TsanaPhysics/JC-AGRITecH-AI/chewa/OPPO_NPK_SYSTEM_INTEGRATION.md

# ระบบกล่องวัดแบบทึบแสงเชื่อมต่อสมาร์ทโฟน OPPO และการวิเคราะห์ NPK ในดินด้วยปัญญาประดิษฐ์

**โครงการวิจัย** การพัฒนาชุดวิเคราะห์ปริมาณไนโตรเจนและฟอสฟอรัสในดินแบบพกพาด้วยหลักการสะท้อนแสงร่วมกับปัญญาประดิษฐ์  
**หน่วยงาน** คณะวิทยาศาสตร์และเทคโนโลยี มหาวิทยาลัยราชภัฏรำไพพรรณี  
**หัวหน้าโครงการ** ผู้ช่วยศาสตราจารย์ ดร.ชีวะ ทัศนา  

---

## 1. ภาพรวมการเชื่อมต่อระบบระหว่างกล่อง Dark Chamber กับสมาร์ทโฟน OPPO

การพัฒนาชุดตรวจวัดแบบพกพานี้ ได้ผสานโครงสร้างกล่องวัดแบบทึบแสง (Optical Dark Chamber) ที่ขึ้นรูปด้วยเครื่องพิมพ์สามมิติจากเส้นใย PETG สีดำ เข้ากับสมาร์ทโฟน OPPO เพื่อทำหน้าที่เป็นทั้ง **หน่วยรับสัญญาณเชิงแสงความละเอียดสูง** **หน่วยประมวลผลปัญญาประดิษฐ์แบบ On-Device** และ **หน้าจอแสดงผล Cyber Dashboard** สำหรับรายงานค่าธาตุอาหารพืช ไนโตรเจน (N) ฟอสฟอรัส (P) และโพแทสเซียม (K) แก่เกษตรกรชาวสวนทุเรียนได้ทันทีในแปลงเพาะปลูก

ภาพจำลองการใช้งานชุดกล่อง Dark Chamber เชื่อมต่อสมาร์ทโฟน OPPO ในแปลงทุเรียน

---

## 2. การออกแบบแท่นสวมยึดสมาร์ทโฟน OPPO เฉพาะทาง (Custom OPPO Cradle Mount)

เนื่องจากสมาร์ทโฟนตระกูล OPPO (เช่น ซีรีส์ Reno, Find X และ A-Series) มีเอกลักษณ์ในการออกแบบโมดูลกล้องหลังแบบนูนเด่น (Camera Island Bump) ฝาบนของกล่องวัดจึงได้รับการออกแบบเชิงกลเพื่อรองรับลักษณะดังกล่าวโดยเฉพาะ

ภาพระยะประชิดแสดงการล็อกสมาร์ทโฟน OPPO เข้ากับแท่นและปะเก็นยาง EVA กันแสง

### จุดเด่นเชิงกลของแท่นจับยึดสมาร์ทโฟน OPPO
1. **รางประกบขนาดพอดี (Precision Form-fit Rails)** รางนำร่องความกว้าง 75.5 มิลลิเมตร พร้อมเขี้ยวล็อกเลื่อนสปริงด้านข้าง ช่วยให้การสอดสมาร์ทโฟนเข้าตำแหน่งทำได้อย่างรวดเร็ว แนบสนิท ไม่ขยับเขยื้อนขณะเคลื่อนย้ายในแปลงเกษตร
2. **หลุมเบ้ารองรับโมดูลกล้องนูน (Camera Bump Recess)** ปาดผิวเว้าลึก 3.2 มิลลิเมตร รองรับโมดูลกล้องของ OPPO ทำให้ตัวเครื่องวางขนานราบสนิทกับระนาบกล่อง ไม่เอียงตัว
3. **ปะเก็นยางโฟม EVA กันแสงเล็ดลอด 100% (High-density EVA Foam Gasket)** บริเวณรอบเลนส์กล้องหลักมีร่องใส่ยางโฟม EVA สีดำความหนาแน่นสูง เมื่อสอดสมาร์ทโฟนเข้าที่ ยางโฟมจะถูกกดทับแนบสนิทกับผิวกระจกหน้าเลนส์ ตัดแสงสว่างจากภายนอกเข้าสู่เซนเซอร์ได้อย่างสิ้นเชิง
4. **ช่องเปิดเชื่อมต่อสายสัญญาณ USB-C** บริเวณขอบล่างมีช่องเว้นระยะสำหรับเสียบสาย USB-C OTG สำหรับการเชื่อมต่อข้อมูลความเร็วสูง หรือใช้จ่ายพลังงานแบบสองทิศทาง

---

## 3. แผนผังสถาปัตยกรรมการเชื่อมต่อระบบ (System Architecture Diagram)

ระบบทำงานประสานกันระหว่างฮาร์ดแวร์ควบคุมแสงในห้องมืด ช่องทางการสื่อสาร และแอปพลิเคชันปัญญาประดิษฐ์บนสมาร์ทโฟน OPPO ดังแสดงในแผนผัง

```
[ ช่องบรรจุถาดดิน Ø 35 mm ลึก 8 mm ]
                 |
[ เขี้ยวดักแสง Labyrinth Seal สองชั้น ตัดแสง 99.94% ]
                 |
[ แหล่งกำเนิดแสง LED Array 45° (6 ย่านคลื่น 465-940 nm) ]
                 |
[ ลำแสงสะท้อนแบบกระจาย Diffuse Reflectance 0° แนวตั้งฉาก ]
                 |
[ กรวยเลนส์ + ปะเก็นยาง EVA สีดำรอบโมดูลกล้อง OPPO ]
                 |
+-------------------------------------------------------------+
|                     สมาร์ทโฟน OPPO                          |
|                                                             |
|  1. กล้องรับภาพความเข้มแสงสะท้อนสัมพัทธ์ (Relative R)         |
|  2. การแปลงสัญญาณ Kubelka-Munk F(R) และปรับชดเชยน้ำ 940 nm   |
|  3. แบบจำลองโครงข่ายประสาทเทียม MLP-ANN (6-16-8-1)          |
|  4. แสดงผล Cyber Dashboard ค่า N, P, K และคำแนะนำปุ๋ยทุเรียน  |
+-------------------------------------------------------------+
                 ^
                 | ช่องทางสื่อสารคู่ขนาน (Dual-mode Communication)
                 | 1. Bluetooth Low Energy 5.0 (ไร้สาย)
                 | 2. USB-C Serial OTG (สายตรง)
                 v
[ ไมโครคอนโทรลเลอร์ ESP32-S3 + Sequential LED Driver 100ms/50ms ]
```

---

## 4. ช่องทางการเชื่อมต่อข้อมูลสองระบบ (Dual-mode Communication)

ระบบรองรับการเชื่อมต่อกับสมาร์ทโฟน OPPO ได้ 2 รูปแบบ เพื่อความยืดหยุ่นสูงสุดในการทำงานภาคสนาม

### 4.1 การเชื่อมต่อไร้สายผ่านบลูทูธพลังงานต่ำ (Bluetooth Low Energy หรือ BLE 5.0)
* ไมโครคอนโทรลเลอร์ ESP32-S3 ภายในกล่องจะแพร่สัญญาณ BLE Advertisement
* แอปพลิเคชันบนสมาร์ทโฟน OPPO จะตรวจจับและจับคู่อัตโนมัติ (Auto-pairing) ภายใน 1 วินาที
* ส่งคำสั่งเปิด-ปิดไฟ LED พัลส์ตามลำดับ (Sequential Triggering) และส่งกลับข้อมูลสถานะแบตเตอรี่ อุณหภูมิ และความชื้นภายในกล่อง

### 4.2 การเชื่อมต่อผ่านสายตรง USB-C OTG (Direct Serial Cable Connection)
* เชื่อมต่อสาย USB-C สั้นแบบขดสปริงเข้ากับพอร์ต Type-C ของสมาร์ทโฟน OPPO โดยตรง
* ให้ความเร็วในการส่งผ่านคำสั่งระดับไมโครวินาที ปราศจากสัญญาณรบกวนคลื่นวิทยุในพื้นที่ห่างไกล
* สามารถแชร์พลังงานสำรองจากตัวกล่อง Dark Chamber ไปช่วยประจุไฟฟ้าให้สมาร์ทโฟนขณะปฏิบัติงานได้

---

## 5. การทำงานของแอปพลิเคชัน Soil NPK AI บนสมาร์ทโฟน OPPO

1. **ขั้นตอนการสอบเทียบฐานศูนย์ (Baseline Calibration)** ผู้ใช้งานวางแผ่นเทียบสีขาวมาตรฐานในถาดตัวอย่าง กดปุ่ม "สอบเทียบ" บนแอปพลิเคชัน เพื่อบันทึกค่าความเข้มแสงอ้างอิงของแต่ละย่านคลื่น
2. **การสแกนตัวอย่างดิน (Sequential Soil Scan)** บรรจุถาดดินที่ปาดหน้าเรียบเข้าสู่ลิ้นชัก ระบบจะสั่งให้ LED สว่างทีละดวงตามลำดับ (465, 525, 660, 720, 850, 940 nm) ดวงละ 100 มิลลิวินาที สลับความมืด 50 มิลลิวินาที กล้องของ OPPO จะถ่ายภาพความเข้มแสงสะท้อนในแต่ละช่วงคลื่น
3. **การประมวลผลเคมีเมตริกส์ล่วงหน้า (Chemometrics Pipeline)**
   * คำนวณค่าการสะท้อนแสงสัมพัทธ์ $R_\lambda = \frac{I_{\text{sample}} - I_{\text{dark}}}{I_{\text{white}} - I_{\text{dark}}}$
   * แปลงฟังก์ชันคูเบลกา-มังก์ $F(R_\lambda) = \frac{(1 - R_\lambda)^2}{2R_\lambda}$
   * ชดเชยอิทธิพลของความชื้นด้วยอัตราส่วนสเปกตรัมแถบดูดกลืนน้ำที่ 940 นาโนเมตร
4. **การทำนายผลด้วยโมเดลปัญญาประดิษฐ์ (Edge AI Inference)**
   * นำเวกเตอร์สเปกตรัมทั้ง 6 ช่องคลื่น ป้อนเข้าสู่โครงข่ายประสาทเทียม MLP สถาปัตยกรรม 6-16-8-1
   * คำนวณค่า **Total Nitrogen (g/kg)** และ **Available Phosphorus (mg/kg)** โดยตรง พร้อมประเมินแนวโน้มระดับ **Potassium (mg/kg)**
5. **การแสดงผลและคำแนะนำการจัดการปุ๋ย (Decision Support)**
   * หน้าจอ Cyber Dashboard บนสมาร์ทโฟน OPPO จะแสดงผลเป็นมาตรวัดเข็มและแถบสีสถานะ (ต่ำ ปานกลาง สูง)
   * ระบบเชื่อมโยงกับฐานความรู้ปุ๋ยทุเรียน แนะนำสูตรปุ๋ยและอัตราการใส่ที่เหมาะสมกับระยะการเจริญเติบโต เช่น ระยะฟื้นฟูต้น ระยะสะสมอาหาร หรือระยะพัฒนาการของผลทุเรียนโดยอัตโนมัติ

---

## 6. รายการไฟล์โมเดลและภาพจำลองที่จัดทำขึ้น

* [fig_oppo_npk_chamber_field.jpg](file:///Users/chewathassana/Desktop/handysense/chewa/figures/fig_oppo_npk_chamber_field.jpg) ภาพจำลองการทำงานจริงของชุดกล่อง Dark Chamber ร่วมกับสมาร์ทโฟน OPPO ในสวนทุเรียน
* [fig_oppo_macro_mount_engineering.jpg](file:///Users/chewathassana/Desktop/handysense/chewa/figures/fig_oppo_macro_mount_engineering.jpg) ภาพโคลสอัพเชิงวิศวกรรมการสวมล็อกสมาร์ทโฟน OPPO เข้ากับแท่นและปะเก็นยางกันแสง EVA
* [oppo_npk_system_diagram.svg](file:///Users/chewathassana/Desktop/handysense/chewa/figures/oppo_npk_system_diagram.svg) แผนผังเวกเตอร์สถาปัตยกรรมระบบการเชื่อมต่อฮาร์ดแวร์และการประมวลผล AI
* [dark_chamber_oppo_mount.scad](file:///Users/chewathassana/Desktop/handysense/chewa/dark_chamber_oppo_mount.scad) โค้ดพารามิเตอร์ 3 มิติ OpenSCAD ฝาบนสำหรับสมาร์ทโฟน OPPO
* [dark_chamber_oppo_mount.stl](file:///Users/chewathassana/Desktop/handysense/chewa/dark_chamber_oppo_mount.stl) ไฟล์เมช 3D STL สำหรับสั่งพิมพ์ 3 มิติด้วยเส้นใย PETG สีดำได้ทันที
