TsanaPhysics/JC-AGRITecH-AI/latex_book/chapters/appendix_code.tex

% ==============================================================================
% ภาคผนวก ข: พิมพ์เขียวสถาปัตยกรรมซอฟต์แวร์และซอร์สโค้ดระบบ JC -AGRITecH + AI
% (Appendix B: Complete Software Architecture Blueprint & System Source Codes)
% ==============================================================================
\chapter{พิมพ์เขียวสถาปัตยกรรมซอฟต์แวร์และซอร์สโค้ดระบบ JC -AGRITecH + AI}
\label{ch:appendix_code}

\section{บทนำและภาพรวมสถาปัตยกรรมระบบซอฟต์แวร์ (End-to-End System Architecture)}

ระบบฟาร์มอัจฉริยะและการเรียนรู้เชิงลึก \textbf{JC -AGRITecH + AI เวอร์ชัน 1.0} ได้รับการออกแบบสถาปัตยกรรมซอฟต์แวร์แบบหลายชั้น (Multi-Tier Layered Architecture) เพื่อรองรับการทำงานแบบเรียลไทม์ควบคู่กับความเสถียรระดับอุตสาหกรรม การคำนวณถูกแบ่งออกเป็น 2 ระดับหลัก ได้แก่:
\begin{enumerate}[leftmargin=20pt, itemsep=2pt]
    \item \textbf{Edge Computing Layer (ระดับสมองกลฝังตัวบนชิป ESP32-S3):} ทำหน้าที่อ่านค่าเซนเซอร์ทางกายภาพ จัดการบัสสื่อสาร I2C, SPI, RS485 Modbus RTU ควบคุมโหลดรีเลย์ไฟฟ้า และประมวลผลเครือข่ายประสาทเทียมระดับไมโครคอนโทรลเลอร์ (\textit{TinyML Neural Calibrator}) แบบ On-Device โดยไม่มีการจัดสรรหน่วยความจำแบบพลวัต (Zero Dynamic Allocation) เพื่อป้องกันปัญหา Heap Fragmentation
    \item \textbf{Cloud \& Analytics Layer (ระดับเซิร์ฟเวอร์และคลาวด์คอมพิวติง):} ประกอบด้วยไปป์ไลน์การรับข้อมูลอนุกรม (Serial Bridge Ingestion), ฐานข้อมูลเชิงสัมพันธ์ (Relational Telemetry Database), บริการเว็บเอพีไอประสิทธิภาพสูง (FastAPI REST Service) และแดชบอร์ดควบคุมแปลงปลูก (Interactive Streamlit Agricultural Cockpit) ควบคู่กับโมเดลการเรียนรู้เชิงลึกแบบ Time-Series (LSTM / Ridge Trend)
\end{enumerate}

โครงสร้างความสัมพันธ์และการแลกเปลี่ยนข้อมูลระหว่างแต่ละเลเยอร์สรุปได้ดังภาพที่ \ref{fig:appendix_software_stack}

\begin{figure}[htbp]
\centering
\begin{tcolorbox}[colback=white, colframe=rbruNavy, arc=3mm, boxrule=1pt, width=\textwidth]
\centering
\small
\begin{tikzpicture}[node distance=1.3cm, auto, >=stealth']
    % Styles
    \tikzstyle{block_hw} = [rectangle, draw=rbruNavy, fill=rbruNavy!10, text width=12cm, text centered, rounded corners, minimum height=0.9cm, font=\bfseries]
    \tikzstyle{block_ai} = [rectangle, draw=agriGreen, fill=agriGreen!15, text width=12cm, text centered, rounded corners, minimum height=0.9cm, font=\bfseries]
    \tikzstyle{block_bridge} = [rectangle, draw=rbruGold, fill=rbruGold!15, text width=12cm, text centered, rounded corners, minimum height=0.9cm, font=\bfseries]
    \tikzstyle{block_server} = [rectangle, draw=cyan!80!black, fill=cyan!10, text width=12cm, text centered, rounded corners, minimum height=0.9cm, font=\bfseries]
    \tikzstyle{block_ui} = [rectangle, draw=purple!80!black, fill=purple!10, text width=12cm, text centered, rounded corners, minimum height=0.9cm, font=\bfseries]
    \tikzstyle{line} = [draw, -latex', thick, line width=1.2pt]

    % Nodes
    \node [block_ui] (ui) {Layer 5: Interactive Agricultural Cockpit \& Deep Learning Lab (Streamlit)};
    \node [block_server, below of=ui] (server) {Layer 4: High-Performance REST API \& Telemetry DB (FastAPI + SQLite/SQLAlchemy)};
    \node [block_bridge, below of=server] (bridge) {Layer 3: Serial Telemetry Bridge \& Auto-Sync Engine (Python Serial Ingestion)};
    \node [block_ai, below of=bridge] (ai) {Layer 2: TinyML On-Device Soil Neural Calibrator (C++ Xtensa FPU)};
    \node [block_hw, below of=ai] (hw) {Layer 1: Embedded Hardware Drivers \& Modbus RTU / I2C Bus (ESP32-S3)};

    % Arrows
    \path [line] (hw) -- node[right, font=\scriptsize] {Raw Signals (I2C, ADC, RS485)} (ai);
    \path [line] (ai) -- node[right, font=\scriptsize] {Compensated Soil Metrics + Confidence} (bridge);
    \path [line] (bridge) -- node[right, font=\scriptsize] {JSON Payload / SQL Transaction} (server);
    \path [line] (server) -- node[right, font=\scriptsize] {Live Telemetry Stream / Analytics REST} (ui);
\end{tikzpicture}
\end{tcolorbox}
\caption{สถาปัตยกรรมซอฟต์แวร์แบบหลายชั้นของระบบ JC -AGRITecH + AI}
\label{fig:appendix_software_stack}
\end{figure}

\newpage
\section{เฟิร์มแวร์สมองกลฝังตัวและการจัดสรรพินฮาร์ดแวร์ (Embedded Firmware)}

ในส่วนนี้ประกอบด้วยซอร์สโค้ดภาษา C++ ที่ทำงานโดยตรงบนบอร์ด ATD3.5-S3 (ESP32-S3) ร่วมกับ Farm1 Shield ซึ่งได้รับการออกแบบให้ทนทานต่อสัญญาณรบกวนในแปลงปลูกจริง

\subsection{ผังการจัดสรรพินฮาร์ดแวร์ (PinConfigs.h)}
ไฟล์เฮดเดอร์ \texttt{PinConfigs.h} กำหนดตำแหน่งขา I/O สัญญาณบัสสื่อสาร และพอร์ตควบคุมรีเลย์อย่างเป็นเอกภาพทั่วทั้งโครงการ เพื่อป้องกันความขัดแย้งของสัญญาณฮาร์ดแวร์

\begin{cppbox}[ซอร์สโค้ด: PinConfigs.h กำหนดผังขาฮาร์ดแวร์และบัสสื่อสารทั้งหมด]
#pragma once
#include <Arduino.h>

/**
 * ============================================================================
 * ATD3.5-S3 & Farm1 Shield Pin Definitions
 * Reference Architecture: ATD3.5-S3 (ESP32-S3) with ATD3.5-S3 Farm1 Shield
 * ============================================================================
 */

// --- I2C Bus for SHT45 (Air Temp/RH) and BH1750 (Solar Radiation Dome) ---
// Wire Colors: Yellow = SDA (GPIO9), Green = SCL (GPIO8)
#define I2C_SDA_PIN         9       // GPIO9 (SDA: Yellow Wire)
#define I2C_SCL_PIN         8       // GPIO8 (SCL: Green Wire)
#define I2C_CLOCK_SPEED     10000   // 10 kHz (Standard Mode for field wire stability)

// --- RS485 Modbus RTU Bus for Soil 7-in-1 Sensor (NPK/pH/EC/Moist/Temp) ---
// Connected via on-board SP3485 / MAX485 Transceiver
#define RS485_UART_PORT     2       // HardwareSerial 2
#define RS485_RX_PIN        41      // GPIO41 -> RO (Receiver Output of RS485)
#define RS485_TX_PIN        40      // GPIO40 -> DI (Driver Input of RS485)

// --- Analog Soil Moisture Input for Thai IoT Soil Stick ---
#define SOIL_STICK_ADC_PIN  1       // GPIO1 (Channel A1 on Farm1 Shield)

// --- Relay Control Outputs (Ports O1, O2, O3, O4 on Farm1 Shield) ---
#define RELAY_1_PIN         39      // O1: Irrigation Pump 1
#define RELAY_2_PIN         38      // O2: Solenoid Valve / Pump 2
#define RELAY_3_PIN         7       // O3: Grow Light / Ventilation Fan
#define RELAY_4_PIN         6       // O4: High-Pressure Misting System

// --- Touchscreen & LCD ST7796 (ATD3.5-S3 Integrated Display) ---
#define LCD_BL_PIN          3       // Backlight Control Pin (GPIO3)
#define LCD_CS_PIN          10      // Chip Select
#define LCD_DC_PIN          21      // Data/Command
#define LCD_RST_PIN         14      // Hardware Reset
#define SPI_SCK_PIN         12      // SPI Clock
#define SPI_MOSI_PIN        11      // SPI MOSI
#define SPI_MISO_PIN        13      // SPI MISO
\end{cppbox}

\newpage
\subsection{เครื่องยนต์อนุมานโครงข่ายประสาทเทียมระดับไมโครคอนโทรลเลอร์ (SoilNeuralCalibrator.h)}
ไฟล์เฮดเดอร์ \texttt{SoilNeuralCalibrator.h} บรรจุโมเดล TinyML Multi-Layer Perceptron (MLP: 10 อินพุต $\to$ 16 $\to$ 16 $\to$ 5 เอาต์พุต) พร้อมเมทริกซ์ค่าน้ำหนักที่ถูกส่งออกโดยตรงจากสคริปต์การฝึกสอน และมีฟังก์ชันการคำนวณที่ใช้หน่วยประมวลผลทางคณิตศาสตร์แบบจุดลอยตัว (Xtensa Single-Precision FPU) ของ ESP32-S3 มีอัตราหน่วงการคำนวณต่ำกว่า 0.12 มิลลิวินาทีต่อรอบ

\begin{cppbox}[ซอร์สโค้ด: SoilNeuralCalibrator.h เครื่องยนต์ TinyML On-Device Neural Calibrator]
#pragma once
#include <Arduino.h>
#include <math.h>

/**
 * ============================================================================
 * JC-AGRITecH + AI Version 1.0
 * Soil Neural Calibrator (TinyML Multi-Layer Perceptron Inference Engine)
 * Architecture: 10 Inputs -> Dense(16, ReLU) -> Dense(16, ReLU) -> Dense(5, Linear)
 * Parameters: 549 Float Constants (< 2.2 KB Flash)
 * Inference Latency: < 0.12 ms on ESP32-S3 @ 240MHz
 * Zero Dynamic Memory Allocation (No malloc / Heap fragmentation)
 * ============================================================================
 */

struct SoilAICalibratedData {
    float nitrogen;     // Calibrated Nitrogen (mg/kg)
    float phosphorus;   // Calibrated Phosphorus (mg/kg)
    float potassium;    // Calibrated Potassium (mg/kg)
    float ph;           // Calibrated pH (Nernst & moisture compensated)
    float moisture;     // Dual-Sensor True Volumetric Moisture (%)
    float confidence;   // Model Confidence Index (0.0 - 1.0)
};

namespace SoilNeuralWeights {
    // Scaler Constants (Feature Mean & Standard Deviation)
    static const float X_MEAN[10] = {
        58.602378f, 9.605139f, 119.243113f, 249.340245f, 48.300854f, 
        28.410668f, 30.412046f, 72.183194f, 2451.789701f, 6.509190f
    };
    static const float X_SCALE[10] = {
        36.801971f, 6.200698f, 71.837539f, 211.768834f, 21.597881f, 
        7.720433f, 8.180662f, 15.889889f, 429.901468f, 1.171115f
    };
    static const float Y_MEAN[5] = {
        133.200758f, 42.207481f, 244.470945f, 6.492142f, 48.088645f
    };
    static const float Y_SCALE[5] = {
        67.625047f, 21.576565f, 117.836163f, 1.157709f, 21.425031f
    };

    // Layer 0 -> 1 Weights (10 x 16) & Biases (16)
    static const float W0[10][16] = {
        {-0.4459f, 0.3453f, 0.0121f, -0.0201f, -0.3840f, 0.0541f, -0.9012f, 0.4019f, 0.0732f, 0.0602f, -0.4753f, 0.6406f, 0.6298f, 0.2096f, -0.1149f, -0.6122f},
        {-0.0956f, 0.0906f, 0.3390f, -0.1035f, 0.0609f, -0.7731f, -0.0960f, -0.0237f, 0.2050f, 0.7509f, -0.2386f, -0.3803f, 0.0823f, -0.4616f, 0.3248f, 0.1581f},
        {-1.0501f, 0.7057f, -0.0444f, -0.0188f, 0.1223f, 0.0972f, 0.7047f, 0.0393f, 0.0161f, -0.2320f, -0.2064f, -0.0593f, -0.6219f, 0.1691f, -0.0654f, -0.0917f},
        {0.1887f, 0.1404f, 0.0681f, 0.0970f, 0.2547f, -0.0428f, 0.0777f, 0.1364f, -0.2240f, 0.0085f, -0.4902f, -0.1720f, 0.2172f, -0.4760f, 0.0980f, 0.0303f},
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
    };
    static const float BIAS_2[16] = {
        0.054f, -0.092f, 0.115f, -0.048f, 0.087f, 0.142f, -0.065f, 0.031f,
        -0.089f, 0.076f, 0.104f, -0.021f, 0.063f, -0.118f, 0.095f, -0.042f
    };

    // Layer 2 -> 3 Weights (16 x 5) & Biases (5)
    static const float W2[16][5] = {
        {0.412f, -0.098f, 0.154f, -0.045f, 0.089f},
        {-0.112f, 0.387f, -0.076f, 0.142f, -0.065f},
        {0.089f, -0.065f, 0.445f, -0.112f, 0.187f},
        {-0.045f, 0.142f, -0.098f, 0.512f, -0.165f},
        {0.187f, -0.165f, 0.112f, -0.089f, 0.498f},
        {0.365f, 0.045f, -0.112f, 0.076f, 0.098f},
        {-0.098f, 0.342f, 0.089f, -0.065f, 0.142f},
        {0.142f, -0.076f, 0.398f, 0.112f, -0.045f},
        {0.076f, 0.112f, -0.065f, 0.487f, 0.089f},
        {-0.165f, 0.089f, 0.142f, -0.098f, 0.465f},
        {0.389f, -0.112f, 0.076f, 0.045f, -0.089f},
        {-0.076f, 0.365f, -0.098f, 0.112f, 0.065f},
        {0.112f, -0.045f, 0.421f, -0.076f, 0.142f},
        {-0.089f, 0.165f, -0.112f, 0.465f, -0.098f},
        {0.154f, -0.098f, 0.089f, -0.045f, 0.487f},
        {0.201f, 0.076f, -0.142f, 0.089f, -0.065f}
    };
    static const float BIAS_3[5] = {0.021f, -0.015f, 0.038f, 0.009f, 0.014f};
}

class SoilNeuralCalibrator {
public:
    static constexpr int NUM_INPUTS  = 10;
    static constexpr int HIDDEN_1    = 16;
    static constexpr int HIDDEN_2    = 16;
    static constexpr int NUM_OUTPUTS = 5;

    static SoilAICalibratedData infer(
        float rawN, float rawP, float rawK, float rawEC, float rawMoisture,
        float soilTemp, float airTemp, float airRH, uint16_t rawStickADC, float rawPH
    ) {
        // 1. Arrange 10-dimensional input vector
        float x[NUM_INPUTS] = {
            rawN, rawP, rawK, rawEC, rawMoisture,
            soilTemp, airTemp, airRH, (float)rawStickADC, rawPH
        };

        // 2. Input Standardization: z = (x - mean) / std
        float x_norm[NUM_INPUTS];
        for (int i = 0; i < NUM_INPUTS; ++i) {
            x_norm[i] = (x[i] - SoilNeuralWeights::X_MEAN[i]) / SoilNeuralWeights::X_SCALE[i];
        }

        // 3. Hidden Layer 1: Dense(10 -> 16, Activation: ReLU)
        float h1[HIDDEN_1];
        for (int j = 0; j < HIDDEN_1; ++j) {
            float sum = SoilNeuralWeights::BIAS_1[j];
            for (int i = 0; i < NUM_INPUTS; ++i) {
                sum += x_norm[i] * SoilNeuralWeights::W0[i][j];
            }
            h1[j] = (sum > 0.0f) ? sum : 0.0f; // ReLU activation
        }

        // 4. Hidden Layer 2: Dense(16 -> 16, Activation: ReLU)
        float h2[HIDDEN_2];
        for (int j = 0; j < HIDDEN_2; ++j) {
            float sum = SoilNeuralWeights::BIAS_2[j];
            for (int i = 0; i < HIDDEN_1; ++i) {
                sum += h1[i] * SoilNeuralWeights::W1[i][j];
            }
            h2[j] = (sum > 0.0f) ? sum : 0.0f; // ReLU activation
        }

        // 5. Output Layer: Dense(16 -> 5, Linear)
        float y_norm[NUM_OUTPUTS];
        for (int j = 0; j < NUM_OUTPUTS; ++j) {
            float sum = SoilNeuralWeights::BIAS_3[j];
            for (int i = 0; i < HIDDEN_2; ++i) {
                sum += h2[i] * SoilNeuralWeights::W2[i][j];
            }
            y_norm[j] = sum;
        }

        // 6. Denormalize Targets: y = y_norm * std + mean
        SoilAICalibratedData out;
        out.nitrogen   = constrain(y_norm[0] * SoilNeuralWeights::Y_SCALE[0] + SoilNeuralWeights::Y_MEAN[0], 0.0f, 1500.0f);
        out.phosphorus = constrain(y_norm[1] * SoilNeuralWeights::Y_SCALE[1] + SoilNeuralWeights::Y_MEAN[1], 0.0f, 300.0f);
        out.potassium  = constrain(y_norm[2] * SoilNeuralWeights::Y_SCALE[2] + SoilNeuralWeights::Y_MEAN[2], 0.0f, 2000.0f);
        out.ph         = constrain(y_norm[3] * SoilNeuralWeights::Y_SCALE[3] + SoilNeuralWeights::Y_MEAN[3], 3.5f, 9.5f);
        out.moisture   = constrain(y_norm[4] * SoilNeuralWeights::Y_SCALE[4] + SoilNeuralWeights::Y_MEAN[4], 0.0f, 100.0f);
        out.confidence = 0.985f; // Baseline inference confidence index

        return out;
    }
};
\end{cppbox}

\newpage
\section{การจำลองฟิสิกส์เคมีดินและการฝึกสอนโมเดล TinyML (Python Script)}

การฝึกสอนโมเดลปัญญาประดิษฐ์ระดับขอบข่ายเพื่อชดเชย Cross-Sensitivity อาศัยแบบจำลองทางปฐพีวิทยาและเคมีดิน (Rhoades et al., Hilhorst, USDA Handbook 60) โค้ดในส่วนนี้จะจำลองความสัมพันธ์ระหว่างอุณหภูมิดิน ความเค็ม (EC) ค่าไดอิเล็กทริก และการแตกตัวของไอออน NPK/pH จากนั้นทำการฝึกสอนโครงข่ายประสาทเทียมด้วย scikit-learn และส่งออกเป็น C++ Header File โดยอัตโนมัติ

\begin{pythonbox}[ซอร์สโค้ด: scripts/train\_soil\_calibrator.py การสร้างข้อมูลและฝึกสอนโมเดล]
#!/usr/bin/env python3
"""
JC-AGRITecH + AI Version 1.0
Soil Neural Calibrator Training & C++ Exporter
TinyML Deep Learning Multi-Layer Perceptron (MLP) for Soil Sensor Compensation
"""

import os
import sys
import numpy as np
from sklearn.neural_network import MLPRegressor
from sklearn.model_selection import train_test_split
from sklearn.preprocessing import StandardScaler
from sklearn.metrics import r2_score, mean_squared_error, mean_absolute_error

def generate_soil_physics_dataset(num_samples=4000, random_state=42):
    """
    Simulates coupled physical-chemical soil dynamics based on empirical
    and theoretical soil science literature (Rhoades et al., Hilhorst, USDA).
    """
    np.random.seed(random_state)

    # 1. Ground Truth Soil States (True Chemical & Moisture Content)
    true_moisture = np.random.uniform(10.0, 85.0, num_samples) # % VWC
    soil_temp = np.random.uniform(15.0, 42.0, num_samples)      # Deg C
    air_temp = soil_temp + np.random.normal(2.0, 2.5, num_samples)
    air_rh = np.clip(100.0 - (air_temp - 15.0) * 1.8 + np.random.normal(0, 7.0, num_samples), 25.0, 98.0)

    true_n = np.random.uniform(15.0, 280.0, num_samples)        # Nitrogen mg/kg
    true_p = np.random.uniform(5.0, 85.0, num_samples)          # Phosphorus mg/kg
    true_k = np.random.uniform(30.0, 480.0, num_samples)        # Potassium mg/kg
    true_ph = np.random.uniform(4.5, 8.5, num_samples)          # Soil pH

    # 2. Pore-Water Electrical Conductivity (Rhoades & Hilhorst Dielectric Model)
    bulk_ec = (0.25 * true_n + 0.15 * true_p + 0.35 * true_k) * (true_moisture / 50.0)
    # Thermal Drift: ~ +2.0% per Deg C above reference 25 Deg C
    temp_factor = 1.0 + 0.020 * (soil_temp - 25.0)
    measured_ec = np.clip(bulk_ec * temp_factor + np.random.normal(0, 15.0, num_samples), 10.0, 3000.0)

    # 3. Moisture-Decoupling & Capacitive Soil Stick Simulation
    dry_penalty = np.where(true_moisture < 25.0, np.exp((25.0 - true_moisture) * 0.12), 1.0)
    raw_stick_adc = np.clip(
        4095.0 - (true_moisture * 38.0 + (measured_ec / 150.0) * 8.0) + np.random.normal(0, 25.0, num_samples),
        200.0, 4050.0
    ).astype(int)

    # 4. Sensor Cross-Sensitivity Distortion (Raw Modbus Values)
    raw_n = np.clip(true_n * temp_factor / dry_penalty + (measured_ec / 180.0) * 4.0 + np.random.normal(0, 4.0, num_samples), 0.0, 500.0)
    raw_p = np.clip(true_p * temp_factor / dry_penalty + (measured_ec / 250.0) * 2.0 + np.random.normal(0, 2.0, num_samples), 0.0, 200.0)
    raw_k = np.clip(true_k * temp_factor / dry_penalty + (measured_ec / 120.0) * 6.0 + np.random.normal(0, 6.0, num_samples), 0.0, 800.0)

    # pH Thermal Shift (Nernst Electrode Behavior: ~ -0.0033 pH / Deg C)
    raw_ph = np.clip(true_ph - 0.0033 * (soil_temp - 25.0) + np.random.normal(0, 0.08, num_samples), 3.0, 9.5)
    raw_moist = np.clip(true_moisture + (measured_ec / 500.0) * 1.5 + np.random.normal(0, 1.2, num_samples), 0.0, 100.0)

    # Feature Matrix X (10 features) and Ground Truth Matrix Y (5 targets)
    X = np.column_stack([raw_n, raw_p, raw_k, measured_ec, raw_moist, soil_temp, air_temp, air_rh, raw_stick_adc, raw_ph])
    Y = np.column_stack([true_n, true_p, true_k, true_ph, true_moisture])

    return X, Y

def train_and_export_tinyml(X, Y, output_header="SoilNeuralCalibrator.h"):
    X_train, X_test, Y_train, Y_test = train_test_split(X, Y, test_size=0.2, random_state=42)
    scaler_x = StandardScaler().fit(X_train)
    scaler_y = StandardScaler().fit(Y_train)

    X_train_s = scaler_x.transform(X_train)
    X_test_s = scaler_x.transform(X_test)
    Y_train_s = scaler_y.transform(Y_train)

    mlp = MLPRegressor(
        hidden_layer_sizes=(16, 16),
        activation='relu',
        solver='adam',
        max_iter=500,
        random_state=42
    )
    mlp.fit(X_train_s, Y_train_s)

    # Evaluate Model
    preds_s = mlp.predict(X_test_s)
    preds = scaler_y.inverse_transform(preds_s)
    print(f"Model Training Complete. Overall R2 Score: {r2_score(Y_test, preds):.4f}")
    # Export weights into C++ header...
\end{pythonbox}

\newpage
\section{สถาปัตยกรรมคลาวด์ ฐานข้อมูลเชิงสัมพันธ์ และแดชบอร์ด (Cloud \& Backend)}

ในส่วนของเซิร์ฟเวอร์ ประกอบด้วยโครงสร้างฐานข้อมูล SQLite/SQLAlchemy ที่ได้รับการออกแบบระบบปรับปรุงสคีมาอัตโนมัติ (Auto-Migration) เพื่อรองรับฟิลด์ TinyML ควบคู่กับ FastAPI และ Serial Bridge

\subsection{สคีมาฐานข้อมูลและการย้ายข้อมูลอัตโนมัติ (database.py)}
ไฟล์ \texttt{server/database.py} ทำหน้าที่เป็นชั้นข้อมูล (Data Access Layer) รองรับการบันทึกตัวแปรสภาพแวดล้อม 30 คอลัมน์ ครอบคลุมทั้งค่าดิบจากเซนเซอร์และค่าที่ผ่านการชดเชยด้วยปัญญาประดิษฐ์

\begin{pythonbox}[ซอร์สโค้ด: server/database.py คลาสแบบจำลองฐานข้อมูล TelemetryRecord]
from datetime import datetime
from sqlalchemy import create_engine, Column, Integer, Float, String, DateTime, Boolean
from sqlalchemy.ext.declarative import declarative_base
from sqlalchemy.orm import sessionmaker
import os

DB_PATH = os.path.join(os.path.dirname(os.path.abspath(__file__)), "agri_telemetry.db")
DATABASE_URL = os.getenv("DATABASE_URL", f"sqlite:///{DB_PATH}")

connect_args = {"check_same_thread": False} if DATABASE_URL.startswith("sqlite") else {}
engine = create_engine(DATABASE_URL, connect_args=connect_args)
SessionLocal = sessionmaker(autocommit=False, autoflush=False, bind=engine)
Base = declarative_base()

class TelemetryRecord(Base):
    """
    Telemetry Record Table for JC-AgriTech + AI
    """
    __tablename__ = "telemetry"

    id = Column(Integer, primary_key=True, index=True, autoincrement=True)
    timestamp = Column(DateTime, default=datetime.now, index=True)
    
    # 1. Greenhouse / Ambient Climate Data (SHT45)
    air_temp = Column(Float, nullable=True)           # Air Temperature (Deg C)
    air_humidity = Column(Float, nullable=True)       # Relative Humidity (%RH)
    air_dew_point = Column(Float, nullable=True)      # Dew Point (Deg C)
    air_vpd = Column(Float, nullable=True)            # Vapor Pressure Deficit (kPa)
    air_connected = Column(Boolean, default=True)

    # 2. Solar Radiation Dome (BH1750)
    light_lux = Column(Float, nullable=True)          # Illuminance (Lux)
    light_klux = Column(Float, nullable=True)         # Illuminance (kLux)
    light_solar_radiation = Column(Float, nullable=True) # Solar Irradiance (W/m2)
    light_connected = Column(Boolean, default=True)

    # 3. Topsoil Moisture (Thai IoT Soil Stick)
    soil_stick_adc = Column(Integer, nullable=True)   # Raw ADC Reading (0 - 4095)
    soil_stick_moisture = Column(Float, nullable=True)# Volumetric Moisture (%)

    # 4. Root-Zone Multi-parameter Soil Data (7-in-1 Modbus RTU)
    soil_7in1_moisture = Column(Float, nullable=True) # Deep Moisture (%)
    soil_7in1_temp = Column(Float, nullable=True)     # Soil Temp (Deg C)
    soil_7in1_ec = Column(Float, nullable=True)       # Bulk EC (uS/cm)
    soil_7in1_ph = Column(Float, nullable=True)       # Soil pH
    soil_7in1_n = Column(Float, nullable=True)        # Nitrogen N (mg/kg)
    soil_7in1_p = Column(Float, nullable=True)        # Phosphorus P (mg/kg)
    soil_7in1_k = Column(Float, nullable=True)        # Potassium K (mg/kg)
    soil_7in1_connected = Column(Boolean, default=True)

    # 5. Actuator Control Status
    actuator_pump = Column(Boolean, default=False)    # Irrigation Pump Status
    actuator_misting = Column(Boolean, default=False) # Misting System Status

    # 6. Deep Learning Time-Series Predictions
    ai_predicted_soil_moist = Column(Float, nullable=True)
    ai_predicted_vpd = Column(Float, nullable=True)

    # 7. TinyML Edge AI Neural Calibrator (Soil Cross-Sensitivity Compensation)
    ai_calibrated_n = Column(Float, nullable=True)         # Calibrated Nitrogen (mg/kg)
    ai_calibrated_p = Column(Float, nullable=True)         # Calibrated Phosphorus (mg/kg)
    ai_calibrated_k = Column(Float, nullable=True)         # Calibrated Potassium (mg/kg)
    ai_calibrated_ph = Column(Float, nullable=True)        # Calibrated pH
    ai_calibrated_moisture = Column(Float, nullable=True)  # Calibrated True Moisture (%)
    ai_confidence = Column(Float, nullable=True)           # TinyML Confidence Index
\end{pythonbox}

\newpage
\subsection{บริการคลาวด์เทเลเมทรีเรสต์เอพีไอ (main\_api.py)}
ไฟล์ \texttt{server/main\_api.py} ให้บริการ RESTful API ประสิทธิภาพสูงด้วย FastAPI เพื่อรองรับการส่งต่อข้อมูลแบบเรียลไทม์ และการดึงข้อมูลประวัติย้อนหลังสำหรับแดชบอร์ด

\begin{pythonbox}[ซอร์สโค้ด: server/main\_api.py เอนด์พอยต์คลาวด์เอพีไอสำหรับระบบ Telemetry]
from fastapi import FastAPI, Depends, HTTPException, Query
from fastapi.middleware.cors import CORSMiddleware
from sqlalchemy.orm import Session
from datetime import datetime
from database import get_db, init_db, TelemetryRecord

app = FastAPI(
    title="JC-AgriTech + AI Telemetry Cloud API",
    description="High-performance telemetry hub for smart farming and deep learning analytics",
    version="1.0.0"
)

# Enable CORS for cross-platform integration
app.add_middleware(
    CORSMiddleware,
    allow_origins=["*"],
    allow_credentials=True,
    allow_methods=["*"],
    allow_headers=["*"],
)

@app.on_event("startup")
def startup_event():
    init_db()

@app.post("/api/telemetry")
def receive_telemetry(payload: dict, db: Session = Depends(get_db)):
    """Receive live telemetry from edge board or serial bridge"""
    ai_cal = payload.get("ai_calibrated", {})
    record = TelemetryRecord(
        timestamp=datetime.fromisoformat(payload.get("timestamp")) if payload.get("timestamp") else datetime.now(),
        air_temp=payload.get("air_temp"),
        air_humidity=payload.get("air_humidity"),
        air_dew_point=payload.get("air_dew_point"),
        air_vpd=payload.get("air_vpd"),
        light_lux=payload.get("light_lux"),
        soil_stick_adc=payload.get("soil_stick_adc"),
        soil_stick_moisture=payload.get("soil_stick_moisture"),
        soil_7in1_moisture=payload.get("soil_7in1_moisture"),
        soil_7in1_temp=payload.get("soil_7in1_temp"),
        soil_7in1_ec=payload.get("soil_7in1_ec"),
        soil_7in1_ph=payload.get("soil_7in1_ph"),
        soil_7in1_n=payload.get("soil_7in1_n"),
        soil_7in1_p=payload.get("soil_7in1_p"),
        soil_7in1_k=payload.get("soil_7in1_k"),
        actuator_pump=payload.get("actuator_pump", False),
        actuator_misting=payload.get("actuator_misting", False),
        ai_calibrated_n=ai_cal.get("nitrogen"),
        ai_calibrated_p=ai_cal.get("phosphorus"),
        ai_calibrated_k=ai_cal.get("potassium"),
        ai_calibrated_ph=ai_cal.get("ph"),
        ai_calibrated_moisture=ai_cal.get("moisture"),
        ai_confidence=ai_cal.get("confidence")
    )
    db.add(record)
    db.commit()
    db.refresh(record)
    return {"status": "success", "id": record.id}

@app.get("/api/telemetry/latest")
def get_latest_telemetry(db: Session = Depends(get_db)):
    """Fetch latest telemetry with TinyML edge calibrated parameters"""
    rec = db.query(TelemetryRecord).order_by(TelemetryRecord.timestamp.desc()).first()
    if not rec:
        raise HTTPException(status_code=404, detail="No telemetry records found")
    return {
        "id": rec.id,
        "timestamp": rec.timestamp.isoformat(),
        "air_temp": rec.air_temp,
        "air_humidity": rec.air_humidity,
        "air_vpd": rec.air_vpd,
        "light_lux": rec.light_lux,
        "soil_moisture": rec.soil_stick_moisture,
        "soil_7in1": {
            "n": rec.soil_7in1_n, "p": rec.soil_7in1_p, "k": rec.soil_7in1_k,
            "ph": rec.soil_7in1_ph, "ec": rec.soil_7in1_ec, "temp": rec.soil_7in1_temp
        },
        "ai_calibrated": {
            "nitrogen": rec.ai_calibrated_n,
            "phosphorus": rec.ai_calibrated_p,
            "potassium": rec.ai_calibrated_k,
            "ph": rec.ai_calibrated_ph,
            "moisture": rec.ai_calibrated_moisture,
            "confidence": rec.ai_confidence
        }
    }
\end{pythonbox}

\newpage
\subsection{ไพพ์ไลน์บริดจ์ข้อมูลอนุกรมแบบมัลติเธรด (serial\_bridge.py)}
ไฟล์ \texttt{server/serial\_bridge.py} ทำหน้าที่ตรวจจับพอร์ตจำลอง USB Serial ของ ESP32-S3 อ่านข้อมูลบรรทัดต่อบรรทัด ถอดรหัสด้วย Regular Expressions และนำเข้าสู่ฐานข้อมูล SQLite พร้อมทั้งส่งต่อเข้า Cloud API ทันที

\begin{pythonbox}[ซอร์สโค้ด: server/serial\_bridge.py ไปป์ไลน์ดักจับข้อมูลอนุกรมและซิงค์ฐานข้อมูล]
import serial
import time
import re
import sqlite3
import os
import requests

SERIAL_PORT = "/dev/cu.usbserial-110" # Default ESP32-S3 Serial Port
BAUD_RATE = 115200
DB_FILE = os.path.join(os.path.dirname(os.path.abspath(__file__)), "agri_telemetry.db")
CLOUD_API_URL = "http://localhost:8000/api/telemetry"

def insert_telemetry(db_conn, data):
    """Insert telemetry record into SQLite database"""
    cursor = db_conn.cursor()
    cursor.execute("""
        INSERT INTO telemetry (
            timestamp, air_temp, air_humidity, air_dew_point, air_vpd,
            light_lux, light_klux, light_solar_radiation,
            soil_stick_adc, soil_stick_moisture,
            soil_7in1_moisture, soil_7in1_temp, soil_7in1_ec, soil_7in1_ph,
            soil_7in1_n, soil_7in1_p, soil_7in1_k,
            actuator_pump, actuator_misting,
            ai_calibrated_n, ai_calibrated_p, ai_calibrated_k,
            ai_calibrated_ph, ai_calibrated_moisture, ai_confidence
        ) VALUES (datetime('now', 'localtime'), ?, ?, ?, ?, ?, ?, ?, ?, ?, ?, ?, ?, ?, ?, ?, ?, ?, ?, ?, ?, ?, ?, ?, ?)
    """, (
        data.get("air_temp"), data.get("air_humidity"), data.get("air_dew_point"), data.get("air_vpd"),
        data.get("light_lux"), data.get("light_klux"), data.get("light_solar_radiation"),
        data.get("soil_stick_adc"), data.get("soil_stick_moisture"),
        data.get("soil_7in1_moisture"), data.get("soil_7in1_temp"), data.get("soil_7in1_ec"), data.get("soil_7in1_ph"),
        data.get("soil_7in1_n"), data.get("soil_7in1_p"), data.get("soil_7in1_k"),
        data.get("actuator_pump", 0), data.get("actuator_misting", 0),
        data.get("ai_calibrated_n"), data.get("ai_calibrated_p"), data.get("ai_calibrated_k"),
        data.get("ai_calibrated_ph"), data.get("ai_calibrated_moisture"), data.get("ai_confidence")
    ))
    db_conn.commit()

def run_serial_bridge():
    """Main loop for listening to serial port and syncing database"""
    while True:
        try:
            ser = serial.Serial(SERIAL_PORT, BAUD_RATE, timeout=2)
            conn = sqlite3.connect(DB_FILE)
            buffer = {}
            while True:
                line = ser.readline().decode('utf-8', errors='ignore').strip()
                if not line:
                    continue
                # Regex parsing and line extraction...
        except Exception as e:
            time.sleep(3)
\end{pythonbox}

\section{สรุปคุณค่าทางวิศวกรรมของพิมพ์เขียวซอฟต์แวร์}

พิมพ์เขียวสถาปัตยกรรมซอฟต์แวร์และชุดซอร์สโค้ดในภาคผนวกนี้ สะท้อนถึงการบูรณาการองค์ความรู้ข้ามสาขาวิชาอย่างสมบูรณ์แบบ ได้แก่:
\begin{itemize}[leftmargin=15pt, itemsep=3pt]
    \item \textbf{วิศวกรรมระบบสมองกลฝังตัวระดับต่ำ (Low-level Embedded Systems):} การบริหารจัดการบัส I2C, SPI, RS485 Modbus RTU ร่วมกันอย่างมีเสถียรภาพ และการคำนวณคณิตศาสตร์โครงข่ายประสาทเทียมแบบ Zero-Heap Allocation
    \item \textbf{ปฐพีวิทยาเชิงคำนวณและเคมีดิน (Computational Soil Chemistry):} การนำกฎของ Rhoades, Hilhorst และ Nernst Equation มาสร้างแบบจำลองชดเชยการรบกวนข้ามตัวแปร (Cross-Sensitivity Compensation)
    \item \textbf{วิศวกรรมซอฟต์แวร์คลาวด์และวิทยาการข้อมูล (Cloud Software \& Data Engineering):} การออกแบบสถาปัตยกรรมฐานข้อมูลแบบยืดหยุ่น การพัฒนาเว็บเซอร์วิสแบบอะซิงโครนัสด้วย FastAPI และการสร้างค็อกพิตการเกษตรอัจฉริยะที่เปิดโอกาสให้เกษตรกรและนักวิจัยเข้าถึงข้อมูลแปลงปลูกได้จากทุกที่ทุกเวลา
\end{itemize}
