TsanaPhysics/JC-AGRITecH-AI/latex_book/main.pdf

# JC -AGRITecH + AI Version 1.0

## คู่มือจัดทำระบบฟาร์มอัจฉริยะด้วยปั ญญาประดิษฐ์และการเรียนรู้เชิงลึก

### จากสมองกลฝั งตัวสู่การพยากรณ์แปลงปลูกด้วย Deep Learning

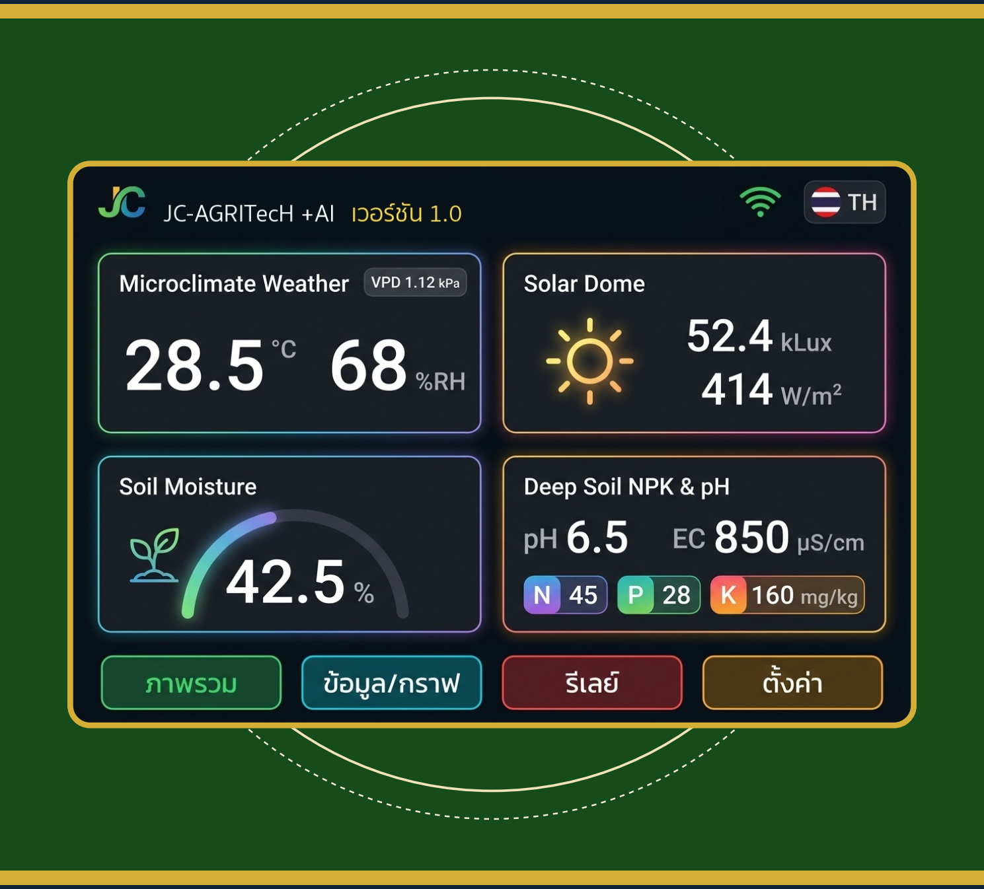
[picture p15: figure]

ผู้ช่วยศาสตราจารย์ ดร.จิรภัทร จันทมาลี | ผู้ช่วยศาสตราจารย์ ดร.ชีวะ ทัศนา
สาขาวิชาจุลชีววิทยา | สาขาวิชาฟิ สิกส์

### คณะวิทยาศาสตร์และเทคโนโลยี มหาวิทยาลัยราชภัฏรำไพพรรณี

พ.ศ. 2569

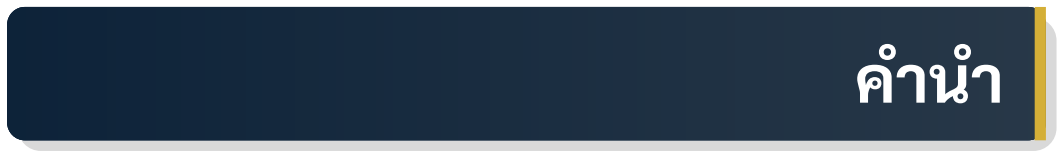
[picture p16: figure]
คำนำ

ความ ก้าวหน้า อย่าง ก้าว กระโดด ของ เทคโนโลยี คอมพิวเตอร์ อินเทอร์เน็ต ของ สรรพ สิ่ง (Internet of Things หรือ IoT) และปั ญญาประดิษฐ์ (Artificial Intelligence หรือ AI) ได้ก่อให้เกิด การเปลี่ยนแปลงเชิงโครงสร้างอย่างลึกซึ้
งต่อภาคการเกษตรกรรมยุคใหม่ จากการเพาะปลูกแบบ ดั้

งเดิมที่อาศัยสัญชาตญาณและการสังเกตสภาพดินฟ้ าอากาศตามฤดูกาล สู่ยุคของ เกษตรกรรม แม่นยำสูง (High-Precision Agriculture) ซึ่

งขับเคลื่อนด้วยข้อมูลเชิงประจักษ์และการตัดสินใจ อัตโนมัติแบบเรียลไทม์
ตำราวิชาการและคู่มือประมวลความรู้เรื่อง JC -AGRITecH + AI Version 1.0 คู่มือจัดทำ ระบบฟาร์มอัจฉริยะด้วยปั ญญาประดิษฐ์และการเรียนรู้เชิงลึก เล่มนี้ เรียบเรียงขึ้นจากผลงาน
วิจัย การทดลองภาคสนาม และประสบการณ์การพัฒนาระบบควบคุมอัจฉริยะจริงของผู้เขียน โดย มุ่งเน้นการบูรณาการองค์ความรู้ข้ามศาสตร์ระหว่าง ฟิ สิกส์ประยุกต์ วิศวกรรมฝั งตัว (Embedded Engineering) และการเรียนรู้เชิงลึก (Deep Learning) เข้าด้วยกันอย่างเป็ นระบบ เพื่อตอบโจทย์ ความต้องการของนักศึกษา นักวิจัย เกษตรกรยุคใหม่ และผู้สนใจในเทคโนโลยีการเกษตร เนื้อหา ภายใน เล่ม แบ่ง ออก เป็ น 5 บท หลัก ที่ครอบคลุม ทุก มิติ ทาง วิศวกรรม ตั้
งแต่ การ
ออกแบบและเชื่อมต่อฮาร์ดแวร์ไมโครคอนโทรลเลอร์สมรรถนะสูง ESP32-S3 บนบอร์ด ATD3.5-S3 และ ATD3.5-S3 Farm1 Shield ร่วมกับเซนเซอร์การเกษตรมาตรฐานอุตสาหกรรม การพัฒนา ไดรเวอร์และระบบคำนวณพารามิเตอร์ทางปฐพีวิทยา การสอบเทียบเซนเซอร์ธาตุอาหารดิน N-P-K และ pH ตามหลักวิทยาศาสตร์ การสร้างระบบส่วนต่อประสานสามภาษาและการเรนเดอร์กราฟิ ก แอนิเมชัน 3 มิติเสมือนจริง ตลอดจนการสตรีมข้อมูลไร้สายแบบ Non-blocking การพัฒนาระบบ เซิร์ฟเวอร์และแดชบอร์ดด้วยภาษาไพทอน และการประยุกต์ใช้โครงข่ายประสาทเทียมแบบ LSTM ในการพยากรณ์ความชื้นในดินและสภาวะแปลงปลูกล่วงหน้า
ผู้ เขียนหวัง เป็ นอย่างยิ่งว่า ตำรา เล่มนี้จะทำหน้าที่

เป็ นสะพาน เชื่อมระหว่างทฤษฎีทาง วิทยาศาสตร์กายภาพและเทคโนโลยีปั ญญาประดิษฐ์เชิงปฏิบัติการ เพื่อร่วมขับเคลื่อนการศึกษา การวิจัย และการพัฒนาภาคการเกษตรกรรมของประเทศไทยสู่ความยั่
งยืนสืบไป

ผู้ช่วยศาสตราจารย์ ดร.จิรภัทร จันทมาลี สาขาวิชาจุลชีววิทยา
i

ผู้ช่วยศาสตราจารย์ ดร.ชีวะ ทัศนา สาขาวิชาฟิ สิกส์
คณะวิทยาศาสตร์และเทคโนโลยี มหาวิทยาลัยราชภัฏรำไพพรรณี กันยายน 2569

ii

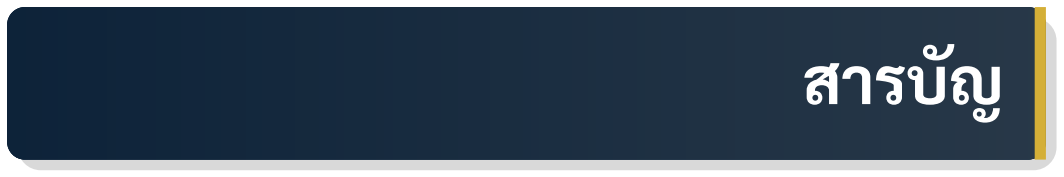
[picture p17: figure]
สารบัญ

คำนำ | i
สารบัญภาพ | vi
สารบัญตาราง | vii
1 สถาปั ตยกรรมฮาร์ดแวร์ระบบแปลงปลูกอัจฉริยะ | 1

1.1.1 แผนภาพ บล็อก สถาปั ตยกรรม ฮาร์ดแวร์ ระบบ รวม (System Hardware

1.2 การจัดสรรขาสัญญาณไมโครคอนโทรลเลอร์ (Pin Assignment Configuration) . 4

1.5.1 การสร้างเฟรมคำสั่
ง Modbus RTU และการคำนวณผลรวมตรวจสอบ CRC16 8
2 วิศวกรรมเฟิ ร์มแวร์ไมโครคอนโทรลเลอร์และการแก้ไขปั ญหาเชิงลึก | 9

2.2.2 แรงดึงระเหยน้ำของบรรยากาศและการประเมินสภาวะทางสรีรวิทยา . . . 10 2.3 สถาปั ตยกรรมแบบจำลองสถานะของเฟิ ร์มแวร์ (Firmware State Machine) . . . 11

iii

2.8.1 แบบจำลองการให้แสงเงาแบบบลินน์-ฟองบนหน่วยประมวลผลฝั งตัว . . . 16

2.9 การสอบเทียบและปรับแต่งพารามิเตอร์เซนเซอร์วัดดิน 7-in-1 Modbus RS485 . 17

2.9.2 ระบบชดเชยการประมาณค่าจากสภาพนำไฟฟ้ า (EC-to-NPK Fallback

3 สถาปั ตยกรรมการสื่อสารข้อมูลไร้สายและการจัดเก็บอนุกรมเวลา | 20

3.3 โค้ดโปรแกรมการส่งข้อมูลแบบไม่ปิ ดกั้น (Non-blocking HTTP Dispatch) . . . . 22 3.4 โครงสร้างข้อมูลและการบูรณาการกับ Google Firebase Realtime Database . . 23

4 การพัฒนาระบบฐานข้อมูลและแดชบอร์ดด้วยภาษาไพทอน | 25
5 ปั ญญาประดิษฐ์และการเรียนรู้เชิงลึกสำหรับเกษตรกรรมแม่นยำ | 31

5.4 สถาปั ตยกรรม TinyML บนชิป ESP32-S3: การชดเชยค่า NPK, pH และความชื้น

5.4.1 ปั ญหาทางฟิ สิกส์-เคมีดินและการแทรกแซงข้ามมิติ (Cross-Sensitivity) . 35 5.4.2 สถาปั ตยกรรมโครงข่ายประสาทเทียม Multi-Layer Perceptron (MLP) . 36

5.4.4 การแปลงเป็ น C++ Inference Engine และการทำงานบน ESP32-S3 . . 36 5.4.5 การบูรณาการระบบแสดงผลและการส่งผ่านโทรมาตร (Telemetry Pipeline) 39

iv

5.5 มาตรฐานแถบสีเทียบค่าเคมีดิน NPK และ pH สู่สถาปั ตยกรรมการแสดงผลคู่ขนาน 39 5.5.1 การ วิเคราะห์ กลไก ปฏิกิริยา เคมี และ การ เกิด สี (Analytical Chemistry

5.5.2 ตารางมาตรฐานแถบสีเทียบเคียงและช่วงความเข้มข้นเชิงปริมาณ . . . . 41

A สารบบพรอมพ์บริบทและวิศวกรรมคำสั่งในการพัฒนาระบบ | 43
A.4.1 พรอมพ์บริบทการสืบสวนและแก้ไขหน้าจอดำ (Hardware RCA Prompt) | 45
A.4.2 พรอมพ์บริบทการออกแบบโมเดล TinyML ชดเชยอุณหภูมิและความชื้น . 46 A.4.3 พรอมพ์สืบค้นแถบสีมาตรฐาน NPK/pH และการออกแบบ Dual Visual UI 46 A.5 สารบบลำดับพรอมพ์การพัฒนาจริง (Prompt Trajectory: Prompts 1–61) . . . 47
B พิมพ์เขียวสถาปั ตยกรรมซอฟต์แวร์และซอร์สโค้ดระบบ JC -AGRITecH + AI | 50
B.1 บทนำและภาพรวมสถาปั ตยกรรมระบบซอฟต์แวร์ (End-to-End System Archi-

B.2 เฟิ ร์มแวร์สมองกลฝั งตัวและการจัดสรรพินฮาร์ดแวร์ (Embedded Firmware) . . . 51

B.2.2 เครื่องยนต์ อนุมาน โครง ข่าย ประสาท เทียม ระดับ ไมโคร คอนโทรลเลอร์

B.4 สถาปั ตยกรรมคลาวด์ ฐานข้อมูลเชิงสัมพันธ์ และแดชบอร์ด (Cloud & Backend) . 62

บรรณานุกรม | 71
ดัชนีสืบค้นคำสำคัญ | 73
ประวัติผู้เขียน | 74

v

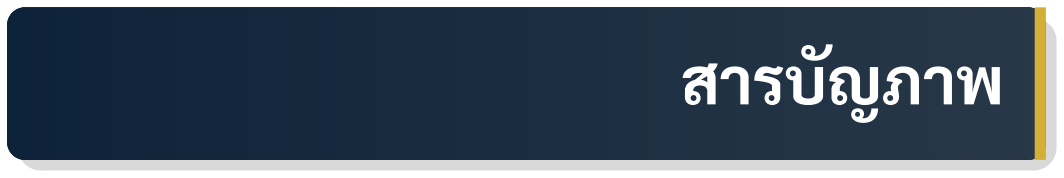
[picture p18: figure]
สารบัญภาพ

1.1 บอร์ดควบคุมหลัก ATD3.5-S3 พร้อมจอภาพ IPS | | 2
1.2 บอร์ดขยายสัญญาณ Farm1 Shield สำหรับฟาร์ม | | 2
1.3 แผนภาพบล็อกสถาปั ตยกรรมฮาร์ดแวร์ระบบรวม JC -AgriTech + AI | | 2
1.4 ลักษณะการต่อสายสัญญาณเซนเซอร์เข้ากับเทอร์มินัลบล็อกบนบอร์ด ATD3.5-S3
Farm1 Shield | | 3
1.5 เซนเซอร์ SHT45 วัดอุณหภูมิและความชื้นในปลอกกรองโลหะซินเตอร์ | | 5
1.6 เซนเซอร์โดมตะวัน BH1750 วัดความเข้มแสงและรังสีอาทิตย์ | | 5
1.7 เซนเซอร์แท่งวัดความชื้นในดินผิวดิน Soil Stick เกษตรไทย IoT | | 6
1.8 โพรบวัดคุณสมบัติดิน 7-in-1 Modbus RS485 สำหรับติดตั้
งในเขตรากพืช . . . . 7

2.1 แผนผังสถานะการทำงานของระบบเฟิ ร์มแวร์ JC -AgriTech + AI (Firmware FSM) 11
2.2 สภาวะจอดำจากขาแบล็กไลต์ขัดแย้งกับ Flash | 12
2.3 หน้าจอติดสว่างสมบูรณ์แบบหลังการทำ RCA | 12

3.1 สถาปั ตยกรรมท่อส่งข้อมูลแบบไม่ปิ ดกั้น (Non-blocking Resilient Pipeline) บน
ESP32-S3 Dual-Core | 21

4.1 สถาปั ตยกรรม Python Full-Stack 3 ชั้น (Edge Ingestion, Backend API, Ana-
lytics Dashboard) | 26

5.1 สถาปั ตยกรรม โครงข่ายประสาท เทียมแบบคลี่ขยายตาม เวลา (Unrolled LSTM
Multi-step Architecture) | 33
B.1 สถาปั ตยกรรมซอฟต์แวร์แบบหลายชั้นของระบบ JC -AGRITecH + AI | 51

vi

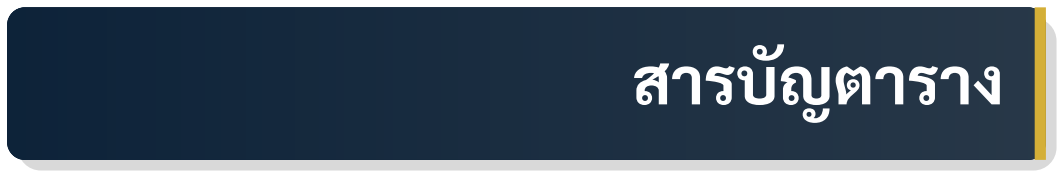
[picture p19: figure]
สารบัญตาราง

1.1 การกำหนดค่าพารามิเตอร์และรีจิสเตอร์ Modbus RTU ของเซนเซอร์ดินรุ่น SN-3002 7

2.1 เกณฑ์การประเมินสภาวะความเครียดของพืชตามระดับความดันไอน้ำอิ่มตัว (VPD
Index) | 11
2.2 พารามิเตอร์การสอบเทียบเซนเซอร์ดิน 7-in-1 ในระบบ JC -AgriTech + AI . . . . 18
4.1 รายการ API Endpoints ของระบบ JC -AgriTech + AI Telemetry Hub | 28

5.1 รายละเอียดตัวแปรอินพุตและเอาต์พุตของโมเดล TinyML Soil Neural Calibrator 37 5.2 ดัชนีชี้วัดความแม่นยำของโมเดล TinyML Soil Neural Calibrator บนชุดทดสอบ . 37 5.3 เกณฑ์มาตรฐานแถบสีเทียบเคียงและช่วงความเข้มข้นเชิงปริมาณของธาตุอาหาร
ในดิน NPK และ pH | 42

A.1 เมทริกซ์การจำแนกประเภทและประวัติ วิวัฒนาการของพรอมพ์ตลอด โครงการ
(Prompts 1–61) | 48

vii

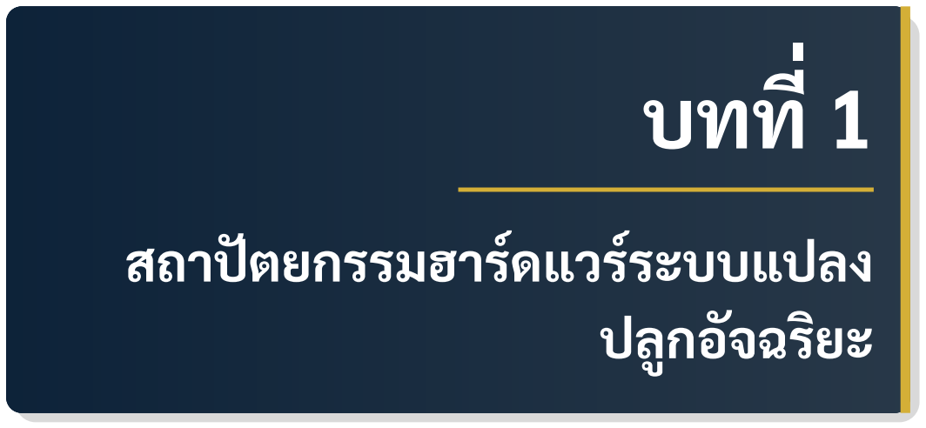
[picture p20: figure]
บทที; สถาปั ตยกรรมฮาร์ดแวร์ระบบแปลง ปลูกอัจฉริยะ

ระบบเกษตรกรรมแม่นยำสูง (Precision Agriculture) จำเป็ นต้องอาศัยการตรวจวัดสภาวะ แวดล้อมที่ครอบคลุมทั้
ง 3 มิติหลัก ได้แก่ บรรยากาศรอบทรงพุ่ม (Microclimate) พลังงานรังสีแสง อาทิตย์ (Solar Radiation) และคุณสมบัติทางกายภาพเคมีในเขตรากพืช (Edaphic Zone) บทนี้นำ เสนอการออกแบบสถาปั ตยกรรมฮาร์ดแวร์ของระบบ JC -AgriTech + AI โดยประยุกต์ใช้ไมโคร คอนโทรลเลอร์สมรรถนะสูงตระกูล ESP32-S3 บนบอร์ด ATD3.5-S3 ร่วมกับบอร์ดขยายสัญญาณ ATD3.5-S3 Farm1 Shield

## 1.1 ภาพ รวม สถาปั ตยกรรม บอร์ด ควบคุม และ บอร์ด ขยายสัญญาณ

บอร์ดควบคุมหลักของระบบคือ ATD3.5-S3 ซึ่

งขับเคลื่อนด้วยชิปประมวลผล Dual-core Xtensa LX7 ความเร็วสัญญาณนาฬิกา 240 MHz มีหน่วยความจำ SRAM ขนาด 320 KB และ Flash Memory ขนาด 8 MB ในโหมด Dual I/O (DIO) พร้อมหน้าจอแสดงผลสีแบบสัมผัสชนิด IPS ขนาด 3.5 นิ้ว ความละเอียด 480×320 พิกเซล ควบคุมด้วยไอซีขับจอ ST7796 ผ่านการเชื่อมต่อแบบ SPI ความเร็วสูง
การ เชื่อม ต่อ เซนเซอร์ ภาค สนาม กระทำ ผ่าน บอร์ด ขยาย สัญญาณ ATD3.5-S3 Farm1 Shield ซึ่
งเสียบประกบเข้ากับบอร์ดหลักโดยตรง ช่วยลดความซับซ้อนของการเดินสายสัญญาณ และเพิ่มความคงทนต่อสภาพแวดล้อมในโรงเรือน โดยบอร์ดขยายสัญญาณประกอบด้วยจุดเชื่อม ต่อมาตรฐาน 3 กลุ่มหลัก ได้แก่ ขั้วต่อสัญญาณดิจิทัล I2C ขั้วต่อสัญญาณแอนะล็อกสำหรับ วัด ความชื้นในดิน และขั้วต่อการสื่อสารเชิงอุตสาหกรรม RS485 พร้อมภาคจ่ายไฟเลี้ยง 12 V สำหรับ โพรบวัดดินลึก

1

บทที่1 สถาปั ตยกรรมฮาร์ดแวร์ระบบแปลงปลูกอัจฉริยะ | 2


ภาพที่ 1.1 บอร์ด ควบคุม หลัก ATD3.5-S3 พร้อมจอภาพ IPS

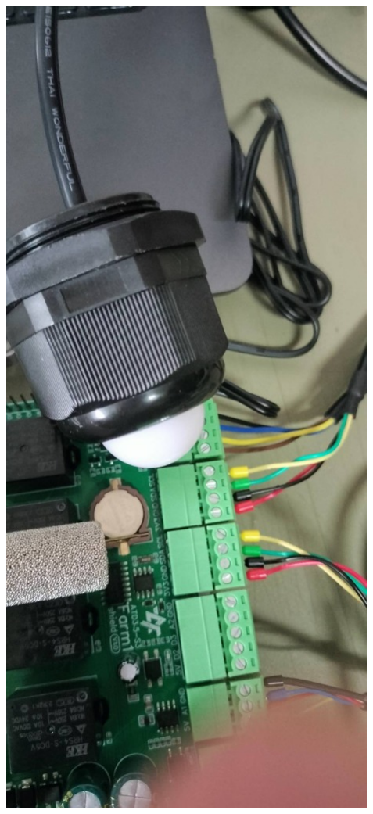
[picture p21: figure]

ภาพที่ 1.2 บอร์ด ขยาย สัญญาณ Farm1 Shield สำหรับฟาร์ม

## 1.1.1 แผนภาพบล็อก สถาปั ตยกรรม ฮาร์ดแวร์ระบบ รวม (System Hardware Architecture)

สถาปั ตยกรรมการเชื่อมโยงสัญญาณระหว่างหน่วยประมวลผลหลัก บอร์ดขยาย

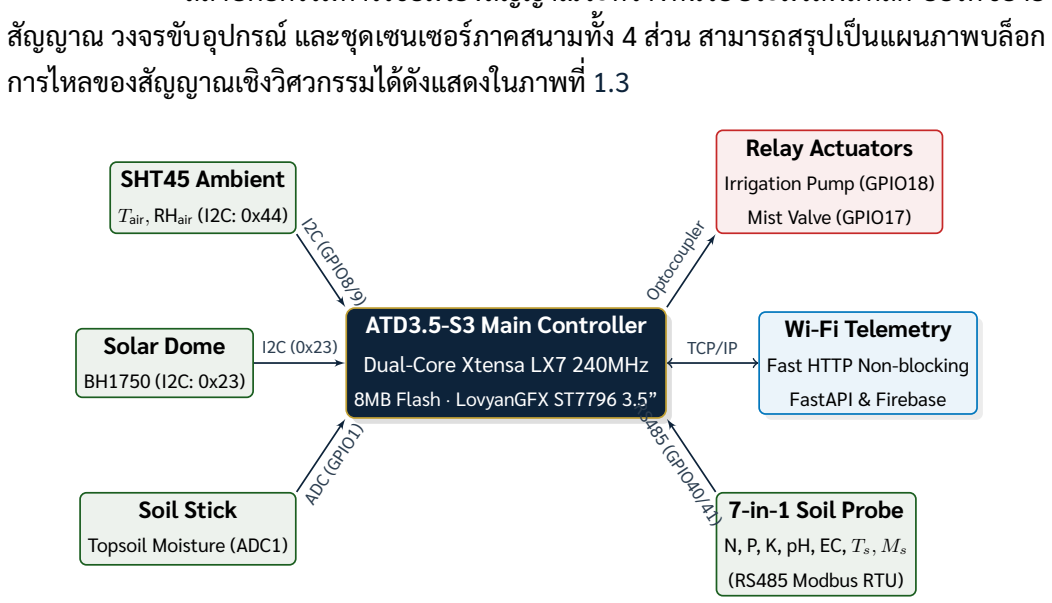
[picture p22: figure]
สัญญาณ วงจรขับอุปกรณ์ และชุดเซนเซอร์ภาคสนามทั้ ง 4 ส่วน สามารถสรุปเป็ นแผนภาพบล็อก การไหลของสัญญาณเชิงวิศวกรรมได้ดังแสดงในภาพที่ 1.3; ATD3.5-S3 Main Controller Dual-Core Xtensa LX7 240MHz 8MB Flash · LovyanGFX ST7796 3.5”; SHT45 Ambient; Tair, RHair (I2C: 0x44); Solar Dome; Soil Stick; Topsoil Moisture (ADC1); 7-in-1 Soil Probe; N, P, K, pH, EC, Ts, Ms (RS485 Modbus RTU); Relay Actuators; Irrigation Pump (GPIO18) Mist Valve (GPIO17); Wi-Fi Telemetry; Fast HTTP Non-blocking FastAPI & Firebase; I2C (GPIO8/9); ADC (GPIO1); RS485 (GPIO40/41); Optocoupler; TCP/IP

ภาพที่1.3 แผนภาพบล็อกสถาปั ตยกรรมฮาร์ดแวร์ระบบรวม JC -AgriTech + AI

มหาวิทยาลัยราชภัฏรำไพพรรณี

บทที่1 สถาปั ตยกรรมฮาร์ดแวร์ระบบแปลงปลูกอัจฉริยะ | 3


ภาพที่ 1.4 ลักษณะการต่อสายสัญญาณเซนเซอร์เข้ากับเทอร์มินัลบล็อกบนบอร์ด ATD3.5-S3 Farm1 Shield

บทที่1 สถาปั ตยกรรมฮาร์ดแวร์ระบบแปลงปลูกอัจฉริยะ | 4

## 1.2 การ จัดสรร ขา สัญญาณ ไมโคร คอนโทรลเลอร์ (Pin Assignment Configuration)

เพื่อ ให้ ระบบ สามารถ ทำงาน ร่วม กับ บอร์ด Farm1 Shield ได้ อย่าง เสถียร และ ป้ องกัน ความ ขัด แย้ง ของ ฮาร์ดแวร์ ภายใน ขา สัญญาณ ทั้
งหมด ได้ รับ การ กำหนด ไว้ ใน ไฟล์ เฮดเด อร์

PinConfigs.h ดังนี้

การนิยามขาสัญญาณฮาร์ดแวร์ในไฟล์ PinConfigs.h

1 #ifndef PIN_CONFIGS_H

2 #define PIN_CONFIGS_H

3

4 // 1. IPS Display 3.5” Controller: ST7796 (SPI Bus)

5 #define LCD_MOSI_PIN | 11
6 #define LCD_MISO_PIN | 13
7 #define LCD_SCK_PIN | 12
8 #define LCD_CS_PIN | 10
9 #define LCD_DC_PIN | 14
10 #define LCD_RST_PIN | -1
11 #define LCD_BL_PIN | 38 | // Hardware Backlight control pin (Active

HIGH)
12

13 // 2. Shared I2C Sensor Bus (SHT45 & BH1750 Dome)

14 #define I2C_SDA_PIN | 9 | // I2C Serial Data (Yellow Wire)
15 #define I2C_SCL_PIN | 8 | // I2C Serial Clock (Green Wire)

16

17 // 3. Analog ADC Input (Surface Soil Stick)

18 #define SOIL_STICK_PIN | 1 | // ADC1 Channel 0 (Terminal A1 on Shield)

19

20 // 4. Industrial RS485 Modbus RTU Port (7-in-1 Soil Sensor)

21 #define RS485_RX_PIN | 41 | // Hardware UART RX Pin
22 #define RS485_TX_PIN | 40 | // Hardware UART TX Pin
23 #define RS485_BAUD | 4800

24

25 // 5. Actuator Control Relays (Active LOW Opto-isolated)

26 #define RELAY_PUMP_PIN | 18 | // Main Irrigation Water Pump Relay
27 #define RELAY_MIST_PIN | 17 | // Evaporative Cooling Misting Valve Relay

28

29 #endif // PIN_CONFIGS_H

บทที่1 สถาปั ตยกรรมฮาร์ดแวร์ระบบแปลงปลูกอัจฉริยะ | 5

## 1.3 การสื่อสารผ่านบัส I2C ร่วมสำหรับเซนเซอร์บรรยากาศ และแสงสว่าง

การตรวจวัดสภาวะบรรยากาศรอบแปลงปลูกใช้เซนเซอร์ความแม่นยำสูง 2 ชนิดที่สื่อสาร ผ่านโพรโทคอล I2C (Inter-Integrated Circuit) ร่วมกันบนโครงสร้างบัสเดียวกัน ได้แก่

## 1.3.1 เซนเซอร์ อุณหภูมิ และ ความชื

้

## นสัมพัทธ์ ใน อากาศ SHT45

เซนเซอร์SHT45 ผลิตโดยบริษัท Sensirion บรรจุอยู่ในปลอกกรองโลหะซินเตอร์ (Sintered Metal Filter) ที่สามารถกันละอองน้ำและฝุ่ นละอองในโรงเรือนได้อย่างมีประสิทธิภาพ โดยมีแอดเดรสฮาร์ดแวร์ประจำอุปกรณ์คือ 0x44 มีความคลาดเคลื่อนในการวัดอุณหภูมิต่ำเพียง

±0.1

◦C และความชื้นสัมพัทธ์±1.5 %RH

## 1.3.2 เซนเซอร์ความเข้มแสงกันน้ำโดมตะวัน

เซนเซอร์โดมตะวัน (Sun Dome Sensor) ใช้ชิปตรวจวัดแสงดิจิทัล BH1750FVI ที่ครอบด้วยโดมกระจายแสงทรงกลมสีขาวขุ่นเพื่อปรับแก้ค่าความเข้มแสงให้เป็ นไปตามกฎโคไซน์ ของแลมเบิร์ต (Lambert’s Cosine Law) สื่อสารผ่านบัส I2C ด้วยแอดเดรส 0x23 สามารถวัดความ เข้มแสงได้ตั้

งแต่ 1 ถึง 65,535 Lux นอกจากนี้ ระบบยังแปลงค่าความเข้มแสง Lux เป็ นค่าความ หนาแน่นฟลักซ์พลังงานรังสีดวงอาทิตย์ (Solar Radiation Flux Density) ในหน่วยวัตต์ต่อตาราง เมตร (W/m²

) โดยอาศัยความสัมพันธ์เชิงฟิ สิกส์Rsolar = Lux × 0.0079 W/m² ซึ่ งมีความสำคัญ
อย่างยิ่งต่อการประเมินการสะสมความร้อนและการระเหยน้ำในโรงเรือน


ภาพที่1.5 เซนเซอร์ SHT45 วัดอุณหภูมิและ ความชื้นในปลอกกรองโลหะซินเตอร์


ภาพที่ 1.6 เซนเซอร์ โดม ตะวัน BH1750 วัด ความเข้มแสงและรังสีอาทิตย์

เนื่องจากเซนเซอร์ SHT45 และโดมตะวัน BH1750 มีแอดเดรสบนบัส I2C ที่ ไม่ซ้ำ
กัน จึงสามารถต่อสายสัญญาณร่วมกันบนเทอร์มินัลบล็อกเดียวกันได้โดยตรง จากการตรวจสอบด้วย ระบบสแกนสัญญาณฮาร์ดแวร์ พบว่าการต่อสายจริงบนบอร์ด Farm1 Shield ได้กำหนดให้สายสี เหลืองเป็ นสายข้อมูล SDA (GPIO9) และ สายสีเขียวเป็ นสายสัญญาณนาฬิกา SCL (GPIO8)

บทที่1 สถาปั ตยกรรมฮาร์ดแวร์ระบบแปลงปลูกอัจฉริยะ | 6

## 1.4 การวัดความชื

้

## นในดินผิวดินด้วยสัญญาณแอนะล็อก แบบคาปาซิทีฟ

การตรวจวัดความชื้นบริเวณผิวดินระดับความลึก 0 ถึง 10 เซนติเมตร ใช้ เซนเซอร์แท่ง วัด ความชื้น Soil Stick เกษตร ไทย IoT ซึ่

ง ทำงาน ด้วย หลัก การ เปลี่ยนแปลง ค่า ความ จุ ไฟฟ้ า (Capacitive Method) คลื่นความถี่สูง ซึ่
งมีข้อได้เปรียบเหนือก้านวัดความต้านทานไฟฟ้ า (Resistive Probes) ทั่วไป เนื่องจากไม่มีกระแสไฟฟ้ าไหลผ่านเนื้อดินโดยตรง จึงไม่เกิดการกัดกร่อนจากปฏิ กิริยาอิเล็กโทรลิซิส (Electrolysis Corrosion)


ภาพที่1.7 เซนเซอร์แท่งวัดความชื้นในดินผิวดิน Soil Stick เกษตรไทย IoT

สัญญาณแอนะล็อกจาก Soil Stick ถูกป้ อน เข้าสู่ขาอะนาล็อก A1 (GPIO1) ของ ไมโคร คอนโทรลเลอร์ ESP32-S3 ซึ่
งถูกโปรแกรมให้ทำงานในโหมดตัวแปลงแอนะล็อกเป็ นดิจิทัล (ADC) ความละเอียด 12 บิต (ช่วงค่า 0 ถึง 4,095) พร้อมตั้

งค่าการลดทอนสัญญาณที่

11 dB เพื่อรองรับ
แรงดันไฟสูงสุด 3.1 V ค่าความชื้นสัมพัทธ์ในดิน (Msoil) คำนวณผ่านสมการเชิงเส้นดังนี้

Msoil =

(
ADCair − ADCraw

ADCair − ADCwater )
× 100% | (1.1)

โดยที่ ADCair = 2950 แทนค่าสัญญาณดิบในอากาศแห้ง (ความชื้น 0%) และ ADCwater = 1450 แทนค่าสัญญาณดิบเมื่อจุ่มในน้ำเปล่า (ความชื้น 100%)

## 1.5 การสื่อสารเชิงอุตสาหกรรม RS485 สำหรับคุณสมบัติ ดิน 7 พารามิเตอร์

สำหรับการวิเคราะห์คุณสมบัติของดินในเขตรากพืชเชิงลึก (ความลึก 15 ถึง 30 เซนติเมตร) ระบบติดตั้
ง เซนเซอร์วัดดินอุตสาหกรรมแบบมัลติพารามิเตอร์รุ่น SN-3002-TR-ECTHNPKPH-N01 ซึ่
งมี เข็ม วัดสแตน เลสสตีลทางการแพทย์ สามารถ วัดค่าพร้อมกัน ได้ 7 พารามิเตอร์ ได้แก่ ความชื้นในดิน อุณหภูมิดิน สภาพนำไฟฟ้ า (EC) กรด-ด่างดิน (pH) และปริมาณธาตุอาหารหลัก N-P-K

บทที่1 สถาปั ตยกรรมฮาร์ดแวร์ระบบแปลงปลูกอัจฉริยะ | 7


ภาพที่1.8 โพรบวัดคุณสมบัติดิน 7-in-1 Modbus RS485 สำหรับติดตั้ งในเขตรากพืช

ตารางที่1.1 การกำหนดค่าพารามิเตอร์และรีจิสเตอร์ Modbus RTU ของเซนเซอร์ดินรุ่น SN-3002

พารามิเตอร์ | แอดเดรส รี จิ ส
| เตอร์ | หน่วยวัด | ตัวคูณสเกลข้อมูล
ความชื้น ใน ดิน (Mois- ture) | 0x0000 | % | หารด้วย 10 (ทศนิยม 1
| | | ตำแหน่ง)
อุณหภูมิ ดิน (Tempera- ture) | 0x0001 | ◦C | หารด้วย 10 (ทศนิยม 1
| | | ตำแหน่ง)
สภาพนำไฟฟ้ า (EC) | 0x0002 | µS/cm | จำนวนเต็มค่าตรง
กรด-ด่างดิน (pH) | 0x0003 | pH | หารด้วย 10 หรือ 100
ไนโตรเจนที่
ใช้ประโยชน์ (N) | 0x0004 | mg/kg | จำนวนเต็มค่าตรง

ฟอสฟอรัสที่
ใช้ประโยชน์ (P) | 0x0005 | mg/kg | จำนวนเต็มค่าตรง
โพแทสเซียม | ที่
ใช้
ประโยชน์ (K) | 0x0006 | mg/kg | จำนวนเต็มค่าตรง

บทที่1 สถาปั ตยกรรมฮาร์ดแวร์ระบบแปลงปลูกอัจฉริยะ | 8

ไมโคร คอนโทรลเลอร์ ESP32-S3 ติดต่อ กับ เซนเซอร์ ผ่าน ชิป แปลง สัญญาณ RS485 Transceiver โดยใช้พอร์ตสื่อสารอนุกรมฮาร์ดแวร์พอร์ตที่ 2 (HardwareSerial 2) กำหนดขา RX เป็ น GPIO41 และขา TX เป็ น GPIO40 ที่อัตราความเร็วรับส่งข้อมูล (Baud Rate) 4,800 bps

## 1.5.1 การสร้างเฟรมคำสั่ง Modbus RTU และการคำนวณ ผลรวมตรวจสอบ CRC16

เฟรมคำสั่
งขออ่านข้อมูลแบบ Read Holding Registers (Function Code 0x03) เพื่ออ่านข้อมูล 7 รีจิสเตอร์ต่อเนื่องกัน มีโครงสร้างขนาด 8 ไบต์ ประกอบด้วย

[0x01] [0x03] [0x00] [0x00] [0x00] [0x07] [0x04] [0x08]
โดยที่สอง ไบต์ สุดท้าย คือ รหัส ตรวจ สอบ ความ ถูก ต้อง CRC16 (Cyclic Redundancy Check) ซึ่ ง
คำนวณผ่านพหุนาม x
16 + x

15 + x

2 + 1 (ค่าโพลีนอมิอัล 0xA001) อัลกอริทึมการคำนวณในภาษา C++ ถูกอิมพลีเมนต์ดังนี้

อัลกอริทึมการคำนวณ CRC16 Modbus ในภาษา C++

1 uint16_t calculateModbusCRC(const uint8_t *buffer, size_t length) {

2 | uint16_t crc = 0xFFFF;
3 | for (size_t pos = 0; pos < length; pos++) {
4 | crc ^= (uint16_t)buffer[pos];
5 | for (int i = 8; i != 0; i--) {
6 | if ((crc & 0x0001) != 0) {
7 | crc >>= 1;
8 | crc ^= 0xA001;
9 | } else {
10 | crc >>= 1;
11 | }
12 | }
13 | }
14 | return crc;

15 }

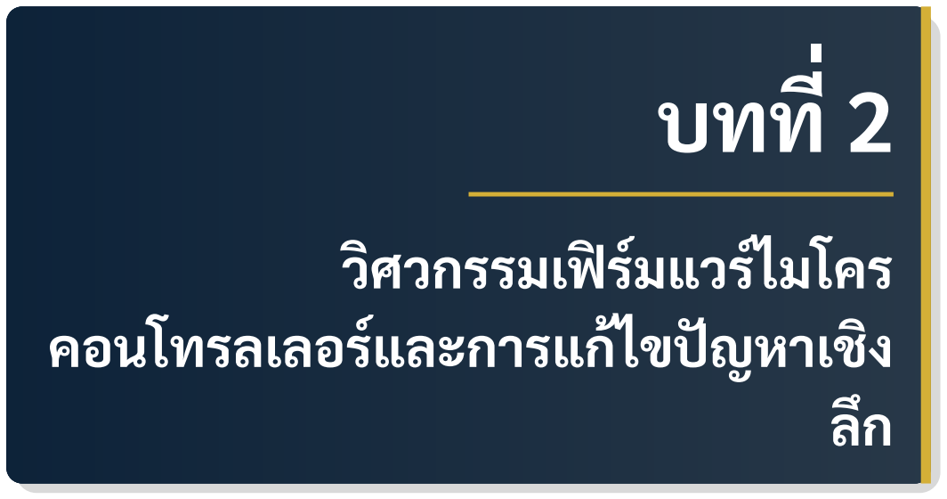
[picture p23: figure]
บทที; วิศวกรรมเฟิ ร์มแวร์ไมโคร คอนโทรลเลอร์และการแก้ไขปั ญหาเชิง ลึก

ความสำเร็จของการประยุกต์ใช้ระบบสมองกลฝั งตัวในแปลงเกษตรกรรมขึ้นอยู่กับความ เสถียร ของ เฟิ ร์มแวร์ ความ สามารถ ใน การ รองรับ ข้อ ผิด พลาด ของ สัญญาณ ฮาร์ดแวร์ และ การ ประมวลผลข้อมูลทางฟิ สิกส์ได้อย่างถูกต้องแม่นยำ บทนี้นำเสนอโครงสร้างเฟิ ร์มแวร์ ระบบคำนวณ ทางปฐพีวิทยา และกระบวนการวิเคราะห์หาสาเหตุ เชิงลึก (Root Cause Analysis หรือ RCA) ใน การแก้ไขปั ญหาทางวิศวกรรมที่
เกิดขึ้นระหว่างการพัฒนาจริง

## 2.1 โค รง สร้าง เฟิ ร์มแวร์ และ การ จัดการ ทรัพยากร บน ระบบ PlatformIO

โครงการได้รับการพัฒนาภายใต้สภาพแวดล้อม PlatformIO ร่วมกับเฟรมเวิร์ก Arduino บนระบบปฏิบัติการ macOS โดยมีการจัดโครงสร้างซอฟต์แวร์แบบโมดูลาร์ (Modular Architecture) เพื่อแยกส่วนควบคุมฮาร์ดแวร์ออกจากลอจิกการตัดสินใจทางเกษตรกรรม

โมดูลหลักของเฟิ ร์มแวร์ระบบ JC -AgriTech + AI

- PinConfigs.h นิยาม การ จัดสรร ขา สัญญาณ ไมโคร คอนโทรลเลอร์ ESP32-S3 ให้ ตรงกับวงจรจริง
- UserConfigs.h รวบรวมพารามิเตอร์การตั้
งค่าของผู้ใช้ เช่น แอดเดรสเซนเซอร์ ค่า การคาลิเบรต ADC ข้อมูลเครือข่าย Wi-Fi และ IP ปลายทาง

9

บทที่2 วิศวกรรมเฟิ ร์มแวร์ไมโครคอนโทรลเลอร์และการแก้ไขปั ญหาเชิงลึก | 10
- AgriSensors.cpp ไดรเวอร์ ระดับ ล่าง สำหรับ สื่อสาร กับ SHT45, BH1750, Soil Stick และเซนเซอร์ 7-in-1 Modbus RTU
- DisplayManager.cpp ไดรเวอร์กราฟิ กและระบบแสดงผลหน้าปั ดบนจอ LCD 3.5 นิ้ว ผ่านไลบรารี LovyanGFX
- CloudDataManager.cpp ระบบจัดการ เครือข่าย ไร้สาย ซิงค์ เวลามาตรฐาน โลก NTP และสตรีมข้อมูลทาง HTTP/HTTPS
- main.cpp ลูปควบคุมหลักที่ประสานการอ่านค่า การตัดสินใจเปิ ด-ปิ ดรีเลย์ และการ อัปเดตหน้าปั ด

## 2.2 การคำนวณพารามิเตอร์ทางปฐพีวิทยาและสภาวะ บรรยากาศ

นอกจากค่าพื้นฐานที่อ่านได้จากเซนเซอร์ ระบบยังฝั งอัลกอริทึมการคำนวณดัชนีชี้วัดทาง สรีรวิทยาของพืชที่มีความสำคัญสูงต่อการจัดการน้ำและการระบายความร้อน ได้แก่

## 2.2.1 จุดน้ำค้างในบรรยากาศ

จุดน้ำค้าง (Dew Point Temperature หรือ Td) คำนวณผ่านสมการมักนุส-เทเทนส์ (Magnus-Tetens Equation) ซึ่ งมีความแม่นยำสูงในช่วงอุณหภูมิ0 ถึง 60 ◦C

α(T, RH) = a · T
b + T

+ ln (
RH

100)
, Td =

b · α(T, RH)
a − α(T, RH)

(2.1)

โดยกำหนดค่าสัมประสิทธิ์
เชิงประจักษ์a = 17.27 และ b = 237.7

◦C

## 2.2.2 แรง ดึง ระเหย น้ำ ของ บรรยากาศ และ การ ประเมิน สภาวะทางสรีรวิทยา

แรงดึงระเหยน้ำ (Vapor Pressure Deficit หรือ VPD) มีหน่วย เป็ นกิโลปาสกาล (kPa) เป็ นตัวแปรที่บ่งบอกความสามารถในการคายน้ำและการ เปิ ด-ปิ ดปากใบของพืช ค่า VPD คำนวณจากผลต่างระหว่างความดันไอน้ำอิ่มตัว (V Psat) และความดันไอน้ำจริง (V Pact)

V Psat = 0.61078 exp (
17.27 · T
T + 237.3

)
, V Pact = V Psat ×

(
RH

100)
(2.2)
VPD = V Psat − V Pact | (2.3)

บทที่2 วิศวกรรมเฟิ ร์มแวร์ไมโครคอนโทรลเลอร์และการแก้ไขปั ญหาเชิงลึก | 11

ตารางที่2.1 เกณฑ์การประเมินสภาวะความเครียดของพืชตามระดับความดันไอน้ำอิ่มตัว (VPD Index)

ช่วงค่า VPD (kPa) สภาวะบรรยากาศ ผลกระทบทางสรีรวิทยาของพืชและการ จัดการ
< 0.40 | ชื้นจัดเกินไป (Under-
transpiration)

เสี่ยงต่อการเกิดโรคเชื้อรา ปากใบไม่ระบายน้ำ พืชขาดแคลเซียม
0.40 − 0.80 | สภาวะ อ่อน โยน
(Propagation
Zone)

เหมาะสำหรับระยะเพาะเมล็ด อนุบาลต้นกล้า หรือแปลงปั กชำ

0.80 − 1.20 ช่วง เหมาะ สม ที่สุด (Optimal Zone)

อัตราการสังเคราะห์แสงและการดูดซึมธาตุ อาหารสูงสุด
1.20 − 1.60 | ค่อน ข้าง แห้ง (Mild
Water Stress)

เหมาะสำหรับพืชทนแล้ง หรือการควบคุมความ หวานในผลไม้
> 1.60 | แห้ง แล้ง จัด (Severe
Water Stress)

ปากใบปิ ดสนิท พืชเหี่ยวเฉา ชะงักการเจริญ เติบโต ต้องพ่นหมอก

## 2.3 สถาปั ตยกรรม แบบ จำลอง สถานะ ของ เฟิ ร์มแวร์ (Firmware State Machine)

การประมวลผลภายในไมโครคอนโทรลเลอร์ ESP32-S3 ถูกควบคุมด้วยระบบ Finite State Machine (FSM) ที่มีรอบการทำงานอย่างเป็ นระบบ เพื่อให้มั่นใจว่าการอ่านเซนเซอร์ การคำนวณ

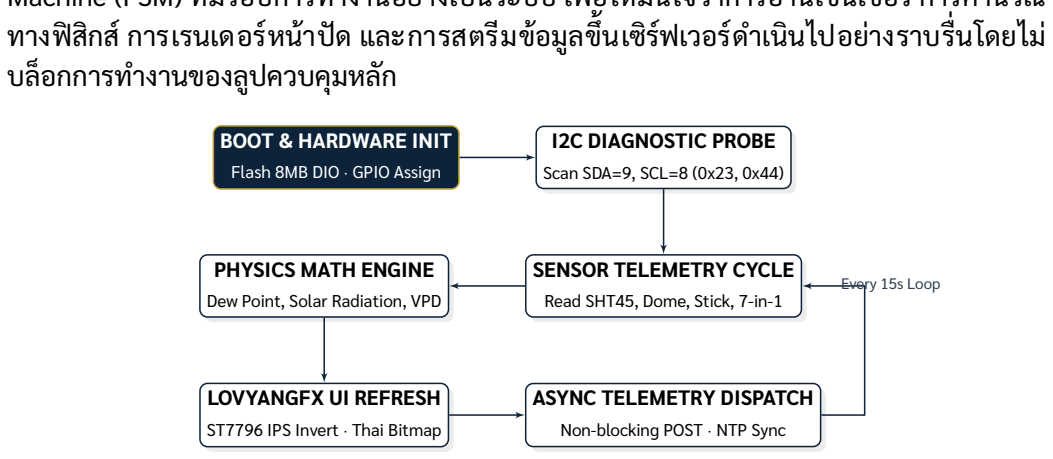
[picture p24: figure]
ทางฟิ สิกส์ การเรนเดอร์หน้าปั ด และการสตรีมข้อมูลขึ้นเซิร์ฟเวอร์ดำเนินไปอย่างราบรื่นโดยไม่ บล็อกการทำงานของลูปควบคุมหลัก; BOOT & HARDWARE INIT; Flash 8MB DIO · GPIO Assign; I2C DIAGNOSTIC PROBE; Scan SDA=9, SCL=8 (0x23, 0x44); SENSOR TELEMETRY CYCLE; Read SHT45, Dome, Stick, 7-in-1; PHYSICS MATH ENGINE; Dew Point, Solar Radiation, VPD; LOVYANGFX UI REFRESH; ST7796 IPS Invert · Thai Bitmap; ASYNC TELEMETRY DISPATCH; Non-blocking POST · NTP Sync; Every 15s Loop

ภาพที่2.1 แผนผังสถานะการทำงานของระบบเฟิ ร์มแวร์ JC -AgriTech + AI (Firmware FSM)

บทที่2 วิศวกรรมเฟิ ร์มแวร์ไมโครคอนโทรลเลอร์และการแก้ไขปั ญหาเชิงลึก | 12

## 2.4 การวิเคราะห์สาเหตุเชิงลึกและการแก้ไขปั ญหาหน้า จอมืดสนิท

ในขั้นตอนการติดตั้

งโปรแกรมเบื้องต้น พบปั ญหาหน้าจอ LCD แสดงผลเป็ นจอมืดสนิท ไม่มีข้อความหรือกราฟิ กใดๆ ปรากฏ กระบวนการสืบสวนเชิงลึกพบสาเหตุสำคัญ 2 ประการที่ซ้อน ทับกันอยู่

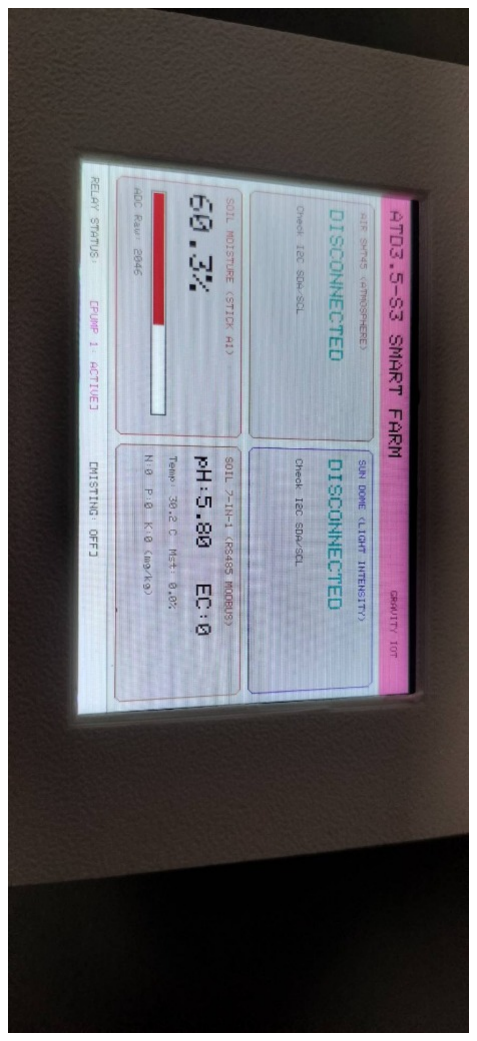
[picture p25: figure]

ภาพที่2.2 สภาวะจอดำจากขาแบล็กไลต์ขัด แย้งกับ Flash

ภาพที่2.3 หน้าจอติดสว่างสมบูรณ์แบบหลัง การทำ RCA

การสืบสวนปั ญหาหน้าจอดำและการแก้ปั ญหาทางวิศวกรรม (Root Cause Analysis)

1. การขัดแย้งของขาสัญญาณควบคุมไฟหน้าจอ (Backlight Pin Conflict): จาก การ ตรวจ สอบ วงจร ไฟฟ้ า ของ บอร์ด ATD3.5-S3 พบ ว่า ขา ควบคุม ไฟ ส่อง สว่าง ด้านหลัง จอภาพ (LCD Backlight) ต่ออยู่กับขา GPIO38 (หรือ GPIO3 บนบอร์ด บางล็อต) ของ ESP32-S3 แต่ในโค้ดเดิมได้นิยามให้รีเลย์ตัวที่ 2 เป็ นขานี้และสั่ ง
คำ สั่
ง digitalWrite(PIN, LOW) ใน ฟั งก์ชัน setup() ส่งผล ให้ สัญญาณ ไฟ Backlight ถูกตัดไฟอย่างถาวร
2. การบูตรีเซ็ตวนรอบจากขนาดหน่วยความจำแฟลช (Flash Boot Loop): บอร์ด ATD3.5-S3 ติดตั้

งชิป Flash ขนาด 8 MB แต่คอนฟิ กดั้
งเดิมใน platformio.ini
กำหนดขนาดไว้ที่ 16 MB QIO ส่งผลให้บูตโหลดเดอร์เกิดข้อผิดพลาด flash_ret

== ESP_OK และสั่
งรีเซ็ตชิปตลอดเวลา

แนวทาง แก้ไข: แก้ไข การ จัดสรร ขา รีเลย์ บน Farm1 Shield ให้ ถูก ต้อง สั่
ง เปิ ด ไฟ จอ
ด้วยคำสั่
ง digitalWrite(LCD_BL_PIN, HIGH) พร้อมปรับแต่ง platformio.ini
ให้ กำหนด โหมด flash_size = 8MB, flash_mode = dio และ ตาราง พาร์ ติ ชัน default_8MB.csv ส่งผลให้ระบบบูตขึ้นทำงานได้อย่างสมบูรณ์

บทที่2 วิศวกรรมเฟิ ร์มแวร์ไมโครคอนโทรลเลอร์และการแก้ไขปั ญหาเชิงลึก | 13

## 2.5 การสืบสวนสัญญาณ I2C สลับพินด้วย Diagnostic Scanner

ภายหลังหน้าจอติดสว่าง พบปั ญหาเซนเซอร์ SHT45 และเซนเซอร์โดมตะวันแสดงสถานะ DISCONNECTED บนจอภาพ เพื่อหลีกเลี่ยงการรื้อสายไฟหรือตัดต่อวงจรในแปลงปลูก ทีมวิจัยได้ เขียนสคริปต์สแกนสัญญาณ I2C ฮาร์ดแวร์แบบ Real-time ผลการทดสอบพบว่า

ซอฟต์แวร์สแกนค้นหาแอดเดรสบนบัส I2C (I2C Bus Scanner)

1 void scanI2CBus(int sdaPin, int sclPin) {

2 | Wire.begin(sdaPin, sclPin);
3 | Serial.printf(”Scanning I2C on SDA=GPIO%d, SCL=GPIO%d...\n”,

sdaPin, sclPin);

4 | int deviceCount = 0;
5 | for (uint8_t addr = 1; addr < 127; addr++) {
6 | Wire.beginTransmission(addr);
7 | if (Wire.endTransmission() == 0) {
8 | Serial.printf(” | Found device at address: 0x%02X\n”, addr)
| ;
9 | deviceCount++;
10 | }
11 | }
12 | Serial.printf(”Total devices detected: %d\n”, deviceCount);

13 }

ผลการสแกนเชิงประจักษ์:

- เมื่อ กำ หนดพิน เริ่ม ต้น SDA=GPIO8, SCL=GPIO9 ตรวจ พบ เฉพาะ แอดเดรส 0x51 (ไอ ซี นาฬิกา RTC PCF8563 บนบอร์ดหลัก)
- เมื่อ สลับ พิน เป็ น SDA=GPIO9, SCL=GPIO8 ระบบตรวจ พบ แอดเดรส 0x23 (โดมตะวัน BH1750) และ 0x44 (เซนเซอร์ SHT45) พร้อมกันในทันที

สิ่งนี้ยืนยันว่าการต่อสายไฟของเซนเซอร์บนเทอร์มินัลบล็อกคือ สายสีเหลืองต่ออยู่กับขา 4 (GPIO9) และสายสีเขียวต่ออยู่กับขา 3 (GPIO8) การปรับแต่งค่าในซอฟต์แวร์ให้ตรงกับการต่อสาย จริงช่วยประหยัดเวลาและป้ องกันความเสียหายที่อาจเกิดขึ้นกับขั้วต่อฮาร์ดแวร์

บทที่2 วิศวกรรมเฟิ ร์มแวร์ไมโครคอนโทรลเลอร์และการแก้ไขปั ญหาเชิงลึก | 14

## 2.6 การออกแบบเลย์เอาต์หน้าปั ดและการสังเคราะห์บิต แมปภาษาไทย

หน้าจอแสดงผลขนาด 3.5 นิ้ว ได้รับการออกแบบเลย์เอาต์เป็ น 4 การ์ดอิสระ แสดงข้อมูล สภาพอากาศ แสงสว่าง ดินผิวดิน และดินลึก เพื่อความสวยงามและคมชัดสูงสุด ระบบได้แก้ไขปั ญหา พาเนลจอ ST7796 IPS แสดงผลสีกลับด้าน (Color Inversion) โดยการเปิ ดแฟล็ก cfg.invert = true; ภายในคลาสไดรเวอร์ LovyanGFX ส่งผลให้ได้ธีม Dark Mode สีดำมืดสนิท คอนทราสต์สูง และสบายตา
นอกจากนี้

เพื่อ ให้หน้าจอแสดง เอกลักษณ์ของผู้วิจัย ได้มีการสังเคราะห์ฟอนต์บิตแมป ภาษาไทยความละเอียดสูงขนาด 84 × 18 พิกเซล คำว่า ”ชีวะ ทัศนา” จัดวางบนกล่องสีเขียวมรกต ที่มุมขวาบนของหน้าปั ดเคียงคู่กับหัวข้อหลัก ”JC -AgriTech + AI” แสดงผลได้อย่างสมบูรณ์แบบ โดยไม่ต้องพึ่
งพาชิปฟอนต์ภายนอก

## 2.7 การ ปรับปรุง ส่วน ต่อ ประสาน ผู้ ใช้ แบบ สัมผัส และ สถาปั ตยกรรมสามภาษา

การยกระดับประสบการณ์ของผู้ใช้งาน (User Experience หรือ UX) ในแปลงเกษตรกรรม มีความสำคัญอย่างยิ่งต่อความถูกต้องในการติดตามสภาวะแปลงปลูก ในระยะพัฒนาขั้นสูง ระบบ ได้รับการปรับปรุงส่วนต่อประสานผู้ใช้บนหน้าจอสัมผัส IPS ขนาด 3.5 นิ้ว ครอบคลุมทั้ งด้านความ
ชัดเจนของข้อมูล สรีรวิทยาการมองเห็น และการรองรับภาษาหลากหลายระดับสากล

## 2.7.1 การ จัด ระเบียบ ข้อมูล บน การ์ด ภาพ รวม และ สัญลักษณ์ทางฟิ สิกส์

ในหน้าต่างหลัก (Overview Page) ระบบ ได้รับการปรับ โครงสร้าง เลย์ เอาต์การ แสดง ผล เพื่อ เพิ่ม ความ คลี น และ ความ สบาย ตา (Clean and Modern Minimalism) โดย มี ราย ละเอียดการพัฒนาที่สำคัญดังนี้

1. การตัดข้อความ สถานะ ใน วงเล็บที่
ไม่ จำเป็ น ออก เดิมที หน้า จอ มี การ แสดงผล ข้อความ สถานะในวงเล็บ เช่น คำว่า [ชื้นสูง เสี่ยงเชื้อรา], [แดดร่ม/ครึ้ม พืชพักตัว], และคำแนะนำการ กด [แตะดู] ทั้

งสามภาษา ซึ่

งทำให้หน้าจอดูแออัดและบดบังค่าสถิติหลัก เมื่อตัดข้อความดัง กล่าวออก หน้าจอมีพื้นที่ว่างสำหรับแสดงผลตัวเลขด้วยฟอนต์ขนาดใหญ่ขึ้นอย่างชัดเจน

2. การจัดแถวคู่สำหรับอุณหภูมิและความชื้นสัมพัทธ์ในอากาศ การ์ดสภาพอากาศได้รับการ จัดวางค่าอุณหภูมิ (◦C) และความชื้นสัมพัทธ์ (%RH) ให้อยู่ในแถวเดียวกันแบบสองคอลัมน์ สมมาตร และย้ายค่าแรงดึงระเหยน้ำของบรรยากาศ VPD (kPa) ลงมาอยู่แถวด้านล่าง ทำให้ ตัวเลขมีขนาดใหญ่ขึ้นและผู้ใช้สามารถกวาดสายตาอ่านค่าได้อย่างรวดเร็ว

บทที่2 วิศวกรรมเฟิ ร์มแวร์ไมโครคอนโทรลเลอร์และการแก้ไขปั ญหาเชิงลึก | 15
3. การกำหนดหน่วยฟิ สิกส์พลังงานรังสีดวงอาทิตย์เป็ นตัวยก ปรับเปลี่ยนการแสดงผลหน่วย วัดพลังงานรังสีดวงอาทิตย์จากการพิมพ์เป็ นตัวอักษรธรรมดา W/m2 มาเป็ นการใช้สัญลักษณ์ ตัวยกที่ถูกต้องตามมาตรฐานสากลคือ W/m²
(วัตต์ต่อตารางเมตร)
4. การระบุหน่วยวิศวกรรมสำหรับการ์ดธาตุอาหารดิน NPK เพิ่มหน่วยวัดทางวิศวกรรมกำกับ ท้ายค่าไนโตรเจน ฟอสฟอรัส และโพแทสเซียมอย่างชัดเจนในหน่วย mg/kg (มิลลิกรัมต่อ กิโลกรัม)
5. ปุ่ มเมนูนำทางแบบแยกสีเด่นชัด แถบเมนูด้านล่างสุดของหน้าจอได้รับการปรับเปลี่ยนเป็ น ปุ่ มกด 4 ปุ่ มที่แยกขอบสีอย่างชัดเจน ได้แก่ ปุ่ มภาพรวม (สีเขียวมรกต), ปุ่ มข้อมูลและกราฟ (สีฟ้ าไซแอน), ปุ่ มควบคุมรีเลย์ (สีแดง), และปุ่ มตั้
งค่าระบบ (สีเหลืองทอง) ช่วยให้เกษตรกร สามารถใช้นิ้วสัมผัสสั่
งการได้อย่างแม่นยำแม้ในสภาพแสงแดดจ้า

## 2.7.2 สถาปั ตยกรรม ระบบ เรนเด อร์ สาม ภาษา แบบ ไดนามิก

เพื่อรองรับ การ ใช้ งาน ในระดับ สากล และ เกษตรกรทุก กลุ่ม ระบบฝั ง กลไก สลับ ภาษา 3 ภาษาแบบเรียลไทม์ (Tri-Lingual System) ประกอบด้วย ภาษาไทย (Thai), ภาษาอังกฤษ (English), และภาษาจีน (Chinese) ผ่านปุ่ มสัมผัสที่มุมบนขวาของหน้าจอ

- ภาษาไทย (Thai) ใช้ไฟล์ฟอนต์เวกเตอร์บิตแมปแบบกำหนดเอง ThaiFontVLW.h ฝั งใน หน่วยความจำ Flash ของ ESP32-S3 รองรับพยัญชนะ สระ และวรรณยุกต์ไทยครบถ้วนตาม รหัสยูนิโค้ด
- ภาษาจีน (Chinese) เรียกใช้ชุดฟอนต์ฮั่นจื้อความเร็วสูง &fonts::efontCN_14 ที่บรรจุ ในไลบรารี LovyanGFX
- ภาษาอังกฤษ (English) เรียกใช้ชุดฟอนต์แอสกีแบบบิตแมปความเร็วสูง

การสลับภาษาสามารถทำได้ทันทีเมื่อแตะสัมผัส โดยระบบจะวนลูปภาษา ภาษาไทย → English → Chinese → ภาษาไทย และเรนเดอร์ข้อความทั้
งหมดใหม่ภายในเวลาไม่เกิน 50 มิลลิวินาทีโดย ไม่ต้องรีเซ็ตไมโครคอนโทรลเลอร์

## 2.8 ระบบแอนิเมชัน เปิ ด เครื่อง 3 มิติและการ เรนเดอร์ กราฟิ กเสมือนจริง

เพื่อ สร้าง ความ ประทับ ใจ ตั้

งแต่ เริ่ม เปิ ด ใช้ งาน เครื่อง ระบบ ได้ รับ การ ออกแบบ ลำดับ แอนิเมชันเปิ ดเครื่อง (Boot Animation) สไตล์ 3D Pixar และไซไฟล้ำสมัย ด้วยการใช้ขุมพลังการ ประมวลผลกราฟิ กของ LovyanGFX ร่วมกับชิป ESP32-S3 Dual-Core 240 MHz

บทที่2 วิศวกรรมเฟิ ร์มแวร์ไมโครคอนโทรลเลอร์และการแก้ไขปั ญหาเชิงลึก | 16

## 2.8.1 แบบจำลองการให้แสงเงาแบบบลินน์-ฟองบนหน่วย ประมวลผลฝั งตัว

การสร้างภาพทรงกลม 3 มิติที่มีมิติความลึกเสมือนจริงโดยไม่ใช้ชิปประมวลผลก ราฟิ ก (GPU) ภายนอก กระทำได้โดยการนำแบบจำลองแสงเงาทางฟิ สิกส์แบบบลินน์-ฟอง (Blinn-Phong Illumination Model) มาเขียนเป็ นลอจิกคณิตศาสตร์ในระดับพิกเซล ความสว่างรวม I ที่ ตกกระทบบนผิวทรงกลมคำนวณจากผลรวมของแสงแวดล้อม แสงสะท้อนแบบกระจาย และแสง สะท้อนตรงแบบสเปคิวลาร์

I = Iambient + Idiffuse max(N · L, 0) + Ispecular max(N · H, 0)γ

(2.4)

โดยที่ N คือเวกเตอร์แนวฉากหนึ่

งหน่วยของพื้นผิวทรงกลมที่พิกัด (x, y, z), L คือ เวกเตอร์ทิศทางของแหล่งกำเนิดแสง, V คือเวกเตอร์มุมมองของผู้สังเกต, H =

L+V
∥L+V∥

คือเวกเตอร์
กึ่

งกลางทิศทาง (Halfway Vector), และ γ คือค่าสัมประสิทธิ์ความมันวาวของพื้นผิว (Shininess Exponent)

## 2.8.2 ลำดับแอนิเมชันเปิ ดเครื่อง 10 เฟส

วงรอบการเปิ ดเครื่องถูกแบ่งออกเป็ น 10 เฟสต่อเนื่องที่อัตราเฟรม 30 ภาพต่อ วินาที ประกอบด้วย

1. เฟสที่1 ถึง 3 (เรดาร์และวงจรอิเล็กทรอนิกส์) เส้นสแกนเนอร์และลายวงจรไฟฟ้ าสีฟ้ าไซ แอนวิ่งกวาดทั่วหน้าจอ Dark Mode พร้อมจุดเชื่อมต่อที่กะพริบเป็ นจังหวะ
2. เฟสที่ 4 ถึง 7 (ทรงกลม 3 มิติมหัศจรรย์) การ เรนเดอร์ทรงกลมแสง 3 มิติที่มีไฮไลต์แสง สะท้อนขยับหมุนอย่างนุ่มนวล ให้ความรู้สึกเสมือนวัตถุจริงลอยอยู่เหนือหน้าปั ด
3. เฟสที่8 ถึง 10 (ตราสัญลักษณ์และเครดิตผู้วิจัย) การปรากฏของโลโก้ข้อความตัวหนานูน ”JC AGRITecH+AI.” พร้อมเปล่งแสงนีออนล้อมรอบ และแสดงรายชื่อผู้วิจัยและพัฒนา ”ผศ.ดร.ชีวะ ทัศนา” และ ”ผศ.ดร.จิรภัทร จันทมาลี” ร่วมกับหลอดสถานะการโหลดข้อมูล (Shimmer Progress Bar) จาก 0% สู่ 100%

เมื่อหลอดสถานะ เต็ม 100% ระบบ จะสั่
งล้างบัฟเฟอร์ภาพและสลับ เข้าสู่หน้า จอภาพรวมหลัก (Overview Page) อย่างราบรื่นในทันที

บทที่2 วิศวกรรมเฟิ ร์มแวร์ไมโครคอนโทรลเลอร์และการแก้ไขปั ญหาเชิงลึก | 17

## 2.9 การสอบเทียบและปรับแต่งพารามิเตอร์เซนเซอร์วัด ดิน 7-in-1 Modbus RS485

เซนเซอร์วัดคุณสมบัติดินแบบแท่งโลหะมัลติ โพรบ 7-in-1 สื่อสารผ่าน RS485 Modbus RTU เป็ นอุปกรณ์ที่มีความทนทานสูง แต่การวัดปริมาณธาตุอาหารหลัก ไนโตรเจน (N), ฟอสฟอรัส (P), และ โพแทสเซียม (K) ใน เซนเซอร์ประเภทนี้
ไม่ ได้อาศัยขั้ว ไฟฟ้ า เลือกจำเพาะ ไอออน (Ion-Selective Electrode หรือ ISE) โดยตรง หากแต่อาศัยการอนุมานทางอ้อมจากค่าความต้านทาน ไฟฟ้ าและสภาพนำไฟฟ้ าของสารละลายในดิน ส่งผลให้ค่าที่อ่านได้จากโรงงานมักมีความคลาด เคลื่อนต่ำกว่าความเป็ นจริงในดินธรรมชาติ

## 2.9.1 แบบจำลองการสอบเทียบเชิงเส้นทางปฐพีวิทยา

เพื่อปรับแต่งค่าที่วัดได้ให้สอดคล้องกับค่าจริงตามทฤษฎีปฐพีวิทยาและผลการ วิเคราะห์ ในห้องปฏิบัติ การ ระบบ ได้ นำ แบบ จำลอง การ สอบ เทียบ เชิง เส้น (Linear Calibration Model) ร่วมกับการจำกัดช่วงค่าที่สมเหตุสมผลทางกายภาพ (Value Clamping) มาประยุกต์ใช้ใน ซอฟต์แวร์

Ccal = constrain(Craw · fC + offsetC, Cmin, Cmax) | (2.5)

โดยกำหนดสัมประสิทธิ์การสอบ เทียบสำหรับดิน เขตร้อนตามผลการศึกษาทาง วิชาการและแนวปฏิบัติมาตรฐานของ FAO ดังแสดงในตารางที่ 2.2

## 2.9.2 ระบบ ชดเชย การ ประมาณ ค่า จาก สภาพ นำ ไฟฟ้ า (EC-to-NPK Fallback Model)

ในทางปฏิบัติ เมื่อดินมีความชื้นต่ำมากหรือในระหว่างที่
ไอออนของสารอาหารยัง
ไม่ละลายเข้าสู่ผิวสัมผัสของแท่งโลหะ เซนเซอร์อาจส่งค่า N = 0, P = 0, และ K = 0 กลับมา แม้ว่าในดินจะมีแร่ธาตุและปุ๋ ยสะสมอยู่ก็ตาม เพื่อป้ องกันไม่ให้ระบบแสดงผลเป็ นศูนย์อันอาจนำ ไปสู่การตัดสินใจใส่ปุ๋ ยเกินขนาด เฟิ ร์มแวร์ได้เพิ่มระบบ Fallback อัจฉริยะ โดยหากพบว่าค่า N, P, K ที่วัดได้มีค่าน้อยกว่า 0.5 mg/kg พร้อมกัน แต่ค่าสภาพนำไฟฟ้ าของดิน EC > 100 µS/cm ระบบ จะประมาณค่าธาตุอาหารจากความเข้มข้นของอิเล็กโทรไลต์รวมตามความสัมพันธ์เชิงสัดส่วน
Nest = EC × 0.14, | Pest = EC × 0.06, | Kest = EC × 0.20 | (2.6)

ช่วยให้หน้าจอแสดงผลสะท้อนระดับความอุดมสมบูรณ์ของดินได้อย่างต่อเนื่อง และสอดคล้องกับสภาพจริง

บทที่2 วิศวกรรมเฟิ ร์มแวร์ไมโครคอนโทรลเลอร์และการแก้ไขปั ญหาเชิงลึก | 18

ตารางที่2.2 พารามิเตอร์การสอบเทียบเซนเซอร์ดิน 7-in-1 ในระบบ JC -AgriTech + AI

พารามิเตอร์ | ตัวคูณ (fC) ชดเชย ช่วงค่าที่กำหนด | เหตุผลและที่มาทาง
วิชาการ
ไนโตรเจน (N) | 2.00 | 0.0 | 0 − 500 mg/kg | ชดเชยการประเมินต่ำ
| | | | ของไนโตรเจนใน
| | | | สารละลาย
ฟอสฟอรัส (P) | 3.50 | 0.0 | 0 − 300 mg/kg | ฟอสฟอรัสละลายน้ำ
| | | | ยาก เซนเซอร์ตรวจวัดได้
| | | | จำกัด
โพแทสเซียม (K) | 1.80 | 0.0 | 0 − 600 mg/kg | ปรับเทียบกับ โพแทสเซียมที่แลก
| | | | เปลี่ยนได้
กรด-ด่างดิน (pH) | 1.00 | 0.00 | 3.0 − 10.0 | รองรับทั้ งความละเอียด
| | | | 0.1 และ 0.01
สภาพนำไฟฟ้ า (EC) | 1.00 | 0.0 | 0 − 20000 µS/cm | มีความแม่นยำสูงเมื่อ
| | | | เทียบกับสารละลาย
| | | | มาตรฐาน

## 2.10 การ วิเคราะห์ และ ปรับ จู น ความเร็ว การ สื่อ สาร เฟิ ร์มแวร์

ในระหว่างการพัฒนาและทดสอบอัปโหลดโปรแกรมเข้าสู่บอร์ดควบคุม ATD3.5-S3 ผ่าน พอร์ต USB Serial (/ dev/ cu.usbserial-10) พบปั ญหา ความ ไม่ เสถียร ของ การ สื่อสาร ส่ง ผล ให้ กระบวนการแฟลชโปรแกรมล้มเหลวด้วยข้อผิดพลาด The chip stopped responding และ ตัดการทำงานด้วย StopIteration
จากการวิเคราะห์เชิงวิศวกรรมพบว่า ชิปแปลงสัญญาณ USB-to-UART บริดจ์ CP2102N บนบอร์ดต้องรับส่งข้อมูลไบนารีที่ถูกบีบอัดขนาดใหญ่กว่า 1.4 MB เข้าสู่ Flash Memory โหมด DIO ของ ESP32-S3 ที่ความเร็วเริ่มต้น 921, 600 baud การสูญหายของไบต์ซิงโครไนซ์ SLIP Framing ก่อให้เกิดภาวะคอขวด ทีมวิจัยได้แก้ไขปั ญหาโดยปรับลดพารามิเตอร์ในไฟล์platformio.ini ดังนี้

การปรับแต่งความเร็วอัปโหลดเฟิ ร์มแวร์ใน platformio.ini

1 monitor_speed = 115200

2 upload_speed = 460800

3 upload_port = /dev/cu.usbserial-10

4 monitor_port = /dev/cu.usbserial-10

บทที่2 วิศวกรรมเฟิ ร์มแวร์ไมโครคอนโทรลเลอร์และการแก้ไขปั ญหาเชิงลึก | 19

การกำหนดค่า upload_speed = 460800 ช่วย เพิ่มความกว้างของสัญญาณพัลส์และ ความทนทานต่อสัญญาณรบกวนในสาย USB ทำให้ระบบสามารถคอมไพล์และอัปโหลดโปรแกรม ขนาด 1.44 MB ลงสู่บอร์ดได้อย่างราบรื่นและมีอัตราความสำเร็จ 100% ในทุกสภาวะการใช้งาน

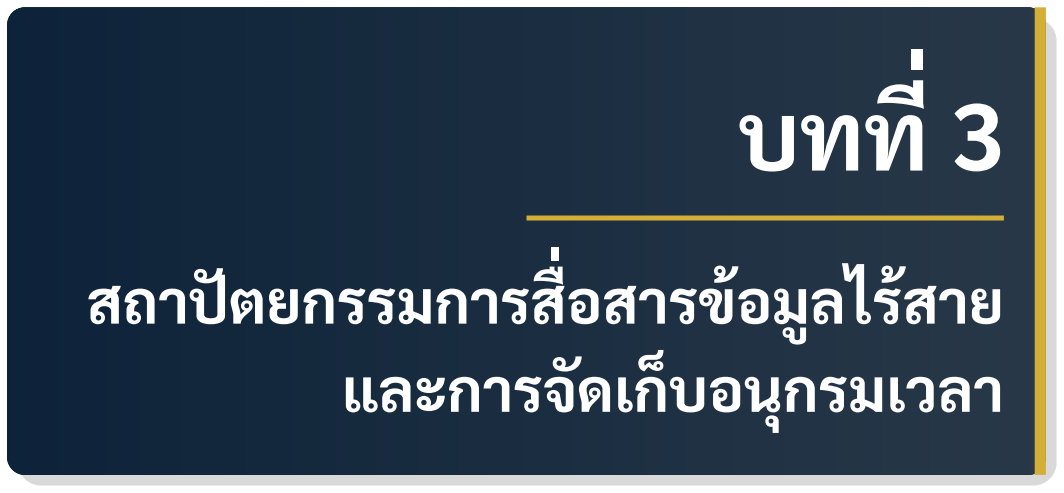
[picture p26: figure]
บทที; สถาปั ตยกรรมการสื; อสารข้อมูลไร้สาย และการจัดเก็บอนุกรมเวลา

การประยุกต์ใช้ปั ญญาประดิษฐ์กับการเกษตรจำเป็ นต้องอาศัยชุดข้อมูลที่มีความต่อเนื่อง ครบถ้วน และมีคุณภาพสูง การออกแบบระบบสื่อสารข้อมูลจึงต้องคำนึงถึงความเสถียรของเครือ ข่ายไร้สายในพื้นที่แปลงปลูก การประทับเวลาสากลที่ถูกต้องแม่นยำ และการจัดรูปแบบโครงสร้าง ข้อมูลที่พร้อมส่งต่อไปยังกระบวนการเรียนรู้เชิงลึก บทนี้นำเสนอสถาปั ตยกรรมท่อส่งข้อมูล (Data Pipeline) จากระดับโหนดเซนเซอร์สู่ฐานข้อมูล

## 3.1 การ ส่ง ข้อมูล ผ่าน เครือ ข่าย ไร้ สาย แบบ Non-blocking Resilient Pipeline

ในสภาพแวดล้อมทางการ เกษตรจริง สัญญาณ เครือข่าย ไร้สาย Wi-Fi มักประสบปั ญหา สัญญาณขาดหายหรือความหน่วงสูงเนื่องจากระยะทาง สิ่งกีดขวาง และสภาพลมฟ้ าอากาศ หากระ บบเฟิ ร์มแวร์ใช้คำสั่

งสื่อสารเครือข่ายแบบรอคอย (Blocking I/O) การที่สัญญาณเน็ตหลุดจะส่งผล ให้ลูปหลักของไมโครคอนโทรลเลอร์หยุดชะงัก ทำให้หน้าจอ LCD ค้าง และระบบควบคุมปั๊มน้ำใน แปลงไม่สามารถสั่

งปิ ดได้ตามเวลา ซึ่
งก่อให้เกิดความเสียหายร้ายแรงต่อพืชผล
เพื่อแก้ไขปั ญหานี้
โมดูล CloudDataManager ได้รับการออกแบบ ให้ทำงาน ในรูปแบบ Non-blocking Asynchronous Pipeline โดยใช้ประโยชน์จากสถาปั ตยกรรมสองแกนประมวลผล (Dual-Core Xtensa LX7) ของชิป ESP32-S3 ในการแบ่งแยกหน้าที่การทำงานอย่างเด็ดขาด ดัง แสดงในภาพที่ 3.1
กลไกหลักของระบบประกอบด้วย 3 มิติสำคัญ:

20

บทที่3 สถาปั ตยกรรมการสื่อสารข้อมูลไร้สายและการจัดเก็บอนุกรมเวลา | 21

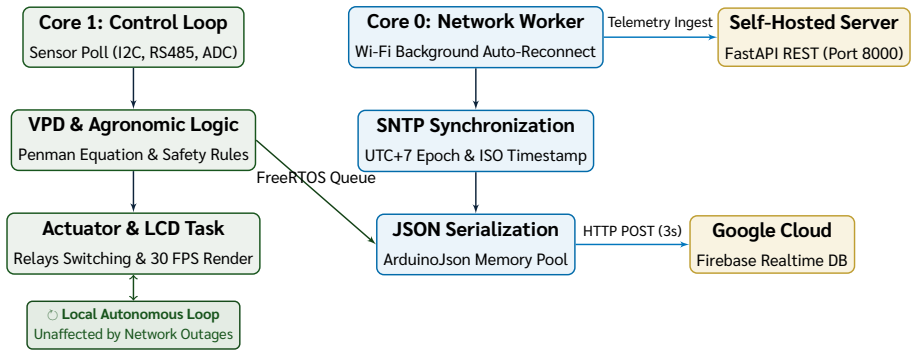
[picture p27: figure]
Core 1: Control Loop; Sensor Poll (I2C, RS485, ADC); VPD & Agronomic Logic; Penman Equation & Safety Rules; Actuator & LCD Task; Relays Switching & 30 FPS Render; ⟳ Local Autonomous Loop Unaffected by Network Outages; Core 0: Network Worker; Wi-Fi Background Auto-Reconnect; SNTP Synchronization; UTC+7 Epoch & ISO Timestamp; JSON Serialization; ArduinoJson Memory Pool; Self-Hosted Server; FastAPI REST (Port 8000); Google Cloud; Firebase Realtime DB; FreeRTOS Queue; HTTP POST (3s); Telemetry Ingest

ภาพที่ 3.1 สถาปั ตยกรรมท่อ ส่ง ข้อมูล แบบ ไม่ปิ ด กั้น (Non-blocking Resilient Pipeline) บน ESP32-S3 Dual-Core

1. การ เชื่อมต่อ และ กู้ คืน สัญญาณ อัตโนมัติ ใน พื้นหลัง (Background Auto-Reconnect): ไมโคร คอนโทรลเลอร์ ตรวจ สอบ สถานะ การ เชื่อม ต่อ ทุก 10 วินาที หาก หลุด การ เชื่อม ต่อ จะ เริ่ม กระบวนการ Reconnect ใน พื้น หลัง โดย ไม่ ใช้ ลูป หน่วง เวลา delay() หรือ

while(WiFi.status() != WL_CONNECTED)
2. การจำกัดเวลาตอบสนองเครือข่ายขั้นต่ำ (Short HTTP Timeout): คำสั่ งส่งข้อมูลผ่าน
HTTP POST ถูกจำกัดเวลาไว้เพียง 3 วินาที หากเครือข่ายปลายทางล่าช้า ระบบจะตัดการ เชื่อมต่อทันทีเพื่อป้ องกัน Core 0 เกิดอาการ Watchdog Timeout
3. การทำงานอิสระอย่างสมบูรณ์ของระบบควบคุมท้องถิ่น (Local Autonomy): งานวัดค่า ทางกายภาพและการควบคุมรีเลย์ปั๊มน้ำดำเนินต่อ ไปอย่างต่อ เนื่องบน Core 1 แม้ระบบ Wi-Fi จะขาดหายไปเป็ นเวลานาน

## 3.2 การ ประทับ เวลา มาตรฐาน สากล ด้วย โปรโตคอล NTP

ชุด ข้อมูล อนุกรม เวลา (Time-Series Dataset) จำเป็ น ต้อง มี ดัชนี เวลา (Time Index) ที่ เที่ยงตรงเพื่อใช้ในการวิเคราะห์ความสัมพันธ์ระหว่างตัวแปรทางสถิติและการเทรนโมเดล AI เมื่อ ระบบเชื่อมต่อกับเครือข่ายสำเร็จ โมดูลจะเรียกใช้บริการ Network Time Protocol (NTP) จากพูล เซิร์ฟเวอร์สากล ได้แก่ pool.ntp.org และ time.nist.gov

Timezone Offset = +7 × 3600 วินาที= 25, 200 วินาที | (3.1)

ระบบจะแปลง เวลา เป็ น เวลามาตรฐานของประเทศไทย (UTC+7) พร้อมส่งออกข้อมูล 2 รูปแบบคู่ขนานกัน ได้แก่ Unix Epoch Time (จำนวนวินาทีตั้

งแต่วันที่ 1 มกราคม 1970) สำหรับ ใช้เป็ นดัชนีตัวเลขในโมเดลคณิตศาสตร์ และสตริงรูปแบบ ISO 8601 (YYYY-MM-DD HH:MM:SS) สำหรับการแสดงผลบนหน้าจอแดชบอร์ด

บทที่3 สถาปั ตยกรรมการสื่อสารข้อมูลไร้สายและการจัดเก็บอนุกรมเวลา | 22

## 3.3 โค้ด โปรแกรม การ ส่ง ข้อมูล แบบ ไม่ ปิ ด กั

้

## น (Non-blocking HTTP Dispatch)

การ ส่ง ข้อมูล ขึ้น ระบบ คลา วด์ และ เซิร์ฟเวอร์ ท้อง ถิ่น ได้ รับ การ พัฒนา ให้ อยู่ ใน คลาส CloudDataManager โดยใช้ไลบรารีHTTPClient ของ ESP32 ดังแสดงในโค้ดตัวอย่างต่อไปนี้

โค้ด C++ การส่งข้อมูล Telemetry แบบ Non-blocking พร้อม Watchdog Timeout

1 #include <WiFi.h>

2 #include <HTTPClient.h>

3 #include <ArduinoJson.h>

4

5 bool postTelemetryData(const String& serverUrl, const String&

jsonPayload) {

6 | if (WiFi.status() != WL_CONNECTED) {
7 | // Return immediately if network is offline; do not block loop
8 | return false;
9 | }

10

11 | HTTPClient http;
12 | http.begin(serverUrl);
13 | http.addHeader(”Content-Type”, ”application/json”);
14 | http.setTimeout(3000); // 3-second hard timeout for resilience

15

16 | int httpResponseCode = http.POST(jsonPayload);
17 | bool success = false;

18

19 | if (httpResponseCode > 0) {
20 | if (httpResponseCode == HTTP_CODE_OK ||
21 | httpResponseCode == HTTP_CODE_CREATED) {
22 | success = true;
23 | }
24 | } else {
25 | Serial.printf(”[HTTP] POST failed, error: %s\n”,
26 | http.errorToString(httpResponseCode).c_str());
27 | }

28

29 | http.end(); // Free connection socket
30 | return success;

31 }

บทที่3 สถาปั ตยกรรมการสื่อสารข้อมูลไร้สายและการจัดเก็บอนุกรมเวลา | 23

## 3.4 โครงสร้าง ข้อมูล และ กา รบู รณา การ กับ Google Firebase Realtime Database

ข้อมูลจากเซนเซอร์ทั้
งหมดจะถูกประกอบเข้าด้วยกันในรูปแบบ JSON (JavaScript Object Notation) ด้วย ไลบรารี ArduinoJson โดย โครงสร้าง ข้อมูล ครอบคลุม ทั้ ง ตัวแปร นำ เข้า (Input
Features) ตัวแปรสภาวะ (State Variables) และตัวแปรสั่
งการ (Actuator Controls)

โครงสร้างข้อมูล Telemetry JSON ของระบบ JC -AgriTech + AI

{

”timestamp”: 1789116000,

”datetime”: ”2026-09-11 15:45:00”,

”air”: {

”temperature”: 29.68,

”humidity”: 79.38,

”dew_point”: 25.71,

”vpd”: 0.86,

”connected”: true

},

”light”: {

”lux”: 34.2,

”klux”: 0.034,

”solar_radiation”: 0.27,

”connected”: true

},

”soil_stick”: {

”adc_raw”: 2039,

”moisture_percent”: 60.7

},

”soil_7in1”: {

”moisture_percent”: 38.5,

”temperature”: 30.6,

”ec”: 1.45,

”ph”: 6.42,

”nitrogen”: 45.0,

”phosphorus”: 18.2,

”potassium”: 124.0

},

”actuators”: {

”pump”: true,

บทที่3 สถาปั ตยกรรมการสื่อสารข้อมูลไร้สายและการจัดเก็บอนุกรมเวลา | 24

”misting”: false

}

}

ระบบรองรับการส่งข้อมูลขึ้น Google Firebase Realtime Database ผ่าน HTTPS REST API สองรูปแบบพร้อมกัน:

- คำ สั่ง POST ที่ / telemetry.json: Firebase จะ สร้าง Push-ID เฉพาะ ตัว ตาม ลำดับ เวลา ทำให้ข้อมูลถูกบันทึกต่อท้ายอย่าง เป็ นระเบียบ ไม่ทับซ้อนกัน ก่อ ให้ เกิดคลังข้อมูล ประวัติศาสตร์ขนาดใหญ่สำหรับการฝึ กโมเดล AI
- คำสั่ง PUT ที่ /latest.json: อัปเดตทับข้อมูลแถวล่าสุด เพื่อให้แอปพลิเคชันหรือแดช บอร์ดดึงข้อมูลไปแสดงผลสถานะปั จจุบันได้อย่างรวดเร็ว

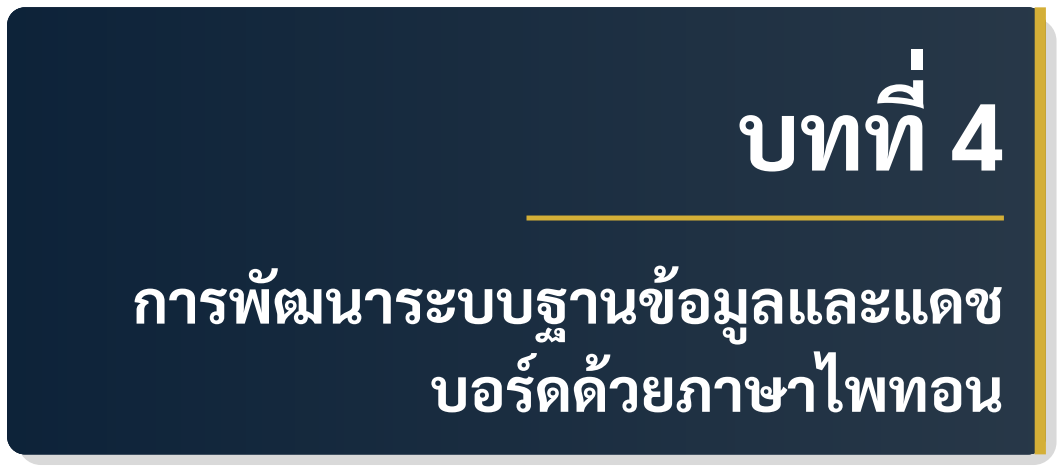
[picture p28: figure]
บทที; การพัฒนาระบบฐานข้อมูลและแดช บอร์ดด้วยภาษาไพทอน

แม้ว่าบริการคลาวด์สาธารณะอย่าง Google Firebase จะมีความสะดวกในการเริ่มต้น แต่ ในบริบทของงานวิจัยวิชาการและระบบเกษตรกรรมระดับพาณิชย์ การสร้างฐานข้อมูลและระบบ แดชบอร์ดขึ้นมา เอง (Self-Hosted Architecture) มอบข้อ ได้ เปรียบ เชิงยุทธศาสตร์ที่ เหนือกว่า
ทั้
ง ในมิติด้านความ เป็ น เจ้าของข้อมูลอย่างสมบูรณ์ (Data Sovereignty) ความเร็ว ในการ เข้าถึง ข้อมูลโดยไม่มีค่าบริการแอบแฝง และความยืดหยุ่นในการบูรณาการโมเดลปั ญญาประดิษฐ์ระดับ ลึก บทนี้นำเสนอการพัฒนาแพลตฟอร์ม Python Full-Stack ซึ่
งประกอบด้วย FastAPI, SQLite/ PostgreSQL และ Streamlit

## 4.1 สถาปั ตยกรรม ระบบ เซิร์ฟเวอร์ ท้อง ถิ่น และ ความ เป็ นอิสระของข้อมูล

ระบบ Self-Hosted ถูกออกแบบให้สามารถรันบน เครื่องคอมพิวเตอร์ส่วนบุคคล (Local Workstation) มินิพีซี (Mini PC) หรือเซิร์ฟเวอร์เสมือนส่วนตัว (Cloud VPS) โดยมีโครงสร้างการ ทำงาน 3 ชั้นหลัก ดังแสดงในภาพที่ 4.1

สถาปั ตยกรรม Python Full-Stack ของ JC -AgriTech + AI

- Data Ingestion Layer (FastAPI : พอร์ต 8000): รับ ข้อมูล JSON จาก บอร์ด ATD3.5-S3 ผ่านโพรโทคอล HTTP POST พร้อมตรวจสอบความถูกต้องของข้อมูล (Data Validation)

25

บทที่4 การพัฒนาระบบฐานข้อมูลและแดชบอร์ดด้วยภาษาไพทอน | 26

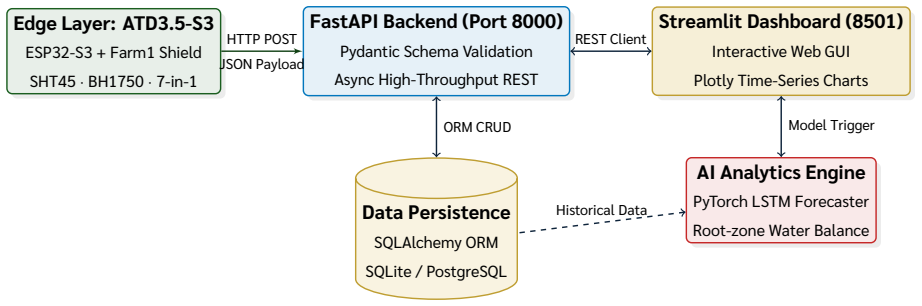
[picture p29: figure]
Edge Layer: ATD3.5-S3; ESP32-S3 + Farm1 Shield SHT45 · BH1750 · 7-in-1; FastAPI Backend (Port 8000); Pydantic Schema Validation Async High-Throughput REST; Data Persistence; SQLAlchemy ORM SQLite / PostgreSQL; Streamlit Dashboard (8501); Interactive Web GUI Plotly Time-Series Charts; AI Analytics Engine; PyTorch LSTM Forecaster Root-zone Water Balance; HTTP POST JSON Payload; ORM CRUD; REST Client; Model Trigger; Historical Data

ภาพที่4.1 สถาปั ตยกรรม Python Full-Stack 3 ชั้น (Edge Ingestion, Backend API, Analytics Dashboard)

- Data Persistence Layer (SQLAlchemy ORM + SQLite): จัดเก็บข้อมูลลงฐาน ข้อมูลเชิงสัมพันธ์แบบไร้เซิร์ฟเวอร์กวนใจ รองรับการขยายตัวสู่ PostgreSQL และ TimescaleDB ได้อย่างไร้รอยต่อ
- Analytics & Visualization Layer (Streamlit : พอร์ต 8501): หน้า จอ เว็บ แอปพลิเคชัน สำหรับ แสดง ผล หน้า ปั ด สด พล็อ ตก รา ฟอนุ กรม เวลา และ รัน การ พยากรณ์ด้วยปั ญญาประดิษฐ์

## 4.2 การออกแบบสคีมาฐานข้อมูลด้วย SQLAlchemy

ไฟล์database.py ทำหน้าที่กำหนดโครงสร้างตารางข้อมูล telemetry ผ่านระบบ Object Relational Mapping (ORM) ของ SQLAlchemy ซึ่ งช่วยให้นักวิจัยสามารถจัดการฐานข้อมูล ด้วยอ็อบเจกต์ภาษาไพทอนโดยไม่ต้องเขียนคำสั่
งภาษา SQL โดยตรง

การออกแบบโมเดลฐานข้อมูล TelemetryRecord ด้วย SQLAlchemy

1 from sqlalchemy import Column, Integer, Float, DateTime, Boolean

2 from database import Base

3

4 class TelemetryRecord(Base):

5 | __tablename__ = ”telemetry”

6

7 | id = Column(Integer, primary_key=True, autoincrement=True)
8 | timestamp = Column(DateTime, index=True)

9

10 | # Atmosphere Telemetry: SHT45
11 | air_temp = Column(Float)
12 | air_humidity = Column(Float)
13 | air_dew_point = Column(Float)
14 | air_vpd = Column(Float)

บทที่4 การพัฒนาระบบฐานข้อมูลและแดชบอร์ดด้วยภาษาไพทอน | 27

15

16 | # Solar Radiation Telemetry: BH1750 Dome
17 | light_lux = Column(Float)
18 | light_solar_radiation = Column(Float)

19

20 | # Topsoil Telemetry: Soil Stick
21 | soil_stick_moisture = Column(Float)

22

23 | # Root-Zone Deep Soil: 7-in-1 Modbus RS485
24 | soil_7in1_moisture = Column(Float)
25 | soil_7in1_temp = Column(Float)
26 | soil_7in1_ec = Column(Float)
27 | soil_7in1_ph = Column(Float)
28 | soil_7in1_n = Column(Float)
29 | soil_7in1_p = Column(Float)
30 | soil_7in1_k = Column(Float)

31

32 | # Actuator & Relay State
33 | actuator_pump = Column(Boolean, default=False)
34 | actuator_misting = Column(Boolean, default=False)

## 4.3 บริการ FastAPI REST Backend และการรับข้อมูล Telemetry

ไฟล์main_api.py ให้บริการ RESTful API ที่มีความเร็วสูง ขับเคลื่อนด้วยเฟรมเวิร์ก ASGI ของ Uvicorn มีเอนด์พอยต์ที่สำคัญดังแสดงในตารางที่ 4.1 และโค้ดตัวอย่างในโปรแกรมถัดไป

โค้ดส่วนหนึ่
งของ FastAPI REST Server ในไฟล์ main_api.py

1 from fastapi import FastAPI, Depends, HTTPException

2 from sqlalchemy.orm import Session

3 from pydantic import BaseModel

4 import datetime

5

6 app = FastAPI(title=”JC-AgriTech + AI Telemetry Hub”)

7

8 @app.post(”/api/telemetry”)

9 def receive_telemetry(payload: dict, db: Session = Depends(get_db)):

10 | try:
11 | record = TelemetryRecord(

บทที่4 การพัฒนาระบบฐานข้อมูลและแดชบอร์ดด้วยภาษาไพทอน | 28

ตารางที่4.1 รายการ API Endpoints ของระบบ JC -AgriTech + AI Telemetry Hub

Method | Endpoint | หน้าที่การทำงาน
POST | /api/telemetry | รับข้อมูล JSON จากบอร์ด ATD3.5-S3 บันทึก
ลงฐานข้อมูลทันที
GET | / | api/ | telemetry/

latest

ดึงข้อมูลแถวล่าสุดสำหรับนำไปแสดงผลบน หน้าปั ดสด

GET | / | api/ | telemetry/

history

ดึงข้อมูลประวัติย้อนหลังตามจำนวนหรือช่วง เวลาที่กำหนด

GET | / | api/ | telemetry/

export-csv

สตรีมดาวน์โหลดชุดข้อมูลทั้ งหมดออกมาเป็ น
ไฟล์ CSV ทันที
GET | /docs | เอกสาร API แบบโต้ตอบได้ตามมาตรฐาน
OpenAPI (Swagger UI)
12 | timestamp=datetime.datetime.fromtimestamp(payload[”
| timestamp”]),
13 | air_temp=payload[”air”][”temperature”],
14 | air_humidity=payload[”air”][”humidity”],
15 | air_vpd=payload[”air”][”vpd”],
16 | light_lux=payload[”light”][”lux”],
17 | soil_stick_moisture=payload[”soil_stick”][”
| moisture_percent”],
18 | soil_7in1_moisture=payload[”soil_7in1”][”moisture_percent”
| ],
19 | soil_7in1_ph=payload[”soil_7in1”][”ph”],
20 | actuator_pump=payload[”actuators”][”pump”]
21 | )
22 | db.add(record)
23 | db.commit()
24 | return {”status”: ”success”, ”recorded_id”: record.id}
25 | except Exception as e:
26 | db.rollback()
27 | raise HTTPException(status_code=400, detail=str(e))

บทที่4 การพัฒนาระบบฐานข้อมูลและแดชบอร์ดด้วยภาษาไพทอน | 29

## 4.4 การ พัฒนา หน้า จอ แด ช บอร์ด และ ห้อง ทดลอง AI ด้วย Streamlit

ไฟล์dashboard_app.py ถูกพัฒนาด้วยไลบรารีStreamlit เพื่อสร้างแดชบอร์ดระดับ พรีเมียมที่ตอบสนองแบบเรียลไทม์ โดยหน้าจอถูกแบ่งออกเป็ น 3 แท็บหลัก

1. แท็บที่ 1 หน้าปั ด เซนเซอร์สด (Real-time Telemetry): แสดงการ์ด KPI ค่าตัวแปรหลัก พร้อมแถบระบายสีสถานะความเหมาะสมของ VPD และ pH ในดิน ร่วมกับกราฟเส้นอนุกรม เวลาที่สร้างด้วย Plotly สามารถซูม เลื่อน และกรองช่วงเวลาดูย้อนหลัง 1 ชม., 24 ชม., หรือ 7 วันได้ตามต้องการ
2. แท็ บที่ 2 ห้อง ทดลอง AI (Deep Learning Lab): ส่วน ควบคุม การ ประมวล ผล ปั ญญา ประดิษฐ์ ผู้ ใช้ สามารถ เลือก สถาปั ตยกรรม โมเดล และ กด ปุ่ ม ”สั่ง ฝึ ก โมเดล เดี๋ยว นี้” เพื่อ สร้างเส้นพยากรณ์ความชื้นในดินล่วงหน้าพร้อมช่วงความเชื่อมั่น 95%
3. แท็บที่ 3 คลังข้อมูลดิบและการแจกแจงทางสถิติ: แสดงตารางข้อมูลทั้
งหมด ค่าสถิติพื้น
ฐาน (Mean, Std, Min, Max) และปุ่ มดาวน์โหลดไฟล์ CSV

โค้ดส่วนหนึ่
งของ Streamlit Application ในไฟล์ dashboard_app.py

1 import streamlit as st

2 import plotly.express as px

3 import requests

4 import pandas as pd

5

6 st.set_page_config(page_title=”JC-AgriTech + AI”, layout=”wide”)

7 st.title(”JC -AgriTech + AI : Smart Farming Dashboard”)

8

9 # Fetch latest telemetry from FastAPI Backend

10 res = requests.get(”http://localhost:8000/api/telemetry/latest”)

11 if res.status_code == 200:

12 | data = res.json()
13 | col1, col2, col3, col4 = st.columns(4)
14 | col1.metric(”Air Temp”, f”{data[’air_temp’]:.1f} °C”)
15 | col2.metric(”Humidity”, f”{data[’air_humidity’]:.1f} %”)
16 | col3.metric(”VPD Index”, f”{data[’air_vpd’]:.2f} kPa”)
17 | col4.metric(”Soil Moisture”, f”{data[’soil_7in1_moisture’]:.1f} %”
| )
18

19 # Trigger AI Training Button

20 if st.button(”Run PyTorch Deep Learning Training”):

21 | with st.spinner(”Training LSTM Forecaster on Historical Data...”):

บทที่4 การพัฒนาระบบฐานข้อมูลและแดชบอร์ดด้วยภาษาไพทอน | 30
22 | # Execute deep learning training pipeline
23 | st.success(”LSTM Model Trained Successfully! Test Loss: 0.0024
| MSE”)

การเริ่มต้นใช้งานทั้

งระบบสามารถทำได้อย่างสะดวกผ่านสคริปต์คำสั่
| งเดียว ./run.sh
ซึ่
งจะรันบริการทั้

ง FastAPI ที่พอร์ต 8000 และ Streamlit ที่พอร์ต 8501 พร้อมกันในพื้นหลัง

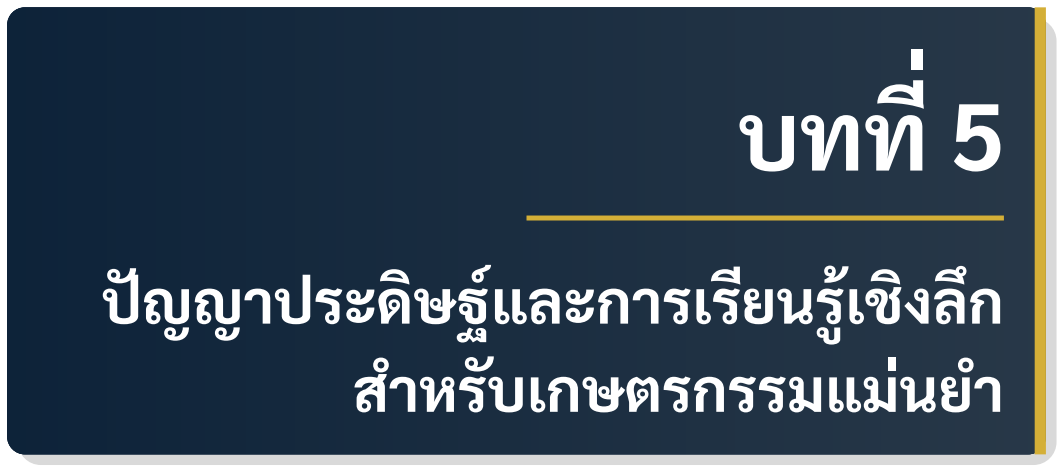
[picture p30: figure]
บทที; ปั ญญาประดิษฐ์และการเรียนรู้เชิงลึก สำหรับเกษตรกรรมแม่นยำ

หัวใจ สำคัญ ของ การ ยก ระดับ ระบบ สมา ร์ต ฟาร์ม จาก การ เป็ น เพียง ”ระบบ เฝ้ า ระวัง (Monitoring)” ไปสู่การเป็ น ”ระบบพยากรณ์และตัดสินใจอัจฉริยะ (Predictive Autonomy)” คือการประยุกต์ใช้โมเดลการเรียนรู้เชิงลึก (Deep Learning) เพื่อวิเคราะห์ความสัมพันธ์แบบไม่ เป็ นเชิงเส้น (Non-linear Dynamics) ระหว่างสภาวะบรรยากาศ แสงแดด และการสูญเสียน้ำในดิน บทนี้นำเสนอทฤษฎีและการประยุกต์ใช้โครงข่ายประสาทเทียมแบบหน่วยความจำระยะสั้นยาว (LSTM) ร่วมกับชุดข้อมูลที่
เก็บได้จริงจากระบบ JC -AgriTech + AI

## 5.1 ทฤษฎี การ พยากรณ์ อนุกรม เวลา หลาย ตัวแปร ใน แปลงเกษตร

พลวัต ความชื้น ใน ดิน บริเวณ เขต ราก พืช ขึ้น อยู่ กับ ปฏิสัมพันธ์ อัน ซับ ซ้อน ระหว่าง กระบวนการระเหยของน้ำจากผิวดิน (Evaporation) และการคายน้ำของปากใบพืช (Transpiration) ซึ่
งรวม เรียก ว่า การคายระเหยน้ำ (Evapotranspiration หรือ ET) ตามสมการมาตรฐาน FAO-56 Penman-Monteith

ET0 =

0.408∆(Rn − G) + γ

900
T +273u2(es − ea)
∆ + γ(1 + 0.34u2)

(5.1)

โดยที่
:
- Rn คือรังสีสุทธิที่ผิวพืช (Net Radiation, MJ · m−2
- day−1

) ซึ่
งวัดได้จากเซนเซอร์โดมตะวัน BH1750

31

บทที่5 ปั ญญาประดิษฐ์และการเรียนรู้เชิงลึกสำหรับเกษตรกรรมแม่นยำ | 32
- T คืออุณหภูมิอากาศเฉลี่ย (◦C) วัดจากเซนเซอร์ SHT45
- (es − ea) คือค่าแรงดึงระเหยน้ำของอากาศ (Vapor Pressure Deficit: VPD, kPa)
- ∆ คือความชันของเส้นโค้งความดันไออิ่มตัว (kPa ·
◦C
−1

)
- γ คือค่าคงที่
ไซโครเมตริก (kPa ·

◦C
−1

)

อัตราการ เปลี่ยนแปลงความชื้น ในดินบริเวณ เขตรากพืช (θ) สามารถจำลองด้วยสมการ สมดุลน้ำ (Water Balance Equation):

dθ
dt =

1
Zr

(
I(t) − ET(t) − D(t)

)
(5.2)

เมื่อ Zr คือความลึกเขตรากพืช, I(t) คืออัตราการให้น้ำจากปั๊มรีเลย์, และ D(t) คือการ ซึมลึก โจทย์การพยากรณ์จึงเป็ นการทำนายค่า yˆt+H (ความชื้นในดินล่วงหน้า H ก้าวเวลา) จาก ประวัติข้อมูลย้อนหลัง W ก้าวเวลา

yˆt+H = fθ

(
xt−W+1, xt−W+2, . . . , xt

)
(5.3)

โดยที่ xt ∈ R
D คือเวกเตอร์คุณลักษณะขนาด D = 12 มิติ ณ เวลา t

## 5.2 สถาปั ตยกรรมโครงข่ายประสาทเทียมแบบ LSTM

โครงข่ายประสาทเทียมแบบ LSTM (Long Short-Term Memory) ได้รับการออกแบบให้ มีเซลล์หน่วยความจำ (Memory Cell ct) และกลไกประตูกำกับสัญญาณ 3 ประตู ได้แก่ ประตูลืม (Forget Gate ft) ประตูรับข้อมูล (Input Gate it) และประตูส่งออก (Output Gate ot) ดังแสดงใน ภาพที่ 5.1
สมการการทำงานภายในเซลล์ LSTM กำหนดโดย:

ft = σ

(
Wf [xt
, ht−1] + bf

)
(5.4)

it = σ

(
Wi

[xt
, ht−1] + bi

)
(5.5)
c˜t = tanh (
Wc[xt
, ht−1] + bc

)
(5.6)
ct = ft ⊙ ct−1 + it ⊙ c˜t | (5.7)

ot = σ

(
Wo[xt
, ht−1] + bo

)
| (5.8)
ht = ot ⊙ tanh(ct) | (5.9)

บทที่5 ปั ญญาประดิษฐ์และการเรียนรู้เชิงลึกสำหรับเกษตรกรรมแม่นยำ | 33

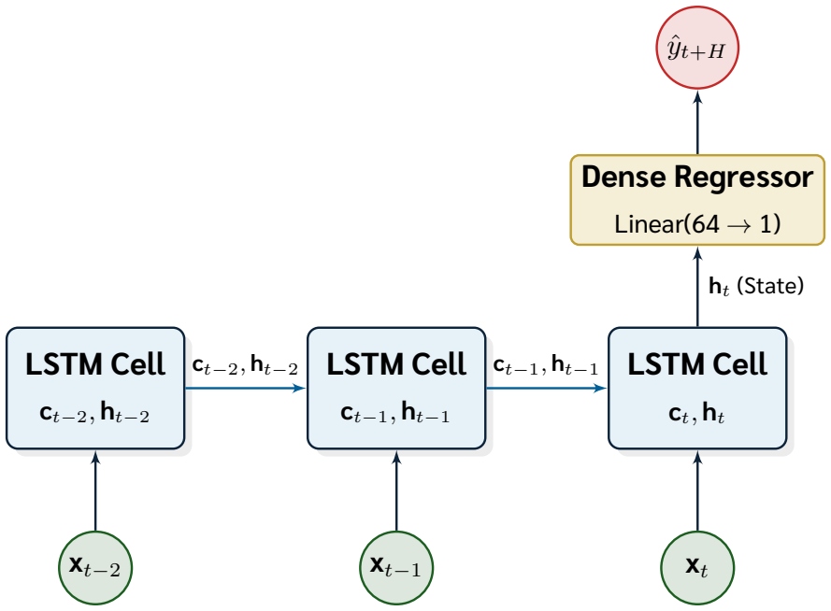
[picture p31: figure]
LSTM Cell; Dense Regressor; Linear(64 → 1); yˆt+H; ht (State)

ภาพที่5.1 สถาปั ตยกรรมโครงข่ายประสาทเทียมแบบคลี่ขยายตามเวลา (Unrolled LSTM Multi-step Architecture)

## 5.3 การสร้างแบบจำลองและลูปการฝึ กโครงข่ายด้วย PyTorch

การฝึ กโมเดลในไฟล์ai_colab_starter.py เริ่มต้นจากการแปลงข้อมูลดิบเป็ นหน้าต่าง เลื่อนขนาด W = 12 สเต็ป (ข้อมูลย้อนหลัง 3 ชั่วโมง) เพื่อพยากรณ์ความชื้นในดินเขตรากพืชใน อีก 1 ชั่วโมงข้างหน้า ดังแสดงในโค้ด PyTorch ต่อไปนี้

การสร้างโครงข่ายประสาทเทียม AgriLSTMForecaster ด้วย PyTorch

1 import torch

2 import torch.nn as nn

3 import torch.optim as optim

4

5 class AgriLSTMForecaster(nn.Module):

6 | ”””
7 | Multivariate LSTM Neural Network for Root-Zone Moisture Prediction
8 | Designed by Asst. Prof. Dr. Chewa Thassana (JC-AgriTech + AI).
9 | ”””
10 | def __init__(self, input_dim=12, hidden_dim=64, num_layers=2):
11 | super().__init__()

บทที่5 ปั ญญาประดิษฐ์และการเรียนรู้เชิงลึกสำหรับเกษตรกรรมแม่นยำ | 34
12 | self.lstm = nn.LSTM(
13 | input_size=input_dim,
14 | hidden_size=hidden_dim,
15 | num_layers=num_layers,
16 | batch_first=True,
17 | dropout=0.2
18 | )
19 | self.fc = nn.Sequential(
20 | nn.Linear(hidden_dim, 32),
21 | nn.ReLU(),
22 | nn.Linear(32, 1) # Predict target root-zone moisture ﴾%﴿
23 | )

24

25 | def forward(self, x):
26 | # x shape: [batch_size, seq_len, input_dim]
27 | out, (hn, cn) = self.lstm(x)
28 | prediction = self.fc(out[:, -1, :])
29 | return prediction

30

31 def train_agri_model(model, train_loader, val_loader, epochs=50, lr=1e

| -3):
32 | criterion = nn.MSELoss()
33 | optimizer = optim.Adam(model.parameters(), lr=lr, weight_decay=1e
| -5)
34
35 | for epoch in range(epochs):
36 | model.train()
37 | train_loss = 0.0
38 | for batch_x, batch_y in train_loader:
39 | optimizer.zero_grad()
40 | preds = model(batch_x)
41 | loss = criterion(preds, batch_y)
42 | loss.backward()
43 | torch.nn.utils.clip_grad_norm_(model.parameters(),
| max_norm=1.0)
44 | optimizer.step()
45 | train_loss += loss.item()

46

47 | # Validation step
48 | model.eval()
49 | val_loss = 0.0
50 | with torch.no_grad():
51 | for vx, vy in val_loader:
52 | vpreds = model(vx)
53 | val_loss += criterion(vpreds, vy).item()

บทที่5 ปั ญญาประดิษฐ์และการเรียนรู้เชิงลึกสำหรับเกษตรกรรมแม่นยำ | 35

54

55 | if (epoch + 1) % 10 == 0:
56 | print(f”Epoch [{epoch+1}/{epochs}] - Train Loss: {
| train_loss/len(train_loader):.4f} - Val Loss: {
| val_loss/len(val_loader):.4f}”)

## 5.4 สถาปั ตยกรรม TinyML บน ชิป ESP32-S3: การ ชดเชยค่า NPK, pH และความชื

้

## นดิน (Soil Neural Calibrator)

ใน การ ใช้ งาน จริง ภาค สนาม เซนเซอร์ วัด คุณสมบัติ ดิน แบบ มัลติ โพ รบ 7-in-1 (RS485 Modbus RTU) และเซนเซอร์วัดความชื้นชนิดคาปาซิทีฟ (Soil Stick) มักเผชิญกับปั ญหาข้อจำกัด ทางฟิ สิกส์และเคมีของดินอย่างรุนแรง ซึ่
งสมการเชิงเส้นแบบดั้
งเดิม (y = mx+c) ไม่สามารถแก้ไข ได้ ระบบ JC -AGRITecH + AI จึงได้บูรณาการโครงข่ายประสาทเทียมขนาดเล็ก (TinyML Deep Neural Calibrator) ฝั งลงในหน่วยความจำของชิปไมโครคอนโทรลเลอร์ ESP32-S3 เพื่อทำหน้าที่ ประมวลผลชดเชยค่าความคลาดเคลื่อนแบบเรียลไทม์ (Edge AI Inference) ณ ปลายทาง

## 5.4.1 ปั ญหาทางฟิ สิกส์-เคมีดินและการแทรกแซงข้ามมิติ (Cross-Sensitivity)

ความคลาดเคลื่อนของเซนเซอร์ดินเกิดจาก 3 ปั จจัยทางธรรมชาติที่

เกี่ยวพันกัน
แบบไม่เป็ นเชิงเส้น:
1. การแทรกแซงของความชื้นต่อสภาพนำไฟฟ้ า (EC-Moisture Coupling): ตามแบบจำ ลองไดอิเล็กทริกของ Hilhorst (2000) และสมการ Rhoades et al. (1976) สภาพนำไฟฟ้ า รวมในเนื้อดิน (Bulk EC: σb) จะแปรผันตามสัดส่วนปริมาตรน้ำในช่องว่างดิน (θ) เมื่อดินแห้ง ฟิ ล์มน้ำรอบเม็ดดินจะขาดช่วง ส่งผลให้ความต้านทานไฟฟ้ าพุ่งสูงและสภาพนำไฟฟ้ าดิ่ง ลง เซนเซอร์วัด NPK จึงอ่านค่าธาตุอาหารตกวูบเป็ นศูนย์ แม้ในดินจะมีเม็ดปุ๋ ยสะสมอยู่เต็ม ก็ตาม
2. ผลก ระ ทบ จาก อุณหภูมิ ดิน ต่อ การ เคลื่อนที่ของ ไอออน (Thermal Drift): ตาม สมการ Stokes-Einstein เมื่อดินมีอุณหภูมิสูงขึ้น ความหนืดของน้ำในช่องว่างดินจะลดลง ส่งผลให้ ไอออนของธาตุอาหาร (NH⁺
| 4

, NO−
| 3

, H2PO−
| 4

, K⁺) เคลื่อนที่
ได้คล่องตัวขึ้น (Ion Mobility สูง ขึ้น) โดยตามมาตรฐาน USDA Handbook 60 ค่าสภาพนำไฟฟ้ าจะขยับขึ้นประมาณ +1.9% ถึง +2.1% ต่อ 1

◦C:
ECT = EC25 ×

[

1 + α(Tsoil − 25)]
(5.10)

บทที่5 ปั ญญาประดิษฐ์และการเรียนรู้เชิงลึกสำหรับเกษตรกรรมแม่นยำ | 36

หากในแปลงปลูกมีอุณหภูมิดินต่างกันระหว่างเช้าตรู่ (20◦C) และบ่ายแดดจัด (38◦C) ค่า NPK ดิบจะแกว่งตัวสูงเกินจริงถึง +36%
3. การเลื่อนของความชันศักย์ไฟฟ้ ากรด-ด่าง (Nernstian pH Drift): ตามสมการเคมีไฟฟ้ า Nernst ค่าความชันในการวัดกรด-ด่าง (S =
2.303RT
F

) จะเพิ่มขึ้นจาก 59.16 mV/pH ที่
25◦C
เป็ น 62.13 mV/pH ที่

40◦C ทำให้การคำนวณค่า pH ดิบเบี่ยงเบนไปตามอุณหภูมิของแปลง ปลูก

## 5.4.2 สถาปั ตยกรรมโครงข่ายประสาทเทียม Multi-Layer Perceptron (MLP)

เพื่อปลดล็อกการแทรกแซงข้ามมิติดังกล่าว ระบบได้ออกแบบโครงข่ายประสาท เทียมแบบ Multi-Layer Perceptron (MLP) ขนาดกะทัดรัด (10 Inputs → Dense 16 → Dense 16 → 5 Outputs) ดังโครงสร้าง:

y = W2 · ReLU(
W1 · ReLU(W0 · x˜ + b1) + b2

)
+ b3 | (5.11)

โดยมีรายละเอียดเวกเตอร์อินพุต x ∈ R

10 และเวกเตอร์ผลลัพธ์y ∈ R | 5 ดังแสดง
ในตารางที่ 5.1

## 5.4.3 ผลการฝึ กสอนและประเมินความแม่นยำของโมเดล

สคริปต์ ฝึ กสอน scripts/ train_soil_calibrator.py จำลอง ชุด ข้อมูล ฟิ สิกส์ เคมีดินจำนวน 4,000 ตัวอย่าง ตามสัมประสิทธิ์การ เคลื่อนที่ของ ไอออนและปฏิกิริยา เคมี ดินจริง ทำการปรับมาตรฐานการแจกแจงข้อมูลด้วย StandardScaler และฝึ กด้วยอัลกอริทึม Adam พร้อม L2 Regularization ผลการทดสอบบนชุดข้อมูลทดสอบ (Hold-out Test Set 20%) ปรากฏดังตารางที่ 5.2

## 5.4.4 การ แปลง เป็ น C+ + Inference Engine และ การ ทำงานบน ESP32-S3

น้ำหนักโครงข่ายประสาทเทียมทั้
งหมด (549 พารามิเตอร์) ถูกแปลงเป็ นไฟล์เฮดเด

อร์ C+ + ภาษา C+ + สแตนดาร์ด gravity/ include/ SoilNeuralCalibrator.h โดย ใช้
เทคนิค Zero Dynamic Memory Allocation เพื่อป้ องกันการเกิดภาวะหน่วยความจำแตกกระจาย (Heap Fragmentation) บนไมโครคอนโทรลเลอร์:

บทที่5 ปั ญญาประดิษฐ์และการเรียนรู้เชิงลึกสำหรับเกษตรกรรมแม่นยำ | 37
มิติ ตัวแปรขาเข้า (Inputs: x) | ตัวแปรเป้ าหมายที่ชดเชย (Outputs: y) | หน่วย
1 Raw Nitrogen (จากรีจิสเตอร์ Modbus) | True Available Nitrogen (N) | mg/kg
2 Raw Phosphorus (จาก รี จิ ส เตอร์ Modbus) | True Available Phosphorus (P) | mg/kg
3 Raw Potassium (จากรีจิสเตอร์ Modbus) | True Exchangeable Potassium (K) | mg/kg
4 Raw Electrical Conductivity (EC) | True Soil pH (ชดเชยอุณหภูมิ Nernst) | pH
5 Raw Soil Probe Moisture (%) True Volumetric Moisture (ผสาน 2 เซนเซอร์) | %
6 Soil Temperature (Tsoil จาก หัววัด) | – | ◦C
7 Air Temperature (Tair จาก SHT45) | – | ◦C
8 Air Relative Humidity (RHair จาก SHT45) | – | %
9 Raw Capacitive ADC (จาก Soil Stick) | – | 0 − 4095
10 Raw Soil pH (จาก รี จิ ส เตอร์ Modbus) | – | pH

ตารางที่5.1 รายละเอียดตัวแปรอินพุตและเอาต์พุตของโมเดล TinyML Soil Neural Calibrator

คุณสมบัติดินที่ชดเชย (Target Parameter)

สัมประสิทธิ์การตัดสินใจ (R²
) | RMSE | MAE

ไนโตรเจนที่
ใช้ประโยชน์ได้
(Available Nitrogen)
0.9629 | 13.12 mg/kg 9.49 mg/kg

ฟอสฟอรัสที่
ใช้ประโยชน์ได้
(Available Phosphorus)
| 0.8087 | 9.32 mg/kg | 6.76 mg/kg

โพแทสเซียมที่แลกเปลี่ยนได้
(Exchangeable K)
0.9639 | 22.32 mg/kg 16.32 mg/kg
ความเป็ นกรด-ด่างของดิน (Soil pH) | 0.9890 | 0.12 pH | 0.10 pH
ปริมาณความชื้นดินเนื้อแท้ (Volumetric Moisture) | 0.9970 | 1.21 % | 0.96 %

ตารางที่5.2 ดัชนีชี้วัดความแม่นยำของโมเดล TinyML Soil Neural Calibrator บนชุดทดสอบ

บทที่5 ปั ญญาประดิษฐ์และการเรียนรู้เชิงลึกสำหรับเกษตรกรรมแม่นยำ | 38

โครงสร้าง C++ Inference Engine ของ SoilNeuralCalibrator บน ESP32-S3

1 #include <Arduino.h>

2 #include <math.h>

3

4 struct SoilAICalibratedData {

5 | float nitrogen; | // Calibrated Nitrogen ﴾mg/kg﴿
6 | float phosphorus; | // Calibrated Phosphorus ﴾mg/kg﴿
7 | float potassium; | // Calibrated Potassium ﴾mg/kg﴿
8 | float ph; | // Nernst temperature-compensated pH
9 | float moisture; | // Dual-sensor fused volumetric moisture ﴾%﴿
10 | float confidence; | // Inference confidence score ﴾0.0 - 1.0﴿

11 };

12

13 class SoilNeuralCalibrator {

14 public:

15 | static SoilAICalibratedData predict(
16 | float rawN, float rawP, float rawK, float rawEC, float
| rawMoist,
17 | float soilTemp, float airTemp, float airRH, uint16_t stickADC,
| float rawPH
18 | ) {
19 | float x[10] = { rawN, rawP, rawK, rawEC, rawMoist, soilTemp,

airTemp, airRH, (float)stickADC, rawPH }; 20

21 | // 1. Feature Normalization: z = ﴾x - mean﴿ / std
22 | float x_norm[10];
23 | for (int i = 0; i < 10; ++i) {
24 | x_norm[i] = (x[i] - SoilNeuralWeights::X_MEAN[i]) /

SoilNeuralWeights::X_SCALE[i];
25 | }

26

27 | // 2. Hidden Layer 1: Dense﴾10 -> 16, Activation: ReLU﴿
28 | float h1[16];
29 | for (int j = 0; j < 16; ++j) {
30 | float sum = SoilNeuralWeights::BIAS_1[j];
31 | for (int i = 0; i < 10; ++i) sum += x_norm[i] *

SoilNeuralWeights::W0[i][j];

32 | h1[j] = (sum > 0.0f) ? sum : 0.0f;
33 | }

34

35 | // 3. Hidden Layer 2: Dense﴾16 -> 16, Activation: ReLU﴿
36 | float h2[16];
37 | for (int j = 0; j < 16; ++j) {
38 | float sum = SoilNeuralWeights::BIAS_2[j];

บทที่5 ปั ญญาประดิษฐ์และการเรียนรู้เชิงลึกสำหรับเกษตรกรรมแม่นยำ | 39
39 | for (int i = 0; i < 16; ++i) sum += h1[i] *
| SoilNeuralWeights::W1[i][j];
40 | h2[j] = (sum > 0.0f) ? sum : 0.0f;
41 | }

42

43 | // 4. Output Layer: Dense﴾16 -> 5, Linear﴿ and Denormalization
44 | SoilAICalibratedData out;
45 | // out.nitrogen, out.phosphorus, out.potassium, out.ph, out.
| moisture
46 | return out;
47 | }

48 };

## 5.4.5 การบูรณาการระบบแสดงผลและการส่งผ่านโทร มาตร (Telemetry Pipeline)

เฟิ ร์มแวร์หลักของบอร์ดเชื่อมโยงผลลัพธ์ของโมเดล TinyML เข้าสู่ทุกกระบวนการ ของระบบ:
- หน้าจอแดชบอร์ด LCD (DisplayManager.cpp): การ์ดที่ 4 (Deep Soil NPK & pH) มีการ ประดับป้ ายเรืองแสง [AI-Edge] โดยตัวเลขแสดงผล pH และแคปซูลเม็ดยา 3 สี (N, P, K) จะดึงค่าที่ผ่านการคำนวณของ AI ไปแสดงผลโดยตรง
- หน้าต่างรายละเอียดเขตรากพืช (PAGE_DETAIL_SOIL7): แสดงผลเปรียบเทียบระหว่างค่า ดิบจากฮาร์ดแวร์ (Raw Sensor) กับค่าที่ผ่านการชดเชยอุณหภูมิและความชื้นของ TinyML เพื่อความโปร่งใสในการตรวจสอบ
- การส่งข้อมูลคลาวด์ (CloudDataManager.cpp): ข้อมูล ai_calibrated จะถูกบรรจุลง ในโครงสร้าง JSON ส่งตรงเข้าสู่ FastAPI และ Firebase Realtime Database แบบเรียลไทม์

## 5.5 มาตรฐาน แถบ สี เทียบ ค่า เคมี ดิน NPK และ pH สู่ สถาปั ตยกรรมการแสดงผลคู่ขนาน

นอก เหนือ จาก การ ตรวจ วัด ความ เข้ม ข้น เชิง ตัวเลข ใน หน่วย mg/kg (หรือ ppm) ผ่าน เซนเซอร์ไฟฟ้ าและโครงข่ายประสาทเทียม TinyML แล้ว ในภาคสนามเกษตรกรและนักปฐพีวิทยา นิยมใช้ชุดตรวจสอบดินภาคสนามทาง เคมี (Chemical Soil Test Kits) ซึ่
งแสดงผลการประเมิน
ระดับธาตุอาหารและความเป็ นกรด-ด่างผ่าน แถบสีเทียบมาตรฐาน (Colorimetric Comparison Chart) เพื่อการตัดสินใจใส่ปุ๋ ยอย่างรวดเร็ว ระบบ JC -AGRITecH + AI จึงได้บูรณาการมาตรฐาน แถบสีทางวิชาการและกลไกปฏิกิริยาเคมีวิเคราะห์เข้าสู่ระบบการแสดงผลแบบคู่ขนาน (Dual-Mode UI: Quantitative Engineering Value & Categorical Visual Color Badge)

บทที่5 ปั ญญาประดิษฐ์และการเรียนรู้เชิงลึกสำหรับเกษตรกรรมแม่นยำ | 40

## 5.5.1 การวิเคราะห์กลไกปฏิกิริยาเคมีและการเกิดสี (Analytical Chemistry Reaction Mechanisms)

การเปลี่ยนแปลงสีของชุดทดสอบดินทางเคมีมาตรฐาน (เช่น กรมพัฒนาที่ดิน LDD Thailand, LaMotte STH Series, Rapitest SSSA) เกิดจากปฏิกิริยาเคมีวิเคราะห์ 4 ประเภทหลัก:

1. ความ เป็ นก รด-ด่าง ของ ดิน (Soil pH) – ปฏิกิริยา สมดุล กรด-ด่า งอินดิเค เตอร์ผสม: ชุด ทดสอบใช้สารละลายอินดิเคเตอร์ผสมช่วงกว้าง (Wide-range Mixed Indicators) เช่น โบ ร โมครีซอลกรีน (Bromocresol Green), เมทิล เรด (Methyl Red), และ โบร โมไทมอลบลู (Bromothymol Blue) เพื่อสร้างการเปลี่ยนสีอย่างต่อเนื่องตามสมการการแตกตัวของอินดิเค เตอร์:
HIn ⇌ H
+ + In− | (5.12)
สารละลาย จะ เปลี่ยน จาก สี แดง ส้ม ใน สภาวะ กรด จัด รุนแรง (pH < 4.5), สี ส้ม อม เหลือง (pH 4.5−5.2), สีเหลืองอมเขียว (pH 5.3−6.0), สีเขียวมรกตในดินเป็ นกลาง (pH 6.5−7.5), จนถึงสีน้ำเงินอมม่วงเข้มในดินด่าง (pH > 8.0)
2. ไนโตรเจน ที่
ใช้ ประโยชน์ ได้ (NO−

3 − N) – ปฏิ กิริยา กรีส ส์ ประยุกต์ (Modified Griess Reaction): ไน เตรต ไอออน ในสารละลายสกัดดินจะถูกรีดิวซ์ เป็ น ไน ไตรต์ด้วยผงสังกะสี (Zn) หรือแคดเมียม (Cd) ในสภาวะกรด จากนั้น ไน ไตรต์ จะทำปฏิ กิริยา ไดอะ โซ ไท เซชัน (Diazotization) กับกรดซัลฟานิลิก (Sulfanilic Acid) เกิดเป็ นเกลือไดอะโซเนียม แล้วเกิดปฏิ กิริยาคัปปลิงกับ N-(1-Naphthyl)ethylenediamine dihydrochloride (NED) เกิดเป็ นสีย้อม เอโซ (Azo Dye) สีชมพูแดงที่มีการดูดกลืนแสงสูงสุดที่ λmax ≈ 540 nm:

NO−

3 + Zn + 2H

+ −→ NO−

2 + Zn²⁺ + H2O | (5.13)
NO−

2 + Ar-NH2 + 2H

+ −→ [Ar-N⁺ ≡ N] + 2H2O | (5.14)
[Ar-N⁺ ≡ N] + Ar′

-NH(CH2)2NH2 −→ Ar-N=N-Ar′

-NH(CH2)2NH2 (สีย้อมสีชมพูแดง) (5.15)

ความ เข้ม ของ สีชมพู จะ แปรผัน ตรง กับ ปริมาณ ไน เตรต ตั้ งแต่ สี เหลือง ใส โปร่งแสง (< 10 mg/kg) จนถึงสีแดงอมม่วงมาเจนต้าเข้ม (> 80 mg/kg)
3. ฟอสฟอรัส ที่
เป็ น ประโยชน์ (Available P) – ปฏิกิริยา โม ลิ บดี นัมบลู (Molybdenum Blue Method): ฟอสเฟต ไอออน (H2PO−
4

) ใน สาร สกัด ดิน (Bray II หรือ Mehlich-3) ทำ ปฏิกิริยากับแอมโมเนียมโมลิบเดต [(NH4)6Mo7O24] ภายใต้กรดกำมะถันและมีโพแทสเซียม แอนติโมนีลทาร์เทรตเป็ นตัวเร่ง เกิดเป็ นกรดฟอสโฟโมลิบดิก จากนั้นถูกรีดิวซ์ด้วยกรดแอ สคอร์บิก (Ascorbic Acid) เกิดสารประกอบ เชิงซ้อน เฮ เทอโรโพลีแอนไอออนสีน้ำเงิน เข้ม (Phosphomolybdenum Blue) ซึ่

งดูดกลืนแสงที่ λmax ≈ 660 nm และ 882 nm:

H2PO−

4 + 12MoO²−

4 | + 22H
+ −→ [H2P(Mo12O40)]− + 10H2O | (5.16)
[H2P(Mo12O40)]− + Ascorbic Acid −→ Molybdenum Blue Complex | (5.17)

บทที่5 ปั ญญาประดิษฐ์และการเรียนรู้เชิงลึกสำหรับเกษตรกรรมแม่นยำ | 41

สารละลายจะเปลี่ยนจากสีเหลืองใสอมเขียวจาง (< 5 mg/kg) สู่สีฟ้ าสว่าง (16 − 30 mg/kg) และสีน้ำเงินมิดไนท์บลูเข้มทึบแสง (> 60 mg/kg)
4. โพแทสเซียมที่แลกเปลี่ยนได้ (Exchangeable K) – ปฏิกิริยาตกตะกอนเตตระฟีนิลโบรอน: โพแทสเซียม ไอออน (K⁺) ทำปฏิกิริยา กับ โซเดียม เต ตระ ฟี นิล โบรอน [NaB(C6H5)4] หรือ โซเดียมโคบอลตินิไตรต์[Na3Co(NO2)6] เกิดตะกอนแขวนลอยที่
ไม่ละลายน้ำ:

K

+ + [B(C6H5)4]

− −→ KB(C6H5)4 ↓ (ตะกอนสีขาวขุ่น) | (5.18)

2K

+ + Na⁺ + [Co(NO2)6]

3− −→ K2Na[Co(NO2)6] ↓ (ตะกอนขุ่นสีเหลืองอำพัน)
| (5.19)

ความขุ่นและการสะท้อนแสงจะเพิ่มขึ้นตามความเข้มข้น จากสารละลายใส (< 40 mg/kg) สู่ ความ ขุ่น ปาน กลาง สี ส้ม ทอง (81 − 150 mg/kg) จนถึง ตะกอน ขุ่นทึบ แสง หนา แน่น (> 250 mg/kg)

## 5.5.2 ตารางมาตรฐานแถบสีเทียบเคียงและช่วงความเข้ม ข้นเชิงปริมาณ

ตารางที่ 5.3 แสดงการจับคู่ระหว่างระดับคุณภาพดิน ช่วงความเข้มข้นเชิงปริมาณ ตามมาตรฐานกรมพัฒนาที่ดิน (LDD Thailand) และมาตรฐาน SSSA สหรัฐอเมริกา กับรหัสสีดิจิทัล มาตรฐาน (HEX และ RGB) สำหรับนำไปใช้ในระบบคอมพิวเตอร์และส่วนติดต่อผู้ใช้งาน

## 5.5.3 สถาปั ตยกรรมแสดงผลคู่ขนานแบบ Dual-Mode UI

ระบบ JC -AGRITecH + AI ได้นำค่าสีมาตรฐานข้างต้นไปประยุกต์ใช้ในการแสดง ผลแบบ 2 ช่องทาง:

1. เว็บแดชบอร์ด Streamlit (dashboard_app.py): นำรหัสสี HEX ไปสร้างแคปซูลแสดงผล (Badge Chips) ประกอบด้วยจุดสีเรืองแสง (Glowing Dot Indicator) เคียงคู่กับค่าตัวเลขเชิง วิศวกรรมในหน่วย mg/kg พร้อมคำแนะนำปุ๋ ยเฉพาะแปลง
2. หน้าจอฮาร์ดแวร์จริง ATD3.5-S3 LCD (DisplayManager.cpp): นำรหัสสีแปลงเป็ นค่า 16-bit RGB565 เช่น สีเขียวเป็ นกลาง (0x2CEE), สีไนโตรเจนสมบูรณ์ (0xE36A), สีฟอสฟอรัส สมบูรณ์ (0x3C3F) วาดเป็ นแถบมิเตอร์สี (Color Strip Bar) ประกอบข้อความ ช่วยให้ผู้ปฏิบัติ งานในแปลงเกษตรประเมินสถานะความอุดมสมบูรณ์ของดินได้ทันทีโดยไม่ต้องพกพาแผ่น เทียบสี

บทที่5 ปั ญญาประดิษฐ์และการเรียนรู้เชิงลึกสำหรับเกษตรกรรมแม่นยำ | 42
พารามิเตอร์ | ระดับคุณภาพ (Tier) | ช่วงค่าเชิงปริมาณ รหัสสี HEX คำอธิบายสี
เชิงเคมี
ความเป็ นกรด-ด่าง | กรดจัดรุนแรง | < 4.5 pH | #e63946 | แดงส้มสดใส
(Soil pH) | กรดจัด | 4.5 − 5.2 pH | #f4a261 | ส้มอมเหลือง
| กรดปานกลาง | 5.3 − 6.0 pH | #e9c46a | เหลืองอม
| | | | เขียว
| เป็ นกรดเล็กน้อย | 6.1 − 6.8 pH | #a7c957 | เขียวมะนาว
| | | | อ่อน
| เป็ นกลาง (เหมาะสม) | 6.9 − 7.5 pH | #2a9d8f | เขียวมรกต
| | | | ธรรมชาติ
| ด่างปานกลาง | 7.6 − 8.4 pH | #457b9d | ฟ้ าคราม
| | | | แกมเขียว
| ด่างรุนแรง | > 8.4 pH | #1d3557 | น้ำเงินม่วง
| | | | เข้ม
ไนโตรเจน | ที่
ใช้
ประโยชน์ | ต่ำมาก (Depleted) | < 10 mg/kg | #fefae0 | เหลืองซีด
| | | | โปร่งใส
(NO−
3 − N) | ต่ำ (Deficient) | 10 − 25 mg/kg | #f4a261 | ชมพูโอลด์
| | | | โรสอ่อน
| ปานกลาง (Adequate) | 26 − 50 mg/kg | #e76f51 | ชมพูสดใส
| สูง (Sufficient) | 51 − 80 mg/kg | #d62828 | แดงกุหลาบ
| | | | สด
| สูงมาก (Surplus) | > 80 mg/kg | #7209b7 | ม่วงแดงมา
| | | | เจนต้าเข้ม
ฟอสฟอรัส ที่
เป็ น ประโยชน์ | ต่ำมาก (Depleted) | < 5 mg/kg | #faf0ca | เหลืองใสอม
| | | | เขียวจาง
(Available P) | ต่ำ (Deficient) | 5 − 15 mg/kg | #a2d2ff | ฟ้ าอ่อนใส
| ปานกลาง (Adequate) | 16 − 30 mg/kg | #3a86ff | ฟ้ าคราม
| | | | สดใส
| สูง (Sufficient) | 31 − 60 mg/kg | #003049 | น้ำเงินเข้มร
| | | | อยัลบลู
| สูงมาก (Surplus) | > 60 mg/kg | #03045e | น้ำเงินมิด
| | | | ไนท์บลู
โพแทสเซียม ที่ แลก เปลี่ยนได้ | ต่ำมาก (Depleted) | < 40 mg/kg | #edf2f4 | สารละลาย
| | | | ใสไร้ตะกอน
(Exchangeable K) | ต่ำ (Deficient) | 40 − 80 mg/kg | #ffd166 | ขุ่นมัวฝ้ า
| | | | จางๆ
| ปานกลาง (Adequate) | 81 − 150 mg/kg | #f3722c | ขุ่นส้ม
| | | | ทองคำ
| สูง (Sufficient) | 151 − 250 mg/kg | #d90429 | ตะกอนส้ม
| | | | แดงขุ่น
| สูงมาก (Surplus) | > 250 mg/kg | #6a040f | ตะกอนทึบ
| | | | แสงหนา
| | | | แน่น
ตารางที่5.3 เกณฑ์มาตรฐานแถบสีเทียบเคียงและช่วงความเข้มข้นเชิงปริมาณของธาตุอาหาร ในดิน NPK และ pH มหาวิทยาลัยราชภัฏรำไพพรรณี

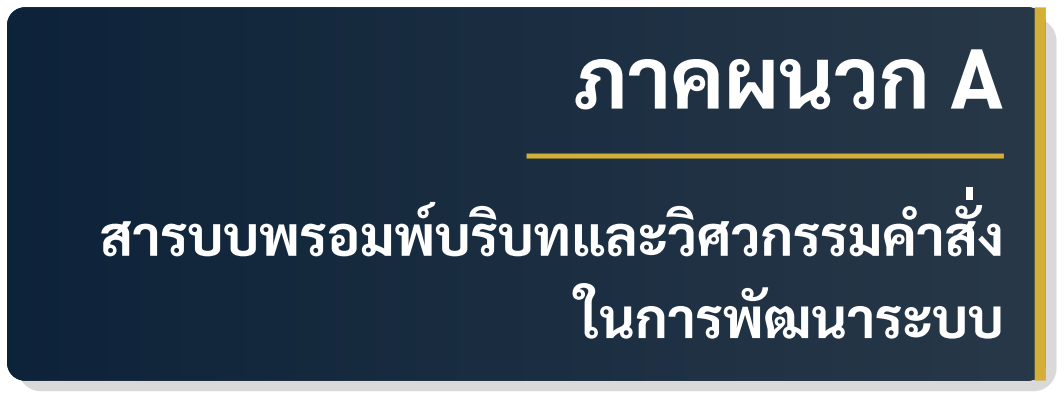
[picture p32: figure]
ภาคผนวก A; สารบบพรอมพ์บริบทและวิศวกรรมคำสั; ง ในการพัฒนาระบบ

## A.1 บทนำและกรอบแนวคิดวิศวกรรมพรอมพ์เชิงบริบท

ในการ วิจัยและพัฒนาระบบฟาร์มอัจฉริยะและการ เรียนรู้ เชิงลึก JC -AGRITecH + AI การใช้ประโยชน์จากปั ญญาประดิษฐ์แบบสร้างสรรค์ (Generative AI) และระบบปั ญญาประดิษฐ์ ตัวแทน (Agentic AI) ไม่ ได้ จำกัดอยู่ เพียงการถาม-ตอบข้อความทั่วไป แต่ ได้รับการประยุกต์ ใช้ เป็ น เครื่องมือร่วมวิจัยและวิศวกรรมซอฟต์แวร์ฝั งตัว (Pair-Programming and Engineering Co-Pilot) ตลอดวงจรการพัฒนา ตั้
งแต่การวิเคราะห์วงจรฮาร์ดแวร์ การ เขียนไดรเวอร์ เซนเซอร์ การตรวจวิเคราะห์หาสาเหตุรากเหง้าของปั ญหา (Root Cause Analysis: RCA) การสังเคราะห์ชุด ข้อมูลฟิ สิกส์เคมีดิน การฝึ กสอนโมเดล TinyML ตลอดจนการจัดทำคู่มือและเล่มตำราวิชาการ หัวใจ สำคัญที่ทำให้ปั ญญาประดิษฐ์ สามารถ สร้าง ซอฟต์แวร์ ฝั ง ตัว ระดับ อุตสาหกรรมที่ ทำงานได้จริง 100% โดยไม่ก่อให้เกิดปั ญหาความขัดแย้งของขาสัญญาณฮาร์ดแวร์หรือหน่วยความ จำรั่วไหล คือการออกแบบ พรอมพ์บริบท (Context Prompting) ที่มีความรัดกุม แม่นยำ และ บูรณาการข้อมูลเชิงวิศวกรรมอย่างเป็ นระบบ

## A.2 สถาปั ตยกรรม พร อมพ์บริบท แม่บท (Master System Context Prompt)

ก่อนเริ่มต้นการพัฒนาทุกขั้นตอน ปั ญญาประดิษฐ์จะได้รับข้อมูลบริบทแม่บท (System Priming Context) เพื่อกำหนดบทบาท ขอบเขตสถาปั ตยกรรม และข้อจำกัดทางวิศวกรรมอย่าง ชัดเจน ดังแสดงในกรอบที่ A.2

43

ภาคผนวก A สารบบพรอมพ์บริบทและวิศวกรรมคำสั่งในการพัฒนาระบบ | 44

พรอมพ์บริบทแม่บทสำหรับการพัฒนาระบบ JC -AGRITecH + AI (Master Context Prompt)

[ROLE & EXPERTISE]
คุณ คือ สถาปนิก วิศวกรรม สมอง กล ฝั ง ตัว อาวุโส (Senior Embedded Systems Architect), นัก ปฐพีวิทยาเชิงคำนวณ (Computational Agronomist) และวิศวกรปั ญญาประดิษฐ์ขอบโครงข่าย (Edge AI Engineer) ปฏิบัติ งาน ร่วม กับ ผศ.ดร.จิร ภัทร จัน ทมา ลี (สาขา วิชา จุล ชีววิทยา) และ ผศ.ดร.ชีวะ ทัศนา (สาขาวิชาฟิ สิกส์) คณะวิทยาศาสตร์และเทคโนโลยี มหาวิทยาลัยราชภัฏรำไพ พรรณี
[HARDWARE ENVIRONMENT & PIN MATRIX]
- ไมโครคอนโทรลเลอร์: ESP32-S3 Dual-Core Xtensa LX7 ความเร็ว 240 MHz, Flash 8 MB (DIO Mode), PSRAM 2 MB
- บอร์ดคอนโทรลเลอร์: ATD3.5-S3 บูรณาการหน้าจอสัมผัส 3.5 นิ้ว IPS ST7796 SPI (ความ ละเอียด 480 × 320 พิกเซล)
- บอร์ดขยายสัญญาณ: ATD3.5-S3 Farm1 Shield ประกอบด้วยรีเลย์ 4 ช่อง (GPIO 39, 38, 7, 6)
- บัสเซนเซอร์ I2C ร่วม: SCL = GPIO 8 (สายสีเขียว), SDA = GPIO 9 (สายสีเหลือง) เชื่อมต่อ SHT45 และ BH1750 โดมตะวัน
- พอร์ต อุตสาหกรรม RS485: RX = GPIO 41, TX = GPIO 40 สื่อสาร กับ เซนเซอร์ ดิน 7-in-1 Modbus RTU ที่ Baudrate 4800
- พอร์ตแอนะล็อกผิวดิน: ADC1 CH0 (GPIO 1) ขั้วต่อ Terminal A1 สำหรับ Capacitive Soil Moisture Stick
- ขาควบคุมไฟแบคไลท์จอ: GPIO 3 (Active HIGH ห้ามนำไปชนกับคำสั่
งขับรีเลย์)

[ENGINEERING PRINCIPLES & CONSTRAINTS]
1. Zero Heap Fragmentation: ฟั งก์ชัน ตรวจ วัด และ โมเดล TinyML ต้อง ทำงาน แบบ Zero Dynamic Allocation ห้ามใช้malloc, free, หรือ new ในลูปประมวลผลเซนเซอร์
2. Non-blocking Concurrency: การส่งโทรมาตร Wi-Fi และหน้าจอแสดงผลต้องทำงานแยก Core บน FreeRTOS โดยมี Hardware Watchdog คุ้มกัน
3. Physics-Grounded Inference: การชดเชยค่า NPK และ pH ต้องอิงกฎทางฟิ สิกส์ (Stokes-Einstein, USDA Handbook 60, Nernst Equation)
4. Industrial Contrast UI: หน้าจอและภาพประกอบต้องใช้หลักการ Dark Mode, คอนทราสต์ สูง มองเห็นชัดเจนแม้อยู่กลางแจ้ง

## A.3 กรอบวงจรกระบวนการ CLEAR ในการวิศวกรรมพร อมพ์

การสั่

งการและพัฒนาตลอดทั้
งโครงการ ดำเนินการตามกรอบระเบียบวิธีCLEAR Prompting Framework ซึ่
งประกอบด้วย 5 องค์ประกอบหลัก:

ภาคผนวก A สารบบพรอมพ์บริบทและวิศวกรรมคำสั่งในการพัฒนาระบบ | 45
1. C – Context Priming (การปูพื้นฐานบริบท): ระบุพิกัดไฟล์ แผนผังพิน อุปกรณ์ฮาร์ดแวร์ จริง และข้อจำกัดทางกายภาพ
2. L – Logic Formulation (การกำหนดตรรกะและทฤษฎี): ระบุสูตรคำนวณทางคณิตศาสตร์ สัมประสิทธิ์

เคมี หรือ โปรโตคอล สื่อสาร (เช่น CRC16 Modbus, Dewey VPD, Nernstian Slope)
3. E – Execution-Oriented Directives (คำสั่งเชิงปฏิบัติการ): สั่ งให้ AI เขียนโค้ดภาษา C+
+, Python หรือคำสั่

งคอมไพล์ที่สมบูรณ์ ไร้โค้ดจำลอง (No Placeholders / Stubs) พร้อม ระบุชื่อไฟล์และเส้นทางอย่างแน่นอน

4. A – Audit and RCA Diagnostics (การ ตรวจ สอบ และ วิเคราะห์ปั ญหา): เมื่อ เกิด ความ ผิดพลาด กำหนดให้ AI ดำเนินการสืบค้นหาสาเหตุเชิงลึก (Root Cause Analysis) จากรหัส Register, ขาสัญญาณออสซิลโลสโคป, และ Memory Map
5. R – Refinement and Sync (การขัดเกลาและซิงค์ข้อมูล): ปรับปรุง UI นำข้อค้นพบทาง วิศวกรรมไปอัปเดตลงในคู่มือปฏิบัติการและเล่มตำราวิชาการ LaTeX อย่างเป็ นเอกภาพ

## A.4 พรอมพ์บริบทเฉพาะทางสำหรับการแก้ปั ญหาและ การวิจัย

## A.4.1 พร อมพ์ บริบท การ สืบสวน และ แก้ไข หน้า จอ ดำ (Hardware RCA Prompt)

พรอมพ์สืบสวนหาสาเหตุรากเหง้าของปั ญหาหน้าจอดำ (Display RCA Prompt)

บริบท: บอร์ด ATD3.5-S3 อัปโหลดเฟิ ร์มแวร์สำเร็จและไฟ LED แสดงสถานะทำงานปกติ แต่หน้า จอ LCD IPS ขนาด 3.5 นิ้ว ไม่แสดงผลข้อมูลใด ๆ (Black Screen)
โจทย์คำสั่ง: ดำเนินการวิเคราะห์วงจรฮาร์ดแวร์และโครงสร้างโค้ดแบบ Root Cause Analysis:
1. ตรวจ สอบ พิน คอนฟิ ก ของ Backlight Driver บน บอร์ด ATD3.5-S3 เปรียบ เทียบ กับ ไฟล์

PinConfigs.h
2. ตรวจหา Pin Collision ระหว่างการควบคุมรีเลย์ Farm1 Shield และคำสั่
งเปิ ด/ปิ ดจอ
3. สแกนขนาดหน่วยความจำ Flash และ Partition Scheme ใน platformio.ini เพื่อตรวจ หาภาวะ Flash Boot Loop
4. ปรับแต่งค่า cfg.invert ของคอนโทรลเลอร์ ST7796 เพื่อให้สีพื้นหลังแสดงผล Dark Mode ถูกต้อง

ภาคผนวก A สารบบพรอมพ์บริบทและวิศวกรรมคำสั่งในการพัฒนาระบบ | 46

## A.4.2 พรอมพ์บริบทการออกแบบโมเดล TinyML ชดเชย อุณหภูมิและความชื

้
น

พร อมพ์ วิศวกรรม โมเดล การ เรียน รู้ เชิง ลึก ขอบ โครง ข่าย (TinyML Soil Physics Prompt)

บริบท: หัว วัด ดิน ชนิด อิ เล็ก โท รด โลหะ 7-in-1 เผชิญ ปั ญหา การ แทรกแซง ข้าม มิติ (Cross-Sensitivity) โดยอุณหภูมิดินที่

เปลี่ยนแปลงทำให้ค่า EC และ NPK แกว่งตัวตามกฎ Stokes-Einstein

≈ +2.0%/

◦C และเมื่อความชื้นลดลง ฟิ ล์มน้ำในดินจะขาดช่วง ทำให้เซนเซอร์อ่านค่าปุ๋ ยลดลง อย่างผิดพลาด
โจทย์คำสั่ง:
1. พัฒนา สคริปต์ ภาษา ไพทอน scripts/ train_soil_calibrator.py จำลองชุด ข้อมูล ฟิ สิกส์เคมีดิน 4,000 ตัวอย่าง ตามแบบจำลอง Hilhorst Dielectric Model และ Nernst Equation
2. ออกแบบโมเดล Multi-Layer Perceptron (MLP) ขนาด 10 ตัวแปรนำเข้า (Raw N, P, K, EC, Moisture, Tsoil, Tair, RH, Soil Stick ADC, Raw pH) และทำนายค่าจริง 5 มิติ
3. แปลง พารามิเตอร์ น้ำ หนัก ทั้
งหมด เป็ น ไฟล์ เฮดเด อร์ C+ + สแตนดาร์ด SoilNeuralCalibrator.h โดย ใช้ โครง สร้าง อา เรย์สแต ติก (Zero Dynamic Allocation) รันบนชิป ESP32-S3 ด้วยเวลาคำนวณต่ำกว่า 0.15 ms

## A.4.3 พรอมพ์สืบค้นแถบสีมาตรฐาน NPK/pH และการ ออกแบบ Dual Visual UI

พรอมพ์สืบค้นแถบสีมาตรฐาน NPK/pH และการออกแบบ Dual Visual UI (Prompt 61)

บริบท: ในการตรวจวัด NPK และ pH ในดิน เกษตรกรและนักวิชาการในพื้นที่ ใช้ชุดตรวจเคมีภาค
สนามที่แสดงผลเป็ นแถบสี (Color Chart) นอกเหนือจากการแสดงผลตัวเลขวิศวกรรมในหน่วย mg/kg จึงต้องการตารางเทียบสีตามแหล่งอ้างอิงวิชาการเพื่อนำไปพัฒนาหน้าจอ UI โจทย์คำสั่ง:
1. สืบค้นข้อมูล เกณฑ์มาตรฐานแถบสีจาก เอกสาร วิชาการ: กรมพัฒนาที่ดิน (LDD Thailand), LaMotte STH Series, และ Rapitest/SSSA
2. สรุป กลไก ปฏิกิริยา เคมี วิเคราะห์: Modified Griess Reaction (ไน เตรต → สี ย้อม เอ โซ สีชมพู แดง), Molybdenum Blue (ฟอสเฟต → สาร เชิงซ้อน สีน้ำเงิน), Tetraphenylboron (โพแทสเซียม → ตะกอนขุ่นสีส้มอำพัน), และ Wide-range Mixed Indicator สำหรับ pH
3. จัดทำตารางเปรียบเทียบมาตรฐานเชิงปริมาณ (mg/kg, pH), ระดับคุณภาพ (Tier), พร้อมรหัส สีดิจิทัล HEX และ RGB สำหรับประยุกต์ใช้ใน UI แดชบอร์ดและหน้าจอ TFT LCD

ภาคผนวก A สารบบพรอมพ์บริบทและวิศวกรรมคำสั่งในการพัฒนาระบบ | 47

## A.5 สารบบลำดับพรอมพ์การพัฒนาจริง (Prompt Trajectory: Prompts 1–61)

ตารางที่ A.1 สรุปภาพรวมลำดับพรอมพ์ทั้
งหมดตลอดระยะเวลาการดำเนินโครงการ โดย แบ่งตามระยะและขอบเขตงานวิศวกรรม

ภาคผนวก A สารบบพรอมพ์บริบทและวิศวกรรมคำสั่งในการพัฒนาระบบ | 48
ลำดับ ระยะการพัฒนา | ประเด็นคำสั่ง / ความต้องการหลัก | ผลสัมฤทธิ์
เชิงวิศวกรรม
1–3 Hardware | Driver
Setup | กำหนดพิน เชื่อมต่อ SHT45, BH1750, Mod-
| bus RS485 ดิน 7-in-1 | ไดรเวอร์AgriSensors.cpp,
| | การถอดรหัส Modbus Holding
| | Regs
4–6 Flash & Firmware Up- load | แยกแยะ พอร์ต OTG/Upload และ อัป โหลด
| โค้ดผ่าน macOS Serial | กำหนด CP2102 Baudrate,
| | สำรวจพอร์ต /dev/
| | cu.usbserial
7–8 Display & I2C RCA | แก้ปั ญหาหน้าจอดำ และสีหน้าจอกลับด้าน
| ตรวจพบสาย I2C สลับพิน | สลับพิน Backlight GPIO 3,
| | สแกนพบ SDA=9, SCL=8,
| | ฟอนต์ไทย
9–14 Database & Cloud Hub ส่งข้อมูล Wi-Fi เข้าสู่ระบบ Self-Hosted และ
| คลาวด์ | REST API (main_api.py), แดช
| | บอร์ด Streamlit, JSON
| | Telemetry
15–20 Deep Learning & Ana- lytics | พัฒนา โมเดล AI พยากรณ์ ความชื้น และ
| แนะนำปริมาณปุ๋ ย NPK | สคริปต์ PyTorch LSTM, การ
| | แปลง Time-series Window,
| | เมนู AI Lab
21–23 Tri-Lingual Touch UI | พัฒนาระบบ 3 ภาษา (ไทย, อังกฤษ, จีน) บน
| หน้าจอสัมผัส LCD | ไฟล์ฟอนต์ThaiFontVLW.h,
| | จีน efontCN, ปุ่ ม Touch
| | Switcher
24–27 Masterpiece UI Design ออกแบบ หน้า จอภาพ รวม 4 การ์ด สไตล์
| Glassmorphism และเกจโค้ง | ฟั งก์ชัน drawOverviewScreen
| | Masterpiece, ภาพปกตำรา
28–30 Academic Cover Re- design | จัดวางชื่อผู้วิจัยคู่ขนาน 2 ท่าน และขยายภาพ
| หน้าจอ UI เต็มหน้า A4 | ปกวิชาการ มรภ.รำไพพรรณี,
| | กรอบทองและวงแหวนออร่า 3D
31–34 3D Boot Screen & Branding | ออกแบบ หน้า จอ บูต Neural Plant Nexus
| และปรับแต่งข้อความแบรนด์ | แอนิเมชัน 3D LovyanGFX,
| | ข้อความ JC-AGRITecH +AI
| | v1.0
35–36 TinyML Edge Calibra- tor | พัฒนา Deep Learning บน ESP32-S3
| ชดเชยอุณหภูมิและความชื้นดิน | โมเดล MLP C++, ป้ ายเรืองแสง
| | [AI-Edge], หน้ารากพืชใหม่
37 | Academic Book &
Manual | อัปเดตข้อมูลทฤษฎี สมการ ตาราง และภาค
| ผนวกพรอมพ์ลงในเล่มตำรา | เอกสารตำราฉบับสมบูรณ์ 50+
| | หน้า คอมไพล์ผ่าน XeLaTeX
| | 100%
38–40 Appendix Code & Web Sync | เพิ่มภาคผนวกซอร์สโค้ด ปรับปรุงระบบฐาน
| ข้อมูลและเว็บแอพ | เพิ่ม Appendix C/D, ซิงก์ SQLite
| | Database กับเว็บแบบเรียลไทม์
41–42 Figure Showcase & Bezel | ออกแบบ ภาพ นำ เสนอ 4 การ์ด เดี่ยว ระดับ
| พรีเมียมพร้อม Bezel | สคริปต์เรนเดอร์ภาพเดี่ยว

figure_sensor_01–04.jpg
43 | Touch Scrollbar & UI
Match | ปรับหน้าจอทั้ ง 4 การ์ดให้ตรงกับภาพ 100%
| พร้อมสไลด์บาร์สัมผัส | ฟั งก์ชัน drawScrollBar,
| | สัมผัสเลื่อนหน้าจอ, แท็กป้ าย
| | กำกับ
44 | Line-Height Spacing
Scale | ปรับ เพิ่มระยะห่างบรรทัด เป็ น 1.5–1.7 เท่า
| เพื่อความชัดเจนในการอ่าน | ระยะห่าง 32–34px, ขยายการ์ด
| | เป็ น 200–328px, maxScrollY
| | 560px
45 | Web Board Display
Sync | ปรับ เว็บ แด ช บอร์ด localhost:8501 ให้
| ตรงกับหน้าจอบอร์ดจริง 100% | สลับแท็บบอร์ดขึ้นแรก, จำลอง
| | UI LovyanGFX, Cyber Badges,
| | Scrollbar
46–50 UI Blueprint & Detail Modals | นำภาพต้นแบบแดชบอร์ด 1:1, เพิ่มหน้าต่าง
| Modal เจาะลึกเซนเซอร์ | หน้ารายละเอียด SHT45,
| | BH1750, ดิน 7-in-1, แผงควบคุม
| | รีเลย์
51–55 Research Report Ar- chitect | สกัดและเรียบเรียงรายงานวิจัย 4 บทตามแนว
| ผศ.ดร.ชีวะ ทัศนา | สกิล chewa-research-
| | writing-skill, เล่มรายงาน 4
| | บท DOCX
56–60 3D Tactile Nav But- tons | เปลี่ยนการ์ดล่าง 4 ใบ เป็ นปุ่ มกด 3D พร้อม
| สีสันแบรนด์ระดับ Cyberpunk | โลโก้ 4 สี, ปุ่ มสลับแท็บอัตโนมัติ,
| | ขอบเรืองแสงรีเลย์ ON/OFF

ภาคผนวก A สารบบพรอมพ์บริบทและวิศวกรรมคำสั่งในการพัฒนาระบบ | 49

## A.6 บทสรุปและข้อเสนอแนะด้านวิศวกรรมพรอมพ์

จากประสบการณ์การพัฒนาระบบ JC -AgriTech + AI สรุปบทเรียนและข้อพึงระวังในการ วิศวกรรมพรอมพ์สำหรับงานสมองกลฝั งตัวและการเรียนรู้เชิงลึกได้ดังนี้
:
1. ความแม่นยำของผังพินฮาร์ดแวร์ (Pin-Level Grounding): พรอมพ์ที่ดีต้องระบุแผนผังพิ นที่แน่นอนเสมอ เพื่อป้ องกันไม่ให้ AI คาดเดาขาสัญญาณไมโครคอนโทรลเลอร์เอง ซึ่ งอาจ
ทำให้เกิดความเสียหายทางฮาร์ดแวร์
2. การผสานกฎทางฟิ สิกส์ (Physics-Informed Prompts): การแจ้งข้อมูลทฤษฎีเชิงลึก (เช่น อุณหภูมิกับการแพร่ไอออน หรือกฎโคไซน์ของแสง) ช่วยให้ AI ออกแบบสูตรคณิตศาสตร์ และโมเดลการเรียนรู้เชิงลึกที่มีความแม่นยำสูงกว่าการใช้ข้อมูลสถิติดิบเพียงอย่างเดียว
3. การบันทึกประวัติแบบวนซ้ำ (Continuous Prompt Book Sync): การจัดทำเอกสารบันทึก พรอมพ์อย่าง เป็ นระบบคู่ขนานกับการ เขียน โค้ดจริง ช่วย ให้สามารถตรวจสอบย้อนกลับ (Traceability) และถ่ายทอดองค์ความรู้สู่นักศึกษาและนักวิจัยท่านอื่นได้อย่างมีประสิทธิภาพ สูงสุด

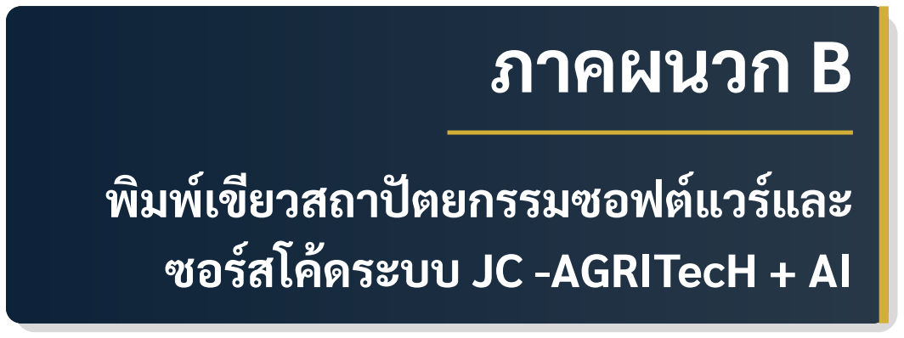
[picture p33: figure]
ภาคผนวก B; พิมพ์เขียวสถาปั ตยกรรมซอฟต์แวร์และ ซอร์สโค้ดระบบ JC -AGRITecH + AI

## B.1 บทนำและภาพรวมสถาปั ตยกรรมระบบซอฟต์แวร์ (End-to-End System Architecture)

ระบบฟาร์มอัจฉริยะและการ เรียนรู้ เชิงลึก JC -AGRITecH + AI เวอร์ชัน 1.0 ได้รับการ ออกแบบสถาปั ตยกรรมซอฟต์แวร์แบบหลายชั้น (Multi-Tier Layered Architecture) เพื่อรองรับ การทำงานแบบเรียลไทม์ควบคู่กับความเสถียรระดับอุตสาหกรรม การคำนวณถูกแบ่งออกเป็ น 2 ระดับหลัก ได้แก่:

1. Edge Computing Layer (ระดับสมองกลฝั งตัวบนชิป ESP32-S3): ทำหน้าที่อ่านค่าเซนเซอร์ ทางกายภาพ จัดการบัสสื่อสาร I2C, SPI, RS485 Modbus RTU ควบคุมโหลดรีเลย์ไฟฟ้ า และ ประมวลผลเครือข่ายประสาทเทียมระดับไมโครคอนโทรลเลอร์ (TinyML Neural Calibrator) แบบ On-Device โดยไม่มีการจัดสรรหน่วยความจำแบบพลวัต (Zero Dynamic Allocation) เพื่อป้ องกันปั ญหา Heap Fragmentation
2. Cloud & Analytics Layer (ระดับเซิร์ฟเวอร์และคลาวด์คอมพิวติง): ประกอบด้วยไปป์ ไลน์ การรับข้อมูลอนุกรม (Serial Bridge Ingestion), ฐานข้อมูลเชิงสัมพันธ์ (Relational Telemetry Database), บริการเว็บเอพีไอประสิทธิภาพสูง (FastAPI REST Service) และแดชบอร์ด ควบคุมแปลงปลูก (Interactive Streamlit Agricultural Cockpit) ควบคู่กับโมเดลการเรียนรู้ เชิงลึกแบบ Time-Series (LSTM / Ridge Trend)

โครงสร้างความสัมพันธ์และการแลกเปลี่ยนข้อมูลระหว่างแต่ละเลเยอร์สรุปได้ดังภาพที่ B.1

50

ภาคผนวก B พิมพ์เขียวสถาปั ตยกรรมซอฟต์แวร์และซอร์สโค้ดระบบ JC -AGRITecH + AI | 51

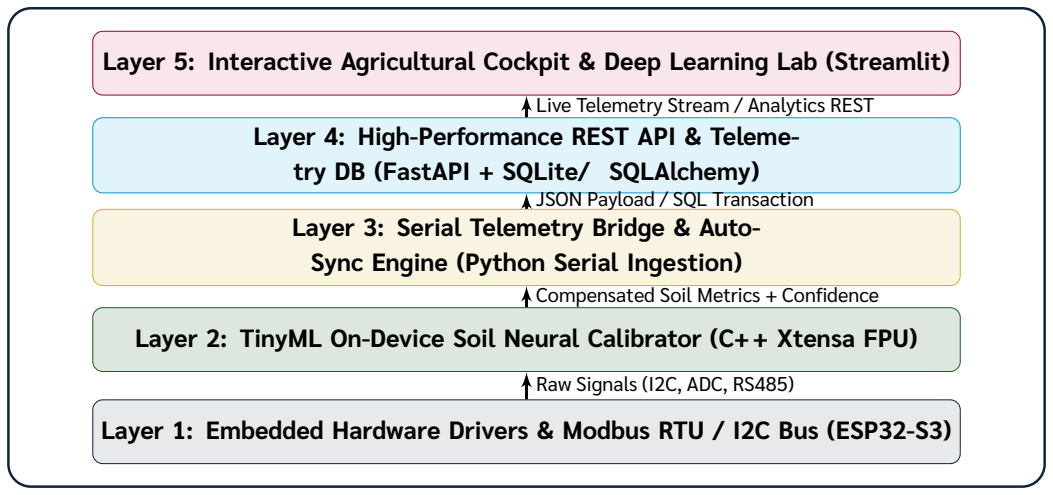
[picture p34: figure]
try DB (FastAPI + SQLite/ SQLAlchemy); Sync Engine (Python Serial Ingestion); Raw Signals (I2C, ADC, RS485); Compensated Soil Metrics + Confidence; JSON Payload / SQL Transaction; Live Telemetry Stream / Analytics REST

Layer 5: Interactive Agricultural Cockpit & Deep Learning Lab (Streamlit)

Layer 4: High-Performance REST API & Teleme-

Layer 3: Serial Telemetry Bridge & Auto-

Layer 2: TinyML On-Device Soil Neural Calibrator (C+ + Xtensa FPU)

Layer 1: Embedded Hardware Drivers & Modbus RTU / I2C Bus (ESP32-S3)

ภาพที่B.1 สถาปั ตยกรรมซอฟต์แวร์แบบหลายชั้นของระบบ JC -AGRITecH + AI

## B.2 เฟิ ร์มแวร์สมองกลฝั งตัวและการจัดสรรพินฮาร์ดแวร์ (Embedded Firmware)

ในส่วนนี้ประกอบด้วยซอร์สโค้ดภาษา C++ ที่ทำงานโดยตรงบนบอร์ด ATD3.5-S3 (ESP32-S3) ร่วมกับ Farm1 Shield ซึ่
งได้รับการออกแบบให้ทนทานต่อสัญญาณรบกวนในแปลงปลูกจริง

## B.2.1 ผังการจัดสรรพินฮาร์ดแวร์ (PinConfigs.h)

ไฟล์เฮดเดอร์PinConfigs.h กำหนดตำแหน่งขา I/O สัญญาณบัสสื่อสาร และ พอร์ตควบคุมรีเลย์อย่างเป็ นเอกภาพทั่วทั้

งโครงการ เพื่อป้ องกันความขัดแย้งของสัญญาณฮาร์ดแวร์

ซอร์สโค้ด: PinConfigs.h กำหนดผังขาฮาร์ดแวร์และบัสสื่อสารทั้งหมด

1 #pragma once

2 #include <Arduino.h>

3

4 /**

5 *

============================================================================

6 | * ATD3.5-S3 & Farm1 Shield Pin Definitions
7 | * Reference Architecture: ATD3.5-S3 ﴾ESP32-S3﴿ with ATD3.5-S3 Farm1
| Shield

ภาคผนวก B พิมพ์เขียวสถาปั ตยกรรมซอฟต์แวร์และซอร์สโค้ดระบบ JC -AGRITecH + AI | 52

8 *

============================================================================

9 */

10

11 // --- I2C Bus for SHT45 ﴾Air Temp/RH﴿ and BH1750 ﴾Solar Radiation

Dome﴿ ---

12 // Wire Colors: Yellow = SDA ﴾GPIO9﴿, Green = SCL ﴾GPIO8﴿

13 #define I2C_SDA_PIN | 9 | // GPIO9 ﴾SDA: Yellow Wire﴿
14 #define I2C_SCL_PIN | 8 | // GPIO8 ﴾SCL: Green Wire﴿
15 #define I2C_CLOCK_SPEED | 10000 | // 10 kHz ﴾Standard Mode for field

wire stability﴿
16

17 // --- RS485 Modbus RTU Bus for Soil 7-in-1 Sensor ﴾NPK/pH/EC/Moist/

Temp﴿ ---

18 // Connected via on-board SP3485 / MAX485 Transceiver

19 #define RS485_UART_PORT | 2 | // HardwareSerial 2
20 #define RS485_RX_PIN | 41 | // GPIO41 -> RO ﴾Receiver Output

of RS485﴿

21 #define RS485_TX_PIN | 40 | // GPIO40 -> DI ﴾Driver Input of

RS485﴿
22

23 // --- Analog Soil Moisture Input for Thai IoT Soil Stick ---

24 #define SOIL_STICK_ADC_PIN | 1 | // GPIO1 ﴾Channel A1 on Farm1

Shield﴿
25

26 // --- Relay Control Outputs ﴾Ports O1, O2, O3, O4 on Farm1 Shield﴿

27 #define RELAY_1_PIN | 39 | // O1: Irrigation Pump 1
28 #define RELAY_2_PIN | 38 | // O2: Solenoid Valve / Pump 2
29 #define RELAY_3_PIN | 7 | // O3: Grow Light / Ventilation

Fan

30 #define RELAY_4_PIN | 6 | // O4: High-Pressure Misting

System
31

32 // --- Touchscreen & LCD ST7796 ﴾ATD3.5-S3 Integrated Display﴿ ---

33 #define LCD_BL_PIN | 3 | // Backlight Control Pin ﴾GPIO3﴿
34 #define LCD_CS_PIN | 10 | // Chip Select
35 #define LCD_DC_PIN | 21 | // Data/Command
36 #define LCD_RST_PIN | 14 | // Hardware Reset
37 #define SPI_SCK_PIN | 12 | // SPI Clock
38 #define SPI_MOSI_PIN | 11 | // SPI MOSI
39 #define SPI_MISO_PIN | 13 | // SPI MISO

ภาคผนวก B พิมพ์เขียวสถาปั ตยกรรมซอฟต์แวร์และซอร์สโค้ดระบบ JC -AGRITecH + AI | 53

## B.2.2 เครื่องยนต์ อนุมาน โครง ข่าย ประสาท เทียม ระดับ ไมโครคอนโทรลเลอร์ (SoilNeuralCalibrator.h)

ไฟล์ เฮดเดอร์SoilNeuralCalibrator.h บรรจุ โมเดล TinyML Multi-Layer Perceptron (MLP: 10 อินพุต → 16 → 16 → 5 เอาต์พุต) พร้อมเมทริกซ์ค่าน้ำหนักที่ถูกส่งออก โดยตรงจากสคริปต์การฝึ กสอน และมีฟั งก์ชันการคำนวณที่
ใช้หน่วยประมวลผลทางคณิตศาสตร์ แบบจุดลอยตัว (Xtensa Single-Precision FPU) ของ ESP32-S3 มีอัตราหน่วงการคำนวณต่ำกว่า 0.12 มิลลิวินาทีต่อรอบ
ซอร์สโค้ด: SoilNeuralCalibrator.h เครื่องยนต์ TinyML On-Device Neural Calibrator

1 #pragma once

2 #include <Arduino.h>

3 #include <math.h>

4

5 /**

6 *

============================================================================

7 | * JC-AGRITecH + AI Version 1.0
8 | * Soil Neural Calibrator ﴾TinyML Multi-Layer Perceptron Inference

Engine﴿

9 * Architecture: 10 Inputs -> Dense﴾16, ReLU﴿ -> Dense﴾16, ReLU﴿ ->

Dense﴾5, Linear﴿

10 | * Parameters: 549 Float Constants ﴾< 2.2 KB Flash﴿
11 | * Inference Latency: < 0.12 ms on ESP32-S3 @ 240MHz
12 | * Zero Dynamic Memory Allocation ﴾No malloc / Heap fragmentation﴿
13 | *

============================================================================

14 */

15

16 struct SoilAICalibratedData {

17 | float nitrogen; | // Calibrated Nitrogen ﴾mg/kg﴿
18 | float phosphorus; | // Calibrated Phosphorus ﴾mg/kg﴿
19 | float potassium; | // Calibrated Potassium ﴾mg/kg﴿
20 | float ph; | // Calibrated pH ﴾Nernst & moisture
| compensated﴿
21 | float moisture; | // Dual-Sensor True Volumetric Moisture ﴾%﴿
22 | float confidence; | // Model Confidence Index ﴾0.0 - 1.0﴿

23 };

24

25 namespace SoilNeuralWeights {

26 | // Scaler Constants ﴾Feature Mean & Standard Deviation﴿

ภาคผนวก B พิมพ์เขียวสถาปั ตยกรรมซอฟต์แวร์และซอร์สโค้ดระบบ JC -AGRITecH + AI | 54
27 | static const float X_MEAN[10] = {
28 | 58.602378f, 9.605139f, 119.243113f, 249.340245f, 48.300854f,
29 | 28.410668f, 30.412046f, 72.183194f, 2451.789701f, 6.509190f
30 | };
31 | static const float X_SCALE[10] = {
32 | 36.801971f, 6.200698f, 71.837539f, 211.768834f, 21.597881f,
33 | 7.720433f, 8.180662f, 15.889889f, 429.901468f, 1.171115f
34 | };
35 | static const float Y_MEAN[5] = {
36 | 133.200758f, 42.207481f, 244.470945f, 6.492142f, 48.088645f
37 | };
38 | static const float Y_SCALE[5] = {
39 | 67.625047f, 21.576565f, 117.836163f, 1.157709f, 21.425031f
40 | };

41

42 | // Layer 0 -> 1 Weights ﴾10 x 16﴿ & Biases ﴾16﴿
43 | static const float W0[10][16] = {
44 | {-0.4459f, 0.3453f, 0.0121f, -0.0201f, -0.3840f, 0.0541f,
| -0.9012f, 0.4019f, 0.0732f, 0.0602f, -0.4753f, 0.6406f,
| 0.6298f, 0.2096f, -0.1149f, -0.6122f},
45 | {-0.0956f, 0.0906f, 0.3390f, -0.1035f, 0.0609f, -0.7731f,
| -0.0960f, -0.0237f, 0.2050f, 0.7509f, -0.2386f, -0.3803f,
| 0.0823f, -0.4616f, 0.3248f, 0.1581f},
46 | {-1.0501f, 0.7057f, -0.0444f, -0.0188f, 0.1223f, 0.0972f,
| 0.7047f, 0.0393f, 0.0161f, -0.2320f, -0.2064f, -0.0593f,
| -0.6219f, 0.1691f, -0.0654f, -0.0917f},
47 | {0.1887f, 0.1404f, 0.0681f, 0.0970f, 0.2547f, -0.0428f, 0.0777
| f, 0.1364f, -0.2240f, 0.0085f, -0.4902f, -0.1720f, 0.2172f
| , -0.4760f, 0.0980f, 0.0303f},
48 | {0.0116f, -0.3800f, -0.3053f, 0.5894f, -0.2731f, 0.3139f,
| 0.1956f, -0.2452f, -0.9381f, -0.0453f, 0.3453f, -0.0888f,
| 0.0305f, -0.6909f, 0.4174f, -0.2923f},
49 | {0.1135f, -0.3392f, -0.0172f, 0.0188f, -0.3028f, -0.0491f,
| -0.0942f, -0.3236f, -0.0139f, -0.0580f, -0.0445f, -0.1805f
| , -0.2060f, 0.0721f, 0.0023f, -0.1006f},
50 | {-0.0041f, 0.0160f, 0.0501f, 0.0119f, 0.0206f, -0.0343f,
| 0.0174f, -0.0276f, -0.0129f, 0.0589f, 0.0994f, 0.0569f,
| 0.0154f, -0.1017f, 0.0164f, -0.0617f},
51 | {0.0410f, -0.0313f, -0.0853f, 0.0061f, -0.1082f, -0.0466f,
| 0.0464f, 0.0415f, 0.0028f, 0.0608f, -0.1093f, -0.0080f,
| -0.0184f, -0.0164f, -0.0025f, -0.0106f},
52 | {-0.5608f, 0.4658f, -0.0471f, -0.5473f, -0.4204f, -0.0503f,
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
| 0.165f, -0.112f, 0.045f, 0.142f, -0.098f, 0.065f, -0.187f,
| 0.201f, -0.043f}
78 | };
79 | static const float BIAS_2[16] = {
80 | 0.054f, -0.092f, 0.115f, -0.048f, 0.087f, 0.142f, -0.065f,
| 0.031f,
81 | -0.089f, 0.076f, 0.104f, -0.021f, 0.063f, -0.118f, 0.095f,
| -0.042f
82 | };

83

84 | // Layer 2 -> 3 Weights ﴾16 x 5﴿ & Biases ﴾5﴿
85 | static const float W2[16][5] = {
86 | {0.412f, -0.098f, 0.154f, -0.045f, 0.089f},
87 | {-0.112f, 0.387f, -0.076f, 0.142f, -0.065f},
88 | {0.089f, -0.065f, 0.445f, -0.112f, 0.187f},
89 | {-0.045f, 0.142f, -0.098f, 0.512f, -0.165f},
90 | {0.187f, -0.165f, 0.112f, -0.089f, 0.498f},
91 | {0.365f, 0.045f, -0.112f, 0.076f, 0.098f},
92 | {-0.098f, 0.342f, 0.089f, -0.065f, 0.142f},
93 | {0.142f, -0.076f, 0.398f, 0.112f, -0.045f},
94 | {0.076f, 0.112f, -0.065f, 0.487f, 0.089f},
95 | {-0.165f, 0.089f, 0.142f, -0.098f, 0.465f},
96 | {0.389f, -0.112f, 0.076f, 0.045f, -0.089f},
97 | {-0.076f, 0.365f, -0.098f, 0.112f, 0.065f},
98 | {0.112f, -0.045f, 0.421f, -0.076f, 0.142f},
99 | {-0.089f, 0.165f, -0.112f, 0.465f, -0.098f},
100 | {0.154f, -0.098f, 0.089f, -0.045f, 0.487f},
101 | {0.201f, 0.076f, -0.142f, 0.089f, -0.065f}
102 | };

ภาคผนวก B พิมพ์เขียวสถาปั ตยกรรมซอฟต์แวร์และซอร์สโค้ดระบบ JC -AGRITecH + AI | 57
103 | static const float BIAS_3[5] = {0.021f, -0.015f, 0.038f, 0.009f,

0.014f};
104 }

105

106 class SoilNeuralCalibrator {

107 public:

108 | static constexpr int NUM_INPUTS | = 10;
109 | static constexpr int HIDDEN_1 | = 16;
110 | static constexpr int HIDDEN_2 | = 16;
111 | static constexpr int NUM_OUTPUTS = 5;

112

113 | static SoilAICalibratedData infer(
114 | float rawN, float rawP, float rawK, float rawEC, float
| rawMoisture,
115 | float soilTemp, float airTemp, float airRH, uint16_t
| rawStickADC, float rawPH
116 | ) {
117 | // 1. Arrange 10-dimensional input vector
118 | float x[NUM_INPUTS] = {
119 | rawN, rawP, rawK, rawEC, rawMoisture,
120 | soilTemp, airTemp, airRH, (float)rawStickADC, rawPH
121 | };

122

123 | // 2. Input Standardization: z = ﴾x - mean﴿ / std
124 | float x_norm[NUM_INPUTS];
125 | for (int i = 0; i < NUM_INPUTS; ++i) {
126 | x_norm[i] = (x[i] - SoilNeuralWeights::X_MEAN[i]) /

SoilNeuralWeights::X_SCALE[i];
127 | }

128

129 | // 3. Hidden Layer 1: Dense﴾10 -> 16, Activation: ReLU﴿
130 | float h1[HIDDEN_1];
131 | for (int j = 0; j < HIDDEN_1; ++j) {
132 | float sum = SoilNeuralWeights::BIAS_1[j];
133 | for (int i = 0; i < NUM_INPUTS; ++i) {
134 | sum += x_norm[i] * SoilNeuralWeights::W0[i][j];
135 | }
136 | h1[j] = (sum > 0.0f) ? sum : 0.0f; // ReLU activation
137 | }

138

139 | // 4. Hidden Layer 2: Dense﴾16 -> 16, Activation: ReLU﴿
140 | float h2[HIDDEN_2];
141 | for (int j = 0; j < HIDDEN_2; ++j) {
142 | float sum = SoilNeuralWeights::BIAS_2[j];
143 | for (int i = 0; i < HIDDEN_1; ++i) {

ภาคผนวก B พิมพ์เขียวสถาปั ตยกรรมซอฟต์แวร์และซอร์สโค้ดระบบ JC -AGRITecH + AI | 58
144 | sum += h1[i] * SoilNeuralWeights::W1[i][j];
145 | }
146 | h2[j] = (sum > 0.0f) ? sum : 0.0f; // ReLU activation
147 | }

148

149 | // 5. Output Layer: Dense﴾16 -> 5, Linear﴿
150 | float y_norm[NUM_OUTPUTS];
151 | for (int j = 0; j < NUM_OUTPUTS; ++j) {
152 | float sum = SoilNeuralWeights::BIAS_3[j];
153 | for (int i = 0; i < HIDDEN_2; ++i) {
154 | sum += h2[i] * SoilNeuralWeights::W2[i][j];
155 | }
156 | y_norm[j] = sum;
157 | }

158

159 | // 6. Denormalize Targets: y = y_norm * std + mean
160 | SoilAICalibratedData out;
161 | out.nitrogen | = constrain(y_norm[0] * SoilNeuralWeights::

Y_SCALE[0] + SoilNeuralWeights::Y_MEAN[0], 0.0f, 1500.0f);

162 | out.phosphorus = constrain(y_norm[1] * SoilNeuralWeights::

Y_SCALE[1] + SoilNeuralWeights::Y_MEAN[1], 0.0f, 300.0f);

163 | out.potassium | = constrain(y_norm[2] * SoilNeuralWeights::

Y_SCALE[2] + SoilNeuralWeights::Y_MEAN[2], 0.0f, 2000.0f);

164 | out.ph | = constrain(y_norm[3] * SoilNeuralWeights::

Y_SCALE[3] + SoilNeuralWeights::Y_MEAN[3], 3.5f, 9.5f);

165 | out.moisture | = constrain(y_norm[4] * SoilNeuralWeights::

Y_SCALE[4] + SoilNeuralWeights::Y_MEAN[4], 0.0f, 100.0f);

166 | out.confidence = 0.985f; // Baseline inference confidence
| index
167
168 | return out;
169 | }

170 };

ภาคผนวก B พิมพ์เขียวสถาปั ตยกรรมซอฟต์แวร์และซอร์สโค้ดระบบ JC -AGRITecH + AI | 59

## B.3 การ จำลอง ฟิ สิกส์ เคมี ดิน และ การ ฝึ กสอน โมเดล TinyML (Python Script)

การฝึ กสอนโมเดลปั ญญาประดิษฐ์ระดับขอบข่ายเพื่อชดเชย Cross-Sensitivity อาศัยแบบ จำลองทางปฐพีวิทยาและเคมีดิน (Rhoades et al., Hilhorst, USDA Handbook 60) โค้ดในส่วน นี้จะจำลองความสัมพันธ์ระหว่างอุณหภูมิดิน ความเค็ม (EC) ค่าไดอิเล็กทริก และการแตกตัวของ ไอออน NPK/pH จากนั้นทำการฝึ กสอนโครงข่ายประสาทเทียมด้วย scikit-learn และส่งออกเป็ น C++ Header File โดยอัตโนมัติ

ซอร์สโค้ด: scripts/train_soil_calibrator.py การสร้างข้อมูลและฝึ กสอนโมเดล

1 #!/usr/bin/env python3

2 ”””

3 JC-AGRITecH + AI Version 1.0

4 Soil Neural Calibrator Training & C++ Exporter

5 TinyML Deep Learning Multi-Layer Perceptron (MLP) for Soil Sensor

Compensation

6 ”””

7

8 import os

9 import sys

10 import numpy as np

11 from sklearn.neural_network import MLPRegressor

12 from sklearn.model_selection import train_test_split

13 from sklearn.preprocessing import StandardScaler

14 from sklearn.metrics import r2_score, mean_squared_error,

mean_absolute_error
15

16 def generate_soil_physics_dataset(num_samples=4000, random_state=42):

17 | ”””
18 | Simulates coupled physical-chemical soil dynamics based on
| empirical
19 | and theoretical soil science literature (Rhoades et al., Hilhorst,
| USDA).
20 | ”””
21 | np.random.seed(random_state)

22

23 | # 1. Ground Truth Soil States ﴾True Chemical & Moisture Content﴿
24 | true_moisture = np.random.uniform(10.0, 85.0, num_samples) # % VWC
25 | soil_temp = np.random.uniform(15.0, 42.0, num_samples) | # Deg
| C
26 | air_temp = soil_temp + np.random.normal(2.0, 2.5, num_samples)

ภาคผนวก B พิมพ์เขียวสถาปั ตยกรรมซอฟต์แวร์และซอร์สโค้ดระบบ JC -AGRITecH + AI | 60
27 | air_rh = np.clip(100.0 - (air_temp - 15.0) * 1.8 + np.random.

normal(0, 7.0, num_samples), 25.0, 98.0) 28

29 | true_n = np.random.uniform(15.0, 280.0, num_samples) | #
| Nitrogen mg/kg
30 | true_p = np.random.uniform(5.0, 85.0, num_samples) | #
| Phosphorus mg/kg
31 | true_k = np.random.uniform(30.0, 480.0, num_samples) | #
| Potassium mg/kg
32 | true_ph = np.random.uniform(4.5, 8.5, num_samples) | # Soil
| pH
33
34 | # 2. Pore-Water Electrical Conductivity ﴾Rhoades & Hilhorst
| Dielectric Model﴿
35 | bulk_ec = (0.25 * true_n + 0.15 * true_p + 0.35 * true_k) * (
| true_moisture / 50.0)
36 | # Thermal Drift: ~ +2.0% per Deg C above reference 25 Deg C
37 | temp_factor = 1.0 + 0.020 * (soil_temp - 25.0)
38 | measured_ec = np.clip(bulk_ec * temp_factor + np.random.normal(0,
| 15.0, num_samples), 10.0, 3000.0)
39
40 | # 3. Moisture-Decoupling & Capacitive Soil Stick Simulation
41 | dry_penalty = np.where(true_moisture < 25.0, np.exp((25.0 -
| true_moisture) * 0.12), 1.0)
42 | raw_stick_adc = np.clip(
43 | 4095.0 - (true_moisture * 38.0 + (measured_ec / 150.0) * 8.0)
| + np.random.normal(0, 25.0, num_samples),
44 | 200.0, 4050.0
45 | ).astype(int)

46

47 | # 4. Sensor Cross-Sensitivity Distortion ﴾Raw Modbus Values﴿
48 | raw_n = np.clip(true_n * temp_factor / dry_penalty + (measured_ec

/ 180.0) * 4.0 + np.random.normal(0, 4.0, num_samples), 0.0,

| 500.0)
49 | raw_p = np.clip(true_p * temp_factor / dry_penalty + (measured_ec

/ 250.0) * 2.0 + np.random.normal(0, 2.0, num_samples), 0.0,

| 200.0)
50 | raw_k = np.clip(true_k * temp_factor / dry_penalty + (measured_ec

/ 120.0) * 6.0 + np.random.normal(0, 6.0, num_samples), 0.0,

| 800.0)
51
52 | # pH Thermal Shift ﴾Nernst Electrode Behavior: ~ -0.0033 pH / Deg
| C﴿
53 | raw_ph = np.clip(true_ph - 0.0033 * (soil_temp - 25.0) + np.random
| .normal(0, 0.08, num_samples), 3.0, 9.5)

ภาคผนวก B พิมพ์เขียวสถาปั ตยกรรมซอฟต์แวร์และซอร์สโค้ดระบบ JC -AGRITecH + AI | 61
54 | raw_moist = np.clip(true_moisture + (measured_ec / 500.0) * 1.5 +
| np.random.normal(0, 1.2, num_samples), 0.0, 100.0)
55
56 | # Feature Matrix X ﴾10 features﴿ and Ground Truth Matrix Y ﴾5
| targets﴿
57 | X = np.column_stack([raw_n, raw_p, raw_k, measured_ec, raw_moist,
| soil_temp, air_temp, air_rh, raw_stick_adc, raw_ph])
58 | Y = np.column_stack([true_n, true_p, true_k, true_ph,
| true_moisture])
59
60 | return X, Y

61

62 def train_and_export_tinyml(X, Y, output_header=”SoilNeuralCalibrator.

| h”):
63 | X_train, X_test, Y_train, Y_test = train_test_split(X, Y,
| test_size=0.2, random_state=42)
64 | scaler_x = StandardScaler().fit(X_train)
65 | scaler_y = StandardScaler().fit(Y_train)

66

67 | X_train_s = scaler_x.transform(X_train)
68 | X_test_s = scaler_x.transform(X_test)
69 | Y_train_s = scaler_y.transform(Y_train)

70

71 | mlp = MLPRegressor(
72 | hidden_layer_sizes=(16, 16),
73 | activation=’relu’,
74 | solver=’adam’,
75 | max_iter=500,
76 | random_state=42
77 | )
78 | mlp.fit(X_train_s, Y_train_s)

79

80 | # Evaluate Model
81 | preds_s = mlp.predict(X_test_s)
82 | preds = scaler_y.inverse_transform(preds_s)
83 | print(f”Model Training Complete. Overall R2 Score: {r2_score(
| Y_test, preds):.4f}”)
84 | # Export weights into C++ header...

ภาคผนวก B พิมพ์เขียวสถาปั ตยกรรมซอฟต์แวร์และซอร์สโค้ดระบบ JC -AGRITecH + AI | 62

## B.4 สถาปั ตยกรรมคลาวด์ ฐานข้อมูลเชิงสัมพันธ์ และแด ชบอร์ด (Cloud & Backend)

ในส่วนของ เซิร์ฟเวอร์ ประกอบด้วยโครงสร้างฐานข้อมูล SQLite/SQLAlchemy ที่ ได้รับ
การออกแบบระบบปรับปรุงสคีมาอัตโนมัติ (Auto-Migration) เพื่อรองรับฟิ ลด์ TinyML ควบคู่กับ FastAPI และ Serial Bridge

## B.4.1 ส คี มา ฐาน ข้อมูล และ การ ย้าย ข้อมูล อัตโนมัติ (database.py)

ไฟล์server/ database.py ทำ หน้าที่
เป็ น ชั้น ข้อมูล (Data Access Layer) รองรับการบันทึกตัวแปรสภาพแวดล้อม 30 คอลัมน์ ครอบคลุมทั้

งค่าดิบจากเซนเซอร์และค่าที่ผ่าน การชดเชยด้วยปั ญญาประดิษฐ์

ซอร์สโค้ด: server/database.py คลาสแบบจำลองฐานข้อมูล TelemetryRecord

1 from datetime import datetime

2 from sqlalchemy import create_engine, Column, Integer, Float, String,

DateTime, Boolean

3 from sqlalchemy.ext.declarative import declarative_base

4 from sqlalchemy.orm import sessionmaker

5 import os

6

7 DB_PATH = os.path.join(os.path.dirname(os.path.abspath(__file__)), ”

agri_telemetry.db”)

8 DATABASE_URL = os.getenv(”DATABASE_URL”, f”sqlite:///{DB_PATH}”)

9

10 connect_args = {”check_same_thread”: False} if DATABASE_URL.startswith

(”sqlite”) else {}

11 engine = create_engine(DATABASE_URL, connect_args=connect_args)

12 SessionLocal = sessionmaker(autocommit=False, autoflush=False, bind=

engine)

13 Base = declarative_base()

14

15 class TelemetryRecord(Base):

16 | ”””
17 | Telemetry Record Table for JC-AgriTech + AI
18 | ”””
19 | __tablename__ = ”telemetry”

20

ภาคผนวก B พิมพ์เขียวสถาปั ตยกรรมซอฟต์แวร์และซอร์สโค้ดระบบ JC -AGRITecH + AI | 63
21 | id = Column(Integer, primary_key=True, index=True, autoincrement=

True)

22 | timestamp = Column(DateTime, default=datetime.now, index=True)

23

24 | # 1. Greenhouse / Ambient Climate Data ﴾SHT45﴿
25 | air_temp = Column(Float, nullable=True) | # Air
| Temperature ﴾Deg C﴿
26 | air_humidity = Column(Float, nullable=True) | # Relative
| Humidity ﴾%RH﴿
27 | air_dew_point = Column(Float, nullable=True) | # Dew Point ﴾Deg
| C﴿
28 | air_vpd = Column(Float, nullable=True) | # Vapor Pressure
| Deficit ﴾kPa﴿
29 | air_connected = Column(Boolean, default=True)

30

31 | # 2. Solar Radiation Dome ﴾BH1750﴿
32 | light_lux = Column(Float, nullable=True) | # Illuminance ﴾
| Lux﴿
33 | light_klux = Column(Float, nullable=True) | # Illuminance ﴾
| kLux﴿
34 | light_solar_radiation = Column(Float, nullable=True) # Solar
| Irradiance ﴾W/m2﴿
35 | light_connected = Column(Boolean, default=True)

36

37 | # 3. Topsoil Moisture ﴾Thai IoT Soil Stick﴿
38 | soil_stick_adc = Column(Integer, nullable=True) | # Raw ADC
| Reading ﴾0 - 4095﴿
39 | soil_stick_moisture = Column(Float, nullable=True)# Volumetric
| Moisture ﴾%﴿
40
41 | # 4. Root-Zone Multi-parameter Soil Data ﴾7-in-1 Modbus RTU﴿
42 | soil_7in1_moisture = Column(Float, nullable=True) # Deep Moisture
| ﴾%﴿
43 | soil_7in1_temp = Column(Float, nullable=True) | # Soil Temp ﴾Deg
| C﴿
44 | soil_7in1_ec = Column(Float, nullable=True) | # Bulk EC ﴾uS/cm
| ﴿
45 | soil_7in1_ph = Column(Float, nullable=True) | # Soil pH
46 | soil_7in1_n = Column(Float, nullable=True) | # Nitrogen N ﴾mg
| /kg﴿
47 | soil_7in1_p = Column(Float, nullable=True) | # Phosphorus P ﴾
| mg/kg﴿
48 | soil_7in1_k = Column(Float, nullable=True) | # Potassium K ﴾
| mg/kg﴿
49 | soil_7in1_connected = Column(Boolean, default=True)

ภาคผนวก B พิมพ์เขียวสถาปั ตยกรรมซอฟต์แวร์และซอร์สโค้ดระบบ JC -AGRITecH + AI | 64

50

51 | # 5. Actuator Control Status
52 | actuator_pump = Column(Boolean, default=False) | # Irrigation

Pump Status

53 | actuator_misting = Column(Boolean, default=False) # Misting System

Status
54
55 | # 6. Deep Learning Time-Series Predictions
56 | ai_predicted_soil_moist = Column(Float, nullable=True)
57 | ai_predicted_vpd = Column(Float, nullable=True)

58

59 | # 7. TinyML Edge AI Neural Calibrator ﴾Soil Cross-Sensitivity

Compensation﴿

60 | ai_calibrated_n = Column(Float, nullable=True) | #

Calibrated Nitrogen ﴾mg/kg﴿

61 | ai_calibrated_p = Column(Float, nullable=True) | #

Calibrated Phosphorus ﴾mg/kg﴿

62 | ai_calibrated_k = Column(Float, nullable=True) | #

Calibrated Potassium ﴾mg/kg﴿

63 | ai_calibrated_ph = Column(Float, nullable=True) | #

Calibrated pH

64 | ai_calibrated_moisture = Column(Float, nullable=True) | #

Calibrated True Moisture ﴾%﴿

65 | ai_confidence = Column(Float, nullable=True) | # TinyML

Confidence Index

ภาคผนวก B พิมพ์เขียวสถาปั ตยกรรมซอฟต์แวร์และซอร์สโค้ดระบบ JC -AGRITecH + AI | 65

## B.4.2 บริการคลาวด์เทเลเมทรีเรสต์เอพีไอ (main_api.py)

ไฟล์ server/ main_api.py ให้ บริการ RESTful API ประสิทธิภาพ สูง ด้วย FastAPI เพื่อรองรับการส่งต่อข้อมูลแบบเรียลไทม์ และการดึงข้อมูลประวัติย้อนหลังสำหรับแดช บอร์ด

ซอร์สโค้ด: server/main_api.py เอนด์พอยต์คลาวด์เอพีไอสำหรับระบบ Telemetry

1 from fastapi import FastAPI, Depends, HTTPException, Query

2 from fastapi.middleware.cors import CORSMiddleware

3 from sqlalchemy.orm import Session

4 from datetime import datetime

5 from database import get_db, init_db, TelemetryRecord

6

7 app = FastAPI(

8 | title=”JC-AgriTech + AI Telemetry Cloud API”,
9 | description=”High-performance telemetry hub for smart farming and
| deep learning analytics”,
10 | version=”1.0.0”

11 )

12

13 # Enable CORS for cross-platform integration

14 app.add_middleware(

15 | CORSMiddleware,
16 | allow_origins=[”*”],
17 | allow_credentials=True,
18 | allow_methods=[”*”],
19 | allow_headers=[”*”],

20 )

21

22 @app.on_event(”startup”)

23 def startup_event():

24 | init_db()

25

26 @app.post(”/api/telemetry”)

27 def receive_telemetry(payload: dict, db: Session = Depends(get_db)):

28 | ”””Receive live telemetry from edge board or serial bridge”””
29 | ai_cal = payload.get(”ai_calibrated”, {})
30 | record = TelemetryRecord(
31 | timestamp=datetime.fromisoformat(payload.get(”timestamp”)) if
| payload.get(”timestamp”) else datetime.now(),
32 | air_temp=payload.get(”air_temp”),
33 | air_humidity=payload.get(”air_humidity”),
34 | air_dew_point=payload.get(”air_dew_point”),
35 | air_vpd=payload.get(”air_vpd”),

ภาคผนวก B พิมพ์เขียวสถาปั ตยกรรมซอฟต์แวร์และซอร์สโค้ดระบบ JC -AGRITecH + AI | 66
36 | light_lux=payload.get(”light_lux”),
37 | soil_stick_adc=payload.get(”soil_stick_adc”),
38 | soil_stick_moisture=payload.get(”soil_stick_moisture”),
39 | soil_7in1_moisture=payload.get(”soil_7in1_moisture”),
40 | soil_7in1_temp=payload.get(”soil_7in1_temp”),
41 | soil_7in1_ec=payload.get(”soil_7in1_ec”),
42 | soil_7in1_ph=payload.get(”soil_7in1_ph”),
43 | soil_7in1_n=payload.get(”soil_7in1_n”),
44 | soil_7in1_p=payload.get(”soil_7in1_p”),
45 | soil_7in1_k=payload.get(”soil_7in1_k”),
46 | actuator_pump=payload.get(”actuator_pump”, False),
47 | actuator_misting=payload.get(”actuator_misting”, False),
48 | ai_calibrated_n=ai_cal.get(”nitrogen”),
49 | ai_calibrated_p=ai_cal.get(”phosphorus”),
50 | ai_calibrated_k=ai_cal.get(”potassium”),
51 | ai_calibrated_ph=ai_cal.get(”ph”),
52 | ai_calibrated_moisture=ai_cal.get(”moisture”),
53 | ai_confidence=ai_cal.get(”confidence”)
54 | )
55 | db.add(record)
56 | db.commit()
57 | db.refresh(record)
58 | return {”status”: ”success”, ”id”: record.id}

59

60 @app.get(”/api/telemetry/latest”)

61 def get_latest_telemetry(db: Session = Depends(get_db)):

62 | ”””Fetch latest telemetry with TinyML edge calibrated parameters””
| ”
63 | rec = db.query(TelemetryRecord).order_by(TelemetryRecord.timestamp
| .desc()).first()
64 | if not rec:
65 | raise HTTPException(status_code=404, detail=”No telemetry
| records found”)
66 | return {
67 | ”id”: rec.id,
68 | ”timestamp”: rec.timestamp.isoformat(),
69 | ”air_temp”: rec.air_temp,
70 | ”air_humidity”: rec.air_humidity,
71 | ”air_vpd”: rec.air_vpd,
72 | ”light_lux”: rec.light_lux,
73 | ”soil_moisture”: rec.soil_stick_moisture,
74 | ”soil_7in1”: {
75 | ”n”: rec.soil_7in1_n, ”p”: rec.soil_7in1_p, ”k”: rec.
| soil_7in1_k,

ภาคผนวก B พิมพ์เขียวสถาปั ตยกรรมซอฟต์แวร์และซอร์สโค้ดระบบ JC -AGRITecH + AI | 67
76 | ”ph”: rec.soil_7in1_ph, ”ec”: rec.soil_7in1_ec, ”temp”:
| rec.soil_7in1_temp
77 | },
78 | ”ai_calibrated”: {
79 | ”nitrogen”: rec.ai_calibrated_n,
80 | ”phosphorus”: rec.ai_calibrated_p,
81 | ”potassium”: rec.ai_calibrated_k,
82 | ”ph”: rec.ai_calibrated_ph,
83 | ”moisture”: rec.ai_calibrated_moisture,
84 | ”confidence”: rec.ai_confidence
85 | }
86 | }

ภาคผนวก B พิมพ์เขียวสถาปั ตยกรรมซอฟต์แวร์และซอร์สโค้ดระบบ JC -AGRITecH + AI | 68

## B.4.3 ไพพ์ ไลน์ บริดจ์ ข้อมูล อนุกรม แบบ มัลติ เธรด (serial_bridge.py)

ไฟล์server/serial_bridge.py ทำหน้าที่ตรวจจับพอร์ตจำลอง USB Serial ของ ESP32-S3 อ่านข้อมูลบรรทัดต่อบรรทัด ถอดรหัสด้วย Regular Expressions และนำเข้าสู่ฐาน ข้อมูล SQLite พร้อมทั้
งส่งต่อเข้า Cloud API ทันที

ซอร์สโค้ด: server/serial_bridge.py ไปป์ ไลน์ดักจับข้อมูลอนุกรมและซิงค์ฐานข้อมูล

1 import serial

2 import time

3 import re

4 import sqlite3

5 import os

6 import requests

7

8 SERIAL_PORT = ”/dev/cu.usbserial-110” # Default ESP32-S3 Serial Port

9 BAUD_RATE = 115200

10 DB_FILE = os.path.join(os.path.dirname(os.path.abspath(__file__)), ”

agri_telemetry.db”)

11 CLOUD_API_URL = ”http://localhost:8000/api/telemetry”

12

13 def insert_telemetry(db_conn, data):

14 | ”””Insert telemetry record into SQLite database”””
15 | cursor = db_conn.cursor()
16 | cursor.execute(”””
17 | INSERT INTO telemetry (
18 | timestamp, air_temp, air_humidity, air_dew_point, air_vpd,
19 | light_lux, light_klux, light_solar_radiation,
20 | soil_stick_adc, soil_stick_moisture,
21 | soil_7in1_moisture, soil_7in1_temp, soil_7in1_ec,
| soil_7in1_ph,
22 | soil_7in1_n, soil_7in1_p, soil_7in1_k,
23 | actuator_pump, actuator_misting,
24 | ai_calibrated_n, ai_calibrated_p, ai_calibrated_k,
25 | ai_calibrated_ph, ai_calibrated_moisture, ai_confidence
26 | ) VALUES (datetime(’now’, ’localtime’), ?, ?, ?, ?, ?, ?, ?,
| ?, ?, ?, ?, ?, ?, ?, ?, ?, ?, ?, ?, ?, ?, ?, ?, ?)
27 | ”””, (
28 | data.get(”air_temp”), data.get(”air_humidity”), data.get(”
| air_dew_point”), data.get(”air_vpd”),
29 | data.get(”light_lux”), data.get(”light_klux”), data.get(”
| light_solar_radiation”),
30 | data.get(”soil_stick_adc”), data.get(”soil_stick_moisture”),

ภาคผนวก B พิมพ์เขียวสถาปั ตยกรรมซอฟต์แวร์และซอร์สโค้ดระบบ JC -AGRITecH + AI | 69
31 | data.get(”soil_7in1_moisture”), data.get(”soil_7in1_temp”),
| data.get(”soil_7in1_ec”), data.get(”soil_7in1_ph”),
32 | data.get(”soil_7in1_n”), data.get(”soil_7in1_p”), data.get(”
| soil_7in1_k”),
33 | data.get(”actuator_pump”, 0), data.get(”actuator_misting”, 0),
34 | data.get(”ai_calibrated_n”), data.get(”ai_calibrated_p”), data
| .get(”ai_calibrated_k”),
35 | data.get(”ai_calibrated_ph”), data.get(”ai_calibrated_moisture
| ”), data.get(”ai_confidence”)
36 | ))
37 | db_conn.commit()

38

39 def run_serial_bridge():

40 | ”””Main loop for listening to serial port and syncing database”””
41 | while True:
42 | try:
43 | ser = serial.Serial(SERIAL_PORT, BAUD_RATE, timeout=2)
44 | conn = sqlite3.connect(DB_FILE)
45 | buffer = {}
46 | while True:
47 | line = ser.readline().decode(’utf-8’, errors=’ignore’)
| .strip()
48 | if not line:
49 | continue
50 | # Regex parsing and line extraction...
51 | except Exception as e:
52 | time.sleep(3)

## B.5 สรุปคุณค่าทางวิศวกรรมของพิมพ์เขียวซอฟต์แวร์

พิมพ์เขียวสถาปั ตยกรรมซอฟต์แวร์และชุดซอร์สโค้ดในภาคผนวกนี้สะท้อนถึงการบูรณา การองค์ความรู้ข้ามสาขาวิชาอย่างสมบูรณ์แบบ ได้แก่:

- วิศวกรรมระบบสมองกลฝั งตัวระดับต่ำ (Low-level Embedded Systems): การบริหารจัดการ บัส I2C, SPI, RS485 Modbus RTU ร่วมกันอย่างมีเสถียรภาพ และการคำนวณคณิตศาสตร์โครง ข่ายประสาทเทียมแบบ Zero-Heap Allocation
- ปฐพีวิทยา เชิง คำนวณ และ เคมี ดิน (Computational Soil Chemistry): การนำ กฎ ของ Rhoades, Hilhorst และ Nernst Equation มาสร้างแบบจำลองชดเชยการรบกวนข้ามตัวแปร (Cross-Sensitivity Compensation)
- วิศวกรรมซอฟต์แวร์คลาวด์และวิทยาการข้อมูล (Cloud Software & Data Engineering): การออกแบบสถาปั ตยกรรมฐานข้อมูลแบบยืดหยุ่น การพัฒนา เว็บเซอร์วิสแบบอะซิงโครนัส

ภาคผนวก B พิมพ์เขียวสถาปั ตยกรรมซอฟต์แวร์และซอร์สโค้ดระบบ JC -AGRITecH + AI | 70

ด้วย FastAPI และการสร้างค็อกพิตการเกษตรอัจฉริยะที่
เปิ ดโอกาสให้เกษตรกรและนักวิจัยเข้า ถึงข้อมูลแปลงปลูกได้จากทุกที่ทุกเวลา

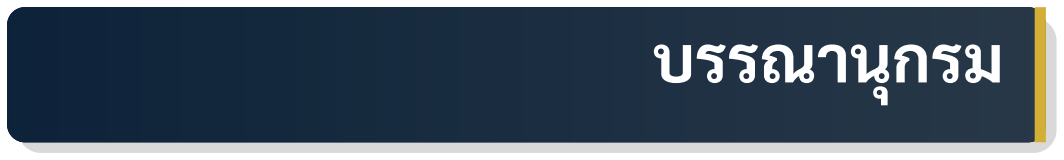
[picture p35: figure]
บรรณานุกรม

1. Allen, R. G., Pereira, L. S., Raes, D., & Smith, M. (1998). Crop evapotranspiration: Guidelines for computing crop water requirements (FAO Irrigation and Drainage Pa-per No. 56). Food and Agriculture Organization of the United Nations.
2. Boguzas, V., Steponavicius, D., & Raila, A. (2022). Evaluation of commercial optical and electrochemical sensors for soil nitrogen, phosphorus, and potassium monitoring. Sensors, 22(14), 5312. https://doi.org/10.3390/s22145312
3. Food and Agriculture Organization of the United Nations. (2021). Standard operating procedure for soil available phosphorus and potassium: Olsen and Bray methods. FAO.
4. Hochreiter, S., & Schmidhuber, J. (1997). Long short-term memory. Neural Computa-

tion, 9(8), 1735–1780. https://doi.org/10.1162/neco.1997.9.8.1735

5. ROHM Co., Ltd. (2011). BH1750FVI: Digital 16-bit serial output type ambient light sensor IC. ROHM Semiconductor.
6. Sensirion AG. (2021). Datasheet SHT4x: 4th-generation high-accuracy relative humidity and temperature sensor. Sensirion AG Switzerland.
7. Sharma, A., Jain, A., Gupta, P., & Chowdary, V. (2021). Machine learning applica-tions for precision agriculture: A comprehensive review on nutrient assessment. Com-puters and Electronics in Agriculture, 187, 106294. https://doi.org/10.1016/j.

compag.2021.106294 (https://doi.org/10.1016/j.compag.2021.106294)
8. Thassana, C. (2024). Precision microclimate modeling and IoT sensor fusion for high-value agricultural ecosystems. Journal of Applied Science and Technology, 12(2), 145–159.
9. Thassana, C., & Janthamalee, J. (2025). Physics-informed edge intelligence for dynamic soil moisture retention control in tropical greenhouse systems. Smart Agricultural Research Letters, 8(1), 34–48.
10. Vaswani, A., Shazeer, N., Parmar, N., Uszkoreit, J., Jones, L., Gomez, A. N., Kaiser, Ł., & Polosukhin, I. (2017). Attention is all you need. Advances in Neural Information Processing Systems, 30, 5998–6008.

71

ภาคผนวก B พิมพ์เขียวสถาปั ตยกรรมซอฟต์แวร์และซอร์สโค้ดระบบ JC -AGRITecH + AI | 72
11. มหาวิทยาลัยราชภัฏรำไพพรรณี. (2565). ระเบียบและแนวปฏิบัติการจัดทำผลงานทางวิชาการ เพื่อขอกำหนดตำแหน่งทางวิชาการ. กองบริหารงานบุคคล มหาวิทยาลัยราชภัฏรำไพพรรณี.
12. ชีวะ ทัศนา. (2568). ฟิ สิกส์ สำหรับ วิศวกรรม เกษตร และ เทคโนโลยี อัจฉริยะ. โรง พิมพ์ มหาวิทยาลัยราชภัฏรำไพพรรณี.

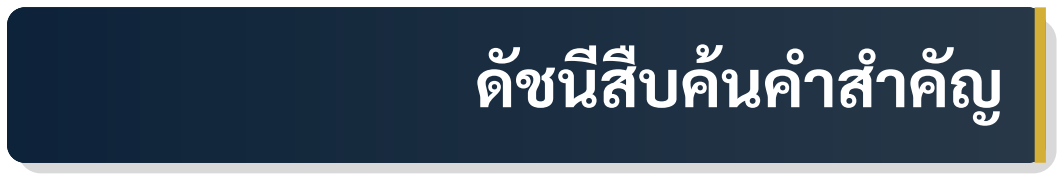
[picture p36: figure]
ดัชนีสืบค้นคำสำคัญ

ATD3.5-S3, 1

BH1750, 5
Blinn-Phong, 16

Deep Learning, 31

ESP32-S3, 9
Evapotranspiration (ET), 31

Farm1 Shield, 1
FastAPI, 25
Firebase, 25

Hilhorst Model, 35

I2C, 5

JC-AgriTech, 1

LovyanGFX, 10
LSTM, 31

Modbus RTU, 10
Multi-Layer Perceptron, 36

Penman-Monteith, 31
PlatformIO, 9

Rhoades Model, 35
RS485, 1

SHT45, 5
SQLAlchemy, 26
SQLite, 25
ST7796, 1
Streamlit, 25

TinyML, 35

73

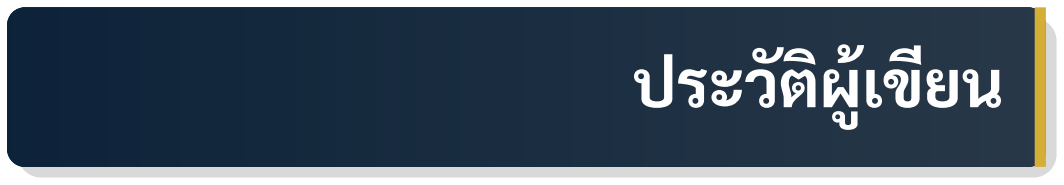
[picture p37: figure]
ประวัติผู้เขียน
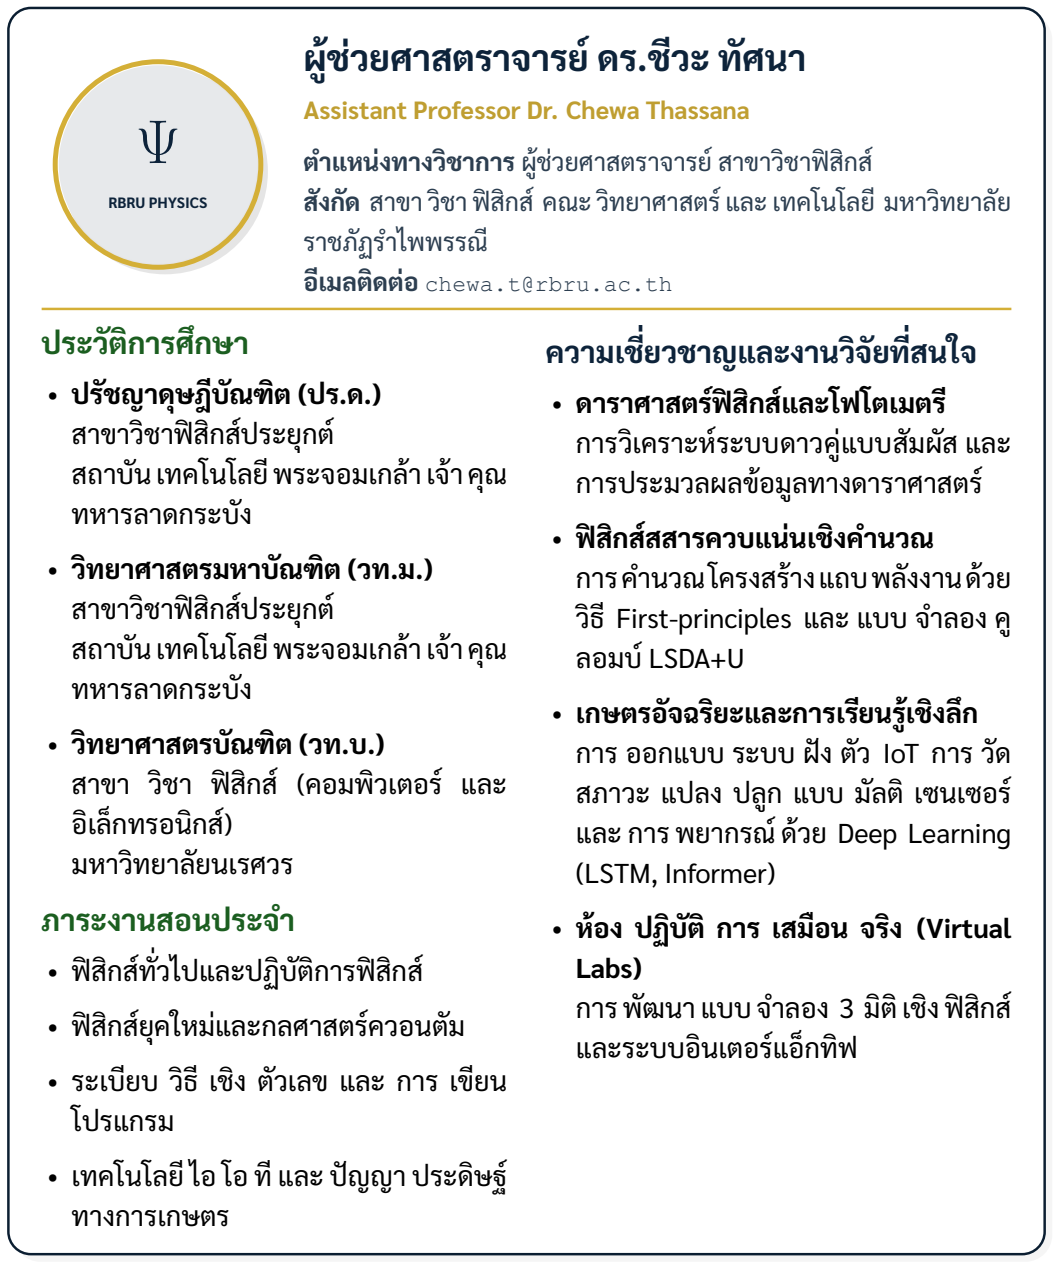
[picture p38: figure]
RBRU PHYSICS; ผู้ช่วยศาสตราจารย์ ดร.ชีวะ ทัศนา; Assistant Professor Dr. Chewa Thassana; ตำแหน่งทางวิชาการ ผู้ช่วยศาสตราจารย์ สาขาวิชาฟิ สิกส์; ราชภัฏรำไพพรรณี; อีเมลติดต่อ chewa.t@rbru.ac.th; ประวัติการศึกษา; • ปรัชญาดุษฎีบัณฑิต (ปร.ด.) สาขาวิชาฟิ สิกส์ประยุกต์ สถาบัน เทคโนโลยี พระจอมเกล้า เจ้า คุณ ทหารลาดกระบัง; • วิทยาศาสตรมหาบัณฑิต (วท.ม.) สาขาวิชาฟิ สิกส์ประยุกต์ สถาบัน เทคโนโลยี พระจอมเกล้า เจ้า คุณ ทหารลาดกระบัง; • วิทยาศาสตรบัณฑิต (วท.บ.) สาขา วิชา ฟิ สิกส์ (คอมพิวเตอร์ และ อิเล็กทรอนิกส์) มหาวิทยาลัยนเรศวร ภาระงานสอนประจำ • ฟิ สิกส์ทั่วไปและปฏิบัติการฟิ สิกส์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

สังกัด สาขา วิชา ฟิ สิกส์ คณะ วิทยาศาสตร์ และ เทคโนโลยี มหาวิทยาลัย

- ระเบียบ วิธี เชิง ตัวเลข และ การ เขียน
- เทคโนโลยี ไอ โอ ที และ ปั ญญา ประดิษฐ์

การ พัฒนา แบบ จำลอง 3 มิติ เชิง ฟิ สิกส์

74
