TsanaPhysics/JC-AGRITecH-AI/thanapat_research/project_dossier/README.md

# คลังข้อมูลโครงการวิจัยและสารบบผู้ช่วยวิจัยหลัก (Research Project Dossier & Lead Assistant Archive)

**โครงการวิจัย** การพัฒนาชุดทดสอบค่าความเป็นกรด-ด่างของดินแบบพกพาภาคสนามความแม่นยำสูงด้วยการชดเชยความคลาดเคลื่อนโดยปัญญาประดิษฐ์  
**คณะผู้วิจัย**  
1. **อาจารย์ธนพัฒน์ ถิระวุฒิ** (หัวหน้าโครงการ สัดส่วน 50%)  
2. **ผู้ช่วยศาสตราจารย์ ดร.ชีวะ ทัศนา** (ผู้ร่วมวิจัย สัดส่วน 30%)  
3. **ผู้ช่วยศาสตราจารย์ ดร.นันทพร มูลรังษี** (ผู้ร่วมวิจัย สัดส่วน 10%)  
4. **รองศาสตราจารย์ ดร.นิภัทร เปี่ยมอรุณ** (ผู้ร่วมวิจัย สัดส่วน 10%)  
**หน่วยงาน** คณะวิทยาศาสตร์และเทคโนโลยี มหาวิทยาลัยราชภัฏรำไพพรรณี  
**งบประมาณ** 75,000 บาท กองทุนวิจัย มหาวิทยาลัยราชภัฏรำไพพรรณี ประจำปีงบประมาณ พ.ศ. 2569  

---

## 1. วัตถุประสงค์ของโฟลเดอร์นี้

โฟลเดอร์นี้จัดทำขึ้นเพื่อเป็นคลังข้อมูลศูนย์กลาง (Single Source of Truth) สำหรับการถอดรหัสข้อเสนอโครงการวิจัยฉบับเต็ม (Full Proposal 26 หน้า) โดยทำหน้าที่เป็นคลังข้อมูลอ้างอิงให้แก่ **ผู้ช่วยวิจัยหลัก (Lead Research Assistant)** ในการปฏิบัติงาน 3 ด้านหลัก

1. **การปรับปรุง ยกร่าง และขยายรายงานวิจัยฉบับสมบูรณ์** ในโฟลเดอร์ `/Users/chewathassana/Desktop/handysense/thanapat_research/` (บทที่ 1 ถึง 5)
2. **การพัฒนาและปรับปรุงโค้ดโปรแกรมแอปพลิเคชันมือถือ** ในแอปพลิเคชันตรวจวัดค่า pH ดิน (Flutter / Dart เช่น วิดเจ็ต `ht_compensation_card.dart` ใน `SoilpH_HT`)
3. **การพัฒนาแบบจำลองปัญญาประดิษฐ์ชดเชยความคลาดเคลื่อน** ทั้งในระดับการฝึกสอนด้วย Python (Scikit-Learn / PyTorch) และการแปลงสู่ระบบสมองกลฝังตัวระดับ Edge (ESP32 C++ / TinyML)

---

## 2. โครงสร้างเอกสารในคลังข้อมูล

* [FULL_PROPOSAL_MASTER_PROFILE.md](file:///Users/chewathassana/Desktop/handysense/thanapat_research/project_dossier/FULL_PROPOSAL_MASTER_PROFILE.md) สรุปสาระสำคัญของข้อเสนอโครงการวิจัย 26 หน้าฉบับสมบูรณ์ ประกอบด้วยประวัติคณะผู้วิจัย วัตถุประสงค์ 3 ข้อ สมมติฐาน แผนผังกรอบแนวคิด ระเบียบวิธีวิจัย 4 ขั้นตอน แผนงบประมาณ 75,000 บาท และผลผลิตผลลัพธ์
* [EXPERIMENTAL_AND_AI_FRAMEWORK.md](file:///Users/chewathassana/Desktop/handysense/thanapat_research/project_dossier/EXPERIMENTAL_AND_AI_FRAMEWORK.md) กรอบทฤษฎีสมการเนินสต์ เมทริกซ์การทดลองในห้องปฏิบัติการด้วยอ่างควบคุมอุณหภูมิ (Water Bath 20-45°C บัฟเฟอร์ 4.01, 7.00, 10.01) สถาปัตยกรรมโครงข่ายประสาทเทียม MLP และเกณฑ์ Method Validation (Error < 5%, %RSD < 5%, t-test)
* [SKILL.md (thanapat-soil-ph-ai-architect)](file:///Users/chewathassana/Desktop/handysense/.agents/skills/thanapat-soil-ph-ai-architect/SKILL.md) สกิลผู้ช่วยวิจัยหลัก ติดตั้งในระบบ `.agents/skills/` พร้อมเรียกใช้งานทันทีสำหรับการเขียนรายงานและพัฒนาโค้ด

---

## 3. สรุปความเชื่อมโยงกับโค้ดโปรแกรมและแอปพลิเคชัน

| ส่วนงาน | ไฟล์และโฟลเดอร์ที่เกี่ยวข้อง | หน้าที่และการประยุกต์ใช้ในโครงการ |
| :--- | :--- | :--- |
| **รายงานวิจัย 4-5 บท** | `thanapat_research/chapters/` | เล่มรายงานวิจัยฉบับสมบูรณ์ เสนอส่งกองทุนวิจัย มรภ.รำไพพรรณี |
| **แอปพลิเคชันมือถือ** | `SoilpH_HT/lib/ui/widgets/ht_compensation_card.dart` | การ์ดหน้าจอคำนวณและแสดงผลการชดเชยความคลาดเคลื่อนอุณหภูมิแบบเรียลไทม์ |
| **สคริปต์ฝึกสอน AI** | `scripts/train_soil_calibrator.py` | โค้ดฝึกสอนโมเดลโครงข่ายประสาทเทียม MLP และสร้าง C++ Array สู่ ESP32 |
| **เฟิร์มแวร์สมองกลฝังตัว** | `server/` / PlatformIO C++ | การอ่านค่า ADC 12-bit จากหัววัด pH และส่งสัญญาณผ่าน BLE 5.0 |
