TsanaPhysics/JC-AGRITecH-AI/leqs-workshop/LEQs_AgriEnvi_xAI_Workshop_Proposal.md

# โครงการอบรมเชิงปฏิบัติการ
## "ปัญญาประดิษฐ์ฝังตัวเพื่อเกษตรดิจิทัลและสิ่งแวดล้อม (LEQs-xAI)"
### (Hands-on Workshop on Embedded AI for Digital Agriculture and Environment)

---

### แหล่งงบประมาณสนับสนุนและหน่วยงานผู้รับผิดชอบ
* **แหล่งงบประมาณ:** งบประมาณเงินรายได้อื่นๆ ประจำปีงบประมาณ พ.ศ. ๒๕๖๙  
  **ภายใต้โครงการหลัก:** **"โครงการเพิ่มศักยภาพครูให้มีสมรรถนะของครูยุคใหม่สำหรับการเรียนรู้ในศตวรรษที่ ๒๑"**
* **หน่วยงานผู้รับผิดชอบ:** คณะวิทยาศาสตร์และเทคโนโลยี มหาวิทยาลัยราชภัฏรำไพพรรณี ร่วมกับโรงเรียนประณีตวิทยาคม และศูนย์พัฒนานวัตกรรมเกษตรดิจิทัล (RBRU-AgriTech Center)
* **วงเงินงบประมาณดำเนินการ:** ๗๖,๐๐๐ บาท (เจ็ดหมื่นหกพันบาทถ้วน) / หรือถัวเฉลี่ยตามกรอบจัดสรร ๕๐–๖๐ คน ๑๒๐,๐๐๐ บาท

---

### 1. ชื่อโครงการและรหัสโครงการ

#### 1.1 ชื่อโครงการภาษาไทย
**โครงการอบรมเชิงปฏิบัติการ "ปัญญาประดิษฐ์ฝังตัวเพื่อเกษตรดิจิทัลและสิ่งแวดล้อม" (LEQs-xAI)**  
*(ภายใต้โครงการเพิ่มศักยภาพครูให้มีสมรรถนะของครูยุคใหม่สำหรับการเรียนรู้ในศตวรรษที่ ๒๑)*

#### 1.2 ชื่อโครงการภาษาอังกฤษ
**Hands-on Workshop on Embedded AI for Digital Agriculture and Environment (LEQs-xAI)**  
*(Under the Teacher Competency Enhancement Program for 21st-Century Learning)*

#### 1.3 ชื่อรหัสโครงการและตัวย่อทางวิชาการ: **LEQs-AgriEnvi-xAI**
ถอดรหัสความหมายตามหลักวิชาการ เทคโนโลยี และสมรรถนะแห่งศตวรรษที่ ๒๑ ได้แก่:
* **L (Learning & Teacher Literacy):** การเรียนรู้เชิงรุก (Active Learning) และการเสริมสร้างความฉลาดรู้ดิจิทัลสำหรับครูและเยาวชนยุคใหม่
* **E (Edge AI & Digital Electronics):** ปัญญาประดิษฐ์ประมวลผลบนอุปกรณ์ฝังตัว (Edge TinyML) ร่วมกับการออกแบบวงจรดิจิทัลอิเล็กทรอนิกส์ควบคุม
* **Q (Quantitative Sensing & Environmental Physics):** การตรวจวัดเชิงปริมาณทางฟิสิกส์สิ่งแวดล้อม (VPD, PAR, Dual-Depth Soil Physics)
* **s (Smart IoT & Sustainability):** ระบบอินเทอร์เน็ตของสรรพสิ่ง (HandySense Platform) และความยั่งยืนของทรัพยากรธรรมชาติและสิ่งแวดล้อม
* **AgriEnvi (Digital Agriculture & Environmental Science):** การบูรณาการเทคโนโลยีเกษตรแม่นยำสูงเข้ากับวิทยาศาสตร์สิ่งแวดล้อมเพื่อความมั่นคงทางอาหาร
* **xAI (Explainable Artificial Intelligence):** ปัญญาประดิษฐ์ที่สามารถอธิบายเหตุผลของการตัดสินใจเชิงกายภาพได้อย่างโปร่งใสและตรวจสอบได้

---

### 2. หลักการและเหตุผล (Background and Rationale)

ในยุคแห่งการเปลี่ยนผ่านสู่สังคมดิจิทัลและความท้าทายระดับโลกด้านความมั่นคงทางอาหารและสภาวะโลกรวน (Climate Crisis) ภาคการศึกษาและการพัฒนากำลังคนของประเทศจำเป็นต้องได้รับการปฏิรูปอย่างเร่งด่วน โดยเฉพาะ **"ครูและบุคลากรทางการศึกษา"** ซึ่งเป็นฟันเฟืองหลักในการถ่ายทอดองค์ความรู้และบ่มเพาะเยาวชน การเรียนรู้ในศตวรรษที่ ๒๑ (21st Century Learning) มิได้จำกัดอยู่เพียงการท่องจำทฤษฎีในห้องเรียน หากแต่ต้องมุ่งเน้นการสร้างสมรรถนะเชิงบูรณาการตามแนวทาง **TPACK (Technological Pedagogical Content Knowledge)** ที่ผสานทักษะด้านเทคโนโลยี วิธีการสอนเชิงรุก (Active Learning) และเนื้อหาวิชาการเข้าด้วยกันอย่างกลมกลืน

กระทรวงการอุดมศึกษา วิทยาศาสตร์ วิจัยและนวัตกรรม (อว.) และมหาวิทยาลัยราชภัฏรำไพพรรณี มีพันธกิจสำคัญในการยกระดับศักยภาพครูให้มีสมรรถนะของครูยุคใหม่ โดยเฉพาะในกลุ่มสาระวิทยาศาสตร์ เทคโนโลยี คอมพิวเตอร์ และการงานอาชีพ ให้ก้าวทันเทคโนโลยีเปลี่ยนโลก (Disruptive Technologies) ๔ เสาหลักสำคัญ ได้แก่:

1. **ดิจิทัลอิเล็กทรอนิกส์และระบบควบคุมอัตโนมัติ (Digital Electronics & Embedded Control):** การทำความเข้าใจโครงสร้างวงจรดิจิทัล การเชื่อมต่อบัสสื่อสารมาตรฐานอุตสาหกรรม (RS485 Modbus RTU, I2C, SPI), การแปลงสัญญาณแอนะล็อกเป็นดิจิทัล (ADC Sampling), การควบคุมโหลดกำลังสูงผ่าน Optocoupler Relay Isolation และการจัดการพลังงานในระบบตรวจวัดภาคสนาม
2. **ระบบอินเทอร์เน็ตของสรรพสิ่งเพื่อการเกษตรและสิ่งแวดล้อม (Smart IoT & Environmental Telemetry):** การตรวจวัดสภาวะแวดล้อมในแปลงเกษตรแบบเรียลไทม์ผ่านแพลตฟอร์มเปิด HandySense, การติดตามค่าทางกายภาพระดับจุลภาค เช่น ความดันไอขาดดุล (Vapor Pressure Deficit: VPD) เพื่อเตือนภัยโรคพืช, ดัชนีความเข้มแสงสังเคราะห์ (PAR), และการตรวจวัดความชื้นดินสองระดับความลึก (Dual-Depth Soil Sensing: 0–10 cm และ 10–30 cm) เพื่อป้องกันการสิ้นเปลืองทรัพยากรน้ำ
3. **คอมพิวเตอร์วิทัศน์และการเรียนรู้เชิงลึก (Computer Vision & Deep Learning):** การประมวลผลข้อมูลภาพถ่ายแปลงเกษตร (Plant Vision) เพื่อจำแนกสุขภาพใบพืช ตรวจจับโรคและแมลงศัตรูพืช และการประเมินสภาพหน้าดินด้วยแบบจำลองโครงข่ายประสาทเทียม (CNN)
4. **ปัญญาประดิษฐ์ระดับอุปกรณ์ฝังตัวและปัญญาประดิษฐ์อธิบายได้ (Edge AI / TinyML & Explainable AI):** การบีบอัดและแปลงแบบจำลองสมองกลให้สามารถติดตั้งและประมวลผลบนไมโครคอนโทรลเลอร์ขนาดเล็ก (ESP32-S3) ได้โดยตรง ทำให้ระบบสามารถตัดสินใจสั่งการวาล์วน้ำ แจ้งเตือนสภาวะวิกฤตได้แบบออฟไลน์ (Zero-Cloud / Offline Real-time Inference) มีความเร็วในระดับมิลลิวินาที ปลอดภัย และประหยัดพลังงาน พร้อมทั้งสามารถแสดงผลเหตุผลการตัดสินใจ (xAI Reasoner) ให้ผู้ใช้งานเข้าใจได้อย่างโปร่งใส

โครงการนี้ได้รับการสนับสนุนงบประมาณจาก **"งบรายได้อื่นๆ ภายใต้โครงการเพิ่มศักยภาพครูให้มีสมรรถนะของครูยุคใหม่สำหรับการเรียนรู้ในศตวรรษที่ ๒๑"** โดยมีกลุ่มเป้าหมายร่วมกัน ๓ ประสาน คือ **ครูและบุคลากรทางการศึกษา, นักเรียนระดับมัธยมศึกษาตอนปลาย และเกษตรกร/ชุมชนในท้องถิ่น** เพื่อสร้างระบบนิเวศแห่งการเรียนรู้ร่วมกัน (Co-Learning Ecosystem) โดยครูจะได้รับการพัฒนาให้เป็น "ครูนวัตกร" ที่สามารถออกแบบแผนการสอนสะเต็มศึกษา (STEM Education) และโครงงานวิทยาศาสตร์ดิจิทัล นักเรียนจะได้รับการฝึกทักษะสร้างชิ้นงานนวัตกรรมจริงเพื่อต่อยอดสู่ TCAS Portfolio และการประกวดระดับชาติ และเกษตรกรในพื้นที่จะได้รับเทคโนโลยีที่จับต้องได้และนำไปใช้งานจริงในแปลงปลูก ซึ่งสอดรับโดยตรงกับ **เป้าหมายการพัฒนาที่ยั่งยืนของสหประชาชาติ (UN Sustainable Development Goals: SDGs)** ได้แก่ SDG 2, SDG 4, SDG 9, SDG 12, SDG 13, SDG 15 และ SDG 17

---

### 3. วัตถุประสงค์ของโครงการ (Objectives)

การดำเนินโครงการมีวัตถุประสงค์หลัก ๕ ประการที่สอดคล้องกับยุทธศาสตร์การพัฒนาครูยุคใหม่และเป้าหมายการพัฒนาที่ยั่งยืน (SDGs) ดังนี้:

1. **เพื่อเพิ่มศักยภาพและยกระดับสมรรถนะครูยุคใหม่ในศตวรรษที่ ๒๑ (Teacher 21st-Century Competencies):** ให้มีความรู้เชิงลึกและทักษะปฏิบัติการด้านดิจิทัลอิเล็กทรอนิกส์, IoT, คอมพิวเตอร์วิทัศน์ และปัญญาประดิษฐ์ฝังตัว (Edge AI/TinyML) สามารถนำไปบูรณาการจัดการเรียนรู้เชิงรุก (Active Learning) และวิจัยในชั้นเรียนได้อย่างมีประสิทธิภาพ **(สอดคล้องกับ SDG 4 การศึกษาที่มีคุณภาพ เป้าประสงค์ 4.4 และ 4.c)**
2. **เพื่อถ่ายทอดทักษะการประกอบวงจรดิจิทัลอิเล็กทรอนิกส์และการตรวจวัดสภาพแวดล้อมทางฟิสิกส์:** การสื่อสาร RS485 Modbus RTU, การตรวจวัดสารอาหารดิน NPK, pH, EC และความชื้นในดิน เพื่อการทำเกษตรกรรมแม่นยำสูง เพิ่มผลผลิต และสร้างความมั่นคงทางอาหาร **(สอดคล้องกับ SDG 2 ขจัดความหิวโหย เกษตรยั่งยืน เป้าประสงค์ 2.4)**
3. **เพื่อส่งเสริมการบริหารจัดการทรัพยากรน้ำ พลังงาน และปัจจัยการผลิตอย่างชาญฉลาด:** ผ่านอัลกอริทึมควบคุมวาล์วรดน้ำอัตโนมัติ ๒ ระดับความลึก และปัญญาประดิษฐ์อธิบายได้ (xAI) ลดการสูญเสียน้ำชลประทาน ลดการตกค้างของปุ๋ยเคมี และฟื้นฟูโครงสร้างดินอย่างยั่งยืน **(สอดคล้องกับ SDG 12 การผลิตและบริโภคที่ยั่งยืน เป้าประสงค์ 12.2 และ SDG 15 ระบบนิเวศบนบก เป้าประสงค์ 15.3)**
4. **เพื่อสร้างระบบเฝ้าระวังและปรับตัวต่อสภาพภูมิอากาศแปรปรวน (Climate-Smart Adaptation):** ด้วยการตรวจวัดค่าความดันไอขาดดุล (VPD) และดัชนีแสงแดด (PAR) เพื่อเตือนภัยสภาวะปากใบพืชปิดและการระบาดของโรคพืชจากความชื้นวิกฤต **(สอดคล้องกับ SDG 13 การรับมือการเปลี่ยนแปลงสภาพภูมิอากาศ เป้าประสงค์ 13.1 และ 13.3)**
5. **เพื่อสร้างเครือข่ายความร่วมมือเชิงพื้นที่ (School-University-Community Partnership):** ระหว่างมหาวิทยาลัยราชภัฏรำไพพรรณี โรงเรียนประณีตวิทยาคม และชุมชนเกษตรกรรม ในการร่วมกันพัฒนานวัตกรรมเทคโนโลยีเปิด (Open Hardware & Software) ที่ชุมชนสามารถพึ่งพาตนเองได้ในระยะยาว **(สอดคล้องกับ SDG 9 โครงสร้างพื้นฐานและนวัตกรรม เป้าประสงค์ 9.5 และ SDG 17 หุ้นส่วนความร่วมมือเพื่อการพัฒนา เป้าประสงค์ 17.17)**

---

### 3.1 ตารางกรอบความสอดคล้องกับเป้าหมายการพัฒนาที่ยั่งยืน (Alignment with UN SDGs Matrix)

| เป้าหมาย SDG | เป้าประสงค์ย่อย (Targets) | กิจกรรมและการดำเนินงานในโครงการ LEQs-AgriEnvi-xAI | ผลลัพธ์และตัวชี้วัดเชิงประจักษ์ (Metrics & Outcomes) |
| :--- | :--- | :--- | :--- |
| **SDG 4 การศึกษาที่มีคุณภาพ (Quality Education)** | **4.4 & 4.c** เสริมสร้างสมรรถนะครูยุคใหม่และเพิ่มจำนวนเยาวชนที่มีทักษะเทคนิคดิจิทัลขั้นสูง | ค่ายอบรมเข้มข้น Hands-on 70% ด้านวงจรดิจิทัลอิเล็กทรอนิกส์, Edge TinyML, Computer Vision, การออกแบบสื่อการสอน Active Learning และ Capstone Hackathon | ครูได้แผนการจัดการเรียนรู้ Active Learning 100%, นักเรียนผ่านเกณฑ์ Post-test $\ge 70\%$ พร้อมผลงานบรรจุลง TCAS Portfolio |
| **SDG 2 ขจัดความหิวโหย (Zero Hunger)** | **2.4** ระบบการผลิตอาหารและเกษตรกรรมยั่งยืน ปรับตัวต่อสภาพอากาศ | ติดตั้งเซนเซอร์ 7-in-1 Modbus RS485 ตรวจวัด NPK, pH, EC และความชื้นเขตรากพืช ทำให้สามารถใส่ปุ๋ยและให้น้ำตรงตามความต้องการทางสรีรวิทยาพืช | ลดต้นทุนปุ๋ยเคมีลงอย่างน้อย 15–25%, เพิ่มผลผลิตต่อไร่, เกษตรกรมีเครื่องมือตรวจวิเคราะห์ดินประจำแปลง |
| **SDG 9 นวัตกรรมและโครงสร้างพื้นฐาน (Industry, Innovation & Infrastructure)** | **9.5** ยกระดับการวิจัย นวัตกรรม และขีดความสามารถทางเทคโนโลยีเปิด | พัฒนาสถาปัตยกรรมบอร์ด ATD3.5-S3 (ESP32-S3), HandySense Open Platform และโมเดล Edge AI ออฟไลน์ แจกจ่ายโค้ดต้นแบบเป็นโอเพนซอร์สบน GitHub | โรงเรียนและชุมชนเข้าถึงเทคโนโลยีเปิดโดยไม่มีค่าลิขสิทธิ์ซอฟต์แวร์ สามารถนำไปสร้างบอร์ดใช้งานเองได้ |
| **SDG 12 การผลิตและบริโภคที่ยั่งยืน (Responsible Consumption & Production)** | **12.2** การจัดการและใช้ทรัพยากรธรรมชาติอย่างมีประสิทธิภาพสูงสุด | อัลกอริทึมควบคุมการให้น้ำอัตโนมัติด้วยฮิสเทอรีซิส ตรวจวัดความชื้นผิวดิน (0–10 cm) ควบคู่เขตรากลึก (10–30 cm) สั่งการตัดน้ำเมื่อดินอิ่มตัว | ประหยัดน้ำชลประทานลงร้อยละ 20–30, ป้องกันการสูญเสียธาตุอาหารจากการชะล้างหน้าดิน |
| **SDG 13 รับมือสภาพภูมิอากาศแปรปรวน (Climate Action)** | **13.1 & 13.3** เสริมสร้างขีดความสามารถในการปรับตัวและเตือนภัยล่วงหน้า | การตรวจวัดอุณหภูมิและความชื้นสัมพัทธ์อากาศด้วย SHT45 คำนวณค่าความดันไอขาดดุล (VPD) เพื่อแจ้งเตือนสภาวะปากใบพืชปิดและการระบาดของเชื้อรา | ระบบแจ้งเตือนภัยล่วงหน้า (Early Warning) ป้องกันความเสียหายของไม้ผลจากคลื่นความร้อนและฝนทิ้งช่วง |
| **SDG 15 ระบบนิเวศบนบก (Life on Land)** | **15.3** ฟื้นฟูดินเสื่อมโทรมและป้องกันการสูญเสียความอุดมสมบูรณ์ | การตรวจวัดค่ากรด-ด่าง (pH) และความเค็ม (EC) ในดิน แจ้งเตือนการปรับปรุงดินด้วยอินทรียวัตถุหรือโดโลไมต์ก่อนดินเปรี้ยวหรือเสื่อมโทรมรุนแรง | รักษาความอุดมสมบูรณ์และจุลินทรีย์ในดิน สนับสนุนเกษตรอินทรีย์และการอนุรักษ์สิ่งแวดล้อมดิน |
| **SDG 17 หุ้นส่วนความร่วมมือเพื่อการพัฒนา (Partnerships for the Goals)** | **17.17** ส่งเสริมความเป็นหุ้นส่วนไตรภาคี (มหาวิทยาลัย-โรงเรียน-ชุมชน) | บันทึกความร่วมมือทางวิชาการ (MOU) ระหว่าง มรภ.รำไพพรรณี, รร.ประณีตวิทยาคม, เกษตรกร จ.จันทบุรี-ตราด และชุมชนเทคโนโลยี HandySense | เกิดเครือข่ายความร่วมมือเชิงพื้นที่อย่างเข้มแข็ง มีกลุ่มสนับสนุนทางเทคนิคต่อเนื่อง 30–60 วันหลังอบรม |

---

### 4. กลุ่มเป้าหมายและคุณสมบัติผู้เข้ารับการอบรม (Target Groups)

### 4. กลุ่มเป้าหมายและคุณสมบัติผู้เข้ารับการอบรม (Target Groups)

โครงการนี้รองรับผู้เข้าร่วมอบรมจำนวนทั้งสิ้น **๕๐–๖๐ คน** แบ่งออกเป็น ๔ กลุ่มเป้าหมายตามยุทธศาสตร์ ๓ ประสาน (ครู-นักเรียน-ชุมชน) ดังนี้:

| กลุ่มเป้าหมาย | สัดส่วน | คุณสมบัติพื้นฐาน | ประโยชน์และสมรรถนะที่ได้รับจากโครงการ |
| :--- | :---: | :--- | :--- |
| **๑. ครูและบุคลากรทางการศึกษา**<br>*(กลุ่มเป้าหมายหลักตามงบประมาณ)* | **๑๕–๒๐ คน** | ครูผู้สอนกลุ่มสาระการเรียนรู้วิทยาศาสตร์และเทคโนโลยี, คอมพิวเตอร์, ฟิสิกส์ หรือการงานอาชีพ ในสังกัด สพม., สพป. หรือ อปท. | **ยกระดับสมรรถนะครูยุคใหม่ในศตวรรษที่ ๒๑ (TPACK):**<br>• ได้รับทักษะปฏิบัติการฮาร์ดแวร์ดิจิทัลอิเล็กทรอนิกส์, IoT และ Edge AI<br>• ได้รับแผนการจัดการเรียนรู้เชิงรุก (Active Learning Lesson Plan)<br>• ได้รับชุดสื่อการสอนจำลองเสมือนจริง (Virtual Lab) ไปใช้จัดการเรียนรู้<br>• ต่อยอดเป็นผลงานวิจัยในชั้นเรียน และการขอมี/เลื่อนวิทยฐานะตามเกณฑ์ ว PA |
| **๒. นักเรียนมัธยมศึกษาตอนปลาย** | **๒๐–๒๕ คน** | กำลังศึกษาในระดับ ม.๔–ม.๖ แผนการเรียนวิทย์-คณิต, เทคโนโลยี หรือมีความสนใจด้าน AI, Coding และสิ่งแวดล้อม | **บ่มเพาะทักษะนวัตกรเยาวชน:**<br>• ทักษะ C++, MicroPython, TinyML และ Computer Vision<br>• ได้ชิ้นงานโครงงานต้นแบบ (Capstone Prototype) ที่ใช้งานได้จริง<br>• ได้โค้ดโอเพนซอร์สบน GitHub และเกียรติบัตรสำหรับแฟ้มสะสมงาน TCAS Portfolio |
| **๓. เกษตรกรผู้เพาะปลูกและผู้นำชุมชน** | **๑๐–๑๕ คน** | เกษตรกรผู้ปลูกไม้ผล พืชสวน พืชเศรษฐกิจ เกษตรกรรุ่นใหม่ (Young Smart Farmer) หรือผู้นำวิสาหกิจชุมชน | **ยกระดับฟาร์มสู่เกษตรแม่นยำสูง (Precision Farming):**<br>• สามารถประกอบ ติดตั้ง และบำรุงรักษาระบบเซนเซอร์และ IoT ประจำสวนได้เอง<br>• เข้าใจค่าความชื้นดิน ๒ ระดับความลึก และค่า VPD ช่วยลดค่าน้ำ-ค่าปุ๋ย และคุมโรคพืช |
| **๔. นักวิจัยและผู้สนใจทั่วไป** | **๕ คน** | นักวิชาการ นิสิต/นักศึกษา หรือผู้ประกอบการเทคโนโลยีชุมชน | ได้ต้นแบบสถาปัตยกรรมเปิด (Open Architecture) ไปขยายผลสู่เชิงพาณิชย์และบริการวิชาการ |

---

### 5. ตัวชี้วัดความสำเร็จของโครงการ (Key Performance Indicators)

#### 5.1 ตัวชี้วัดเชิงปริมาณ (Quantitative KPIs)
* มีครู นักเรียน และเกษตรกรเข้าร่วมการอบรมครบตามเป้าหมายไม่น้อยกว่าร้อยละ ๙๐ ของจำนวนที่กำหนด
* ผู้เข้ารับการอบรมมีเวลาเข้าร่วมกิจกรรมบรรยายและฝึกปฏิบัติการไม่น้อยกว่าร้อยละ ๘๕ ตลอดหลักสูตร
* ครูผู้เข้าร่วมอบรมสามารถจัดทำ **ร่างแผนการจัดการเรียนรู้เชิงรุก (Active Learning Plan)** ด้าน AIoT เกษตรดิจิทัลได้ครบ ๑๐๐%
* สามารถผลิตโครงงานนวัตกรรมต้นแบบระบบดิจิทัลอิเล็กทรอนิกส์และ AI ควบคุมแปลงเกษตรได้ไม่น้อยกว่า ๑๐ โครงงาน (๑ ชิ้นงานต่อกลุ่มย่อย ๔–๕ คน)
* ผลคะแนนการทดสอบความรู้และทักษะหลังการอบรม (Post-test) สูงกว่าก่อนการอบรม (Pre-test) อย่างมีนัยสำคัญทางสถิติที่ระดับ ๐.๐๕ โดยมีค่าดัชนีประสิทธิผล (Effectiveness Index: E.I. หรือ Normalized Gain) ไม่น้อยกว่า ๐.๕๐ (ร้อยละ ๕๐)

#### 5.2 ตัวชี้วัดเชิงคุณภาพ (Qualitative KPIs)
* ผู้เข้ารับการอบรมมีความพึงพอใจต่อภาพรวมของโครงการในระดับ "มากที่สุด" หรือ "มาก" (คะแนนเฉลี่ยไม่น้อยกว่า ๔.๒๕ จาก ๕.๐๐)
* ครูผู้สอนมีความมั่นใจและมีความพร้อมในการนำความรู้ดิจิทัลอิเล็กทรอนิกส์และ Edge AI ไปถ่ายทอดในชั้นเรียน
* นักเรียนสามารถอธิบายตรรกะการทำงานของโครงงานและการตัดสินใจของโมเดล AI (xAI) ได้อย่างเป็นระบบ
* เกษตรกรสามารถนำองค์ความรู้ไปประยุกต์ใช้เพื่อการลดต้นทุนน้ำและปุ๋ยในแปลงเกษตรของตนเองได้อย่างเป็นรูปธรรม

---

### 6. โครงสร้างเนื้อหาหลักสูตรการฝึกอบรม (Curriculum Modules)

หลักสูตรถูกออกแบบให้มีการจัดกระบวนการเรียนรู้แบบบูรณาการ **๕ หน่วยการเรียนรู้หลัก (5 Core Learning Modules)** มุ่งเน้นการลงมือปฏิบัติการจริงร้อยละ ๗๐ (Hands-on Lab) และทฤษฎีร้อยละ ๓๐

```
┌─────────────────────────────────────────────────────────────────────────────────────┐
│                    LEQs-AgriEnvi-xAI Curriculum Architecture                         │
│       (บูรณาการ Digital Electronics • Smart IoT • Edge AI • Environmental SDGs)     │
├─────────────────────────────────────────────────────────────────────────────────────┤
│ Module 1: ดิจิทัลอิเล็กทรอนิกส์และสถาปัตยกรรมฮาร์ดแวร์ไอโอทีเพื่อสิ่งแวดล้อม         │
│   • สถาปัตยกรรมไมโครคอนโทรลเลอร์ ESP32-S3 (Xtensa Dual-Core, 8MB PSRAM, Wi-Fi/BLE)   │
│   • วงจรบัสสื่อสารมาตรฐานอุตสาหกรรม: RS485 Modbus RTU, I2C, SPI และการจัดสัญญาณ     │
│   • วงจรขับโหลดกำลังสูงแบบแยกสัญญาณแสง (Optocoupler Isolated Relay & Solenoid Valve) │
│   • ฟิสิกส์การตรวจวัดสิ่งแวดล้อม: ดิน ๒ ระดับ (0-10 cm, 10-30 cm), NPK, pH, EC, SHT45  │
├─────────────────────────────────────────────────────────────────────────────────────┤
│ Module 2: คอมพิวเตอร์วิทัศน์สำหรับเกษตรดิจิทัลและการเรียนรู้เชิงลึก (Computer Vision) │
│   • การประมวลผลสัญญาณภาพดิจิทัล (Digital Image Processing, Color Spaces, Contours)  │
│   • เทคนิคการถ่ายภาพและสร้างชุดข้อมูลภาพ (Plant Disease & Soil Health Dataset)        │
│   • สถาปัตยกรรมโครงข่ายประสาทเทียมแบบคอนโวลูชัน (CNN) เพื่อการจำแนกโรคและสรีรวิทยาพืช │
├─────────────────────────────────────────────────────────────────────────────────────┤
│ Module 3: ปัญญาประดิษฐ์ระดับอุปกรณ์ฝังตัว (Edge AI & TinyML Zero-Cloud)              │
│   • การบีบอัดและลดทอนโมเดล (Model Quantization & Optimization) ด้วย TensorFlow Lite  │
│   • การแปลงโมเดลเป็น C++ Array และติดตั้งลงหน่วยความจำ Flash ของชิป ESP32-S3        │
│   • ปฏิบัติการประมวลผลอัจฉริยะแบบเรียลไทม์บนตัวบอร์ดโดยไม่ต้องพึ่งพาคลาวด์ (Offline AI) │
├─────────────────────────────────────────────────────────────────────────────────────┤
│ Module 4: ปัญญาประดิษฐ์อธิบายได้ (xAI) และระบบควบคุมอัตโนมัติอัจฉริยะ                │
│   • Explainable AI Reasoner: การแสดงผลเหตุผลการตัดสินใจทางฟิสิกส์บนจอสัมผัส ATD3.5-S3 │
│   • อัลกอริทึมควบคุมวาล์วน้ำสองระดับความลึก และการแจ้งเตือนสภาวะปากใบปิดด้วยค่า VPD   │
│   • การเชื่อมต่อแดชบอร์ด HandySense Platform, Web Telemetry และ Wi-Fi Captive Portal│
├─────────────────────────────────────────────────────────────────────────────────────┤
│ Module 5: สมรรถนะครูสู่การสร้างนวัตกรรม Capstone Hackathon และการนำเสนอผลงาน          │
│   • คลินิกออกแบบแผนการจัดการเรียนรู้ Active Learning & STEM สำหรับครูแกนนำ          │
│   • ปฏิบัติการแก้ปัญหาเชิงพื้นที่จริง ๖ แทร็ก (6 Capstone Tracks) สำหรับนักเรียน/เกษตรกร│
│   • นำเสนอผลงาน (Pitching Showcase), ประเมินรูบริกส์, มอบรางวัลและวุฒิบัตรสมรรถนะ     │
└─────────────────────────────────────────────────────────────────────────────────────┘
```

---

### 7. กำหนดการอบรมเชิงปฏิบัติการ (ระยะเวลา 2 วัน 1 คืน หรือ 16 ชั่วโมง)

#### วันที่ 1 ปูพื้นฐานฟิสิกส์เซนเซอร์ คอมพิวเตอร์วิทัศน์ และระบบสมองกลฝังตัว
* **08.30 – 09.00 น.** ลงทะเบียนผู้เข้ารับการอบรม และทำแบบทดสอบก่อนเรียน (Pre-test)
* **09.00 – 09.30 น.** พิธีเปิดโครงการ แนะนำภาพรวมโครงการ **LEQs-AgriEnvi-xAI** และการสร้างแรงบันดาลใจด้าน AIoT เกษตรดิจิทัล
* **09.30 – 10.45 น.** **Module 1 (Part A)** สถาปัตยกรรมฮาร์ดแวร์ ATD3.5-S3 (ESP32-S3 Dual-Core, หน้าจอ Capacitive Touch) และฟิสิกส์ของการตรวจวัดสิ่งแวดล้อม (VPD, PAR, Soil Physics)
* **10.45 – 11.00 น.** พักรับประทานอาหารว่าง
* **11.00 – 12.00 น.** **Module 1 (Part B - Hands-on)** การต่อวงจรเซนเซอร์อุตสาหกรรม RS485 Modbus RTU (Soil 7-in-1), I2C (SHT45, BH1750) และ Soil Stick พร้อมการเขียนโค้ดอ่านค่าบนบอร์ดจริง
* **12.00 – 13.00 น.** พักรับประทานอาหารกลางวัน
* **13.00 – 14.45 น.** **Module 2 (Hands-on)** คอมพิวเตอร์วิทัศน์สำหรับเกษตรดิจิทัล (Computer Vision): การเชื่อมต่อกล้อง การประมวลผลภาพเพื่อตรวจประเมินความชื้นหน้าดินและตรวจจับรอยโรคบนใบพืช
* **14.45 – 15.00 น.** พักรับประทานอาหารว่าง
* **15.00 – 16.30 น.** **Module 3 (Part A)** พื้นฐาน Deep Learning และการฝึกสอนโมเดลโครงข่ายประสาทเทียมด้วยข้อมูลเซนเซอร์สิ่งแวดล้อมและการวิเคราะห์ภาพ
* **16.30 – 17.30 น.** สรุปบทเรียนประจำวัน มอบหมายโจทย์แนวคิดโครงงาน และแบ่งกลุ่มปฏิบัติการย่อย

---

#### วันที่ 2 Edge AI บนชิปจริง xAI อธิบายเหตุผล และการประชันโครงงานนวัตกรรม
* **08.30 – 10.30 น.** **Module 3 (Part B - Hands-on)** การแปลงโมเดล Deep Learning สู่ Edge TinyML (C++ Array) และการแฟลชลงบนชิป ESP32-S3 เพื่อรันการทำนายผลแบบเรียลไทม์บนตัวเครื่อง
* **10.30 – 10.45 น.** พักรับประทานอาหารว่าง
* **10.45 – 12.00 น.** **Module 4 (Hands-on)** ปัญญาประดิษฐ์ที่อธิบายได้ (Explainable AI): การแสดงผลเหตุผลการตัดสินใจบนหน้าจอทัชสกรีน การควบคุมรีเลย์รดน้ำสองระดับความลึก และการเชื่อมต่อ Wi-Fi / HandySense Cloud
* **12.00 – 13.00 น.** พักรับประทานอาหารกลางวัน
* **13.00 – 15.00 น.** **Module 5 (Capstone Hackathon)** ปฏิบัติการแก้ปัญหาเชิงพื้นที่: แต่ละกลุ่มนำบอร์ดและเซนเซอร์ไปทดสอบในสภาพดินและสภาพแสงจริง พัฒนาฟังก์ชันเฉพาะกลุ่ม
* **15.00 – 15.15 น.** พักรับประทานอาหารว่าง
* **15.15 – 16.30 น.** การนำเสนอผลงานนวัตกรรม (Project Pitching) พร้อมตอบข้อซักถามจากคณะกรรมการผู้ทรงคุณวุฒิ
* **16.30 – 17.00 น.** ทำแบบทดสอบหลังเรียน (Post-test) พิธีมอบเกียรติบัตร มอบรางวัลโครงงานดีเด่น และพิธีปิดการอบรม

---

### 8. ชุดอุปกรณ์และสื่อการเรียนรู้ประจำกลุ่ม (Hardware & Training Kit)

ผู้เข้ารับการอบรมจะได้รับจัดสรรอุปกรณ์ 1 ชุดต่อกลุ่มย่อย (กลุ่มละ 4–5 คน) ประกอบด้วย
1. **บอร์ดประมวลผลหลัก ATD3.5-S3** ชิป ESP32-S3 Dual-Core Xtensa LX7, 8MB PSRAM, หน้าจอสี IPS Capacitive Touch ขนาด 3.5 นิ้ว (ความละเอียด 480×320 พิกเซล)
2. **โมดูลกล้องวิทัศน์ (Vision Camera Module)** สำหรับปฏิบัติการ Computer Vision
3. **ชุดเซนเซอร์สิ่งแวดล้อมและเกษตรแม่นยำ 4 ชนิด**
   * เซนเซอร์อุณหภูมิและความชื้นสัมพัทธ์ในอากาศความแม่นยำสูง (SHT45) สำหรับคำนวณค่า VPD
   * เซนเซอร์วัดความเข้มแสงดิจิทัล (BH1750) สำหรับคำนวณค่า PAR
   * เซนเซอร์วัดความชื้นและอุณหภูมิผิวดินระดับตื้น (Soil Moisture Stick)
   * โพรบสเตนเลสตรวจวัดดินระดับลึก 7 พารามิเตอร์ (Soil 7-in-1 Modbus RS485) ตรวจวัด Moisture, Temperature, EC, pH, N, P, K
4. **โมดูลควบคุมรีเลย์แยกสัญญาณทางแสง (Optocoupler Isolated Relay)** พร้อมปั๊มน้ำจำลองและโซลินอยด์วาล์ว 12V DC
5. **คู่มือปฏิบัติการฉบับสมบูรณ์ (Laboratory Manual)** และซอร์สโค้ดตัวอย่างบน GitHub

---

### 9. ประมาณการงบประมาณดำเนินโครงการ (Budget Estimation)

*(คำนวณสำหรับผู้เข้ารับการอบรม 50 คน และวิทยากร/ผู้ช่วยวิทยากร 10 คน รวม 60 คน)*

| ลำดับ | รายการค่าใช้จ่าย | จำนวน | ราคาต่อหน่วย | รวมเป็นเงิน (บาท) |
| :---: | :--- | :---: | :---: | :---: |
| 1 | ค่าตอบแทนวิทยากรบรรยายและปฏิบัติการ (16 ชม.) | 2 ท่าน | 1,000 บาท/ชม./ท่าน | 32,000 |
| 2 | ค่าตอบแทนผู้ช่วยวิทยากรประจำกลุ่มปฏิบัติการ (16 ชม.) | 4 ท่าน | 300 บาท/ชม./ท่าน | 19,200 |
| 3 | ค่าอาหารกลางวันสำหรับผู้เข้ารับการอบรมและทีมงาน (2 วัน) | 60 คน | 120 บาท/คน/วัน | 14,400 |
| 4 | ค่าอาหารว่างและเครื่องดื่ม (2 วัน วันละ 2 มื้อ) | 60 คน | 70 บาท/คน/วัน | 8,400 |
| 5 | ค่าวัสดุฝึกอบรม ชิ้นส่วนอิเล็กทรอนิกส์ และวัสดุสิ้นเปลือง | 12 ชุด | 2,500 บาท/ชุด | 30,000 |
| 6 | ค่าเอกสารคู่มือปฏิบัติการ ป้ายชื่อ และแฟ้มเอกสาร | 50 ชุด | 150 บาท/ชุด | 7,500 |
| 7 | ค่าเกียรติบัตรและโล่รางวัลโครงงานดีเด่น | 1 ชุด | 3,500 บาท | 3,500 |
| 8 | ค่าสถานที่และระบบไฟฟ้าสัญญาณอินเทอร์เน็ต | 2 วัน | 2,500 บาท/วัน | 5,000 |
| **รวมทั้งสิ้น** | **(หนึ่งแสนสองหมื่นบาทถ้วน)** | | | **120,000** |

*(หมายเหตุ รายการงบประมาณสามารถถัวเฉลี่ยได้ตามระเบียบการเงินของหน่วยงานต้นสังกัด)*

---

### 10. ประโยชน์ที่คาดว่าจะได้รับ (Expected Benefits and Impact)

1. **สำหรับนักเรียนมัธยมศึกษาตอนปลาย** ได้รับองค์ความรู้และทักษะด้านปัญญาประดิษฐ์ฝังตัว (Edge AI) วิทยาการคอมพิวเตอร์ และวิทยาศาสตร์เกษตรดิจิทัล ได้ชิ้นงานโครงงานที่มีหลักฐานเชิงประจักษ์ มีโค้ดบนคลังข้อมูล GitHub สาธารณะ และสามารถนำไปบรรจุลงในแฟ้มสะสมผลงาน (TCAS Portfolio) รอบที่ 1 หรือส่งเข้าประกวดแข่งขันในระดับชาติ
2. **สำหรับบุคลากรทางการศึกษา** ได้รับแนวทางการจัดการเรียนรู้แบบบูรณาการสะเต็มศึกษา (STEM Education) และการเรียนรู้เชิงรุก (Active Learning) ที่สามารถนำชุดทดลองและสื่อจำลองไปใช้สอนจริงในวิชาโครงงานวิทยาศาสตร์ วิทยาการคำนวณ หรือการงานอาชีพ ตลอดจนใช้เป็นผลงานการพัฒนานวัตกรรมการสอน
3. **สำหรับเกษตรกร** ได้รับทักษะการใช้เทคโนโลยีเกษตรแม่นยำที่จับต้องได้จริง สามารถติดตั้งและดูแลรักษาระบบ IoT ตรวจวัดคุณภาพดินและสภาพแวดล้อมได้ด้วยตนเอง เข้าใจความสำคัญของค่า VPD และการควบคุมน้ำ 2 ระดับความลึก ซึ่งช่วยลดต้นทุนค่าน้ำ ค่าปุ๋ย และลดความเสียหายจากโรคพืชได้อย่างยั่งยืน
4. **สำหรับเกษตรกรและผู้สนใจทั่วไป** เกิดชุมชนผู้ใช้งานและนักพัฒนาเทคโนโลยีเกษตรแบบเปิด (Open-Source AgriTech Community) ที่สามารถแลกเปลี่ยนข้อมูลและร่วมกันพัฒนาต่อยอดสู่ระดับวิสาหกิจชุมชน

---

### 11. แนวทางการประเมินผลสัมฤทธิ์และเงื่อนไขการเข้ารับรองสมรรถนะ (Outcome-Based Assessment and Certification Criteria)

เพื่อให้การดำเนินโครงการสามารถประเมินผลลัพธ์เชิงประจักษ์ (Empirical Evidence) ได้อย่างเป็นรูปธรรม ครอบคลุมทั้งผลผลิต (Output) ผลลัพธ์ (Outcome) และผลกระทบ (Impact) โครงการได้กำหนดเงื่อนไขและข้อตกลงในการเข้าร่วมอบรม 5 ประการ พร้อมเกณฑ์ประเมินสมรรถนะตามมาตรฐานมหาวิทยาลัยราชภัฏรำไพพรรณี ดังต่อไปนี้

#### 11.1 เงื่อนไขและข้อตกลงการเข้าร่วมโครงการ 5 ประการ
1. **การบันทึกเวลาและการมีส่วนร่วมตลอดหลักสูตร (Attendance $\ge$ 80%)**  
   ผู้เข้ารับการอบรมต้องมีเวลาเข้าร่วมกิจกรรมบรรยายและฝึกปฏิบัติการไม่น้อยกว่าร้อยละ 80 ของเวลาทั้งหมดตลอดหลักสูตร โดยมีการสแกน QR Code เช็คชื่อแบบเรียลไทม์ทั้งช่วงเช้าและช่วงบ่ายของแต่ละวัน
2. **การวัดผลสัมฤทธิ์ทางการเรียนรู้ก่อนและหลังการอบรม (Pre/Post Test Assessment)**  
   ผู้เข้ารับการอบรมต้องทำแบบทดสอบวัดความรู้พื้นฐาน (Pre-test) และแบบทดสอบวัดผลสัมฤทธิ์ (Post-test) โดยต้องผ่านเกณฑ์คะแนนหลังเรียนไม่ต่ำกว่าร้อยละ 70 หรือมีค่าอัตราการเพิ่มของคะแนนการเรียนรู้เฉลี่ย (Normalized Gain Score หรือ $\langle g \rangle$) ไม่น้อยกว่าร้อยละ 50 ตามแบบจำลองของ Hake
   $$\langle g \rangle = \frac{\text{Post-score} - \text{Pre-score}}{\text{Max-score} - \text{Pre-score}} \times 100\%$$
3. **การฝึกปฏิบัติการฮาร์ดแวร์และการพัฒนาโครงงานต้นแบบ (Hands-on Lab and Capstone Project)**  
   ผู้เข้ารับการอบรมต้องประกอบวงจร เชื่อมต่อเซนเซอร์ดิน น้ำ บรรยากาศ และส่งข้อมูลขึ้นระบบคลาวด์ได้สำเร็จ พร้อมพัฒนาโครงงานนวัตกรรมต้นแบบร่วมกับทีมวิทยากรอย่างน้อย 1 แทร็ก และผ่านการประเมินชิ้นงานตามเกณฑ์รูบริกไม่น้อยกว่าร้อยละ 75
4. **การเข้าร่วมเครือข่ายสื่อสารและการติดตามผลในพื้นที่จริง (LINE Group and Field Deployment)**  
   ผู้สมัครทุกคนต้องเข้าร่วมกลุ่มไลน์ทางการของโครงการ LEQs-xAI Workshop และยินยอมส่งภาพถ่ายหรือรายงานสรุปผลการนำความรู้ ระบบเซนเซอร์ หรือแอปพลิเคชันไปทดลองใช้งานในแปลงเกษตร โรงเรียน หรือหน่วยงานของตนเองภายในระยะเวลา 30 ถึง 60 วันหลังเสร็จสิ้นการอบรม
5. **การประเมินความพึงพอใจและสิทธิ์ในการรับวุฒิบัตรรับรองสมรรถนะ (Certification and Data Consent)**  
   ผู้ที่ผ่านเกณฑ์ครบถ้วนตามข้อ 1 ถึง 4 และส่งแบบประเมินความพึงพอใจ จะได้รับ **วุฒิบัตรรับรองสมรรถนะ AIoT (Certificate of Competence)** ออกโดยคณะวิทยาศาสตร์และเทคโนโลยี มหาวิทยาลัยราชภัฏรำไพพรรณี พร้อมยินยอมให้นำผลการประเมินเชิงสถิติไปใช้ในรายงานวิจัยและการพัฒนานวัตกรรมอย่างโปร่งใส

#### 11.2 ตารางเกณฑ์การประเมินผลรูบริกเพื่อการรับวุฒิบัตร (Rubric Assessment Matrix)

| องค์ประกอบการประเมิน | ค่าน้ำหนัก | เกณฑ์ผ่านขั้นต่ำ | เครื่องมือและหลักฐานเชิงประจักษ์ |
| :--- | :---: | :---: | :--- |
| **1. เวลาเข้าร่วมกิจกรรม (Attendance)** | 20% | $\ge 80\%$ | สถิติการสแกน QR Code เช็คชื่อในระบบฐานข้อมูล LEQs |
| **2. ความก้าวหน้าทางวิชาการ (Pre/Post Test)** | 20% | $\ge 70\%$ หรือ $\langle g \rangle \ge 50\%$ | ระบบสอบออนไลน์และคะแนนเกนสัมพัทธ์ทางสถิติ |
| **3. ทักษะปฏิบัติการฮาร์ดแวร์และแอปพลิเคชัน** | 30% | $\ge 75\%$ | ผลการอ่านค่าเซนเซอร์และการแสดงผลบนแดชบอร์ดจริง |
| **4. ผลงานโครงงานต้นแบบ (Capstone Project)** | 20% | $\ge 70\%$ | การสาธิตการทำงานจริง โค้ดบน GitHub และโปสเตอร์ดิจิทัล |
| **5. การประเมินผลและความร่วมมือติดตามผล** | 10% | ส่งแบบสำรวจครบ 100% | แบบประเมินความพึงพอใจและรายงานผลการติดตั้งในพื้นที่ |
| **รวมคะแนนทั้งสิ้น** | **100%** | **รวม $\ge 75\%$** | **รับวุฒิบัตรรับรองสมรรถนะ (Certificate of Competence)** |

#### 11.3 การติดตามผลระยะยาว 30 ถึง 60 วัน (Long-Term Longitudinal Follow-up)
* การจัดตั้งศูนย์สนับสนุนเทคนิคผ่านกลุ่มไลน์ทางการ เพื่อตอบข้อซักถามในการแก้ปัญหาฮาร์ดแวร์และเฟิร์มแวร์
* การเก็บรวบรวมข้อมูลเชิงปริมาณด้านการประหยัดทรัพยากรน้ำ ปุ๋ย และการลดอัตราความเสียหายจากโรคพืชในแปลงเกษตรของเกษตรกรเครือข่าย
* การสนับสนุนนักเรียนในการจัดทำแฟ้มสะสมผลงาน (TCAS Portfolio) และการส่งผลงานเข้าประกวดโครงงานนวัตกรรมระดับภูมิภาคและระดับชาติต่อไป
