TsanaPhysics/JC-AGRITecH-AI/leqs-workshop/LEQs_xAI_Project_Approval_RBRU.md

# โครงการงบประมาณรายจ่ายประจำปีงบประมาณ พ.ศ. 2569
## มหาวิทยาลัยราชภัฏรำไพพรรณี

---

| ข้อมูลทั่วไป | รายละเอียดโครงการ |
| :--- | :--- |
| **กิจกรรมหลักที่ 1** | สนับสนุนโครงการดำเนินงานตามยุทธศาสตร์มหาวิทยาลัย |
| **หน่วยงาน คณะ/ศูนย์การศึกษา/สถาบัน/สำนัก** | คณะวิทยาศาสตร์และเทคโนโลยี มหาวิทยาลัยราชภัฏรำไพพรรณี |
| **แหล่งที่มาของงบประมาณ** | **งบประมาณเงินรายได้อื่นๆ ประจำปีงบประมาณ พ.ศ. 2569**<br>*(ภายใต้โครงการเพิ่มศักยภาพครูให้มีสมรรถนะของครูยุคใหม่สำหรับการเรียนรู้ในศตวรรษที่ 21)* |
| **แผนงาน** | พื้นฐานด้านการพัฒนาและเสริมสร้างศักยภาพทรัพยากรมนุษย์ |
| **ผลผลิต/โครงการ** | เพิ่มศักยภาพครูและกำลังคนเพื่อรองรับการเรียนรู้ในศตวรรษที่ 21 และการพัฒนาท้องถิ่น |
| **กิจกรรมหลัก** | พัฒนาสมรรถนะครูยุคใหม่ นวัตกรเยาวชน และเทคโนโลยีเกษตรดิจิทัลสู่ชุมชน |
| **ประเภทโครงการ** | โครงการพัฒนาสมรรถนะครูดิจิทัลและสะเต็มศึกษา เพื่อรองรับสังคมศตวรรษที่ 21 |
| **ชื่อโครงการย่อยของหน่วยงาน** | ศูนย์พัฒนานวัตกรรมเกษตรดิจิทัลรำไพพรรณี-ประณีตวิทยาคม<br>(RBRU-Praneet Digital Agri-Innovation Center) |
| **ชื่อกิจกรรม** | **อบรมเชิงปฏิบัติการ ปัญญาประดิษฐ์ฝังตัวเพื่อเกษตรดิจิทัลและสิ่งแวดล้อม (LEQs-xAI)**<br>*(Hands-on Workshop on Embedded AI for Digital Agriculture and Environment)* |
| **วงเงินงบประมาณ** | **76,000 บาท** (เจ็ดหมื่นหกพันบาทถ้วน) |

---

### ความสอดคล้องกับยุทธศาสตร์มหาวิทยาลัย / เป้าประสงค์ / ตัวชี้วัด / กลยุทธ์

| ด้านความสอดคล้อง | รายละเอียด |
| :--- | :--- |
| **นโยบายอธิการบดี** | ด้านเทคโนโลยีสารสนเทศ |
| **นโยบายสภามหาวิทยาลัย** | 3. ด้านสร้างองค์ความรู้ นวัตกรรม การวิจัย และบริการวิชาการ |
| **ยุทธศาสตร์มหาวิทยาลัย** | 2. การพัฒนาท้องถิ่นสู่ความยั่งยืน |
| **เป้าประสงค์** | 1. พัฒนาองค์ความรู้ สร้างนวัตกรรมชุมชนท้องถิ่นนำไปใช้แก้ไขปัญหาชุมชนท้องถิ่น |
| **ตัวชี้วัด** | จำนวนองค์ความรู้หรือนวัตกรรมชุมชนท้องถิ่นที่นำไปใช้แก้ไขปัญหาท้องถิ่นที่ได้รับการเผยแพร่ในระดับชาติ |
| **ตัวชี้วัดรอง** | - |
| **กลยุทธ์** | นำองค์ความรู้ สร้างนวัตกรรม เพื่อชุมชน |

---

### ความสอดคล้องกับยุทธศาสตร์หน่วยงาน / เป้าประสงค์ / ตัวชี้วัด / กลยุทธ์

| ด้านความสอดคล้อง | รายละเอียด |
| :--- | :--- |
| **ยุทธศาสตร์หน่วยงาน** | การพัฒนาท้องถิ่นสู่ความยั่งยืน |
| **เป้าประสงค์** | ขับเคลื่อนงานวิทยาศาสตร์รองรับเป้าหมายการพัฒนาที่ยั่งยืน (SDGs) ได้แก่ สร้างความร่วมมือ การศึกษา การจัดการท้องถิ่น อาหาร ผลไม้เมืองร้อน น้ำและดินชายฝั่ง สิ่งมีชีวิตใต้น้ำ มุ่งเน้นสังคมคาร์บอนต่ำ |
| **ตัวชี้วัด** | จำนวนชุมชนต้นแบบที่ประสบความสำเร็จ (ชุมชนมีการขยายผลและสามารถยืนได้) |
| **ตัวชี้วัดรอง** | - |
| **กลยุทธ์** | SDGs Synergy |

---

### ความสอดคล้องของตัวบ่งชี้การประกันคุณภาพการศึกษา

| ระดับการประกันคุณภาพ | การประกันคุณภาพการศึกษาภายใน | การประกันคุณภาพการศึกษาภายนอก |
| :--- | :--- | :--- |
| **ระดับหลักสูตร** | IQA (คปภ.) และ AUN QA | - |
| **ระดับคณะ** | EdPEx หมวด 3 | - |
| **ระดับมหาวิทยาลัย** | EdPEx หมวด 3 | - |

---

## 1. หลักการและเหตุผล

ในสถานการณ์ปัจจุบัน ภาคการเกษตรของไทยโดยเฉพาะในพื้นที่ภาคตะวันออก ซึ่งเป็นฐานการผลิตผลไม้เมืองร้อนมูลค่าสูง เช่น ทุเรียน มังคุด และลำไย กำลังเผชิญกับวิกฤตการณ์ซ้อนทับระหว่างสภาวะโลกรวน (Climate Change) และพลวัตของโลกดิจิทัลที่เกษตรกรต้องปรับตัวอย่างเร่งด่วน เกษตรกรกำลังตกอยู่ในสถานะเปราะบางจากความเสี่ยงเชิงโครงสร้างที่ไม่สามารถรับมือได้ด้วยภูมิปัญญาดั้งเดิมเพียงลำพัง โดยเฉพาะภัยพิบัติจากสภาพอากาศแปรปรวนสุดขั้ว เช่น ภาวะแล้งจัดที่ยาวนาน หรือฝนตกหนักผิดฤดูกาล ซึ่งส่งผลกระทบโดยตรงทางสรีรวิทยาต่อพืช ทำให้เกิดภาวะเครียด ดอกร่วง ผสมเกสรไม่ติด ไปจนถึงการระบาดรุนแรงของโรครากเน่าและโคนเน่า ส่งผลให้ผลผลิตลดลงหรือเกิดการยืนต้นตาย นอกจากนี้ สภาพอากาศใหม่ยังเป็นตัวเร่งให้เกิดโรคอุบัติใหม่และแมลงศัตรูพืชที่ไม่เคยปรากฏมาก่อน ทำให้ต้นทุนในการจัดการดูแลรักษาพุ่งสูงขึ้นอย่างมีนัยสำคัญ ที่น่ากังวลยิ่งกว่าคือกระบวนการจัดการสวนในปัจจุบันยังคงขาดประสิทธิภาพ โดยเป็นการจัดการในลักษณะการวัดดวงที่อาศัยเพียงประสบการณ์และความรู้สึก ซึ่งมีความเสี่ยงสูงมหาศาลภายใต้สภาพอากาศที่คาดเดาไม่ได้ การขาดแคลนเครื่องมือและข้อมูลที่แม่นยำในการตัดสินใจเรื่องการให้น้ำและการใส่ปุ๋ย นำไปสู่การใช้ทรัพยากรที่เกินความจำเป็นและสิ้นเปลือง ทั้งปุ๋ยเคมีและสารกำจัดศัตรูพืช ซึ่งขัดแย้งกับหลักการเศรษฐกิจสีเขียวและ BCG Model อย่างสิ้นเชิง หากไม่มีการแทรกแซงด้วยเทคโนโลยี เกษตรกรไทยจะสูญเสียขีดความสามารถในการแข่งขันและไม่สามารถรักษาเสถียรภาพความมั่นคงทางรายได้ได้อย่างยั่งยืน

แม้ว่าเทคโนโลยีดิจิทัลจะเป็นโซลูชันสำคัญในการแก้ไขปัญหาข้างต้น แต่ปัจจุบันยังคงปรากฏช่องว่างทางทักษะดิจิทัลขนาดใหญ่ในระดับฐานราก ทั้งในกลุ่มเกษตรกรและเยาวชนที่ยังมองว่าเทคโนโลยีขั้นสูงอย่างปัญญาประดิษฐ์ (Artificial Intelligence หรือ AI) และอินเทอร์เน็ตของสรรพสิ่ง (Internet of Things หรือ IoT) เป็นเรื่องไกลตัว ด้วยเหตุนี้ โครงการศูนย์พัฒนานวัตกรรมเกษตรดิจิทัลรำไพพรรณี-ประณีตวิทยาคม (RBRU-Praneet Digital Agri-Innovation Center) จึงถูกริเริ่มขึ้นเพื่อเป็นกลไกเชิงกลยุทธ์ในการปิดช่องว่างดังกล่าว โดยอาศัยความร่วมมือระหว่างมหาวิทยาลัยราชภัฏรำไพพรรณีและโรงเรียนประณีตวิทยาคม ในการถ่ายทอดองค์ความรู้จากงานวิจัยสู่การปฏิบัติจริงในพื้นที่

โครงการมุ่งเน้นการบูรณาการองค์ความรู้ 6 ด้าน ภายใต้กรอบแนวคิด **LEQs-xAI** ได้แก่
1. **Digital Agriculture** การยกระดับการจัดการสวนผลไม้ด้วยข้อมูลดิจิทัล
2. **Deep Learning** การสร้างและฝึกฝนโมเดลโครงข่ายประสาทเทียมเพื่อการพยากรณ์
3. **Edge AI** การประมวลผลโมเดล AI บนอุปกรณ์สมองกลฝังตัวระดับปลายทาง (เช่น ESP32-S3) โดยไม่ต้องพึ่งพาคลาวด์
4. **Computer Vision** คอมพิวเตอร์วิทัศน์เพื่อวิเคราะห์สุขภาพใบพืชและจำแนกโรคพืช
5. **IoT & Sensors** การตรวจวัดสภาพแวดล้อมจริง ทั้งอุณหภูมิ ความชื้น แสง ค่า pH และความชื้นดินสองระดับ
6. **Environmental AI** การประยุกต์ใช้ AI ในการเฝ้าระวังสภาพแวดล้อมและการเปลี่ยนแปลงสภาพภูมิอากาศ

กระบวนการนี้มุ่งสร้างนวัตกรเกษตรรุ่นใหม่ (Young Agri-Innovators) ครูแกนนำ และเกษตรกรต้นแบบ ที่สามารถใช้ข้อมูลและ AI เป็นเครื่องมือตัดสินใจแทนความรู้สึก เปลี่ยนวิถีการทำเกษตรให้มีประสิทธิภาพ ลดต้นทุนการผลิต ยกระดับคุณภาพชีวิตของชุมชนให้สอดรับกับเป้าหมายการพัฒนาที่ยั่งยืน (SDGs) และสร้างเศรษฐกิจสีเขียว (Green Economy) ในระยะยาว

---

## 2. วัตถุประสงค์

1. เพื่อสร้างนวัตกรเกษตรรุ่นใหม่ด้วยการถ่ายทอดทักษะดิจิทัลขั้นสูง ได้แก่ การเขียนโปรแกรม Python/C++, เทคโนโลยี AI Computer Vision, Deep Learning, Edge AI และ IoT ให้แก่เยาวชน ครู และเกษตรกร เพื่อปิดช่องว่างทางเทคโนโลยีและยกระดับสมรรถนะการศึกษาและการเรียนรู้ตลอดชีวิต **(สอดคล้องกับ SDG 4 การศึกษาที่มีคุณภาพ เป้าประสงค์ 4.4)**
2. เพื่อพัฒนานวัตกรรมต้นแบบเกษตรอัจฉริยะและการตรวจวัดธาตุอาหารดิน NPK/pH/ความชื้น โดยสร้างและพัฒนาต้นแบบนวัตกรรมที่ใช้งานได้จริง เพื่อยกระดับประสิทธิภาพการผลิตอาหารและส่งเสริมเกษตรกรรมยั่งยืน **(สอดคล้องกับ SDG 2 ขจัดความหิวโหย เกษตรยั่งยืน เป้าประสงค์ 2.4)**
3. เพื่อพัฒนาระบบสมองกลฝังตัวและเทคโนโลยีโอเพนซอร์ส (Open-Source AgriTech) สำหรับการบริหารจัดการทรัพยากรน้ำและปัจจัยการผลิตทางการเกษตรอย่างแม่นยำ ช่วยลดการสูญเสียน้ำ ลดการใช้สารเคมีและปุ๋ยเคมีส่วนเกิน และปกป้องระบบนิเวศหน้าดิน **(สอดคล้องกับ SDG 9 โครงสร้างพื้นฐานและนวัตกรรม เป้าประสงค์ 9.5, SDG 12 การผลิตและบริโภคที่ยั่งยืน เป้าประสงค์ 12.2 และ SDG 15 การใช้ประโยชน์ระบบนิเวศบนบก เป้าประสงค์ 15.3)**
4. เพื่อเสริมสร้างขีดความสามารถของชุมชนในการปรับตัวและเฝ้าระวังสภาพภูมิอากาศวิกฤต (Microclimate Adaptation & Extreme Weather Warning) ผ่านระบบเซนเซอร์วัดค่า VPD และดัชนีแสงแดด ช่วยเตือนภัยโรคพืชและลดความสูญเสียจากสภาวะอากาศแปรปรวน **(สอดคล้องกับ SDG 13 รับมือการเปลี่ยนแปลงสภาพภูมิอากาศ เป้าประสงค์ 13.1 และ 13.3)**
5. เพื่อบูรณาการหลักสูตรท้องถิ่นสู่การเกษตรแม่นยำและสร้างความร่วมมือเชิงพื้นที่อย่างเข้มแข็งระหว่างมหาวิทยาลัย สถานศึกษา ชุมชนเกษตรกร และภาคีเครือข่าย เพื่อขับเคลื่อนเศรษฐกิจสีเขียว (Green Economy) อย่างยั่งยืน **(สอดคล้องกับ SDG 17 หุ้นส่วนความร่วมมือเพื่อการพัฒนา เป้าประสงค์ 17.17)**

---

## 3. ผลผลิต / ผลลัพธ์ / ผลกระทบ

### 3.1 ผลผลิต (Outputs)
1. **องค์ความรู้และระบบต้นแบบในการวิเคราะห์ข้อมูลสภาพอากาศด้วย Python** ได้ชุดสคริปต์โค้ดที่สามารถนำไปใช้กับชุดข้อมูลสภาพอากาศชุดใหม่ได้ทันที พร้อมคู่มือการใช้งานและกราฟวิเคราะห์ความเสี่ยงด้านภูมิอากาศ (VPD และสภาพอากาศแปรปรวน)
2. **องค์ความรู้และระบบต้นแบบโมเดลปัญญาประดิษฐ์สำหรับจำแนกโรคพืชและสุขภาพดิน** ผ่านการฝึกสอนด้วย Deep Learning (CNN) และแปลงเป็น Edge TinyML ที่สามารถนำไปติดตั้ง (Deploy) ในบอร์ดไมโครคอนโทรลเลอร์หรือแอปพลิเคชันเพื่อใช้งานจริงในแปลงเกษตรแบบเรียลไทม์
3. **ระบบต้นแบบชุดอุปกรณ์เซนเซอร์ IoT** ประกอบด้วยบอร์ดควบคุมหน้าจอสัมผัส (ATD3.5-S3) และชุดเซนเซอร์สภาพแวดล้อม (SHT45, BH1750, Soil Stick, Soil 7-in-1 Modbus RS485) พร้อมโค้ดควบคุมการทำงาน ที่สามารถติดตั้งเก็บข้อมูลในแปลงจริงได้ทันที
4. **ต้นแบบนวัตกรรมการทำเกษตรแม่นยำด้วย AI และ IoT** ผ่านผลงานโครงงานของนักเรียนและชุมชน (Mini Projects) อย่างน้อย 4 โครงงาน เช่น "ระบบวินิจฉัยโรคใบทุเรียนด้วย Edge Vision", "ระบบแจ้งเตือนการให้น้ำอัตโนมัติตามค่า VPD และความชื้นดินสองระดับ"

### 3.2 ผลลัพธ์ (Outcomes)
1. **ยกระดับทักษะเยาวชนและครู** นักเรียนและบุคลากรทางการศึกษาที่เข้าร่วมโครงการมีทักษะด้านเทคโนโลยีดิจิทัลสูงขึ้นอย่างมีนัยสำคัญ ทั้งการเขียนโปรแกรม การพัฒนาโมเดล AI และการสร้างระบบ IoT ซึ่งเป็นทักษะจำเป็นสำหรับศตวรรษที่ 21
2. **สร้างระบบนิเวศนวัตกรรมการศึกษา** เกิดการนำเทคโนโลยีและองค์ความรู้ใหม่ (ชุดข้อมูล, โมเดล AI, ชุดบอร์ดทดลอง) มาใช้เป็นสื่อการสอนในโรงเรียนประณีตวิทยาคม ทำให้หลักสูตร PBL มีความทันสมัยและยั่งยืน พร้อมเกิดความร่วมมือเข้มแข็งระหว่างมหาวิทยาลัย โรงเรียน และชุมชน
3. **จุดประกายการยอมรับเทคโนโลยีในชุมชน** เกษตรกรในพื้นที่ได้เห็นประโยชน์ที่จับต้องได้จริง ช่วยเปิดใจและสร้างการยอมรับในการนำเทคโนโลยีไปทดลองใช้เพื่อเพิ่มความแม่นยำในการผลิต ลดต้นทุน และยกระดับมาตรฐานผลผลิต

### 3.3 ผลกระทบ (Impacts)
1. **ด้านเศรษฐกิจและคุณภาพชีวิต** ชุมชนเกษตรกรมีความเข้มแข็งทางเศรษฐกิจ สามารถพึ่งพาตนเองได้มากขึ้นจากการทำเกษตรแม่นยำที่ช่วยลดต้นทุนค่าน้ำ ปุ๋ย สารเคมี และเพิ่มผลผลิต ส่งผลให้มีคุณภาพชีวิตที่ดีขึ้น
2. **ด้านสิ่งแวดล้อม** ระบบนิเวศทางการเกษตรได้รับการฟื้นฟูอย่างยั่งยืนจากการลดใช้สารเคมีและจัดการทรัพยากรน้ำอย่างรู้คุณค่า สอดคล้องกับหลักการ Green Economy และเป้าหมายสังคมคาร์บอนต่ำ
3. **ด้านสังคมและทุนมนุษย์** ท้องถิ่นมีกำลังคนรุ่นใหม่ที่มีทักษะสูงด้านเทคโนโลยีดิจิทัลเกษตร (AgriTech) ที่พร้อมกลับมาพัฒนาบ้านเกิด เกิดระบบเศรษฐกิจฐานนวัตกรรมที่ช่วยยกระดับขีดความสามารถการแข่งขันของภูมิภาค

---

## 4. เป้าหมาย (ขอบเขตการจัดโครงการ)

| กิจกรรม | ขอบเขตการจัดโครงการ |
| :--- | :--- |
| **สถานที่จัดกิจกรรม** | โรงเรียนประณีตวิทยาคม อำเภอเขาสมิง จังหวัดตราด |
| **กลุ่มเป้าหมาย** | นักเรียนระดับมัธยมศึกษาตอนปลาย ครูและบุคลากรทางการศึกษา เกษตรกร และผู้สนใจทั่วไป รวม 50 คน |
| **ระยะเวลาดำเนินการ** | วันที่ 11 – 13 มีนาคม พ.ศ. 2569 (รวม 3 วัน หรือ 6 วันทำการอบรมและติดตามผล) |

---

## 5. ตัวชี้วัดและค่าเป้าหมาย

| ประเภทตัวชี้วัด | ตัวชี้วัด | หน่วยนับ | ค่าเป้าหมาย |
| :---: | :--- | :---: | :---: |
| **เชิงคุณภาพ** | 1. ความพึงพอใจต่อภาพรวมของกิจกรรมของผู้เข้าร่วมโครงการ | ร้อยละ | $\ge 85$ |
| **เชิงคุณภาพ** | 2. ผู้เข้าร่วมโครงการได้รับความรู้ความเข้าใจเพิ่มขึ้นหลังเข้าร่วมกิจกรรม (ผลคะแนน Post-test สูงกว่า Pre-test) | ร้อยละ | $\ge 80$ |
| **เชิงปริมาณ** | 1. ครู นักเรียน เกษตรกร และบุคลากรเข้าร่วมโครงการ | คน | 40–50 |
| **เชิงปริมาณ** | 2. โครงงาน/นวัตกรรมต้นแบบที่ผู้เข้าร่วมโครงการพัฒนาร่วมกัน | โครงงาน | $\ge 4$ |

---

## 6. การติดตามและประเมินผล

| ลำดับ | วิธีการประเมิน | เครื่องมือที่ใช้ |
| :---: | :--- | :--- |
| 1 | วัดการเปลี่ยนแปลงองค์ความรู้ของผู้เข้าร่วมโครงการก่อนและหลังการอบรม | แบบทดสอบความรู้ (Pre-test / Post-test) |
| 2 | วัดระดับความพึงพอใจของผู้เข้าร่วมโครงการต่อเนื้อหา วิทยากร และการจัดกิจกรรม | แบบสอบถามความพึงพอใจ |
| 3 | ประเมินทักษะการปฏิบัติ การทำงานเป็นทีม และการแก้ปัญหาเฉพาะหน้าในการพัฒนาชิ้นงาน | แบบประเมินการสังเกตการณ์แบบมีส่วนร่วม |
| 4 | พูดคุยกับตัวแทนนักเรียน ครู และเกษตรกร เพื่อรับฟังความคิดเห็นเชิงลึก อุปสรรค และข้อเสนอแนะ | แบบสัมภาษณ์กลุ่มย่อย (Focus Group Interview) |
| 5 | ติดตามและรายงานผลสัมฤทธิ์การดำเนินงานเมื่อสิ้นสุดโครงการ | รายงานสรุปผลโครงการ และภาพถ่ายกิจกรรม |

---

## 7. การวิเคราะห์ปัญหา / อุปสรรค และแนวทางแก้ไข

| ปัญหาและอุปสรรค | แนวทางแก้ไข |
| :--- | :--- |
| 1. ผู้เข้ารับการอบรมมีพื้นฐานทักษะดิจิทัลและการเขียนโปรแกรมที่หลากหลายและแตกต่างกัน | จัดการเรียนรู้แบบแบ่งกลุ่มคละความสามารถ (Team-based Learning) โดยจัดให้นักเรียน ครู และเกษตรกรทำงานร่วมกัน พร้อมมีผู้ช่วยวิทยากรประจำกลุ่มคอยดูแลให้คำแนะนำอย่างใกล้ชิด |
| 2. สภาพสัญญาณอินเทอร์เน็ตในพื้นที่แปลงเกษตรจริงอาจไม่เสถียร | ออกแบบระบบการเรียนรู้ให้เน้นเทคโนโลยี **Edge AI** ที่ประมวลผลบนบอร์ดฝังตัว ESP32-S3 ได้โดยตรงแบบออฟไลน์ (Offline Autonomous Inference) ไม่ต้องพึ่งพาสัญญาณคลาวด์ตลอดเวลา |
| 3. การนำอุปกรณ์ต้นแบบไปใช้งานจริงในสวนอาจเจอปัญหาสภาพแวดล้อม ความชื้น หรือสัตว์กัดแทะ | ถ่ายทอดองค์ความรู้ด้านมาตรฐานการติดตั้งเซนเซอร์อุตสาหกรรม การป้องกันความชื้นด้วยกล่องกันน้ำ IP65/IP68 และการเดินสายสัญญาณ RS485 ที่ปลอดภัย |

---

## 8. งบประมาณโครงการ (รวมทั้งสิ้น 76,000 บาท)

* **รหัสงบประมาณ:** (ตามที่ได้รับจัดสรรจากงบประมาณแผ่นดิน มหาวิทยาลัยราชภัฏรำไพพรรณี)
* **อ้างอิงกรอบงบประมาณ:** โครงการศูนย์พัฒนานวัตกรรมเกษตรดิจิทัลรำไพพรรณี-ประณีตวิทยาคม (RBRU-Praneet Digital Agri-Innovation Center)
* **วงเงินงบประมาณทั้งสิ้น:** **76,000 บาท** (เจ็ดหมื่นหกพันบาทถ้วน)

### รายละเอียดการจำแนกงบประมาณ

#### 1) หมวดค่าตอบแทน: จำนวน 21,600 บาท
* ค่าตอบแทนวิทยากร (2 คน $\times$ 300 บาท $\times$ 6 ชั่วโมง $\times$ 6 วัน) = **21,600 บาท**

#### 2) หมวดค่าใช้สอย: จำนวน 45,000 บาท
* ค่าอาหารกลางวันสำหรับผู้เข้าร่วมกิจกรรมและคณะกรรมการดำเนินงาน  
  (50 คน $\times$ 80 บาท $\times$ 1 มื้อ $\times$ 6 วัน) = **24,000 บาท**
* ค่าอาหารว่างและเครื่องดื่มสำหรับผู้เข้าร่วมกิจกรรมและคณะกรรมการดำเนินงาน  
  (50 คน $\times$ 35 บาท $\times$ 2 มื้อ $\times$ 6 วัน) = **21,000 บาท**

#### 3) หมวดค่าวัสดุ: จำนวน 9,400 บาท
* ค่าวัสดุประกอบการจัดกิจกรรม อุปกรณ์อิเล็กทรอนิกส์ฝึกอบรม เซนเซอร์ และเอกสารคู่มือ = **9,400 บาท**

$$\text{รวมทั้งสิ้น } 21,600 + 45,000 + 9,400 = \mathbf{76,000} \text{ บาท}$$

*(หมายเหตุ: ทุกรายการสามารถถัวเฉลี่ยจ่ายได้ตามระเบียบการเงินของทางราชการ)*

---

## 9. ผู้รับผิดชอบโครงการ

* **ผู้รับผิดชอบโครงการ**  
  **ผู้ช่วยศาสตราจารย์ ดร.ชีวะ ทัศนา**  
  ตำแหน่ง อาจารย์ประจำสาขาวิชาฟิสิกส์ คณะวิทยาศาสตร์และเทคโนโลยี มหาวิทยาลัยราชภัฏรำไพพรรณี
* **วิทยากรและผู้ร่วมดำเนินโครงการ**  
  **ผู้ช่วยศาสตราจารย์อรรถกร คำฉัตร**  
  ตำแหน่ง อาจารย์ คณะวิทยาศาสตร์และเทคโนโลยี มหาวิทยาลัยราชภัฏรำไพพรรณี
* **ผู้เห็นชอบโครงการ**  
  **ผู้ช่วยศาสตราจารย์ ดร.อาภาพร บุญมี**  
  ตำแหน่ง คณบดีคณะวิทยาศาสตร์และเทคโนโลยี มหาวิทยาลัยราชภัฏรำไพพรรณี

---

## 10. หน่วยงานที่เกี่ยวข้อง

1. คณะวิทยาศาสตร์และเทคโนโลยี มหาวิทยาลัยราชภัฏรำไพพรรณี
2. โรงเรียนประณีตวิทยาคม อำเภอเขาสมิง จังหวัดตราด
3. องค์การบริหารส่วนตำบลประณีต และเครือข่ายวิสาหกิจชุมชนเกษตรกรผู้ปลูกทุเรียนและผลไม้เมืองร้อน อำเภอเขาสมิง จังหวัดตราด

---

## 11. กำหนดการอบรมเชิงปฏิบัติการ

### กำหนดการจัดอบรมเชิงปฏิบัติการ LEQs-xAI
#### ปัญญาประดิษฐ์ฝังตัวเพื่อเกษตรดิจิทัลและสิ่งแวดล้อม
**ระหว่างวันที่ 11 – 13 มีนาคม พ.ศ. 2569**  
**ณ ศูนย์พัฒนานวัตกรรมเกษตรดิจิทัลรำไพพรรณี-ประณีตวิทยาคม โรงเรียนประณีตวิทยาคม อำเภอเขาสมิง จังหวัดตราด**

---

#### วันพุธที่ 11 มีนาคม พ.ศ. 2569: การเตรียมการและการสำรวจพื้นที่จริง
* **09.00 – 12.00 น.** คณะวิทยากรและทีมงานเดินทางจาก มรภ.รำไพพรรณี ไปยังโรงเรียนประณีตวิทยาคม อ.เขาสมิง จ.ตราด
* **12.00 – 13.00 น.** พักรับประทานอาหารกลางวัน
* **13.00 – 15.00 น.** สำรวจแปลงเกษตรสาธิต ติดตั้งสถานีตรวจวัดสภาพอากาศ และจัดเตรียมสถานที่ห้องปฏิบัติการคอมพิวเตอร์และชุดบอร์ด IoT
* **15.00 – 16.30 น.** ประชุมร่วมกับคณะครูและตัวแทนเกษตรกรเพื่อซักซ้อมความเข้าใจและจัดแบ่งกลุ่มผู้เรียน
* **16.30 – 17.00 น.** เดินทางเข้าที่พัก

---

#### วันพฤหัสบดีที่ 12 มีนาคม พ.ศ. 2569: ปฏิบัติการ IoT, คอมพิวเตอร์วิทัศน์ และเซนเซอร์สิ่งแวดล้อม
* **08.30 – 08.45 น.** ลงทะเบียนผู้เข้าร่วมอบรม และทำแบบทดสอบก่อนเรียน (Pre-test)
* **08.45 – 09.00 น.** พิธีเปิดโครงการ โดย ผู้อำนวยการโรงเรียนประณีตวิทยาคม
* **09.00 – 09.30 น.** บรรยายพิเศษเรื่อง "การเปลี่ยนแปลงสภาพภูมิอากาศ พลวัตดิจิทัล และความสำคัญของปัญญาประดิษฐ์ฝังตัวเพื่อเกษตรดิจิทัลและสิ่งแวดล้อม (LEQs-xAI)"  
  *โดย ผศ.ดร.ชีวะ ทัศนา และ ผศ.อรรถกร คำฉัตร*
* **09.30 – 10.30 น.** **Module 1 & 2** สถาปัตยกรรม IoT ทางการเกษตร การตรวจวัดข้อมูลสภาพอากาศ อุณหภูมิ ความชื้น แสง (PAR) ดัชนีไอน้ำสัมพันธ์ (VPD) และความชื้นดินสองระดับ  
  *โดย ผศ.ดร.ชีวะ ทัศนา และ ผศ.อรรถกร คำฉัตร*
* **10.30 – 10.45 น.** พักรับประทานอาหารว่าง
* **10.45 – 12.00 น.** **ปฏิบัติการ Smart Farm Sensor Lab** การต่อวงจรเซนเซอร์ RS485 Modbus RTU (Soil 7-in-1), I2C (SHT45, BH1750) เข้ากับบอร์ดควบคุม ATD3.5-S3 (ESP32-S3)  
  *โดย ผศ.ดร.ชีวะ ทัศนา และ ผศ.อรรถกร คำฉัตร*
* **12.00 – 13.00 น.** พักรับประทานอาหารกลางวัน
* **13.00 – 14.30 น.** **Module 3: Computer Vision for Agriculture** หลักการมองเห็นของ AI การจับภาพใบพืชและหน้าดิน การประมวลผลภาพเบื้องต้น (Image Processing)  
  *โดย ผศ.ดร.ชีวะ ทัศนา และ ผศ.อรรถกร คำฉัตร*
* **14.30 – 14.45 น.** พักรับประทานอาหารว่าง
* **14.45 – 16.30 น.** **ปฏิบัติการ Plant Vision Lab** การเก็บรวบรวมชุดข้อมูลภาพถ่ายใบพืชที่เป็นโรคและสมบูรณ์ การติดป้ายกำกับข้อมูล (Image Annotation) และการจำแนกภาพเบื้องต้น  
  *โดย ผศ.ดร.ชีวะ ทัศนา และ ผศ.อรรถกร คำฉัตร*

---

#### วันศุกร์ที่ 13 มีนาคม พ.ศ. 2569: Deep Learning, Edge AI บนชิปจริง และโครงงานนวัตกรรม
* **08.30 – 09.00 น.** ลงทะเบียนและสรุปทบทวนบทเรียนวันที่หนึ่ง
* **09.00 – 10.30 น.** **Module 4 & 5: Deep Learning & Edge AI** โครงข่ายประสาทเทียม (CNN) การฝึกสอนโมเดล (Training) การบีบอัดโมเดลเพื่อนำไปประมวลผลบนชิป ESP32-S3 โดยตรงแบบเรียลไทม์  
  *โดย ผศ.ดร.ชีวะ ทัศนา และ ผศ.อรรถกร คำฉัตร*
* **10.30 – 10.45 น.** พักรับประทานอาหารว่าง
* **10.45 – 12.00 น.** **ปฏิบัติการ Edge AI Deployment** การแปลงโมเดลลงสู่หน่วยความจำของบอร์ด ATD3.5-S3 และการทดสอบความแม่นยำในการจำแนกโรคและตรวจวัดดินแบบออฟไลน์  
  *โดย ผศ.ดร.ชีวะ ทัศนา และ ผศ.อรรถกร คำฉัตร*
* **12.00 – 13.00 น.** พักรับประทานอาหารกลางวัน
* **13.00 – 15.00 น.** **Module 6 & 7: LEQs-xAI Capstone Mini Project** แต่ละกลุ่มย่อยร่วมกันพัฒนาต้นแบบโครงงานแก้ปัญหาจริงในแปลงเกษตรของโรงเรียนและชุมชน  
  *โดย ผศ.ดร.ชีวะ ทัศนา และ ผศ.อรรถกร คำฉัตร*
* **15.00 – 15.15 น.** พักรับประทานอาหารว่าง
* **15.15 – 16.15 น.** การนำเสนอผลงานโครงงานนวัตกรรม (Project Pitching) พร้อมรับฟังข้อเสนอแนะจากวิทยากรและตัวแทนเกษตรกร
* **16.15 – 16.45 น.** ทำแบบทดสอบหลังเรียน (Post-test) มอบวุฒิบัตรแก่ผู้ผ่านการอบรม มอบรางวัลผลงานดีเด่น
* **16.45 – 17.00 น.** สรุปกิจกรรม พิธีปิดโครงการ และเดินทางกลับมหาวิทยาลัยราชภัฏรำไพพรรณี

*(หมายเหตุ: กำหนดการอาจมีการปรับเปลี่ยนตามความเหมาะสมของสภาพแวดล้อมและบริบทพื้นที่)*

---

<br>

ลงชื่อ ............................................................. ผู้รับผิดชอบโครงการ  
(ผู้ช่วยศาสตราจารย์ ดร.ชีวะ ทัศนา)  
อาจารย์ประจำสาขาวิชาฟิสิกส์ คณะวิทยาศาสตร์และเทคโนโลยี  

<br>

ลงชื่อ ............................................................. ผู้เห็นชอบโครงการ  
(ผู้ช่วยศาสตราจารย์ ดร.อาภาพร บุญมี)  
คณบดีคณะวิทยาศาสตร์และเทคโนโลยี มหาวิทยาลัยราชภัฏรำไพพรรณี
