TsanaPhysics/JC-AGRITecH-AI/chewa/DARK_CHAMBER_STRUCTURE_DIAGRAMS.md

# ภาพโครงสร้างและส่วนประกอบของกล่องวัดแบบทึบแสง (Optical Dark Chamber)

**โครงการวิจัย** การพัฒนาชุดวิเคราะห์ปริมาณไนโตรเจนและฟอสฟอรัสในดินแบบพกพาด้วยหลักการสะท้อนแสงร่วมกับปัญญาประดิษฐ์  
**หัวหน้าโครงการ** ผู้ช่วยศาสตราจารย์ ดร.ชีวะ ทัศนา  
**หน่วยงาน** คณะวิทยาศาสตร์และเทคโนโลยี มหาวิทยาลัยราชภัฏรำไพพรรณี  

---

## ภาพรวมโครงสร้างภาพตัดขวางเชิงวิศวกรรม (Engineering Cutaway View)

ภาพตัดขวาง 3 มิติแสดงมิติภายนอกกล่องขนาด **120 × 80 × 65 มิลลิเมตร** ขึ้นรูปด้วยเครื่องพิมพ์สามมิติจากพอลิเมอร์ **Black PETG** น้ำหนักรวมอุปกรณ์และแบตเตอรี่ไม่เกิน 380 กรัม พร้อมแสดงการจัดวางส่วนประกอบสำคัญทั้ง 4 ส่วนตามหลักทัศนศาสตร์ 45°/0° อย่างแม่นยำ

ภาพตัดขวางโครงสร้างกล่องวัดแบบทึบแสง

---

## ภาพการประกอบชิ้นส่วนแบบแยกชิ้น (Exploded View Diagram)

ภาพจำลองมุมมองกระจายชิ้นส่วนตามแกนทัศนศาสตร์แนวดิ่ง (Vertical Optical Axis) แสดงลำดับการติดตั้งส่วนประกอบ ตั้งแต่ถาดใส่ดิน ลิ้นชักดักแสง ตัวกล่อง วงแหวน LED Array 45 องศา ฝาบนท่อโฟกัส 50 มิลลิเมตร ปะเก็นยาง EVA และสมาร์ทโฟน

ภาพการประกอบชิ้นส่วนแบบกระจายตัวของกล่องวัดทึบแสง

---

## รายละเอียดส่วนประกอบสำคัญ 4 ประการตามข้อกำหนดวิจัย

### 1. ผิวเคลือบดูดกลืนแสง (Matt Black Anti-reflective Inner Lining)
ผนังภายในกล่องทั้งหมดได้รับการพ่นเคลือบด้วยสารดูดกลืนแสงสีดำด้านชนิดพิเศษที่มีค่าการสะท้อนแสงผิวน้อยกว่าร้อยละ 1 เพื่อดูดซับลำแสงที่กระเจิงอยู่ภายใน ป้องกันการเกิดแสงสะท้อนหลายชั้น (Internal Stray Light) ที่อาจทำให้สัญญาณสเปกตรัมเพี้ยน

### 2. แผ่นกั้นดักแสง (Optical Light-trap Baffles)
ติดตั้งรอบบริเวณขอบฝาเปิด-ปิดและช่องบรรจุถาดตัวอย่างดิน โดยใช้ระบบเขี้ยวดักแสงซ้อนสองชั้น (Double-lip Labyrinth Seal) เมื่อปิดลิ้นชักเข้าสู่ตำแหน่งตรวจวัด รอยต่อจะประสานขบล็อกกันสนิท แสงจากภายนอกไม่สามารถเล็ดลอดเป็นเส้นตรงหรือสะท้อนเข้ามาได้ ส่งผลให้อัตราการตัดแสงรบกวนภายนอกสูงกว่าร้อยละ 99.94 (สว่างภายนอก 85,000 ลักซ์ แต่ภายในมืดสนิทต่ำกว่า 0.05 ลักซ์)

### 3. ถาดบรรจุตัวอย่างดินมาตรฐาน (Standard Soil Sample Holder)
ทำจากวัสดุอะคริลิกสีดำ มีขนาดเส้นผ่านศูนย์กลาง 35.0 มิลลิเมตร ลึก 8.0 มิลลิเมตร สามารถบรรจุตัวอย่างดินที่ผ่านการร่อนขนาด 2 มิลลิเมตรได้ปริมาตรคงที่ 7.5 ลูกบาศก์เซนติเมตร และจัดวางในตำแหน่งกึ่งกลางระนาบแสงตกกระทบพอดี ผิวหน้าดินปาดเรียบเสมอกับขอบถาด

### 4. แท่นยึดสมาร์ทโฟนและโมดูลตรวจวัดเชิงแสง (Smartphone Mount & 45°/0° Optical Path)
ออกแบบให้สามารถติดตั้งสมาร์ทโฟนหรือโมดูลตรวจวัดออปติคอลได้อย่างมั่นคง โดยมีระยะห่างทางทัศนศาสตร์จากเลนส์ถึงพื้นผิวตัวอย่างดินคงที่ **50.0 มิลลิเมตร** แหล่งกำเนิดแสง Multi-wavelength LED Array ส่องทำมุมตกกระทบ **45 องศา** เพื่อลดการสะท้อนแบบกระจกเงา (Specular Reflection) และเลนส์รับแสงตั้งฉาก **0 องศา** เพื่อรับเฉพาะแสงสะท้อนแบบกระจาย (Diffuse Reflection) อย่างแม่นยำ พร้อมแผ่นปะเก็นยางโฟม EVA สีดำรอบเลนส์ ป้องกันแสงภายนอกรั่วเข้าสู่เลนส์กล้องสมาร์ทโฟน 100%
