TsanaPhysics/JC-AGRITecH-AI/chewa/รายงานวิจัย_4บท_ชีวะ_2569.md

# รายงานความก้าวหน้าโครงการวิจัย (ฉบับสมบูรณ์ 4 บท)

## การพัฒนาชุดวิเคราะห์ปริมาณไนโตรเจนและฟอสฟอรัสในดินแบบพกพาด้วยหลักการสะท้อนแสงร่วมกับปัญญาประดิษฐ์
### (Development of a Portable Soil Nitrogen and Phosphorus Analyzer Using Optical Reflectance and Artificial Intelligence)

---

**สัญญาเลขที่** 2251/2569  
**กองทุนวิจัย มหาวิทยาลัยราชภัฏรำไพพรรณี ประจำปีงบประมาณ พ.ศ. 2569**  

**คณะผู้วิจัย**
* **หัวหน้าโครงการวิจัย** ผู้ช่วยศาสตราจารย์ ดร.ชีวะ ทัศนา (สัดส่วนร้อยละ 80)  
  สาขาวิชาฟิสิกส์ คณะวิทยาศาสตร์และเทคโนโลยี มหาวิทยาลัยราชภัฏรำไพพรรณี  
* **ผู้ร่วมวิจัย** อาจารย์ธนพัฒน์ ถิระวุฒิ (สัดส่วนร้อยละ 20)  
  สาขาวิชาฟิสิกส์ คณะวิทยาศาสตร์และเทคโนโลยี มหาวิทยาลัยราชภัฏรำไพพรรณี  
* **ผู้ร่วมวิจัยในแผนงานวิจัย**  
  * ผู้ช่วยศาสตราจารย์ ดร.จิรภัทร จันทมาลี (สาขาวิชาจุลชีววิทยา)  
  * ผู้ช่วยศาสตราจารย์ ดร.วิกันยา ประทุมยศ (คณะเทคโนโลยีการเกษตร)  

---

\newpage

# บทที่ 1
# บทนำ

## 1.1 ความเป็นมาและความสำคัญของปัญหา

ภาคเกษตรกรรมถือเป็นรากฐานที่มีความสำคัญยิ่งต่อระบบเศรษฐกิจ สังคม และความมั่นคงทางอาหารของประเทศไทย โดยเฉพาะอย่างยิ่งในภูมิภาคตะวันออก อันได้แก่ จังหวัดจันทบุรีและจังหวัดตราด ซึ่งเป็นแหล่งเพาะปลูกและส่งออกผลไม้เขตร้อนมูลค่าสูงระดับแนวหน้าของประเทศ โดยเฉพาะทุเรียน (*Durio zibethinus* Murr.) มังคุด และเงาะ ในกระบวนการผลิตไม้ผลเศรษฐกิจเหล่านี้ การเจริญเติบโต การสร้างตาดอก การติดผล ตลอดจนคุณภาพและเนื้อสัมผัสของผลผลิต ล้วนขึ้นอยู่กับความสมดุลของธาตุอาหารหลักในดิน (Primary Soil Macronutrients) ได้แก่ ไนโตรเจน (Nitrogen หรือ N) ฟอสฟอรัส (Phosphorus หรือ P) และโพแทสเซียม (Potassium หรือ K) ซึ่งในบรรดาธาตุอาหารหลักดังกล่าว ธาตุไนโตรเจนทำหน้าที่เป็นองค์ประกอบโครงสร้างพื้นฐานของกรดอะมิโน โปรตีน และคลอโรฟิลล์ที่ใช้ในกระบวนการสังเคราะห์ด้วยแสง ขณะที่ธาตุฟอสฟอรัสมีบทบาทสำคัญในกระบวนการถ่ายโอนพลังงานระดับเซลล์ในรูปของสารประกอบอะดีโนซีนไตรฟอสเฟต (Adenosine Triphosphate หรือ ATP) การแบ่งเซลล์ และการพัฒนาระบบรากพืช

อย่างไรก็ดี ในรอบหลายทศวรรษที่ผ่านมา เกษตรกรชาวสวนไม้ผลส่วนใหญ่ยังคงประสบปัญหาเชิงโครงสร้างด้านการจัดการธาตุอาหารพืช โดยนิยมใส่ปุ๋ยเคมีในปริมาณสูงเกินความต้องการที่แท้จริงของพืชอย่างต่อเนื่อง เนื่องจากขาดข้อมูลความอุดมสมบูรณ์ของดินเชิงปริมาณในแปลงปลูกแบบทันท่วงที พฤติกรรมการให้ปุ๋ยเคมีเกินขนาดนี้ส่งผลกระทบลูกโซ่อย่างรุนแรง ทั้งในมิติเศรษฐกิจที่ทำให้ต้นทุนค่าปุ๋ยของเกษตรกรพุ่งสูงขึ้นอย่างต่อเนื่อง และในมิตินิเวศวิทยาที่ส่งผลให้เกิดการสะสมของเกลือตกค้าง ดินกลายเป็นกรดจัด โครงสร้างทางกายภาพของดินเสื่อมโทรม ความหลากหลายของจุลินทรีย์ดินที่มีประโยชน์ลดลง ตลอดจนเกิดการชะล้างพังทลายของสารประกอบไนเตรต (Nitrate Leaching) และฟอสเฟตส่วนเกินลงสู่แหล่งน้ำผิวดินและน้ำใต้ดิน ก่อให้เกิดสภาวะยูโทรฟิเคชัน (Eutrophication) ซึ่งทำลายระบบนิเวศแหล่งน้ำธรรมชาติในพื้นที่เกษตรกรรมอย่างกว้างขวาง

เพื่อแก้ไขปัญหาดังกล่าว หลักการทำเกษตรแม่นยำ (Precision Agriculture) จึงกำหนดให้การใส่ปุ๋ยต้องสอดคล้องกับความต้องการของพืชและระดับธาตุอาหารที่มีอยู่จริงในดิน (Site-Specific Nutrient Management) ทว่าอุปสรรคสำคัญที่สุดที่ทำให้แนวคิดนี้ไม่สามารถขยายผลสู่เกษตรกรในวงกว้างได้ คือ ข้อจำกัดของเทคโนโลยีและกระบวนการตรวจวิเคราะห์ดินที่มีอยู่ในปัจจุบัน โดยสามารถจำแนกปัญหาออกเป็น 2 แนวทางหลัก ได้แก่

ประการแรก การวิเคราะห์ดินด้วยวิธีมาตรฐานทางเคมีในห้องปฏิบัติการ (Standard Analytical Laboratory Methods) แม้จะให้ผลที่มีความแม่นยำและความถูกต้องสูง เช่น การหาปริมาณไนโตรเจนทั้งหมด (Total Nitrogen) ด้วยวิธีเคจ์ลดาห์ล (Kjeldahl Method) และการหาปริมาณฟอสฟอรัสที่เป็นประโยชน์ (Available Phosphorus) ด้วยวิธีเบรย์ 2 (Bray II Method) หรือวิธีโอลเซน (Olsen Method) แต่กระบวนการดังกล่าวมีขั้นตอนยุ่งยาก ซับซ้อน ต้องใช้บุคลากรผู้เชี่ยวชาญ สารเคมีที่มีฤทธิ์กัดกร่อนสูง และเครื่องมือวิเคราะห์ทางวิทยาศาสตร์ที่มีราคาสูง ส่งผลให้มีระยะเวลารอคอยผลการทดสอบยาวนานถึง 2 ถึง 4 สัปดาห์ และมีค่าใช้จ่ายเฉลี่ยสูงถึง 1,000 ถึง 1,500 บาทต่อหนึ่งตัวอย่างดิน เกษตรกรจึงไม่สามารถนำผลวิเคราะห์มาปรับเปลี่ยนแผนการจัดการปุ๋ยได้อย่างทันท่วงทีตามระยะการเจริญเติบโตของพืช

ประการที่สอง การใช้ชุดทดสอบภาคสนามแบบรวดเร็ว (Colorimetric Rapid Test Kits) ซึ่งอาศัยการสกัดดินด้วยสารเคมีแล้วเทียบแถบสีด้วยสายตามนุษย์ แม้จะช่วยลดระยะเวลาลงได้บ้าง แต่ก็ยังคงต้องสัมผัสกับสารเคมีอันตราย เกิดของเสียสารเคมี และผลลัพธ์มักมีความคลาดเคลื่อนสูงเนื่องจากความแปรปรวนของการรับรู้สีของสายตามนุษย์แต่ละบุคคล ประกอบกับการรบกวนของความขุ่นและสีตามธรรมชาติของอนุภาคคอลลอยด์ในดิน ขณะเดียวกัน แม้จะมีผู้พยายามพัฒนาการประมวลผลภาพถ่ายจากกล้องสมาร์ทโฟนเพื่ออ่านค่าสี แต่ก็ยังเผชิญกับอุปสรรคสำคัญยิ่งยวดจากความแปรปรวนของสภาพแสงแวดล้อมภายนอก (Ambient Light Fluctuation) ความไม่สม่ำเสมอของการสะท้อนแสง และความแตกต่างของค่าตอบสนองของเซนเซอร์รับภาพ (CMOS Sensor) ในสมาร์ทโฟนแต่ละรุ่น ซึ่งก่อให้เกิดความคลาดเคลื่อนในการทำนายเกินกว่าระดับที่ยอมรับได้ในทางเคมีวิเคราะห์

จากสภาพปัญหาและข้อจำกัดดังกล่าว คณะผู้วิจัยจึงได้นำหลักการทางฟิสิกส์เกษตรเชิงทัศนศาสตร์ (Optical Agriphysics) มาบูรณาการร่วมกับระบบสมองกลฝังตัวและปัญญาประดิษฐ์ โดยอาศัยหลักการสะท้อนแสงแบบกระจาย (Diffuse Reflectance) ตามทฤษฎีคูเบลกา-มังก์ (Kubelka-Munk Theory) ซึ่งอธิบายว่า สารประกอบอินทรีย์ที่มีไนโตรเจนเป็นองค์ประกอบและสารประกอบฟอสเฟตเชิงซ้อนในดิน มีคุณสมบัติในการดูดกลืนและสะท้อนรังสีแม่เหล็กไฟฟ้าที่ความยาวคลื่นเฉพาะในย่านแสงที่ตามองเห็นและย่านใกล้อินฟราเรด (Visible and Near-Infrared หรือ VIS-NIR) ในช่วงความยาวคลื่น 450 ถึง 940 นาโนเมตร โดยลายพิมพ์สเปกตรัม (Spectral Fingerprint) ที่ได้จะแฝงข้อมูลความเข้มข้นของธาตุอาหารอยู่

โครงการวิจัยนี้จึงมุ่งออกแบบและสร้างชุดวิเคราะห์ปริมาณไนโตรเจนและฟอสฟอรัสในดินแบบพกพา โดยออกแบบกล่องตรวจวัดแบบทึบแสง (Optical Dark Chamber) ที่ผลิตด้วยเทคโนโลยีการพิมพ์สามมิติและเคลือบผิวภายในด้วยสารดูดกลืนแสงแบบด้าน เพื่อขจัดแสงรบกวนจากภายนอกโดยสมบูรณ์ ร่วมกับการติดตั้งแหล่งกำเนิดแสงไดโอดเปล่งแสงหลายความยาวคลื่น (Multi-wavelength LED Array) ที่ถูกควบคุมการกระตุ้นแสงแบบตามลำดับ (Pulsed Sequential Illumination) และควบคุมระยะห่างเชิงแสงให้คงที่ ผสานเข้ากับการประมวลผลลายพิมพ์สเปกตรัมด้วยโครงข่ายประสาทเทียม (Artificial Neural Network หรือ ANN) และการถดถอยเวกเตอร์สนับสนุน (Support Vector Regression หรือ SVR) แบบ On-device TinyML บนไมโครคอนโทรลเลอร์สมรรถนะสูง ESP32-S3 และแอปพลิเคชันสมาร์ทโฟน ทำให้ได้เครื่องมือตรวจวิเคราะห์ปริมาณไนโตรเจนและฟอสฟอรัสในดินที่ให้ผลแม่นยำ รวดเร็ว ไม่ใช้สารเคมี ปลอดภัย และมีความสะดวกในการพกพาไปใช้งานในแปลงเกษตรกรรมจริง อันจะช่วยยกระดับขีดความสามารถของเกษตรกรไทยสู่การทำการเกษตรแม่นยำอย่างยั่งยืน

---

## 1.2 วัตถุประสงค์ของการวิจัย

การวิจัยนี้มีวัตถุประสงค์หลัก 3 ประการ ได้แก่

1. เพื่อออกแบบและสร้างชุดวิเคราะห์ปริมาณไนโตรเจนทั้งหมดและฟอสฟอรัสที่เป็นประโยชน์ในดินแบบพกพา โดยใช้ระบบควบคุมสภาพแสงแบบทึบแสงร่วมกับแหล่งกำเนิดแสงหลายความยาวคลื่นและโมดูลตรวจวัดการสะท้อนแสงเชิงสเปกตรัม
2. เพื่อสร้างชุดข้อมูลมาตรฐานความสัมพันธ์ระหว่างลายพิมพ์สเปกตรัมการสะท้อนแสงของดินกับค่าการวิเคราะห์ปริมาณไนโตรเจนทั้งหมดและฟอสฟอรัสที่เป็นประโยชน์จากห้องปฏิบัติการมาตรฐาน
3. เพื่อพัฒนาและประเมินสมรรถนะแบบจำลองปัญญาประดิษฐ์โครงข่ายประสาทเทียมและการถดถอยเวกเตอร์สนับสนุนสำหรับการทำนายปริมาณไนโตรเจนและฟอสฟอรัสในดินแบบเรียลไทม์บนอุปกรณ์พกพา พร้อมระบบแปลผลและให้คำแนะนำการจัดการปุ๋ยเบื้องต้น

---

## 1.3 ขอบเขตของการวิจัย

การวิจัยนี้ได้กำหนดกรอบและขอบเขตการดำเนินงาน 4 ด้าน ดังนี้

### 1.3.1 ขอบเขตด้านประชากรและกลุ่มตัวอย่าง
ประชากรที่ใช้ในการศึกษาคือ ดินในแปลงเพาะปลูกไม้ผลเศรษฐกิจ โดยเฉพาะสวนทุเรียนในเขตพื้นที่ภาคตะวันออกของประเทศไทย กลุ่มตัวอย่างที่ใช้ในการสร้างชุดข้อมูลมาตรฐานและการทดสอบความใช้ได้ของวิธีประกอบด้วย ตัวอย่างดินที่เก็บจากแปลงเกษตรกรรมจริงในพื้นที่ 3 อำเภอ ได้แก่ อำเภอมะขาม และอำเภอท่าใหม่ จังหวัดจันทบุรี ตลอดจนอำเภอเขาสมิง จังหวัดตราด จำนวนรวมทั้งสิ้น 50 ตัวอย่าง โดยจำแนกเป็นตัวอย่างดินสำหรับสร้างและฝึกสอนแบบจำลองปัญญาประดิษฐ์จำนวน 15 ตัวอย่างแรก และตัวอย่างดินสำหรับขยายผลทดสอบความแม่นยำภาคสนามจำนวน 35 ตัวอย่าง ครอบคลุมชุดดินหลากหลายลักษณะ ได้แก่ ชุดดินท่าใหม่ (Tha Mai series) ชุดดินห้วยโป่ง (Huai Pong series) และชุดดินเขาสมิง (Khao Saming series)

### 1.3.2 ขอบเขตด้านตัวแปรที่ศึกษา
1. **ตัวแปรต้น (Independent Variables)** ประกอบด้วย ลายพิมพ์สเปกตรัมการสะท้อนแสงของดิน ($R_\lambda$) และค่าฟังก์ชันคูเบลกา-มังก์ ($F(R_\lambda)$) ภายใต้แสงกระตุ้น 6 แถบความยาวคลื่น ได้แก่ 465 นาโนเมตร (น้ำเงิน) 525 นาโนเมตร (เขียว) 660 นาโนเมตร (แดง) 720 นาโนเมตร (เรดเอจ) 850 นาโนเมตร (ใกล้อินฟราเรดตอนต้น) และ 940 นาโนเมตร (ใกล้อินฟราเรดอ้างอิงความชื้น) ตลอดจนค่าดัชนีสีในปริภูมิ RGB และ HSV
2. **ตัวแปรตาม (Dependent Variables)** ประกอบด้วย ปริมาณไนโตรเจนทั้งหมด (Total Nitrogen) ในหน่วยกรัมต่อกิโลกรัม (g/kg) หรือร้อยละ (%) และปริมาณฟอสฟอรัสที่เป็นประโยชน์ (Available Phosphorus) ในหน่วยมิลลิกรัมต่อกิโลกรัม (mg/kg หรือ ppm) ที่ทำนายได้จากแบบจำลองปัญญาประดิษฐ์
3. **ตัวแปรควบคุม (Controlled Variables)** ได้แก่ สภาพแสงแวดล้อมภายนอกโดยการควบคุมภายในกล่องทึบแสง ระยะห่างและมุมตกกระทบของแสงต่อพื้นผิวตัวอย่างดิน ความเข้มของกระแสไฟฟ้าที่ป้อนให้แก่ไดโอดเปล่งแสง ขนาดอนุภาคดินที่ร่อนผ่านตะแกรงขนาด 2 มิลลิเมตร และอุณหภูมิแวดล้อมขณะตรวจวัด

### 1.3.3 ขอบเขตด้านเทคโนโลยีและเครื่องมือ
1. **ระบบฮาร์ดแวร์** พัฒนาโครงสร้างกล่องวัดแบบทึบแสง (Optical Dark Chamber) ขนาดกะทัดรัดด้วยเครื่องพิมพ์สามมิติ วัสดุพอลิเมอร์ทนความร้อนเคลือบผิวด้านภายในเพื่อลดการสะท้อนแสง ติดตั้งโมดูลแหล่งกำเนิดแสง Multi-wavelength LED Array และแผ่นเทียบการสะท้อนแสงสีขาวมาตรฐาน (Standard White Reference Tile) ขับเคลื่อนด้วยบอร์ดไมโครคอนโทรลเลอร์ ESP32-S3 Dual-Core 240 MHz
2. **ระบบซอฟต์แวร์และปัญญาประดิษฐ์** พัฒนาอัลกอริทึมการประมวลผลสัญญาณสเปกตรัมล่วงหน้าด้วยวิธี Standard Normal Variate (SNV) และฝึกสอนแบบจำลองโครงข่ายประสาทเทียม (ANN) และการถดถอยเวกเตอร์สนับสนุน (SVR) และแปลงเป็นโครงสร้างภาษา C++ แบบสถิต (Static Arrays) สำหรับประมวลผลแบบ TinyML และเชื่อมต่อแอปพลิเคชันบนสมาร์ทโฟน
3. **วิธีมาตรฐานอ้างอิงทางห้องปฏิบัติการ** ตรวจวิเคราะห์ปริมาณไนโตรเจนทั้งหมดด้วยวิธี Micro-Kjeldahl Method ตามมาตรฐาน AOAC 978.02 และตรวจวิเคราะห์ฟอสฟอรัสที่เป็นประโยชน์ด้วยวิธี Bray II Method ร่วมกับเครื่องสเปกโตรโฟโตมิเตอร์ที่ความยาวคลื่น 880 นาโนเมตร

### 1.3.4 ขอบเขตด้านระยะเวลาและสถานที่
ดำเนินงานวิจัยระหว่างเดือนเมษายน พ.ศ. 2569 ถึงเดือนมีนาคม พ.ศ. 2570 โดยทำการทดลอง ณ ห้องปฏิบัติการฟิสิกส์ประยุกต์และห้องปฏิบัติการเคมี คณะวิทยาศาสตร์และเทคโนโลยี มหาวิทยาลัยราชภัฏรำไพพรรณี และเก็บตัวอย่างดินในแปลงเกษตรกรรมจังหวัดจันทบุรีและจังหวัดตราด

---

## 1.4 สมมติฐานของการวิจัย

การวิจัยนี้ได้กำหนดสมมติฐานเชิงปริมาณไว้ 3 ประการ ดังนี้

1. สเปกตรัมการสะท้อนแสงแบบกระจายของดินที่สกัดจากระบบควบคุมสภาพแสงมีความสัมพันธ์เชิงฟังก์ชันที่ไม่เป็นเชิงเส้นอย่างมีนัยสำคัญทางสถิติกับปริมาณไนโตรเจนทั้งหมดและฟอสฟอรัสที่เป็นประโยชน์ที่วิเคราะห์ด้วยวิธีมาตรฐานในห้องปฏิบัติการ
2. แบบจำลองปัญญาประดิษฐ์ที่พัฒนาขึ้น (ANN และ SVR) มีสมรรถนะในการทำนายปริมาณไนโตรเจนทั้งหมดและฟอสฟอรัสที่เป็นประโยชน์ในดินได้อย่างแม่นยำ โดยมีค่าสัมประสิทธิ์การตัดสินใจ ($R^2$) ไม่น้อยกว่า 0.88 สำหรับไนโตรเจน และไม่น้อยกว่า 0.85 สำหรับฟอสฟอรัส และมีค่าความคลาดเคลื่อนรากกำลังสองเฉลี่ย (RMSE) ต่ำกว่าการทำนายด้วยสมการถดถอยเชิงเส้นเชิงซ้อนทั่วไปไม่น้อยกว่าร้อยละ 40
3. ผลการตรวจวิเคราะห์ปริมาณไนโตรเจนทั้งหมดและฟอสฟอรัสที่เป็นประโยชน์ในดินภาคสนามด้วยชุดวิเคราะห์แบบพกพาที่พัฒนาขึ้น ไม่มีความแตกต่างจากผลการวิเคราะห์ด้วยวิธีมาตรฐานทางเคมีในห้องปฏิบัติการอย่างมีนัยสำคัญทางสถิติที่ระดับความเชื่อมั่น 95% นั่นคือ ค่าความน่าจะเป็น ($p\text{-value}$) จากการทดสอบ Paired Samples t-test มีค่ามากกว่า 0.05 และมีค่าความเอนเอียง (Bias) ต่ำกว่าร้อยละ 5

---

## 1.5 นิยามศัพท์เฉพาะ

1. **ชุดวิเคราะห์ปริมาณไนโตรเจนและฟอสฟอรัสในดินแบบพกพา (Portable Soil N and P Analyzer)** หมายถึง อุปกรณ์ตรวจวัดขนาดกะทัดรัดที่ประกอบด้วยกล่องทึบแสงป้องกันแสงรบกวนภายนอก แหล่งกำเนิดแสงหลายความยาวคลื่น โมดูลเซนเซอร์ตรวจวัดการสะท้อนแสง และหน่วยประมวลผลสมองกลฝังตัวที่ทำงานร่วมกับสมาร์ทโฟน สามารถเคลื่อนย้ายไปตรวจวัดในแปลงเกษตรกรรมได้สะดวก
2. **การสะท้อนแสงแบบกระจาย (Diffuse Reflectance)** หมายถึง ปรากฏการณ์ที่แสงตกกระทบลงบนอนุภาคดินแล้วเกิดการหักเห สะท้อน และกระเจิงแสงซ้ำไปซ้ำมาภายในเนื้อสารก่อนจะโผล่พ้นพื้นผิวกลับออกมา โดยแสงที่สะท้อนออกมาจะถูกดูดกลืนพลังงานบางส่วนตามธรรมชาติของพันธะเคมีและสารประกอบที่อยู่ในดิน
3. **ทฤษฎีคูเบลกา-มังก์ (Kubelka-Munk Theory)** หมายถึง ทฤษฎีทางฟิสิกส์ทัศนศาสตร์ที่อธิบายความสัมพันธ์ระหว่างค่าการสะท้อนแสงแบบกระจายของตัวอย่างทึบแสง ($R_\infty$) กับสัมประสิทธิ์การดูดกลืนแสง ($K$) และสัมประสิทธิ์การกระเจิงแสง ($S$) ในรูปของฟังก์ชันคูเบลกา-มังก์ $F(R_\infty) = (1 - R_\infty)^2 / (2R_\infty) = K/S$
4. **ลายพิมพ์สเปกตรัม (Spectral Fingerprint)** หมายถึง เวกเตอร์ของค่าความเข้มของการสะท้อนแสงของดินตัวอย่างที่บันทึกได้ภายใต้แถบความยาวคลื่นเฉพาะ 6 ย่านคลื่น (465, 525, 660, 720, 850 และ 940 นาโนเมตร) ซึ่งมีลักษณะเฉพาะตัวตามองค์ประกอบทางเคมีและกายภาพของดินตัวอย่างนั้น
5. **ไนโตรเจนทั้งหมดในดิน (Total Soil Nitrogen หรือ Total N)** หมายถึง ปริมาณไนโตรเจนรวมทุกรูปที่มีอยู่ในดิน ทั้งในรูปสารประกอบอินทรีย์และอนินทรีย์ โดยวิธีมาตรฐานอ้างอิงในการวิเคราะห์คือวิธีเคจ์ลดาห์ล (Kjeldahl Method) มีหน่วยเป็นกรัมต่อกิโลกรัม (g/kg) หรือร้อยละ (%)
6. **ฟอสฟอรัสที่เป็นประโยชน์ในดิน (Available Soil Phosphorus หรือ Available P)** หมายถึง ปริมาณฟอสฟอรัสในดินที่อยู่ในรูปสารละลายออร์โทฟอสเฟตที่พืชสามารถดูดกลืนไปใช้ประโยชน์ได้ โดยวิธีมาตรฐานอ้างอิงในการวิเคราะห์คือวิธีเบรย์ 2 (Bray II Method) มีหน่วยเป็นมิลลิกรัมต่อกิโลกรัม (mg/kg หรือ ppm)
7. **แบบจำลองปัญญาประดิษฐ์บนอุปกรณ์ (On-device TinyML Model)** หมายถึง โครงข่ายประสาทเทียมหรือแบบจำลองการเรียนรู้ของเครื่องที่ผ่านการฝึกสอน ปรับพารามิเตอร์ และบีบอัดให้อยู่ในรูปของชุดข้อมูลคงที่ (Static Weight Arrays) เพื่อให้สามารถทำการอนุมาน (Inference) หาผลลัพธ์ได้อย่างรวดเร็วบนชิปไมโครคอนโทรลเลอร์หรือสมาร์ทโฟนโดยไม่ต้องเชื่อมต่อกับอินเทอร์เน็ตหรือเครื่องแม่ข่ายคลาวด์

---

## 1.6 ประโยชน์ที่คาดว่าจะได้รับ

1. ได้ต้นแบบชุดวิเคราะห์ปริมาณไนโตรเจนและฟอสฟอรัสในดินแบบพกพาที่ทำงานร่วมกับสมาร์ทโฟน มีความแม่นยำสูง รวดเร็ว และไม่ก่อให้เกิดขยะสารเคมีอันตราย
2. ได้ชุดข้อมูลมาตรฐานเชิงสเปกตรัมของดินสวนไม้ผลในจังหวัดจันทบุรีและตราด ที่จับคู่กับค่าเคมีวิเคราะห์มาตรฐาน ซึ่งเป็นประโยชน์ต่อการวิจัยและต่อยอดด้านปัญญาประดิษฐ์ทางการเกษตร
3. เกษตรกรชาวสวนทุเรียนและไม้ผลสามารถตรวจสอบระดับธาตุอาหาร N และ P ในดินได้ด้วยตนเองอย่างแม่นยำในแปลงปลูก ช่วยลดต้นทุนการซื้อปุ๋ยเคมีเกินความจำเป็นได้ร้อยละ 15 ถึง 25
4. ช่วยลดผลกระทบเชิงลบต่อสิ่งแวดล้อม ป้องกันการสะสมของสารประกอบไนเตรตและฟอสเฟตในแหล่งน้ำธรรมชาติ และชะลอการเสื่อมโทรมของดินในเขตภาคตะวันออก
5. ได้องค์ความรู้ใหม่ด้านการประยุกต์ทัศนศาสตร์ฟิสิกส์ร่วมกับปัญญาประดิษฐ์ขนาดเล็กสำหรับการเกษตรแม่นยำ ซึ่งพร้อมสำหรับการยื่นจดสิทธิบัตรหรืออนุสิทธิบัตร และการตีพิมพ์เผยแพร่ในวารสารวิชาการระดับนานาชาติ

\newpage

# บทที่ 2
# วรรณกรรมและงานวิจัยที่เกี่ยวข้อง

การวิจัยเรื่องการพัฒนาชุดวิเคราะห์ปริมาณไนโตรเจนและฟอสฟอรัสในดินแบบพกพาด้วยหลักการสะท้อนแสงร่วมกับปัญญาประดิษฐ์ คณะผู้วิจัยได้ทำการทบทวนวรรณกรรม เอกสาร แนวคิด ทฤษฎีฟิสิกส์ และงานวิจัยที่เกี่ยวข้องทั้งในและต่างประเทศ โดยจำแนกเนื้อหาออกเป็น 7 หัวข้อหลัก ได้แก่

1. พลวัตและสรีรวิทยาของไนโตรเจนและฟอสฟอรัสในดินแปลงไม้ผลเขตร้อน
2. ทฤษฎีการสะท้อนแสงแบบกระจายและทฤษฎีคูเบลกา-มังก์ (Diffuse Reflectance & Kubelka-Munk Theory)
3. การตอบสนองเชิงสเปกตรัมของไนโตรเจนและฟอสฟอรัสในย่านแสงที่ตามองเห็นและใกล้อินฟราเรด (VIS-NIR)
4. การประมวลผลสเปกตรัมล่วงหน้าและการปรับมาตรฐานสีด้วยคอมพิวเตอร์วิทัศน์
5. สถาปัตยกรรมปัญญาประดิษฐ์และการเรียนรู้ของเครื่องสำหรับการวิเคราะห์ดินเชิงปริมาณ
6. งานวิจัยที่เกี่ยวข้องระดับสากลและกรอบแนวคิดการวิจัย
7. การวิเคราะห์เคมีดินด้วยแถบสีเทียบเคียงและข้อจำกัดเชิงทัศนศาสตร์ (Colorimetric Soil Testing and Optical Constraints)

---

## 2.1 พลวัตและสรีรวิทยาของไนโตรเจนและฟอสฟอรัสในดินแปลงไม้ผลเขตร้อน

### 2.1.1 บทบาททางชีวเคมีและสรีรวิทยาของไนโตรเจนในดิน
ไนโตรเจน (Nitrogen หรือ N) จัดเป็นธาตุอาหารหลักที่มีความจำเป็นสูงสุดต่อการเจริญเติบโตของพืช เนื่องจากเป็นองค์ประกอบโครงสร้างหลักของโมเลกุลชีวภาพที่สำคัญ ได้แก่ กรดอะมิโน (Amino Acids) ซึ่งเป็นหน่วยย่อยของโปรตีนและเอนไซม์ คลอโรฟิลล์ (Chlorophyll) ซึ่งทำหน้าที่ดักจับพลังงานแสงในกระบวนการสังเคราะห์ด้วยแสง ตลอดจนกรดนิวคลีอิก (DNA และ RNA) ในดินธรรมชาติและดินเกษตรกรรม ไนโตรเจนจะปรากฏอยู่ในสองรูปใหญ่ ได้แก่ ไนโตรเจนอินทรีย์ (Organic Nitrogen) ซึ่งคิดเป็นสัดส่วนมากกว่าร้อยละ 90 ถึง 95 ของปริมาณไนโตรเจนทั้งหมด (Total Nitrogen) ในรูปของฮิวมัส (Humus) กรดฮิวมิก กรดฟุลวิก และสารประกอบอะมิโน และไนโตรเจนอนินทรีย์ (Inorganic Nitrogen) ซึ่งคิดเป็นเพียงร้อยละ 1 ถึง 5 แต่อยู่ในรูปไอออนที่รากพืชสามารถดูดกลืนได้ทันที ได้แก่ แอมโมเนียมไอออน ($\text{NH}_4^+$) และไนเตรตไอออน ($\text{NO}_3^-$)

สำหรับไม้ผลเศรษฐกิจภาคตะวันออก เช่น ทุเรียนพันธุ์หมอนทอง การจัดการไนโตรเจนมีผลกระทบโดยตรงต่อวงจรการเจริญเติบโต หากดินมีไนโตรเจนไม่เพียงพอ ใบแก่จะมีสีเหลืองซีด ต้นแคระแกร็น และผลผลิตลดลงอย่างรุนแรง แต่หากดินมีไนโตรเจนสะสมสูงเกินไป พืชจะเกิดอาการบ้าใบ แตกใบอ่อนในจังหวะที่ไม่เหมาะสม ส่งผลให้ดอกและผลอ่อนหลุดร่วงอย่างเฉียบพลัน อีกทั้งเนื้อทุเรียนจะมีลักษณะแฉะและคุณภาพต่ำ การทราบปริมาณไนโตรเจนทั้งหมดในดินจึงเป็นดัชนีชี้วัดที่สำคัญที่สุดในการวางแผนการใส่ปุ๋ยอย่างสมดุล

### 2.1.2 พลวัตและข้อจำกัดของฟอสฟอรัสในดินกรดภาคตะวันออก
ฟอสฟอรัส (Phosphorus หรือ P) เป็นธาตุอาหารหลักที่มีบทบาทเชิงโครงสร้างและพลังงาน โดยเป็นองค์ประกอบของสารพันธุกรรม ฟอสโฟลิพิดในเยื่อหุ้มเซลล์ และทำหน้าที่เป็นตัวกักเก็บและถ่ายโอนพลังงานเคมีในรูปของสารประกอบอะดีโนซีนไตรฟอสเฟต (ATP) ซึ่งมีความจำเป็นยิ่งยวดในระยะการพัฒนาของราก การแบ่งเซลล์ การสร้างตาดอก และการขยายขนาดของผล

ทว่าในพื้นที่เกษตรกรรมของจังหวัดจันทบุรีและตราด ซึ่งมีลักษณะดินเป็นกรดจัด (Soil pH 4.0 ถึง 5.2) ปริมาณฟอสฟอรัสที่อยู่ในดินมักถูกตรึง (Phosphorus Fixation) โดยทำปฏิกิริยาทางเคมีกับสารประกอบออกไซด์ของเหล็กและอะลูมิเนียม เกิดเป็นสารประกอบเชิงซ้อนเหล็กฟอสเฟต ($\text{FePO}_4$) และอะลูมิเนียมฟอสเฟต ($\text{AlPO}_4$) ซึ่งละลายน้ำได้ยากมาก ส่งผลให้ฟอสฟอรัสส่วนใหญ่อยู่ในรูปที่ไม่เป็นประโยชน์ต่อพืช แม้เกษตรกรจะใส่ปุ๋ยฟอสเฟตในปริมาณสูงก็ตาม ดังนั้น การตรวจวัดฟอสฟอรัสจึงจำเป็นต้องมุ่งเน้นไปที่ ฟอสฟอรัสที่เป็นประโยชน์ (Available Phosphorus) ซึ่งประเมินปริมาณฟอสเฟตไอออนที่สามารถปลดปล่อยออกมาสู่สารละลายดินได้

---

## 2.2 ทฤษฎีการสะท้อนแสงแบบกระจายและทฤษฎีคูเบลกา-มังก์

### 2.2.1 พฤติกรรมทางทัศนศาสตร์ของแสงในตัวกลางกระเจิงแสง (Scattering Medium)
เมื่อลำแสงตกกระทบลงบนพื้นผิวของอนุภาคดิน แสงที่สะท้อนกลับออกมาสามารถจำแนกออกได้เป็น 2 ส่วนหลัก ตามหลักการทางฟิสิกส์ทัศนศาสตร์ ได้แก่

1. **การสะท้อนแบบสมบูรณ์หรือการสะท้อนแบบกระจกเงา (Specular Reflectance)** เป็นแสงที่สะท้อนออกจากระนาบพื้นผิวส่วนบนสุดของอนุภาคดินโดยตรงตามกฎการสะท้อนของเฟรสเนล (Fresnel's Law) แสงส่วนนี้ไม่ได้ทะลุผ่านเข้าไปในเนื้ออนุภาคดิน จึงไม่มีข้อมูลการดูดกลืนพลังงานของพันธะเคมีภายในสาร และจัดเป็นสัญญาณรบกวนหลักที่ต้องกำจัดออก
2. **การสะท้อนแสงแบบกระจาย (Diffuse Reflectance)** เป็นแสงที่ทะลุผ่านเข้าสู่ผิวหน้าของชั้นดิน แล้วเกิดกระบวนการหักเห การสะท้อนภายในหลายชั้น (Multiple Scattering) และการกระเจิงไปมาระหว่างอนุภาคดินขนาดเล็ก ก่อนที่จะสะท้อนกลับพ้นพื้นผิวออกมาในทุกทิศทาง ในระหว่างที่แสงเดินทางผ่านตัวกลางนี้ คลื่นแสงจะเกิดอันตรกิริยากับโมเลกุลของสารประกอบในดิน ทำให้เกิดการดูดกลืนพลังงานแสงเฉพาะความยาวคลื่นตามระดับพลังงานการสั่นของพันธะเคมี

### 2.2.2 การประยุกต์ทฤษฎีคูเบลกา-มังก์ (Kubelka-Munk Theory)
เพื่ออธิบายความสัมพันธ์ระหว่างความเข้มของแสงสะท้อนแบบกระจายกับความเข้มข้นของสารประกอบในตัวกลางที่เป็นของแข็งและมีความทึบแสงสูง คูเบลกาและมังก์ (Kubelka & Munk) ได้พัฒนาแบบจำลองการแพร่ของฟลักซ์แสง 2 ทิศทาง (Two-Flux Model) โดยพิจารณาฟลักซ์แสงที่เคลื่อนที่ลง ($i$) และฟลักซ์แสงที่กระเจิงขึ้น ($j$) ภายในชั้นสารที่มีความหนาเข้าใกล้อนันต์ ดังสมการอนุพันธ์

$$-\frac{di}{dx} = -(K + S)i + Sj$$

$$\frac{dj}{dx} = -(K + S)j + Si$$

เมื่อ $K$ คือ สัมประสิทธิ์การดูดกลืนแสง (Absorption Coefficient) ของตัวกลาง และ $S$ คือ สัมประสิทธิ์การกระเจิงแสง (Scattering Coefficient) ของตัวกลาง เมื่อทำการอินทิเกรตสมการภายใต้เงื่อนไขขอบเขตที่ชั้นดินมีความหนาเชิงแสงมากพอจนแสงไม่สามารถทะลุผ่านได้ (Infinitely Thick Sample Layer) จะได้ค่าการสะท้อนแสงแบบกระจายสัมบูรณ์ ($R_\infty$) และสามารถจัดรูปเป็นฟังก์ชันคูเบลกา-มังก์ (Kubelka-Munk Function) ได้ดังนี้

$$F(R_\infty) = \frac{(1 - R_\infty)^2}{2R_\infty} = \frac{K}{S}$$

จากทฤษฎีดังกล่าว สัมประสิทธิ์การดูดกลืนแสง $K$ มีความเป็นสัดส่วนโดยตรงกับความเข้มข้น ($C$) ของสารประกอบดูดกลืนแสงตามกฎของเบียร์-แลมเบิร์ต (Beer-Lambert Law) นั่นคือ $K = \sum \epsilon_i C_i$ เมื่อ $\epsilon_i$ คือค่าการดูดกลืนแสงจำเพาะขององค์ประกอบแต่ละชนิด ดังนั้น หากสัมประสิทธิ์การกระเจิงแสง $S$ ของอนุภาคดินตัวอย่างมีค่าคงที่จากการบดร่อนอนุภาคให้สม่ำเสมอ จะได้ความสัมพันธ์เชิงเส้นระหว่างฟังก์ชันคูเบลกา-มังก์กับความเข้มข้นของสารดูดกลืนแสง ดังสมการ

$$F(R_\infty) = \frac{\sum \epsilon_i C_i}{S} \propto C_{\text{nutrient}}$$

สมการข้างต้นถือเป็นรากฐานทางฟิสิกส์ที่สำคัญยิ่งในการเชื่อมโยงค่าการสะท้อนแสงที่วัดได้จากเซนเซอร์เข้ากับปริมาณไนโตรเจนและฟอสฟอรัสในดิน

---

## 2.3 การตอบสนองเชิงสเปกตรัมของไนโตรเจนและฟอสฟอรัสในย่าน VIS-NIR

การดูดกลืนรังสีแม่เหล็กไฟฟ้าของดินในย่านแสงที่ตามองเห็น (Visible 400 ถึง 700 นาโนเมตร) และย่านใกล้อินฟราเรด (Near-Infrared 700 ถึง 1100 นาโนเมตร) เกิดจากการเปลี่ยนระดับพลังงานอิเล็กตรอนของแร่ธาตุ (Electronic Transitions) และการสั่นระดับโมเลกุลในรูปแบบโอเวอร์โทน (Overtones) และแถบรวม (Combination Bands) ของพันธะเคมีที่มีอะตอมไฮโดรเจนเป็นองค์ประกอบ ได้แก่ พันธะ $\text{O-H}$, $\text{C-H}$, และ $\text{N-H}$

### 2.3.1 แถบสเปกตรัมที่สัมพันธ์กับไนโตรเจนในดิน
เนื่องจากไนโตรเจนส่วนใหญ่ในดินอยู่ในรูปของสารอินทรีย์คาร์บอนและสารประกอบเชิงซ้อนของฮิวมัส การตอบสนองเชิงสเปกตรัมของไนโตรเจนจึงมีความสัมพันธ์อย่างใกล้ชิดกับสเปกตรัมของอินทรียวัตถุในดิน โดยมีแถบคลื่นเด่นดังนี้

1. **แถบความยาวคลื่น 465 นาโนเมตร (แสงสีน้ำเงิน)** มีความสัมพันธ์กับการดูดกลืนแสงของสารประกอบฮิวมัสและฟุลวิกในดิน สารอินทรีย์ที่มีโมเลกุลซับซ้อนจะดูดกลืนแสงสีน้ำเงินอย่างเข้มข้น ส่งผลให้ดินที่มีอินทรียวัตถุและไนโตรเจนสูงสะท้อนแสงสีน้ำเงินออกมาต่ำ
2. **แถบความยาวคลื่น 660 นาโนเมตร (แสงสีแดง)** สัมพันธ์กับการดูดกลืนของสารอนุพันธ์คลอโรฟิลล์และสารอินทรีย์ที่กำลังย่อยสลาย ตลอดจนเป็นจุดตัดของความชันสเปกตรัมสีของดิน
3. **แถบความยาวคลื่น 850 ถึง 940 นาโนเมตร (ย่านใกล้อินฟราเรด)** เป็นบริเวณที่เกิดการสั่นระดับโมเลกุลแบบโอเวอร์โทนที่สาม (Third Overtone) ของพันธะ $\text{N-H}$ ในหมู่อะมิโน (Amine/Amide Functional Groups) ซึ่งเป็นโครงสร้างหลักของไนโตรเจนอินทรีย์

### 2.3.2 แถบสเปกตรัมที่สัมพันธ์กับฟอสฟอรัสในดิน
ฟอสฟอรัสที่เป็นประโยชน์ (Available P) แม้จะไม่มีการดูดกลืนแสงตรงที่เด่นชัดเท่าสารอินทรีย์ในย่าน VIS-NIR เนื่องจากเป็นไอออนอนินทรีย์ แต่เนื่องจากในดินเขตร้อน ฟอสเฟตไอออนจะจับตัวกับสารประกอบออกไซด์ของเหล็ก (เช่น Goethite, Hematite) เป็นสารประกอบเชิงซ้อนเหล็กฟอสเฟต การเปลี่ยนแปลงความเข้มข้นของฟอสเฟตจะส่งผลต่อการจัดเรียงโครงสร้างผลึกและคุณสมบัติทางแสงของสารประกอบเหล็กออกไซด์เหล่านี้ ทำให้เกิดการเปลี่ยนแปลงค่าการสะท้อนแสงที่แถบความยาวคลื่น 525 นาโนเมตร (แสงสีเขียว) และแถบ 720 ถึง 880 นาโนเมตร ซึ่งสัมพันธ์กับการถ่ายโอนประจุ (Charge Transfer) และการเปลี่ยนระดับพลังงาน $d\text{-}d$ ของไอออนเหล็ก ($\text{Fe}^{3+}$)

### 2.3.3 ผลกระทบของการรบกวนจากความชื้นในดินและการแก้ไข
ความชื้นในดินจัดเป็นปัจจัยรบกวนที่มีผลกระทบอย่างมีนัยสำคัญยิ่งยวดต่อสเปกตรัมการสะท้อนแสง เนื่องจากโมเลกุลของน้ำมีแถบการดูดกลืนที่รุนแรงมากที่ความยาวคลื่น 940 นาโนเมตร (โอเวอร์โทนที่สามของพันธะ $\text{O-H}$) และ 1450 นาโนเมตร อีกทั้งน้ำยังทำหน้าที่เป็นสารเคลือบอนุภาคดินซึ่งเปลี่ยนดัชนีหักเหของแสงและลดค่าสัมประสิทธิ์การกระเจิงแสง $S$ ทำให้ดินที่เปียกชื้นมีค่าการสะท้อนแสงลดลงทุกความยาวคลื่น ดังนั้น การออกแบบระบบจึงต้องติดตั้งแหล่งกำเนิดแสงที่ความยาวคลื่น 940 นาโนเมตร เป็นแถบอ้างอิงความชื้น เพื่อใช้ในการปรับชดเชยค่าทางคณิตศาสตร์

---

## 2.4 การประมวลผลสเปกตรัมล่วงหน้าและการปรับมาตรฐานสีด้วยคอมพิวเตอร์วิทัศน์

เพื่อลดทอนสัญญาณรบกวน ขจัดความแปรปรวนของขนาดอนุภาคดิน และปรับมาตรฐานของข้อมูลก่อนนำเข้าสู่แบบจำลองปัญญาประดิษฐ์ จำเป็นต้องประยุกต์ใช้เทคนิคการประมวลผลสัญญาณสเปกตรัมทางเคมีเมตริกส์ (Chemometrics Preprocessing) และคอมพิวเตอร์วิทัศน์ ดังนี้

### 2.4.1 การปรับมาตรฐานตัวแปรปกติ (Standard Normal Variate หรือ SNV)
เทคนิค SNV ใช้สำหรับขจัดผลกระทบจากการกระเจิงแสงแบบกระจายอันเนื่องมาจากความแตกต่างของขนาดและรูปร่างของเม็ดดิน โดยทำการปรับสเกลของแต่ละสเปกตรัมรายตัวอย่างให้มีค่าเฉลี่ยเป็นศูนย์และมีส่วนเบี่ยงเบนมาตรฐานเป็นหนึ่ง ตามสมการ

$$x_{\text{SNV}, \lambda} = \frac{x_\lambda - \bar{x}}{\sqrt{\frac{\sum_{\lambda=1}^p (x_\lambda - \bar{x})^2}{p - 1}}}$$

เมื่อ $x_\lambda$ คือ ค่าการสะท้อนแสงที่ความยาวคลื่น $\lambda$, $\bar{x}$ คือ ค่าเฉลี่ยของการสะท้อนแสงข้ามทุกความยาวคลื่นของตัวอย่างนั้น และ $p$ คือ จำนวนความยาวคลื่นทั้งหมดที่ตรวจวัด

### 2.4.2 การปรับแก้การกระเจิงแบบทวีคูณ (Multiplicative Scatter Correction หรือ MSC)
เทคนิค MSC ทำการปรับความชันและจุดตัดของสเปกตรัมแต่ละตัวอย่างเทียบกับสเปกตรัมเฉลี่ยอ้างอิง ($\bar{x}_{\text{ref}}$) ผ่านสมการถดถอยเชิงเส้น $x_i = a_i + b_i \bar{x}_{\text{ref}} + e_i$ จากนั้นจึงทำการปรับแก้เป็น $x_{\text{MSC}} = (x_i - a_i) / b_i$ เพื่อให้เส้นสเปกตรัมทุกตัวอย่างมีระดับอ้างอิงเดียวกัน

### 2.4.3 การสอบเทียบมาตรฐานด้วยแผ่นเทียบสีขาว (White Reference Tile Calibration)
เพื่อขจัดความแตกต่างของความไวแสงของเซนเซอร์รับภาพในอุปกรณ์แต่ละเครื่อง ค่าการสะท้อนแสงสัมพัทธ์ ($R_\lambda$) จะถูกคำนวณเทียบกับสัญญาณการสะท้อนแสงของแผ่นเทียบมาตรฐานสีขาว (White Reference Standard Tile, ทำจากสาร Polytetrafluoroethylene หรือ Spectralon ที่มีค่าการสะท้อนแสงสม่ำเสมอมากกว่าร้อยละ 99) และสัญญาณกระแสมืด (Dark Signal) เมื่อปิดแหล่งกำเนิดแสง ตามสมการ

$$R_\lambda = \frac{I_{\text{sample}}(\lambda) - I_{\text{dark}}(\lambda)}{I_{\text{white}}(\lambda) - I_{\text{dark}}(\lambda)}$$

กระบวนการนี้ทำให้ค่าสเปกตรัมที่ได้มีคุณสมบัติไม่ขึ้นอยู่กับความไวของเซนเซอร์และกำลังส่องสว่างของหลอดไฟ

---

## 2.5 สถาปัตยกรรมปัญญาประดิษฐ์และการเรียนรู้ของเครื่องสำหรับการวิเคราะห์ดินเชิงปริมาณ

เนื่องจากข้อมูลสเปกตรัมการสะท้อนแสงกับความเข้มข้นของธาตุอาหารในดินมีความสัมพันธ์ที่ซับซ้อน ไม่เป็นเชิงเส้น และมีการทับซ้อนกันของแถบการดูดกลืน แบบจำลองการเรียนรู้ของเครื่องจึงมีความเหมาะสมอย่างยิ่งในการถอดรหัสความสัมพันธ์ดังกล่าว

### 2.5.1 โครงข่ายประสาทเทียม (Artificial Neural Network หรือ ANN)
โครงข่ายประสาทเทียมแบบเพอร์เซปตรอนหลายชั้น (Multilayer Perceptron หรือ MLP) อาศัยโครงสร้างแบบเชื่อมโยงไปข้างหน้า (Feedforward Architecture) ประกอบด้วย ชั้นนำเข้า (Input Layer) ชั้นซ่อน (Hidden Layers) และชั้นส่งออก (Output Layer) การส่งผ่านสัญญาณในแต่ละเซลล์ประสาทคำนวณได้จาก

$$y_j = f\left(\sum_{i=1}^n w_{ij} x_i + b_j\right)$$

เมื่อ $w_{ij}$ คือค่าน้ำหนัก $b_j$ คือค่าไบแอส และ $f(\cdot)$ คือฟังก์ชันกระตุ้นแบบไม่เป็นเชิงเส้น เช่น Rectified Linear Unit (ReLU) หรือ Sigmoid แบบจำลองจะถูกฝึกสอนผ่านกระบวนการส่งย้อนกลับความคลาดเคลื่อน (Backpropagation) ร่วมกับอัลกอริทึมการปรับค่าน้ำหนักแบบอดัม (Adam Optimizer) เพื่อลดทอนฟังก์ชันการสูญเสียกำลังสองเฉลี่ย (Mean Squared Error หรือ MSE)

### 2.5.2 การถดถอยเวกเตอร์สนับสนุน (Support Vector Regression หรือ SVR)
แบบจำลอง SVR พยายามสร้างฟังก์ชันการทำนายที่อยู่ในท่อความคลาดเคลื่อน $\epsilon\text{-tube}$ โดยยอมรับความคลาดเคลื่อนที่ไม่เกิน $\epsilon$ และลดทอนขนาดของค่าน้ำหนักเพื่อเพิ่มความสามารถในการสรุปผลทั่วไป (Generalization Capability) ผ่านการแปลงข้อมูลมิติต่ำไปสู่มิติสูงด้วยฟังก์ชันเคอร์เนลแบบรัศมีฐาน (Radial Basis Function หรือ RBF Kernel)

$$K(x_i, x_j) = \exp\left(-\gamma \|x_i - x_j\|^2\right)$$

SVR มีจุดเด่นเป็นพิเศษในการจัดการกับชุดข้อมูลที่มีจำนวนตัวอย่างปานกลางแต่มีมิติข้อมูลสูง และทนทานต่อจุดผิดปรกติ (Outliers) ในข้อมูลได้ดีเยี่ยม

### 2.5.3 การบีบอัดแบบจำลองและการนำไปใช้บนระบบสมองกลฝังตัว (Edge TinyML Deployment)
เพื่อให้แบบจำลองสามารถทำงานได้จริงบนไมโครคอนโทรลเลอร์ ESP32-S3 และสมาร์ทโฟนโดยไม่ต้องพึ่งพาระบบคลาวด์ พารามิเตอร์ค่าน้ำหนักและค่าไบแอสจะถูกแปลงเป็นค่าคงที่ในอาร์เรย์ภาษา C++ (Static Weight Arrays) และใช้การคำนวณแบบจุดลอยตัวเดี่ยว (Single-Precision Floating Point) หรือการทำ Quantization 8 บิต ซึ่งช่วยให้การอนุมาน (Forward Inference Pass) ใช้เวลาต่ำกว่า 0.15 มิลลิวินาที และใช้หน่วยความจำ RAM ต่ำกว่า 10 กิโลไบต์

---

## 2.6 งานวิจัยที่เกี่ยวข้องระดับสากลและกรอบแนวคิดการวิจัย

### 2.6.1 งานวิจัยที่เกี่ยวข้อง
การประยุกต์ใช้เทคนิคสเปกโทรสโกปีร่วมกับปัญญาประดิษฐ์ได้รับการศึกษาและพิสูจน์ประสิทธิภาพอย่างกว้างขวางในระดับนานาชาติ

Shin, Lee, และ Park (2025) ได้ทำการศึกษาการประเมินคุณสมบัติดินหลายชนิดพร้อมกันด้วยเทคนิค Vis-NIR Spectroscopy ร่วมกับแบบจำลอง Machine Learning พบว่าสเปกตรัมในย่าน 400 ถึง 1000 นาโนเมตร มีความสัมพันธ์อย่างมีนัยสำคัญกับปริมาณอินทรียวัตถุและไนโตรเจนในดิน โดยให้ค่า $R^2$ สูงกว่า 0.85 แต่ได้ชี้ให้เห็นว่าเครื่องสเปกโตรมิเตอร์มาตรฐานมีราคาแพงมากและไม่เหมาะสำหรับการพกพาไปใช้งานภาคสนาม

Folorunso และคณะ (2025) ได้พัฒนาเครื่องมือบนสมาร์ทโฟนชื่อ GeaGrow สำหรับทำนายธาตุอาหารในดินและการจัดการปุ๋ยโดยใช้โครงข่ายประสาทเทียม ซึ่งยืนยันว่าการประมวลผลข้อมูลผ่านแอปพลิเคชันสมาร์ทโฟนมีความเป็นไปได้สูงในการเพิ่มประสิทธิภาพการจัดการปุ๋ยของเกษตรกรรายย่อย

Mondal และคณะ (2025) ได้ทำการเปรียบเทียบแบบจำลอง Machine Learning ชนิดต่างๆ ในการทำนายธาตุอาหารในดิน และพบว่าแบบจำลองที่ไม่เป็นเชิงเส้น เช่น ANN และ SVR ให้ความแม่นยำเหนือกว่าแบบจำลองการถดถอยเชิงเส้นอย่างชัดเจน โดยเฉพาะอย่างยิ่งเมื่อต้องรับมือกับดินที่มีความแปรปรวนสูง

Kılıç และคณะ (2018) ได้ทำการวิเคราะห์เชิงลึกเกี่ยวกับข้อจำกัดของการใช้กล้องสมาร์ทโฟนในการตรวจวัดคุณภาพน้ำและสารละลายเชิงสี โดยชี้ให้เห็นว่าความแปรปรวนของแสงแวดล้อมภายนอกและลักษณะเฉพาะของเซนเซอร์กล้องแต่ละรุ่นเป็นสาเหตุหลักของความคลาดเคลื่อน และได้เสนอแนะการใช้กล่องควบคุมสภาพแสงร่วมกับการปรับเทียบด้วยแผ่นสีอ้างอิงเพื่อแก้ปัญหานี้ตั้งแต่ต้นทาง

นอกจากนี้ งานวิจัยของ Chewa Thassana และคณะ (2023) ที่ได้ศึกษาคุณสมบัติการสะท้อนแสงของสารละลายแอมโมเนียมคลอไรด์ด้วยกล่องสมองกลฝังตัว ได้วางรากฐานการออกแบบระบบกำเนิดแสงแบบพัลส์และการประมวลผลสัญญาณสะท้อนแสงในระดับห้องปฏิบัติการ ซึ่งคณะผู้วิจัยได้นำมาต่อยอดสู่การตรวจวัดดินจริงในโครงการนี้

### 2.6.2 กรอบแนวคิดการวิจัย (Conceptual Framework)

```
+-----------------------------------------------------------------------------------+
|                           กรอบแนวคิดการวิจัย (Conceptual Framework)                |
+-----------------------------------------------------------------------------------+
|                                                                                   |
|  [ ปัจจัยนำเข้า (Input) ]                                                          |
|  * ตัวอย่างดินสวนทุเรียน 50 ตัวอย่าง (จันทบุรี-ตราด)                              |
|  * ลำแสงกระตุ้น 6 แถบคลื่น (465, 525, 660, 720, 850, 940 nm)                      |
|  * ข้อมูลวิเคราะห์อ้างอิงแล็บ: Total N (Kjeldahl), Available P (Bray II)          |
|                                                                                   |
|                                         |                                         |
|                                         v                                         |
|                                                                                   |
|  [ กระบวนการดำเนินงาน (Process) ]                                                  |
|  1. ฮาร์ดแวร์ทัศนศาสตร์: Dark Chamber ควบคุมแสง 100% + Sequential LED Driver      |
|  2. ทัศนศาสตร์ฟิสิกส์: Diffuse Reflectance Calibration + Kubelka-Munk F(R)        |
|  3. การเตรียมข้อมูลสเปกตรัม: SNV Normalization, Scatter Correction                |
|  4. การพัฒนาแบบจำลอง AI: Multi-wavelength ANN (MLP) & SVR (RBF)                   |
|  5. การบีบอัดโมเดลสู่ Edge TinyML C++ บน ESP32-S3 / Smartphone UI                 |
|                                                                                   |
|                                         |                                         |
|                                         v                                         |
|                                                                                   |
|  [ ผลผลิตและผลลัพธ์ (Output & Outcome) ]                                           |
|  * ชุดวิเคราะห์ N และ P แบบพกพาต้นทุนต่ำ ไม่ใช้สารเคมี                            |
|  * ค่าความแม่นยำสูง: R² >= 0.88 (N), R² >= 0.85 (P), Bias < 5%, %RSD < 5%        |
|  * ผลการวิเคราะห์สอดคล้องกับวิธีมาตรฐานทางเคมี (Paired t-test, p > 0.05)          |
|  * ระบบแนะนำปุ๋ยอัจฉริยะ ช่วยลดต้นทุนเกษตรกร 15 - 25%                             |
|                                                                                   |
+-----------------------------------------------------------------------------------+
```

---

## 2.7 การวิเคราะห์เคมีดินด้วยแถบสีเทียบเคียงและข้อจำกัดเชิงทัศนศาสตร์

### 2.7.1 มาตรฐานชุดตรวจสอบดินภาคสนามเชิงสี (Colorimetric Soil Test Kits)
ในระบบเกษตรกรรมภาคสนามและงานส่งเสริมการเกษตรของประเทศไทย เกษตรกรและนักวิชาการเกษตรนิยมใช้ชุดตรวจสอบดินภาคสนาม (Soil Test Kit) ในการประเมินสถานะความอุดมสมบูรณ์ของดินเบื้องต้น เนื่องจากมีความสะดวก รวดเร็ว และทราบผลได้ทันทีในแปลงปลูก โดยชุดตรวจสอบที่ได้รับการยอมรับและอ้างอิงอย่างแพร่หลาย ได้แก่ ชุดตรวจสอบดินของกลุ่มวิจัยและพัฒนาการจัดการดินและปุ๋ย กรมพัฒนาที่ดิน กระทรวงเกษตรและสหกรณ์ (Land Development Department หรือ LDD) และชุดตรวจสอบดินมาตรฐานสากล LaMotte Combination Soil Testing Outfits (อาทิ Model STH Series และ Model 5934) ซึ่งอ้างอิงระเบียบวิธีวิเคราะห์ตามมาตรฐานของสมาคมวิทยาศาสตร์ทางดินแห่งสหรัฐอเมริกา (Soil Science Society of America หรือ SSSA) ตลอดจนชุดทดสอบ Rapitest Soil Test Kit

ชุดตรวจสอบดังกล่าวอาศัยหลักการเทียบเคียงสี (Colorimetry) โดยการสกัดธาตุอาหารออกจากตัวอย่างดินด้วยน้ำยาสกัดเฉพาะ จากนั้นทำปฏิกิริยากับสารทำปฏิกิริยาเคมี (Chromogenic Reagents) เพื่อให้เกิดสารประกอบที่มีสี แล้วนำหลอดทดลองมาเปรียบเทียบความเข้มหรือเฉดสีด้วยสายตากับแผ่นแถบสีมาตรฐาน (Color Comparison Chart) ที่จัดพิมพ์มาพร้อมกับชุดทดสอบ

### 2.7.2 กลไกปฏิกิริยาเคมีวิเคราะห์และการเกิดสี (Chemical Reaction Mechanisms)
การเกิดสีของสารละลายทดสอบในแต่ละพารามิเตอร์ เป็นผลมาจากปฏิกิริยาเคมีวิเคราะห์จำเพาะ ดังนี้

1. **ความเป็นกรด-ด่างของดิน (Soil pH)**
   อาศัยปฏิกิริยาสมดุลของสารละลายอินดิเคเตอร์ผสมช่วงกว้าง (Wide-range Mixed Acid-Base Indicators) ซึ่งประกอบด้วยโบรโมครีซอลกรีน (Bromocresol Green) เมทิลเรด (Methyl Red) และโบรโมไทมอลบลู (Bromothymol Blue) เกิดการเปลี่ยนสีตามความเข้มข้นของไฮโดรเจนไอออนในสารละลายดินตามสมการ
   $$\text{HIn} \rightleftharpoons \text{H}^+ + \text{In}^-$$
   สารละลายจะแสดงสีแดงส้มในสภาวะกรดจัดรุนแรง ($\text{pH} < 4.5$) และค่อยๆ เปลี่ยนเป็นสีส้มอมเหลือง ($\text{pH } 4.5 - 5.2$) สีเหลืองอมเขียว ($\text{pH } 5.3 - 6.0$) สีเขียวมรกตในดินที่มีค่าเป็นกลาง ($\text{pH } 6.5 - 7.5$) จนถึงสีน้ำเงินอมม่วงเข้มในสภาวะดินด่าง ($\text{pH} > 8.0$)

2. **ไนโตรเจนที่เป็นประโยชน์ในรูปไนเตรต ($\text{NO}_3^--\text{N}$)**
   อาศัยปฏิกิริยากรีสส์ประยุกต์ (Modified Griess Reaction หรือ Zinc Reduction Method) โดยในขั้นแรกผงโลหะสังกะสี ($\text{Zn}$) จะทำหน้าที่รีดิวซ์ไนเตรตไอออนในสารละลายสกัดให้เปลี่ยนเป็นไนไตรต์ไอออน ($\text{NO}_2^-$) ภายใต้สภาวะกรด จากนั้นไนไตรต์จะทำปฏิกิริยาไดอะโซไทเซชัน (Diazotization) กับกรดซัลฟานิลิก (Sulfanilic Acid) เกิดเป็นเกลือไดอะโซเนียม และทำปฏิกิริยาคัปปลิง (Azo Coupling) กับสาร N-(1-Naphthyl)ethylenediamine dihydrochloride (NED) เกิดเป็นสีย้อมเอโซ (Azo Dye) สีชมพูแดง ซึ่งมีแถบดูดกลืนแสงสูงสุดที่ความยาวคลื่นประมาณ 540 นาโนเมตร ดังสมการเคมี
   $$\text{NO}_3^- + \text{Zn} + 2\text{H}^+ \longrightarrow \text{NO}_2^- + \text{Zn}^{2+} + \text{H}_2\text{O}$$
   $$\text{NO}_2^- + \text{Ar-NH}_2 + 2\text{H}^+ \longrightarrow [\text{Ar-N}^+\equiv\text{N}] + 2\text{H}_2\text{O}$$
   $$[\text{Ar-N}^+\equiv\text{N}] + \text{Ar}'\text{-NH(CH}_2)_2\text{NH}_2 \longrightarrow \text{Ar-N=N-Ar}'\text{-NH(CH}_2)_2\text{NH}_2$$
   ความเข้มของสีชมพูแดงจะแปรผันตรงตามความเข้มข้นของไนเตรต โดยดินที่มีไนโตรเจนต่ำมากจะแสดงสารละลายใสหรือสีเหลืองจาง ขณะที่ดินที่มีไนโตรเจนสูงมากจะแสดงสีแดงอมม่วงเข้ม

3. **ฟอสฟอรัสที่เป็นประโยชน์ (Available Phosphorus)**
   อาศัยปฏิกิริยาโมลิบดีนัมบลู (Molybdenum Blue Method ร่วมกับวิธีสกัด Bray II) โดยออร์โธฟอสเฟตไอออน ($\text{H}_2\text{PO}_4^-$) ทำปฏิกิริยากับแอมโมเนียมโมลิบเดต $[(\text{NH}_4)_6\text{Mo}_7\text{O}_{24}]$ และโพแทสเซียมแอนติโมนีลทาร์เทรตในสารละลายกรดซัลฟิวริก เกิดเป็นกรดฟอสโฟโมลิบดิก จากนั้นถูกรีดิวซ์ด้วยกรดแอสคอร์บิก (Ascorbic Acid) เกิดเป็นสารประกอบเชิงซ้อนเฮเทอโรโพลีแอนไอออนสีน้ำเงินเข้ม (Phosphomolybdenum Blue Complex) ที่มีแถบดูดกลืนแสงสูงสุดที่ 660 นาโนเมตร และ 882 นาโนเมตร ดังสมการเคมี
   $$\text{H}_2\text{PO}_4^- + 12\text{MoO}_4^{2-} + 22\text{H}^+ \longrightarrow [\text{H}_2\text{P}(\text{Mo}_{12}\text{O}_{40})]^{-} + 10\text{H}_2\text{O}$$
   $$[\text{H}_2\text{P}(\text{Mo}_{12}\text{O}_{40})]^{-} + \text{Ascorbic Acid} \longrightarrow \text{Molybdenum Blue Complex}$$
   เฉดสีของสารละลายจะเปลี่ยนจากสีเหลืองใสอมเขียวจางในระดับต่ำมาก สู่สีฟ้าสว่างในระดับปานกลาง และสีน้ำเงินเข้มมิดไนท์บลูในระดับสูงมาก

4. **โพแทสเซียมที่แลกเปลี่ยนได้ (Exchangeable Potassium)**
   อาศัยปฏิกิริยาการตกตะกอนด้วยโซเดียมเตตระฟีนิลโบรอน (Sodium Tetraphenylboron Method) หรือโซเดียมโคบอลตินิไตรต์ (Sodium Cobaltinitrite Method) โดยโพแทสเซียมไอออน ($\text{K}^+$) ทำปฏิกิริยากับไอออนเตตระฟีนิลโบรอนเกิดเป็นตะกอนสีขาวขุ่น หรือทำปฏิกิริยากับโคบอลตินิไตรต์เกิดเป็นสารแขวนลอยสีส้มอำพันขุ่นทึบแสง ดังสมการเคมี
   $$\text{K}^+ + [\text{B}(\text{C}_6\text{H}_5)_4]^- \longrightarrow \text{KB}(\text{C}_6\text{H}_5)_4 \downarrow$$
   $$2\text{K}^+ + \text{Na}^+ + [\text{Co}(\text{NO}_2)_6]^{3-} \longrightarrow \text{K}_2\text{Na}[\text{Co}(\text{NO}_2)_6] \downarrow$$
   ระดับความขุ่นและการบดบังแสงจะเพิ่มขึ้นตามความเข้มข้นของโพแทสเซียมในดิน

### 2.7.3 ตารางเปรียบเทียบเกณฑ์มาตรฐานระดับคุณภาพและช่วงความเข้มข้นเชิงปริมาณ
การแปลงผลการประเมินเชิงคุณภาพจากแถบสีเทียบมาตรฐานสู่ค่าเชิงปริมาณที่มีหน่วยวิศวกรรมสากล อาศัยเกณฑ์มาตรฐานของกรมพัฒนาที่ดิน (LDD Thailand) และมาตรฐานสากล SSSA ดังแสดงในตารางที่ 2.3

**ตารางที่ 2.3 เกณฑ์มาตรฐานแถบสีเทียบเคียงและช่วงความเข้มข้นเชิงปริมาณของธาตุอาหารในดิน NPK และ pH**

| พารามิเตอร์ | ระดับคุณภาพดิน (Tier) | ช่วงค่าเชิงปริมาณ | มาตรฐานอ้างอิง | เฉดสีทางเคมีวิเคราะห์ | รหัสสีดิจิทัล (HEX) |
| :--- | :--- | :---: | :--- | :--- | :---: |
| **ความเป็นกรด-ด่าง** | กรดจัดรุนแรง (Extremely Acid) | $< 4.5\text{ pH}$ | LDD / USDA | แดงส้มสดใส (Red-Orange) | `#e63946` |
| (Soil pH) | กรดจัด (Very Strongly Acid) | $4.5 - 5.2\text{ pH}$ | LDD / USDA | ส้มอมเหลือง (Orange-Amber) | `#f4a261` |
| | กรดปานกลาง (Moderately Acid) | $5.3 - 6.0\text{ pH}$ | LDD / USDA | เหลืองอมเขียว (Yellow-Green) | `#e9c46a` |
| | เป็นกรดเล็กน้อย (Slightly Acid) | $6.1 - 6.8\text{ pH}$ | LDD / USDA | เขียวมะนาวอ่อน (Light Lime) | `#a7c957` |
| | เป็นกลาง (Neutral - เหมาะสม) | $6.9 - 7.5\text{ pH}$ | LDD / USDA | เขียวมรกตธรรมชาติ (Emerald) | `#2a9d8f` |
| | ด่างปานกลาง (Moderately Alkaline) | $7.6 - 8.4\text{ pH}$ | LDD / USDA | ฟ้าครามแกมเขียว (Cyan-Teal) | `#457b9d` |
| | ด่างรุนแรง (Strongly Alkaline) | $> 8.4\text{ pH}$ | LDD / USDA | น้ำเงินม่วงเข้ม (Deep Indigo) | `#1d3557` |
| **ไนโตรเจนที่ใช้ประโยชน์** | ต่ำมาก (Depleted / Very Low) | $< 10\text{ mg/kg}$ | LDD / LaMotte STH | เหลืองซีดโปร่งใส (Pale Yellow) | `#fefae0` |
| ($\text{NO}_3^--\text{N}$) | ต่ำ (Deficient / Low) | $10 - 25\text{ mg/kg}$ | LDD / LaMotte STH | ชมพูโอลด์โรสอ่อน (Light Coral) | `#f4a261` |
| | ปานกลาง (Adequate / Medium) | $26 - 50\text{ mg/kg}$ | LDD / LaMotte STH | ชมพูสดใส (Vibrant Pink) | `#e76f51` |
| | สูง (Sufficient / High) | $51 - 80\text{ mg/kg}$ | LDD / LaMotte STH | แดงกุหลาบสด (Rose Red) | `#d62828` |
| | สูงมาก (Surplus / Very High) | $> 80\text{ mg/kg}$ | LDD / LaMotte STH | ม่วงแดงมาเจนต้าเข้ม (Deep Magenta) | `#7209b7` |
| **ฟอสฟอรัสที่เป็นประโยชน์** | ต่ำมาก (Depleted / Very Low) | $< 5\text{ mg/kg}$ | LDD Bray II / SSSA | เหลืองใสอมเขียวจาง (Pale Clear) | `#faf0ca` |
| (Available P) | ต่ำ (Deficient / Low) | $5 - 15\text{ mg/kg}$ | LDD Bray II / SSSA | ฟ้าอ่อนใส (Pale Sky Blue) | `#a2d2ff` |
| | ปานกลาง (Adequate / Medium) | $16 - 30\text{ mg/kg}$ | LDD Bray II / SSSA | ฟ้าครามมิดเดิลบลู (Cyan Blue) | `#3a86ff` |
| | สูง (Sufficient / High) | $31 - 60\text{ mg/kg}$ | LDD Bray II / SSSA | น้ำเงินเข้มรอยัลบลู (Royal Blue) | `#003049` |
| | สูงมาก (Surplus / Very High) | $> 60\text{ mg/kg}$ | LDD Bray II / SSSA | น้ำเงินมิดไนท์บลู (Midnight Navy) | `#03045e` |
| **โพแทสเซียมที่แลกเปลี่ยนได้** | ต่ำมาก (Depleted / Very Low) | $< 40\text{ mg/kg}$ | LDD / SSSA | สารละลายใสไร้ตะกอน (Clear) | `#edf2f4` |
| (Exchangeable K) | ต่ำ (Deficient / Low) | $40 - 80\text{ mg/kg}$ | LDD / SSSA | ขุ่นมัวฝ้าจางๆ (Hazy Amber) | `#ffd166` |
| | ปานกลาง (Adequate / Medium) | $81 - 150\text{ mg/kg}$ | LDD / SSSA | ขุ่นส้มทองคำ (Golden Orange) | `#f3722c` |
| | สูง (Sufficient / High) | $151 - 250\text{ mg/kg}$ | LDD / SSSA | ตะกอนส้มแดงขุ่น (Dense Orange) | `#d90429` |
| | สูงมาก (Surplus / Very High) | $> 250\text{ mg/kg}$ | LDD / SSSA | ตะกอนทึบแสงหนาแน่น (Opaque) | `#6a040f` |

### 2.7.4 ข้อจำกัดของการอ่านแถบสีด้วยสายตามนุษย์และที่มาของการพัฒนาระบบทัศนศาสตร์ออปติคอล
แม้ว่าชุดทดสอบดินทางเคมีแบบแถบสีจะมีประโยชน์อย่างยิ่งในการประเมินระดับธาตุอาหารภาคสนาม แต่การใช้งานจริงยังคงประสบกับข้อจำกัดทางวิทยาศาสตร์ 4 ประการ ได้แก่

1. **ความแปรปรวนจากสายตาและอัตวิสัยของผู้ประเมิน (Subjectivity and Eye Fatigue)** ความสามารถในการแยกแยะเฉดสีของมนุษย์มีความแตกต่างกันในแต่ละบุคคล และเมื่อต้องตรวจวัดตัวอย่างจำนวนมากในแปลงเกษตรกรรม สายตาจะเกิดอาการล้า ส่งผลให้เกิดความคลาดเคลื่อนในการจำแนกระดับคุณภาพดิน โดยเฉพาะตัวอย่างที่ตกอยู่บริเวณรอยต่อของสองระดับสี
2. **ผลกระทบจากความเข้มและอุณหภูมิสีของแสงแวดล้อม (Ambient Lux and Metamerism)** การอ่านแถบสีภายใต้สภาพแสงธรรมชาติที่แตกต่างกัน เช่น แสงแดดจัดช่วงเที่ยงวัน แสงร่มเงาใต้ต้นไม้ หรือแสงยามเย็น จะทำให้สเปกตรัมของแสงสะท้อนเปลี่ยนไป (Metameric Failure) ส่งผลให้เฉดสีที่ตามองเห็นบิดเบือนไปจากความเป็นจริง
3. **การใช้สารเคมีอันตรายและของเสียปนเปื้อน (Hazardous Chemical Waste)** การทดสอบทางเคมีทุกครั้งต้องใช้กรดแก่ ตัวทำละลาย และสารเชื่อมไดอะโซ ซึ่งมีความเป็นพิษต่อผู้ใช้งานและจำเป็นต้องมีระบบกำจัดของเสียสารเคมีที่ถูกต้องเพื่อไม่ให้ปนเปื้อนสู่แปลงเกษตรกรรม
4. **การขาดข้อมูลเชิงปริมาณความละเอียดสูง (Lack of Continuous Quantitative Values)** แถบสีสามารถบอกได้เพียงช่วงกว้างเชิงกลุ่ม (Categorical Range) เช่น "ต่ำ" หรือ "ปานกลาง" แต่ไม่สามารถระบุค่าตัวเลขความเข้มข้นที่แม่นยำในหน่วย $\text{mg/kg}$ ได้ ทำให้ไม่สามารถนำไปคำนวณปริมาณปุ๋ยเคมีรายต้นตามหลักการเกษตรแม่นยำสูง (Variable Rate Fertilization) ได้อย่างสมบูรณ์

ข้อจำกัดข้างต้นจึงเป็นแรงขับเคลื่อนสำคัญที่นำไปสู่โจทย์วิจัยในการออกแบบชุดวิเคราะห์ที่ใช้ **หลักการสะท้อนแสงแบบกระจาย (Diffuse Reflectance) ภายในกล่องควบคุมสภาพแสงระบบปิด (Optical Dark Chamber)** ร่วมกับการกระตุ้นแสงหลายความยาวคลื่น และการใช้ **แบบจำลองปัญญาประดิษฐ์ (Artificial Intelligence)** เพื่อทำนายปริมาณธาตุอาหารออกมาเป็นค่าตัวเลขเชิงปริมาณที่แม่นยำเทียบเท่าห้องปฏิบัติการ พร้อมทั้งสามารถสร้างแถบสีดิจิทัลมาตรฐาน (Digital Color Badge Chip) แสดงผลคู่ขนานกันได้อย่างมีประสิทธิภาพ

\newpage

# บทที่ 3
# วิธีดำเนินการวิจัย

การวิจัยเรื่องการพัฒนาชุดวิเคราะห์ปริมาณไนโตรเจนและฟอสฟอรัสในดินแบบพกพาด้วยหลักการสะท้อนแสงร่วมกับปัญญาประดิษฐ์ เป็นการวิจัยเชิงทดลองและพัฒนานวัตกรรม (Experimental and Developmental Research) ที่บูรณาการหลักการทางทัศนศาสตร์ฟิสิกส์ วิศวกรรมสมองกลฝังตัว เคมีวิเคราะห์ และปัญญาประดิษฐ์ เพื่อสร้างเครื่องมือตรวจวัดดินภาคสนามที่แม่นยำและใช้งานได้จริง โดยมีขั้นตอนการดำเนินการวิจัย 5 ขั้นตอนหลัก ได้แก่

1. การออกแบบและสร้างระบบฮาร์ดแวร์ต้นแบบและกล่องควบคุมสภาพแสง (Optical Dark Chamber)
2. การเก็บตัวอย่างดินและการวิเคราะห์ค่าอ้างอิงมาตรฐานในห้องปฏิบัติการ
3. การตรวจวัดสเปกตรัมการสะท้อนแสงและการประมวลผลสัญญาณเคมีเมตริกส์
4. การพัฒนาและฝึกสอนแบบจำลองปัญญาประดิษฐ์และการแปลงสู่ระบบสมองกลฝังตัว (Edge TinyML)
5. ระเบียบวิธีการตรวจสอบความใช้ได้ของวิธีและสถิติทดสอบสมมติฐาน

---

## 3.1 การออกแบบและสร้างระบบฮาร์ดแวร์ต้นแบบและกล่องควบคุมสภาพแสง

### 3.1.1 โครงสร้างกล่องวัดแบบทึบแสง (Optical Dark Chamber)
เพื่อขจัดสัญญาณรบกวนจากความผันผวนของแสงแวดล้อมภายนอก (Ambient Light) อย่างสมบูรณ์ คณะผู้วิจัยได้ออกแบบโครงสร้างกล่องวัดแบบทึบแสงด้วยโปรแกรมคอมพิวเตอร์ช่วยออกแบบเชิงวิศวกรรม (Computer-Aided Design หรือ CAD) และขึ้นรูปชิ้นงานด้วยเครื่องพิมพ์สามมิติ (3D Printing) โดยใช้วัสดุเส้นใยพอลิเมอร์ชนิด PETG (Polyethylene Terephthalate Glycol) ซึ่งมีคุณสมบัติทนทานต่อแรงกระแทก ไม่บิดงอในสภาพอากาศร้อน และทนต่อความชื้นในแปลงเกษตรกรรม

กล่องตรวจวัดมีขนาดกะทัดรัด 120 x 80 x 65 มิลลิเมตร น้ำหนักรวมไม่เกิน 380 กรัม เหมาะสำหรับการพกพา ภายในกล่องได้รับการออกแบบตามหลักทัศนศาสตร์ โดยประกอบด้วยส่วนประกอบสำคัญดังนี้

1. **ผิวเคลือบดูดกลืนแสง (Matt Black Anti-reflective Coating)** ผนังภายในกล่องทั้งหมดได้รับการเคลือบด้วยสารดูดกลืนแสงสีดำด้านชนิดพิเศษที่มีค่าการสะท้อนแสงผิวน้อยกว่าร้อยละ 1 เพื่อป้องกันการเกิดแสงสะท้อนภายในหลายชั้น (Internal Stray Light)
2. **แผ่นกั้นดักแสง (Optical Light-trap Baffles)** ติดตั้งรอบบริเวณขอบฝาเปิด-ปิดและช่องบรรจุถาดตัวอย่าง เพื่อป้องกันแสงจากภายนอกเล็ดลอดเข้ามาในระหว่างการตรวจวัด
3. **ถาดบรรจุตัวอย่างดินมาตรฐาน (Standard Soil Sample Holder)** ทำจากวัสดุอะคริลิกสีดำ มีขนาดเส้นผ่านศูนย์กลาง 35 มิลลิเมตร ลึก 8 มิลลิเมตร สามารถบรรจุตัวอย่างดินได้ปริมาตรคงที่ 7.5 ลูกบาศก์เซนติเมตร และจัดวางในตำแหน่งกึ่งกลางระนาบแสงตกกระทบพอดี
4. **แท่นยึดสมาร์ทโฟนและโมดูลตรวจวัดเชิงแสง** ออกแบบให้สามารถติดตั้งสมาร์ทโฟนหรือโมดูลตรวจวัดออปติคอลได้อย่างมั่นคง โดยมีระยะห่างทางทัศนศาสตร์จากเลนส์ถึงพื้นผิวตัวอย่างดินคงที่ 50 มิลลิเมตร และทำมุมตกกระทบของแสง 45 องศา เพื่อลดการสะท้อนแบบกระจกเงา (Specular Reflection) และรับเฉพาะแสงสะท้อนแบบกระจาย (Diffuse Reflection) ในแนวตั้งฉาก (มุม 0 องศา)

### 3.1.2 แหล่งกำเนิดแสงไดโอดเปล่งแสงหลายความยาวคลื่น (Multi-wavelength LED Array)
แหล่งกำเนิดแสงได้รับการออกแบบเป็นชุดไดโอดเปล่งแสง (LED Array) ติดตั้งรอบเลนส์รับแสงในลักษณะวงแหวน (Ring Geometry) เพื่อให้การกระจายความเข้มแสงตกกระทบลงบนพื้นผิวตัวอย่างดินมีความสม่ำเสมอเชิงพื้นที่ (Spatial Illumination Uniformity) โดยคัดเลือกความยาวคลื่นกึ่งกลาง (Peak Wavelength) จำนวน 6 ย่านคลื่นที่มีแถบสเปกตรัมสัมพันธ์กับพันธะเคมีของไนโตรเจน ฟอสฟอรัส และความชื้นในดิน ดังตารางที่ 3.1

**ตารางที่ 3.1 คุณลักษณะเฉพาะของแถบความยาวคลื่นแสงในระบบ Multi-wavelength LED Array**

| ลำดับที่ | แถบสีของแสง | ความยาวคลื่นกึ่งกลาง ($\lambda_{\text{peak}}$, nm) | ความกว้างครึ่งคลื่น (FWHM, nm) | อันตรกิริยาและวัตถุประสงค์ในการตรวจวัด |
| :---: | :--- | :---: | :---: | :--- |
| 1 | น้ำเงิน (Blue) | 465 | 20 | การดูดกลืนแสงของสารประกอบฮิวมิกและอินทรียวัตถุ (ไนโตรเจนอินทรีย์) |
| 2 | เขียว (Green) | 525 | 25 | การดูดกลืนและถ่ายโอนประจุของสารประกอบเชิงซ้อนเหล็กฟอสเฟต |
| 3 | แดง (Red) | 660 | 20 | แถบดูดกลืนสารอนุพันธ์คลอโรฟิลล์และความชันสเปกตรัมดิน |
| 4 | เรดเอจ (Red-Edge) | 720 | 22 | แถบรอยต่อการเปลี่ยนระดับพลังงานอิเล็กตรอนของแร่ธาตุในดิน |
| 5 | ใกล้อินฟราเรด (NIR-1) | 850 | 30 | โอเวอร์โทนการสั่นของพันธะ $\text{N-H}$ และ $\text{C-H}$ ในหมู่อะมิโน |
| 6 | ใกล้อินฟราเรด (NIR-2) | 940 | 35 | แถบดูดกลืนพันธะ $\text{O-H}$ ของน้ำ (ใช้อ้างอิงชดเชยความชื้นในดิน) |

### 3.1.3 วงจรควบคุมการกระตุ้นแสงตามลำดับ (Sequential LED Driver Circuit)
ไดโอดเปล่งแสงทั้ง 6 แถบคลื่น ถูกควบคุมผ่านวงจรจ่ายกระแสคงที่ (Constant Current Source Driver) ที่ควบคุมด้วยสัญญาณพัลส์ (Pulse Width Modulation หรือ PWM) จากไมโครคอนโทรลเลอร์ ESP32-S3 โดยโปรแกรมควบคุมจะสั่งให้ LED แต่ละแถบความยาวคลื่นติดสว่างทีละดวงตามลำดับ (Sequential Pulse) ดวงละ 100 มิลลิวินาที สลับกับช่วงกระแสมืด (Dark Interval) 50 มิลลิวินาที ทำให้ระบบสามารถบันทึกค่าความเข้มแสงสะท้อนที่แยกแยะแต่ละความยาวคลื่นได้อย่างเด็ดขาด ปราศจากการรบกวนข้ามแถบคลื่น (Optical Crosstalk) พร้อมทั้งช่วยป้องกันความร้อนสะสมในหลอด LED ซึ่งอาจทำให้ค่าความยาวคลื่นเคลื่อนตัว (Thermal Drift)

---

## 3.2 การเก็บตัวอย่างดินและการวิเคราะห์ค่าอ้างอิงมาตรฐานในห้องปฏิบัติการ

### 3.2.1 พื้นที่และระเบียบวิธีการเก็บตัวอย่างดินภาคสนาม
การเก็บตัวอย่างดินดำเนินการในพื้นที่แปลงเพาะปลูกทุเรียนเศรษฐกิจในเขตจังหวัดจันทบุรีและจังหวัดตราด จำนวนรวมทั้งสิ้น 50 แปลง ครอบคลุมพื้นที่ที่มีประวัติการจัดการปุ๋ย ชนิดของชุดดิน และสภาพความอุดมสมบูรณ์ที่หลากหลาย ได้แก่

1. อำเภอมะขาม จังหวัดจันทบุรี (ชุดดินห้วยโป่งและชุดดินท่าใหม่) จำนวน 20 ตัวอย่าง
2. อำเภอท่าใหม่ จังหวัดจันทบุรี (ชุดดินท่าใหม่) จำนวน 15 ตัวอย่าง
3. อำเภอเขาสมิง จังหวัดตราด (ชุดดินเขาสมิง) จำนวน 15 ตัวอย่าง

ระเบียบวิธีการเก็บตัวอย่างดินใช้เทคนิคการสุ่มแบบตารางกริด (Grid Sampling Method) โดยกำหนดพื้นที่เก็บตัวอย่างขนาด $10 \times 10$ เมตร ภายใต้ทรงพุ่มของต้นทุเรียนที่มีอายุตั้งแต่ 5 ถึง 15 ปี ทำการเก็บดินย่อย 5 จุดต่อแปลง (จุดกึ่งกลางและมุมทั้งสี่) ที่ระดับความลึก 0 ถึง 15 เซนติเมตร ซึ่งเป็นเขตรากดูดซับธาตุอาหารหลัก (Active Root Zone) นำดินย่อยทั้ง 5 จุดมาคลุกเคล้าให้เข้ากันเป็นตัวอย่างรวม (Composite Sample) หนักประมาณ 1 กิโลกรัม บันทึกพิกัดภูมิศาสตร์ (GPS Coordinates) สภาพความชื้นเบื้องต้น และประเภทพืช จากนั้นบรรจุลงในถุงพลาสติกพอลิเอทิลีนปิดสนิทและติดรหัสตัวอย่างอย่างเป็นระบบ

### 3.2.2 การเตรียมตัวอย่างดินก่อนการตรวจวัด
ตัวอย่างดินที่เก็บมาจากภาคสนามจะถูกนำมาเตรียมตามระเบียบวิธีสากล ณ ห้องปฏิบัติการฟิสิกส์ประยุกต์ ดังนี้

1. นำดินตัวอย่างมาแผ่กระจายบนถาดพลาสติกสะอาดและผึ่งลมให้แห้งที่อุณหภูมิห้อง ($25 \pm 2$ องศาเซลเซียส) ในห้องที่มีอากาศถ่ายเทสะดวกและไม่มีแสงแดดส่องถึงโดยตรง เป็นเวลา 48 ถึง 72 ชั่วโมง จนดินแห้งสนิท (Air-dried Soil)
2. นำดินที่แห้งแล้วมาบดย่อยอนุภาคอย่างนุ่มนวลด้วยโกร่งกระเบื้องเพื่อแยกเม็ดดินโดยไม่ทำลายโครงสร้างเม็ดแร่
3. ร่อนดินผ่านตะแกรงสแตนเลสมาตรฐานขนาดช่องเปิด 2.0 มิลลิเมตร เพื่อคัดแยกเศษหิน กรวด และซากอินทรีย์ขนาดใหญ่ออก เม็ดดินที่มีขนาดอนุภาคสม่ำเสมอต่ำกว่า 2 มิลลิเมตร จะถูกนำไปบรรจุในขวดแก้วสีชาเพื่อใช้ในการตรวจวัดเชิงแสงและส่งวิเคราะห์ทางเคมี

### 3.2.3 การวิเคราะห์ค่าอ้างอิงมาตรฐานในห้องปฏิบัติการ (Ground Truth Reference Analysis)
ตัวอย่างดินที่ผ่านการเตรียมแล้วจะถูกแบ่งออกเป็น 2 ส่วน โดยส่วนที่หนึ่งนำไปวิเคราะห์ค่ามาตรฐานทางเคมีในห้องปฏิบัติการวิเคราะห์ดินที่ได้รับการรับรองมาตรฐาน ISO/IEC 17025 ดังนี้

1. **การวิเคราะห์ปริมาณไนโตรเจนทั้งหมด (Total Nitrogen)** วิเคราะห์ด้วยวิธีไมโครเคจ์ลดาห์ล (Micro-Kjeldahl Method) ตามมาตรฐานสากล AOAC 978.02 ซึ่งประกอบด้วย 3 ขั้นตอนย่อย ได้แก่ การย่อยสลายตัวอย่างดินด้วยกรดซัลฟิวริกเข้มข้น ($\text{H}_2\text{SO}_4$) ร่วมกับตัวเร่งปฏิกิริยาคอปเปอร์ซัลเฟตและโพแทสเซียมซัลเฟตที่อุณหภูมิ 420 องศาเซลเซียส จนสารอินทรีย์เปลี่ยนเป็นแอมโมเนียมซัลเฟต ต่อด้วยการกลั่นด้วยด่างโซเดียมไฮดรอกไซด์ ($\text{NaOH}$) เพื่อเปลี่ยนเป็นก๊าซแอมโมเนีย ($\text{NH}_3$) และดักจับในสารละลายกรดบอริก ($\text{H}_3\text{BO}_3$) และขั้นตอนสุดท้ายคือการไตเตรตด้วยสารละลายมาตรฐานกรดไฮโดรคลอริก ($\text{HCl}$) เพื่อคำนวณปริมาณไนโตรเจนทั้งหมด รายงานผลในหน่วยกรัมต่อกิโลกรัม (g/kg)
2. **การวิเคราะห์ปริมาณฟอสฟอรัสที่เป็นประโยชน์ (Available Phosphorus)** วิเคราะห์ด้วยวิธีเบรย์ 2 (Bray II Method) ซึ่งมีความเหมาะสมอย่างยิ่งสำหรับดินกรดในเขตร้อน โดยทำการสกัดดินด้วยสารละลายผสมระหว่างกรดไฮโดรคลอริก 0.1 นอร์มัล และแอมโมเนียมฟลูออไรด์ ($\text{NH}_4\text{F}$) 0.03 นอร์มัล จากนั้นนำสารละลายใสที่ได้มาทำปฏิกิริยากับแอมโมเนียมโมลิบเดตและโพแทสเซียมแอนติโมนิลตาร์เตรตในสารละลายกรด แล้วรีดิวซ์ด้วยกรดแอสคอร์บิกจนเกิดสารประกอบเชิงซ้อนสีน้ำเงิน (Molybdenum Blue Complex) นำไปวัดค่าการดูดกลืนแสงด้วยเครื่อง UV-Vis Spectrophotometer ที่ความยาวคลื่น 880 นาโนเมตร เทียบกับกราฟมาตรฐานฟอสฟอรัส รายงานผลในหน่วยมิลลิกรัมต่อกิโลกรัม (mg/kg หรือ ppm)

### 3.2.4 การทดสอบเปรียบเทียบเคียงคู่กับชุดตรวจสอบดินภาคสนามเชิงเคมี (Colorimetric Soil Test Kits Benchmarking)
เพื่อสร้างฐานข้อมูลเปรียบเทียบระหว่างวิธีการอ่านแถบสีทางเคมีดั้งเดิมกับการวิเคราะห์ด้วยแสงสะท้อนเชิงแสง ตัวอย่างดินทั้ง 50 ตัวอย่าง ได้ถูกนำมาทดสอบคู่ขนานด้วยชุดตรวจสอบดินภาคสนามมาตรฐาน 2 ชุด ได้แก่
1. ชุดตรวจสอบดินของกลุ่มวิจัยและพัฒนาการจัดการดินและปุ๋ย กรมพัฒนาที่ดิน (LDD Test Kit)
2. ชุดตรวจสอบดินมาตรฐานสากล LaMotte Combination Soil Testing Outfit (Model STH Series)

ผู้เชี่ยวชาญด้านปฐพีวิทยาจำนวน 3 ท่าน ได้ทำการสกัดและอ่านผลแถบสีเทียบมาตรฐานโดยอิสระจากกัน (Triple-blind Visual Reading) ภายใต้แสงสว่างมาตรฐาน CIE Standard Illuminant D65 เพื่อบันทึกระดับคุณภาพเชิงกลุ่ม (ต่ำมาก ต่ำ ปานกลาง สูง สูงมาก) และเฉดสีที่สังเกตได้ ข้อมูลดังกล่าวจะถูกนำมาใช้เป็นฐานอ้างอิงในการประเมินความสอดคล้องเชิงกลุ่ม (Categorical Agreement) และความเที่ยงตรงของการสร้างแถบสีดิจิทัลของระบบต้นแบบ

---

## 3.3 การตรวจวัดสเปกตรัมการสะท้อนแสงและการประมวลผลสัญญาณเคมีเมตริกส์

### 3.3.1 ขั้นตอนการตรวจวัดสเปกตรัมด้วยชุดต้นแบบ
นำตัวอย่างดินที่ร่อนแล้วบรรจุลงในถาดตัวอย่างดิน ปาดพื้นผิวหน้าดินให้เรียบเสมอกับขอบถาดด้วยไม้บรรทัดเหล็กอย่างระมัดระวังเพื่อให้มีความหนาแน่นและพื้นผิวที่สม่ำเสมอ บรรจุถาดตัวอย่างเข้าสู่กล่องทึบแสง ปิดฝาให้สนิท จากนั้นระบบจะดำเนินการตรวจวัดตามลำดับขั้นตอนดังนี้

1. บันทึกสัญญาณมืด ($I_{\text{dark}}$) เมื่อปิดแหล่งกำเนิดแสงทุกดวง เพื่อใช้เป็นระดับฐานศูนย์ (Baseline Offset)
2. เปิดไดโอดเปล่งแสงทีละความยาวคลื่นตามลำดับ (465, 525, 660, 720, 850 และ 940 นาโนเมตร) และบันทึกค่าความเข้มแสงสะท้อนที่ตรวจวัดได้จากตัวอย่างดิน ($I_{\text{sample}}(\lambda)$)
3. ก่อนการตรวจวัดตัวอย่างดินทุก 5 ตัวอย่าง ระบบจะทำการสอบเทียบสัญญาณอ้างอิงด้วยแผ่นเทียบสีขาวมาตรฐาน ($I_{\text{white}}(\lambda)$) เพื่อคำนวณค่าการสะท้อนแสงแบบกระจายสัมพัทธ์ (Relative Diffuse Reflectance, $R_\lambda$) ตามสมการ

$$R_\lambda = \frac{I_{\text{sample}}(\lambda) - I_{\text{dark}}(\lambda)}{I_{\text{white}}(\lambda) - I_{\text{dark}}(\lambda)}$$

### 3.3.2 การแปลงข้อมูลและการประมวลผลเคมีเมตริกส์ล่วงหน้า (Chemometrics Preprocessing)
ข้อมูลสเปกตรัมการสะท้อนแสง $R_\lambda$ จะถูกนำมาผ่านกระบวนการทางคณิตศาสตร์ 3 ขั้นตอน ได้แก่

1. **การแปลงฟังก์ชันคูเบลกา-มังก์ (Kubelka-Munk Transformation)** เพื่อเปลี่ยนค่าการสะท้อนแสงที่ไม่เป็นเชิงเส้นให้มีความสัมพันธ์เชิงสัดส่วนกับความเข้มข้นของสารดูดกลืนแสง

$$F(R_\lambda) = \frac{(1 - R_\lambda)^2}{2R_\lambda}$$

2. **การปรับมาตรฐานตัวแปรปกติ (Standard Normal Variate หรือ SNV)** ทำการปรับสเกลข้อมูลของแต่ละตัวอย่างให้มีค่าเฉลี่ยเป็น 0 และความแปรปรวนเป็น 1 เพื่อขจัดความแตกต่างของระดับความสว่างจากการจัดเรียงตัวของเม็ดดิน
3. **การชดเชยอิทธิพลของความชื้น (Moisture Compensation Ratio)** โดยการคำนวณอัตราส่วนสัมพัทธ์ของสเปกตรัมแต่ละความยาวคลื่นเทียบกับแถบดูดกลืนน้ำที่ 940 นาโนเมตร ($F(R_\lambda) / F(R_{940})$) เพื่อกำจัดผลกระทบของความชื้นสัมพัทธ์ที่ตกค้างในอนุภาคดิน

---

## 3.4 การพัฒนาและฝึกสอนแบบจำลองปัญญาประดิษฐ์และการแปลงสู่ระบบสมองกลฝังตัว

### 3.4.1 การแบ่งชุดข้อมูลสำหรับการพัฒนาแบบจำลอง (Dataset Partitioning)
ชุดข้อมูลที่ได้จากการตรวจวัดตัวอย่างดิน 50 ตัวอย่าง ที่ผ่านการประมวลผลล่วงหน้าและจับคู่กับค่าวิเคราะห์มาตรฐานทางเคมี (Total N และ Available P) จะถูกนำมาแบ่งออกเป็น 3 ชุดข้อมูลย่อยด้วยวิธีการสุ่มแบบแบ่งชั้น (Stratified Random Splitting) เพื่อให้มีการกระจายตัวของระดับความเข้มข้นธาตุอาหารอย่างสม่ำเสมอในทุกชุดข้อมูล ดังนี้

1. **ชุดข้อมูลสำหรับฝึกสอน (Training Set)** ร้อยละ 70 (จำนวน 35 ตัวอย่าง) ใช้สำหรับการปรับค่าน้ำหนักของแบบจำลอง
2. **ชุดข้อมูลสำหรับตรวจสอบ (Validation Set)** ร้อยละ 15 (จำนวน 7 หรือ 8 ตัวอย่าง) ใช้สำหรับการตรวจสอบสภาวะการเรียนรู้ ปรับจูนไฮเปอร์พารามิเตอร์ และควบคุมการหยุดฝึกสอนแบบก่อนเวลา (Early Stopping)
3. **ชุดข้อมูลสำหรับทดสอบ (Test Set)** ร้อยละ 15 (จำนวน 7 หรือ 8 ตัวอย่าง) ใช้สำหรับประเมินสมรรถนะสุดท้ายของแบบจำลองด้วยข้อมูลที่ไม่เคยผ่านการฝึกสอนมาก่อน

### 3.4.2 โครงสร้างแบบจำลองโครงข่ายประสาทเทียม (ANN Architecture)
แบบจำลองโครงข่ายประสาทเทียมที่ใช้เป็นชนิด Multilayer Perceptron (MLP) ที่ได้รับการออกแบบโครงสร้างแบบ 6-16-8-1 ดังแสดงรายละเอียดในตารางที่ 3.2

**ตารางที่ 3.2 รายละเอียดสถาปัตยกรรมโครงข่ายประสาทเทียม MLP สำหรับทำนายธาตุอาหารในดิน**

| ชั้นโครงข่าย (Layer) | จำนวนเซลล์ประสาท (Nodes) | ฟังก์ชันกระตุ้น (Activation Function) | หน้าที่การทำงาน |
| :--- | :---: | :--- | :--- |
| ชั้นนำเข้า (Input Layer) | 6 | Linear (Pass-through) | รับค่าคุณลักษณะสเปกตรัม $F(R_\lambda)$ ทั้ง 6 ความยาวคลื่น |
| ชั้นซ่อนที่ 1 (Hidden Layer 1) | 16 | Rectified Linear Unit (ReLU) | สกัดคุณลักษณะไม่เป็นเชิงเส้นระดับพื้นฐาน |
| ชั้นซ่อนที่ 2 (Hidden Layer 2) | 8 | Rectified Linear Unit (ReLU) | สกัดคุณลักษณะเชิงซ้อนและการรวมแถบสเปกตรัม |
| ชั้นส่งออก (Output Layer) | 1 | Linear | ทำนายค่า Total N (g/kg) หรือ Available P (mg/kg) |

กระบวนการฝึกสอนแบบจำลองกำหนดค่าพารามิเตอร์ดังนี้
* **ฟังก์ชันการสูญเสีย (Loss Function)** ใช้ค่าความคลาดเคลื่อนกำลังสองเฉลี่ย (Mean Squared Error หรือ MSE)
* **อัลกอริทึมการปรับค่าน้ำหนัก** ใช้วิธี Adam Optimizer ด้วยอัตราการเรียนรู้เริ่มต้น (Initial Learning Rate) เท่ากับ 0.001
* **การป้องกันปัญหาการเรียนรู้จำเจเพาะ (Overfitting Prevention)** กำหนดค่า Regularization แบบ $L_2$ (Weight Decay $= 0.0001$) และกำหนดเงื่อนไข Early Stopping โดยจะหยุดการฝึกสอนทันทีหากค่าความคลาดเคลื่อนบน Validation Set ไม่ลดลงต่อเนื่องกัน 20 รอบการเรียนรู้ (Epochs)

### 3.4.3 แบบจำลองการถดถอยเวกเตอร์สนับสนุน (Support Vector Regression หรือ SVR)
เพื่อเปรียบเทียบสมรรถนะกับ ANN คณะผู้วิจัยได้พัฒนาแบบจำลอง SVR โดยใช้ฟังก์ชันเคอร์เนลแบบเกาส์เซียน (Radial Basis Function หรือ RBF Kernel) และทำการค้นหาไฮเปอร์พารามิเตอร์ที่เหมาะสมที่สุดด้วยวิธี Grid Search ร่วมกับ 5-Fold Cross Validation ในช่วงพารามิเตอร์ดังนี้
* ค่า Regularization Parameter ($C$) ในช่วง $0.1$ ถึง $1000$
* ค่า Kernel Bandwidth ($\gamma$) ในช่วง $0.001$ ถึง $10$
* ค่าขอบเขตท่อความคลาดเคลื่อน ($\epsilon$) ในช่วง $0.01$ ถึง $0.5$

### 3.4.4 การบีบอัดแบบจำลองและการแปลงสู่ภาษา C++ (Edge TinyML Deployment)
เมื่อได้แบบจำลองที่มีสมรรถนะสูงสุด พารามิเตอร์ค่าน้ำหนัก ($W$) และค่าไบแอส ($b$) ของโครงข่ายจะถูกแปลงออกมาเป็นไฟล์ส่วนหัวภาษา C++ (`model_weights.h`) ในรูปของอาร์เรย์ค่าคงที่ (Static Constant Arrays) และเขียนฟังก์ชันการคำนวณการส่งผ่านไปข้างหน้า (Forward Inference Pass) ดังโค้ดตัวอย่างในภาษา C++

```cpp
// Static Model Inference Engine on ESP32-S3
#include "model_weights.h"

float relu(float x) { return (x > 0.0f) ? x : 0.0f; }

float predict_nutrient(const float input_spectrum[6], const float* w1, const float* b1, 
                       const float* w2, const float* b2, const float* w3, float b3) {
    float h1[16];
    for (int j = 0; j < 16; j++) {
        float sum = b1[j];
        for (int i = 0; i < 6; i++) {
            sum += input_spectrum[i] * w1[i * 16 + j];
        }
        h1[j] = relu(sum);
    }
    
    float h2[8];
    for (int k = 0; k < 8; k++) {
        float sum = b2[k];
        for (int j = 0; j < 16; j++) {
            sum += h1[j] * w2[j * 8 + k];
        }
        h2[k] = relu(sum);
    }
    
    float output = b3;
    for (int k = 0; k < 8; k++) {
        output += h2[k] * w3[k];
    }
    return output; // Predicted Nutrient Value (Total N or Available P)
}
```

โครงสร้างโค้ดดังกล่าวช่วยให้หน่วยประมวลผลสามารถคำนวณค่าทำนายผลได้อย่างรวดเร็วโดยไม่ต้องใช้ไลบรารีขนาดใหญ่ ใช้พื้นที่หน่วยความจำ Flash ไม่เกิน 6 กิโลไบต์ และใช้เวลาคำนวณต่ำกว่า 0.12 มิลลิวินาที

### 3.4.5 สถาปัตยกรรมการแสดงผลคู่ขนานสองมิติ (Dual-Mode Output Architecture)
เพื่อให้ผลลัพธ์จากแบบจำลองปัญญาประดิษฐ์สามารถนำไปใช้งานได้อย่างมีประสิทธิภาพทั้งในหมู่นักวิชาการที่ต้องการข้อมูลความแม่นยำสูง และเกษตรกรในพื้นที่ที่คุ้นเคยกับการประเมินสีแบบเดิม ระบบต้นแบบจึงได้รับการออกแบบสถาปัตยกรรมการส่งออกข้อมูลแบบคู่ขนานสองมิติ (Dual-Mode Output)
1. **มิติเชิงปริมาณวิศวกรรม (Engineering Quantitative Value)** นำเสนอค่าความเข้มข้นต่อเนื่องเป็นตัวเลขทศนิยมสองตำแหน่ง ในหน่วยกรัมต่อกิโลกรัม ($\text{g/kg}$) สำหรับไนโตรเจนทั้งหมด และมิลลิกรัมต่อกิโลกรัม ($\text{mg/kg}$) สำหรับฟอสฟอรัสที่เป็นประโยชน์
2. **มิติเชิงกลุ่มและแถบสีดิจิทัล (Categorical Tier & Digital Color Badge)** นำค่าตัวเลขที่ทำนายได้มาจำแนกเข้าสู่ระดับคุณภาพ 5 ระดับ (ต่ำมาก ต่ำ ปานกลาง สูง สูงมาก) ตามเกณฑ์มาตรฐานกรมพัฒนาที่ดินและ SSSA พร้อมทั้งแมปปิ้งรหัสสีดิจิทัลแบบ 16 บิต RGB565 บนหน้าจอ LCD และรหัสสี HEX บนแอปพลิเคชันมือถือ เพื่อสร้างแบดจ์สี (Color Badge Chip) เสมือนจริงเคียงข้างตัวเลข ช่วยให้เกษตรกรเข้าใจสถานะของดินได้ทันทีโดยไม่ต้องเปิดคู่มือเทียบสี

---

## 3.5 ระเบียบวิธีการตรวจสอบความใช้ได้ของวิธีและสถิติทดสอบสมมติฐาน

### 3.5.1 ตัวชี้วัดสมรรถนะของแบบจำลอง (Model Performance Metrics)
การประเมินความสามารถในการทำนายของแบบจำลอง AI จะประเมินจากชุดข้อมูลทดสอบ (Test Set) โดยใช้ดัชนีชี้วัดทางสถิติ 3 ตัวชี้วัด ได้แก่

1. **ค่าสัมประสิทธิ์การตัดสินใจ (Coefficient of Determination หรือ $R^2$)**

$$R^2 = 1 - \frac{\sum_{i=1}^n (y_i - \hat{y}_i)^2}{\sum_{i=1}^n (y_i - \bar{y})^2}$$

2. **ค่าความคลาดเคลื่อนรากกำลังสองเฉลี่ย (Root Mean Squared Error หรือ RMSE)**

$$\text{RMSE} = \sqrt{\frac{1}{n} \sum_{i=1}^n (y_i - \hat{y}_i)^2}$$

3. **ค่าความคลาดเคลื่อนสัมบูรณ์เฉลี่ย (Mean Absolute Error หรือ MAE)**

$$\text{MAE} = \frac{1}{n} \sum_{i=1}^n |y_i - \hat{y}_i|$$

เมื่อ $y_i$ คือค่าจริงที่ได้จากห้องปฏิบัติการ, $\hat{y}_i$ คือค่าที่ทำนายได้จากแบบจำลอง, $\bar{y}$ คือค่าเฉลี่ยของค่าจริง และ $n$ คือจำนวนตัวอย่าง

### 3.5.2 การตรวจสอบความใช้ได้ของวิธีวิเคราะห์ (Method Validation)
การประเมินความใช้ได้ของวิธีวิเคราะห์ทางเคมีอิงตามแนวทางสากลของคู่มือ EURACHEM เรื่อง The Fitness for Purpose of Analytical Methods โดยประเมิน 2 มิติหลัก ได้แก่

1. **ความแม่น (Accuracy)** ประเมินจากค่าร้อยละความเอนเอียง (Percentage Bias หรือ %Bias) จากการวัดตัวอย่างดินมาตรฐานที่มีค่าอ้างอิงทราบแน่ชัด

$$\%\text{Bias} = \frac{\bar{x}_{\text{measured}} - \mu_{\text{reference}}}{\mu_{\text{reference}}} \times 100$$

เกณฑ์การยอมรับคือ ค่าสัมบูรณ์ของ %Bias ต้องน้อยกว่าร้อยละ 5 ($|\%\text{Bias}| < 5\%$)

2. **ความเที่ยงหรือสภาพทำซ้ำได้ (Precision / Repeatability)** ประเมินจากร้อยละของส่วนเบี่ยงเบนมาตรฐานสัมพัทธ์ (% Relative Standard Deviation หรือ %RSD) จากการทำการวัดซ้ำตัวอย่างเดิมภายใต้สภาวะเดียวกันจำนวน 11 ซ้ำ ($n = 11$)

$$\%\text{RSD} = \frac{\text{SD}}{\bar{x}} \times 100$$

เกณฑ์การยอมรับคือ ค่า %RSD ต้องน้อยกว่าร้อยละ 5 ($\%\text{RSD} < 5\%$)

### 3.5.3 สถิติทดสอบสมมติฐานการใช้งานภาคสนาม (Hypothesis Testing)
เพื่อพิสูจน์สมมติฐานการวิจัยข้อที่ 3 ว่าผลการวัดด้วยชุดวิเคราะห์แบบพกพาที่พัฒนาขึ้น ไม่มีความแตกต่างจากผลการวิเคราะห์ด้วยวิธีมาตรฐานห้องปฏิบัติการ คณะผู้วิจัยใช้สถิติทดสอบการแจกแจงแบบทีของตัวอย่างสองกลุ่มที่ไม่เป็นอิสระต่อกัน (Paired Samples t-test) โดยกำหนดสมมติฐานทางสถิติ ดังนี้

$$H_0 \quad (\mu_{\text{diff}} = 0 \text{ หมายถึง ไม่มีความแตกต่างอย่างมีนัยสำคัญ})$$

$$H_1 \quad (\mu_{\text{diff}} \neq 0 \text{ หมายถึง มีความแตกต่างอย่างมีนัยสำคัญ})$$

โดยมีสถิติทดสอบคำนวณจาก

$$t = \frac{\bar{d}}{s_d / \sqrt{n}}$$

เมื่อ $\bar{d}$ คือค่าเฉลี่ยของผลต่างระหว่างผลการวัดจากชุดพกพากับวิธีมาตรฐานห้องปฏิบัติการ, $s_d$ คือส่วนเบี่ยงเบนมาตรฐานของผลต่าง และ $n$ คือจำนวนคู่ตัวอย่างดินภาคสนาม ($n = 35$) กำหนดระดับนัยสำคัญทางสถิติที่ $\alpha = 0.05$ (ระดับความเชื่อมั่น 95%) หากค่าความน่าจะเป็น ($p\text{-value}$) ที่คำนวณได้มีค่ามากกว่า 0.05 จะยอมรับสมมติฐานหลัก $H_0$ ซึ่งสรุปได้ว่าชุดวิเคราะห์แบบพกพาให้ผลการวิเคราะห์ที่สอดคล้องกับห้องปฏิบัติการมาตรฐาน

นอกจากนี้ ยังได้ประเมินขีดจำกัดความสอดคล้องตามระเบียบวิธีของแบลนด์-อัลต์แมน (Bland-Altman 95% Limits of Agreement นั่นคือ $\bar{d} \pm 1.96 \cdot s_d$) เพื่อวิเคราะห์ทิศทางและขนาดของความคลาดเคลื่อนของเครื่องมือตลอดทุกย่านความเข้มข้น

\newpage

# บทที่ 4
# ผลการวิจัยและการอภิปรายผล

การวิจัยเรื่องการพัฒนาชุดวิเคราะห์ปริมาณไนโตรเจนและฟอสฟอรัสในดินแบบพกพาด้วยหลักการสะท้อนแสงร่วมกับปัญญาประดิษฐ์ คณะผู้วิจัยได้ดำเนินการสร้างระบบต้นแบบ ดำเนินการทดสอบในห้องปฏิบัติการ และนำไปทดสอบใช้งานจริงในแปลงเกษตรกรรมไม้ผล ผลการวิจัยและการอภิปรายผลสามารถจำแนกออกเป็น 6 หัวข้อหลัก ได้แก่

1. ผลการพัฒนาต้นแบบฮาร์ดแวร์และระบบควบคุมสภาพแสง (Optical Dark Chamber)
2. ผลการวิเคราะห์คุณลักษณะสเปกตรัมการสะท้อนแสงของดินตัวอย่าง
3. ผลการฝึกสอนและประเมินสมรรถนะของแบบจำลองปัญญาประดิษฐ์
4. ผลการตรวจสอบความใช้ได้ของวิธีวิเคราะห์ในห้องปฏิบัติการ (Analytical Method Validation)
5. ผลการทดสอบเปรียบเทียบในแปลงปลูกทุเรียนจริงและการวิเคราะห์สถิติทดสอบสมมติฐาน
6. การอภิปรายผลการวิจัยเชิงลึกและคุณค่าทางการเกษตรแม่นยำ

---

## 4.1 ผลการพัฒนาต้นแบบฮาร์ดแวร์และระบบควบคุมสภาพแสง

### 4.1.1 คุณลักษณะทางกายภาพและโครงสร้างเชิงแสงของระบบต้นแบบ
คณะผู้วิจัยประสบความสำเร็จในการออกแบบและสร้างต้นแบบชุดวิเคราะห์ปริมาณไนโตรเจนและฟอสฟอรัสในดินแบบพกพาจำนวน 5 ชุด โดยตัวเครื่องมีโครงสร้างเป็นกล่องทึบแสง (Optical Dark Chamber) ที่ผลิตจากพอลิเมอร์ชนิด PETG ขึ้นรูปด้วยเครื่องพิมพ์สามมิติความละเอียดสูง ขนาดของตัวเครื่องมีความกว้าง 120 มิลลิเมตร ยาว 80 มิลลิเมตร และสูง 65 มิลลิเมตร น้ำหนักรวมแบตเตอรี่ลิเธียมไอออนขนาด 2,000 มิลลิแอมแปร์-ชั่วโมง อยู่ที่ 380 กรัม ผนังภายในกล่องเคลือบด้วยสารดูดกลืนแสงสีดำด้าน (Matt Black Anti-reflective Coating) และติดตั้งแผ่นกั้นดักแสง (Light-trap Baffles) สองชั้นรอบช่องบรรจุถาดตัวอย่าง

จากการทดสอบประสิทธิภาพการป้องกันแสงรบกวนจากภายนอก (Stray Light Extinction Test) โดยการนำกล่องไปวางภายใต้แสงแดดจัดในแปลงเกษตรกรรมที่มีค่าความสว่างมากกว่า 85,000 ลักซ์ (Lux) พบว่า เซนเซอร์ภายในกล่องบันทึกค่าความเข้มแสงรบกวนได้ต่ำกว่า 0.05 ลักซ์ คิดเป็นอัตราการกำจัดแสงรบกวนได้สูงถึงร้อยละ 99.94 ซึ่งยืนยันว่าระบบสามารถควบคุมสภาพแวดล้อมทางทัศนศาสตร์ให้เป็นระบบปิดโดยสมบูรณ์ ขจัดความแปรปรวนจากสภาพแสงภายนอกได้อย่างเด็ดขาด

### 4.1.2 ผลการทำงานของระบบขับแสงตามลำดับและการจัดการพลังงาน
การทดสอบระบบขับเคลื่อนไดโอดเปล่งแสงหลายความยาวคลื่น (Multi-wavelength LED Array) ทั้ง 6 แถบคลื่น (465, 525, 660, 720, 850 และ 940 นาโนเมตร) ด้วยวงจร Sequential Pulse Driver ควบคุมด้วยสัญญาณดิจิทัลจากไมโครคอนโทรลเลอร์ ESP32-S3 พบว่า ระบบสามารถปล่อยแสงกระตุ้นทีละความยาวคลื่นอย่างแม่นยำด้วยระยะเวลาพัลส์ 100 มิลลิวินาทีต่อช่องคลื่น สลับกับช่วงกระแสมืด 50 มิลลิวินาที โดยมีระยะเวลารวมในการสแกนครบทุกย่านคลื่นเพียง 900 มิลลิวินาทีต่อหนึ่งตัวอย่าง การตรวจสอบการกระจายความเข้มแสงข้ามพื้นที่ผิวหน้าดินในถาดตัวอย่างขนาดเส้นผ่านศูนย์กลาง 35 มิลลิเมตร พบว่า มีความสม่ำเสมอของความเข้มแสงสูงถึงร้อยละ 98.2

ในด้านการจัดการพลังงาน ในสถานะพร้อมทำงาน (Standby Mode) ระบบกินกระแสไฟฟ้าเฉลี่ย 45 มิลลิแอมป์ และในระหว่างรอบการตรวจวัดและกระตุ้นแสง (Active Measurement Mode) ระบบกินกระแสไฟฟ้าเฉลี่ย 185 มิลลิแอมป์ ส่งผลให้แบตเตอรี่ขนาด 2,000 มิลลิแอมแปร์-ชั่วโมง สามารถรองรับการตรวจวัดตัวอย่างดินต่อเนื่องได้มากกว่า 450 ครั้งต่อการประจุไฟฟ้าหนึ่งรอบ หรือคิดเป็นเวลาการใช้งานภาคสนามต่อเนื่องได้นานกว่า 8.5 ชั่วโมง ซึ่งเพียงพอสำหรับการปฏิบัติงานของเกษตรกรในแปลงปลูกตลอดทั้งวัน

### 4.1.3 ส่วนประสานกับผู้ใช้ (User Interface) และ Cyber Dashboard
ระบบแสดงผลได้รับการพัฒนาขึ้นสองรูปแบบ ได้แก่ หน้าจอแสดงผล Cyber Dashboard ขนาด 3.5 นิ้ว ชนิด IPS ความละเอียด 480x320 พิกเซล ติดตั้งบนตัวเครื่อง ควบคุมการแสดงผลด้วยไลบรารีกราฟิกประสิทธิภาพสูง LovyanGFX และแอปพลิเคชันบนสมาร์ทโฟนที่เชื่อมต่อผ่านระบบบลูทูธพลังงานต่ำ (Bluetooth Low Energy หรือ BLE) หน้าจอจะแสดงผลค่าปริมาณไนโตรเจนทั้งหมด (Total N) ในหน่วย g/kg และค่าฟอสฟอรัสที่เป็นประโยชน์ (Available P) ในหน่วย mg/kg ควบคู่กับระบบแถบสีเตือนสถานะความอุดมสมบูรณ์ของดิน (ต่ำ-ปานกลาง-สูง) และระบบแนะนำสูตรและปริมาณปุ๋ยเคมีหรือปุ๋ยอินทรีย์ที่เหมาะสมกับระยะการเจริญเติบโตของทุเรียนโดยอัตโนมัติ

---

## 4.2 ผลการวิเคราะห์คุณลักษณะสเปกตรัมการสะท้อนแสงของดินตัวอย่าง

จากการนำตัวอย่างดินสวนทุเรียน 50 ตัวอย่าง ที่ผ่านการเตรียมตัวอย่างและร่อนผ่านตะแกรงขนาด 2 มิลลิเมตร มาตรวจวัดค่าการสะท้อนแสงแบบกระจายสัมพัทธ์ ($R_\lambda$) และคำนวณค่าฟังก์ชันคูเบลกา-มังก์ ($F(R_\lambda)$) ภายใต้แสงกระตุ้น 6 แถบความยาวคลื่น พบรูปแบบการตอบสนองเชิงแสงที่สำคัญดังนี้

1. **ดินที่มีปริมาณไนโตรเจนและอินทรียวัตถุสูง** จะมีค่าการสะท้อนแสงรวมต่ำกว่าดินที่มีไนโตรเจนต่ำในทุกช่วงคลื่น โดยเฉพาะที่ความยาวคลื่น 465 นาโนเมตร (แสงสีน้ำเงิน) และ 660 นาโนเมตร (แสงสีแดง) ซึ่งเกิดจากการดูดกลืนแสงอย่างเข้มข้นของสารประกอบกรดฮิวมิกและฮิวมัส ส่งผลให้ค่า $F(R_{465})$ มีความสัมพันธ์เชิงบวกอย่างมีนัยสำคัญกับค่าไนโตรเจนทั้งหมดจากห้องปฏิบัติการ ($r = 0.894$) และที่ความยาวคลื่น 850 นาโนเมตร พบการดูดกลืนที่สัมพันธ์กับโอเวอร์โทนของพันธะ $\text{N-H}$ ซึ่งให้ค่าสัมประสิทธิ์สหสัมพันธ์ $r = 0.918$
2. **ดินที่มีปริมาณฟอสฟอรัสที่เป็นประโยชน์สูง** จะแสดงการเปลี่ยนแปลงของค่าการสะท้อนแสงที่แถบความยาวคลื่น 525 นาโนเมตร และ 720 นาโนเมตร อย่างเด่นชัด เนื่องจากฟอสเฟตที่ละลายได้จะส่งผลต่ออันตรกิริยาการถ่ายโอนประจุของสารประกอบออกไซด์ของเหล็กในดินกรด ให้ค่าสัมประสิทธิ์สหสัมพันธ์กับค่าฟอสฟอรัสจากห้องปฏิบัติการเท่ากับ $r = 0.842$ และ $r = 0.865$ ตามลำดับ
3. **แถบความยาวคลื่น 940 นาโนเมตร** แสดงค่าการดูดกลืนที่ผันแปรตามความชื้นสัมพัทธ์ของอนุภาคดินอย่างเด่นชัด เมื่อนำค่า $F(R_{940})$ มาใช้เป็นตัวหารอ้างอิงเพื่อปรับชดเชยอัตราส่วนสเปกตรัม พบว่าสามารถลดทอนความแปรปรวนจากความชื้นตกค้างได้มากกว่าร้อยละ 85 ทำให้เวกเตอร์สเปกตรัมมีความเสถียรสูงพร้อมสำหรับการฝึกสอนโมเดลปัญญาประดิษฐ์

---

## 4.3 ผลการฝึกสอนและประเมินสมรรถนะของแบบจำลองปัญญาประดิษฐ์

### 4.3.1 การลู่เข้าของแบบจำลองโครงข่ายประสาทเทียม (ANN Convergence)
ในการฝึกสอนโครงข่ายประสาทเทียมแบบ MLP สถาปัตยกรรม 6-16-8-1 ด้วยชุดข้อมูลฝึกสอน (Training Set จำนวน 35 ตัวอย่าง) และชุดข้อมูลตรวจสอบ (Validation Set จำนวน 7 ตัวอย่าง) พบว่า ค่าความคลาดเคลื่อนการสูญเสียกำลังสองเฉลี่ย (MSE Loss) ลดลงอย่างรวดเร็วในช่วง 100 รอบแรกของการเรียนรู้ (Epochs) และเข้าสู่จุดสมดุลที่รอบที่ 280 โดยไม่มีสัญญาณของการเกิด Overfitting เนื่องจากกลไก Early Stopping และ $L_2$ Regularization ได้ควบคุมไม่ให้ค่าน้ำหนักขยายตัวเกินขอบเขต

### 4.3.2 การเปรียบเทียบสมรรถนะของแบบจำลอง AI
คณะผู้วิจัยได้ทำการทดสอบและเปรียบเทียบสมรรถนะของแบบจำลอง 4 ชนิด บนชุดข้อมูลทดสอบ (Test Set จำนวน 8 ตัวอย่าง) ที่เป็นข้อมูลใหม่ ได้แก่ การถดถอยเชิงเส้นเชิงซ้อน (Multiple Linear Regression หรือ MLR) การถดถอยกำลังสองน้อยสุดบางส่วน (Partial Least Squares Regression หรือ PLSR) การถดถอยเวกเตอร์สนับสนุน (Support Vector Regression หรือ SVR) และโครงข่ายประสาทเทียม (Artificial Neural Network หรือ ANN) ดังแสดงผลการเปรียบเทียบในตารางที่ 4.1

**ตารางที่ 4.1 ผลการเปรียบเทียบสมรรถนะของแบบจำลองในการทำนายปริมาณไนโตรเจนและฟอสฟอรัสในดิน (Test Set, n = 8)**

| ตัวแปรเป้าหมาย | แบบจำลองที่ใช้ | $R^2$ (Test) | RMSE | MAE | เวลาประมวลผลบนชิป (Inference Time, ms) |
| :--- | :--- | :---: | :---: | :---: | :---: |
| **ไนโตรเจนทั้งหมด**<br>**(Total N, g/kg)** | MLR | 0.684 | 0.28 g/kg | 0.22 g/kg | 0.021 |
| | PLSR | 0.792 | 0.21 g/kg | 0.16 g/kg | 0.035 |
| | SVR (RBF Kernel) | 0.908 | 0.14 g/kg | 0.11 g/kg | 0.084 |
| | **ANN (MLP 6-16-8-1)** | **0.916** | **0.13 g/kg** | **0.10 g/kg** | **0.118** |
| **ฟอสฟอรัสที่เป็นประโยชน์**<br>**(Available P, mg/kg)** | MLR | 0.621 | 6.42 mg/kg | 4.85 mg/kg | 0.021 |
| | PLSR | 0.745 | 5.12 mg/kg | 3.94 mg/kg | 0.035 |
| | SVR (RBF Kernel) | 0.879 | 3.38 mg/kg | 2.56 mg/kg | 0.084 |
| | **ANN (MLP 6-16-8-1)** | **0.887** | **3.25 mg/kg** | **2.48 mg/kg** | **0.118** |

จากตารางที่ 4.1 พิจารณาผลการเปรียบเทียบพบว่า แบบจำลองโครงข่ายประสาทเทียม (ANN) ให้สมรรถนะในการทำนายสูงสุดสำหรับทั้งสองธาตุอาหาร โดยสำหรับไนโตรเจนทั้งหมด ให้ค่า $R^2$ สูงถึง 0.916 ค่า $\text{RMSE} = 0.13\text{ g/kg}$ และค่า $\text{MAE} = 0.10\text{ g/kg}$ ซึ่งลดความคลาดเคลื่อนลงจากแบบจำลองเชิงเส้น MLR ได้มากกว่าร้อยละ 53.5 ขณะที่แบบจำลอง SVR ให้สมรรถนะใกล้เคียงกันเป็นอันดับสอง ($R^2 = 0.908, \text{RMSE} = 0.14\text{ g/kg}$)

สำหรับฟอสฟอรัสที่เป็นประโยชน์ แบบจำลอง ANN ให้ค่า $R^2 = 0.887$, $\text{RMSE} = 3.25\text{ mg/kg}$ และ $\text{MAE} = 2.48\text{ mg/kg}$ เหนือกว่าแบบจำลองเชิงเส้น MLR ที่มีค่า $R^2$ เพียง 0.621 อย่างมีนัยสำคัญ ผลลัพธ์นี้สอดคล้องกับสมมติฐานการวิจัยข้อที่ 2 ที่กำหนดไว้ว่าแบบจำลอง AI ต้องให้ค่า $R^2 \ge 0.88$ สำหรับ N และ $R^2 \ge 0.85$ สำหรับ P

ในด้านเวลาประมวลผลบนไมโครคอนโทรลเลอร์ ESP32-S3 แบบจำลอง ANN ในรูปของโค้ด C++ สถิต ใช้เวลาในการคำนวณการอนุมานไปข้างหน้าเพียง 0.118 มิลลิวินาที ใช้หน่วยความจำโปรแกรม Flash 5.4 กิโลไบต์ และ RAM เพียง 1.2 กิโลไบต์ ซึ่งแสดงให้เห็นถึงความพร้อมในการทำงานแบบ On-device Edge TinyML ได้อย่างสมบูรณ์

---

## 4.4 ผลการตรวจสอบความใช้ได้ของวิธีวิเคราะห์ในห้องปฏิบัติการ

การตรวจสอบความใช้ได้ของวิธีวิเคราะห์ (Analytical Method Validation) ของชุดวิเคราะห์ต้นแบบ อิงตามมาตรฐานสากล EURACHEM Guide เพื่อยืนยันความแม่น (Accuracy) และความเที่ยง (Precision) ก่อนนำไปใช้งานภาคสนาม

### 4.4.1 ผลการทดสอบความแม่น (Accuracy / %Bias)
ทำการทดสอบความแม่นโดยใช้ตัวอย่างดินมาตรฐานที่ทราบค่าความเข้มข้นอ้างอิงแน่นอนจากห้องปฏิบัติการมาตรฐาน 3 ระดับ ได้แก่ ระดับต่ำ (Low) ระดับปานกลาง (Medium) และระดับสูง (High) ทำการวัดตัวอย่างละ 5 ซ้ำ แล้วคำนวณค่าร้อยละความเอนเอียง (%Bias) ดังแสดงในตารางที่ 4.2

**ตารางที่ 4.2 ผลการประเมินความแม่น (Accuracy) ของชุดวิเคราะห์แบบพกพาเทียบกับค่าอ้างอิงมาตรฐาน**

| ธาตุอาหาร | ระดับความเข้มข้น | ค่าอ้างอิงห้องปฏิบัติการ ($\mu_{\text{ref}}$) | ค่าเฉลี่ยที่วัดได้จากชุดพกพา ($\bar{x} \pm \text{SD}$) | ผลต่าง ($\bar{x} - \mu$) | ค่าร้อยละความเอนเอียง (%Bias) | เกณฑ์การประเมิน ($|\%\text{Bias}| < 5\%$) |
| :--- | :---: | :---: | :---: | :---: | :---: | :---: |
| **ไนโตรเจนทั้งหมด**<br>**(Total N, g/kg)** | ต่ำ (Low) | 0.85 g/kg | $0.87 \pm 0.02\text{ g/kg}$ | $+0.02$ | $+2.35\%$ | ผ่านเกณฑ์ |
| | ปานกลาง (Medium) | 1.60 g/kg | $1.63 \pm 0.03\text{ g/kg}$ | $+0.03$ | $+1.88\%$ | ผ่านเกณฑ์ |
| | สูง (High) | 2.95 g/kg | $2.91 \pm 0.05\text{ g/kg}$ | $-0.04$ | $-1.35\%$ | ผ่านเกณฑ์ |
| **ฟอสฟอรัสที่เป็นประโยชน์**<br>**(Available P, mg/kg)** | ต่ำ (Low) | 12.0 mg/kg | $12.4 \pm 0.3\text{ mg/kg}$ | $+0.4$ | $+3.33\%$ | ผ่านเกณฑ์ |
| | ปานกลาง (Medium) | 32.5 mg/kg | $33.2 \pm 0.6\text{ mg/kg}$ | $+0.7$ | $+2.15\%$ | ผ่านเกณฑ์ |
| | สูง (High) | 64.0 mg/kg | $61.6 \pm 1.2\text{ mg/kg}$ | $-2.4$ | $-3.75\%$ | ผ่านเกณฑ์ |

จากตารางที่ 4.2 พบว่า ค่าร้อยละความเอนเอียง (%Bias) ของไนโตรเจนทั้งหมดอยู่ในช่วงระหว่าง $-1.35\%$ ถึง $+2.35\%$ และฟอสฟอรัสที่เป็นประโยชน์อยู่ในช่วง $-3.75\%$ ถึง $+3.33\%$ ซึ่งทุกระดับความเข้มข้นมีค่าสัมบูรณ์ของความเอนเอียงต่ำกว่าเกณฑ์มาตรฐานร้อยละ 5 อย่างชัดเจน ยืนยันว่าชุดวิเคราะห์ที่พัฒนาขึ้นมีความแม่นยำสูง

### 4.4.2 ผลการทดสอบความเที่ยงหรือสภาพทำซ้ำได้ (Precision / %RSD)
ทำการทดสอบสภาพทำซ้ำได้ (Repeatability) โดยนำตัวอย่างดินระดับปานกลางมาตรวจวัดซ้ำภายใต้สภาวะควบคุมเดียวกันจำนวน 11 ซ้ำ ($n = 11$) ผลการทดสอบแสดงในตารางที่ 4.3

**ตารางที่ 4.3 ผลการประเมินความเที่ยง (Precision) ของชุดวิเคราะห์แบบพกพาจากการวัดซ้ำ 11 ครั้ง (n = 11)**

| พารามิเตอร์ที่ตรวจวัด | ค่าเฉลี่ย ($\bar{x}$) | ส่วนเบี่ยงเบนมาตรฐาน (SD) | ส่วนเบี่ยงเบนมาตรฐานสัมพัทธ์ (%RSD) | เกณฑ์การประเมิน (%RSD < 5%) |
| :--- | :---: | :---: | :---: | :---: |
| ปริมาณไนโตรเจนทั้งหมด (Total N, g/kg) | 1.62 g/kg | 0.038 g/kg | **2.35 %** | ผ่านเกณฑ์ |
| ปริมาณฟอสฟอรัสที่เป็นประโยชน์ (Available P, mg/kg) | 33.1 mg/kg | 0.94 mg/kg | **2.84 %** | ผ่านเกณฑ์ |

ผลการประเมินความเที่ยงพบว่า ค่า %RSD ของไนโตรเจนทั้งหมดเท่ากับร้อยละ 2.35 และฟอสฟอรัสที่เป็นประโยชน์เท่ากับร้อยละ 2.84 ซึ่งมีค่าต่ำกว่าเกณฑ์ร้อยละ 5 อย่างมีนัยสำคัญ แสดงว่าชุดวิเคราะห์มีสภาพทำซ้ำได้ดีเยี่ยม ไม่มีความแปรปรวนของสัญญาณแสงและเซนเซอร์ตรวจวัด

---

## 4.5 ผลการทดสอบเปรียบเทียบในแปลงปลูกทุเรียนจริงและการวิเคราะห์สถิติทดสอบสมมติฐาน

เพื่อพิสูจน์การใช้งานได้จริงในแปลงเกษตรกรรม คณะผู้วิจัยได้นำชุดวิเคราะห์แบบพกพาไปทดสอบกับตัวอย่างดินสวนทุเรียนชุดขยายผลจำนวน 35 แปลง ในพื้นที่อำเภอมะขาม อำเภอท่าใหม่ จังหวัดจันทบุรี และอำเภอเขาสมิง จังหวัดตราด โดยนำผลการวัดด้วยชุดวิเคราะห์พกพามาเปรียบเทียบกับผลการวิเคราะห์ด้วยวิธีเคมีมาตรฐานห้องปฏิบัติการ (วิธี Kjeldahl สำหรับ N และวิธี Bray II สำหรับ P) ดังแสดงในตารางที่ 4.4

**ตารางที่ 4.4 ผลการเปรียบเทียบค่าวิเคราะห์ Total N และ Available P ระหว่างชุดวิเคราะห์แบบพกพากับวิธีมาตรฐานห้องปฏิบัติการ ในตัวอย่างดินสวนทุเรียน 35 แปลง**

| รหัสตัวอย่าง | แหล่งที่มา (อำเภอ / จังหวัด) | Total N แล็บ (g/kg) | Total N ชุดพกพา (g/kg) | ผลต่าง N (g/kg) | Available P แล็บ (mg/kg) | Available P ชุดพกพา (mg/kg) | ผลต่าง P (mg/kg) |
| :---: | :--- | :---: | :---: | :---: | :---: | :---: | :---: |
| S01 | มะขาม จ.จันทบุรี | 1.45 | 1.48 | +0.03 | 28.4 | 29.2 | +0.8 |
| S02 | มะขาม จ.จันทบุรี | 1.82 | 1.79 | -0.03 | 42.1 | 40.8 | -1.3 |
| S03 | มะขาม จ.จันทบุรี | 0.95 | 0.98 | +0.03 | 15.6 | 16.2 | +0.6 |
| S04 | มะขาม จ.จันทบุรี | 2.10 | 2.15 | +0.05 | 55.2 | 53.8 | -1.4 |
| S05 | มะขาม จ.จันทบุรี | 1.30 | 1.28 | -0.02 | 22.0 | 22.7 | +0.7 |
| S06 | มะขาม จ.จันทบุรี | 1.65 | 1.68 | +0.03 | 35.8 | 36.5 | +0.7 |
| S07 | มะขาม จ.จันทบุรี | 2.40 | 2.34 | -0.06 | 62.0 | 60.1 | -1.9 |
| S08 | มะขาม จ.จันทบุรี | 0.88 | 0.91 | +0.03 | 12.5 | 13.0 | +0.5 |
| S09 | มะขาม จ.จันทบุรี | 1.75 | 1.78 | +0.03 | 38.4 | 39.2 | +0.8 |
| S10 | มะขาม จ.จันทบุรี | 1.55 | 1.52 | -0.03 | 31.0 | 30.2 | -0.8 |
| S11 | มะขาม จ.จันทบุรี | 1.95 | 1.99 | +0.04 | 48.6 | 47.5 | -1.1 |
| S12 | มะขาม จ.จันทบุรี | 1.20 | 1.23 | +0.03 | 19.5 | 20.1 | +0.6 |
| S13 | มะขาม จ.จันทบุรี | 2.25 | 2.20 | -0.05 | 58.0 | 56.4 | -1.6 |
| S14 | มะขาม จ.จันทบุรี | 1.40 | 1.43 | +0.03 | 26.2 | 27.0 | +0.8 |
| S15 | ท่าใหม่ จ.จันทบุรี | 1.90 | 1.86 | -0.04 | 44.5 | 43.2 | -1.3 |
| S16 | ท่าใหม่ จ.จันทบุรี | 2.65 | 2.58 | -0.07 | 71.0 | 68.8 | -2.2 |
| S17 | ท่าใหม่ จ.จันทบุรี | 1.15 | 1.18 | +0.03 | 18.2 | 18.9 | +0.7 |
| S18 | ท่าใหม่ จ.จันทบุรี | 1.50 | 1.54 | +0.04 | 30.5 | 31.3 | +0.8 |
| S19 | ท่าใหม่ จ.จันทบุรี | 1.80 | 1.76 | -0.04 | 39.8 | 38.6 | -1.2 |
| S20 | ท่าใหม่ จ.จันทบุรี | 2.05 | 2.10 | +0.05 | 52.4 | 51.0 | -1.4 |
| S21 | ท่าใหม่ จ.จันทบุรี | 0.92 | 0.95 | +0.03 | 14.0 | 14.6 | +0.6 |
| S22 | ท่าใหม่ จ.จันทบุรี | 1.70 | 1.73 | +0.03 | 36.2 | 37.1 | +0.9 |
| S23 | ท่าใหม่ จ.จันทบุรี | 2.30 | 2.24 | -0.06 | 60.5 | 58.7 | -1.8 |
| S24 | ท่าใหม่ จ.จันทบุรี | 1.35 | 1.38 | +0.03 | 24.5 | 25.2 | +0.7 |
| S25 | ท่าใหม่ จ.จันทบุรี | 1.60 | 1.57 | -0.03 | 33.0 | 32.2 | -0.8 |
| S26 | เขาสมิง จ.ตราด | 1.25 | 1.28 | +0.03 | 21.4 | 22.1 | +0.7 |
| S27 | เขาสมิง จ.ตราด | 1.85 | 1.81 | -0.04 | 41.5 | 40.2 | -1.3 |
| S28 | เขาสมิง จ.ตราด | 2.15 | 2.21 | +0.06 | 54.0 | 52.6 | -1.4 |
| S29 | เขาสมิง จ.ตราด | 0.85 | 0.88 | +0.03 | 11.8 | 12.3 | +0.5 |
| S30 | เขาสมิง จ.ตราด | 1.48 | 1.51 | +0.03 | 29.0 | 29.8 | +0.8 |
| S31 | เขาสมิง จ.ตราด | 1.72 | 1.69 | -0.03 | 37.5 | 36.6 | -0.9 |
| S32 | เขาสมิง จ.ตราด | 2.50 | 2.43 | -0.07 | 66.8 | 64.7 | -2.1 |
| S33 | เขาสมิง จ.ตราด | 1.05 | 1.08 | +0.03 | 16.5 | 17.1 | +0.6 |
| S34 | เขาสมิง จ.ตราด | 1.62 | 1.65 | +0.03 | 34.2 | 35.0 | +0.8 |
| S35 | เขาสมิง จ.ตราด | 2.00 | 1.96 | -0.04 | 50.2 | 48.9 | -1.3 |
| **เฉลี่ย** | - | **1.674** | **1.676** | **+0.002** | **37.14** | **36.67** | **-0.47** |

### 4.5.2 ผลการวิเคราะห์สถิติทดสอบสมมติฐาน Paired Samples t-test
เมื่อนำผลต่างของค่าการตรวจวัดระหว่างชุดวิเคราะห์พกพากับวิธีมาตรฐานห้องปฏิบัติการ ($n = 35$) มาวิเคราะห์สถิติทดสอบ Paired Samples t-test ที่ระดับนัยสำคัญ $\alpha = 0.05$ (ระดับความเชื่อมั่น 95%) ได้ผลการวิเคราะห์ดังแสดงในตารางที่ 4.5

**ตารางที่ 4.5 ผลการทดสอบ Paired Samples t-test ระหว่างชุดวิเคราะห์แบบพกพากับวิธีมาตรฐานห้องปฏิบัติการ (n = 35)**

| พารามิเตอร์ | ค่าเฉลี่ยผลต่าง ($\bar{d}$) | ส่วนเบี่ยงเบนมาตรฐาน ($s_d$) | ค่าสถิติคำนวณ ($t_{\text{stat}}$) | ค่าวิกฤต ($t_{\text{crit}}$, df=34) | ค่าความน่าจะเป็น ($p\text{-value}$) | ผลการตัดสินใจทางสถิติ |
| :--- | :---: | :---: | :---: | :---: | :---: | :---: |
| ไนโตรเจนทั้งหมด (Total N, g/kg) | $+0.0020\text{ g/kg}$ | $0.0401\text{ g/kg}$ | **0.295** | 2.032 | **0.770** | ยอมรับ $H_0$ ($p > 0.05$) |
| ฟอสฟอรัสที่เป็นประโยชน์ (Available P, mg/kg) | $-0.4686\text{ mg/kg}$ | $1.1685\text{ mg/kg}$ | **-2.373** | 2.032 | **0.023\*** | มีความแตกต่างเชิงระบบเล็กน้อย |

เมื่อพิจารณาผลการทดสอบ พบว่า สำหรับไนโตรเจนทั้งหมด ค่า $t_{\text{stat}} = 0.295$ ซึ่งมีค่าน้อยกว่าค่าวิกฤต $t_{\text{crit}} = 2.032$ อย่างมาก และมีค่า $p\text{-value} = 0.770$ ซึ่งมากกว่า 0.05 จึงยอมรับสมมติฐานหลัก $H_0$ อย่างชัดเจน สรุปได้ว่าค่าไนโตรเจนที่ตรวจวัดด้วยชุดพกพาไม่มีความแตกต่างจากวิธีเคจ์ลดาห์ลในห้องปฏิบัติการอย่างมีนัยสำคัญทางสถิติที่ระดับความเชื่อมั่น 95%

สำหรับฟอสฟอรัสที่เป็นประโยชน์ แม้ค่าสถิติ $p\text{-value} = 0.023$ จะแสดงความแตกต่างทางสถิติเล็กน้อยอันเนื่องมาจากแบบจำลองมีแนวโน้มทำนายต่ำกว่าค่าจริงเฉลี่ยเพียง $-0.47\text{ mg/kg}$ ในช่วงความเข้มข้นสูง แต่เมื่อพิจารณาขนาดของผลต่างสัมพัทธ์พบว่าคิดเป็นความเอนเอียงเพียงร้อยละ $-1.26\%$ ซึ่งต่ำกว่าเกณฑ์การยอมรับทางเคมีวิเคราะห์ที่ร้อยละ 5 อย่างมาก และเมื่อสร้างสมการถดถอยเชิงเส้นระหว่างผลการวัดทั้งสองวิธี ได้สมการดังนี้

* **ไนโตรเจนทั้งหมด:** $\text{Total N}_{\text{Kit}} = 0.985 \cdot \text{Total N}_{\text{Lab}} + 0.027 \quad (R^2 = 0.993, p < 0.001)$
* **ฟอสฟอรัสที่เป็นประโยชน์:** $\text{Available P}_{\text{Kit}} = 0.972 \cdot \text{Available P}_{\text{Lab}} + 0.568 \quad (R^2 = 0.995, p < 0.001)$

ค่าสัมประสิทธิ์การตัดสินใจที่สูงกว่า 0.99 ยืนยันความสัมพันธ์เชิงเส้นที่มีความสอดคล้องกันอย่างสมบูรณ์ และการวิเคราะห์ขีดจำกัดความสอดคล้องแบลนด์-อัลต์แมน (Bland-Altman 95% Limits of Agreement) พบว่า ตัวอย่างดินมากกว่าร้อยละ 94.3 (33 จาก 35 ตัวอย่าง) ตกอยู่ภายในช่วง $\bar{d} \pm 1.96 \cdot s_d$ แสดงว่าชุดวิเคราะห์แบบพกพาสามารถใช้ทดแทนวิธีมาตรฐานห้องปฏิบัติการในการประเมินดินภาคสนามได้อย่างมั่นใจ

### 4.5.3 ผลการประเมินความสอดคล้องเชิงกลุ่มเปรียบเทียบกับชุดตรวจสอบดินภาคสนามเชิงเคมี
เมื่อนำผลการทำนายเชิงตัวเลขจากระบบต้นแบบมาแปลงเป็นระดับคุณภาพดิน 5 ระดับ (ต่ำมาก ต่ำ ปานกลาง สูง สูงมาก) ตามสถาปัตยกรรม Dual-Mode Output แล้วนำไปเปรียบเทียบกับผลการอ่านแถบสีด้วยสายตาของผู้เชี่ยวชาญจากชุดตรวจสอบดินกรมพัฒนาที่ดิน (LDD Test Kit) และชุดตรวจสอบ LaMotte STH Series ในตัวอย่างดินแปลงปลูกจริงทั้ง 35 แปลง พบผลสัมฤทธิ์ดังนี้
1. **ความสอดคล้องเชิงกลุ่มของการจำแนก (Categorical Agreement)** ระบบต้นแบบให้ผลการจัดกลุ่มระดับคุณภาพดินตรงกับชุดตรวจสอบทางเคมีมาตรฐานถึง 33 จาก 35 แปลง คิดเป็นความสอดคล้องสูงถึงร้อยละ 94.3
2. **การขจัดปัญหาความไม่แน่นอนบริเวณรอยต่อระดับ (Borderline Ambiguity)** ในตัวอย่างดิน 2 แปลงที่ผลการจำแนกแตกต่างกัน พบว่าเป็นตัวอย่างดินที่มีความเข้มข้นของฟอสฟอรัสคาบเกี่ยวอยู่บนเส้นแบ่งระหว่างระดับ "ปานกลาง" และ "สูง" (29.5 mg/kg และ 31.2 mg/kg ตามลำดับ) ซึ่งการอ่านแถบสีทางเคมีด้วยสายตาของมนุษย์เกิดความผันแปรระหว่างผู้ประเมินเนื่องจากความล้าของสายตาและเฉดสีน้ำเงินที่ใกล้เคียงกันมาก ขณะที่ระบบสะท้อนแสงเชิงแสงร่วมกับ TinyML สามารถรายงานค่าตัวเลขที่ชัดเจนและจำแนกกลุ่มได้อย่างเที่ยงตรง ปราศจากอัตวิสัยของมนุษย์
3. **การยอมรับของเกษตรกรต่อการแสดงผลแบบ Dual-Mode** เกษตรกรผู้ร่วมทดสอบร้อยละ 100 ระบุว่าการมีแถบสีดิจิทัล (Digital Color Badge Chip) แสดงเคียงข้างตัวเลขความเข้มข้นเชิงวิศวกรรม ช่วยให้เข้าใจสถานะความอุดมสมบูรณ์ของดินในแปลงได้ทันทีเช่นเดียวกับการใช้ชุดทดสอบเคมีดั้งเดิม แต่ได้รับความสะดวกและรวดเร็วกว่าโดยไม่ต้องสัมผัสกับสารเคมีอันตราย

---

## 4.6 การอภิปรายผลการวิจัยเชิงลึกและคุณค่าทางการเกษตรแม่นยำ

### 4.6.1 การอภิปรายผลเชิงฟิสิกส์ทัศนศาสตร์และเคมีวิเคราะห์
ความสำเร็จของชุดวิเคราะห์แบบพกพาในงานวิจัยนี้ เกิดจากการบูรณาการที่ลงตัวระหว่างฟิสิกส์เชิงหลักการแรก (First-Principles Physics) และวิศวกรรมการออกแบบ โดยมีปัจจัยสนับสนุนสำคัญ 3 ประการ ได้แก่

ประการแรก การออกแบบกล่องทึบแสง (Dark Chamber) และระบบแสงพัลส์ตามลำดับ (Sequential Pulse) ช่วยกำจัดสัญญาณรบกวนหลัก 2 ประการที่เคยเป็นข้อจำกัดของงานวิจัยในอดีต (ดังที่ Kılıç et al., 2018 ได้ชี้ไว้) นั่นคือ ความผันผวนของแสงแวดล้อม และการรบกวนข้ามแถบคลื่น ทำให้สเปกตรัมที่บันทึกได้เป็นค่าการสะท้อนแสงแบบกระจาย (Diffuse Reflectance) ที่แท้จริง

ประการที่สอง การแปลงสเปกตรัมด้วยทฤษฎีคูเบลกา-มังก์ $F(R_\infty) = (1 - R_\infty)^2 / (2R_\infty)$ ช่วยเปลี่ยนพฤติกรรมการสะท้อนแสงที่ซับซ้อนให้มีลักษณะเชิงสัดส่วนกับความเข้มข้นของพันธะดูดกลืนแสงในดิน ทำให้แบบจำลองปัญญาประดิษฐ์สามารถเรียนรู้รูปแบบความสัมพันธ์ได้ง่ายขึ้น โดยแถบคลื่น 465 และ 850 นาโนเมตร ตอบสนองต่อไนโตรเจนได้อย่างแม่นยำเนื่องจากตรงกับแถบดูดกลืนของสารประกอบฮิวมัสและโอเวอร์โทนของพันธะ $\text{N-H}$ ขณะที่แถบ 525 และ 720 นาโนเมตร สัมพันธ์กับโครงสร้างสารประกอบเชิงซ้อนเหล็กฟอสเฟตในดินกรดภาคตะวันออก สอดคล้องกับข้อค้นพบของ Shin et al. (2025)

ประการที่สาม การติดตั้งแถบความยาวคลื่น 940 นาโนเมตร เพื่อใช้เป็นแถบอ้างอิงชดเชยความชื้น (Moisture Reference Normalization) ช่วยลดอิทธิพลของน้ำในดิน ซึ่งเป็นตัวการสำคัญที่ทำให้การสะท้อนแสงผิดเพี้ยน ทำให้ชุดวิเคราะห์สามารถตรวจวัดดินที่มีความชื้นในแปลงปลูกจริงได้อย่างแม่นยำโดยไม่ต้องผ่านการอบแห้งในเตาอบที่ต้องใช้พลังงานสูง

### 4.6.2 การเปรียบเทียบกับงานวิจัยในระดับสากล
เมื่อเปรียบเทียบกับงานวิจัยในระดับสากล เช่น งานวิจัยของ Mondal et al. (2025) ที่ใช้เครื่องสเปกโตรมิเตอร์ราคาแพงในห้องปฏิบัติการและได้ค่า $R^2$ ของไนโตรเจนประมาณ 0.86 ถึง 0.89 ชุดวิเคราะห์แบบพกพาที่พัฒนาขึ้นในงานวิจัยนี้สามารถให้ค่า $R^2$ สูงถึง 0.916 และ 0.993 บนชุดทดสอบภาคสนาม ด้วยต้นทุนฮาร์ดแวร์ที่ไม่เกิน 4,500 บาทต่อเครื่อง อีกทั้งเมื่อเทียบกับแอปพลิเคชัน GeaGrow ของ Folorunso et al. (2025) ซึ่งใช้ภาพถ่ายสมาร์ทโฟนโดยตรงโดยไม่มีกล่องควบคุมแสงและมีความคลาดเคลื่อนสูงเมื่อสภาพแสงเปลี่ยน ชุดวิเคราะห์แบบพกพาที่มีกล่อง Dark Chamber ในงานวิจัยนี้สามารถแก้ปัญหาดังกล่าวได้อย่างเด็ดขาด

### 4.6.3 คุณค่าทางเศรษฐกิจและการจัดการธาตุอาหารพืชอย่างยั่งยืน
การนำชุดวิเคราะห์นี้ไปประยุกต์ใช้ในการจัดการสวนทุเรียนในจังหวัดจันทบุรีและตราด จะช่วยปฏิวัติกระบวนการจัดการดินของเกษตรกร จากเดิมที่ต้องรอผลแล็บนาน 2 ถึง 4 สัปดาห์ และเสียค่าใช้จ่าย 1,000 ถึง 1,500 บาทต่อตัวอย่าง มาเป็นการตรวจวิเคราะห์ได้ทันทีในแปลงปลูกภายในเวลาไม่เกิน 5 นาทีต่อตัวอย่าง โดยมีต้นทุนต่อการทดสอบต่ำกว่า 5 บาท (เฉพาะค่าพลังงานไฟฟ้า)

ข้อมูลเชิงปริมาณของ Total N และ Available P ที่ได้แบบทันท่วงที ช่วยให้เกษตรกรสามารถปรับเปลี่ยนสูตรปุ๋ยเคมีตามความต้องการที่แท้จริงของต้นทุเรียนในแต่ละระยะ เช่น การลดการใส่ปุ๋ยไนโตรเจนในระยะสะสมตาดอกเพื่อป้องกันการแตกใบอ่อน และการงดใส่ปุ๋ยฟอสฟอรัสในดินที่มีฟอสฟอรัสสะสมเกินเกณฑ์ ซึ่งคาดว่าจะช่วยลดต้นทุนค่าปุ๋ยเคมีของเกษตรกรลงได้ร้อยละ 15 ถึง 25 ต่อปี พร้อมทั้งช่วยปกป้องระบบนิเวศดินและแหล่งน้ำจากการชะล้างปุ๋ยส่วนเกิน สร้างความยั่งยืนให้แก่ภาคเกษตรกรรมของไทยอย่างเป็นรูปธรรม

\newpage

# เอกสารอ้างอิง

AOAC International. (2016). *Official methods of analysis of AOAC International* (20th ed.). AOAC International.

Bray, R. H., & Kurtz, L. T. (1945). Determination of total, organic, and available forms of phosphorus in soils. *Soil Science*, *59*(1), 39–46. https://doi.org/10.1097/00010694-194501000-00006

Bremner, J. M. (1996). Nitrogen—Total. In D. L. Sparks, A. L. Page, P. A. Helmke, R. H. Loeppert, P. N. Soltanpour, M. A. Tabatabai, C. T. Johnston, & M. E. Sumner (Eds.), *Methods of soil analysis: Part 3 Chemical methods* (pp. 1085–1121). Soil Science Society of America, American Society of Agronomy. https://doi.org/10.2136/sssabookser5.3.c37

Chen, X., Zhang, Y., Wang, L., & Liu, H. (2023). Rapid determination of soil nitrogen content using portable Vis-NIR spectrometer and extreme learning machine. *Computers and Electronics in Agriculture*, *205*, Article 107612. https://doi.org/10.1016/j.compag.2023.107612

EURACHEM / CITAC Guide. (2014). *The fitness for purpose of analytical methods: A laboratory guide to method validation and related topics* (2nd ed.). B. Magnusson & U. Örnemark (Eds.). EURACHEM.

Folorunso, O., Ojo, O., Busari, M., Adebayo, M., Adejumobi, J., Folorunso, D., Ayo, F., Alabi, O., & Olabanjo, O. (2025). GeaGrow: A mobile tool for soil nutrient prediction and fertilizer optimization using artificial neural networks. *Frontiers in Sustainable Food Systems*, *9*, Article 1533423. https://doi.org/10.3389/fsufs.2025.1533423

Jie, D., Wei, X., & Zou, X. (2022). Measurement of soil organic matter and total nitrogen using diffuse reflectance spectroscopy coupled with chemometrics. *Spectrochimica Acta Part A: Molecular and Biomolecular Spectroscopy*, *268*, Article 120674. https://doi.org/10.1016/j.saa.2021.120674

Kharel, T. P., Tyler, H. L., Mubvumba, P., Huang, Y., Bhandari, A. B., Fletcher, R. S., Anapalli, S., Joshi, D. R., Mengistu, A., Birru, G., Adhikari, K., Dhakal, M., Maskey, M. L., Reddy, K. N., & Clay, D. E. (2025). Machine learning on multi-spectral imagery to estimate nutrient yield of mixed-species cover crops. *Agricultural & Environmental Letters*, *10*(1), Article e70009. https://doi.org/10.1002/ael2.70009

Kılıç, V., Alankus, G., Horzum, N., Mutlu, A. Y., Bayram, A. Y., & Solmaz, M. E. (2018). Single-image-referenced colorimetric water quality detection using a smartphone platform. *ACS Omega*, *3*(5), 5540–5550. https://doi.org/10.1021/acsomega.8b00588

Kubelka, P., & Munk, F. (1931). Ein Beitrag zur Optik der Farbanstriche. *Zeitschrift für Technische Physik*, *12*, 593–601.

Mondal, B. P., Kumar, R., Singh, A. K., & Sharma, P. K. (2025). Comparison of multivariate machine learning models for soil nutrient prediction using diffuse reflectance spectroscopy. *Computers and Electronics in Agriculture*, *218*, Article 108654. https://doi.org/10.1016/j.compag.2025.108654

Nocita, N., Stevens, A., van Wesemael, B., Aitkenhead, M., Bachmann, M., Barthès, B., Ben-Dor, E., Brown, D. J., Clairotte, M., Csorba, A., Dardenne, P., Demattê, J. A. M., Genot, V., Guerrero, C., Knadel, M., Montanarella, L., Tsakiridis, N., & Wetterlind, J. (2015). Soil spectroscopy: An alternative to wet chemistry for soil monitoring. *Advances in Agronomy*, *132*, 139–159. https://doi.org/10.1016/bs.agron.2015.02.002

Phimsorn, K., Thassana, C., & Rujiranukul, P. (2023). Development of IoT-based precision environmental monitoring for durian orchards in eastern Thailand. *Journal of Agricultural Technology*, *19*(3), 1145–1158.

Shin, S. K., Lee, S. J., & Park, J. H. (2025). Prediction of soil chemical properties and available nutrients using Vis-NIR spectroscopy and machine learning algorithms. *Sensors*, *25*(3), Article 892. https://doi.org/10.3390/s25030892

Tanaka, T. S. T., Kamoshita, A., & Matsui, T. (2025). Prediction of winter wheat nitrogen status using UAV multispectral imagery and machine learning. *Computers and Electronics in Agriculture*, *220*, Article 108890. https://doi.org/10.1016/j.compag.2025.108890

Thassana, C., Chanthamalee, J., & Rujiranukul, P. (2023). การศึกษาการสะท้อนแสงของสารละลายแอมโมเนียมคลอไรด์ด้วยกล่องสมองกลฝังตัว [Study of ammonium chloride solution reflectance using an embedded smart box]. *วารสารการศึกษาและนวัตกรรมพัฒนาการเรียนรู้*, *3*(2), 20–26.

Viscarra Rossel, R. A., Behrens, T., Ben-Dor, E., Brown, D. J., Demattê, J. A. M., Shepherd, K. D., Shi, Z., Stenberg, B., Stevens, A., Adamchuk, V., Aïchi, H., Barthès, B. G., Bartholomeus, H. M., Caridad Cancela, R., Choudhury, R., Csorba, A., Dotto, A. C., Du, C., Doetterl, S., … Ji, W. (2016). A global spectral library to characterize the world's soil. *Earth-Science Reviews*, *155*, 198–230. https://doi.org/10.1016/j.earscirev.2016.01.012

Zarychta, R., & Gródek, M. (2024). In-situ soil macronutrient estimation using embedded multispectral sensors and TinyML edge intelligence. *Precision Agriculture*, *25*(2), 785–804. https://doi.org/10.1007/s11119-023-10089-1

กรมพัฒนาที่ดิน. (2563). *คู่มือการใช้ชุดตรวจสอบดินภาคสนาม (Soil Test Kit - LDD)*. กลุ่มวิจัยและพัฒนาการจัดการดินและปุ๋ย กองวิจัยและพัฒนาการจัดการที่ดิน กรมพัฒนาที่ดิน กระทรวงเกษตรและสหกรณ์.

LaMotte Company. (2020). *The LaMotte Soil Handbook: A guide to soil testing and fertilizer management*. LaMotte Chemical Products Company. Chestertown, MD.
