TsanaPhysics/JC-AGRITecH-AI/chewa/extracted_chewa_full.md

# **แบบเสนอโครงการวิจัย/โครงการวิจัยภายใต้แผนงานวิจัย (Full Proposal)**

**เสนอของบประมาณกองทุนวิจัย มหาวิทยาลัยราชภัฏรำไพพรรณี ประจำปีงบประมาณ พ.ศ.
2569**

**ส่วน 1 ลักษณะสำคัญของโครงการวิจัย**

**1. ประเภททุนวิจัย**

🔾 1.1 ทุนวิจัยสำหรับบุคลากรสายวิชาการ 🔾 1.2 ทุนวิจัยสำหรับบุคลากรสายสนับสนุน

**2. ประเภทงานวิจัย**

🔾 2.1 แผนงานวิจัย/โครงการวิจัยย่อยภายใต้แผนงาน 🔾 2.2 โครงการวิจัยเดี่ยว

**3. ชื่อแผนงานวิจัย** (กรณีแผนงานวิจัย)

> (ภาษาไทย) เรื่อง การบูรณาการเทคโนโลยีจุลชีววิทยาและปัญญาประดิษฐ์เพื่อการจัดการ
> ธาตุอาหารพืชอย่างยั่งยืนในพื้นที่เกษตรกรรมจังหวัดจันทบุรี
>
> (ภาษาอังกฤษ) Integration of Microbiological and Artificial Intelligence
> Technologies for Sustainable Plant Nutrient Management in Agricultural
> Areas of Chanthaburi Province

**4. ชื่อโครงการวิจัยภายใต้แผนงานวิจัย/ โครงการวิจัยเดี่ยว**

> (ภาษาไทย) เรื่อง การพัฒนาชุดวิเคราะห์ปริมาณไนโตรเจนและฟอสฟอรัสในดินแบบพกพา
>
> ด้วยหลักการสะท้อนแสงร่วมกับปัญญาประดิษฐ์
>
> (ภาษาอังกฤษ) Development of a Portable Soil Nitrogen and Phosphorus
> Analyzer using Reflectance Principle Integrated with Artificial
> Intelligence

**ส่วน 2 ความสอดคล้องตามกรอบวิจัยของมหาวิทยาลัยราชภัฏรำไพพรรณี**

**1. ประเด็นความสอดคล้องกับกรอบการวิจัย (สำหรับบุคลากรสายสนับสนุน)**

◻ ประเด็น 1 ด้านหลักสูตร/ การพัฒนาหลักสูตร/ การบริหารจัดการหลักสูตร

◻ ประเด็น 2 ด้านการจัดการเรียนการสอน/ สื่อ/ เทคนิควิธีสอน

◻ ประเด็น 3 ด้านนักเรียน/ นักศึกษา/ บัณฑิต

◻ ประเด็น 4 ด้านอาจารย์/ บุคลากร/ ผู้บริหาร

◻ ประเด็น 5 ด้านการเงิน/ งบประมาณ

◻ ประเด็น 6 ด้านสิ่งอำนวยความสะดวก/ อาคารสถานที่ / สิ่งแวดล้อม

◻ ประเด็น 7 ด้านประชาสัมพันธ์/ ภาพลักษณ์องค์กร

◻ ประเด็น 8 ด้านการประกันคุณภาพการศึกษา

◻ ประเด็น 9 งานวิจัยเพื่อพัฒนางานประจำ (Routine to Research: R2R)

◻ ประเด็น 10 ประเด็นเร่งด่วน (Hot Issue) ซึ่งเป็นความต้องการของหน่วยงานต้นสังกัด

ผู้ขอรับทุนและต้องการผลจากการวิจัยเพื่อศึกษาคำตอบ
การขอทุนในหัวข้อนี้ต้องได้รับความเห็นชอบจากหัวหน้าหน่วยงาน

◻ ประเด็น 11 ประเด็นด้านภูมิปัญญาหรือศาสตร์วิชาที่มุ่งเน้น 7 ด้าน ตามนโยบายเร่งด่วน

ของอธิการบดี ได้แก่ 1) ด้านการผลิตและพัฒนาครู 2) ด้านอาหาร 3)
ด้านการบริหารและการจัดการระบบขนส่ง 4) ด้านอัญมณี 5) ด้านผลไม้เมืองร้อน 6)
ด้านเทคโนโลยีสารสนเทศ 7) ด้านความยั่งยืน

**2. ประเด็นความสอดคล้องกับกรอบการวิจัย (สำหรับบุคลากรสายวิชาการ)**

(เลือกเป้าหมายหลัก และประเด็นที่เกี่ยวข้องโดยตรง 1 ประเด็นเท่านั้น)

- **เป้าหมายที่ 1 การวิจัยและนวัตกรรมเพื่อการพัฒนาท้องถิ่นด้วยวิทยาศาสตร์และเทคโนโลยี**

◻ ประเด็นที่ 1.1 การจัดการสิ่งแวดล้อม ระบบนิเวศบนบก ทรัพยากรทางทะเลและชายฝั่ง
ปะการัง การแก้ปัญหาหรือรับมือกับการเปลี่ยนแปลงสภาพภูมิอากาศ (Climate Change)
(สอดคล้องกับ SDG 13, 14, 15
และภูมิปัญญาหรือศาสตร์วิชามุ่งเน้นตามนโยบายเร่งด่วนอธิการบดีข้อ 7 )

◻ ประเด็นที่ 1.2 การจัดการด้านพลังงาน พลังงานสะอาดและจ่ายได้ พลังงานทางเลือก
(สอดคล้องกับ SDG 7)

◻ ประเด็นที่ 1.3 การบริหารจัดการอัญมณี (สอดคล้องกับ SDG 8
และภูมิปัญญาหรือศาสตร์วิชามุ่งเน้นตามนโยบายเร่งด่วนอธิการบดีข้อ 4)

☑ ประเด็นที่ 1.4 การยกระดับประสิทธิภาพด้านดิจิทัล สารสนเทศ ปัญญาประดิษฐ์ (AI)
ระบบโลจิสติกส์หรือเมือง การบริหารและจัดการระบบขนส่ง และชุมชนยั่งยืน (สอดคล้องกับ SDG
11 และภูมิปัญญาหรือศาสตร์วิชามุ่งเน้นตามนโยบายเร่งด่วนอธิการบดีข้อ 3, 6)

◻ ประเด็นที่ 1.5 เกษตรและอาหาร ความมั่นคงทางอาหารบนฐานทรัพยากรของจังหวัด
ผลไม้เมืองร้อน สมุนไพร การขจัดความหิวโหย การผลิตและบริโภคที่รับผิดชอบ (สอดคล้องกับ SDG
2, 12 และ ภูมิปัญญาหรือศาสตร์วิชามุ่งเน้นตามนโยบายเร่งด่วนอธิการบดีข้อ 2, 5, 7)

◻ ประเด็นที่ 1.6 สุขภาพ ผลิตภัณฑ์ และความเป็นอยู่ที่ดี น้ำสะอาดและสุขาภิบาล (สอดคล้องกับ
SDG 6 และภูมิปัญญาหรือศาสตร์วิชามุ่งเน้นตามนโยบายเร่งด่วนอธิการบดีข้อ 7)

◻ ประเด็นที่ 1.7 เทคโนโลยีด้านวิศวกรรมศาสตร์ อุตสาหกรรมนวัตกรรมโครงสร้างพื้นฐาน
(สอดคล้องกับ SDG 9)

◻ ประเด็นที่ 1.8 ความเป็นกลางทางคาร์บอน คาร์บอนเครดิต (สอดคล้องกับ SDG 13)

**🔾 เป้าหมายที่ 2 การวิจัยและพัฒนานวัตกรรมเพื่อแก้ปัญหาหรือสร้างความเข้มแข็ง ด้านสังคม
ชุมชน และความมั่นคง**

◻ ประเด็นที่ 2.1
การพัฒนาเมืองน่าอยู่และพื้นที่ระเบียงเศรษฐกิจพิเศษที่เชื่อมโยงกับการพัฒนาชุมชน ท้องถิ่น
(สอดคล้องกับ SDG 11)

◻ ประเด็นที่ 2.2 การจัดการนวัตวิถี ท่องเที่ยวชุมชน และเศรษฐกิจสร้างสรรค์
สนับสนุนงานที่มีคุณค่าเศรษฐกิจที่เติบโต (สอดคล้องกับ SDG 8, 11, 12
และภูมิปัญญาหรือศาสตร์วิชามุ่งเน้นตามนโยบายเร่งด่วนอธิการบดีข้อ 7)

◻ ประเด็นที่ 2.3 การพัฒนาคุณภาพชีวิต สวัสดิการ แรงงาน การขจัดความยากจน
ลดความเหลื่อมล้ำ และความมั่นคงของมนุษย์ (สอดคล้องกับ SDG 1, 3, 8, 10
และภูมิปัญญาหรือศาสตร์วิชามุ่งเน้นตามนโยบายเร่งด่วนอธิการบดีข้อ 7)

◻ ประเด็นที่ 2.4 วัฒนธรรม ศาสนา และภูมิปัญญาท้องถิ่น (สอดคล้องกับ SDG 11 และ
ภูมิปัญญาหรือศาสตร์วิชามุ่งเน้นตามนโยบายเร่งด่วนอธิการบดีข้อ 7)

◻ ประเด็นที่ 2.5 การบริหาร การผลิตและพัฒนาครู การพัฒนาบัณฑิตครูตามสมรรถนะในศตวรรษที่
21 และคุณลักษณะตามพระราโชบาย การศึกษาที่มีคุณภาพ การพัฒนานวัตกรรมทางการศึกษา
การศึกษาตลอดชีวิต และการพัฒนาทักษะผู้ประกอบการ (สอดคล้องกับ SDG 5)

◻ ประเด็นที่ 2.6 การอยู่ร่วมกันของประชากรหลายวัย ความเท่าเทียมทางเพศ
ศักยภาพและโอกาสของผู้สูงอายุ และสังคมสูงวัย (สอดคล้องกับ SDG 5
และภูมิปัญญาหรือศาสตร์วิชามุ่งเน้นตามนโยบายเร่งด่วนอธิการบดีข้อ 7)

◻ ประเด็นที่ 2.7 การลดความรุนแรง การค้ามนุษย์ การส่งเสริมนิติธรรม
สันติภาพและสถาบันเข้มแข็ง (สอดคล้องกับ SDG 16
และภูมิปัญญาหรือศาสตร์วิชามุ่งเน้นตามนโยบายเร่งด่วนอธิการบดีข้อ 7)

◻ ประเด็นที่ 2.8 การพัฒนาคุณภาพบัณฑิต การพัฒนาความรู้ ทักษะ สมรรถนะในศตวรรษที่ 21
ทักษะการเป็นวิศวกรสังคม ความสามารถด้านเทคโนโลยีสารสนเทศ
ความสามารถทางการเงินของบัณฑิต (สอดคล้องกับ SDG 4)

**🔾 เป้าหมายที่ 3 องค์ความรู้พื้นฐานเพื่อยกระดับคุณภาพการศึกษา
การวิจัยเพื่อส่งเสริมการเรียนรู้ตลอดชีวิต
หรือการวิจัยเพื่อส่งเสริมประสิทธิภาพการดำเนินงานพลิกโฉมสถาบันอุดมศึกษา (Re-inventing
University)**

**3. ความสอดคล้องตามเป้าหมายการพัฒนาที่ยั่งยืน Sustainable Development Goals 
(SDGs)**

☐ 1. ขจัดความยากจนทุกรูปแบบในทุกพื้นที่

> ☐ 2. ยุติความหิวโหย
> บรรลุความมั่นคงทางอาหารและยกระดับโภชนาการและส่งเสริมเกษตรกรรมที่ยั่งยืน

☐ 3. สร้างหลักประกันว่าคนมีชีวิตที่มีสุขภาพดีและส่งเสริมสวัสดิภาพสำหรับทุกคนในทุกวัย

☐ 4. สร้างหลักประกันว่าทุกคนมีการศึกษาที่มีคุณภาพอย่างครอบคลุมและเท่าเทียม
และสนับสนุนโอกาสในการเรียนรู้ตลอดชีวิต

☐ 5. บรรลุความเท่าเทียมระหว่างเพศ และเสริมสร้างความเข้มแข็งให้แก่สตรีและเด็กหญิง

☐ 6.
สร้างหลักประกันว่าจะมีการจัดให้มีน้ำและสุขอนามัยสำหรับทุกคนและมีการบริหารจัดการที่ยั่งยืน

☐ 7. สร้างหลักประกันให้ทุกคนสามารถเข้าถึงพลังงานสมัยใหม่ที่ยั่งยืนในราคาที่ย่อมเยา

☐ 8. ส่งเสริมการเติบโตทางเศรษฐกิจที่ต่อเนื่อง ครอบคลุมและยั่งยืน การจ้างงานเต็มที่
มีผลิตภาพและการมีงานที่เหมาะสมสำหรับทุกคน

☑ 9. สร้างโครงสร้างพื้นฐานที่มีความยืดหยุ่นต่อการเปลี่ยนแปลง ส่งเสริมการพัฒนาอุตสาหกรรม

ที่ครอบคลุมและยั่งยืน และส่งเสริมนวัตกรรม

☐ 10. ลดความไม่เสมอภาคภายในประเทศและระหว่างประเทศ

☐ 11. ทำให้เมืองและการตั้งถิ่นฐานของมนุษย์มีความครอบคลุม ปลอดภัย มีภูมิต้านทานและยั่งยืน

☑ 12. สร้างหลักประกันให้มีรูปแบบการผลิตและการบริโภคที่ยั่งยืน

☐ 13. เร่งต่อสู้กับการเปลี่ยนแปลงสภาพภูมิอากาศและผลกระทบที่เกิดขึ้น

☐ 14. อนุรักษ์และใช้ประโยชน์จากมหาสมุทร
ทะเลและทรัพยากรทางทะเลอย่างยั่งยืนเพื่อการพัฒนา ที่ยั่งยืน

☐ 15. ปกป้อง ฟื้นฟู และสนับสนุนการใช้ระบบนิเวศบนบกอย่างยั่งยืน จัดการป่าไม้อย่างยั่งยืน
ต่อสู้กับการกลายสภาพเป็นทะเลทราย หยุดการเสื่อมโทรมของที่ดินและฟื้นสภาพกลับมาใหม่
และหยุดการสูญเสียความหลากหลายทางชีวภาพ

☐ 16. ส่งเสริมสังคมที่สงบสุขและครอบคลุมเพื่อการพัฒนาที่ยั่งยืน ให้ทุกคนเข้าถึงความยุติธรรม
และสร้างสถาบันที่มีประสิทธิผล รับผิดชอบและครอบคลุมในทุกระดับ

☐ 17. ความร่วมมือเพื่อการพัฒนาที่ยั่งยืน

**ส่วน 3 : องค์ประกอบการจัดทำแผนงานวิจัย/โครงการวิจัย**

1.  **ชื่อผู้อำนวยการแผนงานวิจัย (กรณีแผนงานวิจัย)**

+----------------+-------------------------+-------------------+----------------------+
| **ชื่อ-สกุล**     | **สังกัดหน่วยงาน**         | **หมายเลขโทรศัพท์** | **อีเมล**             |
+================+=========================+===================+======================+
| นางสาวจิรภัทร    | หลักสูตร วท.บ.จุลชีววิทยา    | 083 786 1113      | jirapat.c@rbru.ac.th |
| จันทมาลี         |                         |                   |                      |
|                | คณะวิทยาศาสตร์และเทคโนโลยี |                   |                      |
+----------------+-------------------------+-------------------+----------------------+

2.  **ชื่อคณะผู้วิจัยและรายละเอียดความรับผิดชอบ**

+----------------+-------------------------+---------------+------------------------+---------------------------------+
| **ชื่อ-สกุล**     | **สังกัดหน่วยงาน**         | **ตำแหน่ง**    | **สัดส่วนร้อยละการดำเนิน** | **ความรับผิดชอบ**                 |
|                |                         |               |                        |                                 |
|                |                         | **ในโครงการ** | **การวิจัย**             |                                 |
+================+=========================+:=============:+:======================:+=================================+
| นายชีวะ ทัศนา    | หลักสูตร คบ.ฟิสิกส์          | หัวหน้าโครงการ  | > 70                   | บริหารโครงการวิจัย                 |
|                |                         |               |                        | ทำการวิจัยจนสิ้นสุดแผนการทดลองที่วางไว้ |
|                | คณะวิทยาศาสตร์และเทคโนโลยี |               |                        |                                 |
+----------------+-------------------------+---------------+------------------------+---------------------------------+
| นางสาวจิรภัทร    | หลักสูตร วท.บ.\           | ผู้ร่วมวิจัย       | > 20                   | รับผิดชอบร่วมในการทำวิจัย            |
| จันทมาลี         | จุลชีววิทยา                |               |                        | ดำเนินการภาคสนาม/ห้องปฏิบัติการ      |
|                |                         |               |                        | รวบรวมและวิเคราะห์ผลการวิจัย        |
|                | คณะวิทยาศาสตร์และเทคโนโลยี |               |                        |                                 |
+----------------+-------------------------+---------------+------------------------+---------------------------------+
| นางสาววิกันยา    | คณะเทคโนโลยี การเกษตร    | ผู้ร่วมวิจัย       | > 10                   | รับผิดชอบร่วมในการทำวิจัย            |
| ประทุมยศ        |                         |               |                        | ดำเนินการภาคสนาม/ห้องปฏิบัติการ      |
+----------------+-------------------------+---------------+------------------------+---------------------------------+

**3. คำสำคัญ (Keywords) ของโครงการวิจัย (กำหนดไม่เกิน 5 คำ)**

> (ภาษาไทย) ธาตุอาหารในดิน ปัญญาประดิษฐ์ การเรียนรู้ของเครื่อง การสะท้อนแสง
>
> (ภาษาอังกฤษ): Soil Nutrient , Artificial Intelligence, Machine
> Learning, Light Reflection

**4. รูปแบบวิธีการวิจัยจำแนกตามการใช้ประโยชน์**

◻ การวิจัยพื้นฐาน ☑ การวิจัยประยุกต์

**5. สาขาการวิจัย**

สาขาการวิจัยหลัก OECD วิทยาศาสตร์ธรรมชาติ (Natural Sciences)

สาขาการวิจัยย่อย OECD วิทยาศาสตร์กายภาพ (Physical Sciences)

**6. ISCED (International Standard Classification of Education)**

ISCED Broad field 05 - Natural sciences, mathematics and statistics

ISCED Narrow field 053 - Physical sciences

ISCED Detailed field 081 - Agriculture

**ส่วน 4 ข้อมูลแผนงานวิจัย/โครงการวิจัย**

**1. บทสรุปแผนงานวิจัย (ไม่เกิน 3,000 คำ) (เฉพาะกรณีแผนงานวิจัย)**

แผนงานวิจัยนี้มีวัตถุประสงค์เพื่อพัฒนาระบบการจัดการธาตุอาหารพืชแบบบูรณาการที่ยั่งยืนในพื้นที่เกษตรกรรมจังหวัดจันทบุรี/ตราด
โดยมุ่งเน้นที่ธาตุไนโตรเจนและฟอสฟอรัสซึ่งเป็นธาตุอาหารหลัก

**1.1 ปัญหาและโจทย์วิจัยหลัก:**

ภาคเกษตรกรรมของไทยประสบปัญหาหลายประการ เช่น ต้นทุนการผลิตที่สูงขึ้น
และความจำเป็นในการเพิ่มผลผลิต การจัดการธาตุอาหารหลัก โดยเฉพาะไนโตรเจน (N)
และฟอสฟอรัส (P) เป็นปัญหาสำคัญ

1 ปัญหาด้านชีวภาพ (โครงการย่อยที่ 1) ในพื้นที่เกษตรกรรมของจังหวัดจันทบุรี
(พื้นที่ยุทธศาสตร์การผลิตไม้ผลเศรษฐกิจ) การใช้ปุ๋ยเคมีต่อเนื่องทำให้อินทรียวัตถุในดินลดลง
ดินเป็นกรดและความหลากหลายของจุลินทรีย์ดินลดลง
นอกจากนี้ไนโตรเจนและฟอสฟอรัสในดินเกษตรอินทรีย์มักอยู่ในรูปที่พืชดูดซึมใช้ไม่ได้ทันที โจทย์วิจัย
P1 PSB (แบคทีเรียละลายฟอสเฟต) และ NFB (แบคทีเรียตรึงไนโตรเจนอิสระ)
สายพันธุ์ท้องถิ่นจากดินเกษตรอินทรีย์จังหวัดจันทบุรีมีศักยภาพและคุณสมบัติส่งเสริมการเจริญเติบโตของพืช
(PGPR) อื่น ๆ ในระดับใด เพื่อนำมาพัฒนาเป็นชีวภัณฑ์ลดการพึ่งพาปุ๋ยเคมี

2 ปัญหาด้านเทคโนโลยี (โครงการย่อยที่ 2)
การวิเคราะห์ดินตามวิธีมาตรฐานในห้องปฏิบัติการใช้เวลานานและมีค่าใช้จ่ายสูง
ทำให้เกษตรกรส่วนใหญ่ใส่ปุ๋ยไม่เหมาะสม
ซึ่งก่อให้เกิดต้นทุนสูงและมลพิษสิ่งแวดล้อมจากการชะล้างไนโตรเจนและฟอสฟอรัสลงสู่แหล่งน้ำ
แม้จะมีการพัฒนาเครื่องมือวิเคราะห์ด้วยสมาร์ทโฟน ร่วมกับปัญญาประดิษฐ์
แต่ก็ยังมีความคลาดเคลื่อนสูงจากความแปรปรวนของสภาพแสงภายนอกและความแตกต่างของกล้องสมาร์ทโฟน
โจทย์วิจัย P2
จะสามารถพัฒนาชุดวิเคราะห์ไนโตรเจนและฟอสฟอรัสในดินแบบพกพาที่แม่นยำและรวดเร็วโดยบูรณาการหลักการสะท้อนแสงเข้ากับปัญญาประดิษฐ์
เพื่อเอาชนะข้อจำกัดด้านแสงและกล้องสมาร์ทโฟนได้อย่างไร

**วัตถุประสงค์**

โครงการย่อยที่ 1

> 1\. คัดแยกและคัดเลือก PSB และ NFB ที่มีศักยภาพสูงจากดินเกษตรอินทรีย์จังหวัดจันทบุรี
> โดยใช้สมรรถนะการละลายฟอสเฟตและการตรึงไนโตรเจนเป็นเกณฑ์
>
> 2\. จำแนกลักษณะทางสัณฐานวิทยา ชีวเคมี และพันธุกรรม (16S rRNA)
> ของสายพันธุ์ที่คัดเลือก
>
> 3\. ประเมินคุณสมบัติ PGPR เพิ่มเติม เช่น การละลายโพแทสเซียม การยับยั้งเชื้อราก่อมโรค
> และความทนทานต่อสภาวะวิกฤต (กรดสูง ความเค็ม อุณหภูมิสูง)
>
> 4\. จัดทำฐานข้อมูลจุลินทรีย์ท้องถิ่นที่มีศักยภาพสูง
> เพื่อใช้เป็นปัจจัยนำเข้าสำคัญในการพัฒนาโมเดล AI ในโครงการย่อยที่ 2

โครงการย่อยที่ 2

> 1\. ออกแบบและพัฒนาชุดวิเคราะห์ N (Total N) และ P (Available P)
> ในดินแบบพกพาที่เชื่อมต่อกับสมาร์ทโฟน โดยใช้หลักการสะท้อนแสง.
>
> 2\. สร้างและฝึกฝนโมเดลการเรียนรู้ของเครื่อง (ANN และ SVR) ที่สามารถทำนายปริมาณ N
> และ P ในดินได้อย่างแม่นยำและรวดเร็ว
>
> 3\. สร้างและพัฒนาแอปพลิเคชันสมาร์ทโฟนที่ใช้โมเดล AI ร่วมกับชุดวิเคราะห์ดิน
> สำหรับการวิเคราะห์ภาคสนามแบบเรียลไทม์ พร้อมระบบให้คำแนะนำการจัดการปุ๋ยเบื้องต้น.

**3. แนวคิดทฤษฎีที่ใช้เป็นกรอบการวิจัย**

โครงการย่อยที่ 1 (จุลชีววิทยา)

> 1 นิเวศวิทยาจุลินทรีย์ดินเน้นบทบาทของ PSB/NFB ในวัฏจักรธาตุอาหาร (เปลี่ยน P
> ที่ไม่ละลายน้ำเป็นรูปที่พืชใช้ได้ และตรึง N~2~ เป็น NH₄⁺)
>
> 2 Plant Growth Promoting Rhizobacteria (PGPR)
> อธิบายกลไกการส่งเสริมการเจริญเติบโตของพืชทั้งทางตรงและทางอ้อม.
>
> 3 เกษตรกรรมยั่งยืน การใช้ทรัพยากรชีวภาพ (ชีวภัณฑ์) เพื่อลดการพึ่งพาสารเคมี.

โครงการย่อยที่ 2 (เทคโนโลยี/AI)

> 1 สเปกโทรสโกปีแบบสะท้อนแสง อาศัยหลักการดูดกลืนและสะท้อนแสงขององค์ประกอบดิน เช่น
> สารอินทรีย์สัมพันธ์กับไนโตรเจน แร่ธาตุสัมพันธ์กับฟอสฟอรัส
> ข้อมูลที่ได้เป็นชุดข้อมูลสเปกตรัมที่มีมิติสูงและซับซ้อน.
>
> 2 ปัญญาประดิษฐ์และการเรียนรู้ของเครื่อง (AI/ML) ใช้เทคนิค Supervised Learning
> เพื่อถอดรหัสรูปแบบที่ไม่เป็นเชิงเส้นในข้อมูลสเปกตรัม โดยใช้ โครงข่ายประสาทเทียม (ANN)
> และ Support Vector Regression (SVR)
> ซึ่งมีประสิทธิภาพในการจัดการข้อมูลที่ซับซ้อนและมีมิติสูง
>
> 3 คอมพิวเตอร์วิทัศน์ (Computer Vision) ใช้ประมวลผลภาพจากสมาร์ทโฟน
> สกัดคุณลักษณะของภาพด้วยปริภูมิสี HSV และปรับมาตรฐานสีด้วยแผ่นเทียบสีมาตรฐาน
> เพื่อลดความคลาดเคลื่อนจากอุปกรณ์

**4. ระเบียบวิธีการวิจัย**

โครงการย่อยที่ 1

> 1\. การเก็บตัวอย่างและแยกเชื้อ: เก็บดินจากเขตรากพืชในสวนเกษตรอินทรีย์ 5 สวน แยก
> PSB บน Pikovskaya\'s Agar (PVK) และ NFB บน Nitrogen-Free Malate medium
> (NFM agar)
>
> 2\. การคัดเลือกเชิงปริมาณ: วัดประสิทธิภาพการละลายฟอสเฟตด้วยวิธี
> Phosphomolybdenum blue colorimetric assay (880 nm)
> และวัดปริมาณแอมโมเนียมที่ผลิตได้ของ NFB ด้วย Ammonium Assay (425 นาโนเมตร)
>
> 3\. การจำแนกชนิดและประเมิน PGPR:
> จัดจำแนกสายพันธุ์ที่ประสิทธิภาพสูงด้วยการทดสอบชีวเคมีและศึกษาลำดับนิวคลีโอไทด์ของยีน 16S
> rRNA พร้อมประเมินคุณสมบัติ PGPR อื่น ๆ

โครงการย่อยที่ 2

> 1\. การพัฒนาฮาร์ดแวร์ ออกแบบชุดวิเคราะห์ดินแบบพกพาด้วย 3D Printing
> ที่เป็นระบบปิดควบคุมแสงรบกวนภายนอก มีแหล่งกำเนิดแสง LED หลายความยาวคลื่น
> และมีแท่นยึดสมาร์ทโฟนให้ได้มุมคงที่
>
> 2\. การสร้างชุดข้อมูลมาตรฐาน เก็บตัวอย่างดิน 15 ตัวอย่างจากจันทบุรี/ตราด,
> วิเคราะห์หาค่า Ground Truth (Total N: Kjeldahl, Available P: Bray
> II/Olsen) ในห้องปฏิบัติการมาตรฐาน และวัด ลายพิมพ์สเปกตรัม (Spectral
> Fingerprint) ด้วยชุดต้นแบบ
>
> 3\. การพัฒนาและประเมินโมเดล AI แบ่งชุดข้อมูลเพื่อฝึกสอน
> ตรวจสอบและทดสอบฝึกสอนโมเดล ANN และ SVR ประเมินประสิทธิภาพด้วยค่า RMSE และ
> R^2^ เพื่อคัดเลือกโมเดลที่ดีที่สุด
>
> 4\. การทดสอบภาคสนาม นำโมเดลที่ดีที่สุดมาฝังในแอปพลิเคชัน (TensorFlow Lite/Core
> ML) และนำระบบต้นแบบไปทดสอบในพื้นที่จริงที่ยังไม่เคยใช้ในการสร้างชุดข้อมูล
> และเปรียบเทียบผลกับค่าจากห้องปฏิบัติการ

**การบูรณาการ**

แผนงานนี้บูรณาการ 2
โครงการย่อยเพื่อให้ได้ทั้งเครื่องมือวิเคราะห์ที่รวดเร็วและปัจจัยนำเข้าทางชีวภาพที่เหมาะสมกับพื้นที่

  ----------------------------------------------------------------------------------------------------------------------
  **โครงการย่อย**    **วัตถุประสงค์หลัก**                       **วิธีการวิจัยหลัก**                     **ผลผลิตหลัก(Output)**
  ----------------- -------------------------------------- ----------------------------------- -------------------------
  **โครงการย่อยที่ 1   คัดแยก PSB และ NFB                      การเพาะเลี้ยงเชื้อบนอาหารเฉพาะ (PVK,    ฐานข้อมูลจุลินทรีย์ท้องถิ่น และ
  (จุลชีววิทยา)**      สายพันธุ์ท้องถิ่นจากดินเกษตรอินทรีย์ที่มีศักยภาพสูง   NFM) และการวิเคราะห์เชิงปริมาณ          ชีวภัณฑ์จุลินทรีย์ต้นแบ 6-10
                    พร้อมจำแนกลักษณะ (16S rRNA)                                                  สายพันธุ์
                    และประเมินคุณสมบัติ PGPR เพิ่มเติม                                                

  **โครงการย่อยที่ 2   พัฒนาชุดวิเคราะห์ N และ P                  พัฒนาชุดควบคุมแสง                      ชุดวิเคราะห์ดินแบบพกพาต้นแบบ 5
  (AI/เทคโนโลยี)**   ในดินแบบพกพาที่แม่นยำและรวดเร็ว             สร้างชุดข้อมูลมาตรฐานจากค่าห้องปฏิบัติการ,   เครื่อง และแอปพลิเคชัน AI
                    โดยใช้หลักการสะท้อนแสงร่วมกับปัญญาประดิษฐ์     ฝึกสอนโมเดล AI (ANN และ SVR)         พร้อมระบบแนะนำปุ๋ยเบื้องต้น
                    (AI)                                                                       
  ----------------------------------------------------------------------------------------------------------------------

**ความเชื่อมโยงของแผนงานย่อย**

ผลผลิตจากโครงการย่อยที่ 1 คือ ข้อมูลประสิทธิภาพเชิงปริมาณของ PSB และ NFB ท้องถิ่น
จะถูกใช้เป็น ปัจจัยนำเข้าสำคัญ เพื่อพัฒนาและปรับปรุง ระบบแนะนำการจัดการปุ๋ยเบื้องต้น
ในแอปพลิเคชัน AI ของโครงการย่อยที่ 2 การบูรณาการนี้ทำให้เกิด ฐานข้อมูลจุลินทรีย์พื้นเมือง +
AI model
ที่ให้คำแนะนำการใช้ธาตุอาหารและชีวภัณฑ์ที่เหมาะสมกับสภาพดินและพืชในจังหวัดจันทบุรีได้อย่างแม่นยำยิ่งขึ้น

**ผลกระทบที่คาดว่าจะได้รับ**

คาดว่าจะช่วยเกษตรกรลดต้นทุนการผลิตของเกษตรกรได้ 10-20%
จากการลดการใช้ปุ๋ยเคมีไนโตรเจนและฟอสฟอรัสที่ไม่จำเป็น และสามารถลดมลพิษทางดินและน้ำ
เพื่อสนับสนุนการเกษตรกรรม ที่ยั่งยืน โดยโครงการสอดคล้องกับเป้าหมาย SDG 2
(ความมั่นคงทางอาหาร), SDG 12 (การผลิตและการบริโภคที่ยั่งยืน) และ SDG 9 (นวัตกรรม).

**แผนผังเชื่อมโยงโครงการวิจัยย่อยทั้งสอง**

แผนผังนี้แสดงให้เห็นว่าโครงการย่อยทั้งสองทำงานควบคู่กัน
และใช้ผลลัพธ์ของกันและกันเพื่อบรรลุเป้าหมายหลักของแผนงาน:
การจัดการธาตุอาหารที่ยั่งยืนบนฐานข้อมูล.

{width="6.268055555555556in"
height="3.4188156167979002in"}

**\**

**2. หลักการและเหตุผลของโครงการวิจัย**

ภาคเกษตรกรรมเป็นรากฐานสำคัญของเศรษฐกิจไทยและเป็นแหล่งรายได้หลักของประชากรส่วนใหญ่
อย่างไรก็ตามภาคการเกษตรกำลังเผชิญกับความท้าทายที่ซับซ้อนหลายประการทั้งจากปัญหาการเปลี่ยนแปลงสภาพภูมิอากาศ
ต้นทุนการผลิตที่สูงขึ้น
และความจำเป็นในการเพิ่มผลผลิตเพื่อรองรับความมั่นคงทางอาหารของประเทศ
ซึ่งเกษตรแม่นยำได้กลายเป็นแนวทางสำคัญในการจัดการทรัพยากรต่าง ๆ ทางการเกษตร
อย่างมีประสิทธิภาพ
โดยเฉพาะอย่างยิ่งการธาตุอาหารหลักที่จำเป็นต่อการเจริญเติบโตของพืชซึ่งประกอบด้วยไนโตรเจน
(N) ฟอสฟอรัส (P) และโพแทสเซียม (K)
ถ้าดินมีปริมาณธาตุอาหารน้อย/ขาดแคลนหรือมากเกินจะส่งผลกระทบโดยตรงต่อคุณภาพและปริมาณของผลผลิต

การจัดการธาตุอาหารหลักในดิน ไนโตรเจน (N) และฟอสฟอรัส (P)
ซึ่งเป็นธาตุมีความสำคัญมากต่อการเจริญเติบโตของพืช
แต่การวิเคราะห์ปริมาณธาตุอาหารในดินตามวิธีมาตรฐานในห้องปฏิบัติการนั้นใช้เวลานานและมีค่าใช้จ่ายสูง
ทำให้เกษตรกรส่วนใหญ่ไม่มีการส่งดินตรวจวิเคราะห์คุณภาพของดิน
เกษตรกรจึงอาจใส่ปุ๋ยไม่เหมาะสมกับความต้องการของพืชในแต่ละพื้นที่
ซึ่งการใช้ปุ๋ยเกินความจำเป็นไม่เพียงแต่เพิ่มต้นทุนการผลิตแต่ยังก่อให้เกิดปัญหาสิ่งแวดล้อม เช่น
การชะล้างไนโตรเจนและฟอสฟอรัสลงสู่แหล่งน้ำ (Tanaka, T. และคณะ, 2025 Kharel, T.
P. และคณะ,2025) ด้วยเหตุนี้การพัฒนาเครื่องมือวิเคราะห์
ธาตุอาหารในดินแบบพกพาที่สามารถให้ผลลัพธ์ได้ทันทีในภาคสนาม จึงเป็นความจำเป็นเร่งด่วน
ในการยกระดับการเกษตรของประเทศให้เข้าสู่ยุคเกษตร 4.0

แม้ว่าปัจจุบันมีงานวิจัยจำนวนมากมุ่งพัฒนาเทคโนโลยีสำหรับวิเคราะห์คุณภาพดินด้วยสมาร์ทโฟน
ร่วมกับโมเดลปัญญาประดิษฐ์ อย่างไรก็ตามวิธีการต่างๆ
ยังคงมีจุดอ่อนสำคัญคือความคลาดเคลื่อนของผลลัพธ์ที่เกิดจากความแปรปรวนของสภาพแสงภายนอกและความแตกต่างของกล้องสมาร์ทโฟนแต่ละรุ่น
(Kılıç, V. และคณะ ,2018)
และงานวิจัยที่มีอยู่ส่วนใหญ่มักเน้นการวิเคราะห์ในห้องปฏิบัติการหรือใช้เทคนิค
สเปกโทรสโกปีที่มีราคาสูง (Shin, S. K. และคณะ, 2025). และโมเดลการเรียนรู้ของเครื่อง
(Machine Learning) ที่พัฒนาขึ้นมักฝึกสอนด้วยข้อมูลจากต่างประเทศ (Mondal, B. P
และคณะ. ,2025) ซึ่งอาจจะ ไม่เหมาะสมกับสภาพดินในท้องถิ่น
ดังนั้นโครงการวิจัยการพัฒนาชุดวิเคราะห์ธาตุไนโตรเจนและฟอสฟอรัสในดินแบบพกพาด้วยหลักการสะท้อนแสงร่วมกับปัญญาประดิษฐ์จึงมุ่งเน้นการแก้ไขช่องว่างดังกล่าว
โดยการบูรณาการหลักการสะท้อนแสงเข้ากับชุดวิเคราะห์ที่ออกแบบมาเป็นพิเศษเพื่อควบคุมสภาพแสงและ
ใช้ปัญญาประดิษฐ์ (Artificial Intelligence) เพื่อจัดการกับความคลาดเคลื่อนของข้อมูล
(Folorunso, O. และคณะ, 2025 , Mondal, B. P. และคณะ ,2025)

โครงการวิจัยนี้มีวัตถุประสงค์เพื่อการพัฒนาชุดวิเคราะห์ธาตุไนโตรเจนและฟอสฟอรัสในดินแบบพกพาโดยใช้หลักการสะท้อนแสงร่วมกับโมเดลปัญญาประดิษฐ์และแอปพลิเคชันสมาร์ทโฟนเพื่อวิเคราะห์ปริมาณของไนโตรเจนทั้งหมด(
Total N) และฟอสฟอรัสที่เป็นประโยชน์ (Available P)
ในดินที่ให้มีความแม่นยำสูงและสามารถนำไปใช้งานภาคสนามได้

**3. วัตถุประสงค์ของการวิจัย**

> 1\. เพื่อออกแบบและพัฒนาชุดวิเคราะห์ปริมาณไนโตรเจนทั้งหมด และฟอสฟอรัสที่เป็นประโยชน์
> ในดินแบบพกพาที่เชื่อมต่อกับสมาร์ทโฟนโดยใช้หลักการสะท้อนแสง
>
> 2.เพื่อสร้างและฝึกฝนโมเดลการเรียนรู้ของเครื่องที่สามารถทำนายปริมาณไนโตรเจนทั้งหมดและฟอสฟอรัสที่เป็นประโยชน์ในดินให้มีความแม่นยำและรวดเร็ว
>
> 3\. เพื่อสร้างและพัฒนาแอปพลิเคชันสมาร์ทโฟนที่ใช้โมเดลการเรียนรู้ของเครื่องร่วมกับ
> ชุดวิเคราะห์ดินฯ สำหรับการวิเคราะห์ปริมาณไนโตรเจนทั้งหมดและฟอสฟอรัสที่เป็นประโยชน์
> ในภาคสนามแบบเรียลไทม์พร้อมระบบให้คำแนะนำการจัดการปุ๋ยเบื้องต้น

**4. กรอบการวิจัย/พัฒนา**

โครงการวิจัยนี้เป็นการบูรณาเชื่อมโยงการออกแบบและพัฒนาเครื่องมือวัดอิเล็กทรอนิกส์และเซนเซอร์และหลักการสะท้อนแสงเข้ากับเทคโนโลยีปัญญาประดิษฐ์
โมเดลการเรียนรู้ของเครื่องและการเรียนรู้เชิงลึก
เพื่อสร้างและพัฒนาเครื่องมือวิเคราะห์ปริมาณไนโตรเจนและฟอสฟอรัสในดิน
แบบพกพาสำหรับเกษตรกรใช้งานจริงในภาคสนาม ซึ่งมีกระบวนการหลัก 3 ขั้นตอน
ดังแสดงในแผนผัง



**4.1 ที่มาและแนวคิด**

เริ่มต้นจากปัญหาการวิเคราะห์ไนโตรเจนทั้งหมดและฟอสฟอรัสที่เป็นประโยชน์ในดินแบบดั้งเดิมค่อนข้างมีความล้าช้า
ราคาแพงและเข้าถึงค่อนข้างยาก นำมาสู่แนวคิดการใช้หลักการสะท้อนแสง
มาทำงานร่วมกับปัญญาประดิษฐ์เพื่อเพิ่มความแม่นยำในการวิเคราะห์ดิน

**4.2 กระบวนการพัฒนา**

การบวนการพัฒนาแบ่งเป็น 2 ส่วน คือการพัฒนาฮาร์ดแวร์ด้วยการสร้างชุดวิเคราะห์ดิน
ด้วยหลักการสะท้อนแสงที่สามารถควบคุมแสงได้ และ
การพัฒนาซอฟต์แวร์ด้วยการสร้างชุดข้อมูลและฝึกสอนโมเดลการเรียนรู้เชิงลึก
จากนั้นนำทั้งสองส่วนมาบูรณาการเข้าด้วยกันเป็นระบบต้นแบบ

> **4.3 ผลลัพธ์และเป้าหมาย**

เมื่อพัฒนาชุดวิเคราะห์ดินเสร็จสิ้น
จะได้ผลลัพธ์เป็นระบบวิเคราะห์ดินต้นแบบที่ประกอบด้วยชุดวิเคราะห์ดินและแอปพลิเคชันสมาร์ทโฟนซึ่งจะถูกนำไปทดสอบภาคสนามเพื่อตรวจสอบความถูกต้องแม่นยำ
และนำไปสู่เป้าหมายสูงสุด คือ เครื่องมือวิเคราะห์ดินที่แม่นยำ รวดเร็ว
และเข้าถึงง่ายสำหรับเกษตรกรในการวิเคราะห์ปริมาณไนโตรเจนทั้งหมดและฟอสฟอรัสที่เป็นประโยชน์ในดินในภาคสนาม
แบบเรียลไทม์พร้อมระบบให้คำแนะนำการจัดการปุ๋ยเบื้องต้น

**5. แนวคิด ทฤษฎี และสมมติฐานงานวิจัย**

**5.1 แนวคิดและทฤษฎีที่เกี่ยวข้อง**

โครงการวิจัยนี้นำหลักการทางฟิสิกส์ เคมี และวิทยาการคอมพิวเตอร์ มาประยุกต์ใช้ร่วมกัน
เพื่อแก้ปัญหาที่ซับซ้อนโดยมีทฤษฎีและแนวคิดที่สำคัญ 4 ข้อ ดังนี้

**1. สเปกโทรสโกปีแบบสะท้อนแสง**

การใช้สเปกโทรสโกปีแบบสะท้อนแสง (Reflectance Spectroscopy) เป็นเทคนิค
การวิเคราะห์ที่ไม่ทำลายตัวอย่างและไม่ต้องใช้สารเคมี
อาศัยหลักการเมื่อแสงตกกระทบลงบนพื้นผิวของดิน
แสงบางส่วนจะถูกดูดกลืนและบางส่วนจะสะท้อนออกมาโดยโมเลกุลและสารประกอบต่าง ๆ
ที่เป็นองค์ประกอบของดิน เช่น สารอินทรีย์ แร่ธาตุต่าง ๆ และความชื้น
มีรูปแบบการดูดกลืนพลังงานแสงที่ความยาวคลื่นต่าง ๆ ที่เป็นเอกลักษณ์เฉพาะตัว
โดยเฉพาะอย่างยิ่งในช่วงคลื่นแสงที่ตามองเห็น (400-700 นาโนเมตร) และย่านใกล้อินฟราเรด
(Near-Infrared, NIR, 700-2500 นาโนเมตร) ดังนั้นจึงสามารถนำมาประยุกต์ใช้
ในโครงการนี้ได้ ทั้งนี้โดยทั่วไปแล้วไนโตรเจน (N) ในดินจะอยู่ในรูปของสารประกอบอินทรีย์
ปริมาณไนโตรเจนทั้งหมดจึงมีความสัมพันธ์อย่างสูงกับปริมาณสารอินทรีย์ในดิน
ซึ่งมีคุณสมบัติดูดกลืนแสงอย่างยิ่งในช่วงคลื่นย่านใกล้อินฟาเรด ดังนั้น
เราสามารถอนุมานปริมาณไนโตรเจนโดยอ้อมได้จากการวิเคราะห์สเปกตรัมการสะท้อนแสงที่สัมพันธ์กับ
ปริมาณสารอินทรีย์ และฟอสฟอรัสในดินมักอยู่ในรูปของสารประกอบอนินทรีย์ เช่น
ฟอสเฟตที่จับกับแคลเซียม เหล็กหรืออะลูมิเนียม
ซึ่งอาจไม่มีแถบการดูดกลืนที่ชัดเจนและโดดเด่นเหมือนสารอินทรีย์
อย่างไรก็ตามรูปแบบสเปกตรัมโดยรวม ซึ่งเป็นผลรวมที่ซับซ้อนของการสะท้อนแสงจากแร่ธาตุต่าง ๆ
และองค์ประกอบอื่น ๆ ในดิน ยังคงมีข้อมูลแฝงที่สัมพันธ์กับปริมาณฟอสฟอรัสอยู่
ดังนั้นแทนที่จะวัดการดูดกลืนแสงของสารละลายเราจะวัดสเปกตรัมการสะท้อนแสงของดินโดยตรงข้อมูลที่ได้จะไม่ใช่ค่าการดูดกลืนแสง
ณ ความยาวคลื่นเดียว
แต่จะเป็นชุดข้อมูลสเปกตรัมที่มีความซับซ้อนและมีมิติสูงซึ่งเป็นข้อมูลที่ตามนุษย์หรือสมการเชิงเส้นธรรมดาไม่สามารถตีความได้
จึงเป็นที่มาของความจำเป็นในการใช้เครื่องมือ ทางคณิตศาสตร์ขั้นสูงอย่างปัญญาประดิษฐ์

**2. ปัญญาประดิษฐ์และการเรียนรู้ของเครื่อง**

เมื่อข้อมูลที่ได้จากเซนเซอร์มีความซับซ้อนและไม่เป็นเชิงเส้น (Non-linear)
การใช้สมการถดถอยเชิงเส้นแบบดั้งเดิมจึงไม่เพียงพอ
โครงการนี้จึงนำเทคนิคการเรียนรู้ของเครื่องเข้ามาเป็นเครื่องมือสำคัญในการถอดรหัสรูปแบบที่ซ่อนอยู่ในสเปกตรัมการสะท้อนแสงของดินโดยใช้แนวคิด
การเรียนรู้แบบมีผู้สอน (Supervised Learning)
ด้วยการสร้างชุดข้อมูลสำหรับสอนโมเดลปัญญาประดิษฐ์ โดยแต่ละตัวอย่างข้อมูลจะประกอบด้วย 2
ส่วน คือ ข้อมูลนำเข้า (Input) ซึ่งก็คือข้อมูลสเปกตรัมการสะท้อนแสงของดินตัวอย่าง และ
ข้อมูลเป้าหมาย (Target/Label) ซึ่งคือค่าปริมาณ
ไนโตรเจนทั้งหมดและฟอสฟอรัสที่เป็นประโยชน์ที่แท้จริงของดินตัวอย่างนั้น ๆ
ที่ได้จากการวิเคราะห์ด้วยวิธีมาตรฐานในห้องปฏิบัติการ
โมเดลปัญญาประดิษฐ์จะเรียนรู้ที่จะสร้างฟังก์ชันทางคณิตศาสตร์ที่สามารถจับคู่ความสัมพันธ์ระหว่างข้อมูลนำเข้าและข้อมูลเป้าหมายได้อย่างแม่นยำ
โมเดลปัญญาประดิษฐ์ที่เลือกใช้ในโครงการนี้ เราจะเลือกใช้โครงข่ายประสาทเทียม
(Artificial Neural Network - ANN)
ซึ่งเป็นโมเดลที่ได้รับแรงบันดาลใจจากโครงสร้างสมองมนุษย์มีความสามารถที่โดดเด่นในการเรียนรู้และจำลองความสัมพันธ์ที่ซับซ้อนและไม่เป็นเชิงเส้นได้ดีเยี่ยมทำให้
ANN
เหมาะสมอย่างยิ่งกับการวิเคราะห์ข้อมูลสเปกตรัมซึ่งมีความสัมพันธ์กับปริมาณธาตุอาหารที่ซับซ้อนและถูกรบกวนจากปัจจัยหลายอย่างพร้อมกัน
เช่น ความชื้น ขนาดอนุภาคดินและองค์ประกอบแร่ธาตุอื่น ๆ และโมเดล Support Vector
Regression (SVR) ซึ่งเป็นอีกหนึ่งโมเดลที่ทรงพลัง
มีจุดเด่นในการจัดการกับชุดข้อมูลที่มีมิติสูงได้ดี
และมักให้ผลลัพธ์ที่ดีแม้จะมีข้อมูลสำหรับฝึกสอนไม่มากเท่า ANN การนำ SVR มาเปรียบเทียบกับ
ANN จะช่วยให้สามารถเลือกโมเดลที่มีประสิทธิภาพสูงสุดสำหรับบริบทของดิน
ในจังหวัดจันทบุรีและตราดได้

การใช้ปัญญาประดิษฐ์ในโครงการวิจัยนี้ไม่ใช่แค่การสร้างสมการแต่เป็นการสร้างผู้เชี่ยวชาญเสมือนที่สามารถตีความสเปกตรัมของดินและทำนายปริมาณไนโตรเจนทั้งหมด(
Total N) และฟอสฟอรัสที่เป็นประโยชน์ (Available P) ในดินได้อย่างแม่นยำและรวดเร็ว

**3. คอมพิวเตอร์วิทัศน์และการประมวลผลภาพ**

แม้ว่าชุดวิเคราะห์ที่ออกแบบมาจะมีการควบคุมแสงแต่ภาพถ่ายที่ได้จากกล้องสมาร์ทโฟนยังคงต้องผ่านกระบวนการประมวลผลเพื่อดึงข้อมูลเชิงแสงที่สำคัญออกมาและลดทอนสัญญาณรบกวนโดยการสกัดคุณลักษณะของภาพด้วยการแปลงภาพให้อยู่ในปริภูมิสี
HSV (Hue, Saturation, Value) ซึ่งสามารถแยกคุณลักษณะของสีออกจากความสว่างได้ดีกว่า
จากนั้นจะทำการสกัดค่าทางสถิติของสีจากบริเวณที่สนใจ (Region of Interest - ROI) เช่น
ค่าเฉลี่ย, ค่ามัธยฐาน, หรือฮิสโตแกรมของสี เพื่อใช้เป็นข้อมูลนำเข้าสำหรับโมเดลปัญญาประดิษฐ์

นอกจากนี้แล้วเรายังต้องมีการแก้ไขและปรับมาตรฐานที่เกิดจากความแตกต่างของเซนเซอร์กล้องสมาร์ทโฟนแต่ละรุ่นที่ต้องใช้เทคนิคการปรับแก้สีด้วยการถ่ายภาพแผ่นเทียบสีมาตรฐาน
ที่รวมอยู่ในชุดวิเคราะห์ เพื่อสร้างโปรไฟล์สำหรับปรับแก้ค่าสีที่อ่านได้จากกล้อง
แต่ละตัวให้มีมาตรฐานใกล้เคียงกัน
ซึ่งจะช่วยเพิ่มความแม่นยำและความสามารถในการทำซ้ำของระบบได้อย่างมีนัยสำคัญ

**4. ชุดวิเคราะห์ปริมาณไนโตรเจนและฟอสฟอรัสในดินแบบพกพา**

บูรณาการองค์ประกอบทั้งสามข้างต้นให้ทำงานร่วมกันได้อย่างราบรื่นในรูปแบบของระบบและแอปพลิเคชันที่ผู้ใช้สามารถเข้าถึงได้ง่าย
ประกอบด้วย ชุดวิเคราะห์ดินแบบพกพาทำหน้าที่เป็นห้องปฏิบัติการขนาดเล็กควบคุมสภาพแวดล้อม
แหล่งกำเนิดแสงเอลอีดี ตำแหน่งตัวอย่างดิน ตำแหน่งกล้องสมาร์ทโฟนให้คงที่
และแอปพลิเคชันบนสมาร์ทโฟนที่ทำหน้าที่หลายอย่างพร้อมกันตั้งแต่การควบคุมการถ่ายภาพ
การประมวลผลภาพเพื่อสกัดข้อมูลสี การส่งข้อมูลไปยังโมเดลปัญญาประดิษฐ์ที่ฝังอยู่ในแอปพลิเคชัน
การรับผล
การทำนายไปจนถึงการแสดงผลลัพธ์และคำแนะนำการใช้ปุ๋ยเบื้องต้นในรูปแบบที่เข้าใจง่าย

**5.2 สมมติฐานงานวิจัย**

โครงการวิจัยนี้ได้ตั้งสมมติฐานหลัก 3 ข้อ ซึ่งสอดคล้องกับวัตถุประสงค์ของโครงการ

1 สมมติฐานข้อที่ 1 ความสัมพันธ์ของข้อมูล

> $H_{0}$ (สมมติฐานว่าง) ข้อมูลสเปกตรัมการสะท้อนแสงของดินที่ได้จากชุดวิเคราะห์ที่พัฒนาขึ้น
> ไม่มีความสัมพันธ์ที่มีนัยสำคัญทางสถิติกับปริมาณไนโตรเจนและฟอสฟอรัส
> ที่วิเคราะห์ด้วยวิธีมาตรฐาน
>
> $H_{1}$ ( (สมมติฐานทางเลือก)
> ข้อมูลสเปกตรัมการสะท้อนแสงของดินที่ได้จากชุดวิเคราะห์ที่พัฒนาขึ้นมีความสัมพันธ์ที่มีนัยสำคัญทางสถิติกับปริมาณไนโตรเจนและฟอสฟอรัส
> ที่วิเคราะห์ด้วยวิธีมาตรฐานซึ่งความสัมพันธ์นี้อาจมีความซับซ้อนและไม่เป็นเชิงเส้น

2 สมมติฐานข้อที่ 2 ประสิทธิภาพของโมเดลปัญญาประดิษฐ์

> $H_{0}$ ( (สมมติฐานว่าง) โมเดลการเรียนรู้ของเครื่อง ANN และ SVR
> ที่ฝึกสอนด้วยข้อมูลสเปกตรัมการสะท้อนแสงไม่สามารถทำนายปริมาณไนโตรเจนและฟอสฟอรัสในดินได้แม่นยำกว่าการคาดเดาแบบสุ่มงและค่าสัมประสิทธิ์การตัดสินใจเข้าใกล้ศูนย์
>
> $H_{1}$ (สมมติฐานทางเลือก) โมเดลการเรียนรู้ของเครื่อง ANN และ SVR
> ที่ฝึกสอนด้วยข้อมูลสเปกตรัมการสะท้อนแสงสามารถทำนายปริมาณไนโตรเจนและฟอสฟอรัสในดินได้อย่างมีนัยสำคัญทางสถิติ
> โดยให้ค่าความคลาดเคลื่อนต่ำและค่าสัมประสิทธิ์ การตัดสินใจสูง
> เมื่อเปรียบเทียบกับค่าจริงจากห้องปฏิบัติการ

3 สมมติฐานข้อที่ 3 การใช้งานจริงของระบบ

> $H_{0}$ (สมมติฐานว่าง) ระบบวิเคราะห์ดินต้นแบบที่บูรณาการฮาร์ดแวร์และซอฟต์แวร์
> ไม่สามารถให้ผลการวิเคราะห์ปริมาณไนโตรเจนและฟอสฟอรัสในภาคสนามที่มีความแม่นยำสอดคล้องกับผลจากห้องปฏิบัติการได้
>
> $H_{1}$ (สมมติฐานทางเลือก)
> ระบบวิเคราะห์ดินต้นแบบที่บูรณาการฮาร์ดแวร์และซอฟต์แวร์สามารถให้ผลการวิเคราะห์ปริมาณไนโตรเจนและฟอสฟอรัสในภาคสนามแบบเรียลไทม์ที่มีความแม่นยำสูงและมีความสอดคล้องอย่างมีนัยสำคัญกับผลที่ได้จากวิธีวิเคราะห์มาตรฐานในห้องปฏิบัติการ

**5.3 การทบทวนวรรณกรรม/สารสนเทศ (information) ที่เกี่ยวข้อง**

การวิจัยเพื่อพัฒนาเครื่องมือวิเคราะห์ดินแบบรวดเร็วและไม่ใช้สารเคมี
ได้รับความสนใจเป็นอย่างมาก
โดยมีงานวิจัยที่เกี่ยวข้องซึ่งเป็นรากฐานและชี้ให้เห็นถึงโอกาสในการพัฒนาต่อยอดดังนี้

การใช้สเปกโทรสโกปีร่วมกับปัญญาประดิษฐ์เพื่อทำนายคุณสมบัติดินนั้นได้รับการยอมรับอย่างกว้างขวาง
Shin, S. K. และคณะ (2025) ได้สรุปและยืนยันว่าเทคนิคสเปกโทรสโกปีในย่าน ใกล้อินฟาเรด
(Vis-NIR) เป็นเครื่องมือที่ทรงพลังอย่างยิ่งในการทำนายคุณสมบัติดินหลายชนิดพร้อมกัน
รวมถึงสารอินทรีย์คาร์บอนซึ่งสัมพันธ์กับไนโตรเจนและแร่ธาตุต่างๆ
งานวิจัยนี้เป็นเครื่องยืนยันว่าข้อมูลสเปกตรัมมีข้อมูลที่จำเป็นสำหรับการทำนายอยู่จริง
แต่ก็ชี้ให้เห็นถึงข้อจำกัดด้านราคาของเครื่องมือที่ใช้ในงานวิจัยส่วนใหญ่
ซึ่งเป็นช่องว่างที่โครงการของเรามุ่งจะแก้ไขโดยการพัฒนาฮาร์ดแวร์ต้นทุนต่ำ ในขณะเดียวกัน
ความพยายามในการลดต้นทุนโดยการใช้กล้องสมาร์ทโฟนก็มีทิศทางที่น่าสนใจ
แต่ก็เต็มไปด้วยความท้าทาย ดังที่ Kılıç V.,และคณะ (2018)
ได้ชี้ให้เห็นอย่างชัดเจนในการศึกษา การวัดคุณภาพน้ำเชิงสีว่า
ความผันผวนของแสงแวดล้อมและความแตกต่างของกล้องแต่ละรุ่นเป็นอุปสรรคสำคัญต่อความแม่นยำและน่าเชื่อถือของผลลัพธ์
บทเรียนจากงานวิจัยนี้มีความสำคัญอย่างยิ่งต่อโครงการของเรา
และเป็นเหตุผลหลักที่อยู่เบื้องหลังการออกแบบชุดวิเคราะห์ที่ควบคุมแสงได้เพื่อกำจัดปัจจัยรบกวนนี้ตั้งแต่ต้นทาง
ซึ่งเป็นแนวทางที่แตกต่างจากแอปพลิเคชันวิเคราะห์ดินด้วยภาพถ่ายส่วนใหญ่ที่ไม่ได้คำนึงถึงปัญหานี้อย่างจริงจัง

เมื่อพิจารณาในเรื่องของซอฟต์แวร์/แอปพลิเคชัน
การใช้การเรียนรู้ของเครื่องและการเรียนรู้เชิงลึกเพื่อตีความข้อมูลที่ซับซ้อนจากดินได้รับการพิสูจน์แล้วว่ามีประสิทธิภาพสูง
Mondal B.P.,และคณะ (2025)
ได้ทำการเปรียบเทียบโมเดลการเรียนรู้ของเครื่องหลายชนิดและสรุปว่าเทคนิคเหล่านี้
โดยเฉพาะโมเดลที่จัดการความสัมพันธ์ไม่เชิงเส้นได้ดี เช่น ANN และ SVR
มีความสามารถสูงในการทำนายปริมาณธาตุอาหารในดิน
ซึ่งสนับสนุนการตัดสินใจเลือกใช้โมเดลในโครงการของเราโดยตรง นอกจากนี้ งานวิจัยของ
Folorunso O. และคณะ (2025) ที่พัฒนาแอปพลิเคชันแล้วยังเป็นต้นแบบ
ที่ดีของการนำผลลัพธ์จากโมเดลปัญญาประดิษฐ์มาสร้างเป็นเครื่องมือที่ใช้งานได้จริงบนสมาร์ทโฟน
พร้อมระบบให้คำแนะนำเบื้องต้น
ซึ่งเป็นแนวทางที่โครงการของเราจะดำเนินการในขั้นตอนสุดท้ายเพื่อส่งมอบนวัตกรรมสู่มือเกษตรกร
ท้ายที่สุดการเชื่อมโยงข้อมูลภาพถ่ายเข้ากับสถานะธาตุอาหารของพืชโดยตรงก็เป็นอีกหนึ่งหลักฐานสนับสนุนที่สำคัญ
แม้ว่างานวิจัยของ Tanaka T. และคณะ (2025) และ Kharel T.P. และคณะ (2025)
จะเน้นที่การวิเคราะห์ภาพถ่ายจากพืช UAV และภาพหลายช่วงคลื่น
แต่ก็เป็นการยืนยันหลักการที่ว่าข้อมูลเชิงแสงมีความสัมพันธ์กับสถานะทางเคมี
ซึ่งสามารถนำหลักการเดียวกันนี้มาประยุกต์ใช้กับดินได้

**6. ระเบียบวิธีวิจัยและวิธีการดำเนินการวิจัย**

โครงการวิจัยนี้เป็นการวิจัยเชิงทดลองและพัฒนาที่มีเป้าหมายเพื่อสร้างนวัตกรรมที่เป็นระบบบูรณาการระหว่างฮาร์ดแวร์และซอฟต์แวร์
แบ่งออกเป็น 4 ขั้นตอน ประกอบด้วย

**6.1 ขั้นตอนที่ 1 การออกแบบและสร้างระบบต้นแบบฮาร์ดแวร์**

การสร้างชุดวิเคราะห์ฮาร์ดแวร์ที่สามารถวัดสเปกตรัมการสะท้อนแสงของดินได้อย่างเสถียรและทำซ้ำได้
โดยการควบคุมตัวแปรทางแสงและกายภาพให้คงที่ประกอบด้วย

6.1.1 การออกแบบชุดวิเคราะห์

ออกแบบโครงสร้างตัวกล่องด้วย Tinkercad ให้เป็นระบบปิดเพื่อป้องกันแสงรบกวน
จากภายนอกโดยสมบูรณ์ และติดตั้งแหล่งกำเนิดแสง LED
ที่มีความยาวคลื่นครอบคลุมช่วงแสงในย่านที่ตามองเห็น (Visible) และย่านใกล้อินฟราเรด
(NIR) ที่สำคัญต่อการวิเคราะห์ดินโดยจัดวางตำแหน่งของ LED
ให้ส่องสว่างไปยังพื้นผิวตัวอย่างดินอย่างสม่ำเสมอ และออกแบบช่องสำหรับวางตัวอย่างดิน (Soil
Sample Holder) และแท่นยึดสมาร์ทโฟน (Smartphone Mount)
ให้มีระยะห่างและมุมระหว่างกล้องกับพื้นผิวตัวอย่างดินคงที่เสมอเพื่อให้ได้ภาพที่มีขนาดและมุมมองเดียวกันทุกครั้ง

6.1.2 การสร้างและประกอบชุดวิเคราะห์ต้นแบบ

ผลิตชิ้นส่วนโครงสร้างตามแบบที่ออกแบบไว้ด้วยการพิมพ์สามมิติแล้วประกอบชิ้นส่วนทั้งหมดเข้าด้วยกันพร้อมติดตั้งวงจรอิเล็กทรอนิกส์สำหรับควบคุมการเปิด-ปิดแหล่งกำเนิดแสง
และเชื่อมต่อกับสมาร์ทโฟนผ่าน Bluetooth หรือ USB-OTG
เพื่อให้แอปพลิเคชันสามารถสั่งการได้เป็นชุดวิเคราะห์ต้นแบบที่พร้อมใช้งาน

**6.2 ขั้นตอนที่ 2 การสร้างชุดข้อมูลมาตรฐานสำหรับการฝึกสอนโมเดล**

สร้างชุดข้อมูล (Dataset) คุณภาพสูงที่จับคู่ระหว่างข้อมูลสเปกตรัมการสะท้อนแสงของดินกับ
ค่าปริมาณไนโตรเจนและฟอสฟอรัสที่แท้จริงสำหรับใช้ในการฝึกสอนและทดสอบโมเดลปัญญาประดิษฐ์

6.2.1 การเก็บตัวอย่างดิน

เก็บตัวอย่างดินจากพื้นที่เกษตรกรรมเป้าหมาย เช่น สวนผลไม้ในจังหวัดจันทบุรีและตราด
โดยเลือกพื้นที่ที่มีความหลากหลายของชนิดดิน
ประวัติการใช้ปุ๋ยและลักษณะทางกายภาพที่แตกต่างกันเพื่อให้ชุดข้อมูลมีความครอบคลุมจำนวนตัวอย่างเบื้องต้น
15 ตัวอย่าง บันทึกข้อมูลประกอบ ของแต่ละจุดเก็บตัวอย่าง เช่น พิกัด GPS
ชนิดพืชที่ปลูกและลักษณะทางกายภาพของดิน

6.2.2 การวิเคราะห์ค่าอ้างอิงในห้องปฏิบัติการ

นำดินแต่ละตัวอย่างส่งไปยังห้องปฏิบัติการที่ได้มาตรฐานเพื่อวิเคราะห์หาค่าปริมาณไนโตรเจนทั้งหมด
(Total Nitrogen) และฟอสฟอรัสที่เป็นประโยชน์ (Available Phosphorus)
ด้วยวิธีวิเคราะห์มาตรฐาน (เช่น วิธี Kjeldahl สำหรับ N และวิธี Bray II หรือ Olsen
สำหรับ P) ผลลัพธ์ที่ได้จะถูกใช้เป็นค่า คำตอบที่ถูกต้อง (Ground Truth)
สำหรับการฝึกสอนโมเดล

6.2.3 การวัดข้อมูลสเปกตรัมด้วยชุดวิเคราะห์ต้นแบบ

นำดินแต่ละตัวอย่างที่ผ่านการเตรียมเบื้องต้น เช่น ผึ่งลมให้แห้งและร่อนผ่านตะแกรง
มาใส่ในช่องวางตัวอย่างของชุดวิเคราะห์ฮาร์ดแวร์ที่สร้างขึ้นในขั้นตอนที่ 1
ใช้แอปพลิเคชันที่พัฒนาขึ้นเบื้องต้นสั่งการให้ LED แต่ละดวงติดสว่างทีละดวง
และให้กล้องสมาร์ทโฟนถ่ายภาพพื้นผิวดินภายใต้แสงแต่ละความยาวคลื่น
ทำการประมวลผลภาพเบื้องต้น (Image Processing)
เพื่อสกัดค่าความเข้มของสีจากบริเวณที่สนใจของแต่ละภาพ ผลลัพธ์ที่ได้คือ ลายพิมพ์สเปกตรัม
(Spectral Fingerprint) ของดินแต่ละตัวอย่าง แล้วดำเนินการจนครบทุกตัวอย่างดิน
และทำการจับคู่ ลายพิมพ์สเปกตรัมกับ ค่ไนโตรเจนและฟอสฟอรัสอ้างอิงที่ได้จากห้องปฏิบัติการ
เพื่อสร้างเป็นชุดข้อมูลมาตรฐานที่สมบูรณ์

**6.3 ขั้นตอนที่ 3 การพัฒนาและประเมินผลโมเดลปัญญาประดิษฐ์**

สร้างและคัดเลือกโมเดลการเรียนรู้ของเครื่องที่สามารถทำนายปริมาณไนโตรเจนและฟอสฟอรัสจากข้อมูลสเปกตรัมได้อย่างแม่นยำที่สุด

6.3.1 การเตรียมข้อมูล

นำชุดข้อมูลมาตรฐานที่สร้างในขั้นตอนที่ 2 ที่ผ่านการตรวจสอบความผิดปกติแล้ว แบ่งออกเป็น 3
ชุดข้อมูล คือ ชุดข้อมูลสำหรับฝึกสอน (Training Set : 70-80%) ชุดข้อมูลสำหรับตรวจสอบ
(Validation Set : 10-15%) และชุดข้อมูลสำหรับทดสอบ (Test Set, 10-15%)

6.3.2 การสร้างและฝึกสอนโมเดล

นำชุดข้อมูลสำหรับทดสอบมาใช้ในการฝึกสอนโมเดลการเรียนรู้ของเครื่องที่เลือกไว้คือโครงข่ายประสาทเทียม
(ANN) และ Support Vector Regression (SVR) โดยในระหว่างการฝึกสอน
จะใช้ชุดข้อมูลสำหรับตรวจสอบเพื่อปรับจูนพารามิเตอร์ของโมเดล และป้องกันการเกิด
Overfitting (การที่โมเดลทำงานได้ดีกับข้อมูลที่ใช้สอนเท่านั้น แต่ทำงานได้ไม่ดีกับข้อมูลใหม่)

6.3.3 การประเมินและคัดเลือกโมเดล

นำชุดข้อมูลสำหรับทดสอบซึ่งเป็นข้อมูลที่โมเดลไม่เคยเห็นมาก่อนมาใช้ประเมินประสิทธิภาพสุดท้ายของโมเดลที่ฝึกสอนเสร็จแล้ว
โดยใช้เกณฑ์วัดทางสถิติในการประเมิน ได้แก่ ค่าความคลาดเคลื่อนรากของกำลังสองเฉลี่ย (Root
Mean Square Error - RMSE) เพื่อดูความแม่นยำ และค่าสัมประสิทธิ์การตัดสินใจ
(Coefficient of Determination - R²)
เพื่อดูความสามารถในการอธิบายความแปรปรวนของข้อมูล
แล้วเปรียบเทียบประสิทธิภาพระหว่างโมเดล ANN และ SVR
แล้วคัดเลือกโมเดลที่ดีที่สุดเพื่อนำไปใช้งานในขั้นตอนต่อไป

**6.4 ขั้นตอนที่ 4 การพัฒนาระบบบูรณาการและทดสอบภาคสนาม**

นำโมเดลปัญญาประดิษฐ์ที่ดีที่สุดมาผนวกรวมกับแอปพลิเคชันและฮาร์ดแวร์
สร้างเป็นระบบต้นแบบที่สมบูรณ์ และนำไปประเมินประสิทธิภาพการใช้งานจริงในภาคสนาม

6.4.1 การพัฒนาแอปพลิเคชันเวอร์ชันสมบูรณ์

นำโมเดลปัญญาประดิษฐ์ที่คัดเลือกไว้ในขั้นตอนที่ 3 มาฝัง (Embed)ลงในแอปพลิเคชันบนสมาร์ทโฟน
(ผ่าน TensorFlow Lite หรือ Core ML) โดยพัฒนาส่วนต่อประสานกับผู้ใช้ (User
Interface - UI) ให้ใช้งานง่าย มีขั้นตอนแนะนำการใช้งานที่ชัดเจน
พัฒนาระบบแสดงผลลัพธ์ปริมาณไนโตรเจนและฟอสฟอรัสพร้อมระบบให้คำแนะนำการจัดการปุ๋ยเบื้องต้นโดยอ้างอิงจากฐานข้อมูลคำแนะนำมาตรฐาน
เช่น ของกรมวิชาการเกษตร

6.4.2 การทดสอบภาคสนาม

นำระบบวิเคราะห์ดินต้นแบบที่สมบูรณ์ (ชุดคิท + แอปพลิเคชัน) ไปทดสอบในพื้นที่เกษตรจริง
โดยเลือกพื้นที่ที่ยังไม่เคยใช้ในการสร้างชุดข้อมูล ดำเนินการวิเคราะห์ดิน ณ
จุดทดสอบด้วยระบบต้นแบบ
และเก็บตัวอย่างดินจากจุดเดียวกันนั้นกลับมาเพื่อส่งวิเคราะห์ในห้องปฏิบัติการโดยทำซ้ำในหลาย ๆ
จุดทดสอบเพื่อให้ได้ข้อมูลที่น่าเชื่อถือ

6.4.3 การวิเคราะห์ผลและสรุป

นำผลการวิเคราะห์ปริมาณไนโตรเจนและฟอสฟอรัสที่ได้จากระบบต้นแบบมาเปรียบเทียบกับผลจากห้องปฏิบัติการและทำการวิเคราะห์ทางสถิติเพื่อประเมินความแม่นยำ
ความเที่ยงตรงและความสอดคล้องของระบบต้นแบบในสภาพการใช้งานจริงแล้สสรุปผลการวิจัย
อภิปรายถึงจุดเด่น ข้อจำกัด และแนวทางการพัฒนาต่อยอดในอนาคต
พร้อมทั้งจัดทำรายงานวิจัยฉบับสมบูรณ์และบทความวิชาการเพื่อการตีพิมพ์

**7. เอกสารอ้างอิง**

> Folorunso, O., Ojo, O., Busari, M., Adebayo, M., Adejumobi, J.,
> Folorunso, D., Ayo, F., Alabi, O., & Olabanjo, O. (2025). GeaGrow: A
> mobile tool for soil nutrient prediction and fertilizer optimization
> using artificial neural networks. Frontiers in Sustainable Food
> Systems, 9, 1533423.
>
> Kharel, T. P., Tyler, H. L., Mubvumba, P., Huang, Y., Bhandari, A. B.,
> Fletcher, R. S., Anapalli, S., Joshi, D. R., Mengistu, A., Birru, G.,
> Adhikari, K., Dhakal, M., Maskey, M. L., Reddy, K. N., & Clay, D. E.
> (2025). Machine learning on multi-spectral imagery to estimate
> nutrient yield of mixed-species cover crops. *Agricultural &
> Environmental Letters, 10*(1), e70009
>
> Kılıç, V., Alankus, G., Horzum, N., Mutlu, A. Y., Bayram, A. Y., &
> Solmaz, M. E. (2018). Single-image-referenced colorimetric water
> quality detection using a smartphone platform. ACS Omega, 3(5),
> 5540--5550.
>
> Mondal, B. P., et al. (2025). Comparison of multivariate machine
> learning models for soil nutrient prediction. *Computers and
> Electronics in Agriculture*. Advance online publication.
>
> Shin, S. K., Lee, S. J., & Park, J. H. (2025). Prediction of soil
> properties using Vis--NIR spectroscopy and machine learning.
> *Sensors*. Advance online publication.
>
> Tanaka, T. S. T., et al. (2025). Prediction of winter wheat nitrogen
> status using UAV imagery and machine learning. *Computers and
> Electronics in Agriculture*. Advance online publication

**ส่วน 5 ระยะเวลาและแผนการดำเนินงานวิจัย**

**1. ระยะเวลาและแผนการดำเนินการวิจัย**
(แสดงแผนการดำเนินงานรายกิจกรรมและระยะเวลาที่ใช้)

+---------------------------------+-----------------------------------------------------------------------------------------------------------------------------------------------+--------------------+
| **กิจกรรม**                      | **เดือนที่**                                                                                                                                     | **ร้อยละของกิจกรรม** |
|                                 +-----------+-----------+-----------+-----------+-----------+-----------+-----------+-----------+-----------+-----------+-----------+-----------+                    |
|                                 | **1**     | **2**     | **3**     | **4**     | **5**     | **6**     | **7**     | **8**     | **9**     | **10**    | **11**    | **12**    |                    |
+=================================+:=========:+:=========:+:=========:+:=========:+:=========:+:=========:+:=========:+:=========:+:=========:+:=========:+:=========:+:=========:+:==================:+
| ขั้นตอนที่ 1:                       |           |           |           |           |           |           |           |           |           |           |           |           | 15                 |
| ออกแบบและสร้างระบบฮาร์ดแวร์        |           |           |           |           |           |           |           |           |           |           |           |           |                    |
|                                 |           |           |           |           |           |           |           |           |           |           |           |           |                    |
| 1.1                             |           |           |           |           |           |           |           |           |           |           |           |           |                    |
| ทบทวนวรรณกรรมและออกแบบชุดวิเคราะห์ |           |           |           |           |           |           |           |           |           |           |           |           |                    |
|                                 |           |           |           |           |           |           |           |           |           |           |           |           |                    |
| 1.2 สร้างและประกอบชุดวิเคราะห์ต้นแบบ |           |           |           |           |           |           |           |           |           |           |           |           |                    |
+---------------------------------+-----------+-----------+-----------+-----------+-----------+-----------+-----------+-----------+-----------+-----------+-----------+-----------+--------------------+
| ขั้นตอนที่ 2:สร้างชุดข้อมูลมาตรฐาน      |           |           |           |           |           |           |           |           |           |           |           |           | 25                 |
|                                 |           |           |           |           |           |           |           |           |           |           |           |           |                    |
| 2.1 วางแผนและเก็บตัวอย่างดิน        |           |           |           |           |           |           |           |           |           |           |           |           |                    |
|                                 |           |           |           |           |           |           |           |           |           |           |           |           |                    |
| 2.2 ส่งตัวอย่างวิเคราะห์ค่าอ้างอิง      |           |           |           |           |           |           |           |           |           |           |           |           |                    |
| (Lab)                           |           |           |           |           |           |           |           |           |           |           |           |           |                    |
|                                 |           |           |           |           |           |           |           |           |           |           |           |           |                    |
| 2.3 วัดข้อมูลสเปกตรัมด้วยชุดต้นแบบ     |           |           |           |           |           |           |           |           |           |           |           |           |                    |
+---------------------------------+-----------+-----------+-----------+-----------+-----------+-----------+-----------+-----------+-----------+-----------+-----------+-----------+--------------------+
| ขั้นตอนที่ 3 พัฒนาและประเมินผลโมเดล   |           |           |           |           |           |           |           |           |           |           |           |           | 30                 |
| AI                              |           |           |           |           |           |           |           |           |           |           |           |           |                    |
|                                 |           |           |           |           |           |           |           |           |           |           |           |           |                    |
| 3.1 เตรียมและแบ่งชุดข้อมูล           |           |           |           |           |           |           |           |           |           |           |           |           |                    |
|                                 |           |           |           |           |           |           |           |           |           |           |           |           |                    |
| 3.2 สร้างและฝึกสอนโมเดล (ANN,     |           |           |           |           |           |           |           |           |           |           |           |           |                    |
| SVR)                            |           |           |           |           |           |           |           |           |           |           |           |           |                    |
|                                 |           |           |           |           |           |           |           |           |           |           |           |           |                    |
| 3.3 ประเมินและคัดเลือกโมเดลที่ดีที่สุด   |           |           |           |           |           |           |           |           |           |           |           |           |                    |
+---------------------------------+-----------+-----------+-----------+-----------+-----------+-----------+-----------+-----------+-----------+-----------+-----------+-----------+--------------------+
| ขั้นตอนที่ 4                        |           |           |           |           |           |           |           |           |           |           |           |           | 30                 |
| พัฒนาระบบบูรณาการและทดสอบ         |           |           |           |           |           |           |           |           |           |           |           |           |                    |
|                                 |           |           |           |           |           |           |           |           |           |           |           |           |                    |
| 4.1 พัฒนาแอปพลิเคชันเวอร์ชันสมบูรณ์    |           |           |           |           |           |           |           |           |           |           |           |           |                    |
|                                 |           |           |           |           |           |           |           |           |           |           |           |           |                    |
| 4.2                             |           |           |           |           |           |           |           |           |           |           |           |           |                    |
| ทดสอบภาคสนามและเก็บข้อมูลเปรียบเทียบ |           |           |           |           |           |           |           |           |           |           |           |           |                    |
|                                 |           |           |           |           |           |           |           |           |           |           |           |           |                    |
| 4.3 วิเคราะห์ผล สรุป               |           |           |           |           |           |           |           |           |           |           |           |           |                    |
| และจัดทำรายงาน/บทความ            |           |           |           |           |           |           |           |           |           |           |           |           |                    |
+---------------------------------+-----------+-----------+-----------+-----------+-----------+-----------+-----------+-----------+-----------+-----------+-----------+-----------+--------------------+

**2. พื้นที่ทำวิจัย**: โปรดระบุสถานที่ทำวิจัยจำแนกตามโครงการวิจัยโดยใช้ฐานข้อมูลจากระบบ
และเพิ่มเติมชื่อเฉพาะ เช่น ชุมชน หมู่บ้าน

+------------------------+--------------------+--------------------------------------+
| **ในประเทศ/ต่างประเทศ** | **ชื่อประเทศ/จังหวัด** | **ชื่อสถานที่**                          |
+:======================:+====================+======================================+
| ในประเทศ               | ประเทศไทย /        | หมู่บ้านหนองอ้อ ตำบลมะขาม อำเภอมะขาม     |
|                        | จังหวัดจันทบุรี         |                                      |
|                        |                    | บ้านหนองตาลิ่น ตำบลสองพี่น้อง อำเภอท่าใหม่   |
+------------------------+--------------------+--------------------------------------+
| ในประเทศ               | ประเทศไทย /        | หมู่บ้านตาละวาย ตำบลประณีต อำเภอเขาสมิง   |
|                        | จังหวัดตราด          |                                      |
+------------------------+--------------------+--------------------------------------+

**3. พื้นที่ที่ได้รับประโยชน์จากการวิจัย**

+------------------------+--------------------+----------------------------------------+
| **ในประเทศ/ต่างประเทศ** | **ชื่อประเทศ/จังหวัด** | **ชื่อสถานที่**                            |
+:======================:+:==================:+========================================+
| ในประเทศ               | จันทบุรี / ตราด       |                                        |
+------------------------+--------------------+----------------------------------------+
| ในประเทศ               | ประเทศไทย /        | หมู่บ้านหนองอ้อ ตำบลมะขาม อำเภอมะขาม       |
|                        | จังหวัดจันทบุรี         |                                        |
|                        |                    | บ้านหนองตาลิ่น ตำบลสองพี่น้อง อำเภอท่าใหม่     |
+------------------------+--------------------+----------------------------------------+
| ในประเทศ               | ประเทศไทย /        | หมู่บ้านตาละวาย ตำบลประณีต อำเภอเขาสมิง     |
|                        | จังหวัดตราด          |                                        |
+------------------------+--------------------+----------------------------------------+

**4. แผนการใช้จ่ายงบประมาณของโครงการวิจัย**

แสดงรายละเอียดประมาณการงบประมาณตลอดโครงการ โดยแบ่งเป็นหมวดต่าง ๆ ดังนี้

+----------------------------------------+---------------------------------+------------+
| **ประเภทงบประมาณ**                     | **รายละเอียด**                   | **งบประมาณ |
|                                        |                                 | (บาท)**    |
+========================================+=================================+:==========:+
| **1 งบดำเนินการ**                       | ค่าตอบแทนปฏิบัติงานนอกเวลาราชการ    | 6,000      |
|                                        |                                 |            |
| **1.1 ค่าตอบแทน**                       | 3 คน x 50 บาท x 2 ชั่วโมง x 20 วัน |            |
|                                        |                                 |            |
| ค่าตอบแทนปฏิบัติงานนอกเวลาราชการของคณะผู้วิจัย |                                 |            |
+----------------------------------------+---------------------------------+------------+
| **1.2 ค่าใช้สอย**                        | ระยะทาง 300 กม. X 4 บาท x 2     | 2,400      |
|                                        | เที่ยวไป-กลับ                      |            |
| 1\) ค่าเดินทางเก็บตัวอย่างดินภาคสนาม         |                                 |            |
+----------------------------------------+---------------------------------+------------+
| 2\)                                    | 15 ตัวอย่าง X 1,000 บาท/ตัวอย่าง    | 15,000     |
| ค่าวิเคราะห์ตัวอย่างดินในห้องปฏิบัติการมาตรฐาน   |                                 |            |
|                                        | 1 ครั้ง x 5,000 บาท               | 5,000      |
| 3\) ค่าลงทะเบียนเข้านำเสนอผลงาน           |                                 |            |
|                                        | ค่าที่พัก 1 ห้อง x 1,500 บาท x 2 คืน  | 3,000      |
| > 4\) ค่าใช้จ่ายในการสัมมนา                |                                 |            |
|                                        |                                 |            |
| และฝึกอบรม/นำเสนอผลงาน                  |                                 |            |
+----------------------------------------+---------------------------------+------------+
| **1.3 ค่าวัสดุ**                          | แหล่งกำเนิดแสง (Multi-wavelength  | 5,000      |
|                                        | LED array)                      |            |
| 1\) ค่าวัสดุไฟฟ้าและวิทยุ                    |                                 | 5,000      |
|                                        | (5 ชุด x 1,000 บาท)              |            |
|                                        |                                 | 5,000      |
|                                        | แผงวงจรควบคุมและโมดูลสื่อสาร (5 ชุด  |            |
|                                        | x 1,000 บาท)                    | 4,500      |
|                                        |                                 |            |
|                                        | แผงวงจรเอนกประสงค์ (5 ชุด x 1,000 | 1,000      |
|                                        | บาท)                            |            |
|                                        |                                 | 3,500      |
|                                        | วัสดุสำหรับสร้างโครงสร้างตัวกล่อง เช่น  |            |
|                                        | 3D Printing Filament            | 3,000      |
|                                        |                                 |            |
|                                        | แผ่นเทียบสีมาตรฐาน (Color          |            |
|                                        | Reference Chart)                |            |
|                                        |                                 |            |
|                                        | อุปกรณ์จัดเก็บข้อมูล(External Hard    |            |
|                                        | Drive/USB Drive)                |            |
|                                        |                                 |            |
|                                        | หัวแล้งบัดกี ลวดเชื่อม สายไฟ          |            |
|                                        | คอนเนกเตอร์ ฯลฯ                  |            |
+----------------------------------------+---------------------------------+------------+
| 2\) ค่าวัสดุวิทยาศาสตร์ สารเคมีและอุปกรณ์      | ชุดทดสอบดินภาคสนามเบื้องต้น (1 ชุด x  | 3,500      |
|                                        | 3,500 บาท)                      |            |
+----------------------------------------+---------------------------------+------------+
| 3\) ค่าวัสดุสำนักงาน/วัสดุอื่น ๆ               | อุปกรณ์เตรียมตัวอย่างดิน เช่น          | 3,000      |
|                                        | ถุงเก็บตัว,ป้ายระบุชื่อ                |            |
|                                        |                                 | 4,850      |
|                                        | วัสดุสำนักงาน เช่น กระดาษ,          |            |
|                                        | กระดาษทิชชู, หมึกพิมพ์, แฟ้ม,         |            |
|                                        | ปากกาเขียนป้าย                    |            |
+----------------------------------------+---------------------------------+------------+
| **ค่าสาธารณูปโภค**                       | ค่าธรรมเนียมอุดหนุนสถาบัน 7%         | **5,250**  |
+----------------------------------------+---------------------------------+------------+
| **รวม**                                                                  | **75,000** |
+--------------------------------------------------------------------------+------------+

หมายเหตุ: ถัวเฉลี่ยทุกรายการ ยกเว้น งบบุคลากร และงบดำเนินงาน: ค่าตอบแทน ไม่เกิน 30%
ของงบประมาณที่ตั้ง

**5. มาตรฐานการวิจัย**

❑ มีการใช้สัตว์ทดลอง

❑ มีการวิจัยในมนุษย์

❑ มีการวิจัยที่เกี่ยวข้องกับงานด้านเทคโนโลยีชีวภาพสมัยใหม่

❑ มีการใช้ห้องปฏิบัติการที่เกี่ยวกับสารเคมี

☑ ไม่มี

**6. หน่วยงานร่วมดำเนินการ/ภาคเอกชนหรือชุมชนที่ร่วมลงทุนหรือดำเนินการ**

+-----------+---------------------------------------+-------------------------------------------+----------------------------+-------------------------+
| **ลำดับที่** | **ชื่อหน่วยงานรัฐ/บริษัท/หน่วยงานต่างประเทศ** | **แนวทางร่วมดำเนินการ**                     | **การร่วมลงทุนในรูปแบบตัวเงิน** | **การร่วมลงทุนในรูปแบบอื่น** |
|           |                                       |                                           |                            |                         |
|           |                                       |                                           | **(in-cash) (บาท)**        | **(in-kind)**           |
+:=========:+:=====================================:+===========================================+:==========================:+=========================+
| 1         | มูลนิธิเก้าเกษตร จังหวัดตราด                | จัดกิจกรรมสาธิตเทคโนโลยี/กลุ่มเกษตรกรในเครือข่ายฯ | \-                         | สถานที่จัดกิจกรรมสาธิต       |
|           |                                       |                                           |                            | ถ่ายทอดเทคโนโลยี          |
+-----------+---------------------------------------+-------------------------------------------+----------------------------+-------------------------+

**7. แนวทางการขับเคลื่อนผลงานวิจัยและนวัตกรรมไปสู่ผลลัพธ์และผลกระทบ**

7.1 การเชื่อมโยงกับนักวิจัยที่เป็นผู้เชี่ยวชาญในสาขาวิชาที่ทำการวิจัยทั้งในและต่างประเทศ
(ถ้ามี) (Connections with other experts within and outside Thailand)
และแผนที่จะติดต่อหรือสร้างความสัมพันธ์กับผู้เชี่ยวชาญ รวมทั้งการสร้างทีมงานวิจัยในอนาคตด้วย

\-

7.2 การเชื่อมโยงหรือความร่วมมือกับผู้มีส่วนได้ส่วนเสีย และผู้ใช้ประโยชน์จากงานวิจัย
(Stakeholder and User Engagement) โดยระบุชื่อหน่วยงานภาครัฐ เอกชน
ประชาสังคมและชุมชน
โดยอธิบายกระบวนการดำเนินงานร่วมกันและการเชื่อมโยงการขับเคลื่อนผลการวิจัยไปสู่การใช้ประโยชน์อย่างชัดเจน
รวมถึงอธิบายกระบวนการดำเนินงานต่อเนื่องของผู้ใช้ประโยชน์จากงานวิจัยเมื่อโครงการวิจัยเสร็จสิ้น

1\. กลุ่มเป้าหมาย

ชุมชน กลุ่มเกษตรกรชาวสวนจังหวัดจันทบุรี/ตราด

ภาคเอกชน มูลนิธิเก้าเกษตร (ความร่วมมือตาม MOU ระหว่างมหาวิทยาลัย
(คณะวิทยาศาสตร์และเทคโนโลยีกับมูลนิธิเก้าเกษตร)

2 แผนดำเนินการ

> \-
> นำชุดวิเคราะห์ปริมาณไนโตเจนและฟอสฟอรัสต้นแบบส่งมอบให้กลุ่มเกษตรชาวสวนจังหวัดจันทบุรีและตราดให้นำไปทดลองใช้ในพื้นที่จริงเพื่อเก็บข้อมูลแล้วนำมาปรับปรุงในอนาคต
>
> \-
> ถ่ายทอดเทคโนโลยีด้วยการจัดทำคู่มือฉบับประชาชนและจัดกิจกรรมสาธิตเทคโนโลยีเพื่อส่งมอบนวัตกรรมและองค์ความรู้สู่เกษตรกร

**ส่วน 6 ประโยชน์ ผลผลิต ผลลัพธ์ และผลกระทบจากงานวิจัย**

**1. ประโยชน์ที่คาดว่าจะได้รับ**

> ☑ ด้านวิชาการ

เกิดองค์ความรู้ใหม่ที่สำคัญในการประยุกต์ใช้เทคนิคปัญญาประดิษฐ์โดยเฉพาะโมเดลการเรียนรู้ของเครื่อง
ANN และ SVR
เพื่อแก้ไขปัญหาความไม่แม่นยำของเซ็นเซอร์เชิงแสงที่เกิดจากความซับซ้อนของเมทริกซ์ดินและการสะท้อนแสงโดยตรง
ซึ่งเป็นการพัฒนาเครื่องมือวัดภาคสนามที่ไม่ต้องพึ่งพาสารเคมี

ผลงานวิจัยสามารถนำไปตีพิมพ์ในวารสารวิชาการระดับชาติ/นานาชาติในวารสาร Computers
and Electronics in Agriculture, Geoderma, หรือ Sensors หรือ
วารสารด้านปัญญาประดิษฐ์เพื่อการเกษตร หรือวารสารอื่นๆ ที่เกี่ยวข้อง

ผู้ได้รับผลประโยชน์ นักวิจัย คณาจารยและนิสิต/นักศึกษา

> ☑ ด้านสังคม

☑ ด้านสาธารณะ ☑ ด้านชุมชนและพื้นที่ ☑ ด้านสิ่งแวดล้อม

ด้านสาธารณะ ส่งเสริมความมั่นคงทางอาหาร
โดยการที่เกษตรกรสามารถจัดการธาตุอาหารพืชได้อย่างแม่นยำจะนำไปสู่การเพิ่มปริมาณและคุณภาพของผลผลิตทางการเกษตรโดยรวม
ซึ่งเป็นการสร้างความมั่นคงทางอาหารให้กับประชากรในประเทศในระยะยาว

ด้านชุมชนและพื้นที่ เสริมสร้างศักยภาพเกษตรกร
ในชุมชนเป้าหมายและพื้นที่ใกล้เคียงจะสามารถเข้าถึงเทคโนโลยีที่ช่วยให้วิเคราะห์คุณภาพดินเบื้องต้นของตนเองได้ทันที
ลดการพึ่งพาการคาดเดาหรือรอผลจากห้องปฏิบัติการที่ยาวนาน
ทำให้เกษตรกรสามารถตัดสินใจจัดการสวนของตนเองได้อย่างมีข้อมูลและ
เป็นวิทยาศาสตร์มากขึ้นและลดความเหลื่อมล้ำในการเข้าถึงเทคโนโลยีเพราะเครื่องมือที่พัฒนาขึ้นมีต้นทุนต่ำและใช้งานง่ายผ่านสมาร์ทโฟนซึ่งเป็นอุปกรณ์ที่เกษตรกรส่วนใหญ่มีอยู่แล้ว

ด้านสิ่งแวดล้อม ลดมลพิษทางดินและน้ำ
เพราะการใช้ปุ๋ยในปริมาณที่เหมาะสมกับความต้องการของพืชและสภาพดินจะช่วยลดปัญหาการใช้ปุ๋ยเกินความจำเป็นได้
ลดการปนเปื้อนของสารเคมีในดินและแหล่งน้ำ และส่งเสริมการทำเกษตรกรรมที่ยั่งยืน

ผู้ได้รับผลประโยชน์ เกษตรกร และประชาชนทั่วไปที่ได้รับประโยชน์จากสิ่งแวดล้อมที่ดีขึ้น

> ◻ ด้านนโยบาย
>
> ☑ ด้านเศรษฐกิจ

ลดต้นทุนการผลิตให้เกษตรกรด้วยการลดค่าใช้จ่ายในการซื้อปุ๋ยเคมีที่ไม่จำเป็น
เมื่อเกษตรกรทราบปริมาณ N และ P ที่มีอยู่แล้วในดิน จะสามารถเลือกซื้อและใส่ปุ๋ยได้ตรงจุด
ทำให้ต้นทุนการผลิตต่อไร่ลดลงเพิ่มนอกจากนี้การที่พืชได้รับธาตุอาหารในปริมาณที่พอเหมาะจะส่งผลให้พืชเจริญเติบโตได้ดี
ให้ผลผลิตต่อไร่สูงขึ้น และมีคุณภาพดีขึ้น

ผู้ได้รับผลประโยชน์ เกษตรกร

**2. ผลผลิตที่คาดว่าจะได้รับ (Output)**

  -----------------------------------------------------------------------------------------------------------------------------------------------------------
  **ผลผลิต**                                **ประเภทผลผลิต**            **รายละเอียดของผลผลิต**                                       **จำนวนนำส่ง**   **หน่วยนับ**
  ---------------------------------------- -------------------------- ---------------------------------------------------------- --------------- ------------
  ชุดวัดปริมาณไนโตรเจนและฟอสฟอรัสในดินแบบพกพา   4.ต้นแบบผลิตภัณฑ์              ชุดวัดปริมาณไนโตรเจนและฟอสฟอรัสในดินแบบพกพาภาคสนามที่มีความแม่นยำ          5           เครื่อง
                                           หรือเทคโนโลยี/กระบวนการใหม่   ใช้งานง่าย ราคาถูก                                                            
                                           หรือนวัตกรรมทางสังคม                                                                                     

  แอปพลิเคชันสมาร์ทโฟน                        4\. ต้นแบบผลิตภัณฑ์            แอปพลิเคชันต้นแบบ (Prototype Application) ที่รวมโมเดลปัญญาประดิษฐ์        1         แอปพลิ เคชัน
                                           หรือเทคโนโลยี/กระบวนการใหม่   และระบบแนะนำการใช้ปุ๋ยเบื้องต้นไว้ด้วยกัน                                           
                                           หรือนวัตกรรมทางสังคม                                                                                     

  บทความวิจัย                                2\. บทความวิจัย (Manuscript) บทความวิจัย 1 เรื่อง                                                **1**          เรื่อง
                                                                      ที่พร้อมสำหรับการส่งตีพิมพ์ในวารสารวิชาการระดับชาติ/นานาชาติ                           

  ชุดข้อมูลสำหรับงานวิจัย                        7\. ฐานข้อมูล ระบบและกลไก    ชุดข้อมูลลายพิมพ์สเปกตรัมของดินที่จับคู่กับค่าวิเคราะห์จากห้องปฏิบัติการ              1           ชุดข้อมูล
                                           หรือมาตรฐาน                                                                                            

  รายงานวิจัยฉบับสมบูรณ์                        3\. หนังสือ                  3.3 เอกสาร/หนังสือที่มีเนื้อหาเกี่ยวกับเรื่องใดเรื่องหนึ่ง อย่างครบถ้วน             1            ฉบับ
                                                                      รายงานสรุปกระบวนการและผลการวิจัยทั้งหมดของโครงการฉบับสมบูรณ์                       
                                                                      ตามรูปแบบที่กองทุนวิจัยกำหนด                                                     
  -----------------------------------------------------------------------------------------------------------------------------------------------------------

**3. ผลลัพธ์ (Expected Outcomes) ที่คาดว่าเกิดขึ้น**

**ประเภทของผลลัพธ์และคําจํากัดความ (Type of Outcomes and Definition)**
(คำอธิบายในภาคผนวก)

+-----------------------------------------------------+-------+-----------+-------------------------------------------------------------+-------------------------------+
| ผลที่คาดว่าจะได้รับ                                      | จำนวน | หน่วยนับ    | รายละเอียดของผลลัพธ์                                           | ผู้ใช้ประโยชน์ (Users)/           |
|                                                     |       |           |                                                             |                               |
| (ทำ dropdown list ให้เลือก)                           |       |           |                                                             | ผู้ได้รับผลประโยชน์                |
|                                                     |       |           |                                                             | (Beneficiaries)               |
+=====================================================+:=====:+:=========:+=============================================================+===============================+
| ผลงานตีพิมพ์ (Publications)                            | 1     | เรื่อง      | บทความวิจัยจากโครงการได้รับการตีพิมพ์ในวารสารวิชาการระดับชาติ/นานาชาติ | นักวิจัย/นักวิชาการ                |
|                                                     |       |           | ทำให้เกิดการเผยแพร่องค์ความรู้ใหม่ด้านการประยุกต์ใช้ AI                |                               |
|                                                     |       |           | ในการวิเคราะห์คุณภาพดิน                                         |                               |
+-----------------------------------------------------+-------+-----------+-------------------------------------------------------------+-------------------------------+
| การอ้างอิง (Citations)                                |       |           |                                                             |                               |
+-----------------------------------------------------+-------+-----------+-------------------------------------------------------------+-------------------------------+
| เครื่องมือและระเบียบวิธีการวิจัย(Research Tools and         |       |           |                                                             |                               |
| Methods)                                            |       |           |                                                             |                               |
+-----------------------------------------------------+-------+-----------+-------------------------------------------------------------+-------------------------------+
| ฐานข้อมูลและแบบจำลองวิจัย                               | 1     | การนำไปใช้ | แบบจำลอง AI และชุดข้อมูลที่พัฒนาขึ้น                                | นักวิจัย/นักพัฒนาซอฟแวร์/oyd;b=kdki |
|                                                     |       |           | ถูกนำไปใช้โดยนักวิจัย/นักพัฒนากลุ่มอื่นเพื่อศึกษาต่อยอด                    |                               |
| (Research Databases and Models)                     |       |           | หรือพัฒนาเป็นแอปพลิเคชัน/ผลิตภัณฑ์ใหม่                               |                               |
+-----------------------------------------------------+-------+-----------+-------------------------------------------------------------+-------------------------------+
| ความก้าวหน้าในวิชาชีพของบุคลากรด้านวิทยาศาสตร์วิจัยและนวัตกรรม |       |           |                                                             |                               |
| (Next Destination)                                  |       |           |                                                             |                               |
+-----------------------------------------------------+-------+-----------+-------------------------------------------------------------+-------------------------------+
| รางวัลและการยอมรับ (Awards and Recognitions)          |       |           |                                                             |                               |
+-----------------------------------------------------+-------+-----------+-------------------------------------------------------------+-------------------------------+
| การใช้ประโยชน์จากเครื่องมือ อุปกรณ์ห้องวิจัยและโครงสร้างพื้นฐาน  |       |           |                                                             |                               |
| (Use of Facilities and Resources)                   |       |           |                                                             |                               |
+-----------------------------------------------------+-------+-----------+-------------------------------------------------------------+-------------------------------+
| ทรัพย์สินทางปัญญา การขึ้นทะเบียนพันธุ์ พืชและพันธุ์สัตว์            | 1     | คำขอ      | มีการยื่นคำขอจด ลิขสิทธิ์ หรืออนุสิทธิบัตร หรือสิทธิบัตร                    | มหาวิทยาลัยราชภัฏรำไพพรรณี        |
| และการอนุญาตให้ใช้สิทธิ (Intellectual property,          |       |           |                                                             |                               |
| Registered Plants Varieties and Animals Breeding    |       |           |                                                             |                               |
| and Licensing)                                      |       |           |                                                             |                               |
+-----------------------------------------------------+-------+-----------+-------------------------------------------------------------+-------------------------------+
| การถ่ายทอดเทคโนโลยี (Technology Transfer)             | 1     | ครั้ง       | มีการจัดกิจกรรมถ่ายทอดเทคโนโลยี ให้กับกลุ่มเกษตรกร                   | เกษตรกร                       |
|                                                     |       |           | หรือนักเรียน/นักศึกษาที่สนใจ                                       |                               |
|                                                     |       |           |                                                             | นักเรียน/นักศึกษา หรือนักวิชาการ     |
+-----------------------------------------------------+-------+-----------+-------------------------------------------------------------+-------------------------------+
| ผลิตภัณฑ์และกระบวนการ บริการ และการ รับรองมาตรฐานใหม่     |       |           |                                                             |                               |
| (New Products/Processes, New Services and New       |       |           |                                                             |                               |
| Standard Assurances)                                |       |           |                                                             |                               |
+-----------------------------------------------------+-------+-----------+-------------------------------------------------------------+-------------------------------+
| ทุนวิจัยต่อยอด (Further Funding)                        |       |           |                                                             |                               |
+-----------------------------------------------------+-------+-----------+-------------------------------------------------------------+-------------------------------+
| ความร่วมมือหรือหุ้นส่วน ความร่วมมือ\                        |       |           |                                                             |                               |
| (Collaborations and Partnerships)                   |       |           |                                                             |                               |
+-----------------------------------------------------+-------+-----------+-------------------------------------------------------------+-------------------------------+
| การผลักดันนโยบาย แนวปฏิบัติ แผนและกฎระเบียบ (Influence on |       |           |                                                             |                               |
| Policy, Practice, Plan and Regulations)             |       |           |                                                             |                               |
+-----------------------------------------------------+-------+-----------+-------------------------------------------------------------+-------------------------------+
| กิจกรรมสร้างการมีส่วนร่วม (Engagement Activities)        |       |           |                                                             |                               |
+-----------------------------------------------------+-------+-----------+-------------------------------------------------------------+-------------------------------+

**4. ผลกระทบ (Expected Impacts) ที่คาดว่าจะเกิดขึ้น**

> ☑ ด้านวิชาการ

ยกระดับขีดความสามารถการวิจัยด้านเกษตรอัจฉริยะของจังหวัดจันทบุรีและตราด
โดยโครงการนี้จะเป็นต้นแบบและแรงผลักดันให้เกิดการวิจัยและพัฒนาที่ผสมผสานศาสตร์ต่าง ๆ
มากขึ้น ทั้งด้านฟิสิกส์ทางแสง เคมีวิเคราะห์และเทคโนโลยีปัญญาประดิษฐ์
เพื่อสร้างนวัตกรรมทางการเกษตร
ส่งผลให้ประเทศไทยมีศักยภาพในการเป็นผู้นำด้านเทคโนโลยีเกษตรแม่นยำ

> ☑ ด้านสังคม

☑ ด้านสาธารณะ ☑ ด้านชุมชนและพื้นที่ ☑ ด้านสิ่งแวดล้อม

ด้านสาธารณะ
ลดความเหลื่อมล้ำในการเข้าถึงเทคโนโลยีทางการเกษตรโดยเครื่องมือที่แม่นยำและราคาถูกจะช่วยทลายกำแพงทางเทคโนโลยี
ทำให้เกษตรกรรายย่อยสามารถเข้าถึงและใช้ประโยชน์จากนวัตกรรม

ด้านชุมชนและพื้นที่ เกิดการเปลี่ยนแปลงสู่การทำเกษตรกรรมบนฐานข้อมูลในระดับชุมชน
เกษตรกรมีเครื่องมือที่ช่วยให้เข้าใจภาษาของดินทำให้เปลี่ยนจากการทำเกษตรตามความเคยชิน
มาเป็นการจัดการสวนอย่างมีหลักการและแม่นยำ ส่งผลให้ชุมชนเกษตรมีความเข้มแข็ง
พึ่งพาตนเองได้

ด้านสิ่งแวดล้อม ฟื้นฟูและรักษาสมดุลของระบบนิเวศทางการเกษตร
เมื่อการใช้ปุ๋ยและสารเคมีเป็นไปอย่างมีประสิทธิภาพและลดลงในวงกว้าง
จะช่วยลดปัญหามลพิษทางดินและแหล่งน้ำอย่างมีนัยสำคัญ
ส่งผลให้ระบบนิเวศในพื้นที่เกษตรกรรมมีความสมดุลและยั่งยืนมากขึ้น

> ◻ ด้านนโยบาย

\-

> ☑ ด้านเศรษฐกิจ

เพิ่มขีดความสามารถในการแข่งขันของภาคเกษตรกรรมไทยในตลาดโลกโดยการจัดการดินที่แม่นยำนำไปสู่การเพิ่มปริมาณและคุณภาพของผลผลิตทางการเกษตรที่สม่ำเสมอ
โดยเฉพาะพืชเศรษฐกิจมูลค่าสูง เช่น ทุเรียน ผลไม้ต่างๆ
ทำให้สินค้าเกษตรของไทยมีคุณภาพเป็นที่ยอมรับและสามารถแข่งขันในตลาดโลกได้ดียิ่งขึ้น

◻ ด้านอื่น ๆ ระบุ
\...\...\...\...\...\...\...\...\...\...\...\...\...\...\...\...\...\...\...\...\...\...\...\...\...\...\...\...\...\...\...\...\...\...\...\...\...\...\...\...\...\...\...\...\...\...\...

**5. การเสนอข้อเสนอหรือส่วนหนึ่งส่วนใดของงานวิจัยนี้ต่อแหล่งทุนอื่นหรือเป็นการวิจัยต่อยอด**

**จากโครงการวิจัยอื่น**

**◻** มี ☑ ไม่มี

หน่วยงาน/สถาบันที่ยื่น\...\...\...\...\...\...\...\...\...\...\...\...\...\...\...\...\...\...\...\...\...\...\...\...\...\...\...\...\...\...\...\...\...\...\...\...\...\...\...\...\...\...\...\...\.....

ชื่อโครงการ\...\...\...\...\...\...\...\...\...\...\...\...\...\...\...\...\...\...\...\...\...\...\...\...\...\...\...\...\...\...\...\...\...\...\...\...\...\...\...\...\...\...\...\...\...\...\...\...\...\...\.....

ระบุความแตกต่างจากโครงการนี้\...\...\...\...\...\...\...\...\...\...\...\...\...\...\...\...\...\...\...\...\...\...\...\...\...\...\...\...\...\...\...\...\...\...\...\...\...\...\...\....

สถานการพิจารณา

**◻** ไม่มีการพิจารณา

**◻** โครงการได้รับอนุมัติแล้ว สัดส่วนทุนที่ได้รับ\...\...\...\...\...\...%

**◻** โครงการอยู่ระหว่างการพิจารณา

ข้าพเจ้าขอรับรองว่าข้อเสนอการวิจัยหรือส่วนหนึ่งส่วนใดของข้อเสนอการวิจัยนี้ ไม่เป็นส่วนหนึ่งของ
วิทยานิพนธ์หรือใช้เพื่อให้ได้มาซึ่งวุฒิการศึกษาของข้าพเจ้า

> ลงลายมือชื่อ หัวหน้าโครงการวิจัย พร้อมวัน เดือน ปี

##  (นายชีวะ ทัศนา)

> วันที่\...\...\...\...\...\...\...\...\...\...\...\...\...\...\...\...\...\...\.....
>
> หัวหน้าโครงการวิจัย
>
> ลงลายมือชื่อผ่านความเห็นชอบของหน่วยงานต้นสังกัด

##  (ผู้ช่วยศาสตราจารย์วิชลัดดา อุ่นสะอาด)

> วันที่\...\...\...\...\...\...\...\...\...\...\...\...\...\...\...\...\...\...\.....
>
> คณบดีคณะวิทยาศาสตร์และเทคโนโลยี

##  ส่วนที่ 7 ประวัติคณะผู้วิจัย

**7.1 หัวหน้าโครงการ**

1\. ชื่อ - นามสกุล (ภาษาไทย) นายชีวะ ทัศนา

ชื่อ - นามสกุล (ภาษาอังกฤษ) Mr.CHEWA THASSANA

2\. ตำแหน่งปัจจุบัน อาจารย์

> เงินเดือน (บาท) 7X,XXX บาท
>
> เวลาที่ใช้ทำวิจัย (ชั่วโมง : สัปดาห์) 20 ชั่วโมง/สัปดาห์
>
> 3\. หน่วยงานและสถานที่อยู่ที่ติดต่อได้สะดวก หลักสูตร คบ.ฟิสิกส์
> คณะวิทยาศาสตร์และเทคโนโลยี
>
> มหาวิทยาลัยราชภัฏรำไพพรรณี
>
> ตำบลท่าช้าง อำเภอเมือง จังหวัดจันทบุรี 22000
>
> โทรศัพท์ 093 742 2654
>
> โทรสาร 0-3947-1060
>
> ไปรษณีย์อิเล็กทรอนิกส์ (e-mail) chewa.t@rbru.ac.th

4 ประวัติการศึกษา

> ปริญญาเอก ปรัชญาดุษฎีบัณฑิต (ฟิสิกส์ประยุกต์)
>
> สถาบันเทคโนโลยีพระจอมเกล้าเจ้าคุณทหารลาดกระบัง 2555
>
> ปริญญาโท วิทยาศาสตรมหาบัณฑิต (ฟิสิกส์ประยุกต์)
>
> สถาบันเทคโนโลยีพระจอมเกล้าเจ้าคุณทหารลาดกระบัง 2549
>
> ปริญญาตรี วิทยาศาสตรบัณฑิต (ฟิสิกส์) มหาวิทยาลัยนเรศวร 2541

5 สาขาวิชาการที่มีความชำนาญพิเศษ (แตกต่างจากวุฒิการศึกษา) ระบุสาขาวิชาการ

> อิเล็กทรอนิกส์และไมโครคอนโทรลเลอร์ ปัญญาประดิษฐ์และการเรียนรู้เชิงลึก

6 ประสบการณ์ที่เกี่ยวข้องกับการบริหารงานวิจัยทั้งภายในและภายนอกประเทศโดยระบุสถานภาพ

ในการทำการวิจัยว่าเป็นผู้อำนวยการแผนงานวิจัย หัวหน้าโครงการวิจัย
หรือผู้ร่วมวิจัยในแต่ละผลงานวิจัย

> 6.1 งานวิจัยที่ทำเสร็จแล้ว

+-------------------+----------------------------------------------------------------+-------+--------------------------------------+------------------------+
| สถานภาพในการทำวิจัย | ชื่อผลงานวิจัย                                                     | ปีที่พิมพ์ | การเผยแพร่                            | แหล่งทุน                 |
+===================+================================================================+:=====:+:=====================================+========================+
| หัวหน้าโครงการ      | การศึกษาการสะท้อนแสงของสารละลายแอมโมเนียมคลอไรด์ด้วยกล่องสมองกลฝังตัว. | 2566  | วารสารการศึกษาและนวัตกรรมพัฒนาการเรียนรู้. | กองทุนวิจัย               |
|                   |                                                                |       | หน้า 20-26.                           | มหาวิทยาลัยราชภัฏรำไพพรรณี |
| (80%)             |                                                                |       |                                      |                        |
|                   |                                                                |       |                                      | ประจำปี พ.ศ. 2566       |
+-------------------+----------------------------------------------------------------+-------+--------------------------------------+------------------------+
| ผู้ร่วมวิจัย           | การศึกษาสมบัติทางความร้อน                                          | 2566  | วารสารวิศวกรรมและเทคโนโลยีอุตสาหกรรม    | กองทุนวิจัย               |
|                   |                                                                |       | มหาวิทยาลัยกาฬสินธุ์                      | มหาวิทยาลัยราชภัฏรำไพพรรณี |
| (25%)             | ของถ่านไม้มังคุดอัดแท่ง                                              |       |                                      |                        |
|                   |                                                                |       | ปีที่ 1ฉบับที่ 5 กันยายน -- ตุลาคม 2566      | ประจำปี พ.ศ. 2566       |
|                   | ผสมคาร์บอนแบล็ค                                                  |       |                                      |                        |
+-------------------+----------------------------------------------------------------+-------+--------------------------------------+------------------------+
| หัวหน้าโครงการ      | ชุดวัดความเร่งเนื่องจาก                                             | 2564  | การประชุมวิชาการระดับชาติและนานาชาติ ครั้งที่ | ทุนวิจัยส่วนตัว             |
|                   |                                                                |       | 4 พ.ศ. 2564 : 7 มกราคม 2564          |                        |
| (100%)            | แรงโน้มถ่วงของโลก                                                |       |                                      |                        |
|                   |                                                                |       | มหาวิทยาลัยราชภัฏบุรีรัมย์                  |                        |
|                   | ด้วยแรงแม่เหล็ก                                                   |       |                                      |                        |
+-------------------+----------------------------------------------------------------+-------+--------------------------------------+------------------------+

6.2 งานวิจัยที่ยังอยู่ระหว่างดำเนินการ

> \-

**7.2 ผู้ร่วมวิจัย**

1\. ชื่อ - นามสกุล (ภาษาไทย) นางสาวจิรภัทร จันทมาลี

ชื่อ - นามสกุล (ภาษาอังกฤษ) Miss Jirapat Chanthamalee

> 2\. ตำแหน่งปัจจุบัน ผู้ช่วยศาสตราจารย์
>
> เงินเดือน (บาท) 4X,XXX บาท
>
> เวลาที่ใช้ทำวิจัย (ชั่วโมง : สัปดาห์) 20 ชั่วโมง/สัปดาห์

3\. หน่วยงานและสถานที่อยู่ที่ติดต่อได้สะดวก ภาควิชาชีววิทยา คณะวิทยาศาสตร์และเทคโนโลยี

มหาวิทยาลัยราชภัฏรำไพพรรณี ต.ท่าช้าง อ.เมือง จ.จันทบุรี

หมายเลขโทรศัพท์ : 083-7861113

> ไปรษณีย์อิเล็กทรอนิกส์ : E-mail: jirapat.c@rbru.ac.th

4 ประวัติการศึกษา

> ปริญญาเอก ปรัชญาดุษฎีบัณฑิต (จุลชีววิทยา) จุฬาลงกรณ์มหาวิทยาลัย 2554
>
> ปริญญาโท วิทยาศาสตรมหาบัณฑิต (จุลชีววิทยาอุตสาหกรรม) จุฬาลงกรณ์มหาวิทยาลัย 2543
>
> ปริญญาตรี วิทยาศาสตรบัณฑิต (จุลชีววิทยา) จุฬาลงกรณ์มหาวิทยาลัย 2540

5 สาขาวิชาการที่มีความชำนาญพิเศษ

\- จุลชีววิทยาทางเกษตรและสิ่งแวดล้อม

6 ประสบการณ์ที่เกี่ยวข้องกับการบริหารงานวิจัยทั้งภายในและภายนอกประเทศ

6.1 หัวหน้าโครงการวิจัย : ชื่อโครงการวิจัย

1\. การบำบัดน้ำทิ้งปนเปื้อนสีจากการย้อมกกโดยใช้เชื้อรา

2\. การคัดแยกแบคทีเรียที่สร้างรงควัตถุจากพื้นที่ปกปักพันธุกรรมพืช มหาวิทยาลัยราชภัฏรำไพพรรณี

3\. ความหลากหลายของจุลินทรีย์ที่มีประโยชน์ทางการเกษตรในดินสวนผลไม้ จังหวัดจันทบุรี

4\. ศักยภาพของแบคทีเรียที่คัดแยกได้จากดินในจังหวัดจันทบุรีในการย่อยสลายไกลโฟเสท

6.2 งานวิจัยที่ทำเสร็จแล้ว

จิรภัทร จันทมาลี, อิสรัศมิ์ แสงน้อย, นภัสกร นาคสกุล, นิภาพร ทองพูล และวิญญู ภักดี.
(2565).
การคัดกรองฤทธิ์ต้านเชื้อราของแบคทีเรียปฏิปักษ์ที่คัดแยกจากดินสวนผลไม้ในจังหวัดจันทบุรี.
การประชุมวิชาการระดับชาติ นนทรี ครั้งที่ 10. มหาวิทยาลัยเกษตรศาสตร์
วิทยาเขตเฉลิมพระเกียรติ จังหวัดสกลนคร. หน้า 182-192.

**7.3 ผู้ร่วมวิจัย**

> 1\. ชื่อ - นามสกุล (ภาษาไทย) นางสาววิกันยา ประทุมยศ
>
> ชื่อ - นามสกุล (ภาษาอังกฤษ) Wikanya Prathumyot

2\. ตำแหน่งปัจจุบัน ผู้ช่วยศาสตราจารย์

> เงินเดือน (บาท) 4X,XXX บาท
>
> เวลาที่ใช้ทำวิจัย (ชั่วโมง : สัปดาห์) 14 ชั่วโมง/สัปดาห์
>
> 3\. หน่วยงานและสถานที่อยู่ที่ติดต่อได้สะดวก คณะเทคโนโลยีการเกษตร
>
> มหาวิทยาลัยราชภัฏรำไพพรรณี จ.จันทบุรี 22000
>
> โทรศัพท์ 080-092-5926 โทรสาร 039-471-073
>
> E-mail: wikanya.p@rbru.ac.th
>
> 4\. ประวัติการศึกษา
>
> Ph.D. (Bioresources Science)Mie University, Japan 2554
>
> M.S. (Bioresources Science) Mie University, Japan 2551
>
> วท.บ. (เทคโนโลยีการเกษตร) มหาวิทยาลัยธรรมศาสตร์ (เกียรตินิยมอันดับหนึ่ง) 2548
>
> 5\. สาขาวิชาการที่มีความชำนาญพิเศษ
>
> สรีรวิทยาพืช การทนเค็มของพืช การปลูกพืชไร้ดิน การจัดการธาตุอาหารของพืช
>
> 6\. ประสบการณ์ที่เกี่ยวข้องกับการบริหารงานวิจัย

6.1 ผู้อำนวยการแผนงานวิจัย : ชื่อแผนงานวิจัย

6.1.1 แผนงานวิจัย เรื่องแนวทางการแก้ไขปัญหาสำหรับการผลิตทุเรียนนอกฤดู

> 6.2 หัวหน้าโครงการวิจัย : ชื่อโครงการวิจัย
>
> 6.2.1 หัวหน้าโครงการวิจัย เรื่อง การศึกษาอิทธิพลของปุ๋ยอินทรีย์และเคมีต่อลักษณะการ

เจริญเติบโตของหนามแดง

> 6.2.2 หัวหน้าโครงการวิจัย เรื่อง การผลิตก๊าซชีวภาพจากเศษเงาะในถังหมักแบบไร้

ออกซิเจน

> 6.2.3 หัวหน้าโครงการวิจัย เรื่อง การผลิตก๊าซชีวภาพจากเปลือกและเมล็ดลำไยในระบบหมัก

แบบไร้ออกซิเจน

> 6.2.4 หัวหน้าโครงการวิจัย เรื่อง การผลิตก๊าซชีวภาพจากเปลือกและเมล็ดทุเรียนร่วมกับมูล

สัตว์ในถังหมักแบบไร้ออกซิเจน

> 6.2.5 หัวหน้าโครงการวิจัย เรื่อง ผลของการใช้น้ำทิ้งจากการหมักก๊าซชีวภาพด้วยมูลสัตว์

และเศษลำไยต่อสมบัติทางเคมีของดินและการเจริญเติบโตของดาวเรือง (*Tagetes erecta*)

6.2.6 หัวหน้าโครงการวิจัย เรื่อง ผลของโพแทสเซียมไนเตรท ยูเรีย ไทโอยูเรีย
และจิบเบอเรลลิน ต่อการกระตุ้นการแตกใบอ่อน
เพื่อเป็นแนวทางในการผลิตทุเรียนพันธุ์หมอนทองนอกฤดูกาล

> 6.3 ผู้ร่วมวิจัย : ชื่อโครงการวิจัย
>
> 6.3.1 ผู้ร่วมวิจัย เรื่อง โครงการบูรณาการการจัดการปุ๋ย อุตสาหกรรมและธุรกิจเงาะ

ของมหาวิทยาลัยราชภัฏรำไพพรรณี

6.3.2 ผู้ร่วมวิจัย เรื่อง
ผลของการใช้น้ำทิ้งจากถังหมักก๊าซชีวภาพด้วยมูลสัตว์และเปลือกทุเรียนต่อสมบัติทางเคมีของดินและการเจริญเติบโตของดาวเรือง
(*Tagetes erecta*)

> 6.3.3 ผู้ร่วมวิจัย เรื่อง ผลของการใช้สารโพแทสเซียมคลอเรตร่วมกับพาโคลบิวทราโซล,

โมโนโพแทสเซียมฟอสเฟต และเมพิควอทคลอไรด์ ต่อการออกดอกของลำไยในฤดูฝน

> 6.3.4 ผู้ร่วมวิจัย เรื่อง การใช้แพคโคบิวทราโซล เมพิควอทคลอไรด์ เอทีฟอน และ

โพแทสเซียมไนเตรท เพื่อยับยั้งการแตกใบอ่อนและลดการหลุดร่วงของผลทุเรียน

6.4 งานวิจัยที่ทำเสร็จแล้ว

+-----------------------------------------------------------------------+
| > 1\. **Prathumyot [W]{.smallcaps}**[.]{.smallcaps}, H. Ehara and H.  |
| > Naito[. 2007.]{.smallcaps} Effect of Diurnal Change of NaCl         |
| > Concentration in                                                    |
| >                                                                     |
| > Culture Solution on Growth of Sago Palm. *In* The 16^th^ Annual     |
| > Meeting of the Society of Sago Palm Studies, Japan.                 |
+-----------------------------------------------------------------------+
| 2\. **Prathumyot [W]{.smallcaps}**[.]{.smallcaps}, H. Ehara, H.       |
| Naito[. 2007.]{.smallcaps} Sago Palm Grown under Diurnal Change of    |
| NaCl Concentration in Hydroponics System with Automatic NaCl          |
| Concentration Controller. In The 223^rd^ Annual Meeting of the Crop   |
| Science Society of Japan, Japan.                                      |
+-----------------------------------------------------------------------+
