TsanaPhysics/JC-AGRITecH-AI/leqs-workshop/เบิกงวด 2 ชีวะ.md

# บันทึกข้อความ

**ส่วนราชการ:** คณะวิทยาศาสตร์และเทคโนโลยี มหาวิทยาลัยราชภัฏรำไพพรรณี โทร. 0-3947-1060  
**ที่:** ........................................................................................ **วันที่:** ....................................................................  
**เรื่อง:** ขออนุมัติเบิกเงินอุดหนุนการวิจัย งวดที่ 2  
**เรียน:** ผู้อำนวยการสถาบันวิจัยและพัฒนา  

ตามที่ข้าพเจ้า **นายชีวะ ทัศนา** อาจารย์/บุคลากร สังกัด **คณะวิทยาศาสตร์และเทคโนโลยี** ได้รับทุนอุดหนุนการวิจัยจากกองทุนวิจัย มหาวิทยาลัยราชภัฏรำไพพรรณี ประจำปีงบประมาณ **2569** ตามสัญญาเลขที่ **2251/2569** เพื่อใช้จ่ายในโครงการวิจัย เรื่อง **การพัฒนาชุดวิเคราะห์ปริมาณไนโตรเจนและฟอสฟอรัสในดินแบบพกพาด้วยหลักการสะท้อนแสงร่วมกับปัญญาประดิษฐ์** 

เป็นจำนวนเงินหลังจากหักค่าธรรมเนียมตามประกาศมหาวิทยาลัยแล้ว ทั้งสิ้น **69,750 บาท (หกหมื่นเก้าพันเจ็ดร้อยห้าสิบบาทถ้วน)** นั้น

ข้าพเจ้า ขออนุมัติเบิกเงินอุดหนุนการวิจัยเพื่อดำเนินงานวิจัยดังกล่าว **ประจำงวดที่ 2 (30%) จำนวนเงินทั้งสิ้น 20,925 บาท (สองหมื่นเก้าร้อยยี่สิบห้าบาทถ้วน)** พร้อมนี้ได้แนบเอกสารประกอบการเบิกเงิน ดังนี้

* [x] **1) แบบรายงานความก้าวหน้าโครงการวิจัย** จำนวน 1 ชุด
* [x] **2) แผนการดำเนินงานการวิจัยงวดที่ 2 (6 เดือน)** จำนวน 1 ชุด
* [x] **3) แผนการใช้งบประมาณการวิจัยงวดที่ 2 (30 %)** จำนวน 1 ชุด
* [x] **4) ร่างรายงานวิจัยบทที่ 1-4** จำนวน 1 ฉบับ
* [x] **5) สำเนาประกาศผลการพิจารณาทุนอุดหนุนฯ** จำนวน 1 ชุด
* [x] **6) สำเนาสัญญาการรับทุนอุดหนุนฯ** จำนวน 1 ชุด
* [x] **7) สำเนาบัตรประชาชน** จำนวน 1 ชุด
* [x] **8) ไฟล์บันทึกข้อความขออนุมัติเบิกเงินฯ และรายการที่ 1-4 ในระบบ RBRU-RMS**

จึงเรียนมาเพื่อโปรดพิจารณาอนุมัติ

\
\
(ลงชื่อ)..........................................................................  
(นายชีวะ ทัศนา)  
หัวหน้าโครงการวิจัย  

\
\
**ความเห็นของเจ้าหน้าที่ฝ่ายบริหารจัดการงานวิจัย:**  
เรียน รองผู้อำนวยการสถาบันวิจัยและพัฒนา  
พิจารณาเอกสารประกอบการเบิกเงินวิจัยแล้ว [x] เอกสารครบถ้วน [ ] เอกสารไม่ครบถ้วน  
(ลงชื่อ)........................................................... วันที่ ......./......./.......

**ความเห็นของรองผู้อำนวยการสถาบันวิจัยและพัฒนา:**  
เรียน ผู้อำนวยการสถาบันวิจัยและพัฒนา  
พิจารณารายละเอียดเนื้อหาเอกสารประกอบการเบิกเงินแล้ว เห็นว่า [x] เห็นควรอนุมัติ [ ] ไม่เห็นควรอนุมัติ  
(ลงชื่อ)........................................................... (ผู้ช่วยศาสตราจารย์ ดร.พัชรินทร์ รุจิรานุกูล) วันที่ ......./......./.......

**การพิจารณาของผู้อำนวยการสถาบันวิจัยและพัฒนา:**  
[x] อนุมัติ [ ] ไม่อนุมัติ  
(ลงชื่อ)........................................................... (ผู้ช่วยศาสตราจารย์ ดร.หยาดรุ้ง สุวรรณรัตน์) วันที่ ......./......./.......

\newpage

# แบบรายงานความก้าวหน้าโครงการวิจัย

### 1. รายละเอียดเกี่ยวกับโครงการวิจัย
* **1.1 ชื่อเรื่อง (ภาษาไทย):** การพัฒนาชุดวิเคราะห์ปริมาณไนโตรเจนและฟอสฟอรัสในดินแบบพกพาด้วยหลักการสะท้อนแสงร่วมกับปัญญาประดิษฐ์  
  **ชื่อเรื่อง (ภาษาอังกฤษ):** Development of a Portable Soil Nitrogen and Phosphorus Analyzer Using Optical Reflectance and Artificial Intelligence
* **1.2 คณะผู้วิจัย:**
  * **หัวหน้าโครงการวิจัย:** นายชีวะ ทัศนา  
    * *สังกัด:* สาขาวิชาฟิสิกส์ คณะวิทยาศาสตร์และเทคโนโลยี มหาวิทยาลัยราชภัฏรำไพพรรณี  
    * *โทรศัพท์มือถือ:* 093-7422654  
    * *E-mail:* chewa.t@rbru.ac.th  
    * *สัดส่วนการทำวิจัย:* **80 %**
  * **ผู้ร่วมวิจัย (1):** นายธนพัฒน์ ถิระวุฒิ สัดส่วนการทำวิจัย **20 %** (สาขาวิชาฟิสิกส์ คณะวิทยาศาสตร์และเทคโนโลยี)
* **การได้รับอนุมัติงบประมาณ:** ได้รับอนุมัติงบประมาณกองทุนวิจัย ปี **2569** จำนวนเงิน **75,000 บาท** (หักค่าธรรมเนียม 7% ร้อยละ 5,250 บาท เหลือรับสุทธิ **69,750 บาท**) ระยะเวลาการวิจัย **1 ปี**
  * *เริ่มทำการวิจัยเมื่อ:* เมษายน 2569  
  * *สิ้นสุดตามสัญญาการรับทุนฯ:* มีนาคม 2570

---

### 2. รายละเอียดความก้าวหน้าของการดำเนินการวิจัย
#### 2.1 วัตถุประสงค์ของการวิจัย
1. เพื่อออกแบบและสร้างชุดวิเคราะห์ปริมาณไนโตรเจน (Total N) และฟอสฟอรัส (Available P) ในดินแบบพกพา โดยใช้ระบบกำเนิดแสงหลายความยาวคลื่น (Multi-wavelength LED) ร่วมกับตัวตรวจวัดการสะท้อนแสง (Optical Reflectance Sensor)
2. เพื่อสร้างชุดข้อมูลความสัมพันธ์ระหว่างสเปกตรัมการสะท้อนแสงของดินที่ความยาวคลื่นต่าง ๆ กับค่าวิเคราะห์ปริมาณธาตุอาหารมาตรฐานจากห้องปฏิบัติการ
3. เพื่อพัฒนาและประเมินผลแบบจำลองปัญญาประดิษฐ์ (Machine Learning / Deep Learning) สำหรับทำนายปริมาณไนโตรเจนและฟอสฟอรัสในดินแบบ On-device/แอปพลิเคชันพกพาที่มีความแม่นยำสูง

\newpage

#### 2.2 ตารางเปรียบเทียบผลการดำเนินงานตามแผนการดำเนินงานวิจัยที่ได้เสนอไว้กับงานวิจัยที่ได้ดำเนินการจริง

| ระยะเวลา | แผนการดำเนินงานวิจัยที่เสนอไว้ | ผลการดำเนินงานจริงพร้อมสรุปวิเคราะห์ผลการดำเนินการวิจัยที่ได้ (พอสังเขป) |
| :---: | :--- | :--- |
| **เดือนที่ 1 - 2**<br>(เม.ย. - พ.ค. 69) | **1. ออกแบบและสร้างระบบฮาร์ดแวร์**<br>1.1 ทบทวนวรรณกรรมและออกแบบชุดวิเคราะห์<br>1.2 สร้างและประกอบชุดวิเคราะห์ต้นแบบ | **ดำเนินการเสร็จสมบูรณ์ 100%:**<br>1. ออกแบบโครงสร้างกล่องวัดแบบทึบแสง (Dark Chamber) ด้วยเครื่องพิมพ์ 3 มิติ (3D Printing Filament) พร้อมช่องยึดสมาร์ทโฟน/โมดูลตรวจวัดออปติคอลที่ป้องกันแสงรบกวนจากภายนอก<br>2. พัฒนาระบบกำเนิดแสง Multi-wavelength LED Array ครอบคลุมแถบสเปกตรัมที่สัมพันธ์กับการดูดกลืนและการสะท้อนแสงของไนโตรเจนและฟอสฟอรัสในดิน พร้อมวงจรควบคุมการกระตุ้นแสงแบบตามลำดับ (Sequential LED Driver) ควบคุมด้วยไมโครคอนโทรลเลอร์<br>3. ประกอบชุดวิเคราะห์ต้นแบบจำนวน 5 ชุด พร้อมแผ่นเทียบสีมาตรฐาน (Color Reference Chart) |
| **เดือนที่ 2 - 4**<br>(พ.ค. - ก.ค. 69) | **2. สร้างชุดข้อมูลมาตรฐาน**<br>2.1 วางแผนและเก็บตัวอย่างดิน<br>2.2 ส่งตัวอย่างวิเคราะห์ค่าอ้างอิง<br>2.3 วัดข้อมูลสเปกตรัมด้วยชุดต้นแบบ | **ดำเนินการเสร็จสมบูรณ์ 100%:**<br>1. วางแผนและเก็บตัวอย่างดินจากแปลงเกษตรกรรมในจังหวัดจันทบุรีและตราด<br>2. ส่งตัวอย่างดินตรวจวิเคราะห์ค่ามาตรฐานในห้องปฏิบัติการมาตรฐานเพื่อหาค่า Total Nitrogen (N) และ Available Phosphorus (P)<br>3. นำตัวอย่างดินมาตรวจวัดการสะท้อนแสงด้วยชุดต้นแบบเพื่อสกัดค่าความเข้มแสงและการตอบสนองเชิงสเปกตรัม จัดเก็บเป็นชุดข้อมูลดิจิทัล (Dataset) อย่างเป็นระบบ |
| **เดือนที่ 4 - 6**<br>(ก.ค. - ก.ย. 69) | **3. พัฒนาและประเมินผลโมเดล AI**<br>3.1 เตรียมและแบ่งชุดข้อมูล<br>3.2 สร้างและฝึกสอนโมเดล<br>3.3 ประเมินและคัดเลือกโมเดลที่ดีที่สุด | **ดำเนินการแล้ว 75% (ก้าวหน้ากว่าแผนงาน):**<br>1. ทำการประมวลผลข้อมูลล่วงหน้า (Data Preprocessing) ปรับสเกลข้อมูลสเปกตรัม (Normalization) และแบ่งชุดข้อมูล Training/Validation/Test Set<br>2. สร้างและฝึกสอนโครงข่ายประสาทเทียม (ANN / Regression Models) เพื่อทำนายค่า N และ P จากค่าการสะท้อนแสงหลายความยาวคลื่น<br>3. พัฒนาสถาปัตยกรรม Edge TinyML แปลงโมเดลให้สามารถรันบนไมโครคอนโทรลเลอร์และแอปพลิเคชันพกพาได้ในเวลา < 0.15 ms โดยไม่ต้องต่ออินเทอร์เน็ต<br>4. พัฒนาระบบแสดงผลหน้าจอ Cyber Dashboard เพื่อแสดงค่า N-P และ N-P-K Stoichiometry ร่วมกับเซนเซอร์ภาคสนามแบบ Real-time |

---

* **2.3 งบประมาณที่ใช้จ่ายไปแล้วในงวดที่ 1:** จำนวน **34,875 บาท** ความก้าวหน้าการดำเนินงานคิดเป็น **75 %** (ดำเนินงานได้เร็วกว่าแผนงานที่กำหนด)
* **2.4 รายละเอียดที่ได้แก้ไขปรับปรุงตามข้อเสนอแนะของผู้ทรงคุณวุฒิประเมินคุณภาพ (ถ้ามี):**  
  ผู้วิจัยได้ปรับปรุงโครงสร้างกล่องวัดให้มีระบบซีลกันแสงสะท้อนภายในแบบ Matt Black Coating และเพิ่มความยาวคลื่นอ้างอิง (Reference Wavelength) เพื่อชดเชยผลกระทบจากความชื้นในดินและสีพื้นฐานของดิน ทำให้โมเดล AI มีความแม่นยำสูงขึ้นในการจำแนกความเข้มข้นของ N และ P
* **2.5 งานตามแผนงานวิจัย/โครงการวิจัยที่จะดำเนินการต่อไป (งวดที่ 2: เดือนที่ 7 - 12):**

| กิจกรรม | เดือน 7 | เดือน 8 | เดือน 9 | เดือน 10 | เดือน 11 | เดือน 12 |
| :--- | :---: | :---: | :---: | :---: | :---: | :---: |
| 1. สอบเทียบความแม่นยำของชุดวิเคราะห์กับสารละลายมาตรฐาน N และ P ในห้องแล็บ | ■ | ■ | | | | |
| 2. ปรับปรุงแอปพลิเคชันพกพา/เฟิร์มแวร์ Edge AI ให้แสดงผลการประเมินปุ๋ยอัตโนมัติ | | ■ | ■ | | | |
| 3. นำชุดทดสอบต้นแบบไปทดสอบจริงในแปลงเกษตรกรรม จ.จันทบุรี และ ตราด | | | ■ | ■ | | |
| 4. วิเคราะห์ผลทางสถิติ (RMSE, R², t-test) เปรียบเทียบกับผลวิเคราะห์ห้องปฏิบัติการ | | | | ■ | ■ | |
| 5. จัดทำรายงานวิจัยฉบับสมบูรณ์ ยื่นจดลิขสิทธิ์ซอฟต์แวร์/อนุสิทธิบัตร | | | | | ■ | ■ |
| 6. จัดเตรียมบทความวิจัย (Manuscript) เพื่อส่งตีพิมพ์ในวารสารวิชาการระดับนานาชาติ | | | | | | ■ |

* **2.6 คำชี้แจงเกี่ยวกับปัญหา/อุปสรรค และวิธีการแก้ไข (ถ้ามี):**  
  * *ปัญหา:* สภาพความชื้นในตัวอย่างดินภาคสนามมีผลต่อค่าสัมประสิทธิ์การสะท้อนแสง (Reflectance) ทำให้สเปกตรัมที่วัดได้มีความแปรปรวน  
  * *การแก้ไข:* นำพารามิเตอร์ความชื้นในดินเข้ามาเป็นฟีเจอร์นำเข้า (Input Feature) ในโมเดลปัญญาประดิษฐ์เพื่อทำการ Decouple และชดเชยผลของความชื้นออกจากสเปกตรัมของสารประกอบไนโตรเจนและฟอสฟอรัสอย่างมีประสิทธิภาพ

\
\
(ลงชื่อ)..........................................................................  
(นายชีวะ ทัศนา)  
หัวหน้าโครงการวิจัย  
วันที่ ......... / ......... / ................

\
\
**ความเห็นจากการประเมินรายงานความก้าวหน้าโครงการวิจัยของผู้บังคับบัญชา (คณบดี):**  
[x] สนับสนุนให้ดำเนินการต่อไป  
[ ] ไม่สนับสนุนให้ดำเนินการต่อไป ระบุเหตุผล ............................................................................  
(ลงชื่อ)........................................................... (ผู้ช่วยศาสตราจารย์ ดร.วิชลัดดา อุ่นสะอาด) คณบดีคณะวิทยาศาสตร์และเทคโนโลยี

**ความเห็นจากการประเมินรายงานความก้าวหน้าโครงการวิจัยของสถาบันวิจัยและพัฒนา:**  
[x] สนับสนุน  
[ ] ไม่สนับสนุน ระบุเหตุผล ............................................................................  
(ลงชื่อ)........................................................... (ผู้ช่วยศาสตราจารย์ ดร.พัชรินทร์ รุจิรานุกูล) รองผู้อำนวยการสถาบันวิจัยและพัฒนา

\newpage

# แผนการดำเนินการวิจัย งวดที่ 2 (6 เดือน)

**โครงการวิจัย เรื่อง:** การพัฒนาชุดวิเคราะห์ปริมาณไนโตรเจนและฟอสฟอรัสในดินแบบพกพาด้วยหลักการสะท้อนแสงร่วมกับปัญญาประดิษฐ์  
**จากแหล่งทุน:** กองทุนวิจัย มหาวิทยาลัยราชภัฏรำไพพรรณี **ปีงบประมาณ:** 2569  

| กิจกรรม | ระยะเวลา | ผลที่คาดว่าจะได้รับ |
| :--- | :---: | :--- |
| **1. สอบเทียบความแม่นยำและเสถียรภาพของชุดตรวจวัดออปติคอลในห้องปฏิบัติการ**<br>- ทดสอบการตอบสนองเชิงสเปกตรัมกับสารละลายมาตรฐานไนโตรเจนและฟอสฟอรัสที่ความเข้มข้นต่าง ๆ<br>- หาค่าความสัมพันธ์เชิงเส้น กราฟมาตรฐาน และขีดจำกัดต่ำสุดในการตรวจวัด (Limit of Detection: LOD)<br>- ประเมินค่าความแม่นยำและความเที่ยง (%RSD < 5%) | ตุลาคม 2569 -<br>พฤศจิกายน 2569 | 1. รายงานผลการสอบเทียบเชิงสเปกตรัมและความแม่นยำของชุดตรวจวัดออปติคอล<br>2. แบบจำลองความสัมพันธ์ทางแสงที่ผ่านการสอบเทียบมาตรฐาน |
| **2. ปรับปรุงตัวเครื่องต้นแบบภาคสนามและทดสอบในแปลงเกษตรกรรมจริง**<br>- ประกอบเครื่องต้นแบบรุ่นสมบูรณ์พร้อมกล่องป้องกันแสงสะท้อนและแบตเตอรี่พกพา<br>- นำไปทดสอบเก็บตัวอย่างดินจริงในแปลงสวนผลไม้ จ.จันทบุรี และ ตราด ไม่น้อยกว่า 20 ตัวอย่าง<br>- เปรียบเทียบผลการวิเคราะห์ N และ P จากชุดพกพากับผลตรวจมาตรฐานจากห้องแล็บ | ธันวาคม 2569 -<br>มกราคม 2570 | 1. ชุดวิเคราะห์ปริมาณ N และ P ในดินแบบพกพาพร้อมใช้งานภาคสนามจริง<br>2. ฐานข้อมูลผลการทดสอบภาคสนามเปรียบเทียบกับวิธีมาตรฐานในห้องปฏิบัติการ |
| **3. วิเคราะห์ผลเชิงสถิติ จัดทำรายงานวิจัยฉบับสมบูรณ์ และยื่นจดทรัพย์สินทางปัญญา**<br>- วิเคราะห์ผลความแม่นยำทางสถิติ (RMSE, R-squared, t-test)<br>- สรุปผลการวิจัยและจัดทำร่างรายงานวิจัยฉบับสมบูรณ์ตามแบบฟอร์ม สวพ. RBRU<br>- ยื่นขอรับความคุ้มครองทรัพย์สินทางปัญญา (อนุสิทธิบัตร/ลิขสิทธิ์ซอฟต์แวร์)<br>- จัดเตรียมนิพนธ์ต้นฉบับบทความวิจัยเพื่อส่งตีพิมพ์ในวารสารวิชาการระดับนานาชาติ | กุมภาพันธ์ 2570 -<br>มีนาคม 2570 | 1. รายงานวิจัยฉบับสมบูรณ์ตามเกณฑ์กองทุนวิจัย มหาวิทยาลัยราชภัฏรำไพพรรณี<br>2. คำขอจดทะเบียนทรัพย์สินทางปัญญา 1 รายการ<br>3. ร่างบทความวิจัย (Manuscript) สำหรับตีพิมพ์ในวารสารวิชาการระดับนานาชาติ (Scopus) |

\newpage

# แผนการใช้งบประมาณการวิจัยงวดที่ 2 (30%)

**โครงการวิจัย เรื่อง:** การพัฒนาชุดวิเคราะห์ปริมาณไนโตรเจนและฟอสฟอรัสในดินแบบพกพาด้วยหลักการสะท้อนแสงร่วมกับปัญญาประดิษฐ์  
**จากแหล่งทุน:** กองทุนวิจัย มหาวิทยาลัยราชภัฏรำไพพรรณี **ปีงบประมาณ:** 2569  

| รายการ | จำนวนเงิน (บาท) |
| :--- | :---: |
| **1. งบบุคลากร** | |
| ค่าจ้างชั่วคราว | - |
| **2. งบดำเนินงาน** | |
| **2.1 ค่าตอบแทน ใช้สอย วัสดุ** | |
| **2.1.1 ค่าตอบแทน** | |
| ค่าตอบแทนปฏิบัติงานนอกเวลาราชการของคณะผู้วิจัย (2 คน x 50 บาท x 2 ชั่วโมง x 10 วัน) | **2,000** |
| **2.1.2 ค่าใช้สอย** | |
| 1) ค่าเดินทางเก็บตัวอย่างดินและทดสอบภาคสนาม (ระยะทาง 250 กม. x 4 บาท x 2 เที่ยวไป-กลับ) ในพื้นที่แปลงเกษตร จ.จันทบุรี และ จ.ตราด | **2,000** |
| 2) ค่าวิเคราะห์ตัวอย่างดินในห้องปฏิบัติการมาตรฐานสำหรับสอบเทียบยืนยันผลเพิ่มเติม (Total N และ Available P) (5 ตัวอย่าง x 1,000 บาท) | **5,000** |
| 3) ค่าลงทะเบียนเข้าร่วมประชุมวิชาการและนำเสนอผลงานวิจัย (1 ครั้ง x 4,000 บาท) | **4,000** |
| 4) ค่าซ่อมแซมครุภัณฑ์ | - |
| 5) ค่าจ้างเหมาบริการ | - |
| 6) ค่าใช้จ่ายในการสัมมนา และฝึกอบรม | - |
| 7) ค่ารับรองและพิธีการ | - |
| 8) ค่าเงินประกันสังคม | - |
| 9) ค่าใช้สอยอื่น ๆ | - |
| **2.1.3 ค่าวัสดุ** | |
| 1) ค่าวัสดุไฟฟ้าและวิทยุ | |
| - โมดูลเซนเซอร์สเปกตรัม/ออปติคอลและแผงวงจรขยายสัญญาณโฟโต้ไดโอดเพิ่มเติม | **3,500** |
| - วัสดุเส้นใย 3D Printing Filament สำหรับพิมพ์โครงสร้างกล่องครอบทึบแสงรุ่นปรับปรุงภาคสนาม | **1,500** |
| 2) ค่าวัสดุวิทยาศาสตร์ สารเคมี และอุปกรณ์ | |
| - สารเคมีและสารละลายมาตรฐานสำหรับทดสอบการสะท้อนแสงและสกัด N-P ในดิน | **1,500** |
| 3) ค่าวัสดุสำนักงานและวัสดุอื่น ๆ | |
| - วัสดุสำนักงาน เอกสารบันทึกผลการทดลอง แบบสำรวจ และหมึกพิมพ์ | **1,425** |
| **2.2 ค่าสาธารณูปโภค** | - |
| **รวมงบประมาณ งวดที่ 2 (30%)** | **20,925** |

*(หมายเหตุ: ถัวเฉลี่ยทุกรายการ ยอดเงินรวมทั้งสิ้น 20,925 บาท คิดเป็นร้อยละ 30 ของเงินทุนสนับสนุนงานวิจัยสุทธิ 69,750 บาท)*

\
\
(ลงชื่อ)..........................................................................  
(นายชีวะ ทัศนา)  
ผู้วิจัย  
วันที่ ......... / ......... / ................
