TsanaPhysics/JC-AGRITecH-AI/leqs-workshop/เบิกงวด 2.md

# บันทึกข้อความ

**ส่วนราชการ:** คณะวิทยาศาสตร์และเทคโนโลยี มหาวิทยาลัยราชภัฏรำไพพรรณี โทร. 0-3947-1060  
**ที่:** ........................................................................................ **วันที่:** ....................................................................  
**เรื่อง:** ขออนุมัติเบิกเงินอุดหนุนการวิจัย งวดที่ 2  
**เรียน:** ผู้อำนวยการสถาบันวิจัยและพัฒนา  

ตามที่ข้าพเจ้า **นายธนพัฒน์ ถิระวุฒิ** อาจารย์/บุคลากร สังกัด **คณะวิทยาศาสตร์และเทคโนโลยี** ได้รับทุนอุดหนุนการวิจัยจากกองทุนวิจัย มหาวิทยาลัยราชภัฏรำไพพรรณี ประจำปีงบประมาณ **2569** ตามสัญญาเลขที่ **2210/2569** เพื่อใช้จ่ายในโครงการวิจัย เรื่อง **การพัฒนาชุดทดสอบค่าความเป็นกรด-ด่างของดินแบบพกพาภาคสนามความแม่นยำสูงด้วยการชดเชยความคลาดเคลื่อนโดยปัญญาประดิษฐ์** 

เป็นจำนวนเงินหลังจากหักค่าธรรมเนียมตามประกาศมหาวิทยาลัยแล้ว ทั้งสิ้น **69,750 บาท (หกหมื่นเก้าพันเจ็ดร้อยห้าสิบบาทถ้วน)** นั้น

ข้าพเจ้า ขออนุมัติเบิกเงินอุดหนุนการวิจัยเพื่อดำเนินงานวิจัยดังกล่าว **ประจำงวดที่ 2 (30%) จำนวนเงินทั้งสิ้น 20,925 บาท (สองหมื่นเก้าร้อยยี่สิบห้าบาทถ้วน)** พร้อมนี้ได้แนบเอกสารประกอบการเบิกเงิน ดังนี้

* [x] **1) แบบรายงานความก้าวหน้าโครงการวิจัย** จำนวน 1 ชุด
* [x] **2) แผนการดำเนินงานการวิจัยงวดที่ 2 (6 เดือน)** จำนวน 1 ชุด
* [x] **3) แผนการใช้งบประมาณการวิจัยงวดที่ 2 (30 %)** จำนวน 1 ชุด
* [x] **4) ร่างรายงานวิจัยบทที่ 1-4** จำนวน 1 ฉบับ
* [x] **5) สำเนาประกาศผลการพิจารณาทุนอุดหนุนฯ** จำนวน 1 ชุด
* [x] **6) สำเนาสัญญาการรับทุนอุดหนุนฯ** จำนวน 1 ชุด
* [x] **7) สำเนาบัตรประชาชน** จำนวน 1 ชุด
* [x] **8) ไฟล์บันทึกข้อความขออนุมัติเบิกเงินฯ และรายการที่ 1-4 ในระบบ RBRU-RMS**

จึงเรียนมาเพื่อโปรดพิจารณาอนุมัติ

\
\
(ลงชื่อ)..........................................................................  
(นายธนพัฒน์ ถิระวุฒิ)  
หัวหน้าโครงการวิจัย  

\
\
**ความเห็นของเจ้าหน้าที่ฝ่ายบริหารจัดการงานวิจัย:**  
เรียน รองผู้อำนวยการสถาบันวิจัยและพัฒนา  
พิจารณาเอกสารประกอบการเบิกเงินวิจัยแล้ว [x] เอกสารครบถ้วน [ ] เอกสารไม่ครบถ้วน  
(ลงชื่อ)........................................................... วันที่ ......./......./.......

**ความเห็นของรองผู้อำนวยการสถาบันวิจัยและพัฒนา:**  
เรียน ผู้อำนวยการสถาบันวิจัยและพัฒนา  
พิจารณารายละเอียดเนื้อหาเอกสารประกอบการเบิกเงินแล้ว เห็นว่า [x] เห็นควรอนุมัติ [ ] ไม่เห็นควรอนุมัติ  
(ลงชื่อ)........................................................... (ผู้ช่วยศาสตราจารย์ ดร.พัชรินทร์ รุจิรานุกูล) วันที่ ......./......./.......

**การพิจารณาของผู้อำนวยการสถาบันวิจัยและพัฒนา:**  
[x] อนุมัติ [ ] ไม่อนุมัติ  
(ลงชื่อ)........................................................... (ผู้ช่วยศาสตราจารย์ ดร.หยาดรุ้ง สุวรรณรัตน์) วันที่ ......./......./.......

\newpage

# แบบรายงานความก้าวหน้าโครงการวิจัย

### 1. รายละเอียดเกี่ยวกับโครงการวิจัย
* **1.1 ชื่อเรื่อง (ภาษาไทย):** การพัฒนาชุดทดสอบค่าความเป็นกรด-ด่างของดินแบบพกพาภาคสนามความแม่นยำสูงด้วยการชดเชยความคลาดเคลื่อนโดยปัญญาประดิษฐ์  
  **ชื่อเรื่อง (ภาษาอังกฤษ):** Development of a Portable Field Test Kit for Soil Acidity and Alkalinity with High Accuracy through AI-Based Error Compensation
* **1.2 คณะผู้วิจัย:**
  * **หัวหน้าโครงการวิจัย:** นายธนพัฒน์ ถิระวุฒิ  
    * *สังกัด:* สาขาวิชาฟิสิกส์ คณะวิทยาศาสตร์และเทคโนโลยี มหาวิทยาลัยราชภัฏรำไพพรรณี  
    * *โทรศัพท์มือถือ:* 085-0716286  
    * *E-mail:* tanapat.t@rbru.ac.th  
    * *สัดส่วนการทำวิจัย:* **50 %**
  * **ผู้ร่วมวิจัย (1):** นายชีวะ ทัศนา สัดส่วนการทำวิจัย **30 %** (สาขาวิชาฟิสิกส์ คณะวิทยาศาสตร์และเทคโนโลยี)
  * **ผู้ร่วมวิจัย (2):** นางสาวนันทพร มูลรังษี สัดส่วนการทำวิจัย **10 %** (สาขาวิชาเคมีประยุกต์ คณะวิทยาศาสตร์และเทคโนโลยี)
  * **ผู้ร่วมวิจัย (3):** นายนิภัทร เปี่ยมอรุณ สัดส่วนการทำวิจัย **10 %** (สาขาวิชาเคมีประยุกต์ คณะวิทยาศาสตร์และเทคโนโลยี)
* **การได้รับอนุมัติงบประมาณ:** ได้รับอนุมัติงบประมาณกองทุนวิจัย ปี **2569** จำนวนเงิน **75,000 บาท** (หักค่าธรรมเนียม 7% ร้อยละ 5,250 บาท เหลือรับสุทธิ **69,750 บาท**) ระยะเวลาการวิจัย **1 ปี**
  * *เริ่มทำการวิจัยเมื่อ:* เมษายน 2569  
  * *สิ้นสุดตามสัญญาการรับทุนฯ:* มีนาคม 2570

---

### 2. รายละเอียดความก้าวหน้าของการดำเนินการวิจัย
#### 2.1 วัตถุประสงค์ของการวิจัย
1. เพื่อศึกษาและสร้างชุดข้อมูลความสัมพันธ์ระหว่างค่าศักย์ไฟฟ้าของเซนเซอร์วัดค่าความเป็นกรด-เบสของดิน (Soil pH) กับค่าอุณหภูมิ และค่า Soil pH มาตรฐาน สำหรับพัฒนาโมเดลปัญญาประดิษฐ์
2. เพื่อพัฒนาโมเดลปัญญาประดิษฐ์ที่สามารถชดเชยความคลาดเคลื่อนในการวัดที่เกิดจากผลของอุณหภูมิ (Temperature Effect) และความไม่เป็นเชิงเส้น (Non-linearity) ของเซนเซอร์
3. เพื่อทดสอบประสิทธิภาพของชุดทดสอบค่าความเป็นกรด-ด่างของดินแบบพกพาภาคสนามที่มีการชดเชยความคลาดเคลื่อนโดยปัญญาประดิษฐ์ โดยเปรียบเทียบความแม่นยำกับเครื่องมือวัดมาตรฐาน และทดสอบจริงในภาคสนาม (สวนผลไม้ทุเรียนในจังหวัดจันทบุรีและตราด)

\newpage

#### 2.2 ตารางเปรียบเทียบผลการดำเนินงานตามแผนการดำเนินงานวิจัยที่ได้เสนอไว้กับงานวิจัยที่ได้ดำเนินการจริง

| ระยะเวลา | แผนการดำเนินงานวิจัยที่เสนอไว้ | ผลการดำเนินงานจริงพร้อมสรุปวิเคราะห์ผลการดำเนินการวิจัยที่ได้ (พอสังเขป) |
| :---: | :--- | :--- |
| **เดือนที่ 1 - 3**<br>(เม.ย. - มิ.ย. 69) | **1. ทบทวนวรรณกรรมและออกแบบระบบ**<br>1.1 ทบทวนวรรณกรรมที่เกี่ยวข้องล่าสุด<br>1.2 ออกแบบและสร้างระบบเก็บข้อมูล (Hardware & Software)<br>1.3 จัดหาและเตรียมสารเคมี/อุปกรณ์ | **ดำเนินการเสร็จสมบูรณ์ 100%:**<br>1. ทบทวนทฤษฎีสมการเนินสต์ (Nernst Equation) ผลกระทบของอุณหภูมิต่อความชัน ($2.303RT/nF$) และโครงข่ายประสาทเทียม ANN ชดเชยความคลาดเคลื่อน<br>2. พัฒนาระบบฮาร์ดแวร์ต้นแบบพกพาภาคสนามบนบอร์ด **ATD3.5-S3 (ESP32-S3 Dual-Core 240MHz)** ร่วมกับ Farm1 Shield เชื่อมต่อโพรบวัดดินอุตสาหกรรม **Soil 7-in-1 Modbus RS485** สแตนเลส 316L และเซนเซอร์อ้างอิงอุณหภูมิความแม่นยำสูง **Sensirion SHT45 (I2C)**<br>3. จัดหาอุปกรณ์อิเล็กทรอนิกส์ หัวโพรบ และสารเคมีบัฟเฟอร์มาตรฐานเรียบร้อย |
| **เดือนที่ 3 - 5**<br>(มิ.ย. - ส.ค. 69) | **2. เก็บข้อมูลและสร้างชุดข้อมูล**<br>2.1 ทดลองเก็บข้อมูลในห้องปฏิบัติการ<br>2.2 ตรวจสอบและจัดระเบียบชุดข้อมูล (Data Cleaning) | **ดำเนินการเสร็จสมบูรณ์ 100%:**<br>1. พัฒนาระบบ Data Acquisition Firmware อ่านค่าสัญญาณเคมีไฟฟ้า Modbus RTU (Holding Registers) พร้อมระบบตรวจสอบความถูกต้อง **CRC-16 Checksum** และ Error Packet Counter ปราศจากสัญญาณรบกวน<br>2. สร้างระบบบันทึกข้อมูล Telemetry Data Pipeline ส่งผ่านพอร์ต USB สู่ระบบฐานข้อมูล **SQLite / CSV** อัตโนมัติ พร้อมสำหรับการฝึกสอนโมเดล AI |
| **เดือนที่ 5 - 8**<br>(ส.ค. - พ.ย. 69) | **3. พัฒนาแบบจำลอง AI และอัลกอริทึม**<br>3.1 เตรียมข้อมูล (Data Preprocessing) และแบ่งชุดข้อมูล<br>3.2 สร้างและฝึกสอนแบบจำลอง AI (Model Training)<br>3.3 ประเมินและคัดเลือกโมเดลที่ดีที่สุด (Model Evaluation) | **ดำเนินการแล้ว 75% (ก้าวหน้ากว่าแผนงาน):**<br>1. ออกแบบสถาปัตยกรรมโครงข่ายประสาทเทียม **Artificial Neural Network (ANN) / Multilayer Perceptron (MLP)** ทำหน้าที่เป็นฟังก์ชันผกผัน (Inverse Mapping Function) ชดเชยอุณหภูมิและความไม่เป็นเชิงเส้น: $\text{pH}_{\text{predicted}} = g(E_{\text{real}}, T, \text{EC})$<br>2. แปลงโครงข่ายให้อยู่ในรูปแบบ **Edge TinyML Decoupling Engine** ฝังลงบน ESP32-S3 ให้ประมวลผล On-device ได้รวดเร็ว (< 0.12 ms) โดยไม่ต้องเชื่อมต่ออินเทอร์เน็ต<br>3. พัฒนาระบบแสดงผล **Cyber Dashboard UI 480x320 พิกเซล บนจอ 3.5 นิ้ว IPS (LovyanGFX)** แสดงค่า pH ชดเชย, N-P-K Stoichiometry, และเรดาร์สุขภาพดินแบบ Real-time |

---

* **2.3 งบประมาณที่ใช้จ่ายไปแล้วในงวดที่ 1:** จำนวน **34,875 บาท** ความก้าวหน้าการดำเนินงานคิดเป็น **75 %** (ดำเนินงานได้เร็วกว่าแผนงานที่กำหนด)
* **2.4 รายละเอียดที่ได้แก้ไขปรับปรุงตามข้อเสนอแนะของผู้ทรงคุณวุฒิประเมินคุณภาพ (ถ้ามี):**  
  ผู้วิจัยได้นำข้อเสนอแนะของผู้ทรงคุณวุฒิมาบูรณาการการตรวจวัดค่าสภาพนำไฟฟ้า (EC) และอุณหภูมิร่วมกับค่า pH ดิน เพื่อให้โมเดลปัญญาประดิษฐ์สามารถชดเชยผลกระทบจากไอออนรบกวนในสารละลายดินได้อย่างแม่นยำยิ่งขึ้น พร้อมทั้งพัฒนาระบบส่วนต่อประสานผู้ใช้ (User Interface) ให้ใช้งานง่ายและมีปุ่มนำทางสะดวกสำหรับเกษตรกรในภาคสนาม
* **2.5 งานตามแผนงานวิจัย/โครงการวิจัยที่จะดำเนินการต่อไป (งวดที่ 2: เดือนที่ 7 - 12):**

| กิจกรรม | เดือน 7 | เดือน 8 | เดือน 9 | เดือน 10 | เดือน 11 | เดือน 12 |
| :--- | :---: | :---: | :---: | :---: | :---: | :---: |
| 1. ทดสอบความใช้ได้ของวิธีในห้องปฏิบัติการ (Method Validation: Bias & %RSD) | ■ | ■ | | | | |
| 2. ประกอบเครื่องต้นแบบภาคสนามสมบูรณ์พร้อมกล่องพกพา | | ■ | ■ | | | |
| 3. ทดสอบเปรียบเทียบจริงในภาคสนาม (สวนทุเรียน จ.จันทบุรี และ จ.ตราด) | | | ■ | ■ | | |
| 4. วิเคราะห์ผลทางสถิติ (t-test) เปรียบเทียบกับวิธีมาตรฐานในห้องปฏิบัติการ | | | | ■ | ■ | |
| 5. จัดทำร่างรายงานวิจัยฉบับสมบูรณ์ และยื่นขอจดทรัพย์สินทางปัญญา | | | | | ■ | ■ |
| 6. จัดเตรียมบทความวิจัยเพื่อส่งตีพิมพ์ในวารสารวิชาการระดับนานาชาติ | | | | | | ■ |

* **2.6 คำชี้แจงเกี่ยวกับปัญหา/อุปสรรค และวิธีการแก้ไข (ถ้ามี):**  
  * *ปัญหา:* หัววัดค่าความเป็นกรด-ด่างในภาคสนามมักมีค่าเบี่ยงเบน (Drift) เมื่อสัมผัสกับอุณหภูมิที่ผันผวนสูงระหว่างช่วงกลางวันและกลางคืนในแปลงปลูก  
  * *การแก้ไข:* คณะผู้วิจัยได้พัฒนาฟังก์ชันชดเชยอุณหภูมิสองขั้นตอน (Two-stage Temperature Compensation) โดยนำการชดเชยเชิงกายภาพตามสมการเนินสต์มาผนวกเข้ากับโครงข่ายประสาทเทียม TinyML เพื่อขจัดความคลาดเคลื่อนได้อย่างแม่นยำในระดับเสี้ยววินาที

\
\
(ลงชื่อ)..........................................................................  
(นายธนพัฒน์ ถิระวุฒิ)  
หัวหน้าโครงการวิจัย  
วันที่ ......... / ......... / ................

\
\
**ความเห็นจากการประเมินรายงานความก้าวหน้าโครงการวิจัยของผู้บังคับบัญชา (คณบดี):**  
[x] สนับสนุนให้ดำเนินการต่อไป  
[ ] ไม่สนับสนุนให้ดำเนินการต่อไป ระบุเหตุผล ............................................................................  
(ลงชื่อ)........................................................... (ผู้ช่วยศาสตราจารย์ ดร.วิชลัดดา อุ่นสะอาด) คณบดีคณะวิทยาศาสตร์และเทคโนโลยี

**ความเห็นจากการประเมินรายงานความก้าวหน้าโครงการวิจัยของสถาบันวิจัยและพัฒนา:**  
[x] สนับสนุน  
[ ] ไม่สนับสนุน ระบุเหตุผล ............................................................................  
(ลงชื่อ)........................................................... (ผู้ช่วยศาสตราจารย์ ดร.พัชรินทร์ รุจิรานุกูล) รองผู้อำนวยการสถาบันวิจัยและพัฒนา

\newpage

# แผนการดำเนินการวิจัย งวดที่ 2 (6 เดือน)

**โครงการวิจัย เรื่อง:** การพัฒนาชุดทดสอบค่าความเป็นกรด-ด่างของดินแบบพกพาภาคสนามความแม่นยำสูงด้วยการชดเชยความคลาดเคลื่อนโดยปัญญาประดิษฐ์  
**จากแหล่งทุน:** กองทุนวิจัย มหาวิทยาลัยราชภัฏรำไพพรรณี **ปีงบประมาณ:** 2569  

| กิจกรรม | ระยะเวลา | ผลที่คาดว่าจะได้รับ |
| :--- | :---: | :--- |
| **1. ทดสอบความใช้ได้ของวิธี (Method Validation) ในห้องปฏิบัติการ**<br>- ทดสอบความแม่น (Accuracy) ในสารละลายบัฟเฟอร์มาตรฐาน (pH 4.01, 7.00, 10.01) หาค่าร้อยละความคลาดเคลื่อน (Bias < 5%)<br>- ทดสอบความเที่ยง (Precision) ทำซ้ำ 11 ครั้ง (n=11) เพื่อหาค่า %RSD (< 5%) | ตุลาคม 2569 -<br>พฤศจิกายน 2569 | รายงานผลการทดสอบความใช้ได้ของวิธี (Validation Report) ที่ยืนยันความแม่นยำและความเที่ยงของชุดทดสอบตามมาตรฐานเคมีวิเคราะห์ |
| **2. ประกอบเครื่องต้นแบบภาคสนามและทดสอบในแปลงสวนผลไม้จริง**<br>- ประกอบชุดต้นแบบพกพาภาคสนามพร้อมโพรบและแบตเตอรี่ในตัว<br>- ทดสอบเก็บตัวอย่างดินจริงในแปลงสวนทุเรียน อ.มะขาม, อ.ท่าใหม่ จ.จันทบุรี และ อ.เขาสมิง จ.ตราด ไม่น้อยกว่า 30 ตัวอย่าง<br>- เปรียบเทียบผลการวัดภาคสนามกับผลวิเคราะห์จากห้องปฏิบัติการมาตรฐาน | ธันวาคม 2569 -<br>มกราคม 2570 | 1. เครื่องต้นแบบชุดวัด pH ดินพกพาภาคสนามความแม่นยำสูงพร้อมใช้งานจริง<br>2. ชุดข้อมูลผลการเปรียบเทียบค่า pH ในตัวอย่างดินจริงเทียบกับเครื่องวัดมาตรฐานในห้องแล็บ |
| **3. วิเคราะห์ผลเชิงสถิติ จัดทำรายงานวิจัยฉบับสมบูรณ์ และยื่นจดทรัพย์สินทางปัญญา**<br>- วิเคราะห์ผลความแม่นยำทางสถิติด้วยการทดสอบ t-test<br>- สรุปผลการวิจัยและจัดทำร่างรายงานวิจัยฉบับสมบูรณ์<br>- ยื่นขอรับการคุ้มครองทรัพย์สินทางปัญญา (อนุสิทธิบัตร/ลิขสิทธิ์)<br>- จัดเตรียมนิพนธ์ต้นฉบับบทความวิจัยเพื่อส่งตีพิมพ์ | กุมภาพันธ์ 2570 -<br>มีนาคม 2570 | 1. รายงานวิจัยฉบับสมบูรณ์ตามเกณฑ์กองทุนวิจัย RBRU<br>2. คำขอจดทะเบียนทรัพย์สินทางปัญญา 1 รายการ<br>3. ร่างบทความวิจัย (Manuscript) สำหรับตีพิมพ์ในวารสารวิชาการระดับนานาชาติ |

\newpage

# แผนการใช้งบประมาณการวิจัยงวดที่ 2 (30%)

**โครงการวิจัย เรื่อง:** การพัฒนาชุดทดสอบค่าความเป็นกรด-ด่างของดินแบบพกพาภาคสนามความแม่นยำสูงด้วยการชดเชยความคลาดเคลื่อนโดยปัญญาประดิษฐ์  
**จากแหล่งทุน:** กองทุนวิจัย มหาวิทยาลัยราชภัฏรำไพพรรณี **ปีงบประมาณ:** 2569  

| รายการ | จำนวนเงิน (บาท) |
| :--- | :---: |
| **1. งบบุคลากร** | |
| ค่าจ้างชั่วคราว | - |
| **2. งบดำเนินงาน** | |
| **2.1 ค่าตอบแทน ใช้สอย วัสดุ** | |
| **2.1.1 ค่าตอบแทน** | |
| ค่าตอบแทนปฏิบัติงานนอกเวลาราชการของคณะผู้วิจัย (3 คน x 50 บาท x 2 ชั่วโมง x 10 วัน) | **3,000** |
| **2.1.2 ค่าใช้สอย** | |
| 1) ค่าเดินทางเก็บตัวอย่างดินและทดสอบภาคสนาม (ระยะทาง 300 กม. x 4 บาท x 2 เที่ยวไป-กลับ) ในพื้นที่สวนผลไม้ จ.จันทบุรี และ จ.ตราด | **2,400** |
| 2) ค่าลงทะเบียนเข้าร่วมประชุมวิชาการและนำเสนอผลงานวิจัย (1 ครั้ง x 5,000 บาท) | **5,000** |
| 3) ค่าซ่อมแซมครุภัณฑ์ | - |
| 4) ค่าจ้างเหมาบริการ | - |
| 5) ค่าใช้จ่ายในการสัมมนา และฝึกอบรม | - |
| 6) ค่ารับรองและพิธีการ | - |
| 7) ค่าเงินประกันสังคม | - |
| 8) ค่าใช้สอยอื่น ๆ | - |
| **2.1.3 ค่าวัสดุ** | |
| 1) ค่าวัสดุไฟฟ้าและวิทยุ | |
| - แผงวงจรวัดแรงดันไฟฟ้าและส่วนขยายการเชื่อมต่อ pH เพิ่มเติม (2 ชุด x 2,000 บาท) | **4,000** |
| - แผงวงจรเอนกประสงค์ สายไฟ สายเคเบิลสัญญาณ RS485 ฉนวนกันสัญญาณรบกวน และอุปกรณ์ประกอบกล่องพกพา | **3,525** |
| 2) ค่าวัสดุวิทยาศาสตร์ สารเคมี และอุปกรณ์ | |
| - สารเคมีสำหรับเตรียมและสกัดตัวอย่างดินภาคสนาม | **1,500** |
| 3) ค่าวัสดุสำนักงานและวัสดุอื่น ๆ | |
| - วัสดุสำนักงาน เอกสารบันทึกผลภาคสนาม แบบฟอร์มสำรวจ และหมึกพิมพ์ | **1,500** |
| **2.2 ค่าสาธารณูปโภค** | - |
| **รวมงบประมาณ งวดที่ 2 (30%)** | **20,925** |

*(หมายเหตุ: ถัวเฉลี่ยทุกรายการ ยอดเงินรวมทั้งสิ้น 20,925 บาท คิดเป็นร้อยละ 30 ของเงินทุนสนับสนุนงานวิจัยสุทธิ 69,750 บาท)*

\
\
(ลงชื่อ)..........................................................................  
(นายธนพัฒน์ ถิระวุฒิ)  
ผู้วิจัย  
วันที่ ......... / ......... / ................
