TsanaPhysics/JC-AGRITecH-AI/latex_book/main.tex

\documentclass[11pt,a4paper,oneside]{book}

% ==============================================================================
% นำเข้าแพ็กเกจสไตล์มาตรฐาน มรภ.รำไพพรรณี (RBRU Master Style)
% ==============================================================================
\usepackage{styles/rbru_style}

\begin{document}

% ==============================================================================
% ส่วนนำ (Front Matter)
% ==============================================================================
\frontmatter
\pagestyle{empty}

% 1. หน้าปกหนังสือวิชาการ (Cover)
\input{frontmatter/cover}

% 2. คำนำ (Preface)
\pagestyle{plain}
\input{frontmatter/preface}

% 3. สารบัญ สารบัญภาพ สารบัญตาราง (TOC, LOF, LOT)
\input{frontmatter/toc}

% ==============================================================================
% ส่วนเนื้อหาหลัก (Main Matter)
% ==============================================================================
\mainmatter
\pagestyle{fancy}

% บทที่ 1: สถาปัตยกรรมฮาร์ดแวร์ระบบแปลงปลูกอัจฉริยะ
\input{chapters/ch01_introduction_hardware}

% บทที่ 2: วิศวกรรมเฟิร์มแวร์ไมโครคอนโทรลเลอร์และการแก้ไขปัญหาเชิงลึก
\input{chapters/ch02_firmware_engineering}

% บทที่ 3: สถาปัตยกรรมการสื่อสารข้อมูลไร้สายและการจัดเก็บอนุกรมเวลา
\input{chapters/ch03_telemetry_pipeline}

% บทที่ 4: การพัฒนาระบบฐานข้อมูลและแดชบอร์ดด้วยภาษาไพทอน
\input{chapters/ch04_self_hosted_dashboard}

% บทที่ 5: ปัญญาประดิษฐ์และการเรียนรู้เชิงลึกสำหรับเกษตรกรรมแม่นยำ
\input{chapters/ch05_deep_learning_agritech}

% ==============================================================================
% ภาคผนวก (Appendix)
% ==============================================================================
\appendix
\input{chapters/appendix_prompts}
\input{chapters/appendix_code}

% ==============================================================================
% ส่วนท้ายเล่ม (Back Matter)
% ==============================================================================
\backmatter

% บรรณานุกรมมาตรฐานสากล APA 7
\input{backmatter/references}

% ดัชนีสืบค้นคำสำคัญ (Bilingual Index)
\clearpage
\phantomsection
\printindex

% ประวัติผู้เขียน ผศ.ดร.ชีวะ ทัศนา (1 หน้าเดียวมาตรฐาน มรภ.รำไพพรรณี)
\input{backmatter/biography}

\end{document}
