TsanaPhysics/JC-AGRITecH-AI/assets/images/atd35/11_qr_portal_screen.jpg

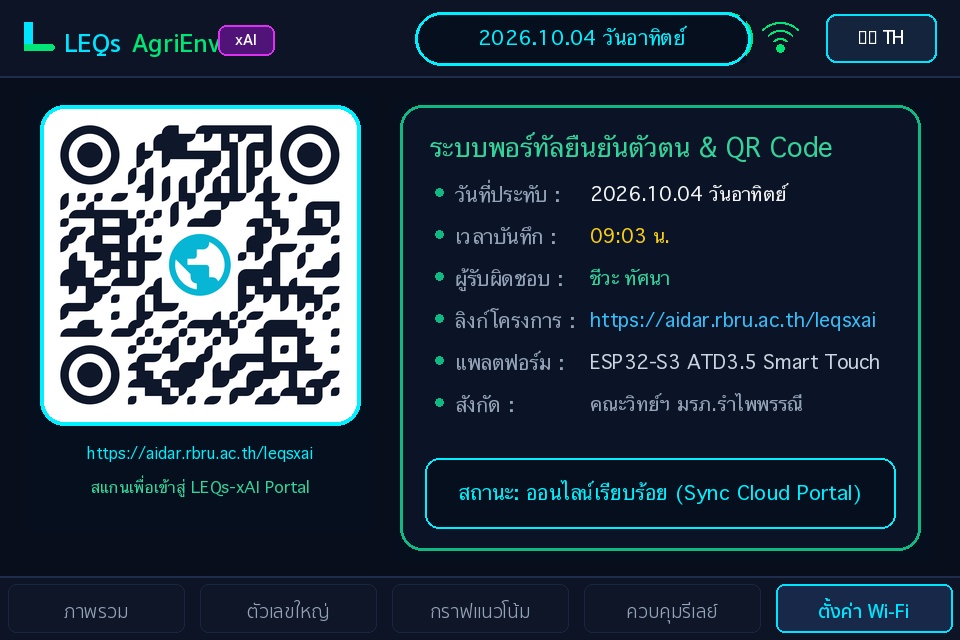
assets/images/atd35/11_qr_portal_screen.jpg
