TsanaPhysics/JC-AGRITecH-AI/assets/images/qr_leqs-agri-workshop.png

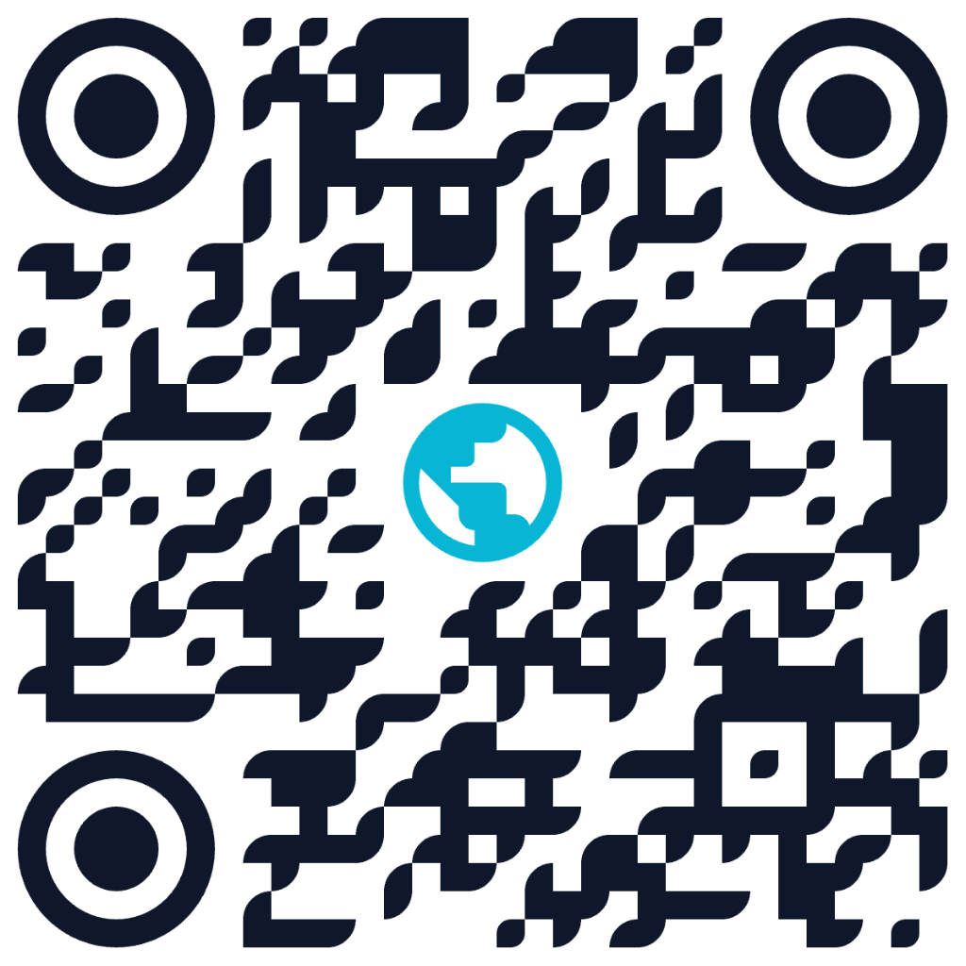
assets/images/qr_leqs-agri-workshop.png
