TsanaPhysics/JC-AGRITecH-AI/assets/images/qr_line_group.jpg

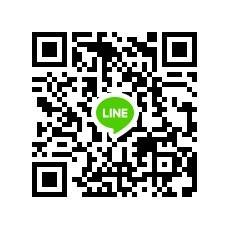
assets/images/qr_line_group.jpg
