TsanaPhysics/JC-AGRITecH-AI/assets/images/soil_nutrient2026/portable_iot_pixar.png

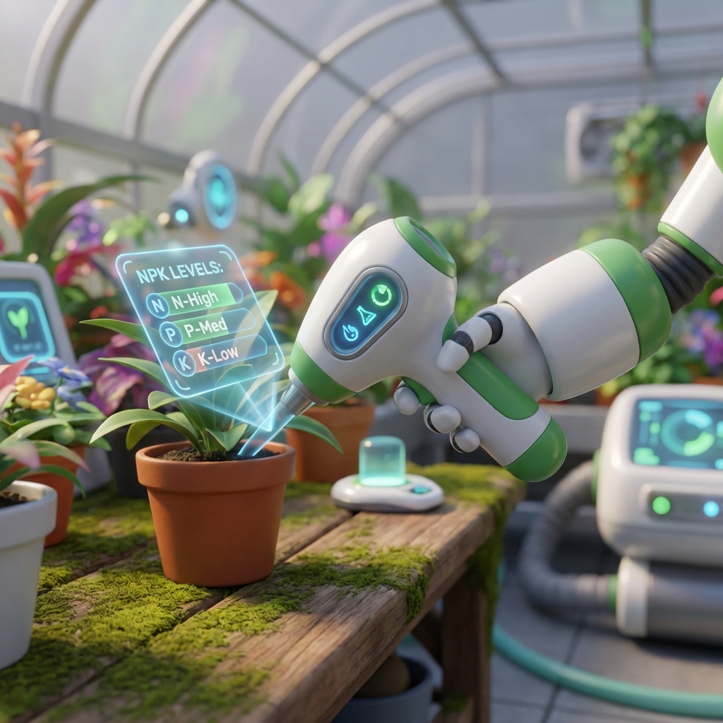
assets/images/soil_nutrient2026/portable_iot_pixar.png
