TsanaPhysics/JC-AGRITecH-AI/assets/images/soil_nutrient2026/sample_soil_lab.jpg

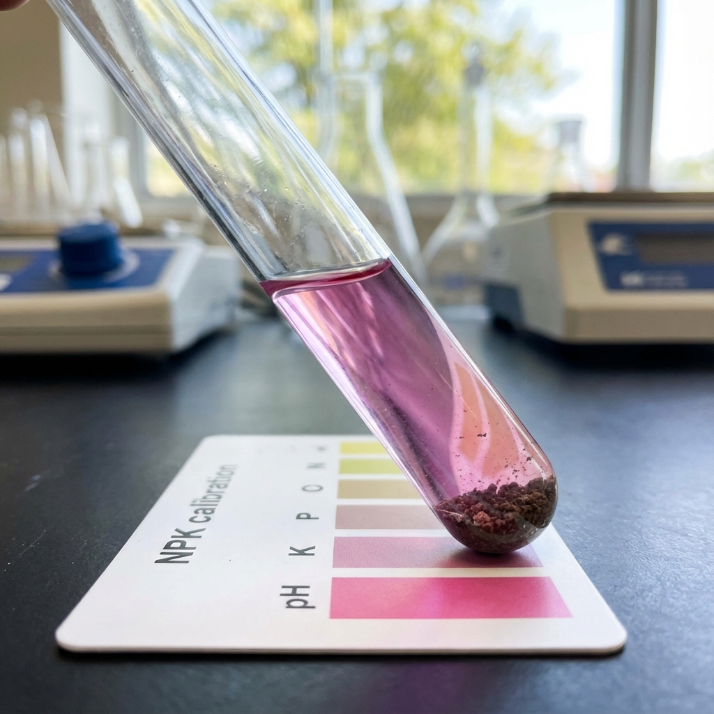
assets/images/soil_nutrient2026/sample_soil_lab.jpg
