TsanaPhysics/JC-AGRITecH-AI/assets/images/soil_nutrient2026/simulated_cam_feed_1766190123.jpg

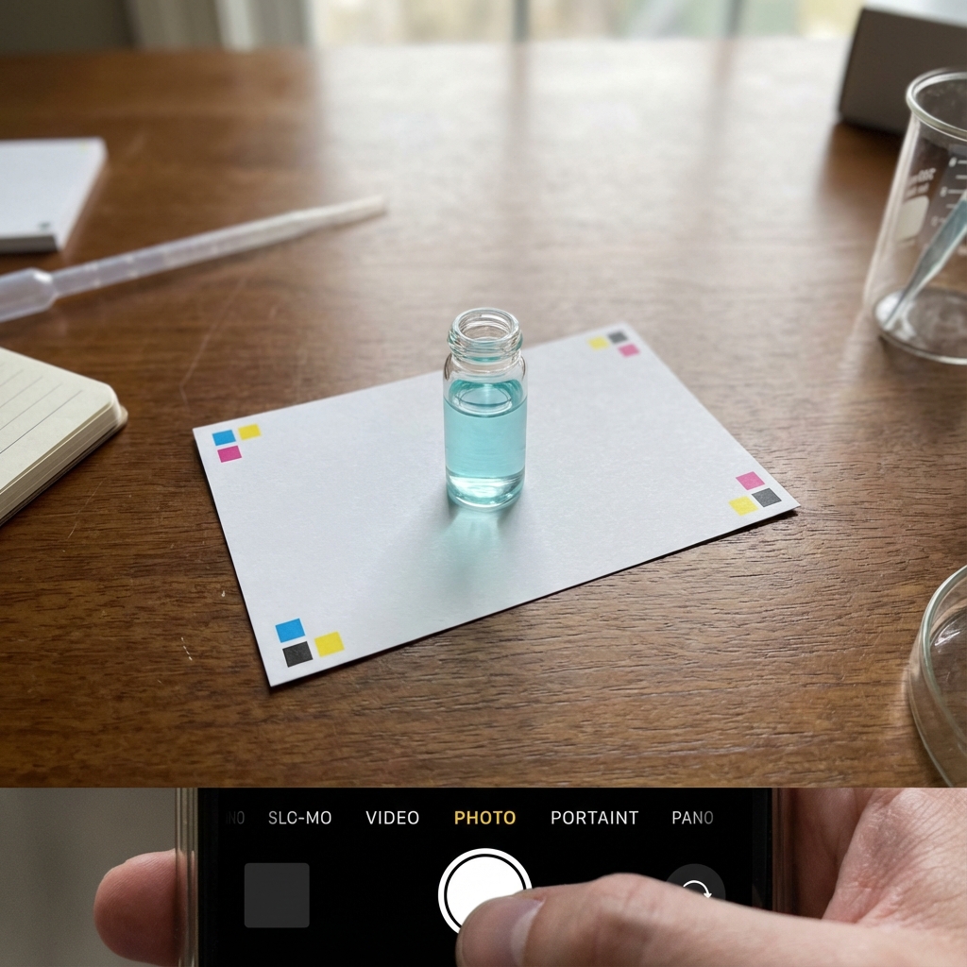
assets/images/soil_nutrient2026/simulated_cam_feed_1766190123.jpg
