TsanaPhysics/JC-AGRITecH-AI/assets/images/soil_nutrient2026/tech_ai_network_1766189604369.png

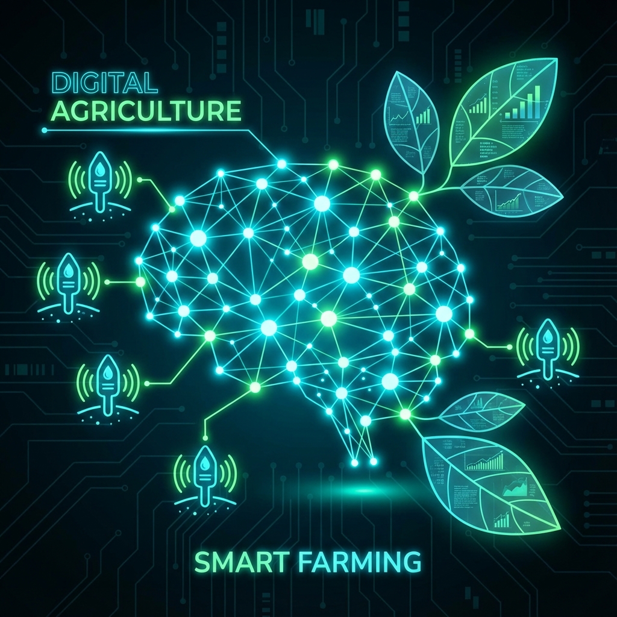
assets/images/soil_nutrient2026/tech_ai_network_1766189604369.png
