TsanaPhysics/JC-AGRITecH-AI/assets/images/soil_nutrient2026/tech_spectroscopy_diagram_1766189587511.png

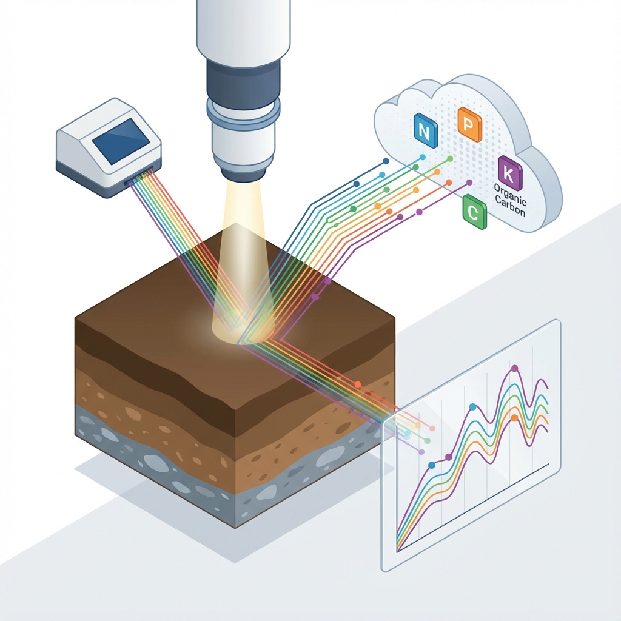
assets/images/soil_nutrient2026/tech_spectroscopy_diagram_1766189587511.png
