TsanaPhysics/JC-AGRITecH-AI/chewa/figures/fig_dark_chamber_exploded_view.jpg

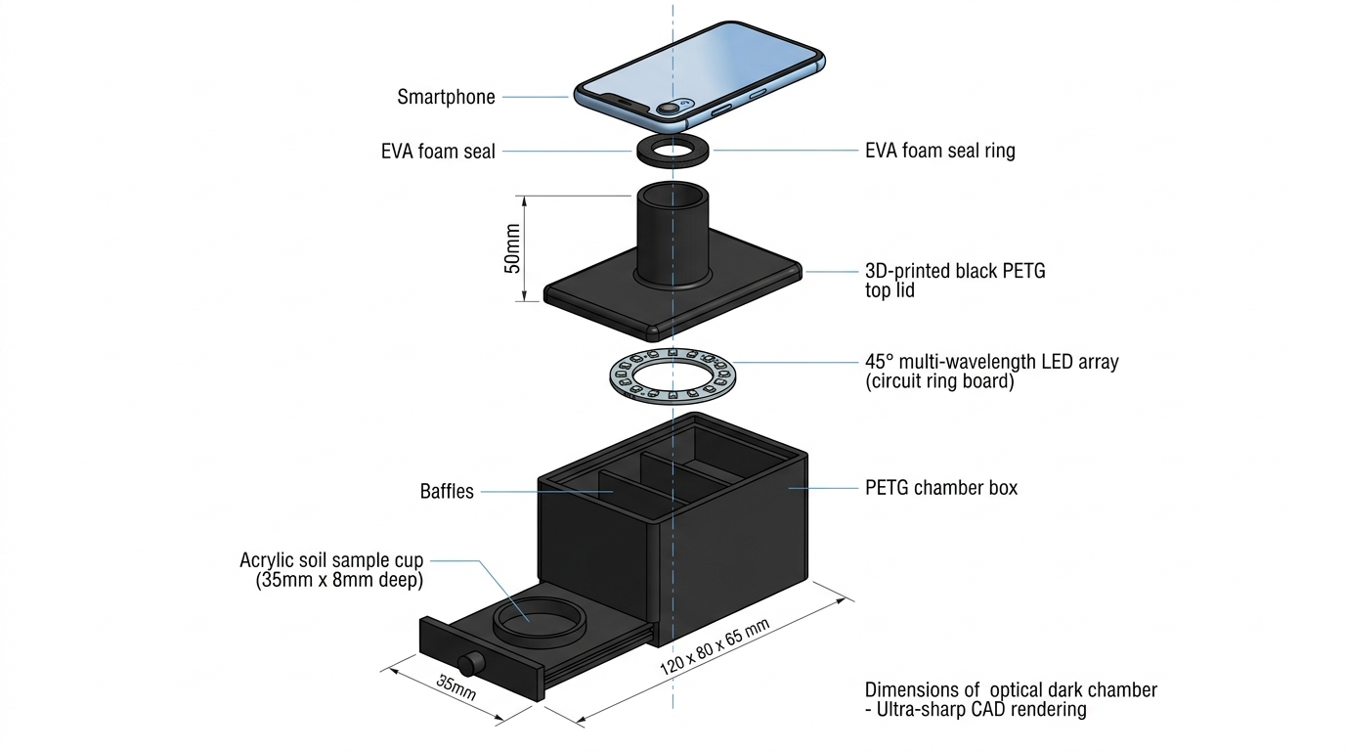
chewa/figures/fig_dark_chamber_exploded_view.jpg
