TsanaPhysics/JC-AGRITecH-AI/chewa/figures/fig_dark_chamber_thai_100percent.jpg

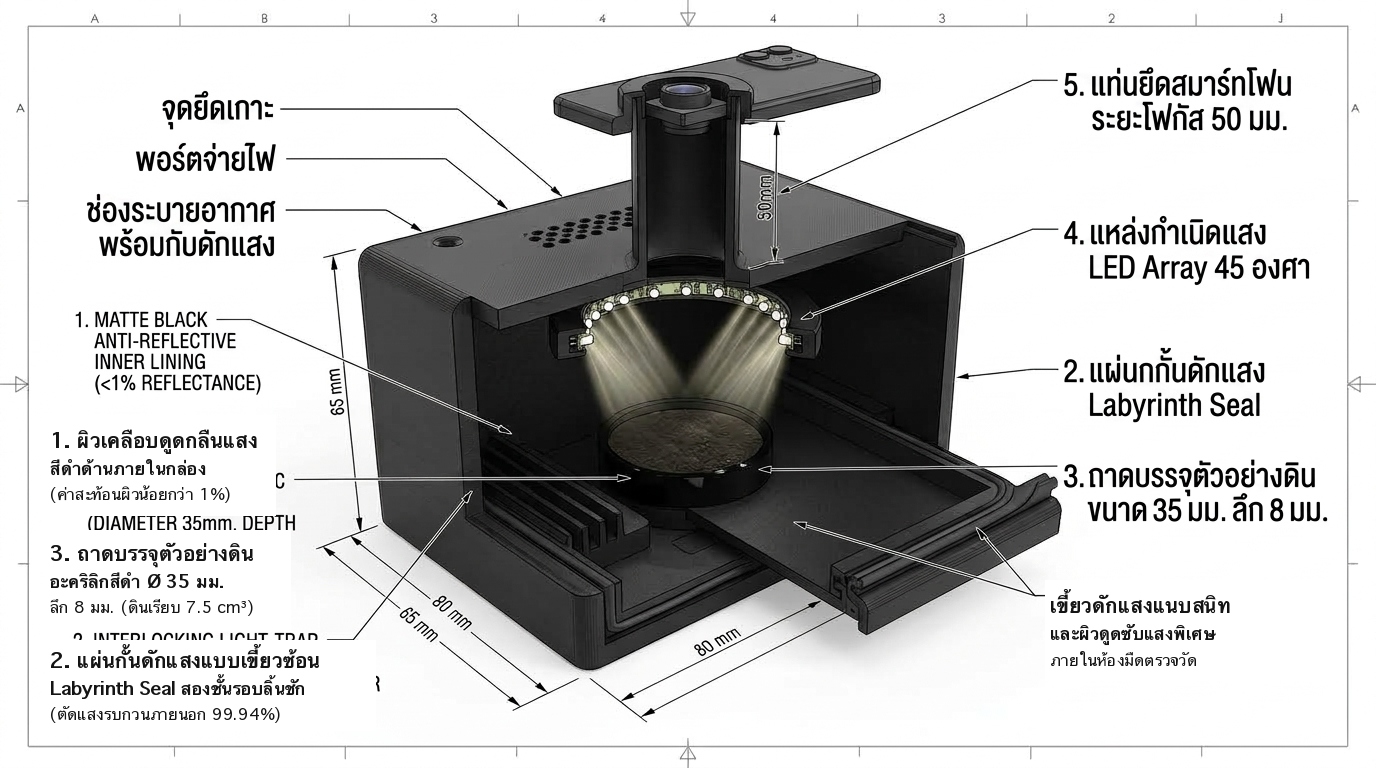
chewa/figures/fig_dark_chamber_thai_100percent.jpg
