TsanaPhysics/JC-AGRITecH-AI/leqs-workshop/assets/images/apps/app_colony_counter.png

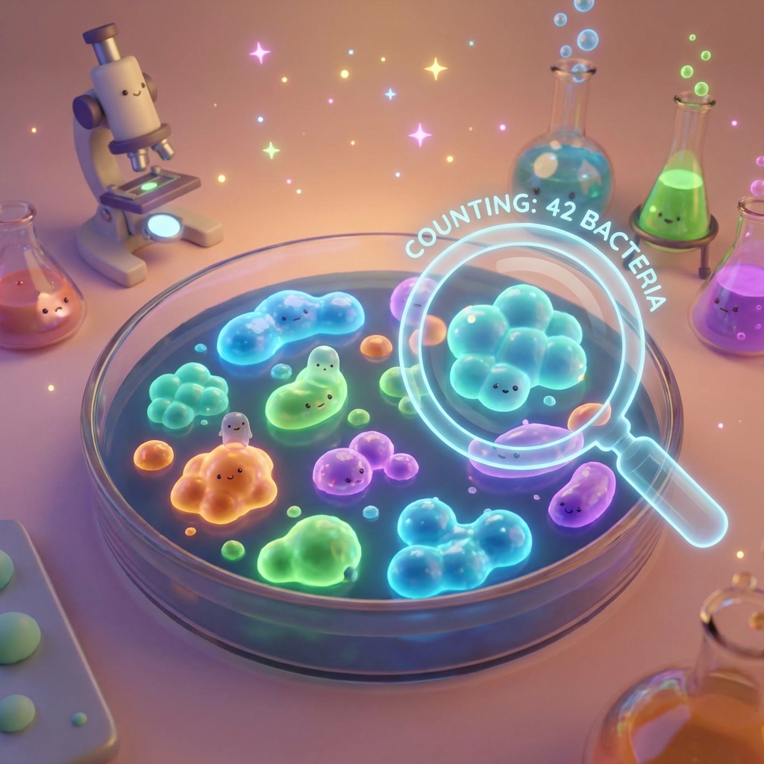
leqs-workshop/assets/images/apps/app_colony_counter.png
