TsanaPhysics/JC-AGRITecH-AI/leqs-workshop/assets/images/apps/app_soilphtxai_cropped.png

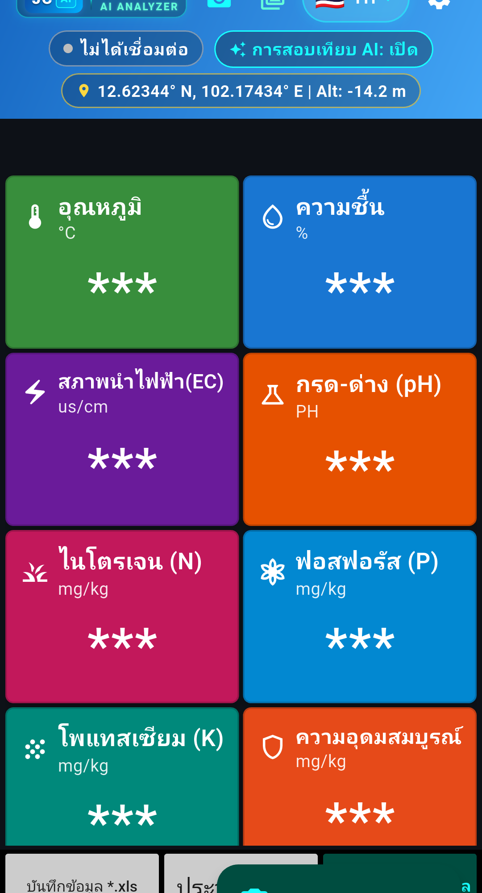
leqs-workshop/assets/images/apps/app_soilphtxai_cropped.png
