TsanaPhysics/JC-AGRITecH-AI/leqs-workshop/assets/images/atd35/02_microclimate_vpd.png

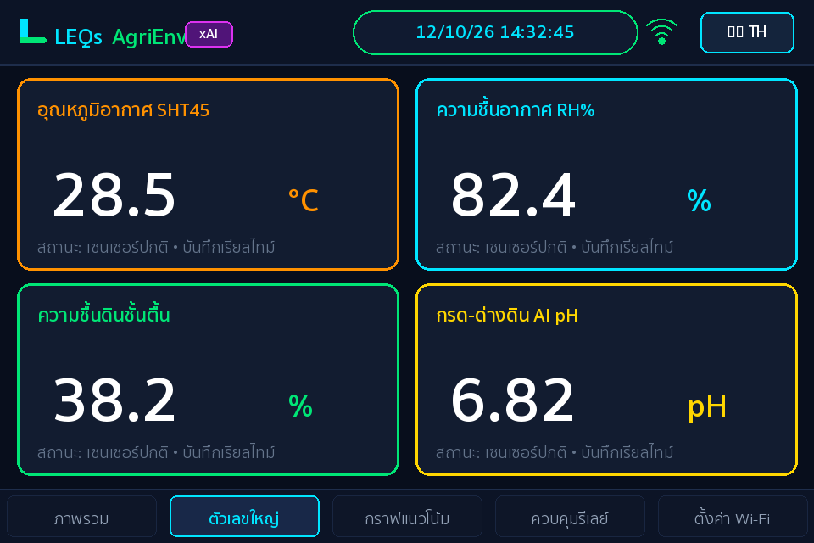
leqs-workshop/assets/images/atd35/02_microclimate_vpd.png
