TsanaPhysics/JC-AGRITecH-AI/leqs-workshop/assets/images/atd35/03_light_solar_par.png

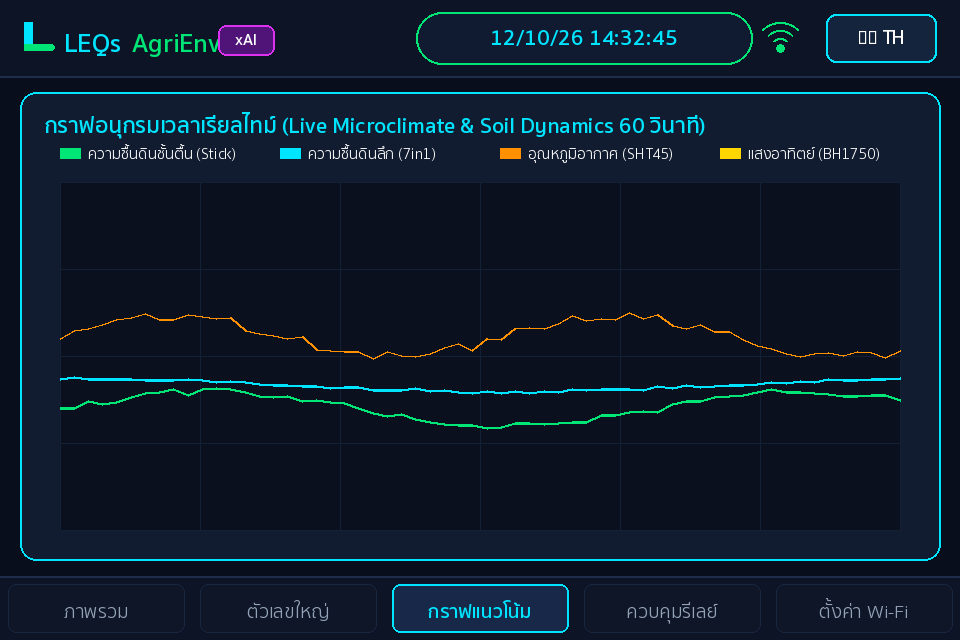
leqs-workshop/assets/images/atd35/03_light_solar_par.png
