TsanaPhysics/JC-AGRITecH-AI/leqs-workshop/assets/images/atd35/04_soil_deep_7in1.png

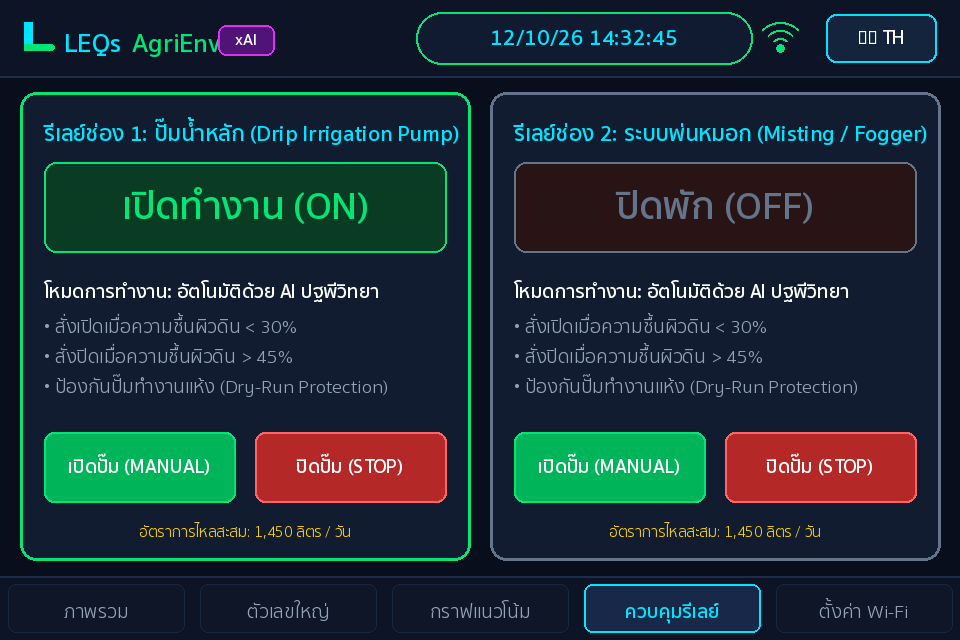
leqs-workshop/assets/images/atd35/04_soil_deep_7in1.png
