TsanaPhysics/JC-AGRITecH-AI/leqs-workshop/assets/images/atd35/05_wifi_captive_portal.png

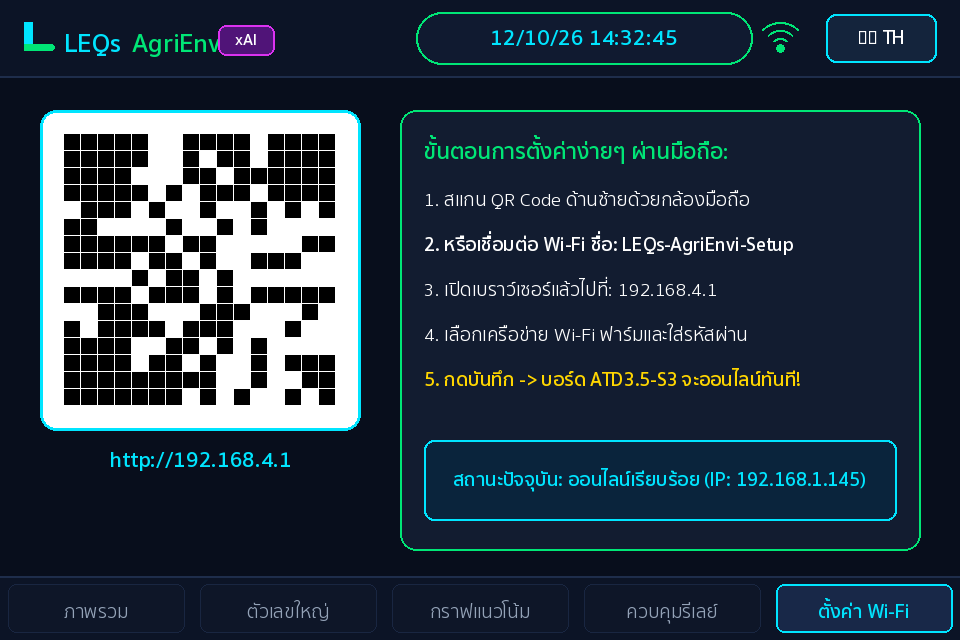
leqs-workshop/assets/images/atd35/05_wifi_captive_portal.png
