TsanaPhysics/JC-AGRITecH-AI/leqs-workshop/assets/images/atd35/06_sht45_air_vpd.png

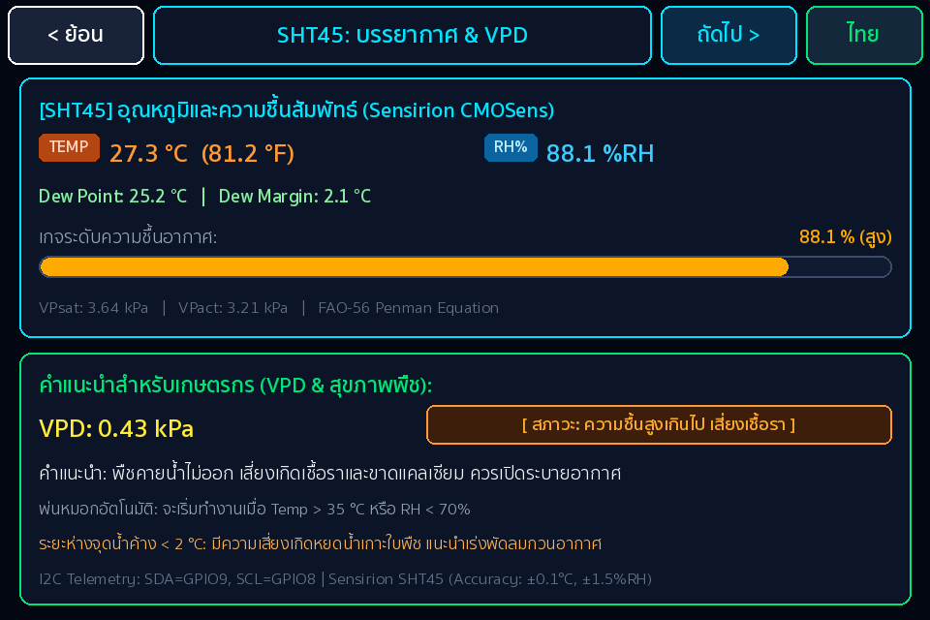
leqs-workshop/assets/images/atd35/06_sht45_air_vpd.png
