TsanaPhysics/JC-AGRITecH-AI/leqs-workshop/assets/images/atd35/07_bh1750_solar_par.png

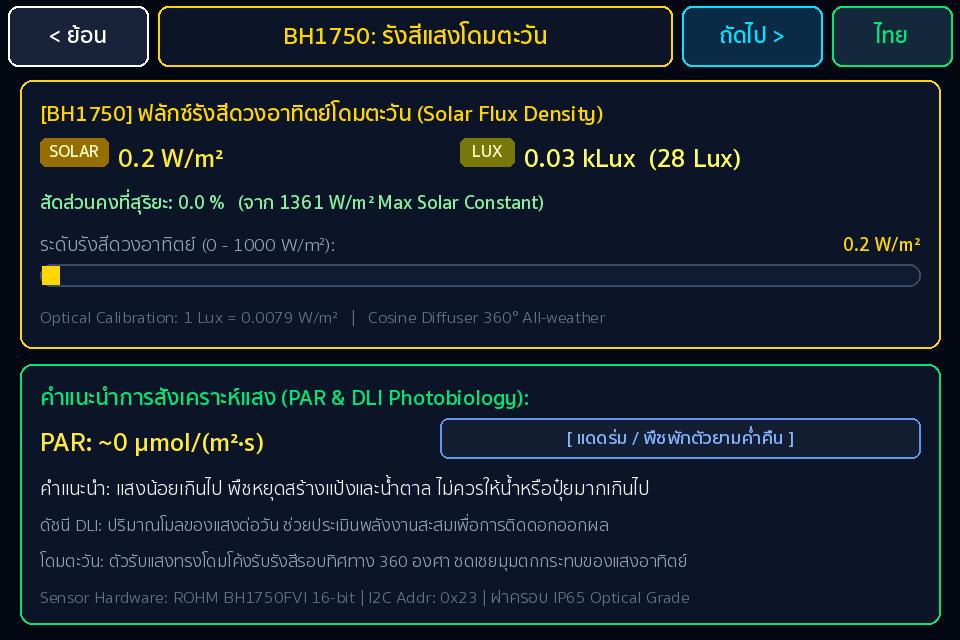
leqs-workshop/assets/images/atd35/07_bh1750_solar_par.png
