TsanaPhysics/JC-AGRITecH-AI/leqs-workshop/assets/images/atd35/08_soil_stick_surface.png

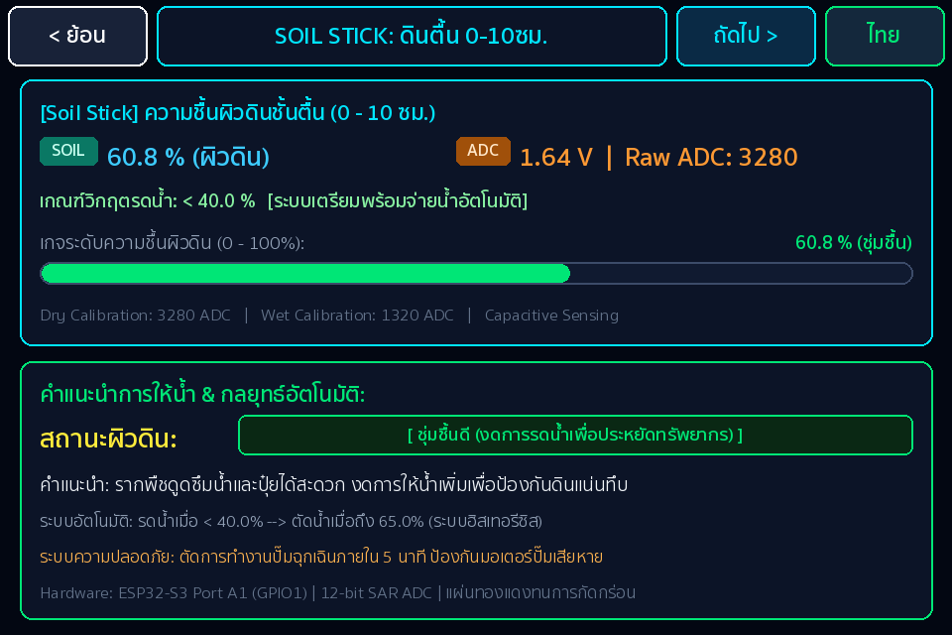
leqs-workshop/assets/images/atd35/08_soil_stick_surface.png
