TsanaPhysics/JC-AGRITecH-AI/leqs-workshop/assets/images/atd35/11_qr_portal_screen.jpg

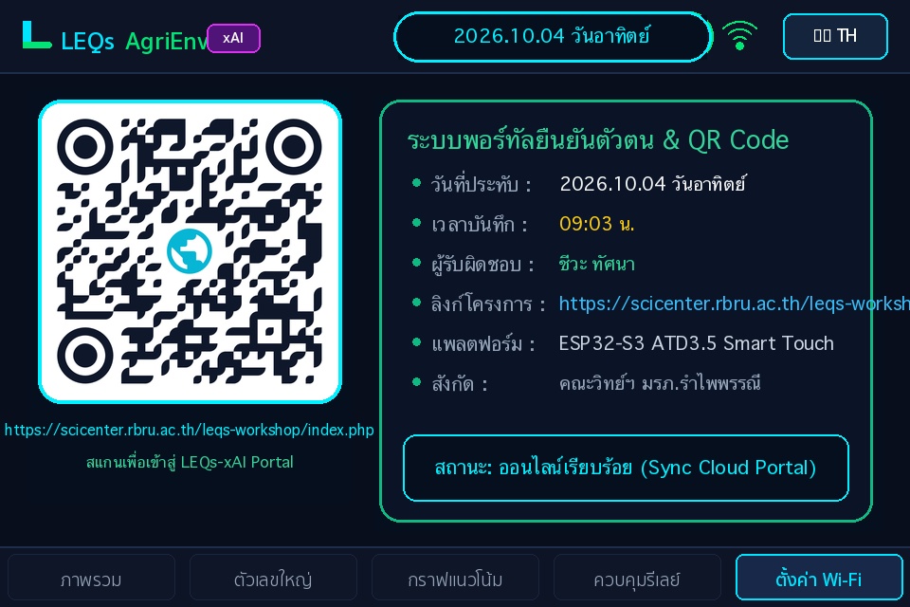
leqs-workshop/assets/images/atd35/11_qr_portal_screen.jpg
