TsanaPhysics/JC-AGRITecH-AI/leqs-workshop/assets/images/atd35/leqs_xai_hero_cover.jpg

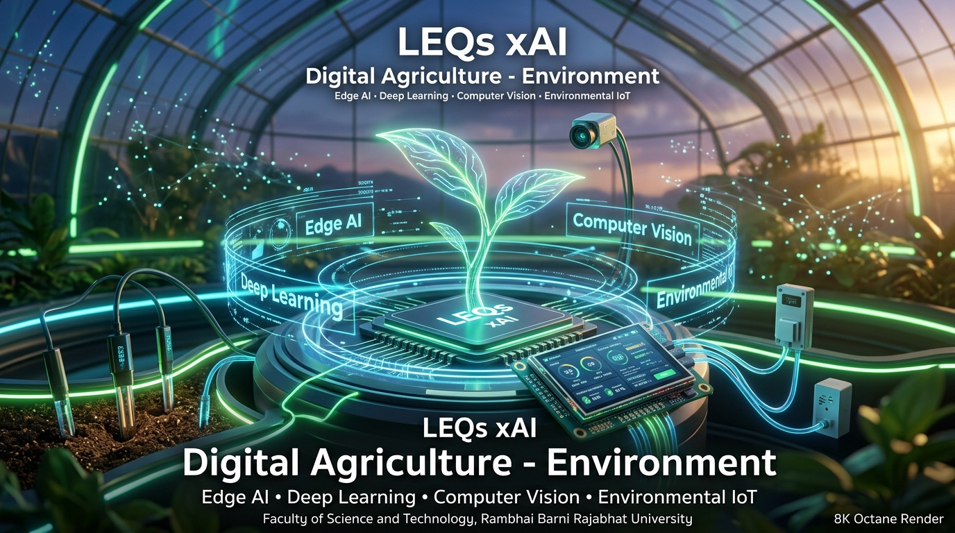
leqs-workshop/assets/images/atd35/leqs_xai_hero_cover.jpg
