TsanaPhysics/JC-AGRITecH-AI/leqs-workshop/assets/images/bio_bg.png

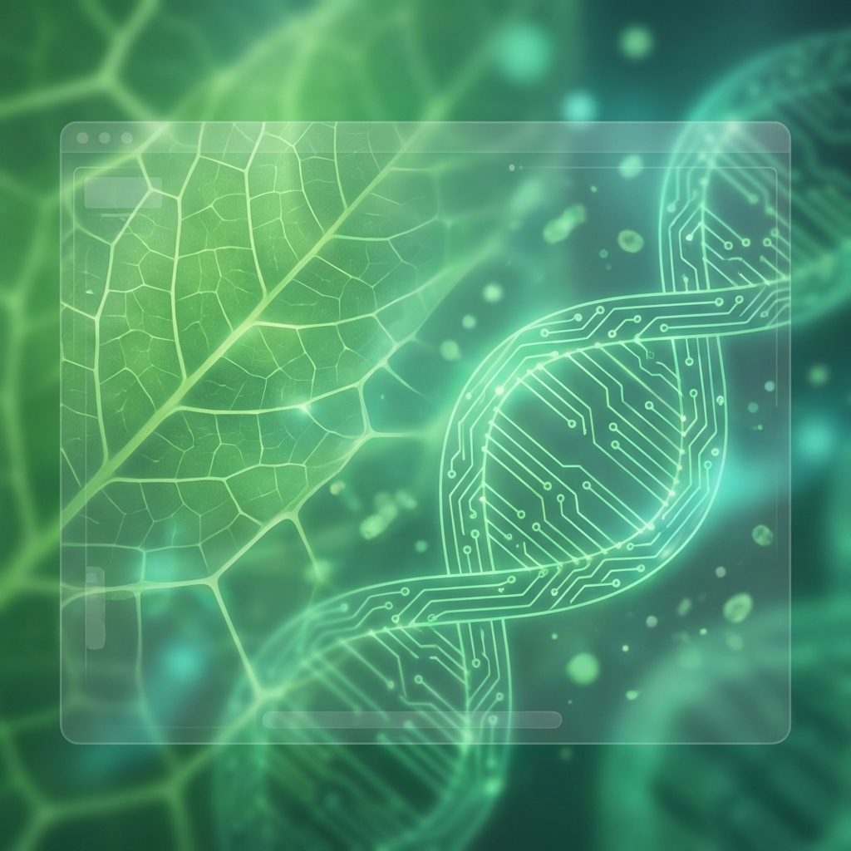
leqs-workshop/assets/images/bio_bg.png
