TsanaPhysics/JC-AGRITecH-AI/leqs-workshop/assets/images/chewa_sign.png

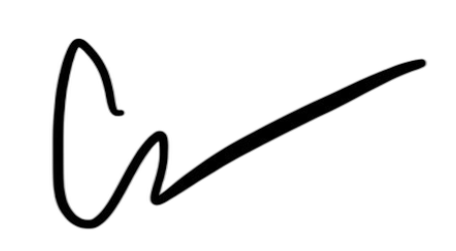
leqs-workshop/assets/images/chewa_sign.png
