TsanaPhysics/JC-AGRITecH-AI/leqs-workshop/assets/images/cv_agri_vision.jpg

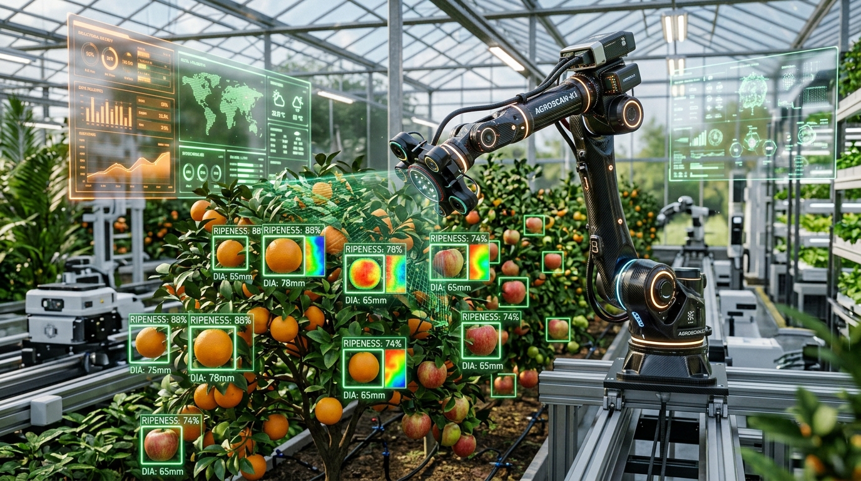
leqs-workshop/assets/images/cv_agri_vision.jpg
