TsanaPhysics/JC-AGRITecH-AI/leqs-workshop/assets/images/cv_cover_artwork.jpg

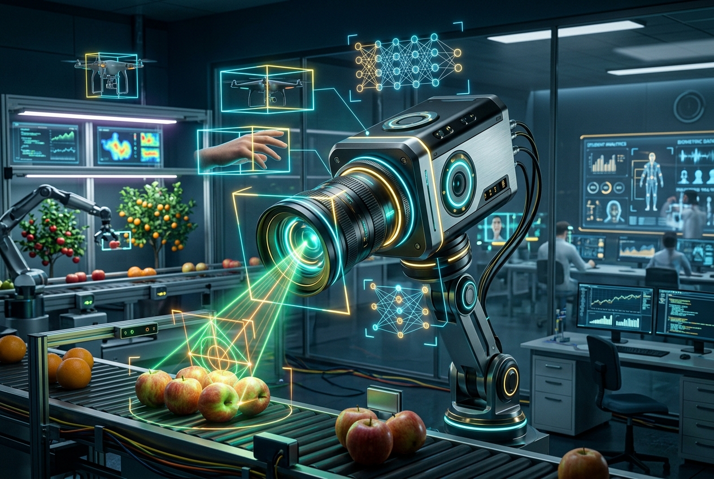
leqs-workshop/assets/images/cv_cover_artwork.jpg
