TsanaPhysics/JC-AGRITecH-AI/leqs-workshop/assets/images/pixar_mode_ai.jpg

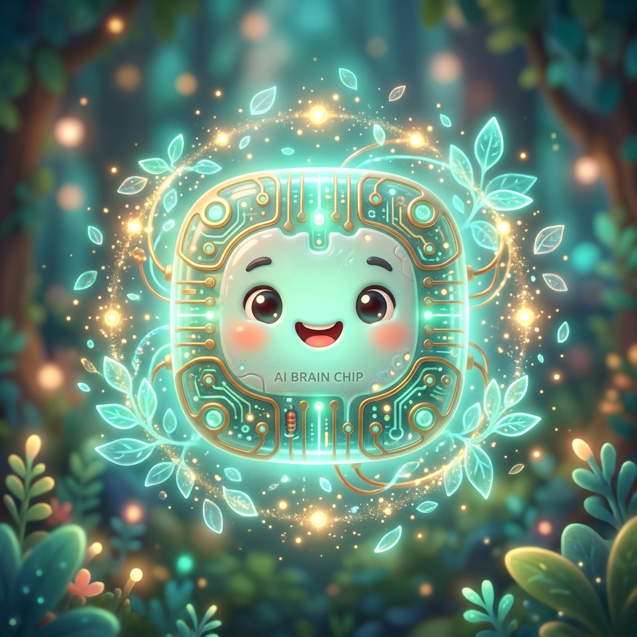
leqs-workshop/assets/images/pixar_mode_ai.jpg
