TsanaPhysics/JC-AGRITecH-AI/leqs-workshop/assets/images/pixar_mode_auto.jpg

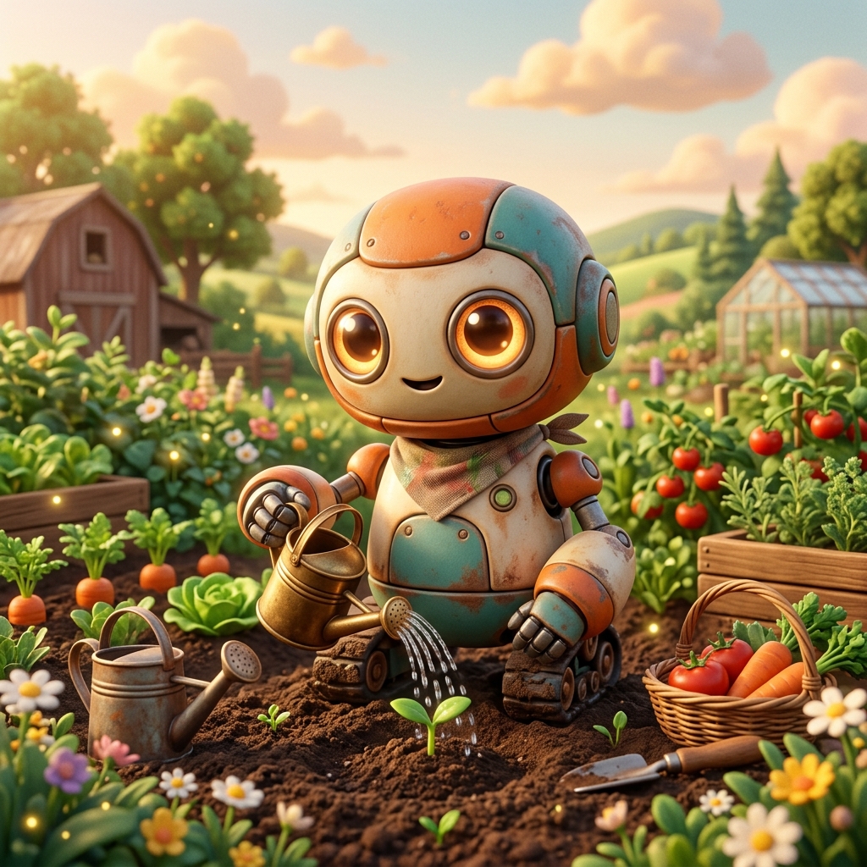
leqs-workshop/assets/images/pixar_mode_auto.jpg
