TsanaPhysics/JC-AGRITecH-AI/leqs-workshop/assets/images/pixar_npk_k.jpg

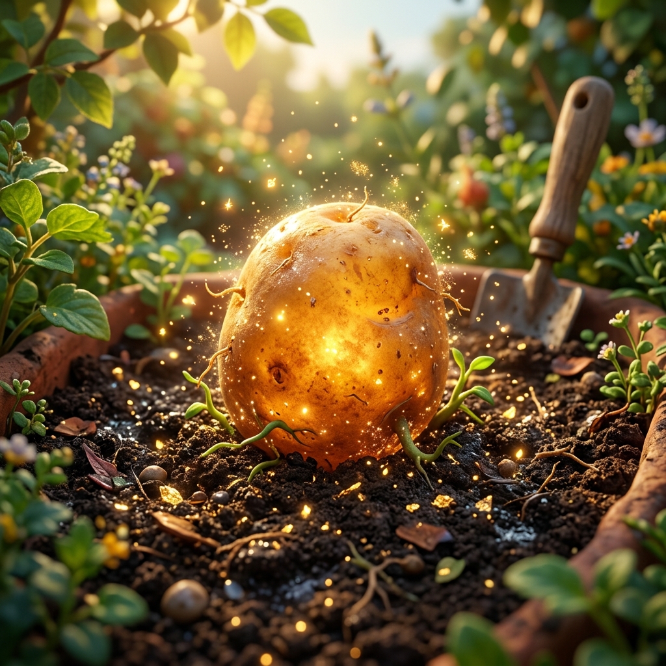
leqs-workshop/assets/images/pixar_npk_k.jpg
