TsanaPhysics/JC-AGRITecH-AI/leqs-workshop/assets/images/pixar_npk_n.jpg

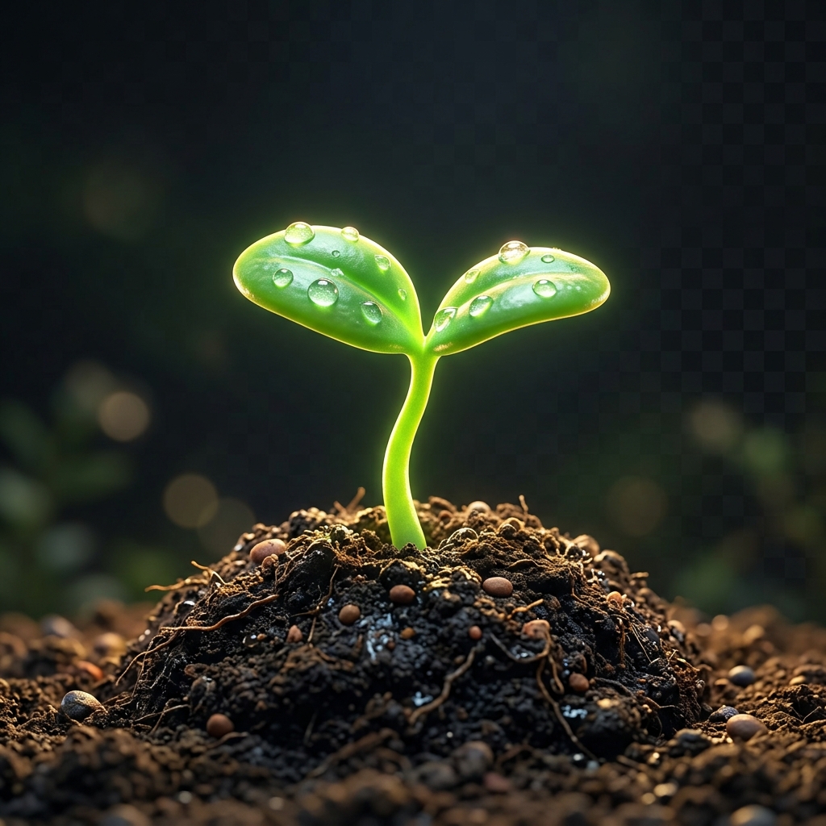
leqs-workshop/assets/images/pixar_npk_n.jpg
