TsanaPhysics/JC-AGRITecH-AI/leqs-workshop/assets/images/pixar_npk_p.jpg

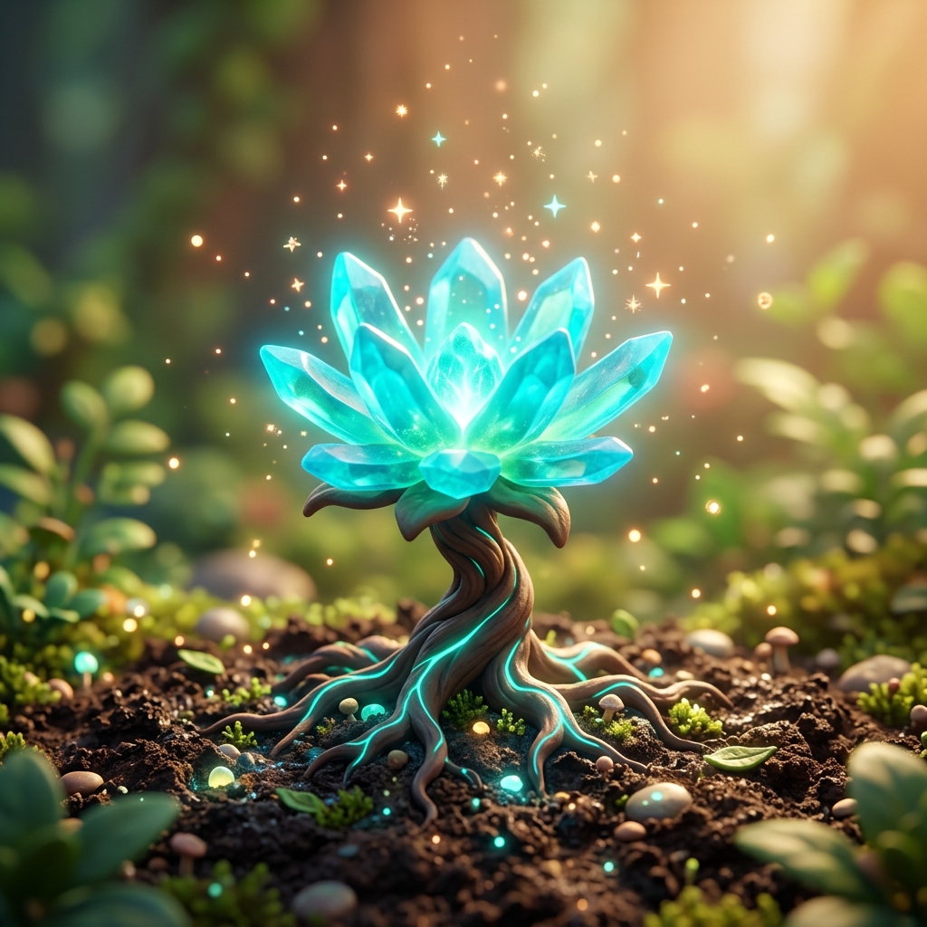
leqs-workshop/assets/images/pixar_npk_p.jpg
