TsanaPhysics/JC-AGRITecH-AI/leqs-workshop/assets/images/pixar_smart_farm_hero.jpg

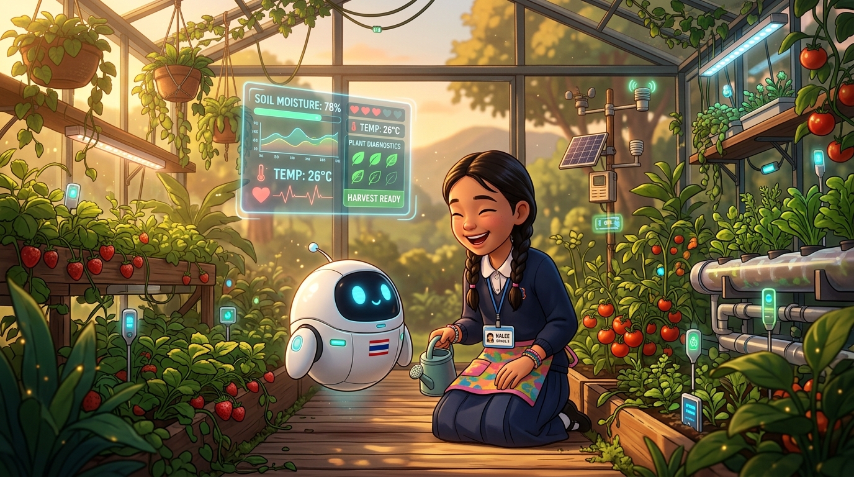
leqs-workshop/assets/images/pixar_smart_farm_hero.jpg
