TsanaPhysics/JC-AGRITecH-AI/leqs-workshop/assets/images/pixar_track_a.jpg

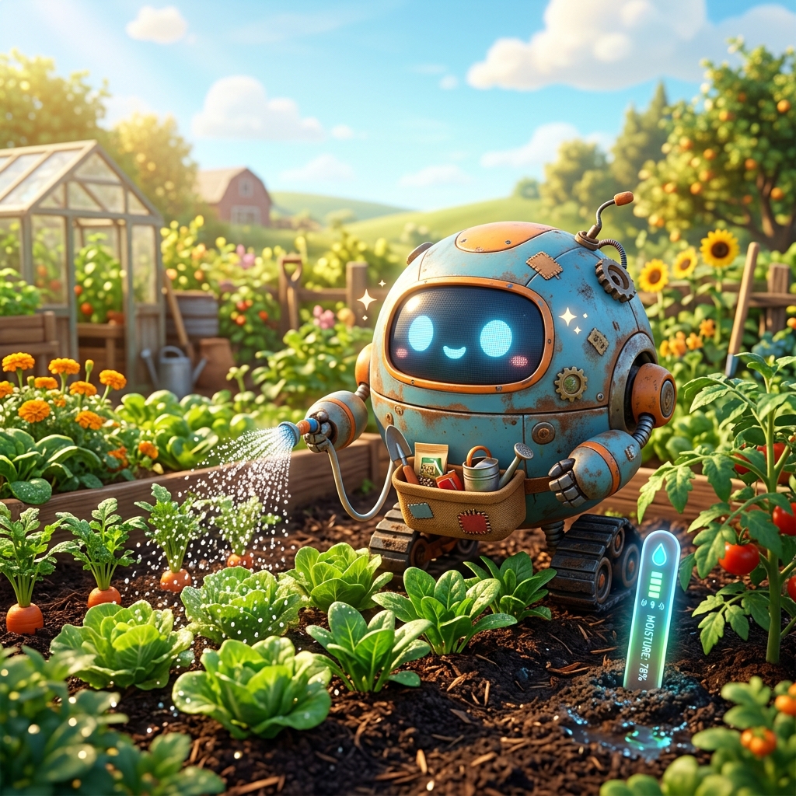
leqs-workshop/assets/images/pixar_track_a.jpg
