TsanaPhysics/JC-AGRITecH-AI/leqs-workshop/assets/images/pixar_track_b.jpg

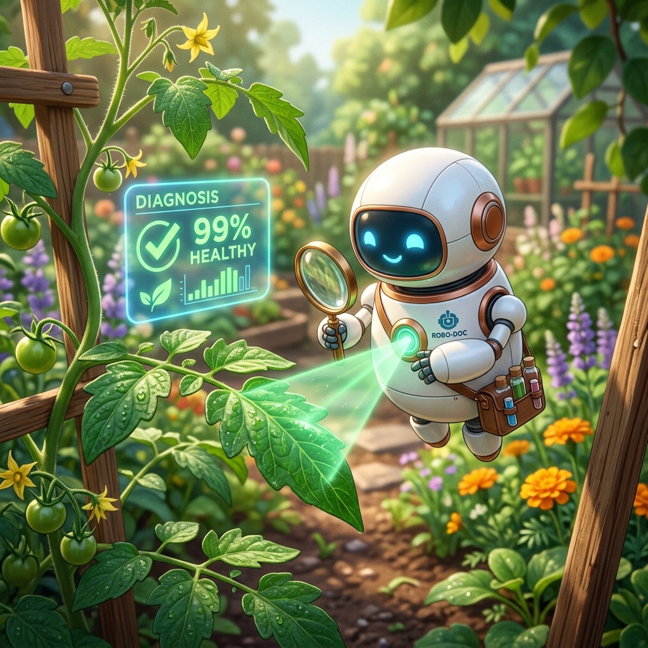
leqs-workshop/assets/images/pixar_track_b.jpg
