TsanaPhysics/JC-AGRITecH-AI/leqs-workshop/assets/images/pixar_track_c.jpg

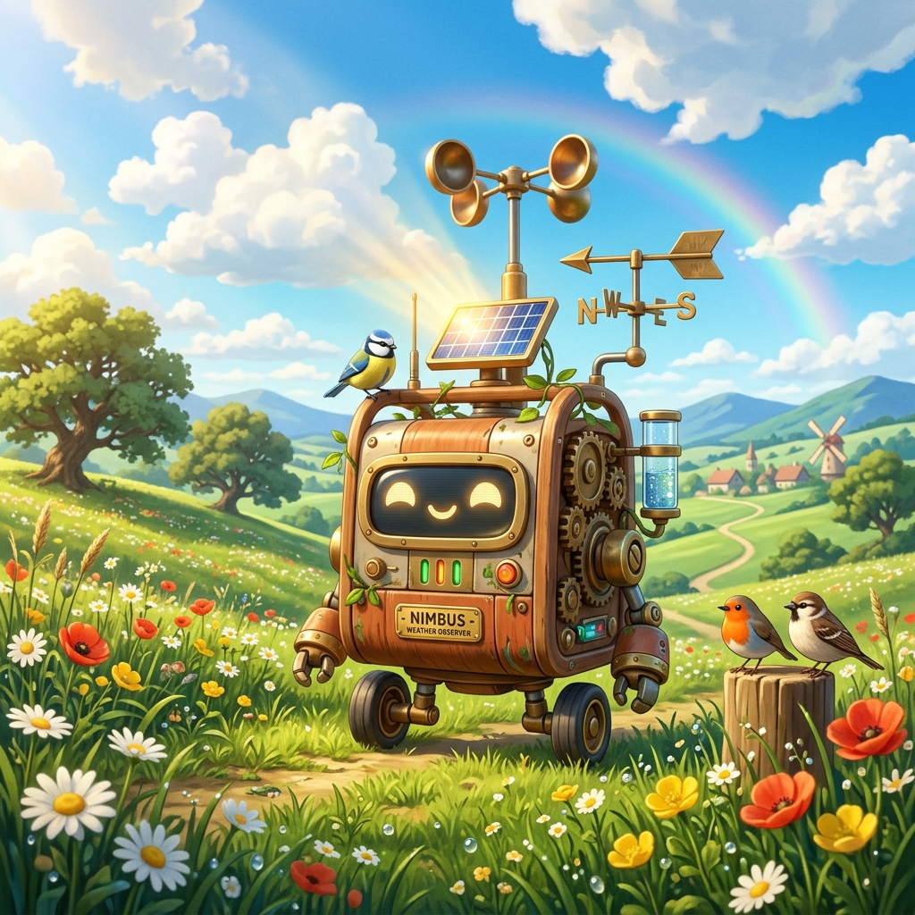
leqs-workshop/assets/images/pixar_track_c.jpg
