TsanaPhysics/JC-AGRITecH-AI/leqs-workshop/assets/images/pixar_track_d.jpg

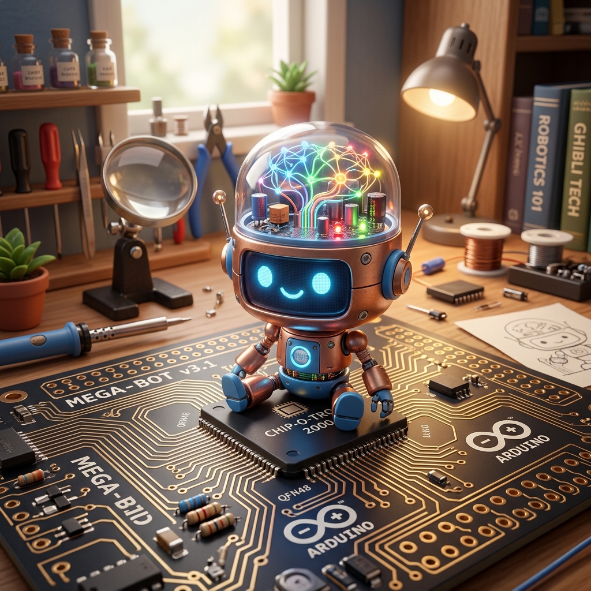
leqs-workshop/assets/images/pixar_track_d.jpg
