TsanaPhysics/JC-AGRITecH-AI/leqs-workshop/assets/images/pixar_track_e.jpg

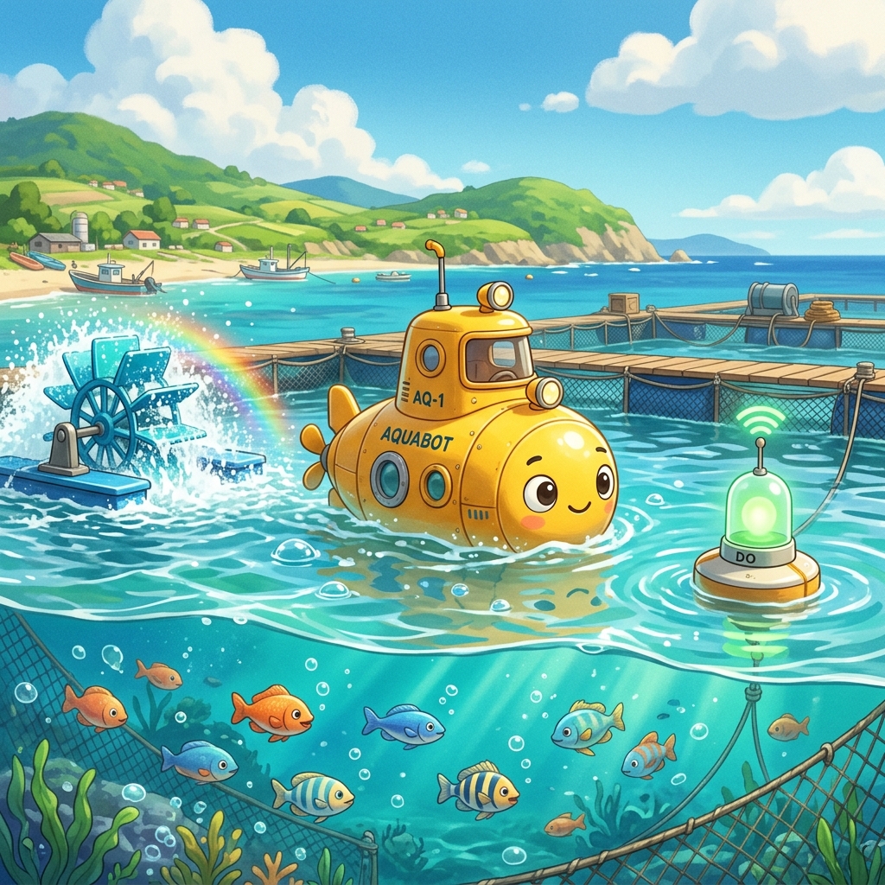
leqs-workshop/assets/images/pixar_track_e.jpg
