TsanaPhysics/JC-AGRITecH-AI/leqs-workshop/assets/images/pixar_track_f.jpg

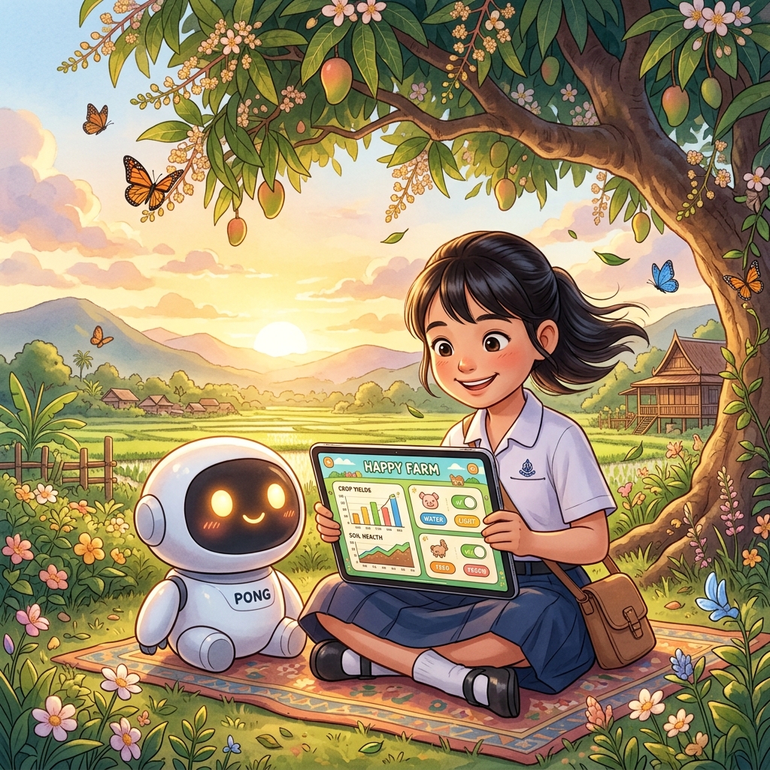
leqs-workshop/assets/images/pixar_track_f.jpg
