TsanaPhysics/JC-AGRITecH-AI/leqs-workshop/assets/images/real_mobile_app_preview.jpg

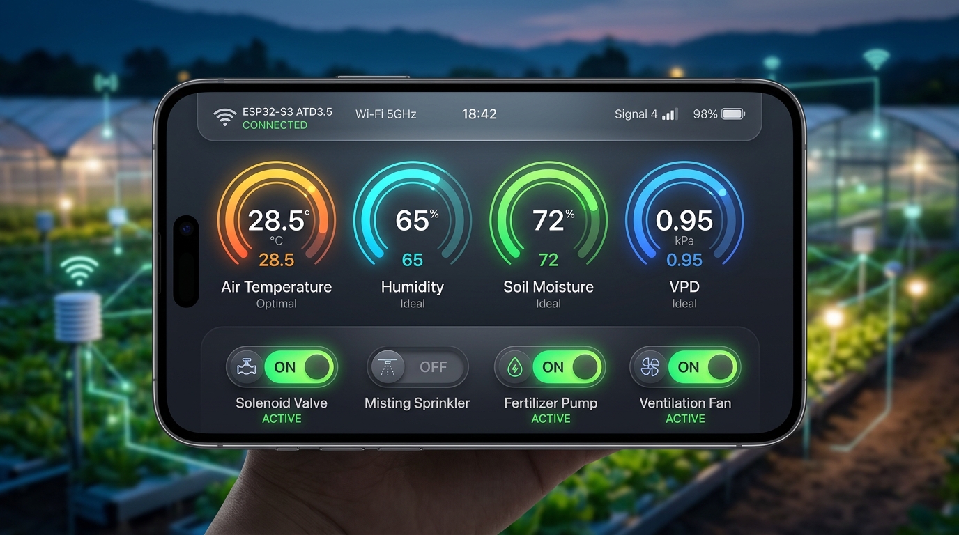
leqs-workshop/assets/images/real_mobile_app_preview.jpg
