TsanaPhysics/JC-AGRITecH-AI/leqs-workshop/assets/images/real_web_dashboard_preview.jpg

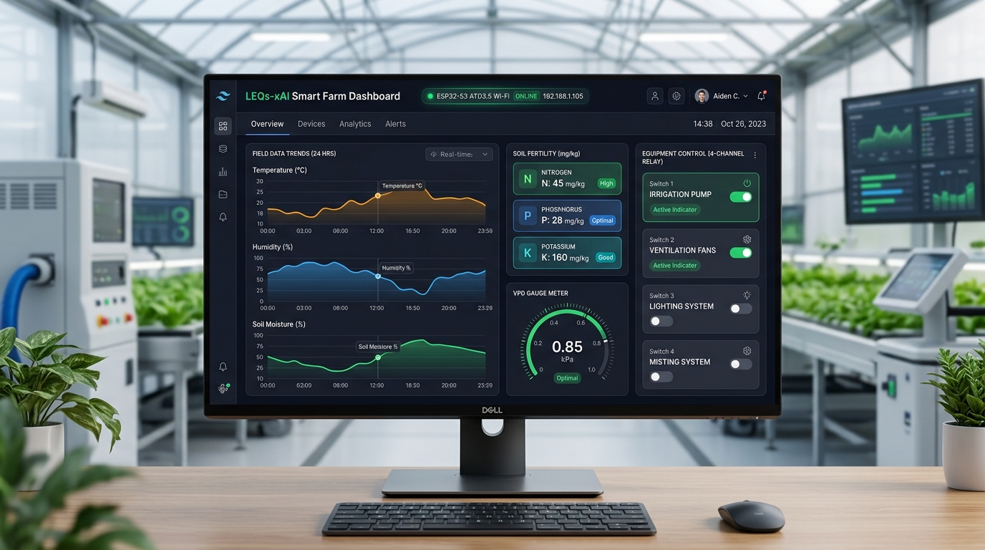
leqs-workshop/assets/images/real_web_dashboard_preview.jpg
