TsanaPhysics/JC-AGRITecH-AI/leqs-workshop/assets/images/soil_7in1_dashboard_ui.jpg

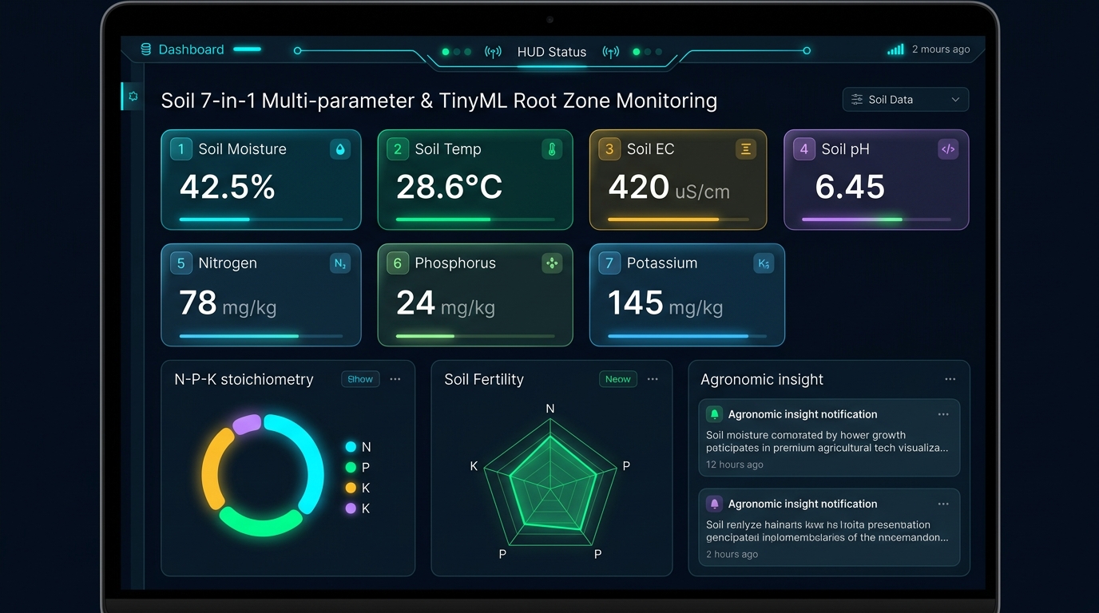
leqs-workshop/assets/images/soil_7in1_dashboard_ui.jpg
