TsanaPhysics/JC-AGRITecH-AI/leqs-workshop/assets/images/soil_kit.png

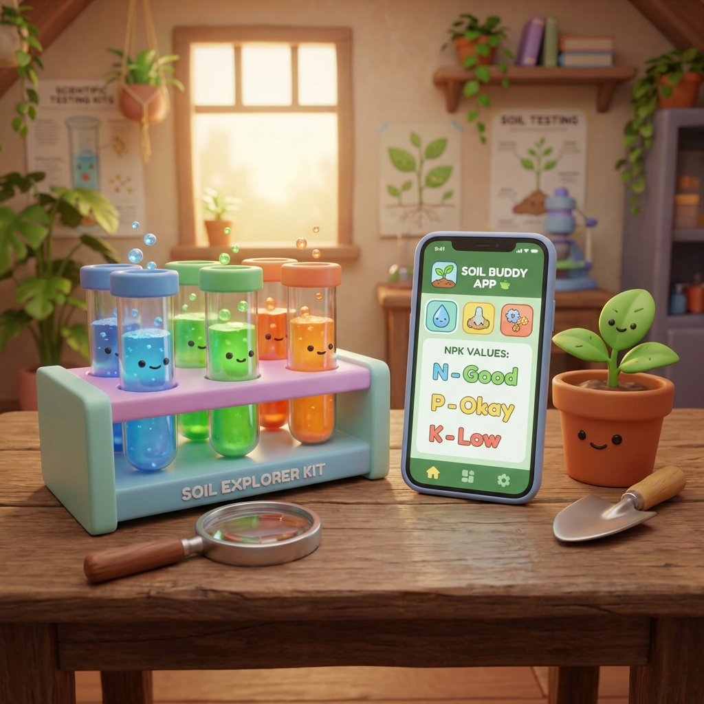
leqs-workshop/assets/images/soil_kit.png
