TsanaPhysics/JC-AGRITecH-AI/leqs-workshop/assets/images/trainers/speaker_attaporn.png

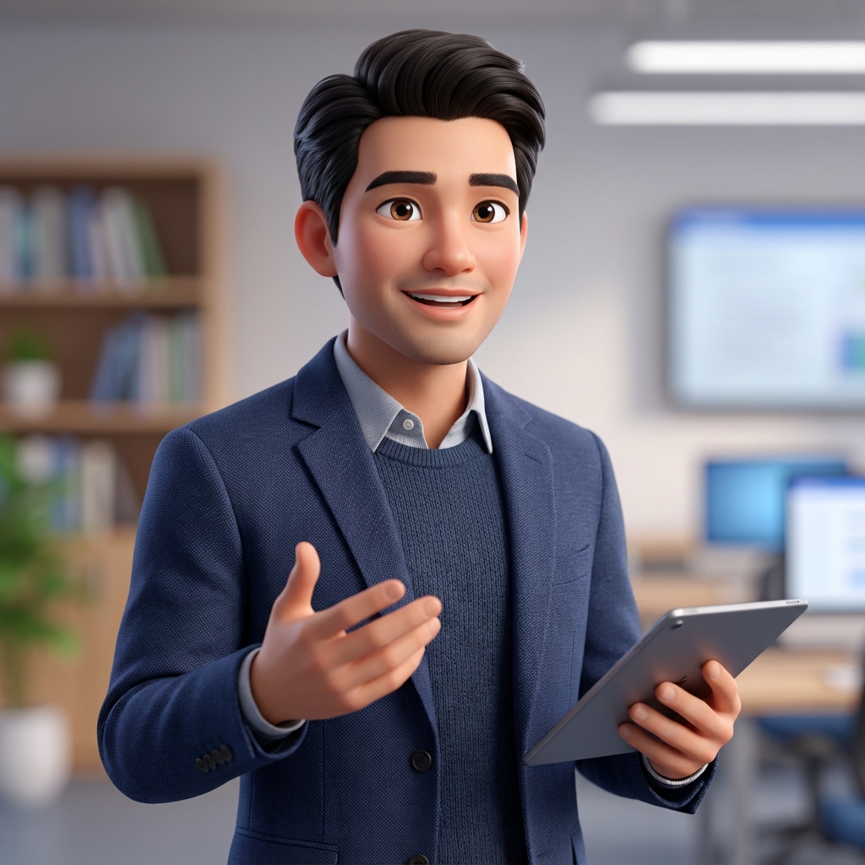
leqs-workshop/assets/images/trainers/speaker_attaporn.png
