TsanaPhysics/JC-AGRITecH-AI/leqs-workshop/assets/images/trainers/speaker_chewa.png

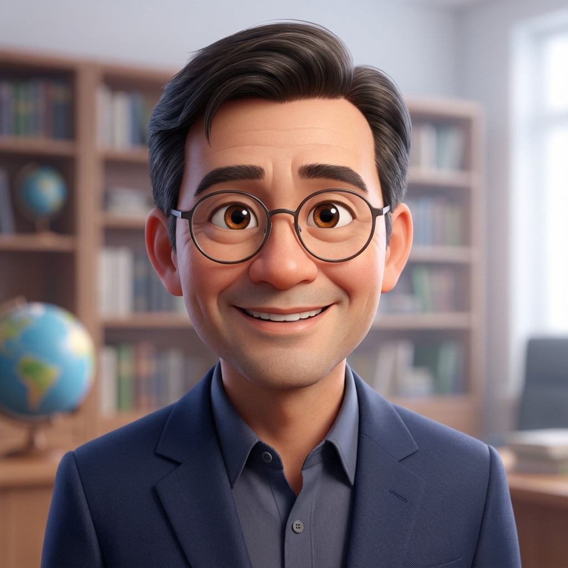
leqs-workshop/assets/images/trainers/speaker_chewa.png
