TsanaPhysics/JC-AGRITecH-AI/leqs-workshop/assets/images/trainers/speaker_jiraporn.png

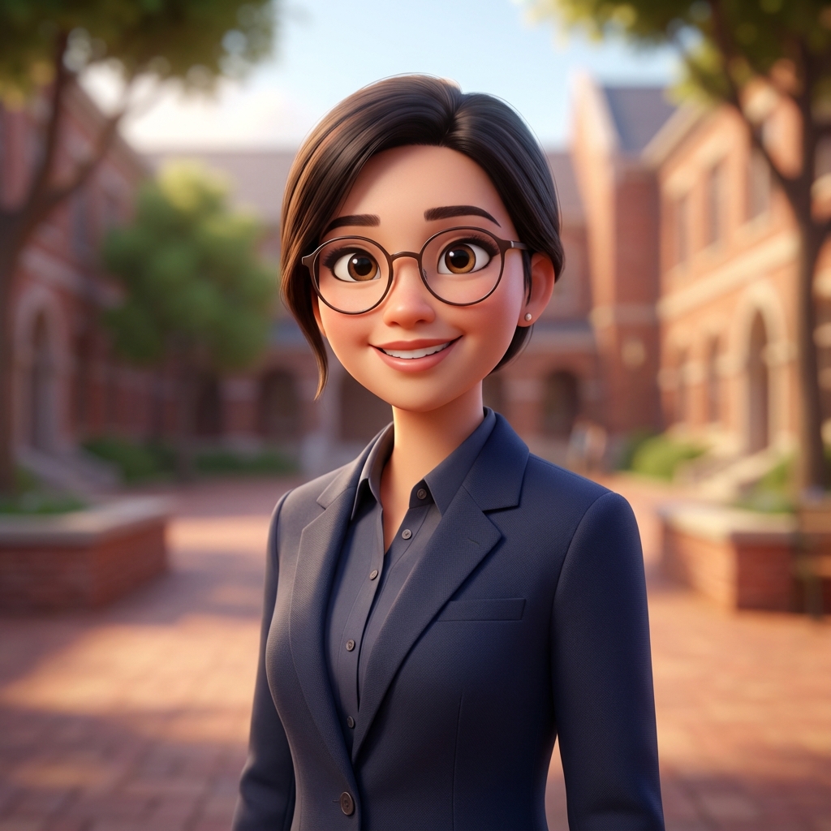
leqs-workshop/assets/images/trainers/speaker_jiraporn.png
