TsanaPhysics/JC-AGRITecH-AI/leqs-workshop/assets/images/trainers/speaker_namonruk.png

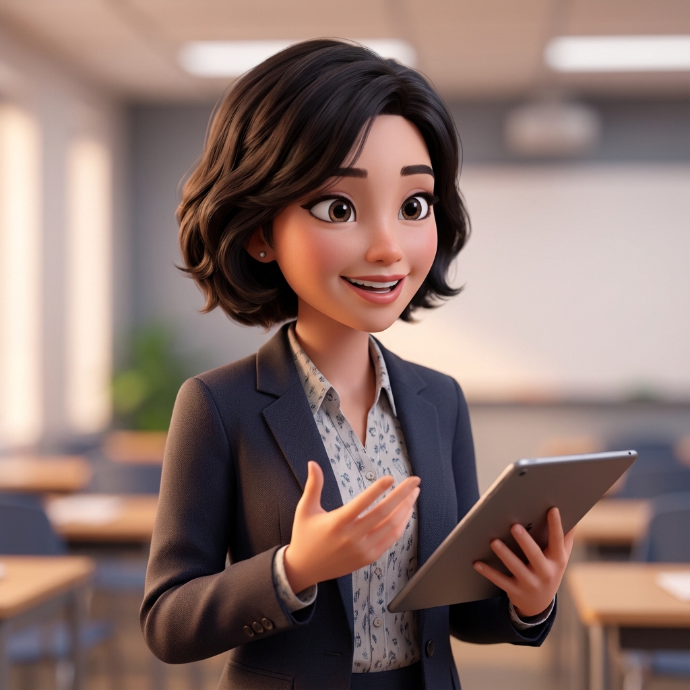
leqs-workshop/assets/images/trainers/speaker_namonruk.png
