TsanaPhysics/JC-AGRITecH-AI/leqs-workshop/assets/images/trainers/speaker_nantaporn.png

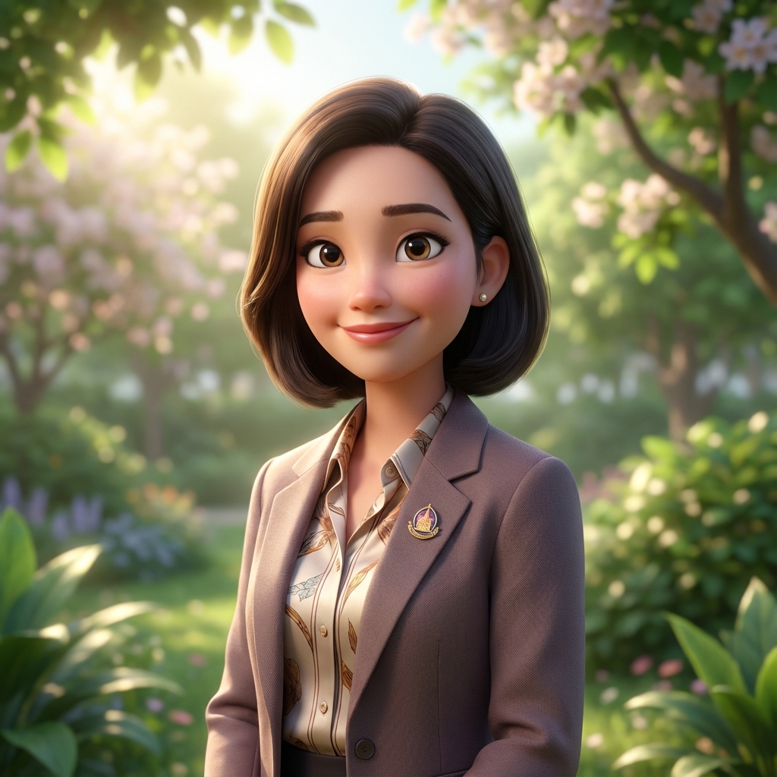
leqs-workshop/assets/images/trainers/speaker_nantaporn.png
