TsanaPhysics/JC-AGRITecH-AI/leqs-workshop/assets/images/trainers/speaker_niphat.png

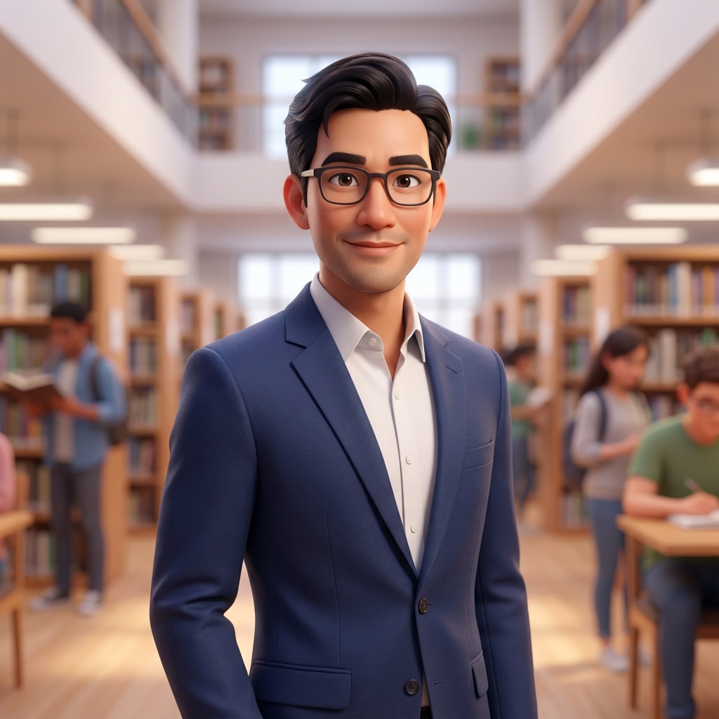
leqs-workshop/assets/images/trainers/speaker_niphat.png
