TsanaPhysics/JC-AGRITecH-AI/leqs-workshop/assets/images/vichaladda_sign.png

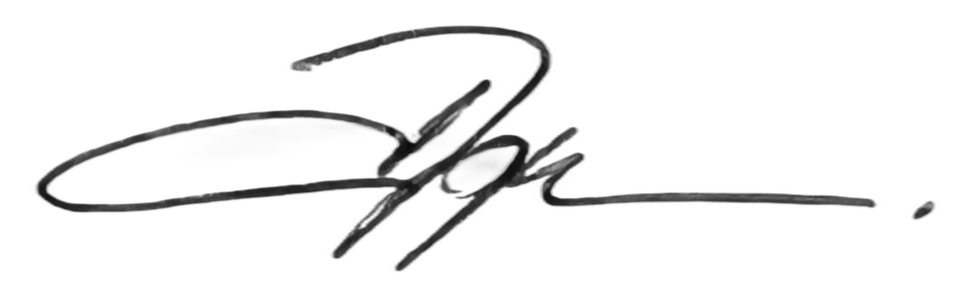
leqs-workshop/assets/images/vichaladda_sign.png
