TsanaPhysics/JC-AGRITecH-AI/oxygen.jpeg

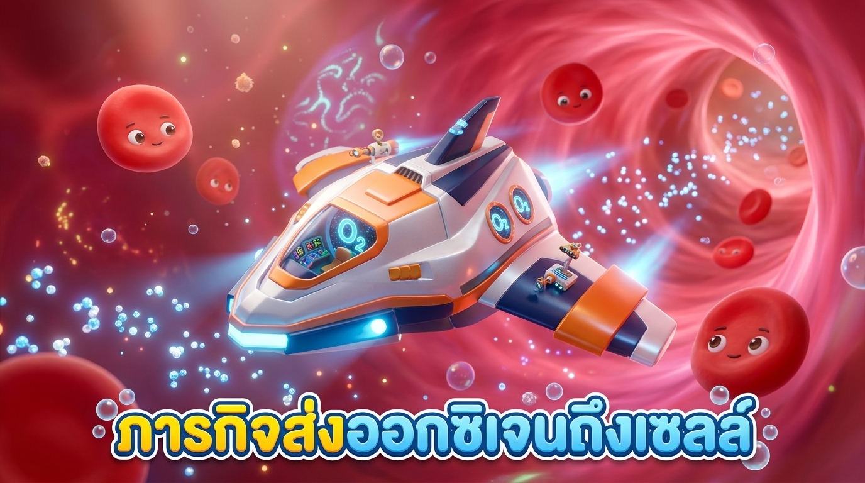
oxygen.jpeg
