TsanaPhysics/JC-AGRITecH-AI/plantheath/assets/images/durian_nutrition_dual_art.jpg

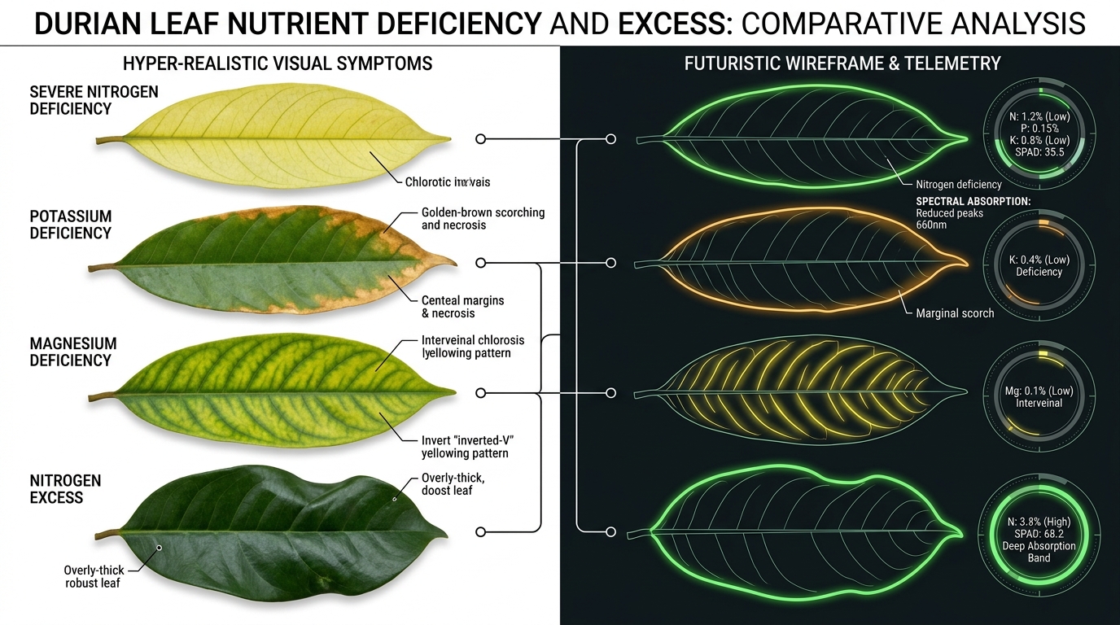
plantheath/assets/images/durian_nutrition_dual_art.jpg
