TsanaPhysics/JC-AGRITecH-AI/plantheath/handysense_dashboard.png

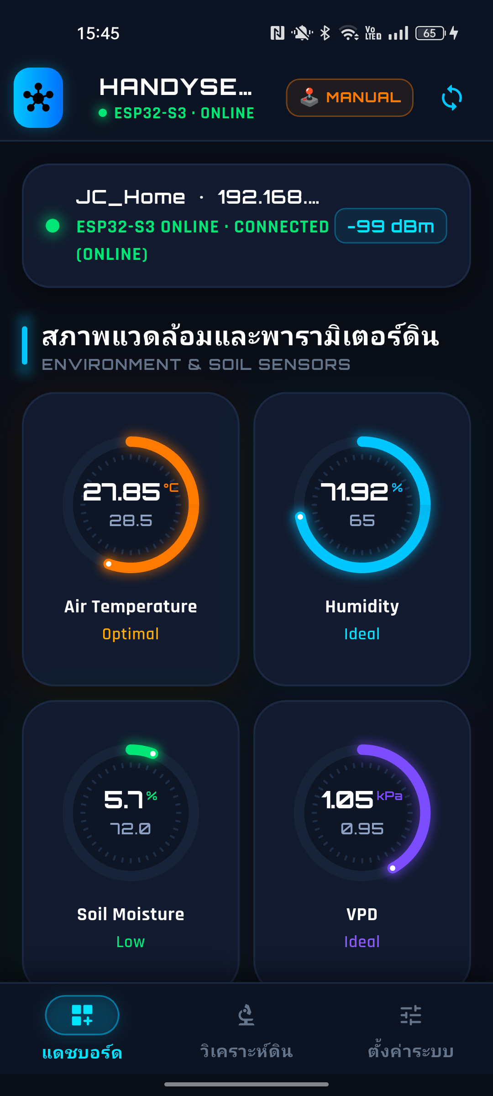
plantheath/handysense_dashboard.png
