TsanaPhysics/JC-AGRITecH-AI/plantheath/handysense_screen.png

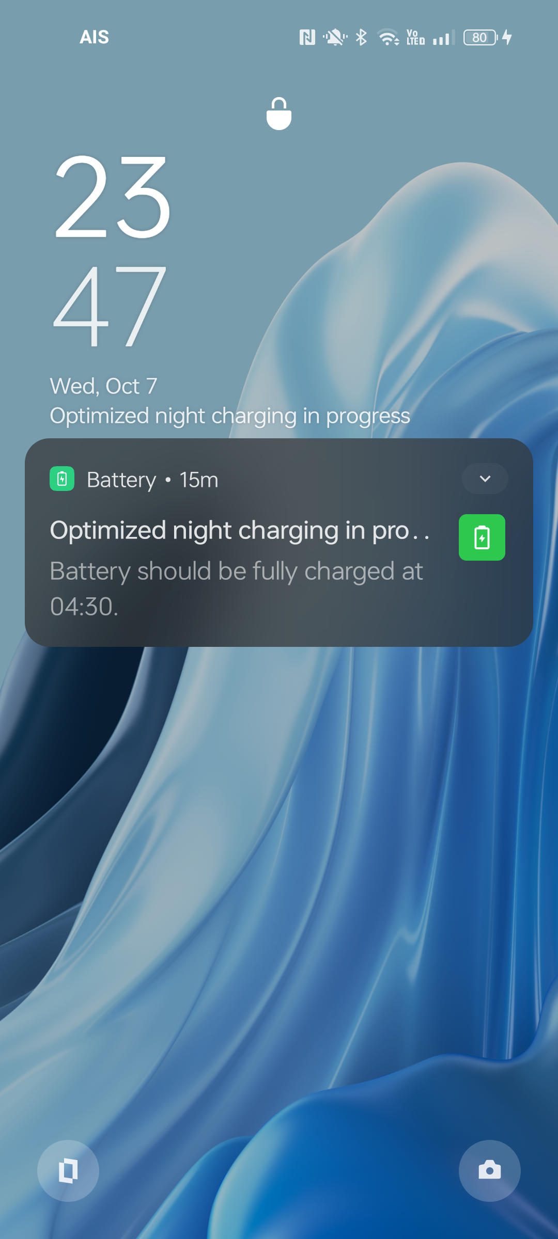
plantheath/handysense_screen.png
