TsanaPhysics/JC-AGRITecH-AI/plantheath/leqsxai_screen.png

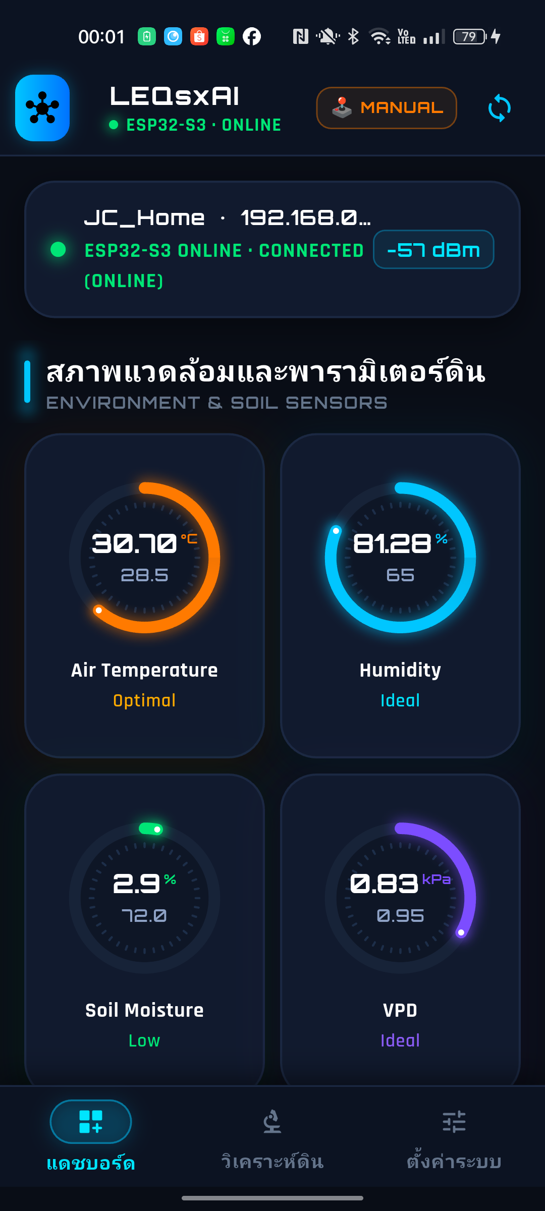
plantheath/leqsxai_screen.png
