TsanaPhysics/JC-AGRITecH-AI/plantheath/leqsxai_screen_cards.png

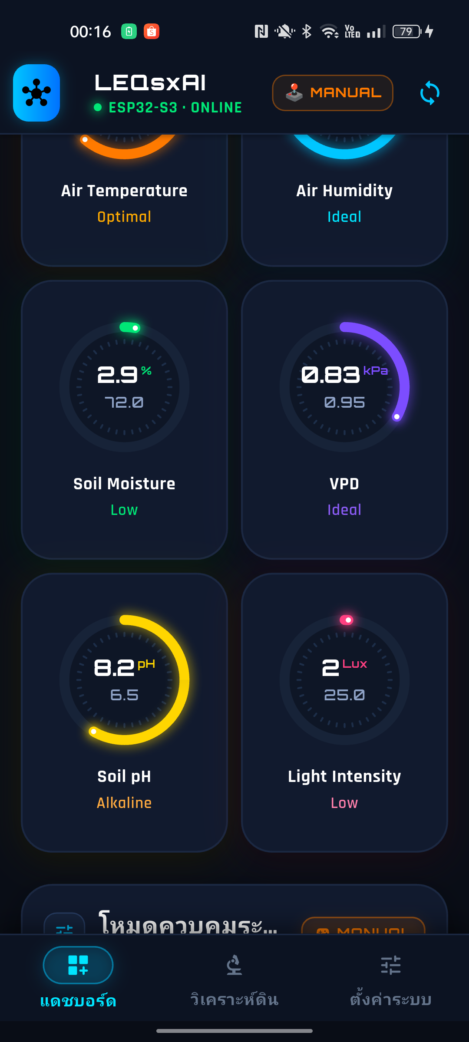
plantheath/leqsxai_screen_cards.png
