TsanaPhysics/JC-AGRITecH-AI/plantheath/leqsxai_screen_top.png

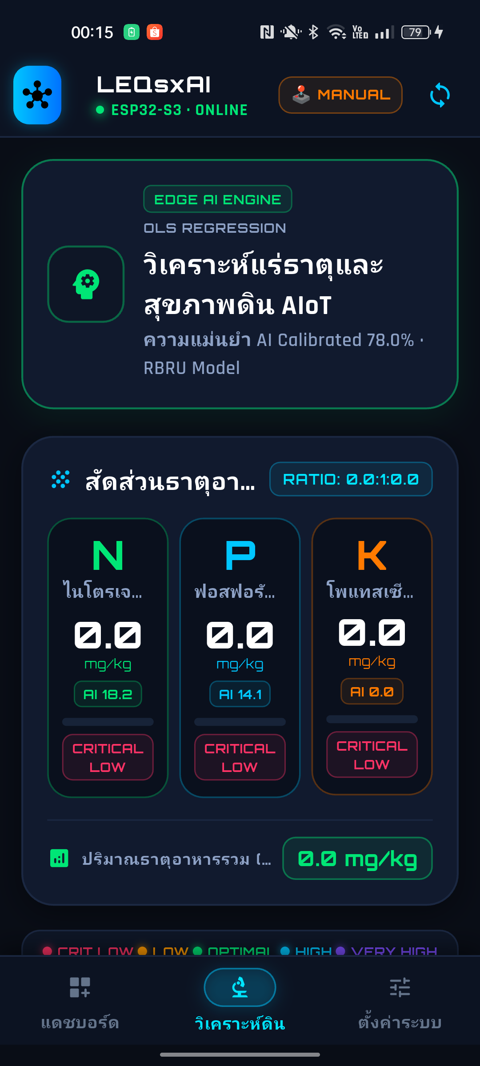
plantheath/leqsxai_screen_top.png
