TsanaPhysics/JC-AGRITecH-AI/plantheath/leqsxai_screen_updated.png

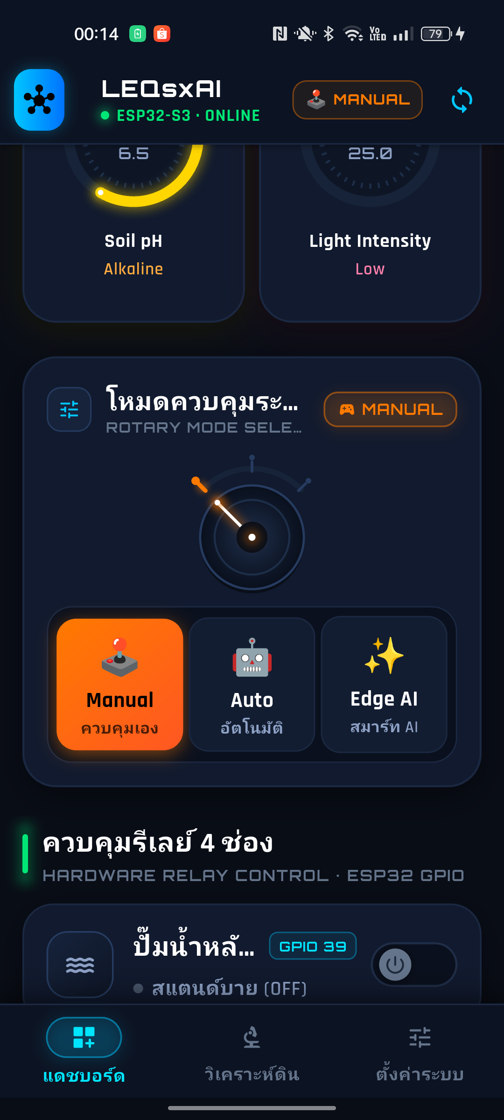
plantheath/leqsxai_screen_updated.png
