TsanaPhysics/JC-AGRITecH-AI/plantheath/tab2_soil.png

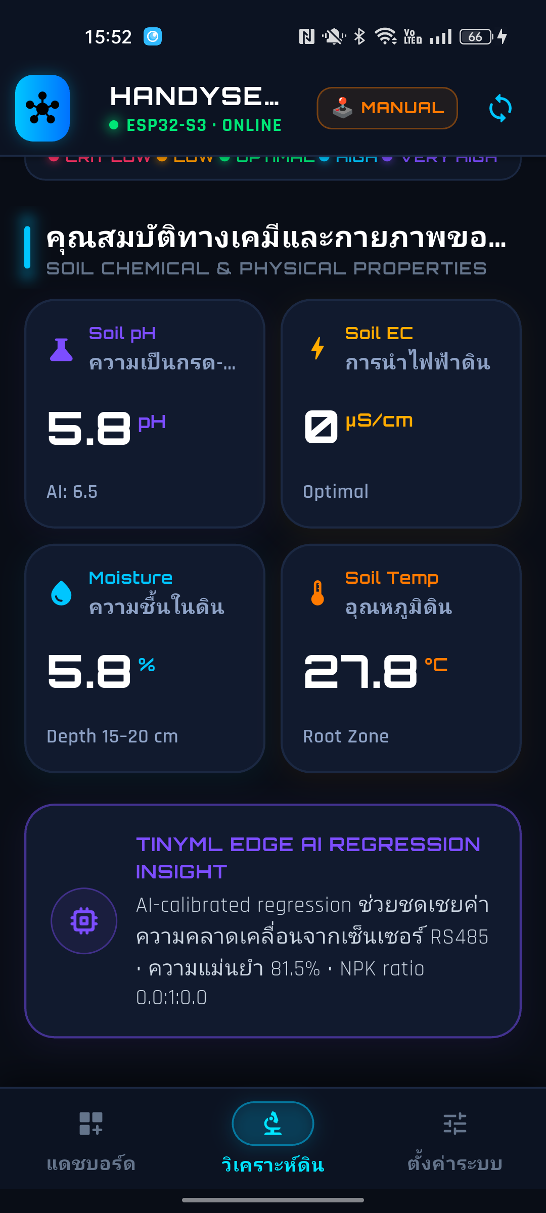
plantheath/tab2_soil.png
