TsanaPhysics/JC-AGRITecH-AI/plantheath/tab3_settings.png

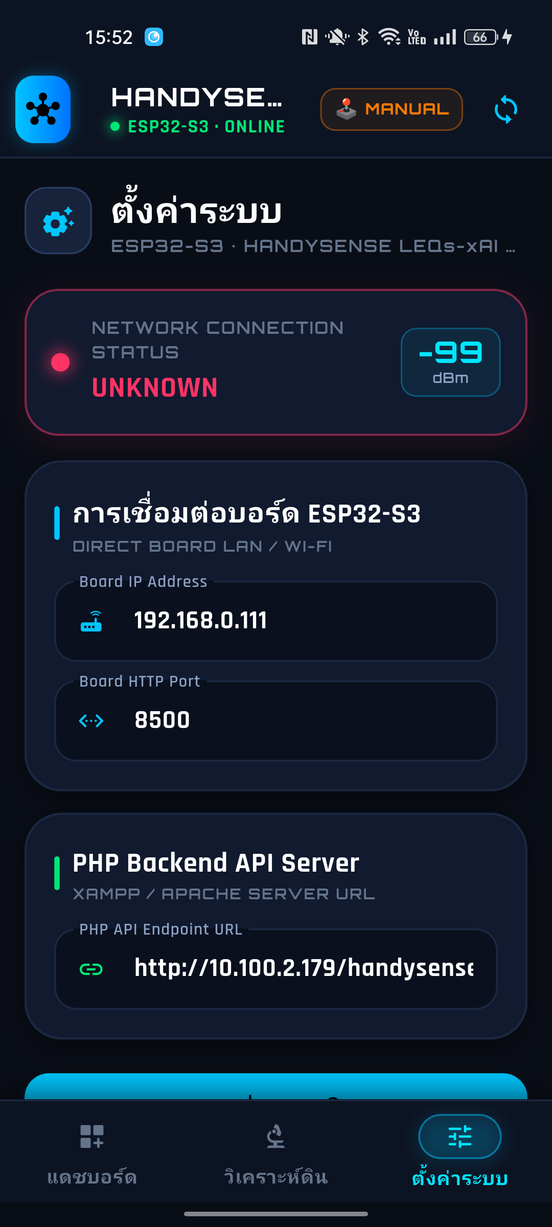
plantheath/tab3_settings.png
