TsanaPhysics/JC-AGRITecH-AI/thanapat_research/project_dossier/MATERIALS_AND_EXECUTION_PLAN.md

# สรุปรายการวัสดุอุปกรณ์และแผนการดำเนินงานวิจัยให้บรรลุวัตถุประสงค์

**โครงการวิจัย** การพัฒนาชุดทดสอบค่าความเป็นกรด-ด่างของดินแบบพกพาภาคสนามความแม่นยำสูงด้วยการชดเชยความคลาดเคลื่อนโดยปัญญาประดิษฐ์  
**คณะผู้วิจัย** อาจารย์ธนพัฒน์ ถิระวุฒิ, ผศ.ดร.ชีวะ ทัศนา, ผศ.ดร.นันทพร มูลรังษี, รศ.ดร.นิภัทร เปี่ยมอรุณ  
**แหล่งทุน** กองทุนวิจัย มหาวิทยาลัยราชภัฏรำไพพรรณี ประจำปีงบประมาณ พ.ศ. 2569 (งบประมาณรวม 75,000 บาท)  

---

## 1. สรุปรายการวัสดุอุปกรณ์และเครื่องมือวิจัย (Materials & Equipment List)

รายการวัสดุอุปกรณ์ได้รับการจัดสรรตามหมวดหมู่งบประมาณและข้อกำหนดระเบียบวิธีวิจัย ดังนี้

### 1.1 หมวดวัสดุไฟฟ้า อิเล็กทรอนิกส์ และสมองกลฝังตัว (26,500 บาท)
1. **แผงวงจรและหัววัดค่าความเป็นกรด-ด่าง (Soil pH Sensor Modules)** จำนวน 5 ชุด (ชุดละ 2,000 บาท รวม 10,000 บาท)  
   ประกอบด้วยหัววัดโพเทนชิออเมตริกพร้อมเยื่อแก้วทนทานภาคสนาม (Glass Electrode) และวงจรแปลงสัญญาณแอนะล็อกความต้านทานนำเข้าสูง (High Input Impedance Pre-amplifier)
2. **แผงวงจรและเซนเซอร์วัดอุณหภูมิความแม่นยำสูง (Temperature Sensor Module)** จำนวน 1 ชุด (3,000 บาท)  
   ใช้โพรบวัดอุณหภูมิสแตนเลสสตีลกันน้ำชนิดดิจิทัล DS18B20 หรือ RTD PT100 เพื่ออ่านค่าอุณหภูมิสารละลายและดินแบบเรียลไทม์
3. **ไมโครคอนโทรลเลอร์ประมวลผลหลัก (Microcontroller Units)** จำนวน 1 ชุด (5,000 บาท)  
   ใช้บอร์ดไมโครคอนโทรลเลอร์ ESP32-S3 Dual-Core Xtensa LX7 รองรับคำสั่งเวกเตอร์สำหรับ TinyML พร้อมโมดูลแปลงสัญญาณแอนะล็อกเป็นดิจิทัลความละเอียด 16 บิต (ADS1115 ADC Module) และระบบสื่อสารบลูทูธพลังงานต่ำ (BLE 5.0)
4. **แผงวงจรเอนกประสงค์ สายสัญญาณ และระบบจ่ายพลังงาน** (8,500 บาท)  
   ประกอบด้วยแผ่นวงจรพิมพ์ (PCB), แบตเตอรี่ลิเธียมไอออนความจุ 2,000 mAh พร้อมวงจรชาร์จและป้องกันแรงดันตก, สวิตช์เปิด-ปิด, ขั้วต่อ USB-C และสายเชื่อมต่อ
5. **อุปกรณ์จัดเก็บข้อมูลสำรอง (External Storage)** (3,500 บาท)  
   External Hard Drive / High-speed USB Drive สำหรับบันทึกชุดข้อมูลดิบจากการทดลอง
6. **วัสดุขึ้นรูปตัวเครื่อง 3 มิติ (3D Printing Filament)**  
   เส้นใยพอลิเมอร์ Black PETG ทนความร้อนสูง ทนรังสี UV และความชื้นในแปลงเกษตรกรรม สำหรับพิมพ์กล่องตรวจวัดแบบพกพา

### 1.2 หมวดวัสดุวิทยาศาสตร์ สารเคมี และอุปกรณ์ห้องปฏิบัติการ (5,000 บาท)
1. **สารละลายบัฟเฟอร์มาตรฐานสอบเทียบ (Standard Buffer Solutions)** (3,500 บาท)  
   สารละลายบัฟเฟอร์มาตรฐานที่ผ่านการรับรองความถูกต้อง (Certified Reference Material หรือ CRM) ได้แก่ pH 4.01, pH 7.00 และ pH 10.01
2. **สารเคมีและวัสดุเตรียมตัวอย่างดิน** (1,500 บาท)  
   น้ำปราศจากไอออน (Deionized Water), สารละลายล้างหัววัด และสารเคมีช่วยตกตะกอนอนุภาคดิน
3. **อ่างควบคุมอุณหภูมิห้องปฏิบัติการ (Constant Temperature Water Bath)**  
   อ่างควบคุมอุณหภูมิที่มีระบบกวนสารละลายในตัว สามารถควบคุมและรักษาอุณหภูมิได้อย่างแม่นยำในช่วง 20.0 ถึง 50.0 องศาเซลเซียส มีความคลาดเคลื่อนไม่เกิน ±0.1 องศาเซลเซียส
4. **อุปกรณ์เตรียมตัวอย่างดินมาตรฐาน**  
   โกร่งบดย่อยดินกระเบื้องเคลือบ (Porcelain Mortar and Pestle), ตะแกรงร่อนดินสแตนเลสมาตรฐานขนาดช่องเปิด 2.0 มิลลิเมตร (ASTM E11 No. 10), เครื่องชั่งไฟฟ้าความละเอียด 2 ตำแหน่ง, บีกเกอร์แก้วบอโรซิลิเกต, และกระบอกตวง

### 1.3 หมวดอุปกรณ์เก็บตัวอย่างดินภาคสนามและสำนักงาน (7,850 บาท)
1. **อุปกรณ์เก็บตัวอย่างดินภาคสนาม** (3,000 บาท)  
   กระบอกสุ่มเก็บตัวอย่างดิน (Soil Core Sampler), ถุงพลาสติกพอลิเอทิลีนปิดสนิท (Zip-lock), ป้ายระบุพิกัดและรหัสตัวอย่างดิน, และเครื่องบันทึกพิกัดภูมิศาสตร์ (GPS)
2. **วัสดุสำนักงานและเอกสารจัดเก็บ** (4,850 บาท)  
   กระดาษบันทึกข้อมูลภาคสนาม, แฟ้มจัดเก็บเอกสาร, หมึกพิมพ์รายงาน, และปากกาเขียนระบุตัวอย่างกันน้ำ

---

## 2. แผนการออกแบบการดำเนินงานวิจัยให้บรรลุวัตถุประสงค์ทั้ง 3 ข้อ

การดำเนินงานวิจัยถูกออกแบบเชิงบูรณาการระหว่างฟิสิกส์เคมีไฟฟ้าและวิศวกรรมปัญญาประดิษฐ์ เพื่อตอบสนองต่อวัตถุประสงค์แต่ละข้ออย่างเป็นรูปธรรม

```
[ วัตถุประสงค์ข้อที่ 1 ] ศึกษาและสร้างชุดข้อมูลความสัมพันธ์ E_real, T, pH_std
         |
         v (กระบวนการ: Water Bath 20-45°C + 3 บัฟเฟอร์มาตรฐาน + บันทึกค่าเสถียร)
[ ชุดข้อมูลมาตรฐาน Benchmark Dataset คุณภาพสูง ]
         |
         v
[ วัตถุประสงค์ข้อที่ 2 ] พัฒนาโมเดล AI ชดเชยผลของอุณหภูมิและความไม่เป็นเชิงเส้น
         |
         v (กระบวนการ: Train ANN 2-16-8-1 + Backprop + Deploy TinyML/Flutter)
[ อัลกอริทึมชดเชยความคลาดเคลื่อน g(E, T) ฝังบนเครื่องต้นแบบและแอปพลิเคชัน ]
         |
         v
[ วัตถุประสงค์ข้อที่ 3 ] ทดสอบประสิทธิภาพ Method Validation และภาคสนามจริง
         |
         v (กระบวนการ: Accuracy < 5%, Precision n=11 %RSD < 5%, Paired t-test > 0.05)
[ รายงานวิจัยฉบับสมบูรณ์ + ต้นแบบ 5 เครื่อง + บทความวิชาการนานาชาติ ]
```

---

### การดำเนินงานเพื่อบรรลุวัตถุประสงค์ข้อที่ 1
**"เพื่อศึกษาและสร้างชุดข้อมูลความสัมพันธ์ระหว่างค่าศักย์ไฟฟ้าของเซนเซอร์วัดค่าความเป็นกรด เบสของดิน (Soil pH) กับค่าอุณหภูมิ และค่า Soil pH มาตรฐาน สำหรับพัฒนาโมเดลปัญญาประดิษฐ์"**

#### ขั้นตอนการปฏิบัติการเชิงวิศวกรรม
1. **การประกอบระบบสถานีเก็บข้อมูล (Data Acquisition Rig)**  
   ต่อวงจรเซนเซอร์โพเทนชิออเมตริกและเซนเซอร์อุณหภูมิ DS18B20 เข้ากับบอร์ด ESP32 โดยใช้โมดูลแปลงสัญญาณ ADS1115 ความละเอียด 16 บิต พร้อมโปรแกรมอ่านค่าแรงดันไฟฟ้าความละเอียดสูง บันทึกข้อมูลส่งผ่านสาย USB Serial สู่คอมพิวเตอร์แบบอัตโนมัติ
2. **การตั้งค่าอ่างควบคุมอุณหภูมิ (Water Bath Protocol)**  
   กำหนดระดับอุณหภูมิควบคุม 6 ระดับ ได้แก่ 20, 25, 30, 35, 40 และ 45 องศาเซลเซียส โดยปรับเพิ่มขึ้นครั้งละ 5.0 องศาเซลเซียส เพื่อจำลองสภาวะอุณหภูมิผันผวนในแปลงเกษตรกรรมภาคสนาม
3. **การทดสอบสารละลายบัฟเฟอร์มาตรฐาน 3 ค่า**  
   ใช้สารละลายบัฟเฟอร์มาตรฐาน pH 4.01 (กรด), pH 7.00 (กลาง) และ pH 10.01 (เบส) ใส่ในอ่างควบคุมอุณหภูมิ รอจนอุณหภูมิสารละลายคงที่สม่ำเสมอ
4. **การบันทึกข้อมูลเพื่อความเสถียร**  
   จุ่มหัววัดลงในสารละลาย บันทึกค่าศักย์ไฟฟ้า $E_{\text{real}}$ และอุณหภูมิ $T$ ต่อเนื่องเป็นเวลา 1.0 ถึง 2.0 นาทีต่อสภาวะ แล้วคำนวณค่าเฉลี่ยที่เสถียร รวมจุดทดสอบทั้งหมด $6 \times 3 = 18$ สภาวะหลัก และทำซ้ำ 5 รอบการทดลอง เพื่อสร้างชุดข้อมูลขนาดใหญ่กว่า 1,500 ตัวอย่าง
5. **การทำความสะอาดและจัดเตรียมชุดข้อมูล (Data Cleaning & Normalization)**  
   กำจัดสัญญาณรบกวนสไปก์ (Noise Spike Filtering) และจัดโครงสร้างข้อมูลลงในไฟล์ CSV ที่ประกอบด้วยฟีเจอร์ ศักย์ไฟฟ้าดิบ อุณหภูมิ และค่า pH มาตรฐานจริง

---

### การดำเนินงานเพื่อบรรลุวัตถุประสงค์ข้อที่ 2
**"เพื่อพัฒนาโมเดลปัญญาประดิษฐ์ที่สามารถชดเชยความคลาดเคลื่อนในการวัดที่เกิดจากผลของอุณหภูมิและความไม่เป็นเชิงเส้นของเซนเซอร์"**

#### ขั้นตอนการปฏิบัติการเชิงวิศวกรรม
1. **การแบ่งส่วนชุดข้อมูล (Dataset Partitioning)**  
   แบ่งข้อมูลด้วยวิธีสุ่มแบบแบ่งชั้น (Stratified Random Splitting) ออกเป็น 3 ส่วน ได้แก่
   * ชุดข้อมูลสำหรับฝึกสอน (Training Set) ร้อยละ 70 สำหรับการเรียนรู้ค่าน้ำหนัก
   * ชุดข้อมูลสำหรับตรวจสอบ (Validation Set) ร้อยละ 15 สำหรับการปรับจูนไฮเปอร์พารามิเตอร์และควบคุมการหยุดฝึกสอน
   * ชุดข้อมูลสำหรับทดสอบ (Test Set) ร้อยละ 15 สำหรับประเมินประสิทธิภาพครั้งสุดท้าย
2. **การออกแบบสถาปัตยกรรมโครงข่ายประสาทเทียม (ANN Architecture)**  
   สร้างโมเดลชนิด Multilayer Perceptron (MLP) แบบ 2-16-8-1
   * **ชั้นนำเข้า (Input Layer)** 2 โหนด รับค่าศักย์ไฟฟ้าดิบ $E_{\text{real}}$ และอุณหภูมิ $T$
   * **ชั้นซ่อนที่ 1 (Hidden Layer 1)** 16 โหนด ใช้ฟังก์ชันกระตุ้นแบบ ReLU เพื่อสกัดความสัมพันธ์ไม่เป็นเชิงเส้น
   * **ชั้นซ่อนที่ 2 (Hidden Layer 2)** 8 โหนด ใช้ฟังก์ชันกระตุ้นแบบ ReLU เพื่อสกัดอันตรกิริยาร่วมระหว่างอุณหภูมิและศักย์ไฟฟ้า
   * **ชั้นส่งออก (Output Layer)** 1 โหนด ใช้ฟังก์ชันเชิงเส้น (Linear) ให้ผลลัพธ์เป็นค่า $\text{pH}_{\text{predicted}}$
3. **การฝึกสอนและการควบคุมความคลาดเคลื่อน**  
   * ใช้ฟังก์ชันการสูญเสีย Root Mean Squared Error (RMSE)
   * ปรับค่าน้ำหนักด้วย Adam Optimizer กำหนดอัตราการเรียนรู้ 0.001
   * ป้องกัน Overfitting ด้วย $L_2$ Regularization (Weight Decay 0.0001) และ Early Stopping หาก Validation Loss ไม่ลดลงต่อเนื่อง 20 Epochs
4. **การเปรียบเทียบแบบจำลองทางเลือก (Model Benchmarking)**  
   เปรียบเทียบสมรรถนะของ ANN กับแบบจำลองอื่น ได้แก่ การถดถอยเชิงเส้นดั้งเดิม (Linear Calibration), การประมาณตามสมการเนินสต์, และ Support Vector Regression (SVR - RBF Kernel)
5. **การฝังแบบจำลองลงบนระบบต้นแบบและแอปพลิเคชัน (Deployment)**  
   * สกัดค่าน้ำหนักและไบอัสของ ANN ออกมาเป็น C++ Matrix Array นำไปฝังในเฟิร์มแวร์ ESP32 ทำงานแบบ TinyML ประมวลผลได้ภายในเวลาไม่เกิน 0.15 มิลลิวินาที
   * นำสมการชดเชยความคลาดเคลื่อนไปติดตั้งลงในแอปพลิเคชันมือถือ Flutter (วิดเจ็ต `ht_compensation_card.dart` ในแอป `SoilpH_HT`) สำหรับการแสดงผลผ่านบลูทูธ

---

### การดำเนินงานเพื่อบรรลุวัตถุประสงค์ข้อที่ 3
**"เพื่อทดสอบประสิทธิภาพของชุดทดสอบค่าความเป็นกรด-ด่างของดินแบบพกพาภาคสนามที่มีการชดเชยความคลาดเคลื่อนโดยปัญญาประดิษฐ์ โดยเปรียบเทียบความแม่นยำกับเครื่องมือวัดมาตรฐานและทดสอบจริงในภาคสนาม (สวนผลไม้)"**

#### ขั้นตอนการปฏิบัติการเชิงวิศวกรรม
การทดสอบแบ่งออกเป็น 2 ระยะสำคัญตามมาตรฐานเคมีวิเคราะห์สากล

#### ระยะที่ 1 การตรวจสอบความใช้ได้ของวิธีในห้องปฏิบัติการ (Method Validation)
1. **การประเมินความแม่น (Accuracy / Trueness Assessment)**  
   นำชุดทดสอบต้นแบบไปตรวจวัดสารละลายบัฟเฟอร์มาตรฐานที่ระดับอุณหภูมิต่างๆ คำนวณค่าร้อยละความคลาดเคลื่อนสัมพัทธ์
   $$\text{Error (\%)} = \left| \frac{\text{pH}_{\text{measured}} - \text{pH}_{\text{standard}}}{\text{pH}_{\text{standard}}} \right| \times 100$$
   * **เกณฑ์ความสำเร็จ** ค่าร้อยละความคลาดเคลื่อนเฉลี่ยต้องน้อยกว่าร้อยละ 5.0 ในทุกช่วงการวัด
2. **การประเมินความเที่ยง (Precision / Repeatability Assessment)**  
   ทำการตรวจวัดซ้ำในสารละลายบัฟเฟอร์มาตรฐานชนิดเดิมจำนวน 11 ครั้งติดต่อกัน ($n = 11$) ภายใต้สภาวะเดียวกัน คำนวณค่าร้อยละของส่วนเบี่ยงเบนมาตรฐานสัมพัทธ์
   $$\text{\%RSD} = \frac{\text{SD}}{\bar{x}} \times 100$$
   * **เกณฑ์ความสำเร็จ** ค่า %RSD ต้องน้อยกว่าร้อยละ 5.0 ยืนยันความเสถียรของชุดทดสอบ

#### ระยะที่ 2 การทดสอบในสภาพแปลงจริงภาคสนาม (Field Testing in Fruit Orchards)
1. **การคัดเลือกพื้นที่และเก็บตัวอย่างดิน**  
   ลงพื้นที่สวนทุเรียนและสวนผลไม้เศรษฐกิจใน จ.จันทบุรี (อ.มะขาม, อ.ท่าใหม่) และ จ.ตราด (อ.เขาสมิง ร่วมกับมูลนิธิเก้าเกษตร) สุ่มเก็บตัวอย่างดินจริงจำนวน 10 ถึง 20 แปลง
2. **การเตรียมตัวอย่างแบบแบ่งคู่ขนาน (Split-sample Protocol)**  
   นำดินแต่ละตัวอย่างมาผึ่งลม บด และร่อนผ่านตะแกรง 2.0 มม. ให้มีขนาดสม่ำเสมอ แล้วแบ่งตัวอย่างออกเป็น 2 ส่วนเท่ากัน
   * **ส่วนที่หนึ่ง** นำมาผสมน้ำกลั่นในอัตราส่วนดินต่อน้ำ 1 ต่อ 1 ตามวิธีมาตรฐาน และตรวจวัดด้วยชุดทดสอบต้นแบบที่ชดเชยด้วย AI ในสภาพอากาศภาคสนาม
   * **ส่วนที่สอง** ส่งไปตรวจวิเคราะห์ด้วยเครื่องวัด pH ดิจิทัลระดับห้องปฏิบัติการมาตรฐานที่ได้รับการรับรอง ISO/IEC 17025 เพื่อใช้เป็นค่าอ้างอิงจริง (Ground Truth)
3. **การทดสอบสมมติฐานทางสถิติ (Statistical Hypothesis Testing)**  
   * ทดสอบเปรียบเทียบผลต่างระหว่างวิธีด้วยการทดสอบทีสำหรับกลุ่มตัวอย่างไม่อิสระ (Paired Samples t-test) ที่ระดับนัยสำคัญ 0.05 โดยตั้งสมมติฐานหลัก ($H_0$) ว่าค่าเฉลี่ยของทั้งสองวิธีไม่แตกต่างกัน
   * หากค่า $p\text{-value} > 0.05$ แสดงว่าชุดทดสอบต้นแบบภาคสนามให้ผลการวัดที่แม่นยำเทียบเท่าเครื่องมือระดับห้องปฏิบัติการมาตรฐาน
   * วิเคราะห์ค่าสัมประสิทธิ์การตัดสินใจ ($R^2$) ต้องมีค่าสูงกว่า 0.95 และทำการพลอตแผนภาพแบลนด์-อัลต์แมน (Bland-Altman Plot) เพื่อยืนยันขอบเขตข้อตกลงร่วมกัน (Limits of Agreement)

---

## 3. ตารางสรุปตัวชี้วัดความสำเร็จตามวัตถุประสงค์ (KPI Matrix)

| วัตถุประสงค์ | กิจกรรมหลัก | ตัวชี้วัดเชิงปริมาณ (KPIs) | เกณฑ์การยอมรับ |
| :--- | :--- | :--- | :---: |
| **วัตถุประสงค์ข้อที่ 1** | การทดลอง Water Bath 20-45°C บัฟเฟอร์ 4.01, 7.00, 10.01 | จำนวนแถวข้อมูลใน Dataset | ไม่น้อยกว่า 1,500 จุดข้อมูล |
| **วัตถุประสงค์ข้อที่ 2** | ฝึกสอนโมเดล ANN และฝัง TinyML / Flutter | ค่า RMSE บน Test Set<br>เวลาประมวลผลบนชิป | $\text{RMSE} < 0.15\text{ pH}$<br>$< 0.15\text{ ms}$ |
| **วัตถุประสงค์ข้อที่ 3.1** | Method Validation ในห้องปฏิบัติการ | ความแม่น (Relative Error)<br>ความเที่ยง (%RSD ซ้ำ 11 ครั้ง) | $\text{Error} < 5.0\%$<br>$\text{\%RSD} < 5.0\%$ |
| **วัตถุประสงค์ข้อที่ 3.2** | ทดสอบภาคสนามสวนผลไม้ จันทบุรี-ตราด | ผลการทดสอบ Paired t-test<br>สัมประสิทธิ์การตัดสินใจ ($R^2$) | $p\text{-value} > 0.05$<br>$R^2 > 0.95$ |
| **ผลผลิตโครงการ** | สร้างชุดต้นแบบและรายงานวิจัยฉบับสมบูรณ์ | เครื่องต้นแบบ<br>บทความวิชาการนานาชาติ | 5 เครื่อง<br>1 เรื่อง |
