TsanaPhysics/JC-AGRITecH-AI/smart_health_tracker/latex_manual/frontmatter/titlepage.tex

\begin{titlepage}
\begin{center}
  \vspace*{1.2cm}

  {\fontsize{20pt}{26pt}\selectfont\bfseries การออกแบบและพัฒนาแอปพลิเคชันเพื่อสุขภาพ\\การนับก้าวและการตรวจจับการเคลื่อนไหวร่างกายเชิงสรีรวิทยาประยุกต์\par}
  \vspace{0.4cm}
  {\fontsize{11pt}{15pt}\selectfont\color{rbruNavy}\bfseries DESIGN AND DEVELOPMENT OF SMART HEALTH TRACKER APPLICATION\\FOR PHYSIOLOGICAL STEP COUNTING AND BIOMECHANICAL KINEMATICS\par}

  \vspace{2.2cm}

  {\fontsize{14pt}{20pt}\selectfont\bfseries
  ผู้ช่วยศาสตราจารย์ ดร.ชีวะ ทัศนา\\
  และคณะนักวิจัย\par}

  \vfill

  {\fontsize{11pt}{16pt}\selectfont
  หน่วยวิเคราะห์-ติดตามคุณภาพดินและสภาพอากาศเชิงพื้นที่\\
  คณะวิทยาศาสตร์และเทคโนโลยี\\
  มหาวิทยาลัยราชภัฏรำไพพรรณี\\
  พุทธศักราช 2569\par}
\end{center}
\end{titlepage}
