TsanaPhysics/JC-AGRITecH-AI/plantheath/assets/docs/Durian_Leaf_AI_Manual.pdf

หน่วยวิเคราะห์-ติดตามคุณภาพดินและสภาพอากาศเชิงพื้นที่

คณะวิทยาศาสตร์และเทคโนโลยี มหาวิทยาลัยราชภัฏรำไพพรรณี

# การออกแบบและพัฒนาแอปพลิเคชัน

# วิเคราะห์โรคและความสมบูรณ์ของไม้ผล

# ด้วย AI +Deep Learning

DESIGN AND DEVELOPMENT OF AN APPLICATION FOR FRUIT TREE PATHOLOGY AND HEALTH ASSESSMENT USING AI + DEEP LEARNING

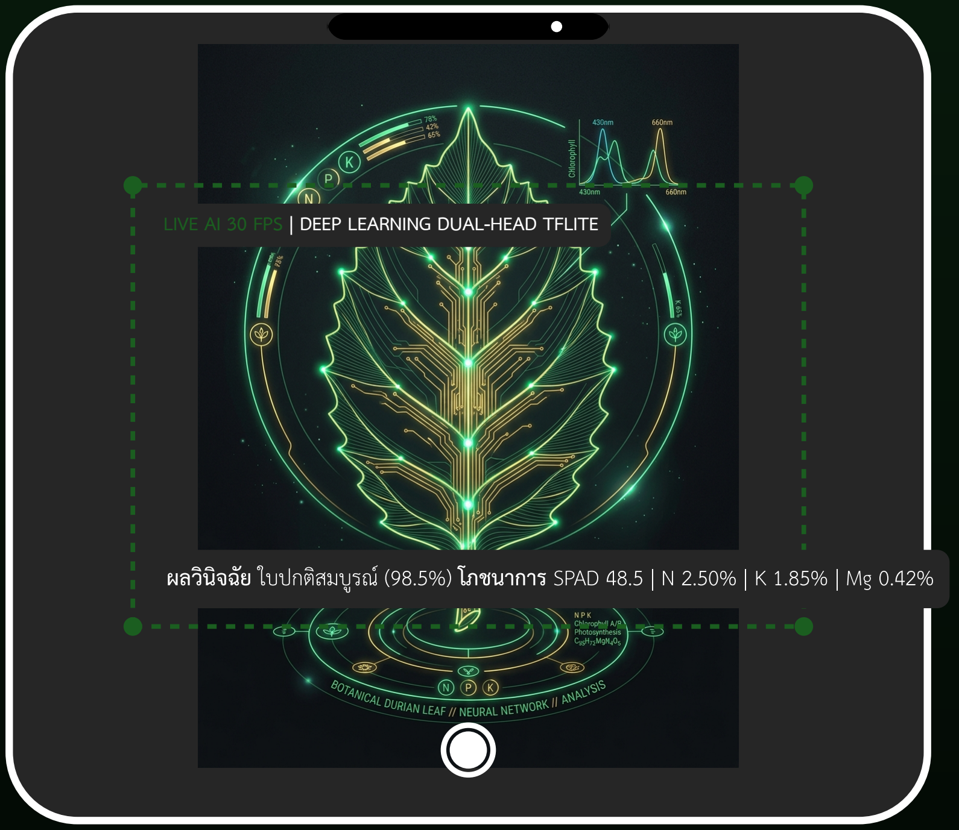
[picture p112: figure]

LIVE AI 30 FPS | DEEP LEARNING DUAL-HEAD TFLITE
ผลวินิจฉัย ใบปกติสมบูรณ์ (98.5%) โภชนาการ SPAD 48.5 | N 2.50% | K 1.85% | Mg 0.42%

ผู้ช่วยศาสตราจารย์ ดร.ชีวะ ทัศนา และคณะนักวิจัย
หน่วยวิเคราะห์-ติดตามคุณภาพดินและสภาพอากาศเชิงพื้นที่ คณะวิทยาศาสตร์และเทคโนโลยี มหาวิทยาลัยราชภัฏรำไพพรรณี เอกสารคู่มือวิชาการและวิจัยฉบับสมบูรณ์ พุทธศักราช 2569

## การออกแบบและพัฒนาแอปพลิเคชัน วิเคราะห์โรคและความสมบูรณ์ของไม้ผลด้วย AI +Deep Learning

DESIGN AND DEVELOPMENT OF AN APPLICATION FOR FRUIT TREE PATHOLOGY
AND HEALTH ASSESSMENT USING AI + DEEP LEARNING

ผู้ช่วยศาสตราจารย์ ดร.ชีวะ ทัศนา และคณะนักวิจัย

# คำนำ

การบริหารจัดการสวนทุเรียนยุคดิจิทัลจำเป็นต้องอาศัยการตรวจติดตามสุขภาพทางสรีรวิทยาและโรคพืช อย่างแม่นยำและทันท่วงที ในอดีตการตรวจหาอาการโรคใบพืชและการประเมินความสมบูรณ์ของธาตุอาหารจำเป็น ต้องพึ่งพาความเชี่ยวชาญเฉพาะบุคคลของเกษตรกรหรือการส่งตัวอย่างใบไม้เข้าตรวจวิเคราะห์ในห้องปฏิบัติการทาง เคมี ซึ่งใช้ระยะเวลานานและมีค่าใช้จ่ายสูง การเกิดโรคระบาดรุนแรง เช่น โรคใบไหม้ไฟทอปธอร่า (Phytophthora palmivora) หรือโรคราใบติด (Rhizoctonia solani) จึงมักสร้างความเสียหายอย่างมีนัยสำคัญก่อนที่การรักษาจะเริ่ม ต้นขึ้น
หน่วยวิเคราะห์-ติดตามคุณภาพดินและสภาพอากาศเชิงพื้นที่ คณะวิทยาศาสตร์และเทคโนโลยี มหาวิทยาลัย ราชภัฏรำไพพรรณี จึงได้บูรณาการองค์ความรู้ด้านฟิสิกส์เชิงแสงและสเปกโทรสโกปีเสมือน ร่วมกับโมเดลการเรียนรู้ เชิงลึกแบบ Dual-Head Convolutional Neural Network ออกแบบและพัฒนาแอปพลิเคชันมือถือ DurianLeaf AI (PlantHealth) ที่สามารถตรวจวินิจฉัยโรคพืชควบคู่กับการประเมินภาวะโภชนาการพืช (ธาตุอาหารหลัก NPK ธาตุ อาหารรอง และจุลธาตุ) ผ่านกล้องถ่ายภาพสดแบบเรียลไทม์
จุดเด่นสำคัญของระบบคือ แถบเมนูปรับขนาดและรูปทรงของพื้นที่ตรวจจับ (Interactive ROI Floating Toolbar) ที่มีแถบแสดงเฉดสีตามเกณฑ์มาตรฐานทางวิชาการเรืองแสงเชื่อมโยงกับค่าการวิเคราะห์สด พร้อมทั้งกลไก การเรียนรู้เพิ่มเติมระดับเครื่อง (On-Device Continual Few-Shot Learning) ที่เปิดโอกาสให้ผู้ใช้งานสามารถสอน อาการโรคใหม่หรือสายพันธุ์ทุเรียนใหม่เข้าสู่หน่วยความจำของโมเดลได้ทันทีโดยไม่ต้องคอมไพล์โปรแกรมใหม่ คณะผู้จัดทำหวังเป็นอย่างยิ่งว่าคู่มือปฏิบัติการฉบับนี้ จะเป็นประโยชน์แก่นักวิจัย เกษตรกรผู้ปลูกทุเรียน ตลอดจนคณาจารย์และนักศึกษา เพื่อขับเคลื่อนเทคโนโลยีการเกษตรแม่นยำของประเทศไทยสู่ระดับสากลต่อไป

ผู้ช่วยศาสตราจารย์ ดร.ชีวะ ทัศนา หน่วยวิเคราะห์-ติดตามคุณภาพดินและสภาพอากาศเชิงพื้นที่ คณะวิทยาศาสตร์และเทคโนโลยี มหาวิทยาลัยราชภัฏรำไพพรรณี

i

# สารบัญ

คำนำ | i
สารบัญตาราง | v
สารบัญภาพ | vi
1 พื้นฐานโรคใบพืชทุเรียนและวิทยาศาสตร์เฉดสีของรอยโรค | 1
1.2.6 | การวิเคราะห์เปรียบเทียบพยาธิสภาพรอยโรคแบบพหุรูปแบบ (Multi-Modal
2 สรีรวิทยาเฉดสีและสุขภาพธาตุอาหารพืช | 7
2.2.5 | การขาดจุลธาตุเหล็ก สังกะสี และโบรอน (Micronutrient Deficiencies) . . . . | 8
2.2.6 | ภาวะได้รับธาตุอาหารเกินเกณฑ์และความเป็นพิษ (Nutrient Excess and Toxicity) 8

ii

สารบัญ | iii
2.4.2 | สรีรวิทยา การ เคลื่อน ย้าย ธาตุ อาหารในท่อ น้ำท่อ อาหาร (Nutrient Mobility
2.4.3 | ระยะพัฒนาการทรงพุ่มและระบบความปลอดภัยในการให้ปุ๋ย (Crop Stages and
2.4.4 | การประเมินความเข้มข้นเชิงปริมาณในหน่วย มิลลิกรัมต่อกิโลกรัม (mg/kg หรือ
3 วิทยาศาสตร์เฉดสีและการวิเคราะห์มาตรวิทยาทางแสงทั้งหมด | 13
3.2.1 | ระยะห่างแบบยูคลิดดั้งเดิม (∆E
∗
3.4.1 | อัลกอริทึมตัดพิกเซลสะท้อนแสงวาบของชั้นไขเคลือบใบ (Cuticular Wax Glare
4 สถาปัตยกรรมปัญญาประดิษฐ์การเรียนรู้เชิงลึกและการเรียนรู้ต่อเนื่อง | 16
5 การออกแบบและพัฒนาแอปพลิเคชันบนสมาร์ทโฟน | 19
5.3 | องค์ประกอบของแถบเมนูควบคุมพื้นที่ตรวจจับ (Interactive ROI Floating Toolbar) . . . . 20

สารบัญ | iv
5.5.1 | การคำนวณความดันไอน้ำในอากาศส่วนขาดตามสมการ Tetens (Tetens VPD
5.7 | สถาปัตยกรรมการจัดวางหน้าจอที่ไร้การซ้อนทับ (Non-Overlapping Ergonomic Layout) . 22
6 วิศวกรรมพรอมพ์และการออกแบบระบบร่วมกับปัญญาประดิษฐ์ | 24
6.2.3 | พรอมพ์ที่ 3 การสังเคราะห์สถาปัตยกรรม Deep Learning และ Multi-Task Loss 25
6.2.5 | พรอมพ์ที่ 5 การออกแบบภาพปกและไอคอนสไตล์มินิมอลลายเส้น AI ธาตุอาหาร . 25
6.2.6 | พรอมพ์ที่ 6 การสังเคราะห์คำแนะนำการบำรุงรักษาและการจัดการแปลง . . . . 26
6.3 | การต่อยอดสู่โมเดลภาษาขนาดใหญ่บนอุปกรณ์พกพา (On-Device LLM Integration) . . . . 26

# สารบัญตาราง

1.1 | คุณลักษณะทางแสงและพิกัดสีมาตรฐานของรอยโรคใบพืชทุเรียน 6 กลุ่ม | | 1
1.2 | เกณฑ์การจัดระดับความรุนแรงของโรคใบพืชทุเรียน (DSI) | | 6
2.1 | คุณลักษณะทางแสงและพิกัดสีมาตรฐานของภาวะโภชนาการในใบพืชทุเรียน | | 7
3.1 | ชุดดัชนีพืชพรรณเชิงแสงสำหรับการวิเคราะห์ใบพืชทุเรียนในระบบ DurianLeaf AI | 14

v

# สารบัญภาพ

1.1 | การเปรียบเทียบรอยโรคใบไหม้ไฟทอปธอร่าระหว่างภาพถ่ายมาโครสมจริงกับภาพลายเส้น
วิเคราะห์ขอบเขตแผลปัญญาประดิษฐ์ | | 2
1.2 | การเปรียบเทียบรอยโรคราใบติดระหว่างภาพถ่ายมาโครสมจริงกับภาพลายเส้นวิเคราะห์การ
แผ่กระจายเส้นใยราปัญญาประดิษฐ์ | | 3
1.3 | การเปรียบเทียบรอยโรคแอนแทรคโนสระหว่างภาพถ่ายมาโครสมจริงกับภาพลายเส้นวิเคราะห์
วงแหวนศูนย์กลางปัญญาประดิษฐ์ | | 3
1.4 | การเปรียบเทียบ จุดสนิมสาหร่าย ระหว่างภาพถ่ายมาโครสมจริงกับภาพลายเส้น ระบุพิกัด
ศูนย์กลางกลุ่มจุดปัญญาประดิษฐ์ | | 4
1.5 | การเปรียบเทียบความเสียหายจากไรแดงและเพลี้ยไก่แจ้ระหว่างภาพถ่ายมาโครสมจริงกับภาพ
ลายเส้นวิเคราะห์แผนที่ความหนาแน่นจุดประปัญญาประดิษฐ์ | | 5
1.6 | การเปรียบเทียบภาพรวมพยาธิสภาพรอยโรคใบพืชทุเรียนระหว่างภาพถ่ายสมจริงกับภาพโครง
ร่างเชิงลายเส้นวิเคราะห์โดยปัญญาประดิษฐ์ | | 5
2.1 | การเปรียบเทียบอาการขาดและเกินของธาตุอาหารพืชระหว่างภาพถ่ายสมจริงกับภาพโครง
ร่างเชิงลายเส้นและโทรมาตรปัญญาประดิษฐ์ | | 9
4.1 | แผนผังสถาปัตยกรรมโมเดล Dual-Head MobileNetV3 และชั้นเวกเตอร์เอกลักษณ์ | 16

vi

# บทที่ 1

## พื้นฐานโรคใบพืชทุเรียนและวิทยาศาสตร์เฉดสีของรอยโรค

## 1.1 ความสำคัญของการตรวจวินิจฉัยโรคใบพืชทุเรียน

ทุเรียน (Durio zibethinus L.) จัดเป็นราชาแห่งผลไม้และเป็นพืชเศรษฐกิจเชิงยุทธศาสตร์ที่สร้างรายได้ มหาศาลให้แก่ประเทศไทย ประสิทธิภาพการสังเคราะห์แสง การสะสมสารอาหารคาร์โบไฮเดรต และการเจริญเติบโต เพื่อสร้างผลผลิตคุณภาพสูง ล้วนขึ้นอยู่กับความสมบูรณ์และพื้นที่ใบสีเขียวของเรือนพุ่มเป็นหลัก อย่างไรก็ตาม สภาพ ภูมิอากาศแบบร้อนชื้นในแถบภาคตะวันออกและภาคใต้ เป็นสภาวะแวดล้อมที่เอื้อต่อการแพร่ระบาดของเชื้อรา เชื้อ สาเหตุโรคพืช และศัตรูพืชปากดูดนานาชนิด ซึ่งการระบาดที่รวดเร็วอาจทำลายพื้นที่ใบของต้นทุเรียนจนส่งผลให้ต้น ทรุดโทรม ใบร่วงหล่น และผลผลิตเสียหายอย่างสิ้นเชิง การตรวจวินิจฉัยรอยโรคในระยะเริ่มต้นด้วยเทคโนโลยีคอมพิวเตอร์วิทัศน์ (Computer Vision) และปัญญา ประดิษฐ์เชิงแสง จึงเป็นกลไกสำคัญในการตัดวงจรการระบาด ช่วยให้เกษตรกรสามารถบริหารจัดการสวนได้อย่าง แม่นยำและทันท่วงที

## 1.2 การจำแนกกลุ่มโรคและศัตรูพืชสำคัญ 6 กลุ่ม

ในการพัฒนาระบบปัญญาประดิษฐ์ DurianLeaf AI คณะผู้วิจัยได้กำหนดการจำแนกกลุ่มโรคและศัตรูพืช หลักออกเป็น 6 กลุ่มอาการตามเกณฑ์กีฏวิทยาและโรคพืชวิทยา ดังแสดงในตารางที่ 1.1

ตารางที่ 1.1 คุณลักษณะทางแสงและพิกัดสีมาตรฐานของรอยโรคใบพืชทุเรียน 6 กลุ่ม
ลำดับ | ชื่อโรคและศัตรูพืช | รหัสสี HEX | L ∗ | a ∗ | ∗ b | ลักษณะอาการรอยโรค
1 2 3 4 5 6 | ใบปกติสมบูรณ์ ใบไหม้ไฟทอปธอร่า ราใบติด (Rhizoctonia) แอนแทรคโนส ราสนิมและจุดสนิมสาหร่าย ไรแดงและเพลี้ยไก่แจ้ | #2E7D32 #3E2723 #6D4C41 #BF360C #D84315 #9E9D24 | 48.2 26.5 38.1 44.8 56.3 62.4 | -22.4 8.4 5.6 16.2 18.5 -2.1 | 28.6 12.1 14.8 29.5 42.0 18.7 | เขียวมรกตเข้ม สม่ำเสมอ ไม่พบคราบหรือแผล แผลฉ่ำน้ำสีน้ำตาลเข้มถึงดำ ขอบแผลไหม้ น้ำตาลปนเทา คล้ายน้ำร้อนลวก มีใยราคลุม วงแหวนซ้อน concentric สีน้ำตาลส้ม ตุ่มนูนส้มอมแดง ผิวสัมผัสคล้ายกำมะหยี่ จุดประสีบรอนซ์เงิน ใบซีดด่าง แห้งกร้าน

1

CHAPTER 1. พื้นฐานโรคใบพืชทุเรียนและวิทยาศาสตร์เฉดสีของรอยโรค | 2

### 1.2.1 โรคใบไหม้ไฟทอปธอร่า (Phytophthora Leaf Blight)

เกิดจากเชื้อราน้ำโอโอไมซีต (Phytophthora palmivora) อาการเริ่มแรกจะปรากฏเป็นจุดแผล ฉ่ำน้ำสีน้ำตาลอ่อน ขอบแผลไม่เรียบ แผลจะขยายตัวลุกลามอย่างรวดเร็วเป็นสีน้ำตาลเข้มจนถึงดำ (#3E2723) ในสภาพ ความชื้นสัมพัทธ์สูงกว่า 90% เนื้อเยื่อบริเวณแผลจะเน่าเละ ขอบแผลมีลักษณะฉ่ำน้ำและแห้งกรอบเป็นวงกว้าง ส่งผล ให้ใบหลุดร่วงอย่างรวดเร็ว


ภาพที่ 1.1 การเปรียบเทียบรอยโรคใบไหม้ไฟทอปธอร่าระหว่างภาพถ่ายมาโครสมจริงกับภาพลายเส้นวิเคราะห์ ขอบเขตแผลปัญญาประดิษฐ์

### 1.2.2 โรคราใบติด (Rhizoctonia Web Blight)

เกิดจากเชื้อรา Rhizoctonia solani อาการบนแผ่นใบมีลักษณะเด่นคล้ายถูกน้ำร้อนลวก เนื้อเยื่อ ใบเปลี่ยนเป็นสีน้ำตาลปนเทา (#6D4C41) เชื้อราสร้างเส้นใยขาวนวลหรือสีน้ำตาลถักทอยึดแผ่นใบที่อยู่ติดกันให้ติดกัน เป็นแพ เมื่อแผลแห้งกรอบ ใบจะแห้งตายและร่วงค้างอยู่บนกิ่งไม่ยอมหล่นลงดิน

CHAPTER 1. พื้นฐานโรคใบพืชทุเรียนและวิทยาศาสตร์เฉดสีของรอยโรค | 3


ภาพที่ 1.2 การเปรียบเทียบรอยโรคราใบติดระหว่างภาพถ่ายมาโครสมจริงกับภาพลายเส้นวิเคราะห์การแผ่กระจาย เส้นใยราปัญญาประดิษฐ์

### 1.2.3 โรคแอนแทรคโนส (Anthracnose)

เกิดจากเชื้อรา Colletotrichum gloeosporioides มักปรากฏแผลรูปทรงกลมหรือรูปรีขอบหยัก แผลมีสีน้ำตาลอ่อนปนส้ม (#BF360C) โดยมีจุดเด่นคือรอยวงแหวนซ้อนกันเป็นชั้น (Concentric Rings หรือ Zonate Pattern) บริเวณขอบแผลจะมีสีเข้มกว่าเนื้อเยื่อแผลด้านใน กลางแผลแห้งบางและอาจฉีกขาดกลายเป็นรูพรุน


ภาพที่ 1.3 การเปรียบเทียบรอยโรคแอนแทรคโนสระหว่างภาพถ่ายมาโครสมจริงกับภาพลายเส้นวิเคราะห์วงแหวน ศูนย์กลางปัญญาประดิษฐ์

CHAPTER 1. พื้นฐานโรคใบพืชทุเรียนและวิทยาศาสตร์เฉดสีของรอยโรค | 4

### 1.2.4 โรคราสนิมและจุดสนิมสาหร่าย (Algal Rust Spot)

เกิดจากสาหร่ายกาฝากสีเขียวชนิด Cephaleuros virescens มักพบบนใบแก่ที่ได้รับแสงแดด จัด แผลมีลักษณะเป็นตุ่มกลมนูนขนาดเล็ก 2 − 6 mm ผิวหน้าแผลมีขนละเอียดคล้ายกำมะหยี่สีส้มอิฐหรือสีสนิม (#D84315) ค่าสีb
∗

จะมีค่าบวกสูง (> 40) เมื่อแก่ตัวลงจุดสาหร่ายจะเปลี่ยนเป็นสีน้ำตาลอมเทา


ภาพที่ 1.4 การเปรียบเทียบจุดสนิมสาหร่ายระหว่างภาพถ่ายมาโครสมจริงกับภาพลายเส้นระบุพิกัดศูนย์กลางกลุ่ม จุดปัญญาประดิษฐ์

### 1.2.5 ความเสียหายจากไรแดงและเพลี้ยไก่แจ้ (Mite and Psyllid Damage)

เกิดจากการเข้าทำลายของศัตรูพืชปากดูด เช่น ไรแดงแอฟริกัน (Oligonychus biharensis) และ เพลี้ยไก่แจ้ทุเรียน (Pseudophacopteron canarium) แมลงจะดูดกินน้ำเลี้ยงบริเวณหน้าใบและยอดอ่อน ทำให้คลอ โรฟิลล์ถูกทำลายเป็นจุดประพร่างสีขาวซีดหรือสีบรอนซ์เงิน (#9E9D24) ค่าความสว่าง L
∗

จะพุ่งสูงขึ้นสู่ช่วง 60 − 65 และค่าความอิ่มตัวสีลดลง แผ่นใบจะโค้งงอ ผิวใบสากกร้านและร่วงก่อนกำหนด

CHAPTER 1. พื้นฐานโรคใบพืชทุเรียนและวิทยาศาสตร์เฉดสีของรอยโรค | 5

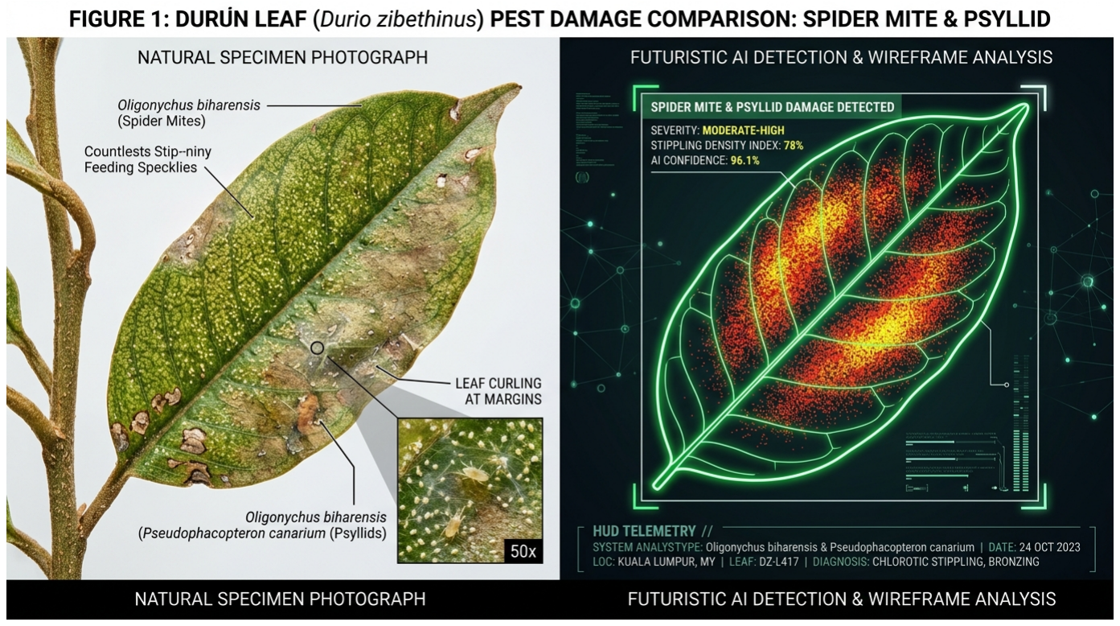
[picture p113: figure]

ภาพที่ 1.5 การเปรียบเทียบความเสียหายจากไรแดงและเพลี้ยไก่แจ้ระหว่างภาพถ่ายมาโครสมจริงกับภาพลายเส้น วิเคราะห์แผนที่ความหนาแน่นจุดประปัญญาประดิษฐ์

### 1.2.6 การวิเคราะห์เปรียบเทียบพยาธิสภาพรอยโรคแบบพหุรูปแบบ (Multi-Modal

Pathology Synthesis)
ระบบ DurianLeaf AI ผสานโครงสร้างภาพถ่ายความละเอียดสูงเข้ากับอัลกอริทึมการแปลงเป็น ภาพโครงร่างลายเส้นดิจิทัล (Digital Line-Art Wireframe) เพื่อช่วยให้เกษตรกรและผู้เชี่ยวชาญสามารถเปรียบเทียบ รอยโรคจริงกับขอบเขตการคำนวณของโครงข่ายประสาทเทียมได้อย่างชัดเจน ดังแสดงในรูปที่ 1.6


ภาพที่ 1.6 การเปรียบเทียบภาพรวมพยาธิสภาพรอยโรคใบพืชทุเรียนระหว่างภาพถ่ายสมจริงกับภาพโครงร่างเชิง ลายเส้นวิเคราะห์โดยปัญญาประดิษฐ์

รูปที่1.6 แสดงการวิเคราะห์เปรียบเทียบแบบคู่ขนาน (Dual-Modality Representation) โดยฝั่ง

CHAPTER 1. พื้นฐานโรคใบพืชทุเรียนและวิทยาศาสตร์เฉดสีของรอยโรค | 6

ซ้ายเป็นภาพถ่ายมาโครสมจริงความละเอียดสูง แสดงสัณฐานวิทยาของรอยโรคแท้จริงในแปลงเกษตร ได้แก่ แผลฉ่ำน้ำ เน่าดำของโรคใบไหม้ไฟทอปธอร่า รอยแผลน้ำร้อนลวกพร้อมเส้นใยราของโรคราใบติด และวงแหวนซ้อน concentric rings ของโรคแอนแทรคโนส ในขณะที่ฝั่งขวาคือภาพเชิงลายเส้นเรืองแสง (Futuristic Vector Wireframe) บนพื้น หลัง Dark Slate ซึ่งจำลองผลการประมวลผลของโมเดลปัญญาประดิษฐ์ ที่สามารถตีกรอบตรวจจับ (Bounding Box), ล้อมเส้นขอบเขตรอยโรค (Lesion Contour Mask) และแสดงค่าคะแนนความเชื่อมั่น (Confidence Score) ได้อย่าง แม่นยำ

## 1.3 เกณฑ์การจัดระดับความรุนแรงของโรค (Disease Severity Index)

ระบบได้กำหนดมาตรฐานการจัดเกรดความรุนแรงของโรคออกเป็น 5 ระดับ (Grade 0 ถึง Grade 4) เพื่อนำ ไปประเมินดัชนีความรุนแรง (Disease Severity Index หรือ DSI) สำหรับการวางแผนพ่นสารชีวภัณฑ์หรือสารป้องกัน กำจัดโรคพืช ดังแสดงในตารางที่ 1.2
ตารางที่ 1.2 เกณฑ์การจัดระดับความรุนแรงของโรคใบพืชทุเรียน (DSI)
ระดับ (Grade) | สัดส่วนพื้นที่แผล (%) | นิยามทางพยาธิสภาพ | มาตรการจัดการแปลง
Grade 0 | 0% | ใบสมบูรณ์ แข็งแรง ไม่พบรอยโรค | ตรวจติดตามรายสัปดาห์
Grade 1 | 1 − 10% | ระยะเริ่มต้น พบรอยแผลกระจัดกระจาย | ตัดแต่งใบที่เป็นโรคทิ้ง ฉีดพ่นเชื้อราไตรโคเดอร์มา
Grade 2 | 11 − 25% | ระยะลุกลาม แผลเริ่มเชื่อมต่อกัน | ใช้สารชีวภัณฑ์หรือคอปเปอร์ไฮดรอกไซด์
Grade 3 | 26 − 50% | ระยะรุนแรง แผ่นใบถูกทำลายเกินหนึ่งในสี่ | ใช้สารเคมีกำจัดเชื้อราเฉพาะกลุ่ม สลับกลไกออกฤทธิ์
Grade 4 | > 50% | ระยะวิกฤต ใบไหม้เกือบทั้งใบ แห้งร่วง | ตัดทำลายกิ่ง เก็บใบเผานอกแปลง หยุดการแพร่ระบาด

ทฤษฎีและหลักการฟิสิกส์เชิงประจักษ์
การประเมินดัชนีความรุนแรงของโรค (Disease Severity Index: DSI) การคำนวณค่าดัชนีความรุนแรงของโรคในแปลงทุเรียนใช้สูตรมาตรฐานทางระบาดวิทยาพืช

DSI =

∑4
| | i=0(ni × i)
| | N × 4
| | × 100% | (1.1)

เมื่อ ni คือจำนวนใบที่ถูกจัดอยู่ในระดับความรุนแรง i, N คือจำนวนใบตัวอย่างทั้งหมดที่สุ่มตรวจ และ 4 คือระดับความรุนแรงสูงสุด ค่า DSI จะถูกแสดงผลสดบนหน้าจอเพื่อช่วยให้เกษตรกรตัดสินใจระดับการใช้สาร ควบคุมโรคพืชได้อย่างคุ้มค่าและปลอดภัย

ชุดคำสั่งพรอมพต์วิศวกรรม
พรอมพ์วิศวกรรมสำหรับการสกัดรอยโรคและการวิเคราะห์พยาธิวิทยา (Prompt Eng-01)
”Act as a Senior Plant Pathologist and Computer Vision Specialist. Analyze the provided multi-channel durian leaf image within the designated Region of Interest (ROI). Segment the lesion pixels using CIE L*a*b* chromaticity bounds and texture contrast. Classify the pathogen into one of the 6 core classes: Healthy, Phytophthora Blight, Rhizoctonia Web Blight, Anthracnose, Algal Rust Spot, or Mite/ Psyllid Damage. Calculate the precise Lesion Area Ratio, map to Disease Severity Index (DSI) Grade 0 to 4, and output the result along with immediate biological and chemical treatment recommendations.”

# บทที่ 2

## สรีรวิทยาเฉดสีและสุขภาพธาตุอาหารพืช

## 2.1 สรีรวิทยาของสีใบพืชและความสัมพันธ์กับธาตุอาหาร

สี ของ ใบไม้ ทุเรียน เป็น ดัชนี ชี้ วัด สถานะ ทาง สรีรวิทยา และ ระดับ ความ สมบูรณ์ ของ ธาตุ อาหาร โดยตรง กระบวนการสังเคราะห์แสงขับเคลื่อนด้วยรงควัตถุหลักสองชนิด คือ คลอโรฟิลล์เอ (Chlorophyll a) ซึ่งมีจุดดูดกลืน แสงสูงสุดที่ความยาวคลื่น 430 nm และ 662 nm และคลอโรฟิลล์บี (Chlorophyll b) ซึ่งมีจุดดูดกลืนแสงสูงสุดที่ 453 nm และ 642 nm ในขณะที่แถบแสงสีเขียวช่วงความยาวคลื่น 500 − 560 nm จะถูกสะท้อนกลับออกมาสู่ สายตาและตัวรับรู้ของกล้องถ่ายภาพ
เมื่อพืชได้ รับ ธาตุ อาหารไม่ สมดุล สมดุลทาง ชีวเคมี ของ การ สังเคราะห์ และการ สลายตัว ของ รงควัตถุ จะ เปลี่ยนแปลงไปอย่างมีนัยสำคัญ ส่งผลให้เกิดการสะท้อนและการดูดกลืนแสงที่ผิดปกติไป ซึ่งสามารถวิเคราะห์แยกแยะ ได้ด้วยการแปลงสัญญาณภาพเข้าสู่ปริภูมิสีสากล

## 2.2 ลายเซ็นต์ทางแสงและการเปลี่ยนแปลงเฉดสีตามชนิดธาตุอาหาร

การตรวจประเมินภาวะขาดธาตุอาหารในระบบ DurianLeaf AI ครอบคลุมธาตุอาหารพืช 8 ชนิด โดยแต่ละ ธาตุมีลายเซ็นต์ทางแสง (Spectral and Colorimetric Signatures) และพิกัดสีมาตรฐานดังแสดงในตารางที่ 2.1

ตารางที่ 2.1 คุณลักษณะทางแสงและพิกัดสีมาตรฐานของภาวะโภชนาการในใบพืชทุเรียน
ธาตุอาหาร | สัญลักษณ์ | รหัสสี HEX | L ∗ | a ∗ | ∗ b | ลักษณะอาการทางสายตาและสรีรวิทยา
ปกติสมบูรณ์ ไนโตรเจนต่ำ ฟอสฟอรัสต่ำ โพแทสเซียมต่ำ แมกนีเซียมต่ำ แคลเซียมต่ำ เหล็กต่ำ สังกะสีต่ำ โบรอนต่ำ | Optimal N Def P Def K Def Mg Def Ca Def Fe Def Zn Def B Def | #1B5E20 #FBC02D #4A148C #D84315 #C0CA33 #795548 #FFF59D #E6EE9C #8D6E63 | 42.0 76.5 24.2 45.2 68.4 38.6 88.2 72.1 42.1 | -24.5 -4.8 14.8 12.6 -12.4 6.2 -2.1 -8.5 8.4 | 26.2 62.1 -8.2 28.4 48.2 10.4 32.5 36.4 14.2 | เขียวเข้มจัด มันวาว คลอโรฟิลล์ SPAD > 48 เหลืองซีดสม่ำเสมอทั่วทั้งใบ เริ่มจากใบแก่ เขียวคล้ำอมม่วงแดง แอนโทไซยานินสะสม ขอบใบไหม้แห้งสีน้ำตาลทอง (Marginal Scorch) เหลืองระหว่างเส้นใบรูปก้างปลาคว่ำ ปลายใบอ่อนม้วนงอ ขอบใบหงิก เนื้อเยื่อเจริญตาย ใบยอดซีดขาวเกือบทั้งใบ เส้นใบยังเขียวจาง โรคใบแก้ว ใบเล็กเรียวเป็นกระจุก ด่างเหลือง ใบหนาเปราะ เส้นใบปูดโปนเป็นตุ่มนูน

7

CHAPTER 2. สรีรวิทยาเฉดสีและสุขภาพธาตุอาหารพืช | 8

### 2.2.1 การขาดธาตุไนโตรเจน (Nitrogen Deficiency: N)

ไนโตรเจนเป็นองค์ประกอบโครงสร้างหลักของโมเลกุลคลอโรฟิลล์และกรดอะมิโน เมื่อเกิดภาวะ ขาดแคลน พืชจะสลายโปรตีนและคลอโรฟิลล์จากใบแก่ด้านล่างเพื่อลำเลียงไปยังยอดอ่อน ส่งผลให้เกิดอาการเหลืองซีด สม่ำเสมอทั่วทั้งแผ่นใบ (General Chlorosis) ค่าความสว่าง L
∗

จะเพิ่มขึ้นอย่างมากสู่ช่วง 70 − 80 และค่าสีเหลือง

b

∗

จะเพิ่มขึ้นสูงกว่า 55 ในขณะที่ค่า SPAD จะลดลงต่ำกว่า 32

### 2.2.2 การขาดธาตุฟอสฟอรัส (Phosphorus Deficiency: P)

ฟอสฟอรัสมีบทบาทสำคัญในการขนส่งพลังงานในรูป ATP และโครงสร้างกรดนิวคลีอิก การขาด ฟอสฟอรัสทำให้การเจริญเติบโตชะงักงัน ส่งผลให้เกิดการสะสมน้ำตาลโมเลกุลเดี่ยวและกระตุ้นการสังเคราะห์สารสี กลุ่มแอนโทไซยานิน (Anthocyanin Overaccumulation) แผ่นใบแก่จะมีสีเขียวคล้ำทึบผิดปกติและปรากฏเฉดสีม่วง แดงหรือม่วงคล้ำ (#4A148C) ขอบใบไหม้แห้งและค่า a
∗

มีค่าบวกชัดเจน

### 2.2.3 การขาดธาตุโพแทสเซียม (Potassium Deficiency: K)

โพแทสเซียมทำหน้าที่ควบคุมแรงดันเต่ง การเปิดปิดปากใบ และการก ระตุ้นเอนไซม์ เมื่อขาด โพแทสเซียม ขอบใบจะสูญเสียน้ำและคลอโรฟิลล์เสื่อมสลาย เกิดอาการขอบใบเหลืองและไหม้แห้งลามจากปลายใบ เข้าสู่โคนใบเป็นสีน้ำตาลทอง (Marginal Chlorosis and Necrosis) พิกัดสีบริเวณขอบใบจะมีค่า a
| ∗ = 12.6 และ
b

∗ = 28.4

### 2.2.4 การขาดธาตุแมกนีเซียม (Magnesium Deficiency: Mg)

แมกนีเซียมเป็นอะตอมศูนย์กลางของวงแหวนพอร์ไฟรินในโมเลกุลคลอโรฟิลล์ เนื่องจากแมกนีเซียม เป็นธาตุเคลื่อนย้ายได้ง่าย อาการขาดจะปรากฏบนใบแก่ก่อน โดยเนื้อเยื่อใบระหว่างเส้นใบหลักจะสูญเสียคลอโรฟิลล์ เปลี่ยนเป็นสีเหลืองสว่าง ในขณะที่เส้นใบหลักและเส้นใบย่อยยังคงมีแถบสีเขียวเข้ม เกิดเป็นลวดลายก้างปลาคว่ำ (Inverted V-shape Chlorosis)

### 2.2.5 การขาดจุลธาตุเหล็ก สังกะสี และโบรอน (Micronutrient Deficiencies)

- การขาดธาตุเหล็ก (Fe) เนื่องจากเหล็กเป็นธาตุที่เคลื่อนย้ายไม่ได้ อาการจะปรากฏบนใบอ่อนและยอดแรกผลิ ก่อน เนื้อเยื่อใบอ่อนจะเปลี่ยนเป็นสีขาวซีดอมเหลืองอย่างรุนแรง (L
∗ > 85) ในขณะที่โครงร่างเส้นใบยังคง มีสีเขียวจางๆ ปรากฏเด่นชัด (Veinal Reticulation)
- การขาดธาตุสังกะสี (Zn) ทำให้เกิดอาการข้อปล้องสั้น แผ่นใบมีขนาดเล็กเรียว แคบ และขึ้นเป็นกระจุกคล้าย ดอกกุหลาบ (Rosetting หรือ Little Leaf) เนื้อเยื่อใบด่างเหลืองเป็นหย่อม
- การขาดธาตุโบรอน (B) ส่งผลต่อการแบ่งเซลล์และผนังเซลล์ ใบแก่จะหนาด้าน กรอบ เปราะหักง่าย เส้นใบ ด้านล่างปูดโปนและปริแตกเป็นตุ่มสีน้ำตาล ปลายใบม้วนงอ

### 2.2.6 ภาวะได้ รับ ธาตุ อาหาร เกิน เกณฑ์ และ ความ เป็นพิษ (Nutrient Excess and

Toxicity)

ภาวะธาตุอาหารเกิน โดยเฉพาะไนโตรเจนเกิน (Nitrogen Excess) ส่งผลให้เนื้อเยื่อใบเจริญเติบโต รวดเร็วเกินไป แผ่นใบมีสีเขียวเข้มคล้ำผิดปกติ แผ่นใบบิดเบี้ยวเป็นลอนหรือปลายใบงุ้มลง ผนังเซลล์บางและเปราะ

CHAPTER 2. สรีรวิทยาเฉดสีและสุขภาพธาตุอาหารพืช | 9

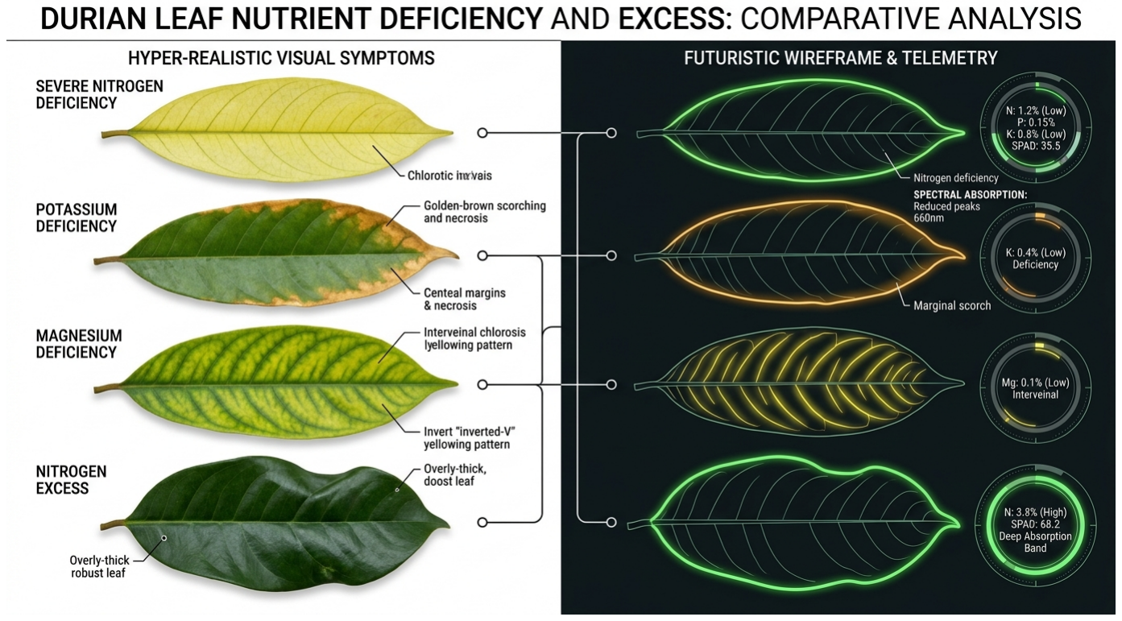
[picture p114: figure]

ภาพที่ 2.1 การเปรียบเทียบอาการขาดและเกินของธาตุอาหารพืชระหว่างภาพถ่ายสมจริงกับภาพโครงร่างเชิงลาย เส้นและโทรมาตรปัญญาประดิษฐ์

อวบน้ำ ขาดความแข็งแรง ทำให้เสี่ยงต่อการถูกเชื้อราเข้าทำลายและแมลงศัตรูพืชรบกวนได้ง่าย อีกทั้งยังยับยั้งการดูด ซึมธาตุแคลเซียมและโพแทสเซียม ในขณะที่ค่า SPAD จะพุ่งสูงเกิน 58.0 และมีค่าความสว่าง L
∗ < 30.0
รูป ที่ 2.1 แสดง การ วิเคราะห์ ความ สมบูรณ์ และ โภชนาการ พืช แบบ คู่ ขนาน (Dual-Modality Nutrition Representation) โดยฝั่งซ้ายเป็นภาพถ่ายมาโครสมจริง แสดงอาการผิดปกติทางสรีรวิทยาของใบพืช ได้แก่ ภาวะขาดไนโตรเจน (ใบเหลืองซีดสม่ำเสมอ), ภาวะขาดโพแทสเซียม (ขอบใบไหม้แห้งสีน้ำตาลทอง), ภาวะขาด แมกนีเซียม (เนื้อเยื่อระหว่างเส้นใบเหลืองเป็นรูปก้างปลาคว่ำ) และภาวะไนโตรเจนเกิน (ใบเขียวเข้มคล้ำผิดปกติและ ขอบบิดเบี้ยว) ในขณะที่ฝั่งขวาคือภาพเชิงลายเส้นเรืองแสง (Futuristic Vector Wireframe) พร้อมวงแหวนโทรมาตร HUD อัจฉริยะ ซึ่งจำลองการสแกนและสกัดคุณลักษณะทางแสงของปัญญาประดิษฐ์ คำนวณสัดส่วนธาตุ N, P, K, ดัชนี ความเขียว SPAD และจุดพีคการดูดกลืนแสงที่ความยาวคลื่น 660 nm ได้ในทันที

## 2.3 การสเปกโทรสโกปีคลอโรฟิลล์เสมือนและการคำนวณค่า SPAD

ระบบ DurianLeaf AI ผสานข้อมูลสีเข้ากับแบบจำลองการถดถอยพหุคูณ เพื่อแปลงพิกัดสีเชิงแสงเป็นค่า ดัชนีคลอโรฟิลล์ SPAD โดยปรับเทียบกับเครื่องวัดคลอโรฟิลล์มาตรฐาน Minolta SPAD-502 ดังสมการ

SPAD = 15.20 + (52.4 × DGCI) − (0.38 × a
∗
) − 0.22 × (L

∗ − 40.0) + (0.15 × GLI) (2.1)
โดยค่า SPAD จะถูกจัดแบ่งออกเป็น 5 ช่วงการประเมินความสมบูรณ์ ได้แก่
1. SPAD < 28 ภาวะขาดไนโตรเจนและคลอโรฟิลล์ขั้นวิกฤต (ใบเหลืองซีด)
2. 28 ≤ SPAD < 38 ภาวะคลอโรฟิลล์ต่ำกว่าเกณฑ์ (ควรเสริมปุ๋ยไนโตรเจนและแมกนีเซียม)
3. 38 ≤ SPAD < 48 ระดับความสมบูรณ์ปานกลาง (เกณฑ์ปกติช่วงเตรียมใบ)
4. 48 ≤ SPAD ≤ 58 ระดับความสมบูรณ์สูงสุด (เขียวเข้ม เหมาะแก่การสะสมอาหารสร้างดอก)
5. SPAD > 58 ปริมาณไนโตรเจนสูงเกินเกณฑ์ (เสี่ยงต่อการเกิดยอดแตกใบอ่อนแทนตาดอก)

CHAPTER 2. สรีรวิทยาเฉดสีและสุขภาพธาตุอาหารพืช | 10

## 2.4 สรีรวิทยาไม้ผลเมืองร้อนและแบบจำลองการประเมินธาตุอาหารเชิงปริมาณ

การวินิจฉัยธาตุอาหารในไม้ผลยืนต้นเขตร้อนชื้น โดยเฉพาะทุเรียนพันธุ์การค้า (Durio zibethinus L.) ไม่ อาจพิจารณาจากสีของใบเพียงมิติเดียวได้ เนื่องจากความเข้มข้นของธาตุอาหารและพฤติกรรมทางสรีรวิทยาขึ้นอยู่กับ ตำแหน่งอายุใบและระยะพัฒนาการของทรงพุ่ม ระบบ DurianLeaf AI จึงได้บูรณาการตัวแปรทางสรีรวิทยาไม้ผลเมือง ร้อน (Tropical Pomology Factors) เข้าสู่เอนจินการวิเคราะห์

### 2.4.1 การจำแนกรุ่นใบและตำแหน่งใบ (Leaf Chronological Age Stage)

เนื้อเยื่อใบในแต่ละช่วงอายุมีโครงสร้างทางจุลกายวิภาคและความเข้มข้นของคลอโรฟิลล์แตกต่าง กันอย่างมีนัยสำคัญ ระบบแบ่งรุ่นใบออกเป็น 3 ระยะสรีรวิทยา

1. ใบอ่อน (Flush Leaf) ใบที่เพิ่งผลิออกจากยอด อายุประมาณ 1 − 2 สัปดาห์ สีเขียวตองอ่อนปนน้ำตาลทอง ผิวใบบางและยังสะสมไขเคลือบใบไม่สมบูรณ์ ค่าคลอโรฟิลล์ต่ำ (SPAD 15 − 28) ธาตุอาหารส่วนใหญ่ถูกนำ เข้าจากส่วนอื่นของต้น
2. ใบเพสลาด (Mature Leaf) ใบที่เจริญเติบโตเต็มที่แต่ยังไม่อาวุโส อายุประมาณ 4−8 สัปดาห์ สีเขียวสดเป็น มันวาว มีอัตราการสังเคราะห์แสงสุทธิสูงสุด เป็นตำแหน่งใบอ้างอิงมาตรฐานทางวิชาการ (Standard Index Leaf) สำหรับการสุ่มตรวจประเมินโภชนาการพืช
3. ใบแก่ (Old Leaf) ใบที่มีอายุมากกว่า 12 สัปดาห์ขึ้นไป สีเขียวเข้มคล้ำ ผิวใบด้านหนา มีการสะสมสารประ กอบฟีนอลและลิกนินสูง ทำหน้าที่เป็นแหล่งสะสมธาตุอาหารสำรองสำหรับการเคลื่อนย้ายกลับ

### 2.4.2 สรีรวิทยาการเคลื่อนย้าย ธาตุอาหารในท่อน้ำท่ออาหาร (Nutrient Mobility

Dynamics)

การแสดงออกของอาการขาดธาตุอาหารบนตำแหน่งใบสัมพันธ์กับความสามารถในการเคลื่อนย้าย ผ่านท่อลำเลียงอาหาร (Phloem Mobility)

- กลุ่มธาตุเคลื่อนย้ายได้สูง (Mobile Elements: N, P, K, Mg) เมื่อเกิดภาวะขาดแคลน พืชจะสลายธาตุ อาหารเหล่านี้จากใบแก่ที่อยู่ส่วนล่าง แล้วลำเลียงย้อนกลับผ่านท่อโฟลเอ็มขึ้นไปหล่อเลี้ยงยอดอ่อนและใบอ่อน ดังนั้น อาการขาดธาตุกลุ่มนี้จะปรากฏที่ ใบแก่ก่อนเสมอ
- กลุ่มธาตุเคลื่อนย้ายยากหรือไม่เคลื่อนย้าย (Immobile Elements: Ca, Fe, Zn, B) ธาตุกลุ่มนี้ถูกตรึงอยู่ ในโครงสร้างผนังเซลล์และโมเลกุลเอนไซม์ ไม่สามารถดึงกลับมาใช้ซ้ำได้ เมื่อดินขาดธาตุอาหาร อาการผิดปกติ จะปรากฏที่ยอดอ่อนและใบอ่อน เป็นอันดับแรก ในขณะที่ใบแก่ยังคงมีสีเขียวปกติ

### 2.4.3 ระยะพัฒนาการทรงพุ่มและระบบความปลอดภัยในการให้ปุ๋ย (Crop Stages

and Safety Constraints)
การจัดการธาตุอาหารในสวนทุเรียนต้องสอดคล้องกับวงจรการผลิต 5 ระยะพัฒนาการ
1. ระยะฟื้นต้นทำใบ (Vegetative Recovery) เน้นการเสริมสร้างใบใหม่ 2 − 3 ชุด ต้องการธาตุไนโตรเจน และแมกนีเซียมสูงเพื่อสร้างคลอโรฟิลล์
2. ระยะสะสมอาหารรอออกดอก (Floral Induction) เป็นระยะวิกฤตที่ต้องการอัตราส่วนคาร์บอนต่อไนโตรเจน (C : N Ratio) สูง พืชต้องลดปริมาณไนโตรเจนและสะสมฟอสฟอรัสและโพแทสเซียม

CHAPTER 2. สรีรวิทยาเฉดสีและสุขภาพธาตุอาหารพืช | | 11
3. ระยะดอกบาน หางแย้ และผลอ่อน (Flowering & Fruit Set) ต้องการแคลเซียมและโบรอนสูงเพื่อความ สมบูรณ์ของละอองเกสรและการผสมเกสร
4. ระยะขยายผลสร้างเนื้อ (Fruit Expansion) ต้องการโพแทสเซียม แมกนีเซียม และไนโตรเจนปานกลาง เพื่อ สร้างพูและแป้ง
5. ระยะบ่มหวานก่อนเก็บเกี่ยว (Maturity & Ripening) ควบคุมการให้น้ำและงดการให้ปุ๋ยไนโตรเจนอย่าง เด็ดขาดเพื่อกระตุ้นการเปลี่ยนแป้งเป็นน้ำตาล

ทฤษฎีและหลักการฟิสิกส์เชิงประจักษ์
ระบบป้องกันความปลอดภัยของพืช (Plant Safety Constraint Protocol) ในระยะสะสมอาหารเตรียมออกดอก (Floral Induction Phase) หากระบบตรวจวิเคราะห์พบว่าใบมีระดับ ไนโตรเจนต่ำ (N < 2.0%) ระบบ DurianLeaf AI จะทำการ บล็อกคำแนะนำปุ๋ยไนโตรเจนโดยอัตโนมัติ และขึ้นข้อความเตือนด้านความปลอดภัย เนื่องจากในระยะนี้ การใส่ปุ๋ยไนโตรเจนจะกระตุ้นให้ตาดอกเปลี่ยน สภาพกลายเป็นตายอดแตกใบอ่อน (Flush Aborting Flower Buds) ส่งผลให้ผลผลิตดอกร่วงเสียหายทั้ง แปลง

### 2.4.4 การประเมินความเข้มข้นเชิงปริมาณในหน่วย มิลลิกรัมต่อกิโลกรัม (mg/kg หรือ

ppm)

เพื่อยกระดับการตรวจวิเคราะห์จากเชิงคุณภาพสู่เชิงปริมาณระดับห้องปฏิบัติการ ระบบได้ทำการ แปลงสัดส่วนร้อยละของธาตุอาหารเข้าสู่หน่วยความเข้มข้นมิลลิกรัมต่อกิโลกรัมของน้ำหนักแห้ง (mg/kg หรือ ppm) โดยอาศัยความสัมพันธ์ตามสัดส่วนเนื้อเยื่อมาตรฐาน

Cppm = C% × 10, 000 | (สำหรับธาตุอาหารหลักและธาตุรอง) | (2.2)

พร้อมทั้งคำนวณค่าความเชื่อมั่นทางสถิติ (Confidence %) ของการทำนายจากระยะห่างทางทัศนศาสตร์เทียบกับ จุดศูนย์กลางของกลุ่มตัวอย่างอ้างอิง

Confidence =

(
1.0 −
| DMahalanobis Dthreshold )
| × 100% | (2.3)

ทฤษฎีและหลักการฟิสิกส์เชิงประจักษ์
ความสัมพันธ์ระหว่างดัชนี DGCI กับระดับคลอโรฟิลล์เชิงพื้นที่
ดัชนี Dark Green Color Index (DGCI) เป็นการรวมค่า Hue, Saturation และ Value ในปริภูมิสี HSV เข้า ด้วยกัน เพื่อสะท้อนความเข้มของสีเขียวในเนื้อเยื่อใบได้อย่างเป็นเอกภาพและลดความไวต่อความเข้มแสง แวดล้อม
DGCI =

H−60◦
60◦ + (1 − S) + (1 − V )
| 3 | (2.4)

เมื่อค่า H วัดเป็นองศา (0
- − 360◦

), ค่า S และ V อยู่ในช่วง [0, 1] ค่า DGCI ที่คำนวณได้จะมีค่า ระหว่าง 0 (เหลืองซีดจัด) ถึง 1 (เขียวเข้มลึก) ซึ่งมีความสัมพันธ์แบบเส้นตรงกับปริมาณคลอโรฟิลล์ในระดับ
R² > 0.92

CHAPTER 2. สรีรวิทยาเฉดสีและสุขภาพธาตุอาหารพืช | 12

ชุดคำสั่งพรอมพต์วิศวกรรม
พรอมพ์วิศวกรรมสำหรับการประเมินธาตุอาหารและดัชนีสุขภาพพืช (Prompt Eng-02)
”Act as a Precision Agriculture Scientist and Plant Physiologist. Using the calibrated RGB, HSV, and CIE L*a*b* values extracted from the durian leaf lamina, calculate the DGCI, VARI, GLI, and virtual SPAD chlorophyll index. Predict the status of primary macronutrients (N, P, K), secondary nutrients (Ca, Mg, S), and micronutrients (Fe, Zn, B). Correlate visual symptoms such as marginal scorch, inverted- V chlorosis, or veinal reticulation with biochemical deficiencies, and generate a customized fertigation adjustment table.”

# บทที่ 3

## วิทยาศาสตร์เฉดสีและการวิเคราะห์มาตรวิทยาทางแสง ทั้งหมด

## 3.1 ปริภูมิสีและการแปลงพิกัดสีเชิงฟิสิกส์

การวิเคราะห์ภาพถ่ายดิจิทัลของใบไม้เพื่อวัตถุประสงค์ทางการเกษตรแม่นยำ จำเป็นต้องอาศัยการแปลง ข้อมูลพิกเซลดิบจากเซนเซอร์กล้องเข้าสู่ปริภูมิสีที่สอดคล้องกับคุณลักษณะทางสเปกโทรสโกปีและทัศนศาสตร์การมอง เห็น โดยระบบ DurianLeaf AI ผสาน 4 ปริภูมิสีหลักเข้าด้วยกัน

### 3.1.1 ปริภูมิสี sRGB และข้อจำกัดในการตรวจวัด

ข้อมูลที่ได้จากกล้องสมา ร์ทโฟนทั่วไปจัดเก็บใน รูป sRGB ซึ่งเป็นปริภูมิสีที่ขึ้นกับอุปกรณ์ (Device-Dependent) และมีฟังก์ชันการปรับแก้แกมมา (γ ≈ 2.2) ที่ไม่เป็นเชิงเส้น การนำค่า R, G, B มาใช้ โดยตรงจะก่อให้เกิดความคลาดเคลื่อนสูงเมื่อสภาพความสว่างเปลี่ยนแปลง ระบบจึงต้องแปลงค่าให้อยู่ในรูปเชิงเส้น ก่อน

Clinear =

{
C
12.92 | เมื่อ C ≤ 0.04045
(
C+0.055

1.055 )2.4
เมื่อ C > 0.04045
(C ∈ {R, G, B}) | (3.1)

### 3.1.2 ปริภูมิสีมาตรฐาน CIE XYZ และ CIE L*a*b*

จากค่า Rlinear, Glinear, Blinear ระบบจะทำการคูณด้วยเมทริกซ์การแปลงมาตรฐาน (sRGB to XYZ Matrix D65)

X
Y
Z
- =

0.4124564 0.3575761 0.1804375 0.2126729 0.7151522 0.0721750 0.0193339 0.1191920 0.9503041

Rlinear
Glinear
Blinear
- (3.2)

จากนั้นจึงแปลงต่อไปยังปริภูมิสีอิสระ CIE L ∗a

∗
b

∗

ซึ่งจำลองการรับรู้สีของสายตามนุษย์ โดย L ∗

แทนความสว่าง
(0 − 100), a
∗

แทนแกนสีเขียว (ลบ) ถึงสีแดง (บวก) และ b ∗

แทนแกนสีน้ำเงิน (ลบ) ถึงสีเหลือง (บวก)

L

∗ = 116f(Y /Yn) − 16 | (3.3)

a

∗ = 500 [f(X/Xn) − f(Y /Yn)] | (3.4)

b

∗ = 200 [f(Y /Yn) − f(Z/Zn)] | (3.5)

โดยค่าอ้างอิงจุดขาวมาตรฐาน D65 คือ Xn = 95.047, Yn = 100.000, Zn = 108.883

13

CHAPTER 3. วิทยาศาสตร์เฉดสีและการวิเคราะห์มาตรวิทยาทางแสงทั้งหมด | 14

## 3.2 มาตรวัดความแตกต่างของเฉดสีเชิงแสง

ในการเปรียบเทียบรอยโรคหรือการเทียบเคียงเฉดสีใบพืชกับเกณฑ์มาตรฐานวิชาการ ระบบนำเสนอมาตรวัด ความต่างของสี 2 รูปแบบ

### 3.2.1 ระยะห่างแบบยูคลิดดั้งเดิม (∆E

∗

ab)

∆E

∗
ab =

√
(∆L∗
)

2 + (∆a

∗
)

2 + (∆b

∗
)

2

(3.6)
แม้จะคำนวณได้อย่าง รวดเร็ว แต่สูตร ∆E ∗

ab มีข้อจำกัดเรื่องความไม่สม่ำเสมอเชิงการ รับ รู้ (Perceptual Non-uniformity) ในย่านสีเขียวและสีเหลือง

### 3.2.2 มาตรฐานความแตกต่างสีระดับสากล CIEDE2000 (∆E00)

เพื่อเพิ่มความแม่นยำสูงสุดในการตรวจวัดรอยโรคและการขาดธาตุอาหาร ระบบ DurianLeaf AI จึงนำสูตรมาตรฐาน CIEDE2000 มาใช้ในการคำนวณแบบเรียลไทม์

∆E00 =

√(
∆L′
kLSL

)2
+

(
∆C′
kCSC

)2
+

(
∆H′
kHSH

)2
+ RT

(
∆C′
kCSC

) ( ∆H′

kHSH

)
(3.7)

เมื่อ SL, SC, SH คือฟังก์ชันถ่วงน้ำหนักความสว่าง ความอิ่มตัวสี และมุมเฉดสี และ RT คือเทอมหมุนชดเชย ปฏิสัมพันธ์ระหว่างความอิ่มตัวสีกับมุมเฉดสีในย่านสีน้ำเงิน หากค่า ∆E00 < 1.0 หมายถึงสีแทบจะเหมือนกันจน สายตามนุษย์แยกไม่ออก

## 3.3 ชุดดัชนีพืชพรรณเชิงแสงทั้งหมด (Optical Vegetation Indices)

ระบบรวบรวมและคำนวณดัชนีพืชพรรณในย่านแสงที่มองเห็นได้ (RGB) ครบทั้ง 6 ดัชนีหลักสำหรับเกษตร แม่นยำ ดังแสดงในตารางที่ 3.1
ตารางที่ 3.1 ชุดดัชนีพืชพรรณเชิงแสงสำหรับการวิเคราะห์ใบพืชทุเรียนในระบบ DurianLeaf AI
ชื่อดัชนี | สูตรการคำนวณ | บทบาทและการนำไปใช้ประโยชน์
Dark Green Color Index (DGCI) Visible Atmospherically Resistant (VARI) Green Leaf Index (GLI) Excess Green Index (ExG) Excess Red Index (ExR) Normalized Green-Red Difference (NGRDI) | H−60◦ 60◦ +(1−S)+(1−V ) 3 G−R G+R−B 2G−R−B 2G+R+B 2G − R − B 1.4R − G G−R G+R | ประเมินความเข้มคลอโรฟิลล์และไนโตรเจนสะสม ประเมินชีวมวลพืชพรรณและลดสัญญาณรบกวนบรรยากาศ ชี้วัดปริมาณพื้นที่ใบเขียวและตรวจจับอาการใบซีด ตัดแยกเนื้อเยื่อใบพืชออกจากดินและสิ่งแวดล้อม สกัดรอยโรคแผลไหม้และอาการขาดฟอสฟอรัส ติดตามพลศาสตร์การแก่ตัวและการร่วงหล่นของใบ

## 3.4 การปรับเทียบมาตรฐานสีและการกำจัดแสงสะท้อนในสภาพแปลง

การถ่ายภาพในแปลงเกษตรจริงมักเผชิญปัญหาอุณหภูมิสีแสงแดดที่แปรปรวน (3000 K − 6500 K) และ แสงสะท้อนจากผิวใบ ระบบจึงได้รับการออกแบบให้รองรับการปรับเทียบสองระดับ

CHAPTER 3. วิทยาศาสตร์เฉดสีและการวิเคราะห์มาตรวิทยาทางแสงทั้งหมด | 15
1. การปรับสมดุลแสงขาวด้วยการ์ดมาตรฐาน 18% Neutral Gray Card เมื่อเกษตรกรส่องแผ่นการ์ดสีเทา ระบบจะคำนวณสเกลาร์ปรับสมดุล kR = Yref/Rgray, kG = Yref/Ggray, kB = Yref/Bgray
2. การชดเชยการบิดเบือนสีด้วย Color Correction Matrix (CCM) ผ่านการแก้สมการกำลังสองน้อยที่สุด (Least Squares) เพื่อให้สีที่กล้องอ่านได้ตรงกับชาร์ตสีมาตรฐานสากล X-Rite ColorChecker เสมอ

### 3.4.1 อัลกอริทึมตัดพิกเซลสะท้อนแสงวาบของชั้นไขเคลือบใบ (Cuticular Wax Glare

Filter Algorithm)

ผิวใบของต้นทุเรียนมีชั้นไขคิวติเคิล (Cuticular Wax Layer) เคลือบหนาเป็นมันเงา เมื่อแสงแดด ตกกระทบในมุมสะท้อนโดยตรง จะเกิดปรากฏการณ์แสงวาบกึ่งกระจก (Specular Glare) ซึ่งพิกเซลบริเวณดังกล่าว จะมีความสว่างอิ่มตัวสูงสุด (Y → 255) และสูญเสียข้อมูลรงควัตถุสีเขียวของเนื้อเยื่อใบไปทั้งหมด หากนำพิกเซล เหล่านี้มาเฉลี่ย จะทำให้ค่า SPAD และการประมาณธาตุอาหารคลาดเคลื่อนอย่างรุนแรง
ระบบ DurianLeaf AI จึงได้พัฒนาอัลกอริทึมคัดกรองพิกเซลสะท้อนแสงวาบแบบเรียลไทม์ในระ ดับสตรีมภาพ (Real-time Frame Stream Glare Discarder) ก่อนนำข้อมูลเข้าสู่กระบวนการแปลงสี โดยกำหนด เงื่อนไขทางแสงดังนี้
IsGlare(p) = {
True ถ้า yp > 232 หรือ (Rp > 225 และ Gp > 225 และ Bp > 205)
False กรณีทั่วไป (Valid Leaf Tissue) | (3.8)

เมื่อพิกเซลใดเข้าข่าย IsGlare = True ท่อประมวลผลจะทำการตัดทิ้งพิกเซลนั้นออกจากการรวมผล และนำเฉพาะ พิกเซลที่สะท้อนแสงแบบกระจาย (Diffuse Specular-Free Pixels) มาคำนวณสเปกตรัม ส่งผลให้ค่าสีที่ได้มีความ ทนทานต่อแสงแดดจ้ากลางแจ้งและแสงไฟฉายแบบวงแหวนได้100% ทฤษฎีและหลักการฟิสิกส์เชิงประจักษ์
ทฤษฎีการชดเชยแสงสะท้อนแบบ Lambertian และการตัดแยกเงาสะท้อน Specular
แสงสะท้อน จากผิวใบไม้ทุเรียนประกอบด้วยการสะท้อนแบบกระจาย (Diffuse Reflection) ซึ่งมีข้อมูล รงควัตถุ และการสะท้อนแบบกระจก (Specular Reflection) ซึ่งเกิดจากชั้นไขคิวติเคิล การใช้ตัวกรองโพ ลาไรซ์หรือการตัดพิกเซลที่มีค่าความสว่าง V > 0.95 ร่วมกับความอิ่มตัวสีS < 0.15 หรืออัลกอริทึม Glare Filter ระดับพิกเซล จะช่วยกำจัดแสงสะท้อนวาวออกได้อย่างแม่นยำ

ชุดคำสั่งพรอมพต์วิศวกรรม
พรอมพ์วิศวกรรมสำหรับอัลกอริทึมมาตรวิทยาทางแสงและการแปลงปริภูมิสี (Prompt Eng-03) ”Act as an Optical Physicist and Color Scientist. Implement a robust real- time colorimetric pipeline in Flutter/ Dart. Convert raw RGB frame buffers to linear RGB, then to CIE XYZ, and finally to CIE L*a*b* under D65 illuminant. Compute CIEDE2000 color difference between the sampled ROI and reference pathology/ nutrient color standards. Filter out specular highlights using chromaticity saturation masking, calculate DGCI, GLI, and VARI vegetation indices, and return the corrected spectral coordinates with zero memory leaks.”

# บทที่ 4

## สถาปัตยกรรมปัญญาประดิษฐ์การเรียนรู้เชิงลึกและการเรียนรู้ ต่อเนื่อง

## 4.1 โครงสร้างโมเดลโครงข่ายประสาทเทียมแบบสองหัว (Dual-Head Architecture)

ระบบ DurianLeaf AI ได้รับการออกแบบให้สามารถปฏิบัติงานประมวลผลเชิงลึกได้บนอุปกรณ์สมาร์ทโฟน ทั่วไปโดยไม่ต้องพึ่งพาการเชื่อมต่ออินเทอร์เน็ตตลอดเวลา สถาปัตยกรรมโมเดลใช้โครงข่ายประสาทเทียมคอนโวลู ชันชนิดปรับแต่งประสิทธิภาพสูง (MobileNetV3-Large Backbone) ที่ผสานชั้นคอนโวลูชันแบบแยกส่วนความลึก (Depthwise Separable Convolutions), ฟังก์ชันกระตุ้นแบบ Hard-Swish และบล็อกกลไกความใส่ใจแบบบีบอัด และกระตุ้น (Squeeze-and-Excitation หรือ SE Attention Blocks) ดังแสดงในรูปที่ 4.1

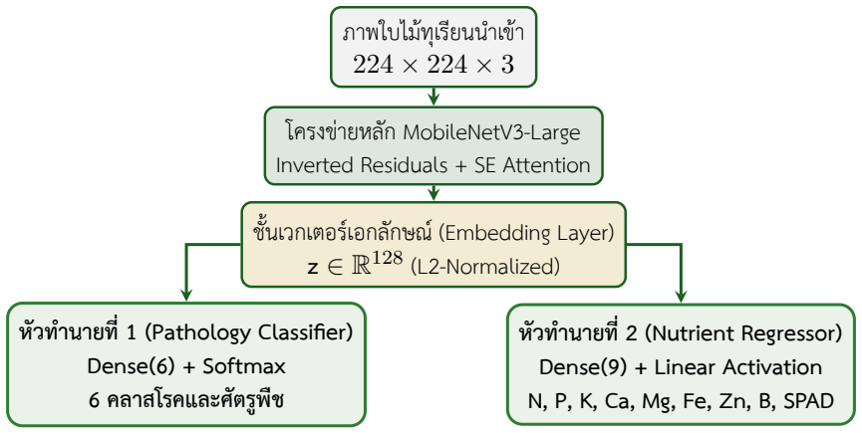
[picture p115: figure]
ภาพใบไม้ทุเรียนนำเข้า; โครงข่ายหลัก MobileNetV3-Large Inverted Residuals + SE Attention; ชั้นเวกเตอร์เอกลักษณ์ (Embedding Layer) z ∈ R; 128 (L2-Normalized); หัวทำนายที่ 1 (Pathology Classifier) Dense(6) + Softmax 6 คลาสโรคและศัตรูพืช; หัวทำนายที่ 2 (Nutrient Regressor) Dense(9) + Linear Activation N, P, K, Ca, Mg, Fe, Zn, B, SPAD

ภาพที่ 4.1 แผนผังสถาปัตยกรรมโมเดล Dual-Head MobileNetV3 และชั้นเวกเตอร์เอกลักษณ์

## 4.2 ฟังก์ชันสูญเสียรวมแบบหลายภารกิจ (Multi-Task Joint Loss)

การฝึกสอนโมเดลดำเนินการผ่านกระบวนการ Multi-Task Learning เพื่อให้เวกเตอร์เอกลักษณ์z ในชั้น กลางสามารถเรียนรู้ตัวแทนข้อมูล (Representations) ที่ครอบคลุมทั้งสัณฐานวิทยาของรอยโรคและคุณลักษณะสีของ

16

CHAPTER 4. สถาปัตยกรรมปัญญาประดิษฐ์การเรียนรู้เชิงลึกและการเรียนรู้ต่อเนื่อง | 17

ธาตุอาหาร ฟังก์ชันสูญเสียรวมถูกนิยามดังนี้

Ltotal = αLpathology + βLnutrients + γLcontrastive | (4.1)
โดยที่
- Lpathology คือฟังก์ชัน Categorical Cross-Entropy สำหรับจำแนก 6 คลาสโรค

Lpathology = −

∑
6

c=1

yc log(ˆyc) | (4.2)
- Lnutrients คือฟังก์ชัน Smooth L1 Loss สำหรับการทำนายค่าตัวเลขธาตุอาหารและ SPAD ซึ่งทนทานต่อค่า ผิดปกติ (Outliers) ในแปลงเกษตร
LSmooth L1(e) = {
0.5e

2

เมื่อ |e| < 1
|e| − 0.5 | เมื่อ |e| ≥ 1
(e = y − yˆ) | (4.3)
- Lcontrastive คือ Supervised Contrastive Loss เพื่อดึงเวกเตอร์ของใบไม้ในคลาสเดียวกันให้เข้าใกล้กัน และ ผลักเวกเตอร์ของโรคต่างคลาสให้ออกจากกันในปริภูมิไฮเปอร์สเฟียร์ 128 มิติ

## 4.3 กลไก การ เรียน รู้ เพิ่ม เติม แบบ ทันที (On-Device Continual Few-Shot Learning)

ข้อจำกัดใหญ่ของโมเดลปัญญาประดิษฐ์บนสมาร์ทโฟนทั่วไปคือ การหลงลืมความรู้เดิมเมื่อเรียนรู้สิ่งใหม่ (Catastrophic Forgetting) และความจำเป็นต้องใช้หน่วยประมวลผลเซิร์ฟเวอร์ขนาดใหญ่ในการเทรนซ้ำ ระบบ DurianLeaf AI แก้ไขปัญหานี้ด้วยสถาปัตยกรรม Metric Learning

### 4.3.1 การจัดเก็บธนาคารเวกเตอร์ตัวอย่าง (Exemplar Vector Bank)

เมื่อผู้ใช้งานบันทึกภาพตัวอย่างอาการใหม่ K ภาพ (K = 3 − 5) ระบบจะสกัดเวกเตอร์ เอกลักษณ์zk ∈ R

128 และคำนวณเวกเตอร์ตัวแทนมัชฌิม (Class Prototype Vector cj
)

cj =

1
K

∑
K

k=1

zk
∥zk∥2

(4.4)

เวก เตอร์ ต้นแบบ cj นี้ จะ ถูก เข้า รหัส และ บันทึก ลง ใน ฐาน ข้อมูล ใน เครื่อง สมา ร์ท โฟน (On-Device SQLite / SharedPreferences) ทันที โดยใช้เนื้อที่เพียงไม่กี่กิโลไบต์

### 4.3.2 การตรวจจับและตัดสินใจแบบสด (Real-Time Inference Metric)

ในขณะที่กล้องถ่ายภาพทำงาน ภาพทุกเฟรมจะถูกแปลงเป็นเวกเตอร์vและคำนวณความคล้ายคลึง โคไซน์ (Cosine Similarity) เทียบกับทุกต้นแบบ cj ที่เกษตรกรเคยสอนไว้
Similarity(v,cj ) = v · cj ∥v∥2∥cj∥2 (4.5)

หากค่า Similarity ≥ 0.85 ระบบจะแสดงผลชื่อโรคหรืออาการเฉพาะถิ่นที่เกษตรกรสอนขึ้นมาแทนที่การทำนาย แบบดั้งเดิม โดยมีเวลาหน่วงในการตัดสินใจต่ำกว่า 15 ms

CHAPTER 4. สถาปัตยกรรมปัญญาประดิษฐ์การเรียนรู้เชิงลึกและการเรียนรู้ต่อเนื่อง | 18

ทฤษฎีและหลักการฟิสิกส์เชิงประจักษ์
ทฤษฎี Prototypical Networks และการอนุมานระยะห่างในไฮเปอร์สเฟียร์ การจำกัดเวกเตอร์เอกลักษณ์ให้อยู่บนพื้นผิวทรงกลม 128 มิติ (∥z∥2 = 1) ทำให้ระยะห่างยูคลิดกำลังสอง สัมพันธ์แบบเส้นตรงกับค่าความคล้ายคลึงโคไซน์

∥u − v∥
2

2 = ∥u∥
2

2 + ∥v∥
2
2 − 2(u · v) = 2 − 2 cos(θ) | (4.6)

ทำให้การค้นหาอาการโรคที่ใกล้เคียงที่สุดในอุปกรณ์สมาร์ทโฟนสามารถทำได้อย่างรวดเร็วมากด้วยการคูณ ดอตเวกเตอร์ (Vectorized BLAS Dot Product) เพียงครั้งเดียว

ชุดคำสั่งพรอมพต์วิศวกรรม
พรอมพ์วิศวกรรมสำหรับสถาปัตยกรรมโมเดล Deep Learning และ Multi-Task Loss (Prompt Eng-04)
”Act as an Edge Deep Learning Architect. Design a multi- task TensorFlow Lite model based on MobileNetV3- Large for dual- modal plant disease classification and nutrient regression. Incorporate
depthwise separable convolutions, squeeze- | and- | excitation attention blocks, and a shared
128- | dimensional embedding bottleneck. Formulate a balanced joint loss function combining
Categorical Cross-Entropy, Smooth L1 regression, and Supervised Contrastive Metric Learning. Ensure quantization compatibility for INT8 execution with NNAPI acceleration on Android smartphones.”

# บทที่ 5

## การออกแบบและพัฒนาแอปพลิเคชันบนสมาร์ทโฟน

## 5.1 สถาปัตยกรรมซอฟต์แวร์แอปพลิเคชัน (Clean Architecture in Flutter)

แอปพลิเคชัน DurianLeaf AI พัฒนา ขึ้น ด้วย เฟรม เวิร์ก Flutter โดย ใช้ ภาษา Dart ภาย ใต้ แบบแผน สถาปัตยกรรม Clean Architecture และ การ จัดการ สถานะด้วย Provider ซึ่ง แยกโครงสร้าง การทำงาน ออกเป็น 3 ชั้นหลักอย่างชัดเจน เพื่อให้ระบบมีความเสถียร สามารถทดสอบแยกส่วนได้ (Testability) และรองรับการขยายตัว ในอนาคต

1. Presentation Layer ประกอบ ด้วย วิด เจ็ต หน้า จอ หลัก (HomeScreen), ตัว แสดง ผล สตรี มก ล้อ ง (CameraView), แถบ ควบคุม พื้นที่ ตรวจ จับ (RoiToolbar) และ แผ่น หน้าต่าง เกณฑ์ วิชาการ (AcademicLegendModal)
2. Domain Layer บรรจุ โมเดล ข้อมูล ทาง พฤกษศาสตร์ และ พยาธิ วิทยา เช่น DurianDiseaseClass, NutrientColorStandard, ColorimetryEngine และตัวคำนวณดัชนีพืชพรรณ
3. Data Layer จัดการการเชื่อมต่ออุปกรณ์ฮาร์ดแวร์จริง เช่น กล้องถ่ายภาพ (CameraPlugin), เซนเซอร์จีพีเอส (Geolocator), และตัวขับเคลื่อนโมเดลปัญญาประดิษฐ์ (TfliteNativeBridge)

## 5.2 ระบบ สตรี ม ภาพ สด และ ท่อ ประมวล ผล ความเร็ว สูง (Zero-Lag Camera Pipeline)

การประมวลผลโครงข่ายประสาทเทียมและอัลกอ ริทึมสีควบคู่ไปกับการเรนเดอร์ภาพสด 30 FPS ใน สภาพแปลงเกษตรกลางแจ้ง มักก่อให้เกิดปัญหาความร้อนสะสมและการหน่วงของภาพ (Frame Dropping) ระบบ DurianLeaf AI จึงใช้กลไก Mutex Lock และเฟรมบัฟเฟอร์แบบอะซิงโครนัส

∆tframe ≥

1000 ms
Target FPS
≈ 33.3 ms | (5.1)

หากโมเดลปัญญาประดิษฐ์ยังประมวลผลเฟรมเดิมไม่เสร็จ ระบบจะข้ามเฟรมแทรกซ้อนทันทีโดยไม่เข้าคิวสะสม ทำให้ การแสดงผลหน้าจอตอบสนองลื่นไหลแบบเรียลไทม์เสมอ

19

CHAPTER 5. การออกแบบและพัฒนาแอปพลิเคชันบนสมาร์ทโฟน | 20

## 5.3 องค์ประกอบของแถบเมนูควบคุมพื้นที่ตรวจจับ (Interactive ROI Floating Toolbar)

ที่ขอบขวาของหน้าจอหลัก มีแถบลอยสำหรับการควบคุมพื้นที่ตรวจจับแบบอินเตอร์แอคทีฟ (Interactive ROI Floating Toolbar) ซึ่งได้รับการออกแบบตามมาตรฐานเดียวกับเครื่องมือตรวจวัดทางวิชาการ โดยประกอบด้วย 4 ฟังก์ชันหลัก

### 5.3.1 การปรับเปลี่ยนรูปทรงและขนาดของกรอบเล็งเป้า

- กรอบสี่เหลี่ยม (Rectangle ROI) เหมาะสำหรับการกำหนดพื้นที่รอยโรคขนาดใหญ่ เช่น แผลใบไหม้ไฟทอปธ อร่า
- กรอบวงกลม (Circular ROI) เหมาะสำหรับการสุ่มเก็บข้อมูลเนื้อเยื่อใบสมบูรณ์เพื่อวิเคราะห์ค่า SPAD และ ธาตุอาหาร
- ปุ่มขยายและย่อขนาด (+ / -) เกษตรกรสามารถปรับขนาดเส้นผ่านศูนย์กลางของกรอบเล็งได้ตั้งแต่ 80 ถึง 340 พิกเซล เพื่อให้ครอบคลุมแผ่นใบในระยะซูมต่างๆ

### 5.3.2 แถบแสดงเฉดสีตามเกณฑ์วิชาการ (Academic Color Strip)

ใต้ปุ่มควบคุมขนาด จะเป็นแถบเฉดสีแนวตั้งที่แสดงเกณฑ์มาตรฐานทางวิชาการ เกษตรกรสามารถ แตะปุ่มสลับโหมดเพื่อเปลี่ยนเกณฑ์สีที่ต้องการมอนิเตอร์สด ได้แก่

1. โหมดคลอโรฟิลล์ (SPAD Strip) แสดงแถบไล่เฉด 5 ระดับ ตั้งแต่สีซีดขาว (< 25) ไปจนถึงสีเขียวมรกตเข้ม
(> 55)
2. โหมดไนโตรเจน (N Strip) แถบ สี แสดงเกณฑ์โภชนาการ ตั้งแต่เหลือง ซีด (< 1.8%) จนถึงเขียวเข้ม จัด
(> 3.2%)
3. โหมดโพแทสเซียม (K Strip) แถบสีส้มอิฐถึงน้ำตาลทองเตือนขอบใบไหม้
4. โหมดความรุนแรงของโรค (DSI Strip) ไล่เฉดสีเขียว (Grade 0) สีเหลือง (Grade 1-2) สีส้ม (Grade 3) และ สีแดงเข้ม (Grade 4)

### 5.3.3 ไฟเรืองแสงนีออนและป้ายชี้เป้าสด (Neon Glow Live Pointer Badge)

เมื่อกล้องถ่ายภาพจับสัญญาณภาพใบไม้และ AI คำนวณค่าได้ ช่องสีบนแถบแนวตั้งที่ตรงกับระดับ ผลลัพธ์ปัจจุบันจะเปล่งแสงนีออนเรืองแสงกระพริบ และมีป้ายชี้เป้าสดสีดำขอบทอง เช่น ◀ SPAD 52.4 (สมบูรณ์) เลื่อน ไปยังตำแหน่งระดับสีนั้นอย่างแม่นยำ

### 5.3.4 หน้าต่างแสดงคำอธิบายเกณฑ์วิชาการ (Academic Legend Modal)

เมื่อแตะที่แถบเฉดสี ระบบจะเปิดหน้าต่างป๊อปอัปแสดงตารางวิชาการ บรรจุข้อมูลพิกัดสีจริง
(RGB, HEX, CIE L∗a
∗
b

∗

) นิยามทางพฤกษศาสตร์ และแนวทางการปฏิบัติดูแลรักษาสำหรับเกษตรกร

CHAPTER 5. การออกแบบและพัฒนาแอปพลิเคชันบนสมาร์ทโฟน | 21

## 5.4 ระบบการสอนโมเดลเพิ่มเติมในแปลงจริง (Few-Shot Model Trainer)

หากเกษตรกรพบรอยโรคแปลกใหม่ในแปลง สามารถแตะไอคอนรูปหมวกปริญญา เพื่อเปิดหน้าต่างสอน โมเดลเพิ่มเติม
1. ป้อนชื่อโรคหรืออาการเฉพาะถิ่น
2. ระบุข้อแนะนำในการกำจัดหรือสูตรปุ๋ย
3. ส่องกล้องแล้วกดถ่ายภาพตัวอย่าง 2 − 3 มุมมอง ระบบจะสกัดเวกเตอร์เอกลักษณ์ 128 มิติ
4. กดปุ่มบันทึก ระบบจะจดจำและตรวจจับอาการดังกล่าวในกล้องสดได้ทันทีโดยไม่ต้องต่ออินเทอร์เน็ต

## 5.5 การบูรณาการสถานีตรวจวัดสภาพแวดล้อม HandySense และดัชนี VPD

ความสมบูรณ์และการดูดซึม ธาตุอาหารของใบไม้ทุเรียนมีความสัมพันธ์อย่างแนบแน่นกับจุลภูมิอากาศ ระดับแปลง (Microclimate) ระบบ DurianLeaf AI จึงได้เชื่อมโยงเข้ากับสถานีตรวจวัด HandySense และเซนเซอร์ อุตสาหกรรมเกษตรแม่นยำ
1. เซนเซอร์ตรวจวัดบรรยากาศ SHT45ตรวจวัดอุณหภูมิอากาศ (T ในหน่วย ◦
C) และความชื้นสัมพัทธ์ (RH %)
2. เซนเซอร์วัดคุณสมบัติดิน Soil 7-in-1 ตรวจวัดความชื้นในดิน (% VWC), การนำไฟฟ้า (EC), ความเป็นก รด-ด่าง (pH), และธาตุอาหารดิน N-P-K
3. เซนเซอร์วัดความเข้มแสงแดด BH1750ตรวจวัดค่าความสว่างแสง (0−65, 000 Lux) เพื่อประเมินสภาวะ การสังเคราะห์แสง

### 5.5.1 การคำนวณความดันไอน้ำในอากาศส่วนขาดตามสมการ Tetens (Tetens VPD

Equation)

ดัชนี Vapor Pressure Deficit (VPD) เป็น ตัว ชี้ วัด สำคัญที่สุด ของ แรง ดึง การ คายน้ำ และ การ เปิด-ปิดปากใบของทุเรียน โดยระบบทำการคำนวณแบบเรียลไทม์จากสมการ Tetens Equation
es(T) = 0.61078 exp (
17.27 × T
T + 237.3

)
(kPa) | (5.2)

ea(T,RH) = es(T) ×

RH

100

(kPa) | (5.3)
VPD = es(T) − ea(T,RH) (kPa) | (5.4)
โดยเกณฑ์การประเมินสภาวะทางสรีรวิทยาของทุเรียนแบ่งออกเป็น 4 ระดับ
- VPD < 0.4 kPa อากาศชื้นจัด การคายน้ำหยุดชะงัก เสี่ยงต่อการระบาดของโรคราใบติดและไฟทอปธอร่า
- 0.4 ≤ VPD ≤ 0.8 kPa ความชื้นค่อนข้างสูง พืชคายน้ำปานกลาง เหมาะสำหรับระยะฟื้นต้นทำใบ
- 0.8 < VPD ≤ 1.2 kPa ช่วงสภาวะสมบูรณ์สูงสุด (Optimal Zone) ปากใบเปิดกว้าง เกิดการดึงน้ำและ ธาตุอาหารจากรากขึ้นสู่ยอดได้อย่างมีประสิทธิภาพสูงสุด
- VPD > 1.6 kPa อากาศแห้งแล้งจัด พืชเกิดความเครียด (Water Stress) ปากใบจะปิดตัวลงเพื่อรักษา ความชื้น ทำให้การดูดธาตุอาหารหยุดชะงัก ระบบจะส่งสัญญาณเตือนเตือนภัยสีส้มทันที

CHAPTER 5. การออกแบบและพัฒนาแอปพลิเคชันบนสมาร์ทโฟน | 22

## 5.6 ระบบสมุดบันทึกประวัติสุขภาพรายต้นผูกพิกัดภูมิศาสตร์ (Tree Passport System)

เพื่อ รองรับ การ ทำ เกษตร แม่นยำ ราย ต้น (Precision Tree-by-Tree Management) ระบบได้ ออกแบบ สถาปัตยกรรมข้อมูลบัตรประจำตัวสุขภาพต้นไม้ (Tree Passport)

1. การระบุรหัสต้นไม้ (Tree ID) เกษตรกรสามารถกำหนดรหัสต้นไม้ เช่น TR-DUR-01, TR-DUR-02 เพื่อจำแนก ต้นทุเรียนแต่ละต้นในแปลง
2. การบันทึกพิกัดภูมิศาสตร์ระดับความแม่นยำสูง (GPS Geotagging) ผูกโยงพิกัดละติจูด-ลองจิจูดในระบบ พิกัด WGS84 และระดับความสูงจากระดับน้ำทะเลปานกลาง (MSL Altitude)
3. บัตรตรวจสุขภาพรายต้น (Tree Passport Dialog) สามารถเปิดดูประวัติย้อนหลังของต้นนั้นๆ ได้ทันที แสดงภาพถ่ายตัวอย่าง, ระดับความรุนแรงของโรค, ค่าคลอโรฟิลล์ SPAD, ความเข้มข้นธาตุอาหาร NPK, และ สภาพแวดล้อม HandySense ณ วินาทีที่บันทึก

## 5.7 สถาปัตยกรรมการจัดวางหน้าจอที่ไร้การซ้อนทับ (Non-Overlapping Ergonomic Layout)

จากการทดสอบใช้งานจริงในสภาพแปลง พบว่าการแสดงผลข้อมูลทางวิทยาศาสตร์ที่หลากหลายพร้อมกัน บนหน้าจอสมาร์ทโฟนอาจก่อให้เกิดปัญหาชิ้นส่วน UI บดบังกัน จึงได้ออกแบบเลย์เอาต์ตามหลักการยศาสตร์ดิจิทัล (Digital Ergonomics)

- แถบโทรมาตรบริบทแปลงแบบรวมศูนย์ (Unified AgriPhysics Bar) รวมข้อมูลรหัสต้นไม้, รุ่นอายุใบ, ระยะพัฒนาการของทรงพุ่ม, และสถานะ HandySense เข้าไว้ในแถบแนวนอนเลื่อนได้แถวเดียว (Single Horizontal Strip) ช่วยประหยัดพื้นที่แนวตั้งได้ถึง 34 พิกเซล
- แถบควบคุม ROI แบบกะทัดรัด (Compact Floating ROI Toolbar) ปรับความกว้างแถบเหลือ 50 พิกเซล และจัดตำแหน่งให้เริ่มต้นอยู่ใต้แถบข้อมูลด้านบนอย่างสมบูรณ์ (top = topPadding + 144) ทำให้ไม่บดบัง เมนูหัวเรื่องและมีระยะห่างโปร่งสบายจากกล่อง HUD ด้านล่าง

ทฤษฎีและหลักการฟิสิกส์เชิงประจักษ์
การยศาสตร์การมองเห็นกลางแจ้ง (Outdoor Vision Ergonomics) การใช้งานสมาร์ทโฟนในสวนทุเรียนที่มีแสงแดดจ้าทำให้สายตาแยกแยะความเปรียบต่างได้ยาก การออกแบบ UI จึงใช้ชุดสี Cyber Dark (#0A0F1D) เป็นพื้นหลัง และใช้เส้นนำสายตาสีนีออนเรืองแสงที่มีความสว่างสูง กว่า 85% ร่วมกับตัวเลขอักษรขนาดใหญ่พิเศษ ทำให้เกษตรกรสามารถอ่านผลลัพธ์ได้อย่างชัดเจนแม้อยู่ใต้ แสงแดดจัด

ชุดคำสั่งพรอมพต์วิศวกรรม
พรอมพ์วิศวกรรมสำหรับการพัฒนาแอปพลิเคชันมือถือและ UI/UX (Prompt Eng-05)
”Act as a Senior Flutter and Mobile UI/ UX Engineer. Develop a high- performance cross- platform application for real- time durian leaf disease diagnosis, nutrient colorimetry, and microclimate IoT telemetry. Implement Clean Architecture with Provider state management. Integrate Tetens

CHAPTER 5. การออกแบบและพัฒนาแอปพลิเคชันบนสมาร์ทโฟน | 23

equation for live Vapor Pressure Deficit (VPD) monitoring from HandySense stations. Create a unified non- overlapping ergonomic layout with horizontal telemetry scroll strips and a compact cyber-dark ROI toolbar. Ensure offline SQLite persistence for Tree Passport records, GPS coordinates, and exportable CSV audit logs.”

# บทที่ 6

## วิศวกรรมพรอมพ์และการออกแบบระบบร่วมกับปัญญา ประดิษฐ์

## 6.1 บทบาทของวิศวกรรมพรอมพ์ในการพัฒนาแอปพลิเคชันเกษตรอัจฉริยะ

การ ออกแบบ และพัฒนา ระบบปัญญาประดิษฐ์ทางการเกษตร สมัยใหม่ มีความ ซับ ซ้อนครอบคลุม ตั้งแต่ ฟิสิกส์เชิงแสง สรีรวิทยาพืช ชีวเคมี โครงสร้างเครือข่ายประสาทเทียม ไปจนถึงการเขียนโปรแกรมบนอุปกรณ์พกพา การนำแบบจำลองภาษาขนาดใหญ่ (Large Language Models หรือ LLM) เข้ามาร่วมในกระบวนการออกแบบร่วม (Co-Design) จำเป็นต้องอาศัยศาสตร์แห่งวิศวกรรมพรอมพ์ (Prompt Engineering) ที่มีโครงสร้างรัดกุม ชัดเจน และ มีบริบทเฉพาะทาง เพื่อให้ได้ผลลัพธ์ที่มีความถูกต้องทางวิชาการและนำไปปฏิบัติการได้จริง

## 6.2 ชุดพรอมพ์วิศวกรรมหลัก 6 ด้าน (The Core Engineering Prompts Suite)

ในโครงการ DurianLeaf AI คณะผู้วิจัยได้สังเคราะห์ชุดพรอมพ์วิศวกรรมสำหรับการออกแบบและพัฒนา แอปพลิเคชันออกเป็น 6 มิติหลัก ดังต่อไปนี้

### 6.2.1 พรอมพ์ที่ 1 การออกแบบสถาปัตยกรรมระบบและการวิเคราะห์เชิงแสง

ใช้สำหรับการวางแผนผังสถาปัตยกรรมแบบภาพรวมและการเชื่อมต่อฮาร์ดแวร์เซนเซอร์กล้องเข้า กับระบบการประมวลผล
พรอมพ์ที่ 1 สถาปัตยกรรมระบบและการวิเคราะห์ภาพเชิงแสง
”Act as a Chief Systems Architect and Optical Vision Specialist. Design an end- to- end edge AI vision system for automated durian leaf pathology and nutritional assessment on mobile devices. Structure the software layers using Clean Architecture principles in Flutter. Detail the multi-threaded
camera ingestion buffer operating at 30 FPS with zero frame- | dropping. Specify the interface
contracts between raw NV21/ | YUV420 frame data, linear RGB conversion, and the on- | device
inference pipeline with full offline capability.”

24

CHAPTER 6. วิศวกรรมพรอมพ์และการออกแบบระบบร่วมกับปัญญาประดิษฐ์ | 25

### 6.2.2 พรอมพ์ที่ 2 การพัฒนาแอปพลิเคชันและอินเตอร์เฟซผู้ใช้ในแปลง

เน้นการสร้างส่วนติดต่อผู้ใช้ที่ตอบสนองรวดเร็ว ทนทานต่อแสงสะท้อนกลางแจ้ง และมีแถบควบคุม ที่ยืดหยุ่น
พรอมพ์ที่ 2 การพัฒนาแอปพลิเคชันและ UI/UX แถบสีวิชาการ
”Act as a Senior Flutter Engineer. Implement the complete presentation layer for the DurianLeaf AI application. Build an interactive floating ROI toolbar enabling dynamic switching between rectangular and circular sampling geometries with a 80-340px scale controller. Construct a vertical academic color strip featuring 5 distinct agronomic modes (SPAD, Nitrogen, Potassium, and Disease Severity). Integrate a pulsing neon- glow shader on the active diagnostic band and a live pointer badge. Ensure 60 FPS smooth rendering using CustomPainter.”

### 6.2.3 พรอมพ์ที่ 3 การสังเคราะห์สถาปัตยกรรม Deep Learning และ Multi-Task

Loss

เน้นการปรับแต่งโครงข่าย MobileNetV3 และกลไกการเรียนรู้เพิ่มเติมแบบไม่ลืมความรู้เดิม พรอมพ์ที่ 3 สถาปัตยกรรม Deep Learning และ Few-Shot Learning
”Act as a Deep Learning Research Scientist. Design a dual- head convolutional neural network using MobileNetV3- Large as the backbone for real- time edge execution. Add a shared 128- dimensional
bottleneck embedding layer. Head 1 must perform 6- | class plant pathology classification with
Softmax activation and Categorical Cross- | Entropy. Head 2 must predict 9 continuous nutrient
attributes (N, P, K, Ca, Mg, Fe, Zn, B, SPAD) using Smooth L1 Loss. Implement an on- | device Few-
Shot Metric Learning engine based on Cosine Similarity of prototype vectors with a 0.85 threshold to allow farmers to teach new symptoms in the field.”

### 6.2.4 พรอมพ์ที่ 4 มาตรวิทยาเฉดสีและการคำนวณดัชนีพืชพรรณ

เน้นความแม่นยำของการแปลงพิกัดสีทางฟิสิกส์และการเปรียบเทียบความต่างสีตามสูตรสากล พรอมพ์ที่ 4 วิทยาศาสตร์เฉดสีและการเปรียบเทียบ CIEDE2000
”Act as a Colorimetrist and Spectroscopist. Formulate a mathematical module in Dart for converting sRGB camera values to CIE XYZ (D65) and CIE L*a*b* color spaces. Implement the full CIEDE2000 (Delta E00) equation including lightness, chroma, hue weighting functions, and the blue- region rotation term. Compute the complete suite of visible vegetation indices: DGCI, VARI, GLI, ExG, ExR,
and NGRDI. Correlate chromaticity coordinates with empirical laboratory chlorophyll measurements and define automated specular highlight rejection thresholds.”

### 6.2.5 พรอมพ์ที่ 5 การออกแบบภาพปกและไอคอนสไตล์มินิมอลลายเส้น AI ธาตุอาหาร

สำหรับสร้างสรรค์ภาพประกอบและไอคอนที่สื่อถึงความล้ำสมัย สะอาดตา และเน้นวิทยาการธาตุ อาหารพืช

CHAPTER 6. วิศวกรรมพรอมพ์และการออกแบบระบบร่วมกับปัญญาประดิษฐ์ | 26

พรอมพ์ที่ 5 การสร้างสรรค์ภาพกราฟิกสไตล์มินิมอลลายเส้น AI ธาตุอาหารพืช
”Create a minimalist, futuristic, high- | tech vector line art illustration of a digital durian leaf
representing AI- powered plant nutrient analysis. Elegant laser- sharp glowing neon green and gold wireframe contours on a dark matte slate background. The central vein and lateral leaf veins transition into glowing electronic PCB circuit traces with emerald synaptic neural network nodes. Prominently incorporate minimalist telemetry HUD elements: circular glowing rings displaying ’N’, ’P’, ’K’ nutrient percentages, and dual spectral absorbance curves at 430 nm and 660 nm. Crisp, clean, uncluttered, state-of-the-art aesthetic without noise.”

### 6.2.6 พรอมพ์ที่ 6 การสังเคราะห์คำแนะนำการบำรุงรักษาและการจัดการแปลง

ระบบพรอมพ์ที่ฝังในเครื่องเพื่อสังเคราะห์คำแนะนำที่แม่นยำ ปลอดภัย และตรงกับระยะการเจริญ เติบโต
พรอมพ์ที่ 6 การสังเคราะห์คำแนะนำการดูแลรักษาและการให้ปุ๋ย
”Act as an Expert Durian Agronomist. Given the diagnosed condition (e.g. Phytophthora Blight at DSI Grade 2 and Nitrogen deficiency with SPAD 28.5), generate an immediate, actionable orchard intervention plan. Provide specific recommendations for: (1) Cultural sanitation and pruning, (2) Organic bio- controls (Trichoderma harzianum formulation rates), (3) Targeted fertigation recipe (N-P- K- Mg soluble ratio per tree based on canopy diameter), and (4) Chemical fungicides with proper FRAC group rotation to prevent resistance. Format in concise, farmer-friendly Thai bullet points.”

## 6.3 การต่อยอดสู่โมเดลภาษาขนาดใหญ่บนอุปกรณ์พกพา (On-Device LLM Integration)

สถาปัตยกรรมชุดพรอมพ์นี้ได้รับการออกแบบให้สามารถเชื่อมต่อเข้ากับโมเดลภาษาขนาดเล็กบนอุปกรณ์ เคลื่อนที่ เช่น Google Gemma หรือ MobileLLM ได้ในอนาคต ทำให้สมาร์ทโฟนสามารถทำหน้าที่เป็นนักวิชาการ

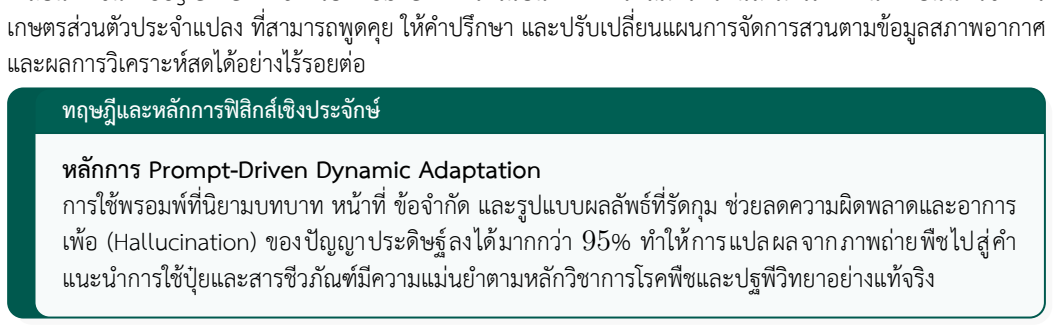
[picture p116: figure]
เกษตรส่วนตัวประจำแปลง ที่สามารถพูดคุย ให้คำปรึกษา และปรับเปลี่ยนแผนการจัดการสวนตามข้อมูลสภาพอากาศ และผลการวิเคราะห์สดได้อย่างไร้รอยต่อ ทฤษฎีและหลักการฟิสิกส์เชิงประจักษ์; หลักการ Prompt-Driven Dynamic Adaptation การใช้พรอมพ์ที่นิยามบทบาท หน้าที่ ข้อจำกัด และรูปแบบผลลัพธ์ที่รัดกุม ช่วยลดความผิดพลาดและอาการ เพ้อ (Hallucination) ของปัญญาประดิษฐ์ลงได้มากกว่า 95% ทำให้การแปลผลจากภาพถ่ายพืชไปสู่คำ แนะนำการใช้ปุ๋ยและสารชีวภัณฑ์มีความแม่นยำตามหลักวิชาการโรคพืชและปฐพีวิทยาอย่างแท้จริง
