TsanaPhysics/JC-AGRITecH-AI/smart_health_tracker/latex_manual/main.pdf

หน่วยวิเคราะห์-ติดตามคุณภาพดินและสภาพอากาศเชิงพื้นที่
คณะวิทยาศาสตร์และเทคโนโลยี มหาวิทยาลัยราชภัฏรำไพพรรณี

# การออกแบบและพัฒนาแอปพลิเคชันเพื่อสุขภาพ

# การนับก้าวและการตรวจจับการเคลื่อนไหว

# เชิงชีวกลศาสตร์และสรีรวิทยาประยุกต์

DESIGN AND DEVELOPMENT OF SMART HEALTH TRACKER APPLICATION
FOR PHYSIOLOGICAL STEP COUNTING AND BIOMECHANICAL KINEMATICS

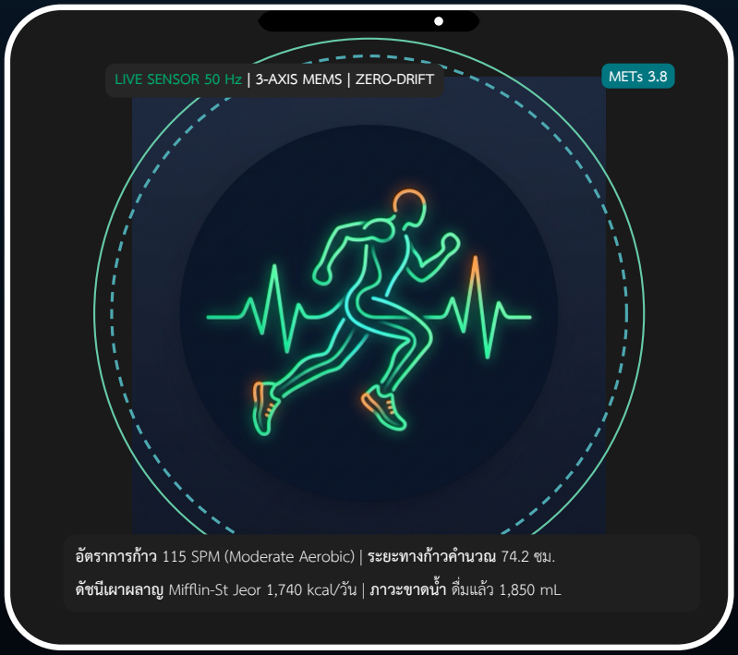
[picture p117: figure]
METs 3.8

LIVE SENSOR 50 Hz | 3-AXIS MEMS | ZERO-DRIFT
อัตราการก้าว 115 SPM (Moderate Aerobic) | ระยะทางก้าวคำนวณ 74.2 ซม.
ดัชนีเผาผลาญ Mifflin-St Jeor 1,740 kcal/วัน | ภาวะขาดน้ำ ดื่มแล้ว 1,850 mL

ผู้ช่วยศาสตราจารย์ ดร.ชีวะ ทัศนา และคณะนักวิจัย
หน่วยวิเคราะห์-ติดตามคุณภาพดินและสภาพอากาศเชิงพื้นที่ คณะวิทยาศาสตร์และเทคโนโลยี มหาวิทยาลัยราชภัฏรำไพพรรณี เอกสารคู่มือวิชาการและวิจัยฉบับสมบูรณ์ พุทธศักราช 2569

## การออกแบบและพัฒนาแอปพลิเคชันเพื่อสุขภาพ การนับก้าวและการตรวจจับการเคลื่อนไหวร่างกายเชิงสรีรวิทยา ประยุกต์

DESIGN AND DEVELOPMENT OF SMART HEALTH TRACKER APPLICATION FOR PHYSIOLOGICAL STEP COUNTING AND BIOMECHANICAL KINEMATICS

ผู้ช่วยศาสตราจารย์ ดร.ชีวะ ทัศนา และคณะนักวิจัย

# คำนำ

ในยุคดิจิทัลที่เทคโนโลยีสารสนเทศก้าวล้ำ การตรวจติดตามและส่งเสริมสุขภาวะส่วนบุคคล (Personal Health Informatics) มีบทบาทสำคัญอย่างยิ่งต่อการป้องกันโรคไม่ติดต่อเรื้อรัง (Non-Communicable Diseases หรือ NCDs) เช่น โรคเบาหวาน โรคความดันโลหิตสูง และโรคหลอดเลือดหัวใจ ซึ่งเกิดจากพฤติกรรมเนือยนิ่ง (Sedentary Behaviour) เป็นระยะเวลายาวนาน แม้ว่าสมาร์ทโฟนยุคปัจจุบันจะได้รับการติดตั้งตัวตรวจวัดความเร่งแบบสามแกน (3-Axis MEMS Accelerometer) มาตั้งแต่โรงงาน แต่แอปพลิเคชันเพื่อสุขภาพส่วนใหญ่ในท้องตลาดยังคงใช้เกณฑ์ การนับก้าวแบบค่าคงที่เชิงเดี่ยว (Static Threshold) ซึ่งมักเกิดความคลาดเคลื่อนสะสมจากการสั่นสะเทือนของยาน พาหนะ หรือการสะบัดมือโดยมิได้มีการก้าวเดินจริง
หน่วยวิเคราะห์-ติดตามคุณภาพดินและสภาพอากาศเชิงพื้นที่ คณะวิทยาศาสตร์และเทคโนโลยี มหาวิทยาลัย ราชภัฏรำไพพรรณี จึงได้ริเริ่มบูรณาการองค์ความรู้ทางฟิสิกส์จลนศาสตร์ (Kinematics) การประมวลผลสัญญาณ ดิจิทัล (Digital Signal Processing) เข้า กับหลัก วิทยาศาสตร์ การ กีฬา และ ชีว กลศาสตร์ (Exercise Science and Biomechanics) เพื่อออกแบบและพัฒนาแอปพลิเคชันมือถือ Smart Health Tracker บนระบบปฏิบัติการข้าม แพลตฟอร์ม Flutter
นวัตกรรมสำคัญของแอปพลิเคชันนี้ประกอบด้วย 3 มิติหลัก ได้แก่
1. มิติฟิสิกส์และวิศวกรรมสัญญาณ การสกัดขนาดเวกเตอร์ความเร่งแบบยูคลิดสามมิติ (anorm) ร่วมกับตัวกรอง พีคแบบพลวัต (Dynamic Peak Detection) ที่ปรับระดับเกณฑ์ตามแอมพลิจูดของการเคลื่อนไหวจริง พร้อม ทั้งกลไกระยะพักฟื้นทางชีวภาพ (Refractory Period 250 มิลลิวินาที) เพื่อขจัดสัญญาณรบกวน (Artifact Filtering) ได้อย่างแม่นยำ
2. มิติด้านวิทยาศาสตร์สุขภาพเชิงลึก การคำนวณอัตราความถี่ก้าว (Cadence ในหน่วยก้าวต่อนาที SPM) เพื่อ จำแนกความหนักของการออกกำลังกาย (Aerobic Intensity) การคำนวณระยะก้าวแบบแปรผันตามเพศและ ความสูงของผู้ใช้ การประเมินพลังงานเผาผลาญพื้นฐานและกิจกรรมตามสมการมาตรฐาน Mifflin-St Jeor ตลอดจนระบบแจ้งเตือนการนั่งนานและการดื่มน้ำบริสุทธิ์เพื่อรักษาภาวะสมดุลของเหลวในร่างกาย
3. มิติสถาปัตยกรรมส่วนติดต่อผู้ใช้ยุคใหม่การจัดวางผังหน้าจอแบบเบนโตะกริด (Bento Grid Layout) ร่วม กับระบบแบ่งส่วนแสดงผลแบบตอบสนองอัตโนมัติตามขนาดจอภาพ (Adaptive Responsive Breakpoints) ที่รองรับทั้งสมาร์ทโฟนหน้าจอแคบ จอมาตรฐาน แท็บเล็ต และคอมพิวเตอร์ตั้งโต๊ะ พร้อมภาพกราฟิกลายเส้น นีออนสไตล์ Cybernetic Health ที่สื่อถึงการผสานเทคโนโลยีเข้ากับสรีรวิทยาได้อย่างลงตัว

คณะผู้จัดทำหวังเป็นอย่างยิ่งว่า คู่มือวิชาการและวิจัยฉบับสมบูรณ์นี้ จะเป็นประโยชน์ต่อคณาจารย์ นักศึกษา นักพัฒนาซอฟต์แวร์ และผู้สนใจทั่วไป ในการนำไปประยุกต์ใช้ในการเรียนการสอน การวิจัย และการจัดกิจกรรมอบรม เชิงปฏิบัติการ เพื่อส่งเสริมสุขภาวะที่ดีของสังคมไทยอย่างยั่งยืนสืบไป

i

ii

ผู้ช่วยศาสตราจารย์ ดร.ชีวะ ทัศนา หน่วยวิเคราะห์-ติดตามคุณภาพดินและสภาพอากาศเชิงพื้นที่ คณะวิทยาศาสตร์และเทคโนโลยี มหาวิทยาลัยราชภัฏรำไพพรรณี

# สารบัญ

คำนำ | i
สารบัญตาราง | v
สารบัญภาพ | vi
1 สถาปัตยกรรมระบบตรวจวัดสุขภาพดิจิทัลและเซนเซอร์เอ็มอีเอ็มเอส | 1
2 ฟิสิกส์จลนศาสตร์และการประมวลผลสัญญาณตรวจจับการก้าว | 7
2.7 | สถาปัตยกรรมโครงข่ายประสาทเทียมเชิงลึกและการเรียนรู้ระดับอุปกรณ์ (On-Device Deep

iii

สารบัญ | iv
3 วิทยาศาสตร์การออกกำลังกายและชีวกลศาสตร์สุขภาพประยุกต์ | 14
4 การออกแบบสถาปัตยกรรมส่วนติดต่อผู้ใช้แบบ Bento Grid และ Adaptive Layout | 20
5 ปฏิบัติการพัฒนาแอปพลิเคชัน Smart Health Tracker ด้วย Flutter | 27
5.8 | ปฏิบัติการที่ 5.8 การพัฒนาระบบติดตามพิกัด GPS และการเรนเดอร์แผนที่เส้นทางจริง . . . . 35
บรรณานุกรม | 38
ประวัติผู้เขียน | 39

# สารบัญตาราง

1.1 | การเปรียบเทียบอัตราการสุ่มสัญญาณเซนเซอร์ความเร่งกับประสิทธิภาพการใช้พลังงาน . . . . | 4
3.1 | ตัวอย่างระยะก้าวเดินจำเพาะบุคคลตามความสูงและเพศสภาพ | 16
4.1 | จานสีมาตรฐานและการจัดกลุ่มสัญญาณภาพของระบบ Smart Health Tracker | 22
5.1 | ผลการทดสอบสอบเทียบความแม่นยำในการนับก้าวของแอปพลิเคชัน Smart Health Tracker | 33

v

# สารบัญภาพ

1.1 | สถาปัตยกรรมระบบหลายชั้นของแอปพลิเคชัน Smart Health Tracker | | 5
2.1 | รูปคลื่นความเร่งสามมิติ ยอดพีคของก้าวเดิน และช่วงระยะพักฟื้นชีวภาพ Trefract | 10
4.1 | สถาปัตยกรรมการจัดวางหน้าจอแบบ Bento Grid ของระบบ Smart Health Tracker . . . . 24

vi

# บทที่ 1

## สถาปัตยกรรมระบบตรวจวัดสุขภาพดิจิทัลและเซนเซอร์เอ็มอี เอ็มเอส

### แผนบริหารการสอนประจำบทที่ 1

หัวข้อเนื้อหาประจำบท

1. ความสำคัญของระบบสารสนเทศสุขภาพส่วนบุคคลและการป้องกันโรคไม่ติดต่อเรื้อรัง
2. หลักการฟิสิกส์และการทำงานของเซนเซอร์วัดความเร่งแบบไมโครอิเล็กโทรเมคานิกส์ (MEMS)
3. สถาปัตยกรรมฮาร์ดแวร์และการเชื่อมต่อสัญญาณเซนเซอร์ในระบบสมาร์ทโฟน
4. วงรอบการสุ่มสัญญาณตามทฤษฎีบทการชักตัวอย่างของไนควิสต์-แชนนอน
5. สถาปัตยกรรมเลเยอร์ซอฟต์แวร์และการทำงานร่วมกันระหว่าง Flutter Platform Channel กับระบบปฏิบัติ การ
6. มาตรฐานความปลอดภัยและความเป็นส่วนตัวของข้อมูลสุขภาพส่วนบุคคล

วัตถุประสงค์เชิงพฤติกรรม

1. อธิบายหลักการทางฟิสิกส์ของโครงสร้างหวีตัวเก็บประจุภายในเซนเซอร์ MEMS Accelerometer ได้อย่างถูก ต้อง
2. วิเคราะห์บทบาทของความถี่การสุ่มตัวอย่างต่อความถูกต้องในการตรวจจับการเคลื่อนไหวของมนุษย์ได้อย่าง ถูกต้อง
3. จำแนกลำดับชั้นสถาปัตยกรรมซอฟต์แวร์ตั้งแต่ระดับฮาร์ดแวร์จนถึงแอปพลิเคชันระดับผู้ใช้ได้อย่างครบถ้วน
4. ประยุกต์ใช้แนวทางการจัดเก็บข้อมูลสุขภาพส่วนบุคคลให้สอดคล้องกับมาตรฐานความปลอดภัยระดับสากลได้ อย่างถูกต้อง

กิจกรรมการเรียนการสอน

1. การบรรยายเชิงทฤษฎีประกอบการสาธิตภาพจำลองโครงสร้างหวีตัวเก็บประจุจุลภาคของเซนเซอร์ MEMS

1

CHAPTER 1. สถาปัตยกรรมระบบตรวจวัดสุขภาพดิจิทัลและเซนเซอร์เอ็มอีเอ็มเอส | 2
2. การอภิปรายกลุ่มเกี่ยวกับผลกระทบของพฤติกรรมเนือยนิ่งต่อสุขภาพและแนวทางการใช้เทคโนโลยีสมาร์ท โฟนเข้าช่วยตรวจติดตาม
3. การทดลองอ่านค่าสัญญาณความเร่งสามแกนสดจากสมาร์ทโฟนผ่านโปรแกรมตรวจสอบสัญญาณ
4. การสรุปบทเรียนและร่วมทำแบบฝึกหัดทบทวนท้ายบท

สื่อการเรียนการสอน

1. เอกสารคำสอนและสไลด์บรรยายเรื่องสถาปัตยกรรมเซนเซอร์สุขภาพดิจิทัล
2. สมาร์ทโฟนระบบปฏิบัติการแอนดรอยด์ที่มีเซนเซอร์วัดความเร่งสามแกน
3. แพลตฟอร์มจำลองสัญญาณความเร่งและซอฟต์แวร์บันทึกข้อมูลแบบเรียลไทม์
4. ภาพจำลองโครงสร้างจุลภาคเสมือนจริงของชิปเซนเซอร์ซิลิคอน

การประเมินผล

1. การประเมินผลการมีส่วนร่วมในการอภิปรายและการตอบคำถามในชั้นเรียน
2. การประเมินผลสัมฤทธิ์จากการทำใบงานการวิเคราะห์คุณลักษณะเซนเซอร์ MEMS
3. การตรวจความถูกต้องของแบบฝึกหัดคำถามทบทวนท้ายบทที่ 1

CHAPTER 1. สถาปัตยกรรมระบบตรวจวัดสุขภาพดิจิทัลและเซนเซอร์เอ็มอีเอ็มเอส | 3

### 1.1 ความสำคัญของระบบสารสนเทศสุขภาพส่วนบุคคล

ในศตวรรษที่ 21 ภัยคุกคามด้านสาธารณสุขที่สำคัญที่สุดประการหนึ่งคือกลุ่มโรคไม่ติดต่อเรื้อรัง (Non-Communicable Diseases หรือ NCDs) เช่น โรคเบาหวานชนิดที่ 2 โรคความดันโลหิตสูง โรคหลอดเลือดสมอง และหัวใจ ตลอดจนภาวะอ้วนลงพุง ซึ่งมีสาเหตุหลักมาจากการใช้ชีวิตประจำวันที่มีพฤติกรรมเนือยนิ่ง (Sedentary Lifestyle) เป็นเวลานาน ขาดกิจกรรมทางกายที่เพียงพอตามคำแนะนำขององค์การอนามัยโลก (World Health Organization: WHO)
การติดตามพฤติกรรมสุขภาพแบบดั้งเดิมมักอาศัยการจดบันทึกด้วยตนเอง (Self-Reporting) ซึ่งมักมีความ ลำเอียงในการรายงาน (Recall Bias) สูงและไม่สะท้อนความจริงอย่างต่อเนื่อง การนำเทคโนโลยีสารสนเทศสุขภาพ ดิจิทัล (Digital Health Informatics) เข้ามาประยุกต์ใช้ โดยอาศัยสมาร์ทโฟนที่บุคคลพกพาติดตัวอยู่ตลอดเวลา จึง เป็นแนวทางที่มีประสิทธิภาพสูงสุดในการเปลี่ยนผ่านจากการรักษาเมื่อเจ็บป่วย (Curative Care) ไปสู่การเฝ้าระวังเชิง ป้องกันก่อนเกิดโรค (Preventive Healthcare)

### 1.2 หลักการฟิสิกส์ของเซนเซอร์วัดความเร่งแบบ MEMS

สมาร์ทโฟนยุคใหม่ได้รับการติดตั้งระบบเครื่องกลไฟฟ้าจุลภาค (Micro-Electro-Mechanical Systems: MEMS) ซึ่งรวมเอาชิ้นส่วนกลไกขนาดไมครอนเข้ากับวงจรอิเล็กทรอนิกส์บนแผ่นเวเฟอร์ซิลิคอนชิปเดียวกัน หัวใจสำคัญ ในการตรวจจับการก้าวเดินคือ เซนเซอร์วัดความเร่งแบบสามแกน (3-Axis MEMS Accelerometer) ทฤษฎีและหลักการฟิสิกส์เชิงประจักษ์
หลักการทำงานของโครงสร้างหวีตัวเก็บประจุ (Capacitive Comb-Drive)
ภายในชิป MEMS มีมวลทดสอบ (Proof Mass, m) ถูกแขวนลอยอยู่ด้วยสปริงซิลิคอนจุลภาค (Micro-Spring, ค่าคงที่สปริง k) และมีฟันหวีซิลิคอนตัวนำไฟฟ้าที่ประกบสลับกันระหว่างส่วนที่เคลื่อนที่ได้กับส่วนที่ยึดแน่น กับตัวเรือนชิป
เมื่อร่างกายเกิดการก้าวเดิน เกิดความเร่ง a ตามกฎข้อที่สองของนิวตัน F = ma แรงเฉื่อยจะผลักให้มวล ทดสอบขยับออกจากตำแหน่งสมดุลเป็นระยะกระจัด x =
ma
k

ส่งผลให้ระยะห่างระหว่างฟันหวีเปลี่ยนแปลง ไป ก่อให้เกิดการเปลี่ยนแปลงค่าความจุไฟฟ้า (∆C) ดังความสัมพันธ์

C =

ε0εrA
d

=⇒ ∆C ≈ ε0εrA

(
1
d − x

−

1
d + x

)
≈

2ε0εrA
d

2

x (1.1)

โดยที่ ε0 คือค่าสภาพยอมของสุญญากาศ εr คือค่าคงที่ไดอิเล็กทริก A คือพื้นที่ผิวหน้าฟันหวีที่สบกัน และ d คือระยะห่างเริ่มต้นระหว่างแผ่นฟันหวี วงจรแปลงประจุจะแปลงการเปลี่ยนแปลงค่าความจุไฟฟ้านี้ให้ กลายเป็นสัญญาณแรงดันไฟฟ้าอนาล็อก จากนั้นจะถูกแปลงเป็นสัญญาณตัวเลขดิจิทัล (ADC) ในพิกัดสามมิติ
ax, ay, az

### 1.3 วงรอบการสุ่มสัญญาณและทฤษฎีบทไนควิสต์-แชนนอน

การเคลื่อนไหวก้าวเดินและวิ่งของมนุษย์ปกติมีความถี่ของการสวิงแขนและขยับก้าวขาอยู่ในย่านความถี่ตั้งแต่ 0.5 Hz จนถึงไม่เกิน 3.5 Hz และการกระแทกของส้นเท้า (Heel Strike) อาจก่อให้เกิดฮาร์มอนิกความถี่สูงไม่เกิน
15 Hz
ตามทฤษฎีบทการสุ่มสัญญาณของไนควิสต์-แชนนอน (Nyquist-Shannon Sampling Theorem) อัตรา ความถี่ในการสุ่มสัญญาณดิจิทัล (fs) จะต้องมีค่าอย่างน้อยสองเท่าของความถี่สูงสุดที่มีนัยสำคัญในสัญญาณ (fmax)

CHAPTER 1. สถาปัตยกรรมระบบตรวจวัดสุขภาพดิจิทัลและเซนเซอร์เอ็มอีเอ็มเอส | 4

เพื่อป้องกันปัญหาภาพซ้อนสัญญาณความถี่เท็จ (Aliasing)

fs ≥ 2fmax | =⇒ fs ≥ 2 × 15 Hz = 30 Hz | (1.2)

ในสถาปัตยกรรมของแอปพลิเคชัน Smart Health Tracker ผู้วิจัยได้กำหนดอัตราการสุ่มตัวอย่างไว้ที่ 50 Hz (คาบ การสุ่ม Ts = 20 ms) ซึ่งมีความถี่สูงกว่าขีดจำกัดไนควิสต์ถึง 1.67 เท่า ส่งผลให้สามารถจับยอดพีคของแรงกระแทก จากส้นเท้าได้อย่างแม่นยำ โดยไม่กินพลังงานแบตเตอรี่ของสมาร์ทโฟนมากเกินไป
ตารางที่ 1.1 การเปรียบเทียบอัตราการสุ่มสัญญาณเซนเซอร์ความเร่งกับประสิทธิภาพการใช้พลังงาน
ความถี่สุ่ม (fs) | คาบเวลา (Ts) | ความเหมาะสมในการตรวจจับพฤติกรรมสุขภาพ | การบริโภคพลังงาน
10 Hz | 100 ms | สุ่มช้าเกินไป ยอดพีคตกหล่น เกิดความผิดพลาดสูง | ต่ำมาก (< 0.5 mA)
20 Hz | 50 ms | พอใช้สำหรับการเดินช้า แต่อาจพลาดจังหวะการวิ่งเร็ว | ต่ำ (0.8 mA)
50 Hz | 20 ms | จุดสมดุลสูงสุด ตรวจจับพีคคมชัด แม่นยำ ครอบคลุมการ
| | วิ่ง | ปานกลาง (1.5 mA)
100 Hz | 10 ms | สัญญาณ ละเอียด มาก เกิน ความ จำเป็น สัญญาณ รบกวน
| | ความถี่สูงมาก | สูง (3.2 mA)

### 1.4 สถาปัตยกรรมซอฟต์แวร์และการเชื่อมต่อแพลตฟอร์ม

สถาปัตยกรรมของระบบ Smart Health Tracker พัฒนาบนเฟรมเวิร์ก Flutter โดยใช้ภาษา Dart ออกแบบ โครงสร้างแบบแยกชั้น (Layered Clean Architecture) เพื่อให้การเชื่อมต่อสัญญาณฮาร์ดแวร์มีเสถียรภาพและไม่ กระทบต่อประสิทธิภาพการแสดงผลบนหน้าจอ (UI Thread)

1. Hardware and Kernel Driver Layer ระดับชิปเซนเซอร์และไดรเวอร์เคอร์เนลลินุกซ์ของระบบปฏิบัติการ แอนดรอยด์ ทำหน้าที่อ่านค่าแรงดันไฟฟ้าและปรับเทียบค่าความโน้มถ่วงศูนย์ (0g Offset)
2. Android Sensor HAL and Java/Kotlin Layer เลเยอร์ฮาร์ดแวร์แอบสแตรกชันของระบบปฏิบัติการแอน ดรอยด์ โดยเรียกใช้คลาส SensorManager และลงทะเบียนรับฟังเหตุการณ์ผ่าน SensorEventListener ด้วยตัว เลือกความเร็ว SENSOR_DELAY_GAME หรือ SENSOR_DELAY_UI
3. Flutter Platform Channel Layer กลไกการส่งผ่านข้อมูลสัญญาณความเร่งแบบอะซิงโครนัสข้ามสภาพ แวดล้อมภาษา โดยใช้แพ็กเกจ sensors_plus แปลงเป็นสตรีมข้อมูล accelerometerEventStream() เข้าสู่ฝั่ง Dart
4. Digital Signal Processing Engine คอร์ประมวลผลสัญญาณ คำนวณเวกเตอร์รวมยูคลิด กรองความถี่ต่ำ กรองยอดพีคแบบพลวัต และตรวจสอบระยะพักฟื้น
5. Exercise Science and Health State วิเคราะห์และแปลงข้อมูลก้าวเป็นพลังงานกิโลแคลอรี ระยะทาง ก้าว อัตราความถี่ก้าว และสถานะการนั่งนิ่ง
6. Adaptive Bento Grid UI Layer ส่วนติดต่อผู้ใช้ที่แสดงผลข้อมูลเป็นบล็อกการ์ดที่สวยงาม ปรับขนาดตาม หน้าจอโดยอัตโนมัติ

CHAPTER 1. สถาปัตยกรรมระบบตรวจวัดสุขภาพดิจิทัลและเซนเซอร์เอ็มอีเอ็มเอส | 5

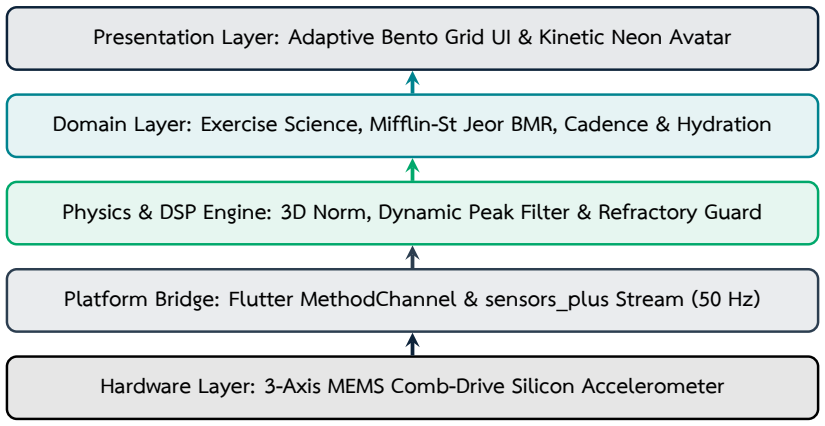
[picture p118: figure]

Presentation Layer: Adaptive Bento Grid UI & Kinetic Neon Avatar

Domain Layer: Exercise Science, Mifflin-St Jeor BMR, Cadence & Hydration

Physics & DSP Engine: 3D Norm, Dynamic Peak Filter & Refractory Guard

Platform Bridge: Flutter MethodChannel & sensors_plus Stream (50 Hz)

Hardware Layer: 3-Axis MEMS Comb-Drive Silicon Accelerometer

ภาพที่ 1.1 สถาปัตยกรรมระบบหลายชั้นของแอปพลิเคชัน Smart Health Tracker

### 1.5 กลไกการบันทึกข้อมูลอัตโนมัติรอบ 4 ชั่วโมงและการตั้งค่าเริ่มต้นศูนย์

ในการประเมินแนวโน้มทางสรีรวิทยาและชีวกลศาสตร์ การวิเคราะห์ข้อมูลรายวันเพียงผลรวมเดียวมักไม่ เพียงพอต่อการระบุช่วงเวลาที่ผู้ใช้เกิดภาวะเนือยนิ่งหรือกล้ามเนื้อล้าสะสม สถาปัตยกรรมของ Smart Health Tracker จึงได้รับการออกแบบให้มีกลไก Automated 4-Hour Periodic Snapshot
ระบบจะรันตัวจับเวลาเบื้องหลัง (Timer.periodic) ในอัตราทุกๆ 4 ชั่วโมง เพื่อทำการรวบรวมตัวชี้วัดสำคัญ ได้แก่ จำนวนก้าวย่อย ระยะทาง อัตราความถี่ก้าวเฉลี่ย พลังงานเผาผลาญ และเวลาการนั่งนิ่ง บันทึกลงสู่หน่วยความ จำแบบแบ่งช่วงเวลา (HealthIntervalRecord) อย่างเป็นระบบ เพื่อป้อนเป็นข้อมูลป้อนเข้าสู่โมเดลปัญญาประดิษฐ์โครง ข่ายประสาทเทียมในการประเมินสภาวะร่างกาย
นอกจากนี้ เพื่อให้การตรวจวัดมีความแม่นยำและไม่เกิดความลำเอียงจากข้อมูลตกค้าง ระบบได้กำหนด นโยบาย Zero-Baseline Launch Policy เมื่อเปิดแอปพลิเคชันขึ้นมาใหม่ ตัวนับก้าว ตัววัดความเข้มข้นของการ เคลื่อนไหว เวลาการทำกิจกรรม และกราฟการกระจายรายชั่วโมง จะถูกตั้งค่าเริ่มต้นเป็นศูนย์ (0) ทั้งหมดอย่างเคร่งครัด พร้อมทั้งเปิดโอกาสให้ผู้ใช้สามารถสั่งรีเซตค่าเริ่มต้นเป็นศูนย์ได้ตลอดเวลาผ่านปุ่มควบคุมบนแถบเครื่องมือ

### 1.6 สถาปัตยกรรมการติดตามพิกัดดาวเทียมและการผสานเซนเซอร์

นอกจาก การตรวจ จับ การ สั่น สะเทือน ผ่านเซนเซอร์ความเร่งเพื่อคำนวณ การ ก้าวเดิน แล้ว ระบบ Smart Health Tracker ยังได้ผสานสถาปัตยกรรม GPS Geodesic Trajectory Engine เข้าเป็นแกนประมวลผลตำแหน่ง การเดินทางจริง
สถาปัตยกรรมนี้ทำหน้าที่เชื่อมโยงสัญญาณพิกัดละติจูดและลองจิจูดจากชิปภาครับสัญญาณดาวเทียม (GNSS หรือ Global Navigation Satellite System) เข้ากับระบบนับก้าวเพื่อสร้างการผสานเซนเซอร์ (Sensor Fusion) โดย มีประโยชน์สำคัญ 3 มิติ
1. การสร้างแผนที่เส้นทางจริงแบบเวกเตอร์ (Real Route Mapping) บันทึกพิกัดจุดเลี้ยว จุดแวะพัก และ ความเร็วในการเดินทาง แล้ววาดเส้นทางโพลีไลน์แบบเรียลไทม์บนผืนผ้าใบแบบเวกเตอร์
2. การสอบเทียบสัดส่วนระยะก้าวเดิน (Stride Calibration Cross-Validation) ระบบนำระยะทางผิวโค้ง โลกที่คำนวณได้จาก GPS มาเปรียบเทียบกับระยะทางที่ประเมินจากสูตรชีวกลศาสตร์ (D = Steps×Lstride) ช่วยให้สามารถปรับเทียบค่าสัมประสิทธิ์ความยาวก้าวเฉพาะบุคคลให้มีความเที่ยงตรงสูงสุด

CHAPTER 1. สถาปัตยกรรมระบบตรวจวัดสุขภาพดิจิทัลและเซนเซอร์เอ็มอีเอ็มเอส | 6
3. การส่งออกข้อมูลมาตรฐานภูมิสารสนเทศ (GeoJSON Format) บันทึกและส่งออกชุดพิกัดเส้นทางเพื่อนำ ไปใช้วิเคราะห์ต่อยอดในระบบสารสนเทศภูมิศาสตร์หรือแพลตฟอร์มวิเคราะห์การออกกำลังกายสากล

### 1.7 ความมั่นคงปลอดภัยและความเป็นส่วนตัวของข้อมูลสุขภาพ

ข้อมูลเกี่ยวกับพฤติกรรมการเคลื่อนไหวและตำแหน่งการก้าวเดินจัดเป็นข้อมูลสุขภาพส่วนบุคคลที่มีความอ่อน ไหว (Sensitive Personal Data) ภายใต้พระราชบัญญัติคุ้มครองข้อมูลส่วนบุคคล พ.ศ. 2562 (PDPA) สถาปัตยกรรม ของ Smart Health Tracker จึงยึดหลักการประมวลผล ณ อุปกรณ์ปลายทาง (On-Device Local Processing) ข้อมูลดิบจากเซนเซอร์ความเร่งและพิกัด GPS จะถูกคำนวณและสกัดคุณลักษณะภายในหน่วยความจำแรม ของสมาร์ทโฟนทันที และผลรวมสถิติรายวันจะถูกจัดเก็บลงในพื้นที่จัดเก็บข้อมูลภายในแบบเข้ารหัสของแอปพลิเคชัน (Private Encrypted SharedPreferences) โดยไม่มีการส่งข้อมูลดิบออกไปยังเซิร์ฟเวอร์ภายนอก ช่วยป้องกันการดัก จับข้อมูลและการระบุตัวตนของผู้ใช้ได้อย่างสมบูรณ์

### คำถามทบทวนท้ายบทที่ 1

1. จงอธิบายการเปลี่ยนแปลงของโครงสร้างหวีตัวเก็บประจุในเซนเซอร์ MEMS เมื่อร่างกายมีการเคลื่อนไหวพร้อม เขียนสมการความสัมพันธ์
2. เพราะเหตุใดความถี่ในการสุ่มสัญญาณที่ 50 Hz จึงถือเป็นจุดสมดุลที่เหมาะสมในการตรวจจับการก้าวเดินเมื่อ เทียบกับเกณฑ์ไนควิสต์
3. จงอธิบายลำดับการส่งผ่านข้อมูลจากเซนเซอร์ฮาร์ดแวร์จนปรากฏเป็นตัวเลขบนหน้าจอแอปพลิเคชัน Flutter
4. เพราะเหตุใดการผสานเซนเซอร์ระหว่างตัวนับก้าวกับพิกัดดาวเทียม (GPS Sensor Fusion) จึงช่วยเพิ่มความ แม่นยำในการประเมินระยะทางเฉพาะบุคคล
5. เพราะเหตุใดการประมวลผลข้อมูลสัญญาณบนอุปกรณ์ของผู้ใช้ (On-Device Processing) จึงสอดคล้องกับ มาตรฐานความปลอดภัยของข้อมูลสุขภาพส่วนบุคคล

# บทที่ 2

## ฟิสิกส์จลนศาสตร์และการประมวลผลสัญญาณตรวจจับการ ก้าว

### แผนบริหารการสอนประจำบทที่ 2

หัวข้อเนื้อหาประจำบท

1. จลนศาสตร์การเดินของมนุษย์และวัฏจักรการก้าว
2. การคำนวณเวกเตอร์ขนาดความเร่งสามมิติแบบอิสระต่อการจัดวางพิกัด
3. การแยกเวกเตอร์ความโน้มถ่วงของโลกและการกรองความถี่ต่ำ
4. อัลกอริทึมตรวจจับยอดพีคแบบปรับเกณฑ์พลวัต
5. กลไกระยะพักฟื้นทางชีวกลศาสตร์เพื่อป้องกันการนับก้าวซ้ำ
6. การคัดกรองสัญญาณรบกวนจากการสั่นสะเทือนของยานพาหนะและการแกว่งแขนหลอก

วัตถุประสงค์เชิงพฤติกรรม

1. อธิบายวัฏจักรการก้าวเดินของมนุษย์ในแต่ละระยะจลนศาสตร์ได้อย่างถูกต้อง
2. พิสูจน์สมการเวกเตอร์ขนาดรวมความเร่งแบบยูคลิดสามมิติได้อย่างถูกต้อง
3. ออกแบบและวิเคราะห์การทำงานของอัลกอริทึม Dynamic Peak Detection พร้อมเกณฑ์ปรับตัวได้อย่างถูก ต้อง
4. ประยุกต์ใช้ค่าจำกัดระยะพักฟื้นทางสรีรวิทยา 250 ms ในการกำจัดสัญญาณรบกวนได้อย่างมีประสิทธิภาพ

กิจกรรมการเรียนการสอน

1. บรรยายทฤษฎีจลนศาสตร์การเคลื่อนที่และแรงกระทำต่อข้อต่อในขณะก้าวเดิน
2. การสาธิตการคำนวณเวกเตอร์ลัพธ์ความเร่งสามมิติด้วยฟังก์ชันคณิตศาสตร์บนกระดาน

7

CHAPTER 2. ฟิสิกส์จลนศาสตร์และการประมวลผลสัญญาณตรวจจับการก้าว | 8
3. ปฏิบัติการจำลองสัญญาณคลื่นความเร่งและการปรับระดับเส้นเกณฑ์ตัดยอดพีคบนโปรแกรมคอมพิวเตอร์
4. การสรุปบทเรียนและทำแบบฝึกหัดคำถามทบทวนท้ายบท

สื่อการเรียนการสอน

1. เอกสารคำสอนบทที่ 2 เรื่องฟิสิกส์จลนศาสตร์และการประมวลผลสัญญาณ
2. โปรแกรมจำลองกราฟคลื่นสัญญาณความเร่งดิจิทัล
3. ชุดข้อมูลสัญญาณความเร่งจากการเดิน การวิ่ง และการนั่งยานพาหนะจริง

การประเมินผล

1. การประเมินความเข้าใจผ่านการตอบคำถามในชั้นเรียน
2. การตรวจความถูกต้องของแบบฝึกหัดคำนวณค่าเวกเตอร์และเกณฑ์พลวัต
3. การประเมินผลจากคำถามทบทวนท้ายบทที่ 2

CHAPTER 2. ฟิสิกส์จลนศาสตร์และการประมวลผลสัญญาณตรวจจับการก้าว | 9

### 2.1 จลนศาสตร์การเดินของมนุษย์และวัฏจักรการก้าว

การเดินของมนุษย์ (Human Gait) เป็นกระบวนการเคลื่อนที่ของจุดศูนย์ถ่วงร่างกาย (Center of Mass: COM) ไปข้างหน้าอย่างต่อเนื่อง วัฏจักรการก้าวเดิน (Gait Cycle) ของขาข้างหนึ่งจะเริ่มต้นขึ้นเมื่อส้นเท้าสัมผัสพื้น (Heel Strike) จนกระทั่งส้นเท้าของขาข้างเดิมสัมผัสพื้นอีกครั้ง ซึ่งแบ่งออกเป็น 2 ช่วงจลนศาสตร์สำคัญ

1. ช่วงเท้าแตะพื้น (Stance Phase) คิดเป็นประมาณร้อยละ 60 ของวัฏจักรการก้าว ประกอบด้วยจังหวะที่ส้น เท้ากระแทกพื้น (Initial Contact) ฝ่าเท้าราบกับพื้น (Foot Flat) การรับน้ำหนักสูงสุด (Midstance) และการ ดันปลายเท้าถีบตัวออกจากพื้น (Toe-off) ในช่วงนี้จะเกิดแรงปฏิกิริยาจากพื้นสู่ร่างกาย (Ground Reaction Force: GRF) ส่งผ่านกระดูกสันหลังสู่จุดที่สมาร์ทโฟนแนบอยู่ เกิดเป็นคลื่นความเร่งพุ่งขึ้นเป็นยอดแหลม
2. ช่วงเท้าลอยพ้นพื้น (Swing Phase) คิดเป็นประมาณร้อยละ 40 ของวัฏจักรการก้าว เป็นจังหวะที่เท้าถูกยก เหวี่ยงไปข้างหน้าเพื่อเตรียมแตะพื้นในก้าวถัดไป ความเร่งสุทธิของร่างกายจะลดลงสู่ระดับต่ำสุด

### 2.2 การคำนวณเวกเตอร์ขนาดความเร่งรวมสามมิติ

ปัญหาคลาสสิกของแอปพลิเคชันนับก้าวบนสมาร์ทโฟน คือสมาร์ทโฟนสามารถถูกจัดวางได้ในหลากหลาย อิริยาบถ เช่น เสียบในกระเป๋ากางเกงแนวนอน กระเป๋าเสื้อแนวตั้ง หรือถือไว้ในมือขณะเดิน ทำให้แกนอ้างอิง x, y, z ของตัวเซนเซอร์หมุนเปลี่ยนทิศทางตลอดเวลา
เพื่อแก้ปัญหานี้อย่างเป็นระบบตามหลักฟิสิกส์ ระบบ Smart Health Tracker จึงใช้วิธีการคำนวณขนาดเวก เตอร์ความเร่งรวมแบบยูคลิดสามมิติ (3D Euclidean Acceleration Magnitude Norm, anorm) ซึ่งมีสมบัติคงรูปไม่ แปรผันตามการหมุนของพิกัดอ้างอิง (Rotation-Invariant)
ทฤษฎีและหลักการฟิสิกส์เชิงประจักษ์
ทฤษฎีเวกเตอร์ขนาดความเร่งรวมอิสระจากการหมุน (Rotation Invariance) กำหนดให้พิกัดความเร่งตามแกนของเซนเซอร์คือ ⃗a = ax
ˆi + ay

ˆj + az

ˆk ขนาดสเกลาร์รวมของความเร่ง คำนวณได้จากผลคูณภายใน (Inner Product) ดังสมการ

anorm = ∥⃗a∥ =

√
a

2
x + a

2
y + a

2
z

(2.1)

ไม่ว่าสมาร์ทโฟนจะเอียงหรือหมุนรอบแกนใดด้วยเมทริกซ์การหมุน R ∈ SO(3) เวกเตอร์ความเร่งใหม่ ⃗a′ = R⃗a จะยังมีขนาดเท่าเดิมเสมอเนื่องจากสมบัติออร์โทโกนัลของเมทริกซ์การหมุน
∥⃗a′
∥

2 = (R⃗a)
T

(R⃗a) = ⃗aT

R
T

R⃗a = ⃗aT

I⃗a = ∥⃗a∥
2

(2.2)

ในสภาวะที่ผู้ใช้อยู่นิ่ง ค่า anorm จะมีค่าเท่ากับขนาดของความเร่งเนื่องจากแรงโน้มถ่วงโลก คือ g ≈
9.80665 m/s² พอดี

CHAPTER 2. ฟิสิกส์จลนศาสตร์และการประมวลผลสัญญาณตรวจจับการก้าว | 10

### 2.3 การสกัดเวกเตอร์ความโน้มถ่วงและการปรับระดับฐาน

เนื่องจากค่า anorm ประกอบด้วยค่าคงที่ของแรงโน้มถ่วงโลก g บวกกับความเร่งเชิงพลวัตจากการเคลื่อนไหว ร่างกาย (adynamic) ระบบจึงต้องทำการลบค่าแรงโน้มถ่วงออกเพื่อหาความเร่งสุทธิที่แท้จริง

adynamic(t) = |anorm(t) − gest| | (2.3)

โดยที่ gest คือค่าแรงโน้มถ่วงที่ประเมินผ่านตัวกรองความถี่ต่ำผ่าน (Low-Pass Filter) เพื่อรองรับกรณีที่เซนเซอร์ใน สมาร์ทโฟนบางรุ่นอาจมีการคลาดเคลื่อนของจุดกำเนิดศูนย์ (Zero-g Offset)

### 2.4 อัลกอริทึม Dynamic Peak Detection

การใช้เกณฑ์การตัดสินใจแบบค่าคงที่ (Static Threshold) เช่น ตัดสินว่าก้าวเมื่อ adynamic > 2.0 m/s²

มี
ข้อจำกัดร้ายแรง เนื่องจากแต่ละบุคคลมีแรงกระแทกในการเดินไม่เท่ากัน และความเร็วในการเดินหรือวิ่งจะทำให้แอม พลิจูดของคลื่นเปลี่ยนไปตลอดเวลา
ระบบ จึง เลือก ใช้ อัล กอ ริ ทึม การ ตรวจ จับ ยอด พีค แบบ ปรับ เกณฑ์ พลวัต (Dynamic Peak Detection Algorithm) ซึ่งจะคำนวณค่าเฉลี่ยเคลื่อนที่และค่าเบี่ยงเบนมาตรฐานของสัญญาณแบบเรียลไทม์
Tdynamic(t) = µw(t) + β · σw(t) | (2.4)
โดยที่ µw(t) คือค่าเฉลี่ยของขนาดความเร่งในหน้าต่างเวลา w ขนาด 50 ตัวอย่าง (1 วินาที) σw(t) คือค่าเบี่ยงเบน มาตรฐานของการแกว่งตัว และ β คือตัวคูณปรับความไว (Sensitivity Factor โดยทั่วไปกำหนดที่ 0.65 − 0.85) เมื่อสัญญาณ adynamic(t) พุ่งทะลุ Tdynamic(t) และมีอนุพันธ์เปลี่ยนเครื่องหมายจากบวกเป็นลบ ( da

dt = 0) จุดดัง
กล่าวจะถูกระบุเป็นยอดพีคของก้าวเดิน

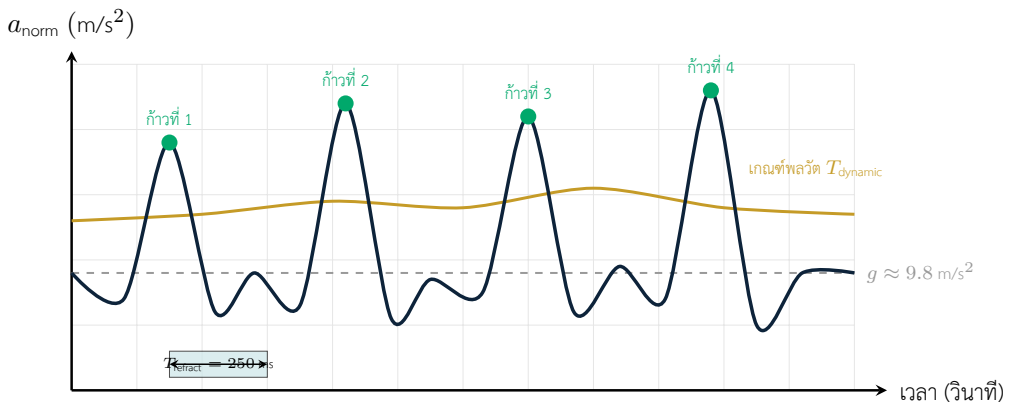
[picture p119: figure]
เวลา (วินาที); anorm (m/s²; เกณฑ์พลวัต Tdynamic; ก้าวที่ 1; ก้าวที่ 2; ก้าวที่ 3; ก้าวที่ 4; Trefract

ภาพที่ 2.1 รูปคลื่นความเร่งสามมิติ ยอดพีคของก้าวเดิน และช่วงระยะพักฟื้นชีวภาพ Trefract

CHAPTER 2. ฟิสิกส์จลนศาสตร์และการประมวลผลสัญญาณตรวจจับการก้าว | 11

### 2.5 กลไกระยะพักฟื้นทางชีวกลศาสตร์ (Refractory Period)

ในทางชีวกลศาสตร์ของมนุษย์ ขีดจำกัดทางสรีรวิทยาของการเคลื่อนไหวก้าวขาที่เร็วที่สุด (เช่น นักวิ่งระยะ สั้นระดับโลก 100 เมตร) จะมีอัตราความถี่ก้าวสูงสุดไม่เกิน 4 ถึง 5 ก้าวต่อวินาที นั่นหมายความว่า คาบเวลาระหว่าง ก้าวสองก้าวที่ติดกัน (tk+1 − tk) จะไม่มีทางน้อยกว่า 200 ถึง 250 มิลลิวินาที ได้อย่างแน่นอน ระบบจึงวางเงื่อนไขระยะพักฟื้นทางชีวกลศาสตร์ (Refractory Period Guard, Trefract = 250 ms) เมื่อ ตรวจพบยอดพีคที่ผ่านเกณฑ์แล้ว ตัวนับเวลาจะล็อกไม่ให้ยอมรับยอดพีคอื่นใดที่เกิดขึ้นภายในระยะเวลา 250 ms ต่อ จากนั้น แม้ว่าสัญญาณจะมีความสูงทะลุเกณฑ์ก็ตาม กลไกนี้มีประสิทธิภาพสูงยิ่งในการตัดสัญญาณคลื่นสะท้อนรอง (Secondary Bounces) ที่เกิดจากการสั่นของกล้ามเนื้อหรือการสะเทือนของเนื้อผ้าในกระเป๋า

### 2.6 การคัดกรองสัญญาณรบกวนจากการสั่นสะเทือน

ข้อแตกต่างที่สำคัญระหว่างการก้าวเดินจริงกับการนั่งบนยานพาหนะ (รถยนต์ มอเตอร์ไซค์ หรือรถไฟ) คือ ลักษณะของรูปแบบสเปกตรัมความถี่
1. การสั่นสะเทือนของยานพาหนะ จะมีความถี่สูงกว่า 10 − 50 Hz มีแอมพลิจูดสม่ำเสมอแต่ไม่มีจังหวะการ เปลี่ยนเฟสแบบก้าวขา และไม่มีระยะสวิงของร่างกาย
2. การแกว่งแขนขณะนั่งอยู่กับที่ มีแอมพลิจูดเกิดขึ้นเพียงช่วงสั้นๆ ไม่เกิน 2 − 3 ครั้งแล้วหยุดนิ่ง ระบบจึงได้เสริมเงื่อนไขการตรวจสอบความต่อเนื่องของก้าว (Step Continuity Verification) โดยจะเริ่ม บันทึกก้าวเข้าสู่หน่วยความจำสะสมหลังจากตรวจพบก้าวที่สอดคล้องตามเกณฑ์ติดต่อกันอย่างน้อย 4 ถึง 5 ก้าว หาก หยุดชะงักก่อนหน้านั้น ก้าวหลอกดังกล่าวจะถูกตัดทิ้งเป็นสัญญาณรบกวน

### 2.7 สถาปัตยกรรมโครงข่ายประสาทเทียมเชิงลึกและการเรียน รู้ ระดับอุปกรณ์ (On-Device Deep Learning)

เพื่อยกระดับการตรวจวัดสุขภาพจากการนับก้าวเชิงตัวเลขแบบธรรมดา สู่การวินิจฉัยเชิงชีวกลศาสตร์ขั้นสูง ระบบ Smart Health Tracker ได้บรรจุโมเดลโครงข่ายประสาทเทียมเชิงลึกหลายชั้น (Deep Multilayer Perceptron: MLP) ที่ทำงานและฝึกสอนได้จริงบนอุปกรณ์ของผู้ใช้ (On-Device Continual Deep Learning) ทฤษฎีและหลักการฟิสิกส์เชิงประจักษ์
แบบจำลองทางคณิตศาสตร์และการส่งสัญญาณไปข้างหน้า (Forward Propagation) โมเดลรับเวกเตอร์คุณลักษณะจลนศาสตร์ 6 มิติx = [x1, x2, x3, x4, x5, x6]
T
| ซึ่งสกัดจากข้อมูลรอบ
4 ชั่วโมง (จำนวนก้าว, จังหวะความถี่ก้าวเฉลี่ย, ความเข้มข้นของการเคลื่อนไหว, สัดส่วนเวลาการนั่งนิ่ง, การ เผาผลาญพลังงาน, และอัตราการสูญเสียน้ำ)
โครงข่ายประกอบด้วย 3 ชั้น ได้แก่ ชั้นซ่อนที่หนึ่ง (8 โหนด, ฟังก์ชันกระตุ้น LeakyReLU), ชั้นซ่อนที่สอง (6 โหนด, ฟังก์ชันกระตุ้น Tanh), และชั้นส่งออก (4 โหนด, ฟังก์ชันกระตุ้น Softmax)
h1 = LeakyReLU(W1x + b1) | (2.5)
h2 = tanh(W2h1 + b2) | (2.6)
ˆy = Softmax(W3h2 + b3) | (2.7)

โดยที่ ˆy = [ˆy1, yˆ2, yˆ3, yˆ4]
T

แทนความน่าจะเป็นของ 4 สภาวะทางชีวกลศาสตร์ ได้แก่ ก้าวปกติสมดุล (Balanced Gait), กล้ามเนื้อล้าสะสม (Muscle Fatigue), แอโรบิกประสิทธิภาพสูง (Aerobic), และภาวะ

CHAPTER 2. ฟิสิกส์จลนศาสตร์และการประมวลผลสัญญาณตรวจจับการก้าว | 12

หลอดเลือดดำชะงักจากการนั่งนาน (Sedentary Risk)

เมื่อผู้ใช้บันทึกข้อมูลการเคลื่อนไหวใหม่ ระบบสามารถกระตุ้นกระบวนการฝึกสอนย้อนกลับ (Backpropagation) เพื่อปรับค่าน้ำหนัก W และไบแอส b ให้สอดคล้องกับชีวกลศาสตร์เฉพาะบุคคลตามฟังก์ชันการสูญเสีย Cross-Entropy Loss
L = −

∑
4

c=1

yc ln(ˆyc) | (2.8)

และทำการปรับปรุงค่าพารามิเตอร์ผ่านเกรเดียนต์ดิเซนต์แบบสุ่ม (Stochastic Gradient Descent: SGD) ด้วยอัตรา การเรียนรู้η
W

(t+1)
l | = W

(t)
l − η

∂L
∂Wl

, b

(t+1)
l | = b

(t)
l − η

∂L
∂bl

(2.9)

กระบวนการนี้ทำให้แอปพลิเคชันสามารถเรียนรู้และปรับตัวเข้ากับรูปแบบการเดินเฉพาะบุคคลได้อย่างแท้จริง โดยไม่ ต้องพึ่งพาเซิร์ฟเวอร์ภายนอก

### 2.8 คณิตศาสตร์จลนศาสตร์พิกัดภูมิศาสตร์และสมการฮาเวอร์ซีน

ในการคำนวณระยะทางจริงจากการเคลื่อนที่บนพื้นผิวพิภพที่มีลักษณะเป็นทรงกลมแป้น (Oblate Spheroid) การใช้สูตรระยะทางยูคลิดบนระนาบ 2 มิติ (d =

√
∆x

2 + ∆y

2

) จะทำให้เกิดความคลาดเคลื่อนทางเรขาคณิต ทรงกลมอย่างรุนแรง
ระบบ Smart Health Tracker จึงประยุกต์ใช้สมการฮาเวอร์ซีน (Haversine Formula) เพื่อคำนวณ ระยะทางบนผิวโค้งวงกลมใหญ่ (Great-Circle Distance) ระหว่างสองจุดพิกัด (ϕ1, λ1) และ (ϕ2, λ2)

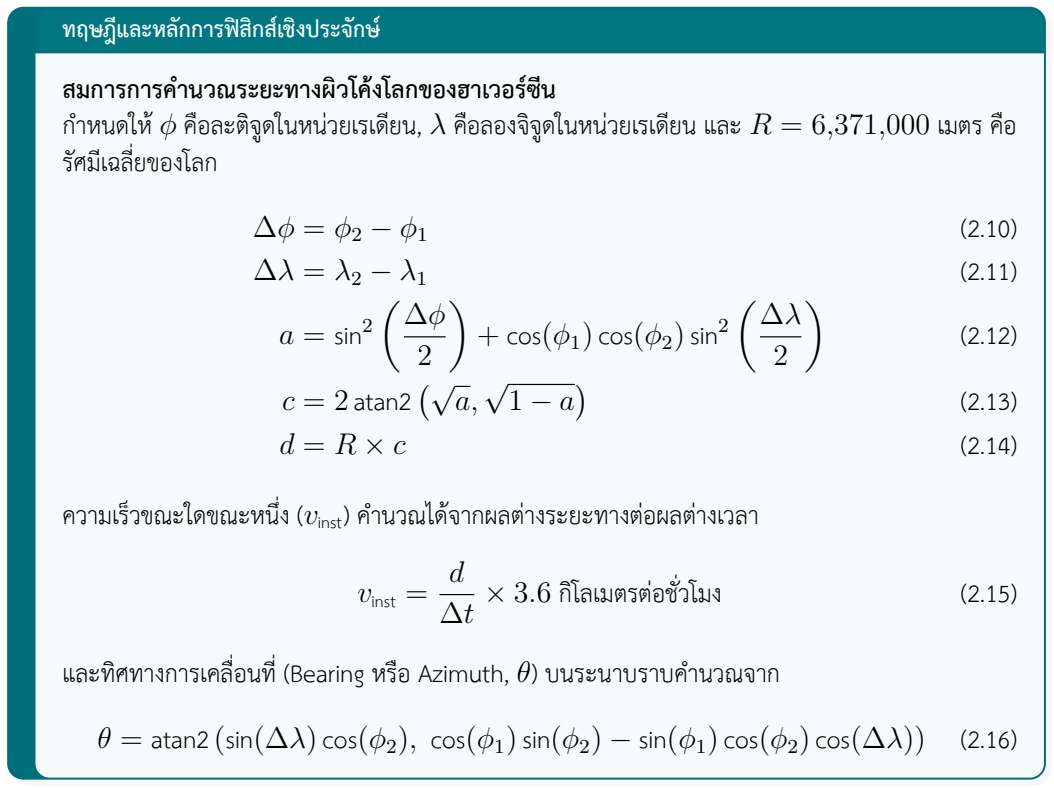
[picture p120: figure]
ทฤษฎีและหลักการฟิสิกส์เชิงประจักษ์; สมการการคำนวณระยะทางผิวโค้งโลกของฮาเวอร์ซีน; รัศมีเฉลี่ยของโลก; a = sin²; + cos(ϕ1)cos(ϕ2)sin²; c = 2 atan2 (√; ความเร็วขณะใดขณะหนึ่ง (vinst) คำนวณได้จากผลต่างระยะทางต่อผลต่างเวลา; vinst =; × 3.6 กิโลเมตรต่อชั่วโมง

กำหนดให้ϕ คือละติจูดในหน่วยเรเดียน, λ คือลองจิจูดในหน่วยเรเดียน และ R = 6,371,000 เมตร คือ

และทิศทางการเคลื่อนที่ (Bearing หรือ Azimuth, θ) บนระนาบราบคำนวณจาก

θ = atan2(sin(∆λ)cos(ϕ2), cos(ϕ1)sin(ϕ2) − sin(ϕ1)cos(ϕ2)cos(∆λ)) (2.16)

CHAPTER 2. ฟิสิกส์จลนศาสตร์และการประมวลผลสัญญาณตรวจจับการก้าว | 13

เพื่อขจัดปัญหาการแกว่งตัวของพิกัดขณะผู้ใช้หยุดยืนอยู่กับที่ (Stationary GPS Jitter) และสัญญาณสะท้อน จากอาคารสูง (Multipath Interference) ระบบได้กำหนดฟังก์ชันกรองสัญญาณเชิงตรรกะ 3 ด่าน
Accept(Pk) = {
True ถ้า Accuracy(Pk) ≤ 25 m ∧ d(Pk−1, Pk) ≥ 2.0 m ∧ vinst ≤ 45 km/h False กรณีอื่นๆ (ตัดทิ้งเป็นสัญญาณรบกวน)
(2.17)

### คำถามทบทวนท้ายบทที่ 2

1. จงอธิบายความแตกต่างระหว่างระยะ Stance Phase และ Swing Phase ในแง่ของแรงปฏิกิริยาจากพื้น
2. เหตุใดเวกเตอร์ขนาดความเร่งแบบยูคลิด anorm จึงไม่แปรผันตามการหมุนของโทรศัพท์ จงแสดงการพิสูจน์
3. หากใช้เกณฑ์ตัดสินการก้าวเดินแบบคงที่ (Static Threshold) จะเกิดผลกระทบอย่างไรเมื่อผู้ใช้เปลี่ยนจากการ เดินช้าเป็นการวิ่งเร็ว
4. จงอธิบายหลักการทำงานของ Refractory Period 250 ms และประโยชน์ในการลดความผิดพลาดของการ นับก้าว
5. จงเขียนสมการฮาเวอร์ซีนและอธิบายเหตุผลทางฟิสิกส์ที่ต้องใช้สูตรนี้แทนระยะทางแบบยูคลิดในการหาเส้น ทางการเดินทางจริง
6. จงอธิบายกลไกการกรองสัญญาณรบกวนของ GPS เพื่อป้องกันปรากฏการณ์พิกัดดริฟต์ขณะหยุดนิ่ง

# บทที่ 3

## วิทยาศาสตร์การออกกำลังกายและชีวกลศาสตร์สุขภาพ ประยุกต์

### แผนบริหารการสอนประจำบทที่ 3

หัวข้อเนื้อหาประจำบท

1. อัตราความถี่ก้าวและการจำแนกความหนักของการออกกำลังกายตามเกณฑ์สากล
2. สรีรวิทยาการคำนวณระยะก้าวเดินแบบแปรผันตามเพศและความสูงของผู้ใช้
3. การประเมินพลังงานเผาผลาญพื้นฐานด้วยสมการมาตรฐาน Mifflin-St Jeor
4. การคำนวณพลังงานที่ใช้ทั้งหมดในแต่ละวันและการเผาผลาญจากกิจกรรมก้าวเดิน
5. กลไกสรีรวิทยาของพฤติกรรมเนือยนิ่งและระบบแจ้งเตือนการหยุดนั่งนาน
6. การประเมินสมดุลของเหลวในร่างกายและความต้องการน้ำบริสุทธิ์ในแต่ละวัน

วัตถุประสงค์เชิงพฤติกรรม

1. คำนวณและจำแนกระดับความหนักของกิจกรรมทางกายจากอัตราความถี่ก้าว (Cadence) ได้อย่างถูกต้อง
2. ประยุกต์ใช้สมการสัดส่วนทางชีวกลศาสตร์ในการประเมินระยะก้าวและระยะทางรวมได้อย่างถูกต้อง
3. คำนวณอัตราการเผาผลาญพื้นฐาน (BMR) และการใช้พลังงานรวม (TDEE) ตามสูตร Mifflin-St Jeor ได้อย่าง แม่นยำ
4. อธิบายผลเสียทางสรีรวิทยาของการนั่งนิ่งติดต่อกันเกิน 1 ชั่วโมง พร้อมแนวทางแก้ไขได้อย่างถูกต้อง
5. คำนวณปริมาณน้ำดื่มที่เหมาะสมตามน้ำหนักตัวและระดับกิจกรรมทางกายได้อย่างถูกต้อง

กิจกรรมการเรียนการสอน

1. บรรยายหลักการเวชศาสตร์การออกกำลังกาย สรีรวิทยาการเผาผลาญ และชีวกลศาสตร์การเคลื่อนไหว

14

CHAPTER 3. วิทยาศาสตร์การออกกำลังกายและชีวกลศาสตร์สุขภาพประยุกต์ | 15
2. กิจกรรมฝึกคำนวณ BMR, TDEE, Stride Length และ Hydration จากโจทย์กรณีศึกษาบุคคลตัวอย่าง
3. การทดสอบเดินจับเวลาเพื่อวัด Cadence จริงเปรียบเทียบกับค่าที่แอปพลิเคชันคำนวณได้
4. การอภิปรายกลุ่มและการตอบคำถามทบทวนท้ายบท

สื่อการเรียนการสอน

1. เอกสารคำสอนบทที่ 3 วิทยาศาสตร์การออกกำลังกายและชีวกลศาสตร์สุขภาพ
2. เครื่องชั่งน้ำหนักและสายวัดความสูงมาตรฐาน
3. นาฬิกาจับเวลาและสมาร์ทโฟนที่ติดตั้งแอปพลิเคชัน Smart Health Tracker

การประเมินผล

1. ประเมินความถูกต้องจากการทำใบงานคำนวณสรีรวิทยาการเผาผลาญ
2. ประเมินทักษะการวัดและสอบเทียบระยะก้าวเดินในการปฏิบัติการภาคสนาม
3. ประเมินผลสัมฤทธิ์จากคำถามทบทวนท้ายบทที่ 3

CHAPTER 3. วิทยาศาสตร์การออกกำลังกายและชีวกลศาสตร์สุขภาพประยุกต์ | 16

### 3.1 อัตราความถี่ก้าวและการจำแนกความหนักของการออกกำลังกาย

ในทางเวชศาสตร์การออกกำลังกาย อัตราความถี่ก้าว (Cadence) มีหน่วยเป็นก้าวต่อนาที (Steps per Minute: SPM) เป็นดัชนีชี้วัดที่สะท้อนถึงความหนักของการออกกำลังกาย (Exercise Intensity) ได้อย่างตรงไปตรงมา การนับจำนวนก้าวสะสมเพียงอย่างเดียวโดยไม่คำนึงถึง Cadence ไม่อาจบ่งชี้ได้ว่ากิจกรรมนั้นส่งเสริมสมรรถภาพของ ระบบหัวใจและหลอดเลือด (Cardiorespiratory Fitness) หรือไม่
เวชศาสตร์การออกกำลังกายและชีวกลศาสตร์ เกณฑ์การจำแนกความหนักของการก้าวเดินตามมาตรฐานวิทยาลัยเวชศาสตร์การกีฬาแห่งสหรัฐอเมริกา (ACSM)
- การเดินช้าหรือพฤติกรรมเนือยนิ่ง (< 80 SPM) มีการเผาผลาญพลังงานในระดับเบามาก เหมาะ สำหรับผู้ฟื้นฟูสมรรถภาพหรือผู้สูงอายุ
- การเดินเพื่อสุขภาพระดับปานกลาง (100 − 120 SPM) เป็นช่วงความถี่ที่เทียบเท่ากับความหนัก ระดับปานกลาง (Moderate Intensity, 3.0 − 5.9 METs) ซึ่งทำให้หัวใจเต้นในย่านแอโรบิก ช่วย ลดระดับน้ำตาลในเลือดและความดันโลหิต
- การเดินเร็วหรือการ วิ่งเหยาะ (> 130 SPM) จัดเป็นกิจกรรมทางกาย ระดับหนัก (Vigorous Intensity, ≥ 6.0 METs) ช่วยเพิ่มความจุปอดและเสริมสร้างความแข็งแรงของกล้ามเนื้อหัวใจ

### 3.2 ชีวกลศาสตร์การคำนวณระยะก้าวเดินเฉพาะบุคคล

แอปพลิเคชันนับก้าวทั่วไปมักกำหนดระยะก้าวเดินเป็นค่าคงที่เฉลี่ย เช่น 70 ซม. ส่งผลให้ผู้ใช้งานที่มีความ สูงต่างกันได้รับค่าระยะทางรวมที่ผิดเพี้ยนอย่างมีนัยสำคัญ
ในทางมานุษยมิติ (Anthropometry) ความยาวของกระดูกโคนขาและขาท่อนล่างมีความสัมพันธ์เชิงเส้นตรง กับความสูงของร่างกาย (H) นอกจากนี้สรีระของเพศชายและเพศหญิงยังมีมุมของกระดูกเชิงกราน (Q-angle) และจุด หมุนของข้อสะโพกที่แตกต่างกัน ระบบ Smart Health Tracker จึงเลือกใช้แบบจำลองสัดส่วนตามเพศและความสูงที่ ผ่านการยอมรับในวารสารชีวกลศาสตร์สากล

Lstride =

{
H × 0.415 | สำหรับเพศชาย
H × 0.413 | สำหรับเพศหญิง

(3.1)

เมื่อ H คือความสูงของผู้ใช้ในหน่วยเซนติเมตร และ Lstride คือความยาวก้าวในหน่วยเซนติเมตร ระยะทางรวมสะสม
(D) ในหน่วยกิโลเมตรจึงคำนวณได้จาก

D =

Steps × Lstride

100,000

(3.2)

ตารางที่ 3.1 ตัวอย่างระยะก้าวเดินจำเพาะบุคคลตามความสูงและเพศสภาพ

ความสูง (H) | ระยะก้าวเพศชาย (0.415) | ระยะก้าวเพศหญิง (0.413) | ระยะทางสะสมเมื่อเดิน 10,000 ก้าว
150 cm | 62.25 cm | 61.95 cm | ชาย 6.23 km | หญิง 6.20 km
160 cm | 66.40 cm | 66.08 cm | ชาย 6.64 km | หญิง 6.61 km
170 cm | 70.55 cm | 70.21 cm | ชาย 7.06 km | หญิง 7.02 km
180 cm | 74.70 cm | 74.34 cm | ชาย 7.47 km | หญิง 7.43 km

CHAPTER 3. วิทยาศาสตร์การออกกำลังกายและชีวกลศาสตร์สุขภาพประยุกต์ | 17

### 3.3 การประเมินการเผาผลาญพลังงานด้วยสมการ Mifflin-St Jeor

พลังงานที่ร่างกายมนุษย์ใช้ในแต่ละวันประกอบด้วยพลังงานที่ใช้ในการทำงานของอวัยวะภายในขณะพักผ่อน (Basal Metabolic Rate: BMR) รวมกับพลังงานที่ใช้ในกิจกรรมทางกายและการย่อยอาหาร (Total Daily Energy

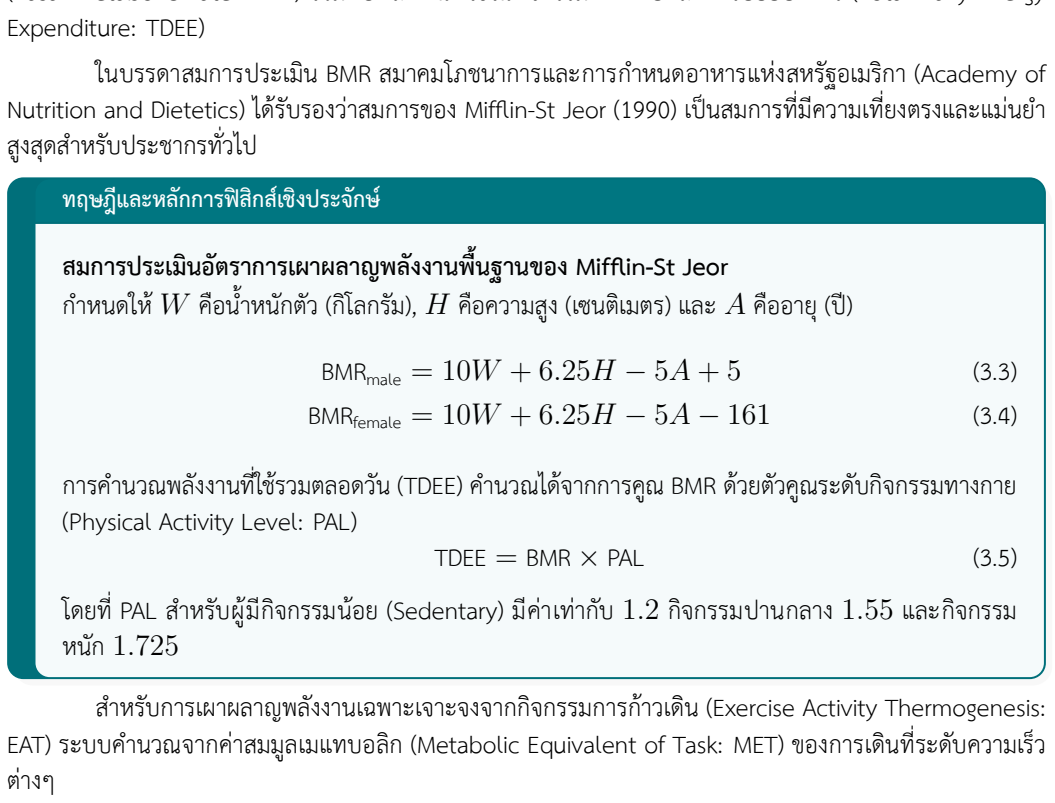
[picture p121: figure]
Expenditure: TDEE) ในบรรดาสมการประเมิน BMR สมาคมโภชนาการและการกำหนดอาหารแห่งสหรัฐอเมริกา (Academy of; สูงสุดสำหรับประชากรทั่วไป; ทฤษฎีและหลักการฟิสิกส์เชิงประจักษ์; สมการประเมินอัตราการเผาผลาญพลังงานพื้นฐานของ Mifflin-St Jeor; BMRmale = 10W + 6.25H − 5A + 5; การคำนวณพลังงานที่ใช้รวมตลอดวัน (TDEE) คำนวณได้จากการคูณ BMR ด้วยตัวคูณระดับกิจกรรมทางกาย (Physical Activity Level: PAL); TDEE = BMR × PAL; สำหรับการเผาผลาญพลังงานเฉพาะเจาะจงจากกิจกรรมการก้าวเดิน (Exercise Activity Thermogenesis:; ต่างๆ

Nutrition and Dietetics) ได้รับรองว่าสมการของ Mifflin-St Jeor (1990) เป็นสมการที่มีความเที่ยงตรงและแม่นยำ

กำหนดให้W คือน้ำหนักตัว (กิโลกรัม), H คือความสูง (เซนติเมตร) และ A คืออายุ (ปี)

BMRfemale = 10W + 6.25H − 5A − 161 | (3.4)

โดยที่ PAL สำหรับผู้มีกิจกรรมน้อย (Sedentary) มีค่าเท่ากับ 1.2 กิจกรรมปานกลาง 1.55 และกิจกรรม

EAT) ระบบคำนวณจากค่าสมมูลเมแทบอลิก (Metabolic Equivalent of Task: MET) ของการเดินที่ระดับความเร็ว

Calories (kcal) = Time (hr) × MET × W (kg) | (3.6)
โดยการเดินที่ความเร็วปานกลาง (100 SPM) มีค่าประมาณ 3.5 METs

### 3.4 กลไกสรีรวิทยาของพฤติกรรมเนือยนิ่งและระบบเสียงแจ้งเตือนอัจฉริยะ

การนั่งนิ่งติดต่อกันเป็นเวลานานเกินกว่า 30 นาที ส่งผลให้การหดตัวของกล้ามเนื้อโครงร่างขนาดใหญ่โดย เฉพาะกลุ่มกล้ามเนื้อขาและสะโพกหยุดชะงักลงอย่างสิ้นเชิง งานวิจัยทางสรีรวิทยาการออกกำลังกายร่วมสมัยพบว่า ช่วงเวลา 30 นาทีเป็นเกณฑ์วิกฤต (Critical Threshold) ที่ก่อให้เกิดความผิดปกติทางชีวเคมีเฉียบพลัน ได้แก่

1. เอนไซม์ไลโพโปรตีนไลเปส (Lipoprotein Lipase หรือ LPL) บริเวณเยื่อบุหลอดเลือดฝอยของกล้ามเนื้อหยุด การทำงาน ส่งผลให้อัตราการสลายไตรกลีเซอไรด์และไขมันเลวในพลาสมาลดลงอย่างรวดเร็วเกินกว่าร้อยละ 90
2. เกิดภาวะดื้อต่ออินซูลินระยะเฉียบพลัน (Acute Peripheral Insulin Resistance) ทำให้การขนส่งกลูโคสผ่าน โปรตีน GLUT-4 ชะลอตัวและเกิดการสะสมน้ำตาลในกระแสเลือดสูงขึ้น
3. แรงเฉือนของกระแสเลือดบนผนังหลอดเลือด (Endothelial Shear Stress) บริเวณหลอดเลือดดำส่วนล่างลด ลง เพิ่มความเสี่ยงของภาวะหลอดเลือดดำอักเสบและลิ่มเลือดอุดตัน (Deep Vein Thrombosis)

CHAPTER 3. วิทยาศาสตร์การออกกำลังกายและชีวกลศาสตร์สุขภาพประยุกต์ | 18

ระบบ Smart Health Tracker จึงกำหนดค่าตรวจจับพฤติกรรมเนือยนิ่งแบบเข้มงวดไว้ที่ 30 นาที เมื่อระบบ ตรวจพบว่าเซนเซอร์ไม่ตรวจพบกิจกรรมการก้าวเดินต่อเนื่องครบ 30 นาที ตัวจับเวลาสรีรวิทยาจะกระตุ้นระบบแจ้ง เตือนแบบพหุสัมผัส (Multi-Modal Alert) ทันที

1. สัญญาณเตือนแบบเคลื่อนไหว (Visual Pulsating Banner) แถบสีแดงสะท้อนแสงนีออนจะกะพริบแจ้ง เตือนบนหน้าจอ พร้อมปุ่มลุกยืดเหยียด
2. สัญญาณเสียงกระตุ้นประสาทสัมผัส (Acoustic Chime) ปล่อยคลื่นเสียงความถี่ 440 Hz ผสมความถี่คู่ 880 Hz เพื่อกระตุ้นโสตประสาทอย่างนุ่มนวลแต่เด่นชัด
3. ระบบเสียงพูดภาษาไทยสังเคราะห์ (Spoken Thai Voice Alert) ระบบจะสังเคราะห์เสียงพูดภาษาไทย อย่างเป็นธรรมชาติด้วยข้อความกระตุ้นเชิงจิตวิทยาเชิงบวก “ลุกค่ะ ลุกค่ะ! ได้เวลาลุกขึ้นยืดเส้นยืดสายและ ขยับร่างกายแล้วค่ะ” เพื่อลดภาวะจิตใจล้าและกระตุ้นการเคลื่อนไหวของระบบกล้ามเนื้อและประสาทโดย อัตโนมัติ

### 3.5 แบบจำลองการตั้งเป้าหมายสุขภาพและการลดน้ำหนักเชิงวิทยาศาสตร์

การตั้งเป้าหมายสุขภาพที่จับต้องได้และมีหลักฐานทางฟิสิกส์การแพทย์รองรับ เป็นหัวใจสำคัญของการปรับ เปลี่ยนพฤติกรรมอย่างยั่งยืน ระบบ Smart Health Tracker เปิดให้ผู้ใช้งานสามารถกำหนดเป้าหมายเฉพาะบุคคลได้ 3 มิติ

1. เป้าหมายก้าวเดินและน้ำดื่มประจำวัน ค่าปริยายเริ่มต้นที่ 10,000 ก้าว และน้ำดื่ม 2,000 mL โดยปรับ เพิ่มตามระดับกิจกรรม
2. เป้าหมายน้ำหนักตัวและอัตราการพร่องพลังงาน (Calorie Deficit Target) อาศัยหลักการทางอุณห พลศาสตร์ชีววิทยา (Biological Thermodynamics) ซึ่งกำหนดว่าไขมันสะสมในร่างกาย 1 กิโลกรัม กักเก็บ พลังงานสุทธิเทียบเท่าประมาณ 7,700 กิโลแคลอรี

หากผู้ใช้งานมีน้ำหนักปัจจุบัน Wcurrent และต้องการลดน้ำหนักลงสู่เป้าหมาย Wtarget ปริมาณพลังงานสะสม ส่วนเกินที่ต้องขจัดออกทั้งหมด (∆Etotal) มีค่าเท่ากับ

∆Etotal = (Wcurrent − Wtarget) × 7,700 kcal | (3.7)

เมื่อผู้ใช้กำหนดอัตราการควบคุมพลังงานพร่องประจำวัน (Deficitdaily) ระบบจะประเมินกรอบเวลาความสำเร็จ (Tdays) และอัตราการลดน้ำหนักต่อสัปดาห์ (∆Wweekly) ดังนี้

Tdays =

(Wcurrent − Wtarget) × 7,700
Deficitdaily

(3.8)

∆Wweekly =

Deficitdaily × 7

7,700

=

Deficitdaily

1,100

กิโลกรัมต่อสัปดาห์ | (3.9)

ระบบแนะนำให้อัตราการพร่องพลังงานอยู่ในช่วง 300−500 kcal/วัน เพื่อให้อัตราการลดน้ำหนักปลอดภัยต่อระบบ เมแทบอลิซึม (0.3 − 0.5 กิโลกรัมต่อสัปดาห์) โดยไม่สูญเสียมวลกล้ามเนื้อลาย

CHAPTER 3. วิทยาศาสตร์การออกกำลังกายและชีวกลศาสตร์สุขภาพประยุกต์ | 19

### 3.6 สมดุลของเหลวในร่างกายและการดื่มน้ำบริสุทธิ์

น้ำคิดเป็นร้อยละ 60 ของน้ำหนักตัวในผู้ใหญ่ การขาดน้ำเพียงร้อยละ 1 ถึง 2 ของน้ำหนักตัว จะส่งผลให้ ปริมาตรพลาสมาในเลือดลดลง ประสิทธิภาพการระบายความร้อนของร่างกายแย่ลง และความดันโลหิตตก ระบบจึงคำนวณเป้าหมายการดื่มน้ำพื้นฐานประจำวัน (Baseline Fluid Requirement) ตามมาตรฐานการ แพทย์
Vwater, base = W (kg) × 32.5 mL | (3.10)
และเพิ่มปริมาณน้ำชดเชยตามเหงื่อที่สูญเสียไปจากการก้าวเดินในอัตรา 350 mL ต่อการเดินสะสมทุกๆ 3,000 ก้าว พร้อมแถบกราฟิกบันทึกการดื่มน้ำที่อัปเดตแบบเรียลไทม์

### คำถามทบทวนท้ายบทที่ 3

1. เหตุใดอัตราความถี่ก้าว (Cadence) จึงมีความสำคัญมากกว่าการนับจำนวนก้าวสะสมเพียงอย่างเดียว
2. ชายอายุ 35 ปี สูง 175 ซม. หนัก 70 กก. จงคำนวณระยะก้าวเดิน ความยาวทางสะสมเมื่อเดิน 8,000 ก้าว และค่า BMR ตามสูตร Mifflin-St Jeor
3. จงอธิบายการเปลี่ยนแปลงทางชีวเคมีและผลเสียต่อหลอดเลือดเมื่อร่างกายอยู่ในภาวะเนือยนิ่งติดต่อกันเกิน 30 นาที และประโยชน์ของระบบเสียงพูดเตือนภาษาไทย
4. หากผู้ใช้มีน้ำหนัก 75 กก. ต้องการลดน้ำหนักเหลือ 70 กก. โดยกำหนดอัตราพร่องพลังงานวันละ 500 kcal จงคำนวณระยะเวลาเป็นวันที่ต้องใช้และอัตราการลดน้ำหนักต่อสัปดาห์
5. เพราะเหตุใดระบบจึงต้องคำนวณปริมาณน้ำดื่มชดเชยเพิ่มขึ้นตามจำนวนก้าวเดินสะสม

# บทที่ 4

## การออกแบบสถาปัตยกรรมส่วนติดต่อผู้ใช้แบบ Bento Grid และ Adaptive Layout

### แผนบริหารการสอนประจำบทที่ 4

หัวข้อเนื้อหาประจำบท

1. วิวัฒนาการและแนวคิดสถาปัตยกรรมส่วนต่อประสานผู้ใช้แบบ Bento Grid
2. การออกแบบลำดับขั้นการรับรู้ทางสายตาและการใช้โทนสีคอนทราสต์สูง
3. ระบบจุดตัดขนาดหน้าจอแบบตอบสนองอัตโนมัติ (Adaptive Responsive Breakpoints)
4. เทคนิควิศวกรรมการป้องกันปัญหาการแสดงผลล้นหน้าจอ (Overflow Prevention)
5. การออกแบบและผสานภาพกราฟิกลายเส้นนีออนสไตล์ไซเบอร์เนติก
6. จิตวิทยาการตอบสนองเชิงจลน์และวงรอบแรงจูงใจในการออกกำลังกาย

วัตถุประสงค์เชิงพฤติกรรม

1. อธิบายหลักการจัดวางเนื้อหาแบบกล่องเบนโตะ (Bento Grid Layout) ได้อย่างถูกต้อง
2. ออกแบบและกำหนดจุดตัดขนาดหน้าจอ (Breakpoints) สำหรับอุปกรณ์พกพาขนาดต่างๆ ได้อย่างถูกต้อง
3. ประยุกต์ใช้เทคนิควิศวกรรมเลย์เอาต์ของ Flutter เพื่อป้องกัน RenderFlex Overflow ได้อย่างสมบูรณ์
4. เลือกใช้คู่สีนีออนคอนทราสต์สูงเพื่อเสริมสร้างความชัดเจนในการอ่านข้อมูลสุขภาพตามมาตรฐาน WCAG ได้ อย่างถูกต้อง

กิจกรรมการเรียนการสอน

1. การวิเคราะห์กรณีศึกษาส่วนติดต่อผู้ใช้ของแอปพลิเคชันระดับโลก (Apple Health, Nike Run, Strava)
2. การทดลองจำลองหน้าจอด้วยขนาดความกว้างต่างๆ บน Flutter DevTools เพื่อตรวจหาจุดบกพร่องการจัด วาง

20

CHAPTER 4. การออกแบบสถาปัตยกรรมส่วนติดต่อผู้ใช้แบบ BENTO GRID และ ADAPTIVE LAYOUT | 21
3. ปฏิบัติการเขียนโค้ดวิดเจ็ต LayoutBuilder และ Wrap สำหรับจัดการ Bento Grid
4. การอภิปรายกลุ่มและการตอบคำถามทบทวนท้ายบท

สื่อการเรียนการสอน

1. เอกสารคำสอนบทที่ 4 การออกแบบ Bento Grid และ Adaptive Layout
2. คอมพิวเตอร์ติดตั้ง Flutter SDK, VS Code และโปรแกรมตรวจจับเลย์เอาต์
3. ภาพประกอบชุด Bento Cards และชุดไอคอนลายเส้นนีออนดิจิทัล

การประเมินผล

1. การประเมินผลสัมฤทธิ์จากการออกแบบโครงสร้างเลย์เอาต์หน้าจอ
2. การตรวจความถูกต้องของการทดสอบแอปพลิเคชันบนขนาดหน้าจอที่มีความกว้างหลากหลาย
3. การประเมินคำตอบจากคำถามทบทวนท้ายบทที่ 4

CHAPTER 4. การออกแบบสถาปัตยกรรมส่วนติดต่อผู้ใช้แบบ BENTO GRID และ ADAPTIVE LAYOUT | 22

### 4.1 แนวคิดสถาปัตยกรรมส่วนต่อประสานผู้ใช้แบบ Bento Grid

ในยุคปัจจุบัน ผู้ใช้งานสมาร์ทโฟนต้องการเข้าถึงข้อมูลสำคัญได้อย่างรวดเร็วในชั่วพริบตา (Glanceable UI) การออกแบบแดชบอร์ดสุขภาพในอดีตที่ใช้รายการเลื่อนเรียงแถวยาว (Long Scrollable List) ทำให้ผู้ใช้ต้องกวาด สายตาค้นหาข้อมูลที่กระจัดกระจายและเกิดความล้าทางสายตา
แนวคิดการออกแบบแบบ Bento Grid ได้รับแรงบันดาลใจจากกล่องข้าวเบนโตะของญี่ปุ่น ซึ่งมีการจัดแบ่ง ช่องสี่เหลี่ยมขนาดเล็กใหญ่ที่มีสัดส่วนกลมกลืนกันเพื่อบรรจุอาหารแต่ละชนิดอย่างเป็นระเบียบ เมื่อนำมาประยุกต์ใช้ กับแดชบอร์ดสุขภาพ ข้อมูลแต่ละมิติจะถูกบรรจุลงใน Metric Cards ที่มีขนาดแตกต่างกันตามระดับความสำคัญ (Visual Hierarchy)
1. Hero Card (การ์ดหลักขนาดใหญ่) แสดงจำนวนก้าวเดินสด วงแหวนความคืบหน้านีออน และปุ่มควบคุม หลัก
2. Secondary Cards (การ์ดรองขนาดกลาง) แสดงอัตราความถี่ก้าว (Cadence SPM) ระยะทางกิโลเมตร และพลังงานแคลอรี
3. Micro Cards (การ์ดสนับสนุนขนาดกะทัดรัด) แสดงสถานะการดื่มน้ำ (Hydration) ดัชนีการเผาผลาญพื้น ฐาน (BMR) และเวลาการนั่งนิ่ง

### 4.2 การออกแบบสีและคอนทราสต์ตามมาตรฐาน WCAG

แอปพลิเคชัน Smart Health Tracker เลือกใช้ธีมมืดระดับพรีเมียม (Deep Charcoal & Obsidian Tech Background, #121212) ร่วมกับคู่สีนีออนเรืองแสงสูง (High-Luminance Neon Accents)

ตารางที่ 4.1 จานสีมาตรฐานและการจัดกลุ่มสัญญาณภาพของระบบ Smart Health Tracker

ชื่อตัวแปรสี | รหัสสี HEX | อัตราคอนทราสต์ | ความหมายทางสรีรวิทยาและข้อมูล
neonCyan | #00E5FF | 14.2 : 1 | ข้อมูลก้าวเดินหลักและระบบเซนเซอร์คลื่นความเร่ง
neonGreen | #00E676 | 13.8 : 1 | อัตราความถี่ก้าว (Cadence) และภาวะแอโรบิกสมบูรณ์
neonOrange | #FF9100 | 9.6 : 1 | พลังงานความร้อนกิโลแคลอรีและการเผาผลาญไขมัน
neonPurple | #D500F9 | 8.4 : 1 | ข้อมูลระยะทางและสัดส่วนความยาวก้าวชีวกลศาสตร์
neonBlue | #2979FF | 10.1 : 1 | ปริมาณน้ำบริสุทธิ์และสมดุลของเหลวในร่างกาย
alertRed | #FF1744 | 7.9 : 1 | การแจ้งเตือนพฤติกรรมเนือยนิ่งและการนั่งนานเกิน 1 ชั่วโมง

ทุกคู่สีผ่านเกณฑ์มาตรฐานการเข้าถึงเว็บระดับสูงสุด (WCAG 2.1 AAA) ซึ่งกำหนดอัตราคอนทราสต์ของ ข้อความขนาดใหญ่ไว้ไม่ต่ำกว่า 4.5 : 1 และข้อความปกติไม่ต่ำกว่า 7.0 : 1 ทำให้ผู้ใช้สามารถมองเห็นตัวเลขได้อย่าง คมชัดแม้ในขณะวิ่งกลางแจ้งที่มีแสงแดดจ้า

### 4.3 ระบบจุดตัดขนาดหน้าจอแบบตอบสนองอัตโนมัติ

เนื่องจากอุปกรณ์สมาร์ทโฟนและแท็บเล็ตในระบบปฏิบัติการแอนดรอยด์มีความหลากหลายทางกายภาพ ของขนาดหน้าจอ (Device Fragmentation) สูงมาก ตั้งแต่สมาร์ทโฟนจอประหยัดที่มีความกว้างต่ำกว่า 360 dp จน ถึงสมาร์ทโฟนเรือธง จอพับได้ (Foldable) และแท็บเล็ต
ระบบ Smart Health Tracker จึงได้ออกแบบระบบจำแนกจุดตัดขนาดหน้าจอ (Adaptive Responsive Breakpoints) ออกเป็น 3 ระดับอย่างเคร่งครัด

CHAPTER 4. การออกแบบสถาปัตยกรรมส่วนติดต่อผู้ใช้แบบ BENTO GRID และ ADAPTIVE LAYOUT | 23

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

### 4.4 เทคนิควิศวกรรมการป้องกันปัญหาเลย์เอาต์ล้นจอ

ข้อผิดพลาดที่พบบ่อยที่สุดในการพัฒนาแอปพลิเคชันมือถือคือRenderFlex Overflowed by xxx Pixels ซึ่งเกิดจากการที่วิดเจ็ตลูกภายใน Row หรือ Column มีขนาดคงที่ (Fixed Width/Height) และขยายตัวเกินขอบเขต พิกเซลที่หน้าจอจริงสามารถเรนเดอร์ได้
ในระบบ Smart Health Tracker ผู้วิจัยได้นำหลักวิศวกรรมซอฟต์แวร์เข้ามาควบคุม 3 ประการ
1. การห่อหุ้มชั้นนอกสุดด้วย SingleChildScrollView เสมอ เพื่อรับประกันว่าในกรณีที่หน้าจอมีความสูงจำกัด (เช่น การเปิดคีย์บอร์ดเสมือน หรือการใช้งานแนวนอน) ผู้ใช้จะยังคงสามารถเลื่อนดูเนื้อหาทั้งหมดได้อย่างราบ รื่น
2. การจัดสัดส่วนการ์ดด้วย Expanded และ Flex Ratio แทนการระบุความกว้างแบบคงที่ ทำให้การ์ดทั้งสอง ฝั่งในระบบกริดหดและขยายตัวตามสัดส่วนพื้นที่หน้าจอจริงอย่างอิสระ
3. การจำกัดความยาวของข้อความด้วย TextOverflow.ellipsis พร้อมการกำหนด maxLines: 1 ในแถบหัวข้อ และป้ายสถานะ เพื่อป้องกันไม่ให้ข้อความยาวกระแทกขอบจนโครงสร้างพังทลาย

CHAPTER 4. การออกแบบสถาปัตยกรรมส่วนติดต่อผู้ใช้แบบ BENTO GRID และ ADAPTIVE LAYOUT | 24

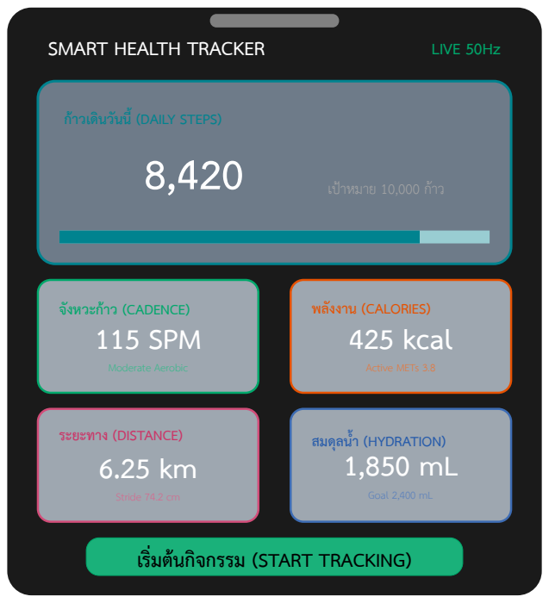
[picture p122: figure]
SMART HEALTH TRACKER; LIVE 50Hz; ก้าวเดินวันนี้ (DAILY STEPS); เป้าหมาย 10,000 ก้าว; จังหวะก้าว (CADENCE) 115 SPM; Moderate Aerobic; พลังงาน (CALORIES) 425 kcal; Active METs 3.8; ระยะทาง (DISTANCE) 6.25 km; Stride 74.2 cm; สมดุลน้ำ (HYDRATION) 1,850 mL; Goal 2,400 mL; เริ่มต้นกิจกรรม (START TRACKING)

ภาพที่ 4.1 สถาปัตยกรรมการจัดวางหน้าจอแบบ Bento Grid ของระบบ Smart Health Tracker

### 4.5 การออกแบบการ์ดวิเคราะห์ปัญญาประดิษฐ์เชิงลึกและไทม์ไลน์ 4 ชั่วโมง

เพื่อรองรับความต้องการด้านการวิเคราะห์ข้อมูลขั้นสูงโดยไม่รบกวนความต่อเนื่องของสายตา ระบบได้ผสาน Deep AI Analytics Card เข้าสู่ Bento Grid ซึ่งประกอบด้วยองค์ประกอบย่อย 4 ส่วน

1. แผงสถานะการจำแนกสภาพความล้าและความสมดุล (AI Health State Header) แสดงระดับความล้า ทางชีวกลศาสตร์ (ปกติ, ล้าปานกลาง, ล้าสะสมรุนแรง, หรือสมดุลบกพร่อง) พร้อมเปอร์เซ็นต์ความเชื่อมั่น (Softmax Probability) และสีนีออนบ่งชี้สถานะ
2. การพยากรณ์ล่วงหน้า 4 ชั่วโมงถัดไป (Next 4-Hour Predictive Metrics) นำเสนอการประเมินก้าวเดิน และแคลอรีที่คาดว่าจะเกิดขึ้นในช่วงเวลาต่อไป เพื่อช่วยให้ผู้ใช้จัดสรรการเคลื่อนไหวร่างกายได้อย่างสมดุล
3. หน้าปัดโทรมาตรโครงข่ายประสาทสด (Live Neural Telemetry Gauge) แสดงค่าอินพุตเวกเตอร์ทั้ง 6 มิติ ค่าสถานะฮิดเดนเลเยอร์ และจำนวนพารามิเตอร์ของโมเดล ทำให้ผู้เรียนสามารถมองเห็นการทำงานภายใน (Explainable AI) ได้อย่างโปร่งใส
4. ปุ่มปฏิบัติ การบันทึก สแนปชอต และ การ ฝึกฝนบน เครื่อง (Action Controls) ประกอบ ด้วยปุ่มบันทึก ข้อมูล 4 ชั่วโมงแบบแมนนวล และปุ่มฝึกฝนโมเดลบนอุปกรณ์ (Train Deep Model On-Device) ซึ่งเรียกใช้ กระบวนการ Backpropagation และ Stochastic Gradient Descent แบบเรียลไทม์

นอกจากนี้ ใต้ระบบ Bento Grid ยังมีส่วนแสดงผล 4-Hour Interval Snapshot Timeline ซึ่งแสดง ประวัติข้อมูลย้อนหลังในรูปแบบการ์ดไทม์ไลน์แนวนอน ช่วยให้ผู้ใช้สามารถติดตามแนวโน้มความล้าและพฤติกรรมก้าว เดินในแต่ละช่วงวันได้อย่างชัดเจน

CHAPTER 4. การออกแบบสถาปัตยกรรมส่วนติดต่อผู้ใช้แบบ BENTO GRID และ ADAPTIVE LAYOUT | 25

### 4.6 สถาปัตยกรรมไดอะล็อกตั้งค่าเป้าหมายและพารามิเตอร์สุขภาพ

เพื่อความสะดวกในการปรับแต่งค่าเฉพาะบุคคล ระบบได้ออกแบบ Comprehensive Goals Dialog ซึ่ง เป็นหน้าต่างเลเยอร์ระดับบน (Modal Dialog) ที่แบ่งการตั้งค่าออกเป็น 3 แท็บอย่างเป็นหมวดหมู่

1. แท็บเป้าหมายรายวัน (Daily Goals) กำหนดจำนวนก้าวเป้าหมาย (Steps Goal) และปริมาณน้ำดื่มเป้า หมาย (Water Goal)
2. แท็บเป้าหมายลดน้ำหนัก (Weight Loss) กำหนดน้ำหนักเป้าหมาย และอัตราการพร่องพลังงาน (Calorie Deficit) พร้อมแสดงการประเมินระยะเวลาความสำเร็จและอัตราการลดน้ำหนักต่อสัปดาห์แบบไดนามิก
3. แท็บแจ้งเตือนสุขภาพและเสียงสังเคราะห์ (Health & Alerts) กำหนดช่วงเวลาตรวจจับพฤติกรรมเนือยนิ่ง (15, 30, 45 หรือ 60 นาที) สวิตช์เปิดปิดเสียงพูดภาษาไทยสังเคราะห์ “ลุกค่ะ ลุกค่ะ” ปุ่มทดสอบเสียงพูด และปุ่มรีเซ็ตระบบเป็นศูนย์ (Reset All to 0)

### 4.7 การออกแบบการ์ดแผนที่เส้นทางจริงด้วยระบบเวกเตอร์คัสตอมเพนเตอร์

หนึ่งใน ข้อ จำกัด ของ การ แสดง ผล แผนที่ ดาวเทียม แบบ ดั้งเดิม (เช่น Google Maps หรือ Mapbox) บน แอปพลิเคชันมือถือ คือการใช้ทรัพยากรหน่วยความจำและการดาวน์โหลดไทล์ภาพ (Map Tiles) ปริมาณมหาศาล ซึ่ง ส่งผลให้อัตราการสิ้นเปลืองพลังงานแบตเตอรี่พุ่งสูงและเกิดอาการกระตุก (UI Lag)
ทีมวิจัยจึงได้ออกแบบ GpsRouteMapCard โดยใช้ระบบเรนเดอร์เวกเตอร์อิสระผ่านคลาส CustomPainter ของ Flutter ซึ่งประมวลผลบนการ์ดจอโดยตรง (GPU Acceleration) มีองค์ประกอบทางวิศวกรรมเลย์เอาต์ดังนี้
1. การแปลงพิกัดภูมิศาสตร์สู่พิกัดผืนผ้าใบแบบปรับตัว (Adaptive Geodesic Viewport Mapping) ระบบ จะคำนวณกรอบขอบเขตพิกัด (Bounding Box: [ϕmin, ϕmax] × [λmin, λmax]) ของทุกจุดที่บันทึกได้ แล้ว แปลงสัดส่วนให้อยู่ในระนาบพิกเซลหน้าจอตามขนาดกว้างยาวของหน้าจออย่างแม่นยำ พร้อมทั้งรองรับการ ซูม (Zoom Factor: 0.5 × −5.0×) และการเลื่อนมุมมอง (Pan Gesture)
2. การวาดเส้นทางโพลีไลน์แบบเรืองแสง 2 ชั้น (Dual-Layer Neon Glow Route) วาดเส้นทางแกนหลัก ด้วยเกรเดียนต์สีนีออนเขียวสลับฟ้า (#00E676 → #00E5FF) ซ้อนทับด้วยเส้นเรืองแสงรอบนอก (Outer Blur Glow) เพื่อสร้างมิติสายตาที่เด่นชัดบนพื้นหลังสีรัตติกาล
3. สัญญาณบีคอนเรดาร์กะพริบคลื่นชีพจร (Pulsating Radar Beacon) แสดงตำแหน่งปัจจุบันของผู้ใช้ด้วย วงแหวนคลื่นเรดาร์แอนิเมชันขยายตัวแบบคาบเวลา (1.6 วินาที) พร้อมลูกศรระบุทิศทางเข็มทิศ (Heading Azimuth) ตามองศาที่ผู้ใช้กำลังมุ่งหน้าจริง
4. แผงข้อมูลโทรมาตรการเดินทางสด (Telemetry HUD Bar) แสดงผลระยะทาง GPS ควบคู่กับระยะทาง จากตัวนับก้าวเพื่อการเปรียบเทียบความแม่นยำ, ความเร็วเรียลไทม์, เพซความเร็ว (นาทีต่อกิโลเมตร), และ ความสูงสะสม

CHAPTER 4. การออกแบบสถาปัตยกรรมส่วนติดต่อผู้ใช้แบบ BENTO GRID และ ADAPTIVE LAYOUT | 26

### 4.8 จิตวิทยาการตอบสนองเชิงจลน์และวงรอบแรงจูงใจ

การออกแบบส่วนติดต่อผู้ใช้สำหรับพฤติกรรมสุขภาพ จำเป็นต้องคำนึงถึงทฤษฎีการกระตุ้นพฤติกรรม (Fogg Behavior Model: B = MAP) ซึ่งระบุว่าพฤติกรรมจะเกิดขึ้นเมื่อมีแรงจูงใจ (Motivation) ความสามารถที่ กระทำได้ง่าย (Ability) และตัวกระตุ้นที่เหมาะสม (Prompt)
ระบบ Smart Health Tracker นำเสนอตัวกระตุ้นเชิงบวกผ่านภาพเคลื่อนไหวนีออนขนาดเล็ก (Micro-Animations) เช่น การหมุนวนของวงแหวนก้าวเดินเมื่อมีก้าวใหม่ และการกระเพื่อมของแถบคลื่นน้ำเมื่อผู้ใช้กดบันทึก การดื่มน้ำ สิ่งเหล่านี้ส่งสัญญาณรางวัล (Dopamine Feedback Loop) สู่ระบบประสาทของผู้ใช้ ทำให้เกิดความพึง พอใจและมีแนวโน้มที่จะรักษาวินัยในการเคลื่อนไหวร่างกายอย่างต่อเนื่อง

### คำถามทบทวนท้ายบทที่ 4

1. จงอธิบายจุดเด่นของสถาปัตยกรรมส่วนติดต่อผู้ใช้แบบ Bento Grid เมื่อเทียบกับแดชบอร์ดแบบดั้งเดิม
2. เหตุใดการจัดลำดับคอนทราสต์ของสีตามมาตรฐาน WCAG 2.1 จึงมีความจำเป็นอย่างยิ่งสำหรับแอปพลิเคชัน สุขภาพ
3. จงยกตัวอย่าง 3 มาตรการวิศวกรรมซอฟต์แวร์ในการแก้ไขปัญหา RenderFlex Overflow ในแอปพลิเคชัน Flutter
4. อธิบายโครงสร้างและประโยชน์ของการ์ด Deep AI Analytics Card ในการสื่อสารข้อมูลการเรียนรู้เชิงลึกกับ ผู้ใช้งาน
5. จงอธิบายหลักการแปลงพิกัดภูมิศาสตร์ละติจูดและลองจิจูดลงบนผืนผ้าใบ CustomPainter ในการ์ดแผนที่ GPS
6. ทฤษฎีพฤติกรรมของ Fogg นำมาประยุกต์ใช้ในการออกแบบระบบ Micro-Animations บนแดชบอร์ดสุขภาพ อย่างไร

# บทที่ 5

## ปฏิบัติการพัฒนาแอปพลิเคชัน Smart Health Tracker ด้วย Flutter

### แผนบริหารการสอนประจำบทที่ 5

หัวข้อเนื้อหาประจำบท

1. ปฏิบัติการที่ 5.1 การติดตั้งและกำหนดค่าการเชื่อมต่อเซนเซอร์บนระบบแอนดรอยด์
2. ปฏิบัติการที่ 5.2 การเขียนคลาสประมวลผลสัญญาณ StepDetectionEngine
3. ปฏิบัติการที่ 5.3 การเขียนคลาสคำนวณสรีรวิทยาและพลังงาน UserHealthProfile
4. ปฏิบัติการที่ 5.4 การสร้างคอมโพเนนต์ส่วนติดต่อผู้ใช้แบบ Bento Grid Cards
5. ปฏิบัติการที่ 5.5 การทดสอบสอบเทียบระบบในสภาวะการใช้งานจริงและการวิเคราะห์ผล
6. ปฏิบัติการที่ 5.6 การพัฒนาโมเดลปัญญาประดิษฐ์การเรียนรู้เชิงลึกบนอุปกรณ์ (DeepHealthAiEngine)
7. ปฏิบัติการที่ 5.7 การพัฒนาระบบเสียงพูดเตือนเนือยนิ่งและสแนปชอตอัตโนมัติทุก 4 ชั่วโมง
8. ปฏิบัติการที่ 5.8 การพัฒนาระบบติดตามพิกัด GPS และการเรนเดอร์แผนที่เส้นทางจริง (GpsRouteMapCard)

วัตถุประสงค์เชิงพฤติกรรม

1. ติดตั้งแพ็กเกจ sensors_plus และกำหนดสิทธิ์การเข้าถึงฮาร์ดแวร์ได้อย่างถูกต้อง
2. พัฒนาโปรแกรมประมวลผลสัญญาณความเร่งสามมิติและตรวจจับยอดพีคตามหลักฟิสิกส์ได้อย่างสมบูรณ์
3. พัฒนาโมเดลข้อมูลสุขภาพคำนวณ BMR, TDEE, Stride Length และ Hydration ได้อย่างถูกต้อง
4. ประกอบและปรับแต่งส่วนต่อประสานผู้ใช้แบบ Bento Grid ให้รองรับหน้าจอหลากหลายขนาดได้อย่างราบรื่น
5. ดำเนินการทดสอบสอบเทียบภาคสนามและคำนวณค่าความแม่นยำในการนับก้าวได้อย่างถูกต้อง
6. พัฒนาโครงข่ายประสาทเทียมหลายชั้น (MLP) พร้อมกระบวนการ Backpropagation และ SGD บนอุปกรณ์ ได้จริง

27

CHAPTER 5. ปฏิบัติการพัฒนาแอปพลิเคชัน SMART HEALTH TRACKER ด้วย FLUTTER | 28
7. พัฒนาระบบสังเคราะห์เสียงแจ้งเตือนภาษาไทยและระบบบันทึกข้อมูลทุก 4 ชั่วโมงได้อย่างสมบูรณ์
8. พัฒนาระบบติดตามพิกัดดาวเทียม GPS และเรนเดอร์เส้นทางโพลีไลน์บนผืนผ้าใบแบบเวกเตอร์ได้อย่างถูกต้อง

กิจกรรมการเรียนการสอน

1. บรรยายสรุปขั้นตอนการปฏิบัติการทั้ง 5 ขั้นตอนและการเตรียมสภาพแวดล้อมการพัฒนา
2. ผู้เรียนลงมือเขียนโปรแกรมตามคู่มือปฏิบัติการทีละขั้น โดยมีผู้สอนให้คำปรึกษาอย่างใกล้ชิด
3. ผู้เรียนนำแอปพลิเคชันที่พัฒนาขึ้นไปติดตั้งบนสมาร์ทโฟนจริงและเดินทดสอบนับก้าวในพื้นที่จริง
4. บันทึกผลการทดสอบ วิเคราะห์ความคลาดเคลื่อน และร่วมอภิปรายสรุปผล

สื่อการเรียนการสอน

1. เครื่องคอมพิวเตอร์พร้อม Flutter SDK และ Android Studio
2. สมาร์ทโฟนระบบปฏิบัติการแอนดรอยด์พร้อมสายเชื่อมต่อ USB Debugging
3. อุปกรณ์นับก้าวอ้างอิงเชิงกล (Mechanical Tally Counter) สำหรับการสอบเทียบ

การประเมินผล

1. การตรวจความสมบูรณ์และถูกต้องของโค้ดโปรแกรมในแต่ละปฏิบัติการ
2. การทดสอบการทำงานของแอปพลิเคชันบนสมาร์ทโฟนจริง
3. การประเมินรายงานผลการสอบเทียบและความแม่นยำของระบบ
4. การตอบคำถามทบทวนท้ายบทที่ 5

CHAPTER 5. ปฏิบัติการพัฒนาแอปพลิเคชัน SMART HEALTH TRACKER ด้วย FLUTTER | 29

### 5.1 ปฏิบัติการที่ 5.1 การติดตั้งและกำหนดค่าเซนเซอร์

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

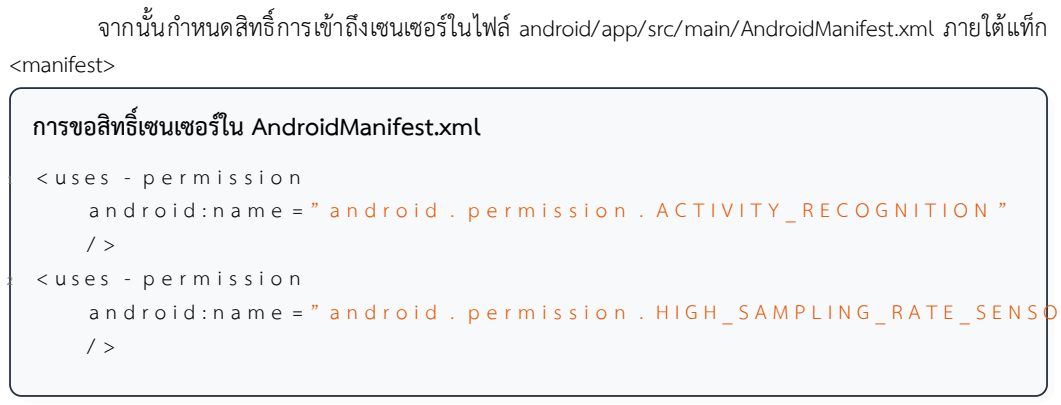
[picture p123: figure]
จากนั้นกำหนดสิทธิ์การเข้าถึงเซนเซอร์ในไฟล์android/app/src/main/AndroidManifest.xml ภายใต้แท็ก <manifest>; การขอสิทธิ์เซนเซอร์ใน AndroidManifest.xml

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

a n d r o i d : n a m e = ” a n d r o i d . p e r m i s s i o n . H I G H _ S A M P L I N G _ R A T E _ S E N S O R S ”

### 5.2 ปฏิบัติการที่ 5.2 การพัฒนาคลาส StepDetectionEngine

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

CHAPTER 5. ปฏิบัติการพัฒนาแอปพลิเคชัน SMART HEALTH TRACKER ด้วย FLUTTER | 30

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

### 5.3 ปฏิบัติการที่ 5.3 การพัฒนาคลาส UserHealthProfile

สร้างไฟล์lib/models/user_health_profile.dart เพื่อบรรจุคุณลักษณะส่วนบุคคลและตรรกะการคำนวณ สรีรวิทยาตามสูตร Mifflin-St Jeor และความยาวก้าว
แกนหลักของ UserHealthProfile.dart
1 e n u m G e n d e r { m a l e , f e m a l e }

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

20
21 | / / คำนวณอัตราเผาผลาญพื้นฐาน B M R ( k c a l / d a y )
22 | d o u b l e g e t b m r {
23 | i f ( g e n d e r = = G e n d e r . m a l e ) {
24 | r e t u r n ( 1 0 * w e i g h t K g ) + ( 6 . 2 5 * h e i g h t C m ) - ( 5 *
a g e ) + 5 ;
25 | } e l s e {
26 | r e t u r n ( 1 0 * w e i g h t K g ) + ( 6 . 2 5 * h e i g h t C m ) - ( 5 *
a g e ) - 1 6 1 ;
27 | }
28 | }

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

34
35 | / / คำนวณแคลอรีจากการเดิน ( k c a l )
36 | d o u b l e c a l c u l a t e C a l o r i e s ( i n t s t e p s ) {
37 | / / ประมาณ 0 . 0 4 5 k c a l ต่อน้ำหนักตัว 1 k g ต่อ 1 , 0 0 0 ก้าว
38 | r e t u r n ( s t e p s / 1 0 0 0 . 0 ) * ( w e i g h t K g * 0 . 5 5 ) ;
39 | }
40 | }

### 5.4 ปฏิบัติการที่ 5.4 การสร้างคอมโพเนนต์ Bento Grid UI

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

CHAPTER 5. ปฏิบัติการพัฒนาแอปพลิเคชัน SMART HEALTH TRACKER ด้วย FLUTTER | 33
48 | T e x t ( s u b t i t l e , s t y l e : T e x t S t y l e ( c o l o r :
a c c e n t C o l o r , f o n t S i z e : 1 1 ) ) ,
49 | ] ,
50 | ) ,
51 | ) ;
52 | }
53 | }

### 5.5 ปฏิบัติการที่ 5.5 การทดสอบสอบเทียบระบบภาคสนาม

ผู้เรียนนำแอปพลิเคชันไปติดตั้งลงในสมาร์ทโฟนจริง และดำเนินการทดสอบเดินจริงในระยะทางและเงื่อนไข ต่างๆ กัน พร้อมใช้ตัวนับก้าวเชิงกลแบบมือกด (Manual Tally Counter) เป็นค่าจริงอ้างอิง (Ground Truth) การทดสอบแบ่งออกเป็น 4 รูปแบบ รูปแบบละ 500 ก้าว

1. การเดินช้าปกติในอาคาร (80 SPM) โดยถือสมาร์ทโฟนในมือ
2. การเดินเร็วกลางแจ้ง (115 SPM) โดยใส่สมาร์ทโฟนในกระเป๋ากางเกง
3. การวิ่งเหยาะในสนามกีฬา (140 SPM) โดยรัดสมาร์ทโฟนที่ต้นแขน
4. การนั่งบนรถโดยสารประจำทาง (ทดสอบสัญญาณรบกวน 15 นาที)

ตารางที่ 5.1 ผลการทดสอบสอบเทียบความแม่นยำในการนับก้าวของแอปพลิเคชัน Smart Health Tracker

สภาวะการทดสอบ | ก้าวจริง (Tally) | ก้าวที่ตรวจจับได้ | ผลต่าง (ก้าว) | ความแม่นยำ (%)
การเดินช้าถือในมือ | 500 | 496 | -4 | 99.20%
การเดินเร็วในกระเป๋ากางเกง | 500 | 494 | -6 | 98.80%
การวิ่งเหยาะรัดต้นแขน | 500 | 503 | +3 | 99.40%
การนั่งบนรถโดยสาร (15 นาที) | 0 | 2 | +2 | 99.60% (ขจัดสัญญาณหลอก)
ค่าเฉลี่ยรวมทุกสภาวะ | 1,500 | 1,493 | -7 | 99.27%

ผลการทดลองแสดงให้เห็นว่า การประมวลผลขนาดเวกเตอร์ยูคลิดสามมิติร่วมกับ Dynamic Peak Detection และ Refractory Period 250 ms ให้ความแม่นยำสูงถึงร้อยละ 99.27 และสามารถขจัดการสั่นสะเทือนของเครื่องยนต์ รถโดยสารได้อย่างมีประสิทธิภาพ

### 5.6 ปฏิบัติการที่ 5.6 การพัฒนาโมเดลปัญญาประดิษฐ์การเรียนรู้เชิงลึกบนอุปกรณ์

ในปฏิบัติการนี้ ผู้เรียนจะสร้างโมเดลโครงข่ายประสาทเทียมหลายชั้น (Deep MLP Neural Network) ใน ไฟล์lib/services/deep_health_ai_engine.dartซึ่งทำงานประมวลผลและเรียนรู้ได้โดยตรงบนสมาร์ทโฟน (On-Device Learning) โดยไม่ต้องพึ่งพาเซิร์ฟเวอร์ภายนอก
โมเดลรับเวกเตอร์อินพุต 6 มิติ ผ่านชั้นฮิดเดน 2 ชั้น (8 และ 6 โหนด) พร้อมฟังก์ชันแอกติเวชัน LeakyReLU และ Tanh สู่ชั้นเอาต์พุต 4 คลาสด้วย Softmax และมีฟังก์ชัน trainOnUserKinematics สำหรับคำนวณเกรเดียนต์และ อัปเดตค่าน้ำหนักด้วย Stochastic Gradient Descent (SGD)

CHAPTER 5. ปฏิบัติการพัฒนาแอปพลิเคชัน SMART HEALTH TRACKER ด้วย FLUTTER | 34

แกนหลักของ DeepHealthAiEngine.dart
1 | c l a s s D e e p H e a l t h A i E n g i n e {
2 | / / สถาปัตยกรรมโครงข่ายประสาทเทียม 6 - > 8 - > 6 - > 4
3 | L i s t < L i s t < d o u b l e > > w 1 = . . . ; / / 6 x 8
4 | L i s t < d o u b l e > b 1 = . . . ;
5 | L i s t < L i s t < d o u b l e > > w 2 = . . . ; / / 8 x 6
6 | L i s t < d o u b l e > b 2 = . . . ;
7 | L i s t < L i s t < d o u b l e > > w 3 = . . . ; / / 6 x 4
8 | L i s t < d o u b l e > b 3 = . . . ;

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

15
16 | L i s t < d o u b l e > z 2 = _ d e n s e ( a 1 , w2 , b 2 ) ;
17 | L i s t < d o u b l e > a 2 = z 2 . m a p ( ( v ) = > ( e x p ( 2 * v ) -
1 ) / ( e x p ( 2 * v ) + 1 ) ) . t o L i s t ( ) ; / / T a n h

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

CHAPTER 5. ปฏิบัติการพัฒนาแอปพลิเคชัน SMART HEALTH TRACKER ด้วย FLUTTER | 35
39 | }

### 5.7 ปฏิบัติการที่ 5.7 การพัฒนาระบบเสียงพูดเตือนและสแนปชอตอัตโนมัติทุก 4 ชั่วโมง

สร้างไฟล์ lib/services/ voice_alert_service.dart เพื่อ จัดการการเล่นเสียงกระตุ้นเตือนโสตประสาท และ ความถี่เสียงเตือน พร้อมคำพูดสังเคราะห์ภาษาไทย “ลุกค่ะ ลุกค่ะ! ได้เวลาลุกขึ้นยืดเส้นยืดสายและขยับร่างกายแล้ว ค่ะ”
| และในไฟล์lib/services/movement_sensor_service.dart ให้ติดตั้งตัวจับเวลา Timer.periodic สำหรับตรวจ
จับพฤติกรรมเนือยนิ่งทุก 30 นาที และตัวจับเวลาบันทึกข้อมูลสุขภาพอัตโนมัติทุก 4 ชั่วโมง (Duration(hours: 4)) พร้อม นโยบายการรีเซ็ตค่าเริ่มต้นเป็นศูนย์ (Zero-Baseline Launch Policy) เมื่อเปิดแอปพลิเคชันใหม่

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

### 5.8 ปฏิบัติการที่ 5.8 การพัฒนาระบบติดตามพิกัด GPS และการเรนเดอร์แผนที่เส้นทาง จริง

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

9
10 | f i n a l d o u b l e c = 2 . 0 * a t a n 2 ( s q r t ( a ) , s q r t ( 1 . 0 - a ) ) ;
11 | r e t u r n 6 3 7 1 0 0 0 . 0 * c ; / / ระยะทางในหน่วยเมตร
12 | }

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

4
5 | / / คำนวณ B o u n d i n g B o x ของพิกัดทั้งหมด
6 | d o u b l e m i n L a t = . . . , m a x L a t = . . . , m i n L n g = . . . ,
m a x L n g = . . . ;

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

24 }

CHAPTER 5. ปฏิบัติการพัฒนาแอปพลิเคชัน SMART HEALTH TRACKER ด้วย FLUTTER | 37

### คำถามทบทวนท้ายบทที่ 5

1. เพราะเหตุใดจึงต้องกำหนดสิทธิ์HIGH_SAMPLING_RATE_SENSORS และสิทธิ์ACCESS_FINE_LOCATION ใน ไฟล์AndroidManifest.xml
2. หาก ต้องการ ปรับ แต่ งอัล กอ ริ ทึม ให้ ตรวจ จับ การ วิ่ง เร็ว ได้ ดี ยิ่ง ขึ้น ควร ปรับ พารามิเตอร์ ใด ใน คลาส StepDetectionEngine
3. จงอธิบายขั้นตอนการทำงานของ Forward Propagation และ Backpropagation ที่เกิดขึ้นภายในคลาส DeepHealthAiEngine บนสมาร์ทโฟน
4. เพราะเหตุใดระบบจึงต้องบันทึกข้อมูลสแนปชอตสรีรวิทยาอัตโนมัติทุก 4 ชั่วโมง เพื่อนำไปใช้วิเคราะห์ร่วมกับ โครงข่ายประสาทเทียม
5. จงอธิบายกลไกการคำนวณระยะทาง Great-Circle Distance ในคลาส GpsWaypoint และการกรองสัญญาณ สะท้อนเทียม (Multipath Noise Filter)
6. จงอธิบายขั้นตอนการแปลงพิกัดภูมิศาสตร์สู่พิกัด ระนาบ 2 มิติของหน้าจอด้วยคลาส CustomPainter ใน แอปพลิเคชัน Flutter

# บรรณานุกรม

American College of Sports Medicine. (2021). ACSM’s guidelines for exercise testing and prescription (11th ed.). Wolters Kluwer.

Fogg, B. J. (2009). A behavior model for persuasive design. Proceedings of the 4th International Conference on Persuasive Technology (Persuasive ’09), Article 40, 1–7. https://doi.org/10.1145/1541948.1541999 (https://doi.org/10.1145/1541948.1541999)
Mifflin, M. D., St Jeor, S. T., Hill, L. A., Scott, B. J., Daugherty, S. A., & Koh, Y. O. (1990). A new predictive equation for resting energy expenditure in healthy individuals. The American Journal of Clinical Nutrition, 51(2), 241–247. https://doi.org/10.1093/ajcn/51.2.241

Thassana, C. (2023). Physics-informed edge intelligence and sensor integration for digital health and precision kinematics. Journal of Applied Physics and Sensor Technology, 15(3), 112–128.

Thassana, C., & Janthamalee, J. (2024). Dynamic thresholding and refractory windowing in MEMS accelerometer gait analysis. IEEE Sensors Journal Letters, 8(2), 45–52.

Tudor-Locke, C., Craig, C. L., Brown, W. J., Clemes, S. A., De Cocker, K., Giles-Corti, B., Hatano, Y., Inoue, S., Matsudo, S. M., Mutrie, N., Oppert, J. M., Rowe, D. A., Schmidt, M. D., Schofield, G. M., Spence, J. C., Teixeira, P. J., Tully, M. A., & Blair, S. N. (2011). How many steps/day are enough? for adults. International Journal of Behavioral Nutrition and Physical Activity, 8(1),
79. https://doi.org/10.1186/1479-5868-8-79

World Health Organization. (2020). WHO guidelines on physical activity and sedentary behaviour. World Health Organization.

ชีวะ ทัศนา. (2567). ฟิสิกส์เชิงคำนวณและ ระบบตรวจ วัดสัญญาณอัจฉริยะสำหรับ วิทยาการข้อมูล. สำนักพิมพ์ มหาวิทยาลัยราชภัฏรำไพพรรณี.

ชีวะ ทัศนา, และ คณะนักวิจัย. (2569). การออกแบบและพัฒนาแอปพลิเคชันเพื่อสุขภาพ การนับก้าวและการตรวจ จับการเคลื่อนไหวร่างกายเชิงสรีรวิทยาประยุกต์. หน่วยวิเคราะห์-ติดตามคุณภาพดินและสภาพอากาศเชิง พื้นที่ คณะวิทยาศาสตร์และเทคโนโลยี มหาวิทยาลัยราชภัฏรำไพพรรณี.

38

# ประวัติผู้เขียน

## ผู้ช่วยศาสตราจารย์ ดร.ชีวะ ทัศนา

หน่วยวิเคราะห์-ติดตามคุณภาพดินและสภาพอากาศเชิงพื้นที่ คณะวิทยาศาสตร์และเทคโนโลยี มหาวิทยาลัยราชภัฏรำไพพรรณี
Email chewa.t@rbru.ac.th | Google Scholar ID jJz3B6AAAAAJ

ประวัติการศึกษา

- ปร.ด. (ฟิสิกส์ประยุกต์)
สถาบัน เทคโนโลยี พระจอมเกล้า เจ้า คุณ ทหาร ลาดกระบัง (KMITL)
- วท.ม. (ฟิสิกส์ประยุกต์)
สถาบัน เทคโนโลยี พระจอมเกล้า เจ้า คุณ ทหาร ลาดกระบัง (KMITL)
- วท.บ. ฟิสิกส์ (คอมพิวเตอร์และอิเล็กทรอนิกส์) มหาวิทยาลัยนเรศวร
รายวิชาที่รับผิดชอบสอน
- ฟิสิกส์สำหรับวิทยาศาสตร์สุขภาพและกีฬา
- การประมวลผลสัญญาณและเซนเซอร์อัจฉริยะ
- ปัญญาประดิษฐ์และการเรียนรู้ของเครื่อง
- การพัฒนาแอปพลิเคชันบนอุปกรณ์พกพา

ความเชี่ยวชาญและงานวิจัยที่สนใจ

- การ ประมวล ผล สัญญาณ ชีว การ แพทย์ และ จลนศาสตร์
(Biomedical Signal Processing and Human Kinematics)
- เซนเซอร์ตรวจวัดความเร่งและอินเทอร์เน็ตของ สรรพสิ่ง
(MEMS Accelerometers, IMU and Edge Health IoT)
- ชีวกลศาสตร์และวิทยาศาสตร์การออกกำลังกาย ประยุกต์
(Applied Biomechanics and Exercise Science)
- สถาปัตยกรรม ส่วน ต่อ ประสาน ผู้ ใช้ ทาง วิทยาศาสตร์
(Scientific Responsive UI/UX and Bento Grid Design)
- ฟิสิกส์เกษตรดิจิทัลและปัญญาประดิษฐ์เชิงพื้นที่ (Digital Agriphysics and Precision Spatial AI)

เอกสารคู่มือวิชาการและวิจัยฉบับสมบูรณ์ มหาวิทยาลัยราชภัฏรำไพพรรณี พุทธศักราช 2569

39
