TsanaPhysics/JC-AGRITecH-AI/leqs-workshop/assets/images/cv_hardware_setup.jpg

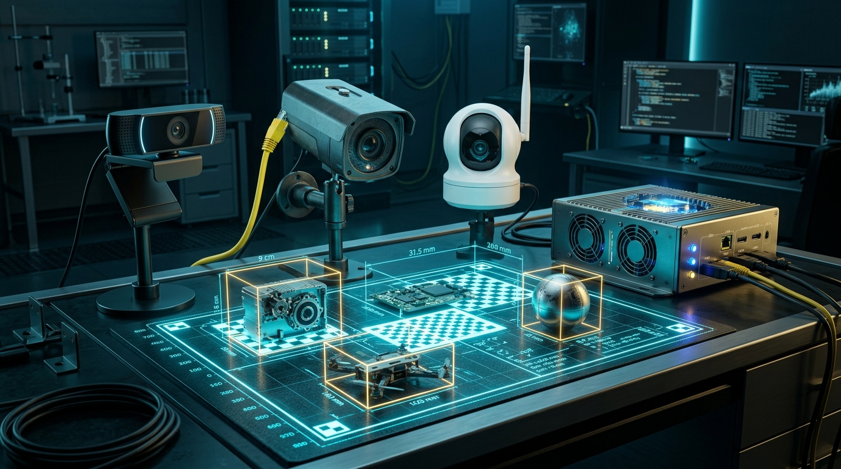
leqs-workshop/assets/images/cv_hardware_setup.jpg
