TsanaPhysics/JC-AGRITecH-AI/thanapat_research/figures/fig3_7_lab_waterbath_calibration.jpg

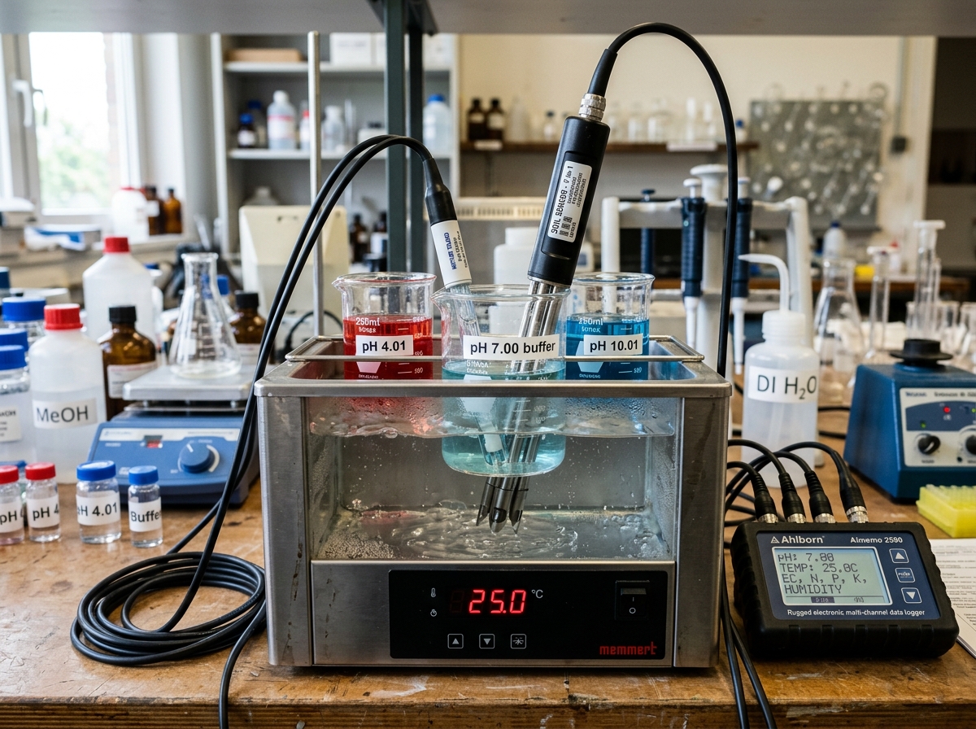
thanapat_research/figures/fig3_7_lab_waterbath_calibration.jpg
