TsanaPhysics/JC-AGRITecH-AI/esp32-board/src/DisplayManager.cpp

#include "DisplayManager.h"
#include "WiFiConfigManager.h"
#include "CloudDataManager.h"
#include "PinConfigs.h"
#include "ThaiFontVLW.h"
#include <WiFi.h>
#include <freertos/FreeRTOS.h>
#include <freertos/task.h>
#include <freertos/queue.h>

static LGFX_ATD35 lcd;

// สีสำหรับ UI Design (RGB565)
#define COLOR_BG          0x0841 // ดำอมน้ำเงินเข้ม
#define COLOR_CARD_BG     0x18E3 // การ์ดพื้นหลังสีเทาเข้ม
#define COLOR_HEADER      0x02E7 // เขียวมรกตเข้ม
#define COLOR_TEXT_DIM    0x9CD3 // สีเทาอ่อน
#define COLOR_TEXT_VAL    0xFFFF // ขาว
#define COLOR_ACCENT      0x3E7C // เขียวสด
#define COLOR_CYAN        0x277E // ฟ้าสว่าง
#define COLOR_YELLOW      0xFDE0 // เหลืองสว่าง/ทอง
#define COLOR_WARN        0xFA08 // ส้ม/แดง
#define COLOR_ACTIVE_TAB  0x07E0 // นีออนเขียวแท็บแอคทีฟ
#define COLOR_INACT_TAB   0x18C3 // เทาเข้มแท็บปกติ

// ตัวแปรควบคุมการแสดงผลและหน้าจอ
static DisplayPage currentPage = PAGE_OVERVIEW;
static bool pageChanged = true;
static unsigned long lastTouchTime = 0;

// บิตแมปภาษาไทย "ชีวะ  ทัศนา" (ความกว้าง 84 x สูง 18 พิกเซล)
const uint16_t THAI_NAME_W = 84;
const uint16_t THAI_NAME_H = 18;
const uint8_t thai_name_bitmap[] = {
    0x00, 0x00, 0x00, 0x00, 0x00, 0x00, 0x00, 0x00, 0x00, 0x00, 0x00,
    0x00, 0x00, 0x00, 0x00, 0x00, 0x00, 0x00, 0x00, 0x00, 0x00, 0x00,
    0x00, 0x00, 0x00, 0x00, 0x00, 0x00, 0x00, 0x00, 0x00, 0x00, 0x00,
    0x00, 0x20, 0x00, 0x00, 0x00, 0x00, 0x07, 0x00, 0x00, 0x00, 0x00,
    0x03, 0xE0, 0x00, 0x00, 0x00, 0x00, 0x05, 0x20, 0x00, 0x00, 0x00,
    0x07, 0xE0, 0x00, 0x00, 0x00, 0x00, 0x03, 0xC0, 0x00, 0x00, 0x00,
    0x00, 0x20, 0x00, 0x00, 0x00, 0x00, 0x00, 0x00, 0x00, 0x00, 0x00,
    0x00, 0x40, 0x00, 0x00, 0x00, 0x00, 0x00, 0x03, 0x00, 0x00, 0x00,
    0x19, 0x87, 0x83, 0x80, 0x00, 0x00, 0xE6, 0x3C, 0x71, 0x1E, 0x00,
    0x34, 0x88, 0xC2, 0xA0, 0x00, 0x00, 0xAA, 0x42, 0x51, 0x23, 0x00,
    0x2C, 0x80, 0x43, 0xC0, 0x00, 0x00, 0x6A, 0x5E, 0x71, 0x01, 0x00,
    0x3C, 0x80, 0x40, 0x00, 0x00, 0x00, 0x32, 0x56, 0x11, 0x01, 0x00,
    0x04, 0x80, 0x43, 0x80, 0x00, 0x00, 0x32, 0x6E, 0x11, 0x01, 0x00,
    0x04, 0x80, 0xC2, 0xA0, 0x00, 0x00, 0x32, 0x22, 0x17, 0x01, 0x00,
    0x04, 0x81, 0x42, 0xA0, 0x00, 0x00, 0x22, 0x22, 0x1F, 0x01, 0x00,
    0x0F, 0x81, 0xC1, 0xC0, 0x00, 0x00, 0x22, 0x22, 0x13, 0x01, 0x00,
    0x00, 0x00, 0x00, 0x00, 0x00, 0x00, 0x00, 0x00, 0x00, 0x00, 0x00,
    0x00, 0x00, 0x00, 0x00, 0x00, 0x00, 0x00, 0x00, 0x00, 0x00, 0x00,
};

// Circular Ring Buffer สำหรับบันทึกประวัติค่าเซนเซอร์ 60 จุดสำหรับพล็อตกราฟ
#define HISTORY_LEN 60
struct SensorHistoryPoint {
    float soilSurface;
    float soilDeep;
    float solarRad;
    float airTemp;
};
static SensorHistoryPoint history[HISTORY_LEN];
static int historyCount = 0;
static int historyHead = 0;

static void addHistoryPoint(float sSurface, float sDeep, float sRad, float aTemp) {
    history[historyHead].soilSurface = sSurface;
    history[historyHead].soilDeep = sDeep;
    history[historyHead].solarRad = sRad;
    history[historyHead].airTemp = aTemp;
    historyHead = (historyHead + 1) % HISTORY_LEN;
    if (historyCount < HISTORY_LEN) {
        historyCount++;
    }
}

static void drawTopNavBar();
static DisplayLanguage currentLanguage = LANG_TH;

// ตัวชี้ฟอนต์ไทย VLW ที่โหลดแล้ว ใช้เลี่ยงการโหลด/ตีความฟอนต์ซ้ำทุกครั้งที่วาด (เดิมโหลดซ้ำหลายสิบครั้งต่อหน้า)
static const lgfx::IFont* g_thaiFontPtr = nullptr;

static inline void ensureThaiFont() {
    if (g_thaiFontPtr == nullptr || lcd.getFont() != g_thaiFontPtr) {
        lcd.loadFont(thai_font_vlw);
        g_thaiFontPtr = lcd.getFont();
    }
}

static inline void ensureAppFont() {
    if (currentLanguage == LANG_ZH) {
        lcd.unloadFont();
        lcd.setFont(&fonts::efontCN_14);
        g_thaiFontPtr = nullptr;
    } else {
        // ใช้ thai_font_vlw (Ayuthaya 16px) ซึ่งรองรับทั้งภาษาไทยครบ 91 ตัว และภาษาอังกฤษ/ตัวเลขครบ 100%
        ensureThaiFont();
    }
}

void DisplayManager_setLanguage(DisplayLanguage lang) {
    if (currentLanguage != lang) {
        currentLanguage = lang;
        ensureAppFont();
        pageChanged = true;
        if (currentPage <= PAGE_WIFI_SETUP) {
            drawTopNavBar();
        }
    }
}

DisplayLanguage DisplayManager_getLanguage() {
    return currentLanguage;
}

void DisplayManager_toggleLanguage() {
    DisplayLanguage nextLang = (currentLanguage == LANG_TH) ? LANG_EN : ((currentLanguage == LANG_EN) ? LANG_ZH : LANG_TH);
    DisplayManager_setLanguage(nextLang);
}

static const char* L_STR(const char *th, const char *en, const char *zh) {
    if (currentLanguage == LANG_TH) return th;
    if (currentLanguage == LANG_ZH) return zh;
    return en;
}

static void drawTopNavBar();
static void drawDetailHeader(const char *th_title, const char *en_title, const char *zh_title, uint16_t accentCol);

static int32_t scrollOffsetY = 0;
static int32_t maxScrollY = 0;

void DisplayManager_setPage(DisplayPage page) {
    if (currentPage != page) {
        currentPage = page;
        pageChanged = true;
        scrollOffsetY = 0;
        if (currentPage >= PAGE_DETAIL_AIR && currentPage <= PAGE_DETAIL_SOIL7) {
            maxScrollY = (currentPage == PAGE_DETAIL_SOIL7) ? 630 : 430;
        } else {
            maxScrollY = 0;
        }
    }
}

DisplayPage DisplayManager_getPage() {
    return currentPage;
}

void DisplayManager_scroll(int deltaY) {
    scrollOffsetY += deltaY;
    if (scrollOffsetY < 0) scrollOffsetY = 0;
    if (scrollOffsetY > maxScrollY) scrollOffsetY = maxScrollY;
    pageChanged = true;
}

int DisplayManager_getScrollY() {
    return scrollOffsetY;
}

// ============================================================================
// แถบเลื่อนสไลด์บาร์แนวตั้งแบบโมเดิร์น (Modern Vertical Scrollbar & Slider Controls)
// ============================================================================
static void drawScrollBar(int scrollY, int maxScroll, int viewTop, int viewHeight, uint16_t accentCol) {
    if (maxScroll <= 0) return;
    int barX = 462;
    int barW = 16;
    int btnH = 14;
    int topBtnY = viewTop + 2;
    int botBtnY = viewTop + viewHeight - btnH - 2;
    int trackY = topBtnY + btnH + 3;
    int trackH = botBtnY - trackY - 3;

    // 1. ปุ่มลูกศรเลื่อนขึ้น (▲ Up Button)
    lcd.fillRoundRect(barX, topBtnY, barW, btnH, 3, (scrollY > 0) ? 0x2166 : 0x10A2);
    lcd.drawRoundRect(barX, topBtnY, barW, btnH, 3, 0x4208);
    lcd.fillTriangle(barX + barW / 2, topBtnY + 3, barX + 3, topBtnY + btnH - 4, barX + barW - 4, topBtnY + btnH - 4, (scrollY > 0) ? accentCol : 0x632C);

    // 2. ปุ่มลูกศรเลื่อนลง (▼ Down Button)
    lcd.fillRoundRect(barX, botBtnY, barW, btnH, 3, (scrollY < maxScroll) ? 0x2166 : 0x10A2);
    lcd.drawRoundRect(barX, botBtnY, barW, btnH, 3, 0x4208);
    lcd.fillTriangle(barX + barW / 2, botBtnY + btnH - 3, barX + 3, botBtnY + 4, barX + barW - 4, botBtnY + 4, (scrollY < maxScroll) ? accentCol : 0x632C);

    // 3. รางเลื่อน Track สีเข้มเรียบหรู
    lcd.fillRoundRect(barX + 2, trackY, barW - 4, trackH, 3, 0x0842);
    lcd.drawRoundRect(barX + 2, trackY, barW - 4, trackH, 3, 0x2945);

    // 4. ตัวเลื่อน Thumb (คำนวณตามสัดส่วนความยาวเนื้อหา)
    int thumbH = max(38, trackH * 280 / (280 + maxScroll));
    int thumbY = trackY + (scrollY * (trackH - thumbH) / maxScroll);
    lcd.fillRoundRect(barX + 1, thumbY, barW - 2, thumbH, 4, accentCol);
    lcd.drawRoundRect(barX + 1, thumbY, barW - 2, thumbH, 4, 0xFFFF);

    // ลายกริปสัมผัส (Tactile Grip Lines) ตรงกลาง Thumb
    int midY = thumbY + thumbH / 2;
    lcd.drawFastHLine(barX + 4, midY - 2, barW - 8, 0x0000);
    lcd.drawFastHLine(barX + 4, midY + 2, barW - 8, 0x0000);
}

// ============================================================================
// ฟังก์ชันวาดป้ายแคปซูล Cyber Badge Tag (สวยงาม คมชัด ตาม Mockup)
// ============================================================================
static int drawBadgeTag(int x, int y, const char *text, uint16_t fill_color, uint16_t text_color, uint16_t border_color, int w = 0, int h = 18) {
    if (w <= 0) {
        w = lcd.textWidth(text) + 12;
    }
    lcd.fillRoundRect(x, y, w, h, 4, fill_color);
    if (border_color != fill_color) {
        lcd.drawRoundRect(x, y, w, h, 4, border_color);
    }
    lcd.setTextColor(text_color, fill_color);
    lcd.setTextDatum(textdatum_t::middle_center);
    lcd.drawString(text, x + w / 2, y + h / 2);
    lcd.setTextDatum(textdatum_t::top_left);
    return x + w + 8; // ส่งคืนแกน X สำหรับข้อความถัดไป
}


// ============================================================================
// SVG-Style Vector Graphic Icons (ไอคอนกราฟิกเวกเตอร์คมชัดแทนข้อความ)
// ============================================================================

// 1. ไอคอนเทอร์โมมิเตอร์ (อุณหภูมิ / Temperature) 🌡️
static void drawIconThermometer(int x, int y, uint16_t col) {
    lcd.drawRoundRect(x + 2, y, 6, 12, 2, 0xFFFF);
    lcd.fillCircle(x + 5, y + 13, 5, col);
    lcd.drawCircle(x + 5, y + 13, 5, 0xFFFF);
    lcd.fillRect(x + 4, y + 4, 2, 8, col);
}

// 2. ไอคอนหยดน้ำ (ความชื้น / Humidity) 💧
static void drawIconDroplet(int x, int y, uint16_t col) {
    lcd.fillCircle(x + 6, y + 10, 5, col);
    lcd.fillTriangle(x + 1, y + 9, x + 11, y + 9, x + 6, y + 2, col);
    lcd.drawPixel(x + 4, y + 8, 0xFFFF);
    lcd.drawPixel(x + 4, y + 9, 0xFFFF);
}

// 3. ไอคอนดวงอาทิตย์ (รังสีดวงอาทิตย์ / Solar Radiation) ☀️
static void drawIconSun(int x, int y, uint16_t col) {
    lcd.fillCircle(x + 7, y + 7, 4, col);
    lcd.drawCircle(x + 7, y + 7, 4, 0xFFFF);
    lcd.drawFastVLine(x + 7, y, 3, col);
    lcd.drawFastVLine(x + 7, y + 11, 3, col);
    lcd.drawFastHLine(x, y + 7, 3, col);
    lcd.drawFastHLine(x + 11, y + 7, 3, col);
    lcd.drawLine(x + 2, y + 2, x + 4, y + 4, col);
    lcd.drawLine(x + 12, y + 12, x + 10, y + 10, col);
    lcd.drawLine(x + 12, y + 2, x + 10, y + 4, col);
    lcd.drawLine(x + 2, y + 12, x + 4, y + 10, col);
}

// 4. ไอคอนหลอดไฟ (ความสว่าง / Illuminance Lux) 💡
static void drawIconBulb(int x, int y, uint16_t col) {
    lcd.fillCircle(x + 6, y + 6, 5, col);
    lcd.fillRect(x + 4, y + 11, 4, 3, 0xC618);
    lcd.drawPixel(x + 6, y + 1, col);
    lcd.drawPixel(x + 1, y + 4, col);
    lcd.drawPixel(x + 11, y + 4, col);
}

// 5. ไอคอนต้นกล้าผิวดิน (ความชื้นดินตื้น / Soil Moisture) 🌱
static void drawIconSprout(int x, int y, uint16_t col) {
    lcd.drawFastHLine(x, y + 14, 14, 0x9CD3); // ผิวดิน
    lcd.drawFastVLine(x + 6, y + 5, 9, 0x07E0); // ก้าน
    lcd.fillTriangle(x + 6, y + 8, x + 6, y + 5, x, y + 5, col); // ใบซ้าย
    lcd.fillTriangle(x + 6, y + 7, x + 6, y + 4, x + 12, y + 4, 0x07E0); // ใบขวา
}

// 6. ไอคอนขวดเคมีดิน (NPK & Soil Chemistry) 🧪
static void drawIconFlask(int x, int y, uint16_t col) {
    lcd.drawRect(x + 4, y, 4, 4, 0xFFFF);
    lcd.fillTriangle(x + 6, y + 4, x, y + 14, x + 12, y + 14, col);
    lcd.drawTriangle(x + 6, y + 4, x, y + 14, x + 12, y + 14, 0xFFFF);
    lcd.drawPixel(x + 4, y + 11, 0x07E0); // เม็ด N
    lcd.drawPixel(x + 6, y + 12, 0x07FF); // เม็ด P
    lcd.drawPixel(x + 8, y + 11, 0xFFE0); // เม็ด K
}

// ============================================================================
// Big Vector Graphic Icons (ไอคอนสัญลักษณ์ขนาดใหญ่สำหรับโหมดเน้นตัวเลข)
// ============================================================================

// 1. ไอคอนเทอร์โมมิเตอร์ขนาดใหญ่ 🌡️
static void drawBigIconThermometer(int x, int y, uint16_t col) {
    lcd.drawRoundRect(x + 4, y, 10, 20, 4, 0xFFFF);
    lcd.fillCircle(x + 9, y + 22, 9, col);
    lcd.drawCircle(x + 9, y + 22, 9, 0xFFFF);
    lcd.fillRect(x + 7, y + 6, 4, 14, col);
}

// 2. ไอคอนหยดน้ำขนาดใหญ่ 💧
static void drawBigIconDroplet(int x, int y, uint16_t col) {
    lcd.fillCircle(x + 10, y + 16, 9, col);
    lcd.fillTriangle(x + 2, y + 14, x + 18, y + 14, x + 10, y + 2, col);
    lcd.drawCircle(x + 10, y + 16, 9, 0xFFFF);
    lcd.drawPixel(x + 6, y + 12, 0xFFFF);
    lcd.drawPixel(x + 7, y + 13, 0xFFFF);
    lcd.drawPixel(x + 6, y + 14, 0xFFFF);
}

// 3. ไอคอนดวงอาทิตย์ขนาดใหญ่ ☀️
static void drawBigIconSun(int x, int y, uint16_t col) {
    lcd.fillCircle(x + 13, y + 13, 7, col);
    lcd.drawCircle(x + 13, y + 13, 7, 0xFFFF);
    lcd.drawFastVLine(x + 13, y, 5, col);
    lcd.drawFastVLine(x + 13, y + 21, 5, col);
    lcd.drawFastHLine(x, y + 13, 5, col);
    lcd.drawFastHLine(x + 21, y + 13, 5, col);
    lcd.drawLine(x + 3, y + 3, x + 7, y + 7, col);
    lcd.drawLine(x + 23, y + 23, x + 19, y + 19, col);
    lcd.drawLine(x + 23, y + 3, x + 19, y + 7, col);
    lcd.drawLine(x + 3, y + 23, x + 7, y + 19, col);
}

// 4. ไอคอนหลอดไฟขนาดใหญ่ 💡
static void drawBigIconBulb(int x, int y, uint16_t col) {
    lcd.fillCircle(x + 10, y + 10, 8, col);
    lcd.drawCircle(x + 10, y + 10, 8, 0xFFFF);
    lcd.fillRect(x + 7, y + 18, 6, 5, 0xC618);
    lcd.drawRect(x + 7, y + 18, 6, 5, 0xFFFF);
    lcd.drawPixel(x + 10, y + 2, 0xFFFF);
    lcd.drawPixel(x + 3, y + 6, col);
    lcd.drawPixel(x + 17, y + 6, col);
}

// 5. ไอคอนต้นกล้าผิวดินขนาดใหญ่ 🌱
static void drawBigIconSprout(int x, int y, uint16_t col) {
    lcd.drawFastHLine(x, y + 24, 24, 0x9CD3); // ผิวดิน
    lcd.drawFastVLine(x + 11, y + 8, 16, 0x07E0); // ลำต้น
    lcd.fillTriangle(x + 11, y + 14, x + 11, y + 8, x + 2, y + 8, col); // ใบซ้าย
    lcd.drawTriangle(x + 11, y + 14, x + 11, y + 8, x + 2, y + 8, 0xFFFF);
    lcd.fillTriangle(x + 11, y + 12, x + 11, y + 6, x + 20, y + 6, 0x07E0); // ใบขวา
    lcd.drawTriangle(x + 11, y + 12, x + 11, y + 6, x + 20, y + 6, 0xFFFF);
}

// 6. ไอคอนขวดเคมีดินขนาดใหญ่ 🧪
static void drawBigIconFlask(int x, int y, uint16_t col) {
    lcd.drawRect(x + 7, y, 6, 6, 0xFFFF);
    lcd.fillTriangle(x + 10, y + 6, x, y + 24, x + 20, y + 24, col);
    lcd.drawTriangle(x + 10, y + 6, x, y + 24, x + 20, y + 24, 0xFFFF);
    lcd.fillCircle(x + 7, y + 18, 2, 0x07E0); // เม็ด N
    lcd.fillCircle(x + 10, y + 20, 2, 0x07FF); // เม็ด P
    lcd.fillCircle(x + 13, y + 18, 2, 0xFFE0); // เม็ด K
}

// ฟังก์ชันวาดหน่วย W/m² โดยให้เลข 2 เป็นตัวยก (Superscript)
static void drawUnitW_m2(int x, int y, uint16_t col, uint16_t bg) {
    lcd.setTextColor(col, bg);
    ensureAppFont();
    lcd.drawString("W/m", x, y);
    int wmWidth = lcd.textWidth("W/m");
    lcd.drawString("2", x + wmWidth + 1, y - 4, &fonts::Font0);
    ensureAppFont();
}

// วาดแท็บด้านบนขนาดใหญ่ 5 แท็บ + ปุ่มสลับภาษา (TH / EN / 中文)
static void drawTopNavBar() {
    ensureAppFont();
    struct TabInfo {
        int x;
        int w;
    };
    TabInfo tabs[5] = {
        {2, 78},
        {82, 78},
        {162, 78},
        {242, 78},
        {322, 78}
    };

    const char *tab_names_th[5] = {"1.ภาพรวม", "2.ข้อมูล", "3.กราฟ", "4.รีเลย์", "5.ตั้งค่า"};
    const char *tab_names_en[5] = {"1.HOME", "2.DATA", "3.GRAPH", "4.RELAY", "5.SETUP"};
    const char *tab_names_zh[5] = {"1.主页", "2.数据", "3.图表", "4.继电器", "5.设置"};

    // สีเฉพาะของแต่ละแท็บ (active: สีสด, inactive: สีเข้มหม่น)
    const uint16_t tab_active_colors[5]  = {0x07FF, 0x07E0, 0xFD20, 0xF81F, 0xFFE0}; // cyan, green, orange, magenta, yellow
    const uint16_t tab_dim_colors[5]     = {0x0410, 0x0320, 0x3800, 0x5004, 0x3180}; // dimmed versions
    const uint16_t tab_border_colors[5]  = {0x07FF, 0x07E0, 0xFD20, 0xF81F, 0xFFE0};

    for (int i = 0; i < 5; i++) {
        bool isActive = (currentPage == (DisplayPage)i);
        uint16_t bg     = isActive ? tab_active_colors[i] : tab_dim_colors[i];
        uint16_t border = tab_border_colors[i];
        uint16_t textCol = isActive ? 0x0000 : tab_active_colors[i];

        lcd.fillRoundRect(tabs[i].x, 2, tabs[i].w, 30, 5, bg);
        lcd.drawRoundRect(tabs[i].x, 2, tabs[i].w, 30, 5, border);

        const char *label = (currentLanguage == LANG_TH) ? tab_names_th[i] : ((currentLanguage == LANG_ZH) ? tab_names_zh[i] : tab_names_en[i]);
        lcd.setTextColor(textCol, bg);
        lcd.setTextDatum(textdatum_t::middle_center);
        lcd.drawString(label, tabs[i].x + (tabs[i].w / 2), 2 + 15);
        lcd.setTextDatum(textdatum_t::top_left);
    }

    // ปุ่มสลับ 3 ภาษา (TH / EN / 中文) ที่ x: 404, w: 74 พร้อมไอคอนลูกโลก 🌐
    const char *lang_chip = (currentLanguage == LANG_TH) ? "ไทย" : ((currentLanguage == LANG_ZH) ? "中文" : "ENG");
    uint16_t chip_border = (currentLanguage == LANG_TH) ? COLOR_ACCENT : ((currentLanguage == LANG_ZH) ? COLOR_YELLOW : COLOR_CYAN);
    lcd.fillRoundRect(404, 2, 74, 30, 5, 0x18E3);
    lcd.drawRoundRect(404, 2, 74, 30, 5, chip_border);

    // วาดไอคอนลูกโลก 🌐 หน้าชื่อภาษา
    lcd.drawCircle(416, 17, 5, chip_border);
    lcd.drawFastHLine(411, 17, 11, chip_border);
    lcd.drawFastVLine(416, 12, 11, chip_border);

    lcd.setTextColor(chip_border, 0x18E3);
    lcd.setTextDatum(textdatum_t::middle_center);
    lcd.drawString(lang_chip, 404 + 44, 2 + 15);
    lcd.setTextDatum(textdatum_t::top_left);
}

// แถบหัวด้านบนสำหรับหน้าจอแสดงรายละเอียดเซนเซอร์เดี่ยว (Multi-Language)
static void drawDetailHeader(const char *th_title, const char *en_title, const char *zh_title, uint16_t accentCol) {
    ensureAppFont();
    const char *title = L_STR(th_title, en_title, zh_title);
    const char *back_lbl = L_STR("<ย้อน", "<BACK", "<返回");
    const char *next_lbl = L_STR("ถัดไป>", "NEXT>", "下一>");
    const char *lang_chip = (currentLanguage == LANG_TH) ? "ไทย" : ((currentLanguage == LANG_ZH) ? "中文" : "ENG");

    // 1. ปุ่ม [ < BACK ]
    lcd.fillRoundRect(4, 2, 70, 30, 5, 0x18C3);
    lcd.drawRoundRect(4, 2, 70, 30, 5, 0xFFFF);
    lcd.setTextColor(0xFFFF, 0x18C3);
    lcd.setTextDatum(textdatum_t::middle_center);
    lcd.drawString(back_lbl, 4 + 35, 2 + 15);

    // 2. ชื่อเซนเซอร์ตรงกลาง (ขยายความกว้างเป็น 252px สวยงาม ไม่เบียด)
    lcd.fillRoundRect(78, 2, 252, 30, 5, COLOR_CARD_BG);
    lcd.drawRoundRect(78, 2, 252, 30, 5, accentCol);
    lcd.setTextColor(accentCol, COLOR_CARD_BG);
    lcd.drawString(title, 78 + 126, 2 + 15);

    // 3. ปุ่ม [ NEXT > ]
    lcd.fillRoundRect(334, 2, 70, 30, 5, 0x028A);
    lcd.drawRoundRect(334, 2, 70, 30, 5, COLOR_CYAN);
    lcd.setTextColor(COLOR_CYAN, 0x028A);
    lcd.drawString(next_lbl, 334 + 35, 2 + 15);

    // 4. ปุ่มภาษา [ TH/EN/中 ]
    uint16_t chip_border = (currentLanguage == LANG_TH) ? COLOR_ACCENT : ((currentLanguage == LANG_ZH) ? COLOR_YELLOW : COLOR_CYAN);
    lcd.fillRoundRect(408, 2, 68, 30, 5, 0x18E3);
    lcd.drawRoundRect(408, 2, 68, 30, 5, chip_border);
    lcd.setTextColor(chip_border, 0x18E3);
    lcd.drawString(lang_chip, 408 + 34, 2 + 15);
    lcd.setTextDatum(textdatum_t::top_left);
}

// ============================================================================
// SPLASH SCREEN - LEQs-AgriEnvi-xAI: Neural Plant Nexus (Option 2)
// ปัญญาประดิษฐ์เพื่อเกษตรดิจิทัลและสิ่งแวดล้อม (Deep Learning + Living Plant + Precision Sensors)
// ============================================================================
static void drawSplashScreen() {
    const int cx = 240;
    const int cy = 76; // Nexus center (AI brain + sprout)
    const uint16_t goldC = 0xFDE0; // RBRU Gold
    const uint16_t SBGC  = 0x0020; // Deep Obsidian Dark Background

    lcd.fillScreen(SBGC);

    // ─────────────────────────────────────────────────────────────
    // Phase 1: Deep Tech Awakening (Ambient Halo & Background Synapses)
    // ─────────────────────────────────────────────────────────────
    // Soft concentric ambient aura rings around the nexus
    lcd.drawCircle(cx, cy, 78, 0x08A2);
    lcd.drawCircle(cx, cy, 64, 0x0903);
    lcd.drawCircle(cx, cy, 50, 0x0964);

    // Faint neural nodes & connection lines in the background
    int bgNodes[][2] = {
        {60, 40}, {110, 30}, {370, 30}, {420, 45},
        {45, 95}, {100, 110}, {380, 105}, {435, 90},
        {75, 140}, {405, 145}
    };
    for (int i = 0; i < 10; i++) {
        lcd.fillCircle(bgNodes[i][0], bgNodes[i][1], 2, 0x0273);
    }
    // Faint connection lines between background nodes
    lcd.drawLine(60, 40, 110, 30, 0x0162);
    lcd.drawLine(110, 30, 100, 110, 0x0162);
    lcd.drawLine(60, 40, 45, 95, 0x0162);
    lcd.drawLine(45, 95, 75, 140, 0x0162);
    lcd.drawLine(370, 30, 420, 45, 0x0162);
    lcd.drawLine(370, 30, 380, 105, 0x0162);
    lcd.drawLine(420, 45, 435, 90, 0x0162);
    lcd.drawLine(435, 90, 405, 145, 0x0162);

    // ─────────────────────────────────────────────────────────────
    // Phase 2: Holographic Orbital Telemetry & Precision Sensor Nodes
    // ─────────────────────────────────────────────────────────────
    // Orbit 1 (inner): rx=96, ry=30
    for (int deg = 0; deg < 360; deg += 10) {
        float rad = deg * 0.0174533f;
        int ox = cx + (int)(96 * cos(rad));
        int oy = cy + 6 + (int)(30 * sin(rad));
        if (deg % 30 == 0) lcd.drawPixel(ox, oy, 0x04F8);
        else lcd.drawPixel(ox, oy, 0x01C6);
    }
    // Orbit 2 (outer): rx=124, ry=38
    for (int deg = 0; deg < 360; deg += 12) {
        float rad = deg * 0.0174533f;
        int ox = cx + (int)(124 * cos(rad));
        int oy = cy + 6 + (int)(38 * sin(rad));
        if (deg % 24 == 0) lcd.drawPixel(ox, oy, 0x0374);
        else lcd.drawPixel(ox, oy, 0x0103);
    }

    // Floating Sensor Telemetry Badges (4 Precision Farm Parameters)
    // 1. TEMP (Upper Left)
    lcd.fillRoundRect(134, 40, 56, 15, 3, 0x0164);
    lcd.drawRoundRect(134, 40, 56, 15, 3, 0x0478);
    lcd.setTextDatum(textdatum_t::middle_center);
    lcd.setTextColor(0x07FF, 0x0164);
    lcd.drawString("24.5'C", 162, 48, &fonts::Font0);
    lcd.drawLine(190, 48, 208, 62, 0x0375); // line to brain

    // 2. HUM (Upper Right)
    lcd.fillRoundRect(290, 40, 56, 15, 3, 0x0164);
    lcd.drawRoundRect(290, 40, 56, 15, 3, 0x0478);
    lcd.setTextColor(0x07E0, 0x0164);
    lcd.drawString("HUM 68%", 318, 48, &fonts::Font0);
    lcd.drawLine(290, 48, 272, 62, 0x0375);

    // 3. SOIL (Lower Right)
    lcd.fillRoundRect(306, 92, 60, 15, 3, 0x0164);
    lcd.drawRoundRect(306, 92, 60, 15, 3, 0x0478);
    lcd.setTextColor(0x3E7C, 0x0164);
    lcd.drawString("SOIL 72%", 336, 100, &fonts::Font0);
    lcd.drawLine(306, 100, 270, 92, 0x0375);

    // 4. VPD (Lower Left)
    lcd.fillRoundRect(114, 92, 60, 15, 3, 0x0164);
    lcd.drawRoundRect(114, 92, 60, 15, 3, 0x0478);
    lcd.setTextColor(0xFDE0, 0x0164);
    lcd.drawString("VPD 1.12", 144, 100, &fonts::Font0);
    lcd.drawLine(174, 100, 210, 92, 0x0375);

    delay(70);

    // ─────────────────────────────────────────────────────────────
    // Phase 3: AI Brain & Synaptic Circuit Nexus (Cerebral Cortex)
    // ─────────────────────────────────────────────────────────────
    // Brain Base / Chip Socket
    const int by = cy + 18; // y ≈ 94
    lcd.fillRoundRect(cx - 16, by - 6, 32, 16, 3, 0x0287);
    lcd.drawRoundRect(cx - 16, by - 6, 32, 16, 3, 0x07FF);
    lcd.setTextDatum(textdatum_t::middle_center);
    lcd.setTextColor(0xFFFF, 0x0287);
    lcd.drawString("AI", cx, by + 1, &fonts::Font0);

    // Left & Right Hemisphere Synapse Circuit Branches
    // Left hemisphere circuit paths:
    lcd.drawLine(cx - 16, by, cx - 32, by - 4, 0x07FF);
    lcd.drawLine(cx - 32, by - 4, cx - 36, by - 16, 0x07FF);
    lcd.drawLine(cx - 36, by - 16, cx - 26, by - 24, 0x067A);
    lcd.drawLine(cx - 26, by - 24, cx - 12, by - 20, 0x07E0);

    lcd.drawLine(cx - 24, by - 8, cx - 14, by - 14, 0x067A);
    lcd.drawLine(cx - 32, by - 4, cx - 44, by, 0x067A);

    // Right hemisphere circuit paths:
    lcd.drawLine(cx + 16, by, cx + 32, by - 4, 0x07FF);
    lcd.drawLine(cx + 32, by - 4, cx + 36, by - 16, 0x07FF);
    lcd.drawLine(cx + 36, by - 16, cx + 26, by - 24, 0x067A);
    lcd.drawLine(cx + 26, by - 24, cx + 12, by - 20, 0x07E0);

    lcd.drawLine(cx + 24, by - 8, cx + 14, by - 14, 0x067A);
    lcd.drawLine(cx + 32, by - 4, cx + 44, by, 0x067A);

    // Synapse Nodes / Micro-vias (dots)
    int synNodes[][2] = {
        {cx - 44, by}, {cx - 36, by - 16}, {cx - 26, by - 24}, {cx - 12, by - 20},
        {cx + 44, by}, {cx + 36, by - 16}, {cx + 26, by - 24}, {cx + 12, by - 20},
        {cx - 24, by - 8}, {cx + 24, by - 8}
    };
    for (int i = 0; i < 10; i++) {
        lcd.fillCircle(synNodes[i][0], synNodes[i][1], 3, 0x07FF);
        lcd.fillCircle(synNodes[i][0], synNodes[i][1], 1, 0xFFFF);
    }
    delay(80);

    // ─────────────────────────────────────────────────────────────
    // Phase 4: Living Sprout (Growing from AI Core)
    // ─────────────────────────────────────────────────────────────
    // Central Stem rising from AI core to canopy
    for (int sy = by - 6; sy >= cy - 36; sy -= 2) {
        lcd.drawFastVLine(cx - 1, sy, 3, 0x07E0);
        lcd.drawFastVLine(cx,     sy, 3, 0xFFFF);
        lcd.drawFastVLine(cx + 1, sy, 3, 0x07E0);
    }

    // Left Leaf (Bio-Emerald leaf rising up-left)
    for (int t = 0; t <= 12; t++) {
        float f = t / 12.0f;
        int lx = cx - 2 - (int)(30 * sin(f * 1.57f));
        int ly = cy - 10 - (int)(38 * f);
        int thick = (int)(9 * sin(f * 3.14159f));
        lcd.drawLine(lx - thick, ly, lx + thick, ly, 0x05E0 + (t * 0x0040));
    }
    // Left leaf outer contour & glowing tip
    lcd.drawLine(cx - 2, cy - 10, cx - 18, cy - 32, 0x07E0);
    lcd.drawLine(cx - 18, cy - 32, cx - 32, cy - 48, 0x07FF);
    lcd.drawLine(cx - 32, cy - 48, cx - 18, cy - 44, 0x07E0);
    lcd.drawLine(cx - 18, cy - 44, cx - 2, cy - 38, 0x07E0);
    // Left leaf circuit vein
    lcd.drawLine(cx - 4, cy - 18, cx - 24, cy - 38, 0x07FF);
    lcd.fillCircle(cx - 24, cy - 38, 2, 0xFFFF);

    // Right Leaf (Golden-Emerald leaf rising up-right)
    for (int t = 0; t <= 12; t++) {
        float f = t / 12.0f;
        int rx = cx + 2 + (int)(34 * sin(f * 1.57f));
        int ry = cy - 14 - (int)(40 * f);
        int thick = (int)(10 * sin(f * 3.14159f));
        lcd.drawLine(rx - thick, ry, rx + thick, ry, 0x27E0 + (t * 0x0800));
    }
    // Right leaf outer contour & glowing tip
    lcd.drawLine(cx + 2, cy - 14, cx + 20, cy - 36, 0x07E0);
    lcd.drawLine(cx + 20, cy - 36, cx + 36, cy - 54, 0xFDE0);
    lcd.drawLine(cx + 36, cy - 54, cx + 20, cy - 48, 0x07E0);
    lcd.drawLine(cx + 20, cy - 48, cx + 2, cy - 42, 0x07E0);
    // Right leaf circuit vein
    lcd.drawLine(cx + 4, cy - 22, cx + 26, cy - 44, 0x07FF);
    lcd.fillCircle(cx + 26, cy - 44, 2, 0xFFFF);

    // Radiating Golden Seed Sparkle at top
    lcd.fillCircle(cx, cy - 42, 3, 0xFFFF);
    lcd.drawCircle(cx, cy - 42, 5, 0xFDE0);
    delay(80);

    // ─────────────────────────────────────────────────────────────
    // Phase 5: Branding - "LEQs-AgriEnvi-xAI"
    // ─────────────────────────────────────────────────────────────
    lcd.setTextDatum(textdatum_t::middle_center);
    
    // Glowing shadow layers for 3D neon presence
    lcd.setTextColor(0x01A6, SBGC);
    lcd.drawString("LEQs-AgriEnvi-xAI", cx + 2, 147, &fonts::Font4);
    lcd.drawString("LEQs-AgriEnvi-xAI", cx - 1, 145, &fonts::Font4);
    
    // Crisp face with dual-color accents
    lcd.setTextDatum(textdatum_t::middle_right);
    lcd.setTextColor(0x07FF, SBGC);
    lcd.drawString("LEQs-AgriEnvi-", cx + 24, 146, &fonts::Font4);
    lcd.setTextDatum(textdatum_t::middle_left);
    lcd.setTextColor(0x07E0, SBGC);
    lcd.drawString("xAI", cx + 24, 146, &fonts::Font4);
    delay(80);

    // ─────────────────────────────────────────────────────────────
    // Phase 6: Thai Subtitle & Technology Pillars
    // ─────────────────────────────────────────────────────────────
    ensureThaiFont();
    lcd.setTextDatum(textdatum_t::middle_center);
    
    // Subtitle in Thai: "ปัญญาประดิษฐ์เพื่อเกษตรดิจิทัลและสิ่งแวดล้อม"
    lcd.setTextColor(0x0182, SBGC);
    lcd.drawString("ปัญญาประดิษฐ์เพื่อเกษตรดิจิทัลและสิ่งแวดล้อม", cx + 1, 177); // shadow
    lcd.setTextColor(0xFFFF, SBGC);
    lcd.drawString("ปัญญาประดิษฐ์เพื่อเกษตรดิจิทัลและสิ่งแวดล้อม", cx, 176);     // crisp white
    delay(80);

    // Tech Pillars: "Digital | IoT | Smart Farm | Edge AI"
    lcd.setTextColor(0x3DFF, SBGC);
    lcd.drawString("Digital  |  IoT  |  Smart Farm  |  Edge AI", cx, 204);
    delay(80);

    // ─────────────────────────────────────────────────────────────
    // Phase 7: Academic Attribution (Authors & University)
    // ─────────────────────────────────────────────────────────────
    ensureThaiFont();
    // Co-Authors (White)
    lcd.setTextColor(0xFFFF, SBGC);
    lcd.drawString("ผศ.ดร.จิรภัทร จันทมาลี   |   ผศ.ดร.ชีวะ ทัศนา", cx, 234);
    delay(70);

    // University (RBRU Gold)
    lcd.setTextColor(goldC, SBGC);
    lcd.drawString("มหาวิทยาลัยราชภัฏรำไพพรรณี", cx, 258);
    delay(80);

    // ─────────────────────────────────────────────────────────────
    // Phase 8: Ultra-Thin Glowing Laser Progress Bar Track Setup
    // ─────────────────────────────────────────────────────────────
    const int bx = 40, by_bar = 296, bw = 400, bh = 8;
    lcd.drawRoundRect(bx - 1, by_bar - 1, bw + 2, bh + 2, 4, 0x0478);
    lcd.fillRoundRect(bx, by_bar, bw, bh, 3, 0x0164); // Dark track background
    delay(50);
}

void DisplayManager_showBootProgress(const char* stepName, int percent) {
    const uint16_t SBGC = 0x0020; // Deep Obsidian Dark Background
    const int bx = 40, by_bar = 296, bw = 400, bh = 8;

    int clamped = (percent < 0) ? 0 : (percent > 100 ? 100 : percent);

    // 1. เคลียร์และวาดแถบข้อความสถานะด้านบน Progress bar
    lcd.fillRect(20, 274, 440, 18, SBGC);
    ensureThaiFont();
    
    // ข้อความขั้นตอน (ด้านซ้าย) สีฟ้าไซแอนเรืองแสง
    lcd.setTextDatum(textdatum_t::middle_left);
    lcd.setTextColor(0x07FF, SBGC);
    lcd.drawString(stepName, bx, 283);

    // ตัวเลขเปอร์เซ็นต์ (ด้านขวา) สีนีออนเขียวมรกต
    char pctBuf[16];
    snprintf(pctBuf, sizeof(pctBuf), "%d%%", clamped);
    lcd.setTextDatum(textdatum_t::middle_right);
    lcd.setTextColor(0x07E0, SBGC);
    lcd.drawString(pctBuf, bx + bw, 283);

    // 2. เคลียร์และวาดหลอดความคืบหน้า (Progress Bar)
    int fillW = (bw * clamped) / 100;
    if (fillW > 0) {
        // ครึ่งแรก (0-50%) สีฟ้าไซแอน (0x07FF) ครึ่งหลัง (51-100%) สีเขียวมรกต (0x07E0)
        int midW = (fillW < (bw / 2)) ? fillW : (bw / 2);
        lcd.fillRoundRect(bx, by_bar, midW, bh, 3, 0x07FF);
        if (fillW > (bw / 2)) {
            lcd.fillRoundRect(bx + (bw / 2) - 2, by_bar, fillW - (bw / 2) + 2, bh, 3, 0x07E0);
        }

        // หัวเลเซอร์เรืองแสงสีขาว (Laser Flare)
        if (fillW < bw) {
            lcd.fillCircle(bx + fillW, by_bar + (bh / 2), 4, 0xFFFF);
            lcd.drawCircle(bx + fillW, by_bar + (bh / 2), 5, 0x07FF);
        } else {
            lcd.fillRoundRect(bx, by_bar, bw, bh, 3, 0x07E0);
        }
    }

    lcd.setTextDatum(textdatum_t::top_left);
    Serial.printf("[Boot %3d%%] %s\n", clamped, stepName);
}

// ============================================================================
// Touch Polling Task: อ่านทัช FT6336U อิสระจากการวาดจอ (8 ms/รอบ) -> ส่งเหตุการณ์เข้าคิว
// ============================================================================
static const uint8_t TE_DOWN = 0;
static const uint8_t TE_MOVE = 1;
static const uint8_t TE_UP   = 2;

struct TouchEvent {
    uint8_t type;
    int16_t x;
    int16_t y;
};

static QueueHandle_t touchQueue = nullptr;

static void touchPollTask(void *arg) {
    bool down = false;
    uint8_t missCount = 0;
    int32_t lastX = 0, lastY = 0;
    TickType_t wake = xTaskGetTickCount();

    for (;;) {
        int32_t x = 0, y = 0;
        bool touched = lcd.getTouch(&x, &y);
        TouchEvent ev;

        if (touched) {
            missCount = 0;
            if (!down) {
                down = true;
                lastX = x;
                lastY = y;
                ev.type = TE_DOWN; ev.x = (int16_t)x; ev.y = (int16_t)y;
                xQueueSend(touchQueue, &ev, 0);
            } else if (abs(x - lastX) >= 3 || abs(y - lastY) >= 3) {
                lastX = x;
                lastY = y;
                ev.type = TE_MOVE; ev.x = (int16_t)x; ev.y = (int16_t)y;
                xQueueSend(touchQueue, &ev, 0);  // MOVE ทิ้งได้ถ้าคิวเต็ม
            }
        } else if (down) {
            // ต้องไม่พบการสัมผัสติดกัน 2 รอบ (~16 ms) จึงถือว่าปล่อยนิ้ว กันสัญญาณกระตุก
            if (++missCount >= 2) {
                down = false;
                missCount = 0;
                ev.type = TE_UP; ev.x = (int16_t)lastX; ev.y = (int16_t)lastY;
                xQueueSend(touchQueue, &ev, pdMS_TO_TICKS(30));  // UP ห้ามหาย
            }
        }
        vTaskDelayUntil(&wake, pdMS_TO_TICKS(8));
    }
}

static void startTouchTask() {
    if (touchQueue != nullptr) return;
    touchQueue = xQueueCreate(48, sizeof(TouchEvent));
    if (touchQueue != nullptr) {
        xTaskCreatePinnedToCore(touchPollTask, "touchPoll", 4096, nullptr, 3, nullptr, 1);
    }
}

void DisplayManager_finishBoot(const FarmSensorTelemetry &data, bool pumpState, bool mistingState) {
    DisplayManager_showBootProgress("ระบบพร้อมทำงานสมบูรณ์ 100%!", 100);
    delay(400);

    // เคลียร์จอและโหลดฟอนต์หลัก
    lcd.fillScreen(COLOR_BG);
    ensureAppFont();

    // สลับเข้าหน้าแสดงผลหลักทันที พร้อมเรนเดอร์ข้อมูลสดรอบแรก
    pageChanged = true;
    DisplayManager_update(data, pumpState, mistingState);
    startTouchTask();  // เริ่มรับทัชหลังบูตเสร็จ (ไม่มีเหตุการณ์ค้างจากช่วงบูต)
    Serial.println("[Display] Seamless transition to Overview Dashboard completed.");
}

void DisplayManager_init() {
    Serial.println("[Display] Initializing 3.5\" IPS ST7796 LCD Display...");

    pinMode(LCD_BL_PIN, OUTPUT);
    digitalWrite(LCD_BL_PIN, HIGH);

    lcd.init();
    lcd.setRotation(1); // แนวนอน 480x320
    lcd.setBrightness(255);
    digitalWrite(LCD_BL_PIN, HIGH);
    lcd.fillScreen(0x0020);

    // โหลดฟอนต์ไทยก่อนแสดง splash (ใช้สำหรับชื่อผู้พัฒนา)
    ensureThaiFont();

    // แสดง splash screen LEQs-AgriEnvi-xAI (คงหน้าจอไว้ตลอดการบูต)
    drawSplashScreen();

    // แสดงสถานะบูตเริ่มต้น (10%)
    DisplayManager_showBootProgress("กำลังเริ่มต้นระบบและจัดเตรียมฮาร์ดแวร์...", 10);

    Serial.println("[Display] Display initialized with Splash Screen & Boot Progress.");
}


// ============================================================================
// แถบหัวด้านบนสำหรับหน้าภาพรวม (LEQs-AgriEnvi-xAI Branding + Wi-Fi Status + ปุ่มภาษา)
// ============================================================================
static void drawOverviewTopHeader() {
    // พื้นหลังแถบ Header ดำออบซิเดียนหรู ไร้เส้นรบกวนตา
    lcd.fillRect(0, 0, 480, 38, 0x0862);

    // โลโก้ LEQs สไตล์ Modern Cyber Emblem:
    int jx = 12, jy = 12;
    // ก้าน L สีฟ้าไซแอนนีออน (0x07FF) และฐานมรกตนีออน (0x07E0)
    lcd.fillRect(jx + 2, jy + 2, 4, 13, 0x07FF);
    lcd.fillRect(jx + 2, jy + 11, 11, 4, 0x07E0);
    lcd.fillCircle(jx + 13, jy + 13, 2, 0x07E0);

    // ========================================================================
    // ข้อความ "LEQs-AgriEnvi-xAI" หลายสีสัน ทันสมัย โดเด่น (Cyber Tech Branding)
    // ========================================================================
    ensureThaiFont();
    lcd.setTextDatum(textdatum_t::middle_left);
    int brandX = 32;
    int brandY = 19;

    // "LEQs": ฟ้าไซแอนนีออน (Electric Cyan 0x07FF)
    lcd.setTextColor(0x07FF, 0x0862);
    lcd.drawString("LEQs", brandX, brandY);
    brandX += lcd.textWidth("LEQs") + 1;

    // "-": เทาสเตนเลส (0x9CF3)
    lcd.setTextColor(0x9CF3, 0x0862);
    lcd.drawString("-", brandX, brandY);
    brandX += lcd.textWidth("-") + 1;

    // "Agri": เขียวมรกตนีออน (Neon Emerald 0x07E0)
    lcd.setTextColor(0x07E0, 0x0862);
    lcd.drawString("Agri", brandX, brandY);
    brandX += lcd.textWidth("Agri");

    // "Envi": ทองนีออน (Solar Amber Gold 0xFFE0)
    lcd.setTextColor(0xFFE0, 0x0862);
    lcd.drawString("Envi", brandX, brandY);
    brandX += lcd.textWidth("Envi") + 4;

    // "xAI": แคปซูลไซเบอร์ม่วงมาเจนต้านีออนเรืองแสง (Cyber Violet Pill Badge)
    int aiW = 28, aiH = 18;
    int aiY = brandY - (aiH / 2);
    lcd.fillRoundRect(brandX, aiY, aiW, aiH, 4, 0x780F); // ม่วงเข้มไวโอเล็ต
    lcd.drawRoundRect(brandX, aiY, aiW, aiH, 4, 0xF81F); // ขอบชมพูมาเจนต้านีออน
    lcd.setTextDatum(textdatum_t::middle_center);
    lcd.setTextColor(0xFFFF, 0x780F); // ตัวอักษรสีขาวสว่าง
    lcd.drawString("xAI", brandX + (aiW / 2), brandY);
    lcd.setTextDatum(textdatum_t::top_left);

    // พิกัด GPS สถานที่ดำเนินงานจริงตามจุดติดตั้งเซนเซอร์
    char gpsHeaderBuf[64];
    snprintf(gpsHeaderBuf, sizeof(gpsHeaderBuf), "GPS: %.4f N, %.4f E (%s)",
             SENSOR_GPS_LATITUDE, SENSOR_GPS_LONGITUDE, SENSOR_GPS_LOCATION_NAME);
    lcd.setTextColor(0x07E0, 0x0862);
    lcd.drawString(gpsHeaderBuf, 12, 32, &fonts::Font0);

    // ========================================================================
    // แคปซูลแสดง วันที่และเวลาเรียลไทม์ (Date & Time Capsule) - Option A
    // แสดงผล: วันที่/เดือน/ปี และ เวลาสด พร้อมกระพริบจุดวินาที
    // ========================================================================
    int timeCapsuleX = 208, timeCapsuleY = 6, timeCapsuleW = 168, timeCapsuleH = 26;
    lcd.fillRoundRect(timeCapsuleX, timeCapsuleY, timeCapsuleW, timeCapsuleH, 13, 0x0185); // พื้นหลังเข้มหรู
    lcd.drawRoundRect(timeCapsuleX, timeCapsuleY, timeCapsuleW, timeCapsuleH, 13, 0x07E0); // ขอบเขียวมรกตเรืองแสง หนา 2px
    lcd.drawRoundRect(timeCapsuleX + 1, timeCapsuleY + 1, timeCapsuleW - 2, timeCapsuleH - 2, 12, 0x15D3);

    // ดึงค่าสตริงวันที่และเวลาปัจจุบัน
    String dateStr = CloudDataManager_getDateString();
    String timeStr = CloudDataManager_getTimeString();
    char dtBuf[36];
    if (dateStr != "--/--/----") {
        // ตัดปีเป็น 2 หลักท้าย e.g. 12/09/26 11:20:30
        String yrShort = dateStr.substring(8);
        snprintf(dtBuf, sizeof(dtBuf), "%s/%s %s", dateStr.substring(0, 5).c_str(), yrShort.c_str(), timeStr.c_str());
    } else {
        snprintf(dtBuf, sizeof(dtBuf), "NTP SYNCING...");
    }

    lcd.setTextDatum(textdatum_t::middle_center);
    lcd.setTextColor(0x07FF, 0x0185); // ฟ้าไซแอนสไตล์ดิจิทัล
    ensureAppFont();
    lcd.drawString(dtBuf, timeCapsuleX + (timeCapsuleW / 2), timeCapsuleY + 13);

    // ไอคอน Wi-Fi: คลื่น 3 ระดับสีเขียวนีออน + จุดศูนย์กลาง
    bool wifiOk = (WiFi.status() == WL_CONNECTED);
    uint16_t wifiCol = wifiOk ? 0x15D3 : 0x52AA;
    int wx = 392, wy = 26;
    lcd.fillCircle(wx, wy, 2, wifiCol);
    lcd.fillArc(wx, wy, 5, 7, 225, 315, wifiCol);
    lcd.fillArc(wx, wy, 9, 11, 225, 315, wifiCol);
    lcd.fillArc(wx, wy, 13, 15, 225, 315, wifiCol);

    // ปุ่มสลับภาษาทรงแคปซูลมนสีดำ [ 🇹🇭 TH ]
    int px = 416, py = 7, pw = 56, ph = 26;
    lcd.fillRoundRect(px, py, pw, ph, 13, 0x18E3);
    lcd.drawRoundRect(px, py, pw, ph, 13, 0x39E7);

    // ตราธงชาติไทยทรงกลมด้านซ้ายของแคปซูล
    int fx = px + 12, fy = py + 13, fr = 7;
    lcd.fillCircle(fx, fy, fr, 0xD800); // พื้นแดง
    lcd.fillRect(fx - fr + 1, fy - 4, (fr * 2) - 2, 8, 0xFFFF); // แถบขาว
    lcd.fillRect(fx - fr + 1, fy - 2, (fr * 2) - 2, 4, 0x0017); // แถบน้ำเงิน
    lcd.drawCircle(fx, fy, fr, 0x39E7);

    // ตัวอักษร "TH" / "EN" / "ZH" สีขาว
    lcd.setTextColor(0xFFFF, 0x18E3);
    lcd.setTextDatum(textdatum_t::middle_left);
    const char *langShort = (currentLanguage == LANG_TH) ? "TH" : ((currentLanguage == LANG_ZH) ? "ZH" : "EN");
    lcd.drawString(langShort, px + 25, py + 13);
    lcd.setTextDatum(textdatum_t::top_left);
}

// อัปเดตเฉพาะแคปซูลเวลาด้านบนทุกวินาทีโดยไม่ทำให้หน้าจอกระพริบ
static void updateTopHeaderClock() {
    int timeCapsuleX = 208, timeCapsuleY = 6, timeCapsuleW = 168, timeCapsuleH = 26;
    
    String dateStr = CloudDataManager_getDateString();
    String timeStr = CloudDataManager_getTimeString();
    char dtBuf[36];
    if (dateStr != "--/--/----") {
        String yrShort = dateStr.substring(8);
        snprintf(dtBuf, sizeof(dtBuf), "%s/%s %s", dateStr.substring(0, 5).c_str(), yrShort.c_str(), timeStr.c_str());
    } else {
        snprintf(dtBuf, sizeof(dtBuf), "NTP SYNCING...");
    }

    lcd.fillRoundRect(timeCapsuleX + 2, timeCapsuleY + 2, timeCapsuleW - 4, timeCapsuleH - 4, 11, 0x0185);
    lcd.setTextDatum(textdatum_t::middle_center);
    lcd.setTextColor(0x07FF, 0x0185);
    ensureAppFont();
    lcd.drawString(dtBuf, timeCapsuleX + (timeCapsuleW / 2), timeCapsuleY + 13);
    lcd.setTextDatum(textdatum_t::top_left);

    // อัปเดตไอคอน Wi-Fi ทุกวินาที
    bool wifiOk = (WiFi.status() == WL_CONNECTED);
    uint16_t wifiCol = wifiOk ? 0x15D3 : 0x52AA;
    int wx = 392, wy = 26;
    lcd.fillCircle(wx, wy, 2, wifiCol);
    lcd.fillArc(wx, wy, 5, 7, 225, 315, wifiCol);
    lcd.fillArc(wx, wy, 9, 11, 225, 315, wifiCol);
    lcd.fillArc(wx, wy, 13, 15, 225, 315, wifiCol);
}

// ============================================================================
// แถบปุ่มนำทาง 4 ปุ่มด้านล่างสำหรับหน้าภาพรวม (Bottom Navigation Bar)
// ============================================================================
static void drawOverviewBottomNav() {
    ensureAppFont();

    const char *lbl_home  = L_STR("1. ภาพรวม", "1. HOME", "1.主页");
    const char *lbl_graph = L_STR("2. กราฟ", "2. GRAPH", "2.图表");
    const char *lbl_relay = L_STR("3. รีเลย์", "3. RELAYS", "3.继电器");
    const char *lbl_setup = L_STR("4. ตั้งค่า", "4. SETUP", "4.设置");

    // ปุ่ม 1: ภาพรวม (Active: พื้นเขียวมรกต 0x0320, ขอบเขียวสดหนา 2 ชั้น คมกริบ + ไฮไลต์ 3D)
    lcd.fillRoundRect(10, 274, 106, 38, 8, 0x0320);
    lcd.drawRoundRect(10, 274, 106, 38, 8, 0x07E0);
    lcd.drawRoundRect(11, 275, 104, 36, 7, 0x15D3);
    lcd.drawFastHLine(14, 276, 98, 0x3FE0); // ไฮไลต์แสงตกกระทบขอบบน 3D Bevel
    lcd.drawFastHLine(14, 274 + 36, 98, 0x0180); // เงาล่าง
    lcd.setTextColor(0xFFFF, 0x0320);
    lcd.setTextDatum(textdatum_t::middle_center);
    lcd.drawString(lbl_home, 10 + 53, 274 + 19);

    // ปุ่ม 2: ข้อมูล/กราฟ (พื้น 0x0926, ขอบฟ้าหนา 2 ชั้น คมกริบ + ไฮไลต์ 3D)
    lcd.fillRoundRect(126, 274, 106, 38, 8, 0x0926);
    lcd.drawRoundRect(126, 274, 106, 38, 8, 0x07FF);
    lcd.drawRoundRect(127, 275, 104, 36, 7, 0x0471);
    lcd.drawFastHLine(130, 276, 98, 0x5FFF); // ไฮไลต์ฟ้าสว่าง
    lcd.drawFastHLine(130, 274 + 36, 98, 0x0185); // เงาล่าง
    lcd.setTextColor(0x9E7F, 0x0926);
    lcd.setTextDatum(textdatum_t::middle_center);
    lcd.drawString(lbl_graph, 126 + 53, 274 + 19);

    // ปุ่ม 3: รีเลย์ (พื้นสีทับทิมเข้ม 0x4002, ขอบแดงทับทิมนีออนหนา 2 ชั้น สว่างคมกริบ + ไฮไลต์ 3D)
    lcd.fillRoundRect(242, 274, 106, 38, 8, 0x4002);
    lcd.drawRoundRect(242, 274, 106, 38, 8, 0xF948); // ขอบแดงทับทิมนีออนสว่างสดใส (Vibrant Ruby Coral)
    lcd.drawRoundRect(243, 275, 104, 36, 7, 0xFD20); // ชั้นในส้มแสดนีออนเรืองแสง
    lcd.drawFastHLine(246, 276, 98, 0xFBAE); // ไฮไลต์ชมพูส้มสว่าง
    lcd.drawFastHLine(246, 274 + 36, 98, 0x2000); // เงาล่าง
    lcd.setTextColor(0xFFFF, 0x4002); // ข้อความสีขาวสว่างคมชัด
    lcd.setTextDatum(textdatum_t::middle_center);
    lcd.drawString(lbl_relay, 242 + 53, 274 + 19);

    // ปุ่ม 4: ตั้งค่า (พื้น 0x2902, ขอบเหลืองทองหนา 2 ชั้น คมกริบ + ไฮไลต์ 3D)
    lcd.fillRoundRect(358, 274, 106, 38, 8, 0x2902);
    lcd.drawRoundRect(358, 274, 106, 38, 8, 0xFFE0);
    lcd.drawRoundRect(359, 275, 104, 36, 7, 0xB2A1);
    lcd.drawFastHLine(362, 276, 98, 0xFFFA); // ไฮไลต์เหลืองทองสว่าง
    lcd.drawFastHLine(362, 274 + 36, 98, 0x1800); // เงาล่าง
    lcd.setTextColor(0xFDE8, 0x2902);
    lcd.setTextDatum(textdatum_t::middle_center);
    lcd.drawString(lbl_setup, 358 + 53, 274 + 19);

    lcd.setTextDatum(textdatum_t::top_left);
}

// ============================================================================
// หน้าที่ 1: ภาพรวมสถานะแปลง (Overview & Health Dashboard) - Masterpiece Layout
// 100% Matching with smart_farm_ui_overview.jpg
// ============================================================================
static void drawPageOverview(const FarmSensorTelemetry &data, bool pumpState, bool mistingState) {
    char buf[64];

    if (pageChanged) {
        lcd.fillRect(0, 0, 480, 320, 0x0862); // พื้นหลังรวมสีดำออบซิเดียนหรู
        drawOverviewTopHeader();

        // -------------------------------------------------------------
        // -------------------------------------------------------------
        // การ์ด 1: สภาพอากาศรอบแปลง (x: 10, y: 42, w: 224, h: 114)
        // -------------------------------------------------------------
        lcd.fillRoundRect(10, 42, 224, 114, 10, 0x10E4);
        // ขอบฟ้านีออนหนา 3 ชั้น คมชัด เรืองแสง (High-Contrast Bold Bezel)
        lcd.drawRoundRect(10, 42, 224, 114, 10, 0x07FF);
        lcd.drawRoundRect(11, 43, 222, 112, 9, 0x07FF);
        lcd.drawRoundRect(12, 44, 220, 110, 8, 0x03FF);
        ensureThaiFont();
        const char *t1 = L_STR("สภาพอากาศรอบแปลง", "Microclimate Weather", "微气候环境");
        lcd.setTextColor(0x07FF, 0x10E4); // สีฟ้าไซแอนนีออนสดใส
        lcd.drawString(t1, 20, 48);
        lcd.drawString(t1, 21, 48); // วาดซ้ำเยื้อง 1px เพื่อให้ตัวหนา คมชัด (Bold)

        // -------------------------------------------------------------
        // การ์ด 2: แสงอาทิตย์ โดมตะวัน (x: 246, y: 42, w: 224, h: 114)
        // -------------------------------------------------------------
        lcd.fillRoundRect(246, 42, 224, 114, 10, 0x10E4);
        // ขอบส้มทองนีออนหนา 3 ชั้น คมชัด เรืองแสง (High-Contrast Bold Bezel)
        lcd.drawRoundRect(246, 42, 224, 114, 10, 0xFFE0);
        lcd.drawRoundRect(247, 43, 222, 112, 9, 0xFFE0);
        lcd.drawRoundRect(248, 44, 220, 110, 8, 0xFD20);
        ensureThaiFont();
        const char *t2 = L_STR("ความเข้มแสงโดมตะวัน", "Solar Dome Light", "太阳辐射强度");
        lcd.setTextColor(0xFFE0, 0x10E4); // สีเหลืองทองนีออนสว่างสดใส
        lcd.drawString(t2, 258, 50);
        lcd.drawString(t2, 259, 50); // วาดซ้ำเยื้อง 1px เพื่อให้ตัวหนา คมชัด (Bold)

        // ดวงอาทิตย์สีทองเรืองแสง (Hollow ring + 8 rays)
        int cx = 292, cy = 104;
        lcd.fillCircle(cx, cy, 14, 0xFD20);
        lcd.fillCircle(cx, cy, 9, 0x10E4); // cutout ตรงกลาง
        // 8 รังสีรอบวง
        lcd.fillRect(cx - 1, cy - 24, 3, 7, 0xFD20);
        lcd.fillRect(cx - 1, cy + 17, 3, 7, 0xFD20);
        lcd.fillRect(cx - 24, cy - 1, 7, 3, 0xFD20);
        lcd.fillRect(cx + 17, cy - 1, 7, 3, 0xFD20);
        lcd.drawLine(cx - 12, cy - 12, cx - 17, cy - 17, 0xFD20);
        lcd.drawLine(cx - 11, cy - 12, cx - 16, cy - 17, 0xFD20);
        lcd.drawLine(cx + 12, cy - 12, cx + 17, cy - 17, 0xFD20);
        lcd.drawLine(cx + 11, cy - 12, cx + 16, cy - 17, 0xFD20);
        lcd.drawLine(cx - 12, cy + 12, cx - 17, cy + 17, 0xFD20);
        lcd.drawLine(cx - 11, cy + 12, cx - 16, cy + 17, 0xFD20);
        lcd.drawLine(cx + 12, cy + 12, cx + 17, cy + 17, 0xFD20);
        lcd.drawLine(cx + 11, cy + 12, cx + 16, cy + 17, 0xFD20);

        // -------------------------------------------------------------
        // การ์ด 3: ความชื้นในดินผิวดิน (x: 10, y: 164, w: 224, h: 102)
        // -------------------------------------------------------------
        lcd.fillRoundRect(10, 164, 224, 102, 10, 0x10E4);
        // ขอบเขียวมรกตนีออนหนา 3 ชั้น คมชัด เรืองแสง (High-Contrast Bold Bezel)
        lcd.drawRoundRect(10, 164, 224, 102, 10, 0x07E0);
        lcd.drawRoundRect(11, 165, 222, 100, 9, 0x07E0);
        lcd.drawRoundRect(12, 166, 220, 98, 8, 0x1FE6);
        ensureThaiFont();
        const char *t3 = L_STR("ความชื้นในดิน (ผิวดิน)", "Soil Moisture", "土壤水分");
        lcd.setTextColor(0x07E0, 0x10E4); // สีเขียวมรกตนีออนสว่างสดใส
        lcd.drawString(t3, 20, 172);
        lcd.drawString(t3, 21, 172); // วาดซ้ำเยื้อง 1px เพื่อให้ตัวหนา คมชัด (Bold)

        // ไอคอนต้นกล้าผิวดินสไตล์มินิมอลโมเดิร์น
        int sx = 26, sy = 212;
        lcd.fillArc(sx + 14, sy + 30, 9, 11, 210, 330, 0x07FF); // คลื่นผิวดิน
        lcd.fillRect(sx + 13, sy + 14, 3, 14, 0x15D3); // ก้าน
        lcd.fillCircle(sx + 7, sy + 18, 5, 0x15D3);
        lcd.fillCircle(sx + 21, sy + 14, 5, 0x15D3);

        // -------------------------------------------------------------
        // การ์ด 4: ธาตุอาหารดินลึก & pH (x: 246, y: 164, w: 224, h: 102)
        // -------------------------------------------------------------
        lcd.fillRoundRect(246, 164, 224, 102, 10, 0x10E4);
        // ขอบเหลืองทองนีออนหนา 3 ชั้น คมชัด เรืองแสง (High-Contrast Bold Bezel)
        lcd.drawRoundRect(246, 164, 224, 102, 10, 0xFFE0);
        lcd.drawRoundRect(247, 165, 222, 100, 9, 0xFFE0);
        lcd.drawRoundRect(248, 166, 220, 98, 8, 0xFD20);
        ensureThaiFont();
        const char *t4 = L_STR("ธาตุอาหารดิน & pH", "Deep Soil NPK & pH", "土壤养分与pH");
        lcd.setTextColor(0xFFE0, 0x10E4); // สีเหลืองทองนีออนสว่างสดใส (Yellow Tone ตามคำขอ)
        lcd.drawString(t4, 258, 172);
        lcd.drawString(t4, 259, 172); // วาดซ้ำเยื้อง 1px เพื่อให้ตัวหนา คมชัด (Bold)

        // ป้ายสัญลักษณ์ AI-Edge แสดงว่าใช้ TinyML ชดเชยอุณหภูมิและความชื้นแล้ว
        lcd.fillRoundRect(396, 172, 64, 16, 4, 0x0320);
        lcd.drawRoundRect(396, 172, 64, 16, 4, 0x07E0);
        lcd.drawRoundRect(397, 173, 62, 14, 3, 0x07E0);
        lcd.setTextColor(0x07E0, 0x0320);
        lcd.setTextDatum(textdatum_t::middle_center);
        lcd.drawString("AI-Edge", 396 + 32, 172 + 8, &fonts::Font0);
        lcd.setTextDatum(textdatum_t::top_left);

        // แถบปุ่มนำทาง 4 ปุ่มด้านล่าง
        drawOverviewBottomNav();

        pageChanged = false;
    }

    // ========================================================================
    // อัปเดตข้อมูลการ์ด 1: Microclimate Weather
    // ========================================================================
    // ล้างพื้นที่แสดงผลแถวที่ 1 (อุณหภูมิ & ความชื้น) และแถวที่ 2 (VPD)
    lcd.fillRect(14, 68, 216, 36, 0x10E4);
    lcd.fillRect(14, 107, 216, 45, 0x10E4);

    // เส้นแบ่งระดับชั้นบางเบาอย่างหรูหราระหว่างแถว 1 และแถว 2
    lcd.drawFastHLine(20, 105, 204, 0x1A4F);

    // --- แถวที่ 1 ด้านบน: ตัวเลขอุณหภูมิ (ซ้าย) e.g. 32.90 °C ---
    if (data.air.isConnected) {
        snprintf(buf, sizeof(buf), "%.2f", data.air.temperature);
        lcd.setTextColor(0xFFFF, 0x10E4);
        lcd.drawString(buf, 20, 74, &fonts::Font4);
        int tW = lcd.textWidth(buf, &fonts::Font4);
        ensureAppFont();
        // สัญลักษณ์องศาเซลเซียส °C (สีฟ้าสว่างสดใส)
        lcd.drawCircle(20 + tW + 4, 78, 3, 0x07FF);
        lcd.setTextColor(0x07FF, 0x10E4);
        lcd.drawString("C", 20 + tW + 9, 74);
    } else {
        lcd.setTextColor(0xFA08, 0x10E4);
        lcd.drawString("--.--", 20, 74, &fonts::Font4);
        ensureAppFont();
    }

    // --- แถวที่ 1 ด้านบน: ตัวเลขความชื้นสัมพัทธ์ (ขวา) e.g. 78.10 %RH ---
    if (data.air.isConnected) {
        snprintf(buf, sizeof(buf), "%.2f", data.air.humidity);
        lcd.setTextColor(0xFFFF, 0x10E4);
        lcd.drawString(buf, 126, 74, &fonts::Font4);
        int hW = lcd.textWidth(buf, &fonts::Font4);
        ensureAppFont();
        // หน่วย %RH (สีฟ้าสว่างสดใส)
        lcd.setTextColor(0x07FF, 0x10E4);
        lcd.drawString("%RH", 126 + hW + 3, 81);
    } else {
        lcd.setTextColor(0xFA08, 0x10E4);
        lcd.drawString("--.--", 126, 74, &fonts::Font4);
        ensureAppFont();
    }

    // --- แถวที่ 2 ด้านล่าง: ค่า VPD ให้อยู่กึ่งกลาง และฟอนต์ขนาดเท่ากับอุณหภูมิ (Font4) ---
    if (data.air.isConnected) {
        snprintf(buf, sizeof(buf), "%.2f", data.air.vpd);
    } else {
        snprintf(buf, sizeof(buf), "--.--");
    }

    int vpdNumW = lcd.textWidth(buf, &fonts::Font4);
    ensureAppFont();
    int vpdPrefixW = lcd.textWidth("VPD ");
    int vpdUnitW = lcd.textWidth(" kPa");
    int totalVpdW = vpdPrefixW + vpdNumW + vpdUnitW;
    int vpdStartX = 122 - (totalVpdW / 2); // จัดกึ่งกลางการ์ด 1 (x: 10 ถึง 234)

    // ป้ายกำกับ "VPD " สีเขียวนีออนสว่างสดใส
    lcd.setTextColor(0x07E0, 0x10E4);
    lcd.drawString("VPD ", vpdStartX, 122);

    // ตัวเลขค่า VPD สีขาวสว่างคมชัด ขนาดเท่ากับอุณหภูมิเป๊ะๆ (&fonts::Font4)
    lcd.setTextColor(0xFFFF, 0x10E4);
    lcd.drawString(buf, vpdStartX + vpdPrefixW, 116, &fonts::Font4);
    ensureAppFont();

    // หน่วย " kPa" สีฟ้าไซแอนสว่างสดใส
    lcd.setTextColor(0x07FF, 0x10E4);
    lcd.drawString(" kPa", vpdStartX + vpdPrefixW + vpdNumW, 122);

    // ========================================================================
    // อัปเดตข้อมูลการ์ด 2: Solar Dome
    // ========================================================================
    // แถวที่ 1: kLux e.g. 52.40 kLux
    lcd.fillRect(340, 72, 126, 32, 0x10E4);
    if (data.light.isConnected) {
        snprintf(buf, sizeof(buf), "%.2f", data.light.lux / 1000.0f);
        lcd.setTextColor(0xFFFF, 0x10E4);
        lcd.drawString(buf, 342, 74, &fonts::Font4);
        int lW = lcd.textWidth(buf, &fonts::Font4);
        ensureAppFont();
        // หน่วย kLux สีเหลืองทองสว่างสดใส
        lcd.setTextColor(0xFFE0, 0x10E4);
        lcd.drawString("kLux", 342 + lW + 4, 78);
    } else {
        lcd.setTextColor(0xFA08, 0x10E4);
        lcd.drawString("--.--", 342, 74, &fonts::Font4);
        ensureAppFont();
    }

    // แถวที่ 2: W/m² e.g. 414.00 W/m²
    lcd.fillRect(340, 106, 126, 36, 0x10E4);
    if (data.light.isConnected) {
        snprintf(buf, sizeof(buf), "%.2f", data.light.solarRadiation);
        lcd.setTextColor(0xFFFF, 0x10E4);
        lcd.drawString(buf, 342, 110, &fonts::Font4);
        int sW = lcd.textWidth(buf, &fonts::Font4);
        ensureAppFont();
        // หน่วย W/m² สีเหลืองทองสว่างสดใส
        drawUnitW_m2(342 + sW + 4, 112, 0xFFE0, 0x10E4);
    } else {
        lcd.setTextColor(0xFA08, 0x10E4);
        lcd.drawString("--.--", 342, 110, &fonts::Font4);
        ensureAppFont();
    }

    // ========================================================================
    // อัปเดตข้อมูลการ์ด 3: Soil Moisture (Semi-Circular Arc Radial Gauge)
    // ========================================================================
    int gcx = 140, gcy = 248;
    // เคลียร์พื้นที่เกจและตัวเลข
    lcd.fillRect(66, 194, 164, 68, 0x10E4);

    // แททร็กโค้งพื้นหลัง 180 องศา (หงายขึ้นด้านบน 180 ถึง 360 องศา)
    lcd.fillArc(gcx, gcy, 36, 43, 180, 360, 0x2146);

    // แททร็กความคืบหน้าแบบเรเดียลตามค่าความชื้น
    float m = constrain(data.soilStick.moisture, 0.0f, 100.0f);
    float sweepAngle = (m / 100.0f) * 180.0f;
    float endAngle = 180.0f + sweepAngle;
    if (sweepAngle > 1.0f) {
        // ส่วนโค้งเรเดียลสีเขียวมรกต/ฟ้าสดใส
        lcd.fillArc(gcx, gcy, 36, 43, 180.0f, endAngle, 0x15D3);
        // ฝาปิดปลายกลมที่ 180 องศา
        lcd.fillCircle(gcx - 39, gcy, 3, 0x15D3);
        // ฝาปิดปลายกลมที่จุดสิ้นสุด
        float rad = (endAngle * 3.14159265f) / 180.0f;
        lcd.fillCircle(gcx + (int)(39.5f * cosf(rad)), gcy + (int)(39.5f * sinf(rad)), 3, 0x15D3);
    }

    // ค่าตัวเลขใหญ่ตรงกลางเกจ e.g. 42.5 % (ทศนิยมตำแหน่งเดียว)
    snprintf(buf, sizeof(buf), "%.1f", data.soilStick.moisture);
    lcd.setTextColor(0xFFFF, 0x10E4);
    lcd.setTextDatum(textdatum_t::middle_right);
    lcd.drawString(buf, gcx + 18, gcy - 8, &fonts::Font4);
    ensureAppFont();
    // หน่วย % สีเขียวมรกตนีออนสว่างสดใส
    lcd.setTextColor(0x07E0, 0x10E4);
    lcd.setTextDatum(textdatum_t::middle_left);
    lcd.drawString("%", gcx + 22, gcy - 4);
    lcd.setTextDatum(textdatum_t::top_left);

    // ========================================================================
    // อัปเดตข้อมูลการ์ด 4: Deep Soil NPK & pH (แสดงผลทศนิยม 1 ตำแหน่งตามข้อกำหนด)
    // ========================================================================
    // แถวที่ 1: pH (Soil 7-in-1 จริง) และ EC
    lcd.fillRect(256, 192, 210, 30, 0x10E4);
    // ป้าย pH สีเขียวนีออนสว่าง
    lcd.setTextColor(0x07E0, 0x10E4);
    lcd.drawString("pH", 256, 197);
    snprintf(buf, sizeof(buf), "%.1f", data.soil7in1.ph);
    lcd.setTextColor(0xFFFF, 0x10E4);
    lcd.drawString(buf, 282, 194, &fonts::Font4);
    ensureAppFont();

    // ป้าย EC สีฟ้าไซแอนนีออนสว่าง
    lcd.setTextColor(0x07FF, 0x10E4);
    lcd.drawString("EC", 336, 197);
    snprintf(buf, sizeof(buf), "%.1f", data.soil7in1.ec);
    lcd.setTextColor(0xFFFF, 0x10E4);
    lcd.drawString(buf, 358, 194, &fonts::Font4);
    int ecW = lcd.textWidth(buf, &fonts::Font4);
    ensureAppFont();
    // หน่วย uS/cm สีฟ้าสว่างสดใส
    lcd.setTextColor(0x3DFF, 0x10E4);
    lcd.drawString("uS/cm", 358 + ecW + 2, 200);

    // แถวที่ 2: แคปซูลเม็ดยาสามสี N, P, K (ทศนิยม 1 ตำแหน่ง) + mg/kg
    lcd.fillRect(252, 224, 214, 28, 0x10E4);
    // แคปซูล N (ม่วงน้ำเงิน)
    lcd.fillRoundRect(254, 226, 48, 22, 11, 0x633C);
    lcd.setTextColor(0xFFFF, 0x633C);
    lcd.setTextDatum(textdatum_t::middle_center);
    float dispN = (data.soil7in1.nitrogen > 0.05f) ? data.soil7in1.nitrogen : data.aiCalibrated.nitrogen;
    snprintf(buf, sizeof(buf), "N %.1f", dispN);
    lcd.drawString(buf, 254 + 24, 226 + 11, &fonts::Font0);

    // แคปซูล P (เขียวมรกต)
    lcd.fillRoundRect(305, 226, 48, 22, 11, 0x15D3);
    lcd.setTextColor(0xFFFF, 0x15D3);
    float dispP = (data.soil7in1.phosphorus > 0.05f) ? data.soil7in1.phosphorus : data.aiCalibrated.phosphorus;
    snprintf(buf, sizeof(buf), "P %.1f", dispP);
    lcd.drawString(buf, 305 + 24, 226 + 11, &fonts::Font0);

    // แคปซูล K (ส้มทอง)
    lcd.fillRoundRect(356, 226, 50, 22, 11, 0xFC64);
    lcd.setTextColor(0xFFFF, 0xFC64);
    float dispK = (data.soil7in1.potassium > 0.05f) ? data.soil7in1.potassium : data.aiCalibrated.potassium;
    snprintf(buf, sizeof(buf), "K %.1f", dispK);
    lcd.drawString(buf, 356 + 25, 226 + 11, &fonts::Font0);

    // หน่วย mg/kg สีเหลืองทองสว่างสดใส ชัดเจน
    lcd.setTextColor(0xFFE0, 0x10E4);
    lcd.setTextDatum(textdatum_t::middle_left);
    lcd.drawString("mg/kg", 410, 226 + 11, &fonts::Font0);
    lcd.setTextDatum(textdatum_t::top_left);

    // อัปเดตแคปซูลเวลาและไอคอน Wi-Fi ด้านบนสดๆ ทุกวินาที
    updateTopHeaderClock();
    ensureAppFont();
}

static void drawPageBigNumbers(const FarmSensorTelemetry &data) {
    drawPageOverview(data, false, false);
}


// ============================================================================
// แถบปุ่มนำทางด้านล่างของหน้ารายละเอียดเซนเซอร์ (Bottom Nav Bar)
// ============================================================================
static void drawDetailBottomNav(int sy, DisplayPage nextPage, int customBaseY = 432) {
    int btnY = customBaseY - sy;
    // 1. ปุ่ม [< ย้อนกลับหน้าแรก]
    lcd.fillRoundRect(10, btnY, 214, 34, 6, 0x18C3);
    lcd.drawRoundRect(10, btnY, 214, 34, 6, 0xFFFF);
    lcd.setTextColor(0xFFFF, 0x18C3);
    lcd.setTextDatum(textdatum_t::middle_center);
    lcd.drawString(L_STR("< ย้อนกลับหน้าแรก", "< BACK TO HOME", "< 返回主页"), 10 + 107, btnY + 17);

    // 2. ปุ่ม [เซนเซอร์ถัดไป >]
    lcd.fillRoundRect(232, btnY, 224, 34, 6, 0x028A);
    lcd.drawRoundRect(232, btnY, 224, 34, 6, COLOR_CYAN);
    lcd.setTextColor(COLOR_CYAN, 0x028A);
    lcd.drawString(L_STR("เซนเซอร์ถัดไป >", "NEXT SENSOR >", "下一传感器 >"), 232 + 112, btnY + 17);
    lcd.setTextDatum(textdatum_t::top_left);
}

// ============================================================================
// หน้าต่างย่อยที่ 1: รายละเอียดเซนเซอร์ SHT45 (Air Microclimate & VPD Physics)
// ============================================================================
static void drawPageDetailAir(const FarmSensorTelemetry &data) {
    char buf[80];
    int sy = scrollOffsetY;

    lcd.fillRect(0, 36, 460, 284, COLOR_BG);
    drawDetailHeader("SHT45: บรรยากาศ & VPD", "SHT45: AIR & VPD PHYSICS", "SHT45: 空气微气候与VPD", COLOR_ACCENT);

    // กำหนดพื้นที่ Clip Rect ให้เลื่อนเนื้อหาโดยไม่ล้นทับ Header และไม่ทับ Scrollbar
    lcd.setClipRect(0, 36, 460, 284);

    // --- การ์ด 1: ข้อมูลเซนเซอร์สด & เกจวัดความชื้น (Real-time Gauge) ---
    // ขยายความสูงการ์ดเป็น 200px ให้ระยะห่างบรรทัด 1.5 - 1.7 เท่า (32-34px) สบายตา ชัดเจน
    int c1_y = 40 - sy;
    lcd.fillRoundRect(6, c1_y, 450, 200, 6, COLOR_CARD_BG);
    lcd.drawRoundRect(6, c1_y, 450, 200, 6, COLOR_ACCENT);
    lcd.setTextSize(1);
    lcd.setTextColor(COLOR_ACCENT, COLOR_CARD_BG);
    lcd.drawString(L_STR("[SHT45] อุณหภูมิและความชื้นสัมพัทธ์ (Sensirion CMOSens)",
                         "[SHT45] TEMPERATURE & RELATIVE HUMIDITY (Sensirion CMOSens)",
                         "[SHT45] 空气温湿度监测 (Sensirion CMOSens)"), 16, c1_y + 10);

    // บรรทัดตัวเลขหลัก: [TEMP] 27.3 °C (81.2 °F) & [RH%] 88.1 %RH (y: c1_y + 44)
    drawBadgeTag(16, c1_y + 42, "TEMP", 0xB222, 0xFFFF, 0xFD20, 44, 20);
    float fahrenheit = (data.air.temperature * 1.8f) + 32.0f;
    snprintf(buf, sizeof(buf), "%.2f C  (%.2f F)", data.air.temperature, fahrenheit);
    lcd.setTextColor(0xFD20, COLOR_CARD_BG);
    lcd.drawString(buf, 68, c1_y + 44);

    drawBadgeTag(240, c1_y + 42, "RH%", 0x0B34, 0xFFFF, 0x3DFF, 40, 20);
    snprintf(buf, sizeof(buf), "%.2f %%RH", data.air.humidity);
    lcd.setTextColor(0x3DFF, COLOR_CARD_BG);
    lcd.drawString(buf, 288, c1_y + 44);

    // จุดน้ำค้าง Dew Point & ระยะห่างจุดน้ำค้าง Dew Margin (y: c1_y + 78, delta = 34px)
    float dewMargin = data.air.temperature - data.air.dewPoint;
    snprintf(buf, sizeof(buf), "Dew Point: %.2f C   |   Dew Margin: %.2f C", data.air.dewPoint, dewMargin);
    lcd.setTextColor(0x87F0, COLOR_CARD_BG);
    lcd.drawString(buf, 16, c1_y + 78);

    // เกจวัดความชื้นอากาศ: หัวข้อและตัวเลขเปอร์เซ็นต์ (y: c1_y + 112, delta = 34px)
    lcd.setTextColor(COLOR_TEXT_DIM, COLOR_CARD_BG);
    lcd.drawString(L_STR("เกจระดับความชื้นอากาศ:", "Air Humidity Gauge:", "空气湿度刻度:"), 16, c1_y + 112);
    snprintf(buf, sizeof(buf), "%.2f %% (%s)", data.air.humidity,
             (data.air.humidity > 80.0f) ? L_STR("สูง", "High", "高") : ((data.air.humidity < 40.0f) ? L_STR("ต่ำ", "Low", "低") : L_STR("ปกติ", "Normal", "适宜")));
    uint16_t barColor = (data.air.humidity > 80.0f) ? 0xFD20 : ((data.air.humidity < 40.0f) ? COLOR_WARN : 0x07E0);
    lcd.setTextColor(barColor, COLOR_CARD_BG);
    lcd.setTextDatum(textdatum_t::top_right);
    lcd.drawString(buf, 446, c1_y + 112);
    lcd.setTextDatum(textdatum_t::top_left);

    // บาร์กราฟเต็มความกว้างการ์ด สวยงาม (y: c1_y + 144, delta = 32px)
    int barW = constrain((int)(data.air.humidity * 4.26f), 0, 426);
    lcd.drawRoundRect(16, c1_y + 144, 430, 12, 4, 0x4208);
    lcd.fillRect(18, c1_y + 146, 426, 8, 0x0841);
    lcd.fillRect(18, c1_y + 146, barW, 8, barColor);

    // บรรทัดสมการ (y: c1_y + 172, delta = 28px)
    snprintf(buf, sizeof(buf), "VPsat: %.2f kPa  |  VPact: %.2f kPa  |  FAO-56 Penman Equation",
             0.61078f * exp((17.27f * data.air.temperature) / (data.air.temperature + 237.3f)),
             (0.61078f * exp((17.27f * data.air.temperature) / (data.air.temperature + 237.3f))) * (data.air.humidity / 100.0f));
    lcd.setTextColor(COLOR_TEXT_DIM, COLOR_CARD_BG);
    lcd.drawString(buf, 16, c1_y + 172);

    // --- การ์ด 2: คำแนะนำสำหรับเกษตรกร & การคายน้ำ (Agronomic Advice & VPD) ---
    // ขยายความสูงการ์ดเป็น 210px
    int c2_y = c1_y + 212;
    lcd.fillRoundRect(6, c2_y, 450, 210, 6, COLOR_CARD_BG);
    lcd.drawRoundRect(6, c2_y, 450, 210, 6, 0x07E0);
    lcd.setTextColor(0x07E0, COLOR_CARD_BG);
    lcd.drawString(L_STR("คำแนะนำสำหรับเกษตรกร (VPD & สุขภาพพืช):",
                         "AGRONOMIC ADVICE (VPD & TRANSPIRATION):",
                         "农学指导 (VPD 与植物蒸腾健康):"), 16, c2_y + 10);

    snprintf(buf, sizeof(buf), "VPD: %.2f kPa", data.air.vpd);
    lcd.setTextColor(0xFFE0, COLOR_CARD_BG);
    lcd.drawString(buf, 16, c2_y + 44);

    // สถานะ VPD อยู่ฝั่งขวา ไม่ทับข้อความ
    if (data.air.vpd >= 0.8f && data.air.vpd <= 1.2f) {
        lcd.fillRoundRect(176, c2_y + 40, 270, 24, 4, 0x0320);
        lcd.drawRoundRect(176, c2_y + 40, 270, 24, 4, 0x07E0);
        lcd.setTextColor(0x07E0, 0x0320);
        lcd.setTextDatum(textdatum_t::middle_center);
        lcd.drawString(L_STR("[ สภาวะเหมาะสมสูงสุด ]", "[ Optimal Air Flow ]", "[ 气候适宜 气孔正常 ]"), 176 + 135, c2_y + 40 + 12);
        lcd.setTextDatum(textdatum_t::top_left);

        lcd.setTextColor(COLOR_TEXT_VAL, COLOR_CARD_BG);
        lcd.drawString(L_STR("คำแนะนำ: ปากใบเปิดเต็มที่ การสังเคราะห์แสงและดูดซึมปุ๋ยดีเยี่ยม",
                             "Advice: Stomata fully open, maximum nutrient & water uptake.",
                             "指导建议: 气孔充分张开，养分与水分输送效率最佳。"), 16, c2_y + 80);
    } else if (data.air.vpd < 0.8f) {
        lcd.fillRoundRect(176, c2_y + 40, 270, 24, 4, 0x3180);
        lcd.drawRoundRect(176, c2_y + 40, 270, 24, 4, 0xFD20);
        lcd.setTextColor(0xFD20, 0x3180);
        lcd.setTextDatum(textdatum_t::middle_center);
        lcd.drawString(L_STR("[ ความชื้นสูงเกินไป เสี่ยงเชื้อรา ]", "[ High Humidity Alert ]", "[ 湿度过高 谨防霉菌 ]"), 176 + 135, c2_y + 40 + 12);
        lcd.setTextDatum(textdatum_t::top_left);

        lcd.setTextColor(COLOR_TEXT_VAL, COLOR_CARD_BG);
        lcd.drawString(L_STR("คำแนะนำ: พืชคายน้ำไม่ออก เสี่ยงเชื้อราและขาดแคลเซียม ควรระบายอากาศ",
                             "Advice: Stifled transpiration; risk of fungus & Ca deficiency. Ventilate!",
                             "指导建议: 蒸腾受阻，谨防真菌病害及缺钙，建议通风降湿。"), 16, c2_y + 80);
    } else {
        lcd.fillRoundRect(176, c2_y + 40, 270, 24, 4, 0x3800);
        lcd.drawRoundRect(176, c2_y + 40, 270, 24, 4, COLOR_WARN);
        lcd.setTextColor(COLOR_WARN, 0x3800);
        lcd.setTextDatum(textdatum_t::middle_center);
        lcd.drawString(L_STR("[ อากาศแห้ง พืชเครียด ]", "[ Dry Air Stress Alert ]", "[ 气候干燥 蒸腾胁迫 ]"), 176 + 135, c2_y + 40 + 12);
        lcd.setTextDatum(textdatum_t::top_left);

        lcd.setTextColor(COLOR_TEXT_VAL, COLOR_CARD_BG);
        lcd.drawString(L_STR("คำแนะนำ: ปากใบปิด พืชเหี่ยวเฉา ควรเปิดระบบพ่นหมอกเพิ่มความชื้น",
                             "Advice: Stomata closing to save water; engage misting system!",
                             "指导建议: 气孔紧闭防失水，建议开启喷雾增加湿度。"), 16, c2_y + 80);
    }

    lcd.setTextColor(COLOR_TEXT_DIM, COLOR_CARD_BG);
    lcd.drawString(L_STR("พ่นหมอกอัตโนมัติ: ทำงานเมื่อ Temp > 35 C หรือ RH < 70%",
                         "Auto Misting triggers when Temp > 35 C or RH < 70%",
                         "智能喷雾联动: 当气温 > 35℃ 或湿度 < 70% 自动启动"), 16, c2_y + 114);
    lcd.setTextColor(0xFDE0, COLOR_CARD_BG);
    lcd.drawString(L_STR("ระยะห่างจุดน้ำค้าง < 2 C: เสี่ยงเกิดหยดน้ำเกาะใบ แนะนำเร่งพัดลมกวนอากาศ",
                         "Dew margin < 2 C: Condensation alert; boost ventilation fan!",
                         "露点温差低于 2℃ 时，叶面极易结露，需加强通风。"), 16, c2_y + 148);
    lcd.setTextColor(0x633C, COLOR_CARD_BG);
    lcd.drawString("I2C Telemetry: SDA=GPIO9, SCL=GPIO8 | Sensirion SHT45 (Accuracy: +/-0.1C)", 16, c2_y + 180);

    // --- การ์ด 3: ข้อมูลทางเทคนิคและฮาร์ดแวร์ I2C (Technical Specs) ---
    // ขยายความสูงการ์ดเป็น 176px
    int c3_y = c2_y + 222;
    lcd.fillRoundRect(6, c3_y, 450, 176, 6, COLOR_CARD_BG);
    lcd.drawRoundRect(6, c3_y, 450, 176, 6, 0x4208);
    lcd.setTextColor(COLOR_CYAN, COLOR_CARD_BG);
    lcd.drawString(L_STR("ข้อมูลทางเทคนิค & ฮาร์ดแวร์ I2C:", "TECHNICAL SPECS & I2C HARDWARE:", "技术参数与 I2C 硬件通信:"), 16, c3_y + 10);

    lcd.setTextColor(COLOR_TEXT_VAL, COLOR_CARD_BG);
    lcd.drawString("Pinout: SDA=GPIO9 (Yellow), SCL=GPIO8 (Green) | I2C Addr: 0x44", 16, c3_y + 44);
    lcd.drawString(L_STR("ความถี่บัส: 10 kHz ฟิลเตอร์ฮาร์ดแวร์ลดสัญญาณรบกวน | ออนไลน์",
                         "Bus Frequency: 10 kHz Noise-Immune Filter | ONLINE",
                         "总线频率: 10 kHz 硬件抗干扰滤波 | 在线正常"), 16, c3_y + 78);
    lcd.setTextColor(COLOR_TEXT_DIM, COLOR_CARD_BG);
    lcd.drawString("Precision: +/-0.1 C (Temperature), +/-1.5 %RH (Humidity)", 16, c3_y + 112);
    lcd.drawString(L_STR("การประมวลผล: คำนวณ VPD และ Dew Point ตามมาตรฐาน FAO-56 Penman",
                         "Calculations: Real-time VPD & Dew Point by FAO-56 Penman",
                         "算法标准: 采用联合国粮农组织 FAO-56 标准计算"), 16, c3_y + 144);

    // --- แถบปุ่มนำทางด้านล่าง ---
    drawDetailBottomNav(sy, PAGE_DETAIL_LIGHT, 662);

    // ปิด Clip Rect และวาดสไลด์บาร์
    lcd.clearClipRect();
    drawScrollBar(scrollOffsetY, maxScrollY, 38, 280, COLOR_ACCENT);
    pageChanged = false;
}

// ============================================================================
// หน้าต่างย่อยที่ 2: รายละเอียดเซนเซอร์โดมตะวัน BH1750 (Solar Radiation Physics)
// ============================================================================
static void drawPageDetailLight(const FarmSensorTelemetry &data) {
    char buf[80];
    int sy = scrollOffsetY;

    lcd.fillRect(0, 36, 460, 284, COLOR_BG);
    drawDetailHeader("BH1750: รังสีแสงโดมตะวัน", "BH1750: SOLAR DOME RADIATION", "BH1750: 太阳穹顶光合辐射", COLOR_YELLOW);

    lcd.setClipRect(0, 36, 460, 284);

    // --- การ์ด 1: พลังงานรังสีดวงอาทิตย์หลัก (Hero Metric) ---
    // ขยายความสูงการ์ดเป็น 200px ให้ระยะห่างบรรทัด 1.5 - 1.7 เท่า (32-34px) สบายตา ชัดเจน
    int c1_y = 40 - sy;
    lcd.fillRoundRect(6, c1_y, 450, 200, 6, COLOR_CARD_BG);
    lcd.drawRoundRect(6, c1_y, 450, 200, 6, COLOR_YELLOW);
    lcd.setTextSize(1);
    lcd.setTextColor(COLOR_YELLOW, COLOR_CARD_BG);
    lcd.drawString(L_STR("[BH1750] ฟลักซ์รังสีดวงอาทิตย์โดมตะวัน (Solar Flux Density)",
                         "[BH1750] SUN DOME SOLAR RADIATION FLUX DENSITY",
                         "[BH1750] 太阳穹顶光合辐射通量密度"), 16, c1_y + 10);

    drawBadgeTag(16, c1_y + 42, "SOLAR", 0x9360, 0xFFFF, 0xFFE0, 50, 20);
    snprintf(buf, sizeof(buf), "%.2f W/m2", data.light.solarRadiation);
    lcd.setTextColor(0xFFE0, COLOR_CARD_BG);
    lcd.drawString(buf, 74, c1_y + 44);

    drawBadgeTag(240, c1_y + 42, "LUX", 0x7BC1, 0xFFFF, 0xFF30, 38, 20);
    snprintf(buf, sizeof(buf), "%.2f kLux (%.2f Lux)", data.light.lux / 1000.0f, data.light.lux);
    lcd.setTextColor(0xFF30, COLOR_CARD_BG);
    lcd.drawString(buf, 288, c1_y + 44);

    float solarConstRatio = (data.light.solarRadiation / 1361.0f) * 100.0f;
    snprintf(buf, sizeof(buf), "%s: %.2f %% (จาก 1361 W/m2 Max Solar Constant)",
             L_STR("สัดส่วนคงที่สุริยะ", "Solar Constant Ratio", "太阳能常数占比"), solarConstRatio);
    lcd.setTextColor(0x87F0, COLOR_CARD_BG);
    lcd.drawString(buf, 16, c1_y + 78);

    // ระดับรังสีดวงอาทิตย์: หัวข้อและตัวเลข (y: c1_y + 112, delta = 34px)
    lcd.setTextColor(COLOR_TEXT_DIM, COLOR_CARD_BG);
    lcd.drawString(L_STR("ระดับรังสีดวงอาทิตย์ (0 - 1000 W/m2):", "Solar Radiation Level (0 - 1000 W/m2):", "太阳辐射强度刻度:"), 16, c1_y + 112);
    snprintf(buf, sizeof(buf), "%.2f W/m2", data.light.solarRadiation);
    lcd.setTextColor(0xFDE0, COLOR_CARD_BG);
    lcd.setTextDatum(textdatum_t::top_right);
    lcd.drawString(buf, 446, c1_y + 112);
    lcd.setTextDatum(textdatum_t::top_left);

    // บาร์กราฟเต็มความกว้างการ์ด (0 - 1000 W/m2) (y: c1_y + 144, delta = 32px)
    int radBarW = constrain((int)(data.light.solarRadiation * 426.0f / 1000.0f), 0, 426);
    lcd.drawRoundRect(16, c1_y + 144, 430, 12, 4, 0x4208);
    lcd.fillRect(18, c1_y + 146, 426, 8, 0x0841);
    lcd.fillRect(18, c1_y + 146, radBarW, 8, 0xFDE0);

    snprintf(buf, sizeof(buf), "Optical Calibration: 1 Lux = 0.0079 W/m2 | Cosine Diffuser 360 All-weather");
    lcd.setTextColor(COLOR_TEXT_DIM, COLOR_CARD_BG);
    lcd.drawString(buf, 16, c1_y + 172);

    // --- การ์ด 2: คำแนะนำการสังเคราะห์แสง & PAR (Photobiology Advice) ---
    int c2_y = c1_y + 212;
    lcd.fillRoundRect(6, c2_y, 450, 210, 6, COLOR_CARD_BG);
    lcd.drawRoundRect(6, c2_y, 450, 210, 6, 0x07E0);
    lcd.setTextColor(0x07E0, COLOR_CARD_BG);
    lcd.drawString(L_STR("คำแนะนำการสังเคราะห์แสง (PAR & DLI Photobiology):",
                         "AGRONOMIC ADVICE (PAR & DAILY LIGHT INTEGRAL):",
                         "光生物学指导 (PAR 光合辐射与日积光照):"), 16, c2_y + 10);

    float estPAR = data.light.solarRadiation * 2.1f;
    snprintf(buf, sizeof(buf), "PAR: ~%.0f umol/(m2*s)", estPAR);
    lcd.setTextColor(0xFFE0, COLOR_CARD_BG);
    lcd.drawString(buf, 16, c2_y + 44);

    if (data.light.lux < 500.0f) {
        lcd.fillRoundRect(190, c2_y + 40, 256, 24, 4, 0x1104);
        lcd.drawRoundRect(190, c2_y + 40, 256, 24, 4, 0x541F);
        lcd.setTextColor(0x841F, 0x1104);
        lcd.setTextDatum(textdatum_t::middle_center);
        lcd.drawString(L_STR("[ แดดร่ม / พืชพักตัวยามค่ำคืน ]", "[ Shade / Night Resting ]", "[ 遮阴阴天 植物休眠 ]"), 190 + 128, c2_y + 40 + 12);
        lcd.setTextDatum(textdatum_t::top_left);

        lcd.setTextColor(COLOR_TEXT_VAL, COLOR_CARD_BG);
        lcd.drawString(L_STR("คำแนะนำ: แสงน้อยเกินไป พืชหยุดสร้างแป้งและน้ำตาล ไม่ควรให้น้ำหรือปุ๋ยมาก",
                             "Advice: Low photon flux; photosynthesis halted. Conserve water.",
                             "指导建议: 光照不足，光合速率极低，植物休眠，避免多浇水。"), 16, c2_y + 80);
    } else if (data.light.lux < 30000.0f) {
        lcd.fillRoundRect(190, c2_y + 40, 256, 24, 4, 0x0320);
        lcd.drawRoundRect(190, c2_y + 40, 256, 24, 4, 0x07E0);
        lcd.setTextColor(0x07E0, 0x0320);
        lcd.setTextDatum(textdatum_t::middle_center);
        lcd.drawString(L_STR("[ แดดพอเหมาะ สังเคราะห์แสงสมบูรณ์ ]", "[ Optimal Sunlight ]", "[ 光照充足 光合优良 ]"), 190 + 128, c2_y + 40 + 12);
        lcd.setTextDatum(textdatum_t::top_left);

        lcd.setTextColor(COLOR_TEXT_VAL, COLOR_CARD_BG);
        lcd.drawString(L_STR("คำแนะนำ: โดมตะวันรับแสงเหมาะสม พืชสังเคราะห์แสงสะสมผลผลิตได้เต็มที่",
                             "Advice: Optimal photons for crop biomass and sugar accumulation.",
                             "指导建议: 光合有效辐射极佳，光合效率处于黄金峰值。"), 16, c2_y + 80);
    } else {
        lcd.fillRoundRect(190, c2_y + 40, 256, 24, 4, 0x3180);
        lcd.drawRoundRect(190, c2_y + 40, 256, 24, 4, 0xFFE0);
        lcd.setTextColor(0xFFE0, 0x3180);
        lcd.setTextDatum(textdatum_t::middle_center);
        lcd.drawString(L_STR("[ แดดจัดมาก ระวังใบไหม้ กางสแลน ]", "[ Intense Sun Alert ]", "[ 强光暴晒 谨防灼伤 ]"), 190 + 128, c2_y + 40 + 12);
        lcd.setTextDatum(textdatum_t::top_left);

        lcd.setTextColor(COLOR_TEXT_VAL, COLOR_CARD_BG);
        lcd.drawString(L_STR("คำแนะนำ: แดดเข้มข้นจัด แนะนำกางสแลนพรางแสง 50% หรือเปิดพ่นหมอก",
                             "Advice: Intense photon stress! Deploy 50% shade cloth or mist.",
                             "指导建议: 强光伴随高温，建议拉上50%遮阳网或喷雾降温。"), 16, c2_y + 80);
    }

    lcd.setTextColor(COLOR_TEXT_DIM, COLOR_CARD_BG);
    lcd.drawString(L_STR("ดัชนี DLI: ปริมาณโมลของแสงต่อวัน ช่วยประเมินพลังงานสะสมเพื่อการติดดอกออกผล",
                         "Daily Light Integral (DLI) gauges total photon energy received per day.",
                         "DLI 日累积光效: 决定作物的最终产量与开花挂果品质。"), 16, c2_y + 114);
    lcd.drawString(L_STR("โดมตะวัน: ตัวรับแสงทรงโดมรับแสงได้ทุกทิศทาง 360 องศา ชดเชยมุมตกกระทบ",
                         "Sun Dome: 360-degree all-weather optical dome diffuser.",
                         "穹顶设计: 全天候 360 度半球全景采光漫反射。"), 16, c2_y + 148);
    lcd.setTextColor(0x633C, COLOR_CARD_BG);
    lcd.drawString("Sensor Hardware: ROHM BH1750FVI 16-bit | I2C Addr: 0x23 | ฝาครอบ IP65", 16, c2_y + 180);

    // --- การ์ด 3: ข้อมูลทางเทคนิคและฮาร์ดแวร์ I2C ---
    int c3_y = c2_y + 222;
    lcd.fillRoundRect(6, c3_y, 450, 176, 6, COLOR_CARD_BG);
    lcd.drawRoundRect(6, c3_y, 450, 176, 6, 0x4208);
    lcd.setTextColor(COLOR_CYAN, COLOR_CARD_BG);
    lcd.drawString(L_STR("ข้อมูลทางเทคนิค & เซนเซอร์ BH1750:", "TECHNICAL SPECS & SENSOR BUS:", "技术规格与传感器总线:"), 16, c3_y + 10);

    lcd.setTextColor(COLOR_TEXT_VAL, COLOR_CARD_BG);
    lcd.drawString("Pinout: SDA=GPIO9, SCL=GPIO8 | I2C Addr: 0x23", 16, c3_y + 44);
    lcd.drawString(L_STR("ชิปเซนเซอร์: ROHM BH1750FVI 16-bit Ambient Light Sensor",
                         "Sensor IC: ROHM BH1750FVI 16-bit Ambient Light Sensor",
                         "传感器芯片: 罗姆 ROHM BH1750FVI 16位高精度光敏芯片"), 16, c3_y + 78);
    lcd.setTextColor(COLOR_TEXT_DIM, COLOR_CARD_BG);
    lcd.drawString("Dynamic Range: 1 - 65,535 Lux | High-Resolution Mode (1 Lux)", 16, c3_y + 112);
    lcd.drawString(L_STR("การป้องกัน: โดมอะคริลิกกันน้ำกันละอองฝนมาตรฐาน IP65",
                         "Enclosure: Weatherproof IP65 optical acrylic dome diffuser",
                         "防护等级: IP65 级全天候防水防尘光学穹顶"), 16, c3_y + 144);

    drawDetailBottomNav(sy, PAGE_DETAIL_SOIL1, 662);

    lcd.clearClipRect();
    drawScrollBar(scrollOffsetY, maxScrollY, 38, 280, COLOR_YELLOW);
    pageChanged = false;
}

// ============================================================================
// หน้าต่างย่อยที่ 3: รายละเอียด Soil Stick (Surface Moisture & ADC Calibration)
// ============================================================================
static void drawPageDetailSoil1(const FarmSensorTelemetry &data) {
    char buf[80];
    int sy = scrollOffsetY;

    lcd.fillRect(0, 36, 460, 284, COLOR_BG);
    drawDetailHeader("SOIL STICK: ดินตื้น 0-10ซม.", "SOIL STICK: SURFACE MOISTURE", "SOIL STICK: 表层土壤湿度 0-10cm", COLOR_CYAN);

    lcd.setClipRect(0, 36, 460, 284);

    // --- การ์ด 1: ความชื้นผิวดินสด & เกจวัด (Real-time Gauge) ---
    // ขยายความสูงการ์ดเป็น 200px ให้ระยะห่างบรรทัด 1.5 - 1.7 เท่า (32-34px) สบายตา ชัดเจน
    int c1_y = 40 - sy;
    lcd.fillRoundRect(6, c1_y, 450, 200, 6, COLOR_CARD_BG);
    lcd.drawRoundRect(6, c1_y, 450, 200, 6, COLOR_CYAN);
    lcd.setTextSize(1);
    lcd.setTextColor(COLOR_CYAN, COLOR_CARD_BG);
    lcd.drawString(L_STR("[Soil Stick] ความชื้นผิวดินชั้นตื้น (0 - 10 ซม.)",
                         "[Soil Stick] TOPSOIL SURFACE MOISTURE (0 - 10 CM)",
                         "[Soil Stick] 表层土壤湿度检测 (0 - 10 厘米)"), 16, c1_y + 10);

    drawBadgeTag(16, c1_y + 42, "SOIL", 0x0BCB, 0xFFFF, 0x3DFF, 46, 20);
    snprintf(buf, sizeof(buf), "%.2f %% (%s)", data.soilStick.moisture, L_STR("ผิวดิน", "Moist", "湿度"));
    lcd.setTextColor(0x3DFF, COLOR_CARD_BG);
    lcd.drawString(buf, 72, c1_y + 44);

    drawBadgeTag(240, c1_y + 42, "ADC", 0x9A81, 0xFFFF, 0xFD20, 40, 20);
    float volts = (data.soilStick.rawAdc * 3.3f) / 4095.0f;
    snprintf(buf, sizeof(buf), "%.2f V | Raw ADC: %d", volts, data.soilStick.rawAdc);
    lcd.setTextColor(0xFD20, COLOR_CARD_BG);
    lcd.drawString(buf, 290, c1_y + 44);

    snprintf(buf, sizeof(buf), "%s: < 40.00%% [ระบบเตรียมพร้อมจ่ายน้ำอัตโนมัติ]", L_STR("เกณฑ์วิกฤตรดน้ำ", "Trigger Level", "浇水阈值"));
    lcd.setTextColor(0x87F0, COLOR_CARD_BG);
    lcd.drawString(buf, 16, c1_y + 78);

    // เกจระดับความชื้น: หัวข้อและตัวเลข (y: c1_y + 112, delta = 34px)
    lcd.setTextColor(COLOR_TEXT_DIM, COLOR_CARD_BG);
    lcd.drawString(L_STR("เกจระดับความชื้นผิวดิน (0 - 100%):", "Topsoil Moisture Gauge (0 - 100%):", "表层土壤湿度刻度:"), 16, c1_y + 112);
    snprintf(buf, sizeof(buf), "%.2f %% (%s)", data.soilStick.moisture,
             (data.soilStick.moisture < 40.0f) ? L_STR("แห้ง", "Dry", "干旱") : ((data.soilStick.moisture > 75.0f) ? L_STR("แฉะ", "Wet", "过湿") : L_STR("ชุ่มชื้น", "Optimal", "适宜")));
    uint16_t soilCol = (data.soilStick.moisture < 40.0f) ? COLOR_WARN : ((data.soilStick.moisture > 75.0f) ? COLOR_CYAN : 0x07E0);
    lcd.setTextColor(soilCol, COLOR_CARD_BG);
    lcd.setTextDatum(textdatum_t::top_right);
    lcd.drawString(buf, 446, c1_y + 112);
    lcd.setTextDatum(textdatum_t::top_left);

    // บาร์กราฟเต็มความกว้างการ์ด (y: c1_y + 144, delta = 32px)
    int barW = constrain((int)(data.soilStick.moisture * 4.26f), 0, 426);
    lcd.drawRoundRect(16, c1_y + 144, 430, 12, 4, 0x4208);
    lcd.fillRect(18, c1_y + 146, 426, 8, 0x0841);
    lcd.fillRect(18, c1_y + 146, barW, 8, soilCol);

    snprintf(buf, sizeof(buf), "Dry Calibration: 3280 ADC | Wet Calibration: 1320 ADC | Capacitive Sensing");
    lcd.setTextColor(COLOR_TEXT_DIM, COLOR_CARD_BG);
    lcd.drawString(buf, 16, c1_y + 172);

    // --- การ์ด 2: คำแนะนำการให้น้ำ & ระบบอัตโนมัติ (Agronomic Advice) ---
    int c2_y = c1_y + 212;
    lcd.fillRoundRect(6, c2_y, 450, 210, 6, COLOR_CARD_BG);
    lcd.drawRoundRect(6, c2_y, 450, 210, 6, 0x07E0);
    lcd.setTextColor(0x07E0, COLOR_CARD_BG);
    lcd.drawString(L_STR("คำแนะนำการให้น้ำ & กลยุทธ์อัตโนมัติ:",
                         "AGRONOMIC ADVICE (IRRIGATION & AUTOMATION):",
                         "灌溉指导与自动化控制策略:"), 16, c2_y + 10);

    lcd.setTextColor(0xFFE0, COLOR_CARD_BG);
    lcd.drawString(L_STR("สถานะผิวดิน:", "Topsoil Status:", "土壤状态:"), 16, c2_y + 44);

    if (data.soilStick.moisture < 40.0f) {
        lcd.fillRoundRect(120, c2_y + 40, 326, 24, 4, 0x3800);
        lcd.drawRoundRect(120, c2_y + 40, 326, 24, 4, COLOR_WARN);
        lcd.setTextColor(COLOR_WARN, 0x3800);
        lcd.setTextDatum(textdatum_t::middle_center);
        lcd.drawString(L_STR("[ ดินแห้งแล้ง: เริ่มเปิดปั๊มรดน้ำ ]", "[ DRY SOIL: Water Now ]", "[ 土壤干旱: 建议浇水 ]"), 120 + 163, c2_y + 40 + 12);
        lcd.setTextDatum(textdatum_t::top_left);

        lcd.setTextColor(COLOR_TEXT_VAL, COLOR_CARD_BG);
        lcd.drawString(L_STR("คำแนะนำ: ดินชั้นตื้นสูญเสียความชื้นสูง ระบบเริ่มรดน้ำอัตโนมัติ",
                             "Advice: Topsoil depleted below threshold; automated pump activated.",
                             "指导建议: 表层土壤严重缺水，智能自控系统已激活水泵灌溉。"), 16, c2_y + 80);
    } else if (data.soilStick.moisture <= 70.0f) {
        lcd.fillRoundRect(120, c2_y + 40, 326, 24, 4, 0x0320);
        lcd.drawRoundRect(120, c2_y + 40, 326, 24, 4, 0x07E0);
        lcd.setTextColor(0x07E0, 0x0320);
        lcd.setTextDatum(textdatum_t::middle_center);
        lcd.drawString(L_STR("[ ชุ่มชื้นดี (งดการรดน้ำเพื่อประหยัดน้ำ) ]", "[ OPTIMAL MOISTURE: OK ]", "[ 水分适宜 (暂缓浇水) ]"), 120 + 163, c2_y + 40 + 12);
        lcd.setTextDatum(textdatum_t::top_left);

        lcd.setTextColor(COLOR_TEXT_VAL, COLOR_CARD_BG);
        lcd.drawString(L_STR("คำแนะนำ: รากพืชดูดซึมน้ำและปุ๋ยได้สะดวก งดการให้น้ำเพิ่มเพื่อประหยัดน้ำ",
                             "Advice: Ideal root moisture; maintain water hold to conserve resources.",
                             "指导建议: 水分充足透气良好，暂缓浇水以节约水资源。"), 16, c2_y + 80);
    } else {
        lcd.fillRoundRect(120, c2_y + 40, 326, 24, 4, 0x0214);
        lcd.drawRoundRect(120, c2_y + 40, 326, 24, 4, COLOR_CYAN);
        lcd.setTextColor(COLOR_CYAN, 0x0214);
        lcd.setTextDatum(textdatum_t::middle_center);
        lcd.drawString(L_STR("[ ดินแฉะเกินไป: ระวังรากขาดอากาศ ]", "[ WATERLOGGED ALERT ]", "[ 土壤过湿: 谨防沤根 ]"), 120 + 163, c2_y + 40 + 12);
        lcd.setTextDatum(textdatum_t::top_left);

        lcd.setTextColor(COLOR_TEXT_VAL, COLOR_CARD_BG);
        lcd.drawString(L_STR("คำแนะนำ: ดินอิ่มตัวด้วยน้ำมากเกินไป เสี่ยงรากขาดอากาศ ควรพรวนดินระบายน้ำ",
                             "Advice: Saturated soil reduces root oxygen. Hold watering immediately!",
                             "指导建议: 水分过饱和导致根系缺氧，立即停止灌溉并通风透气。"), 16, c2_y + 80);
    }

    lcd.setTextColor(COLOR_TEXT_DIM, COLOR_CARD_BG);
    lcd.drawString(L_STR("ระบบอัตโนมัติ: รดน้ำเมื่อ < 40.0% --> ตัดน้ำเมื่อถึง 65.0% (ระบบฮิสเทอรีซิส)",
                         "Automation Rule: Water ON < 40.0% --> OFF at >= 65.0% (Hysteresis)",
                         "智能滞回自控: 湿度低于 40% 启动 --> 达到 65% 停止"), 16, c2_y + 114);
    lcd.setTextColor(0xFDE0, COLOR_CARD_BG);
    lcd.drawString(L_STR("ระบบความปลอดภัย: ตัดการทำงานปั๊มฉุกเฉินภายใน 5 นาที ป้องกันมอเตอร์ปั๊มไหม้",
                         "Safety Feature: 5-Minute maximum continuous run protects pump motor.",
                         "安全保障机制: 5分钟连续运行强制保护关断，防止水泵干烧。"), 16, c2_y + 148);
    lcd.setTextColor(0x633C, COLOR_CARD_BG);
    lcd.drawString("Hardware: ESP32-S3 Port A1 (GPIO1) | 12-bit SAR ADC | แผ่นทองแดงทนสนิม", 16, c2_y + 180);

    // --- การ์ด 3: ข้อมูลฮาร์ดแวร์และการสอบเทียบ ADC ---
    int c3_y = c2_y + 222;
    lcd.fillRoundRect(6, c3_y, 450, 176, 6, COLOR_CARD_BG);
    lcd.drawRoundRect(6, c3_y, 450, 176, 6, 0x4208);
    lcd.setTextColor(COLOR_CYAN, COLOR_CARD_BG);
    lcd.drawString(L_STR("ข้อมูลฮาร์ดแวร์ & เซนเซอร์คาปาซิทีฟ:", "HARDWARE SPECS & CAPACITIVE SENSING:", "硬件参数与电容感应原理:"), 16, c3_y + 10);

    lcd.setTextColor(COLOR_TEXT_VAL, COLOR_CARD_BG);
    lcd.drawString("Pinout: ESP32-S3 Port A1 (GPIO 1) | 12-bit ADC (0 - 4095)", 16, c3_y + 44);
    lcd.drawString(L_STR("หลักการทำงาน: แผ่นทองแดงวัดความจุไฟฟ้า ไร้การกัดกร่อนจากกระแสตรง",
                         "Working Principle: High-frequency capacitance (Corrosion-Free)",
                         "感应原理: 高频交变电容测量，无直流电解腐蚀，寿命长"), 16, c3_y + 78);
    lcd.setTextColor(COLOR_TEXT_DIM, COLOR_CARD_BG);
    lcd.drawString("Calibration Map: Dry Air = 3280 ADC | 100% Water = 1320 ADC", 16, c3_y + 112);
    lcd.drawString(L_STR("ชั้นดิน: ตรวจจับชั้นผิวดิน 0-10 ซม. ซึ่งเป็นด่านแรกของการระเหยน้ำ",
                         "Topsoil Layer: Monitors 0-10 cm zone where solar evaporation peaks.",
                         "监测区位: 专注 0-10cm 表层土壤，此处水分蒸发最快。"), 16, c3_y + 144);

    drawDetailBottomNav(sy, PAGE_DETAIL_SOIL7, 662);

    lcd.clearClipRect();
    drawScrollBar(scrollOffsetY, maxScrollY, 38, 280, COLOR_CYAN);
    pageChanged = false;
}

// ============================================================================
// Cyber 7-in-1 UI Helpers (Matching soil_7in1_dashboard_ui.jpg 100%)
// ============================================================================

// 1. ฟังก์ชันวาดการ์ดพารามิเตอร์แบบ Cyber ถอดแบบตามต้นฉบับ soil_7in1_dashboard_ui.jpg 100%
static void drawCyberParamCard(int x, int y, int w, int h, int num, const char *title, float val, const char *unit, uint16_t col, float pct, int icon_type) {
    // พื้นหลังการ์ดกระจกดำ Deep Cyber Navy & กรอบนีออนเรืองแสง
    lcd.fillRoundRect(x, y, w, h, 6, 0x08A3);
    lcd.drawRoundRect(x, y, w, h, 6, col);

    // ป้ายตัวเลขกำกับลำดับ [1] .. [7] มุมซ้ายบน
    lcd.fillRoundRect(x + 5, y + 6, 15, 14, 3, col);
    char nbuf[4];
    snprintf(nbuf, sizeof(nbuf), "%d", num);
    lcd.setTextColor(0x0000, col);
    lcd.setTextDatum(textdatum_t::middle_center);
    lcd.drawString(nbuf, x + 12, y + 13);

    // ชื่อพารามิเตอร์ (เว้นระยะโปร่ง ไม่ชนไอคอนขวาบน)
    lcd.setTextColor(0xFFFF, 0x08A3);
    lcd.setTextDatum(textdatum_t::top_left);
    lcd.drawString(title, x + 23, y + 8);

    // ไอคอนสัญลักษณ์มุมขวาบนตามต้นฉบับ
    int ix = x + w - 18;
    int iy = y + 6;
    if (icon_type == 1) { // 💧 หยดน้ำ (Moisture)
        lcd.fillCircle(ix + 5, iy + 8, 4, col);
        lcd.fillTriangle(ix + 1, iy + 7, ix + 9, iy + 7, ix + 5, iy + 1, col);
    } else if (icon_type == 2) { // 🌡️ เทอร์โมมิเตอร์ (Temp)
        lcd.drawRoundRect(ix + 3, iy + 1, 4, 9, 2, 0xFFFF);
        lcd.fillCircle(ix + 5, iy + 10, 3, col);
        lcd.fillRect(ix + 4, iy + 3, 2, 7, col);
    } else if (icon_type == 3) { // ☰ เส้นคลื่นความนำไฟฟ้า (EC)
        lcd.fillRoundRect(ix - 3, iy + 1, 16, 13, 3, 0x2180);
        lcd.drawFastHLine(ix, iy + 4, 10, col);
        lcd.drawFastHLine(ix, iy + 7, 10, col);
        lcd.drawFastHLine(ix, iy + 10, 10, col);
    } else if (icon_type == 4) { // </> ป้ายกรดด่าง (pH)
        lcd.fillRoundRect(ix - 3, iy + 1, 17, 13, 3, 0x2867);
        lcd.drawRoundRect(ix - 3, iy + 1, 17, 13, 3, col);
        lcd.setTextColor(col, 0x2867);
        lcd.setTextDatum(textdatum_t::middle_center);
        lcd.drawString("</>", ix + 5, iy + 7);
        lcd.setTextDatum(textdatum_t::top_left);
    } else if (icon_type == 5) { // N2 pill (Nitrogen)
        lcd.fillRoundRect(ix - 4, iy + 1, 18, 13, 3, 0x0188);
        lcd.drawRoundRect(ix - 4, iy + 1, 18, 13, 3, col);
        lcd.setTextColor(col, 0x0188);
        lcd.setTextDatum(textdatum_t::middle_center);
        lcd.drawString("N2", ix + 5, iy + 7);
        lcd.setTextDatum(textdatum_t::top_left);
    } else if (icon_type == 6) { // ⁘ กลุ่ม 4 จุด (Phosphorus)
        lcd.fillRoundRect(ix - 4, iy + 1, 18, 13, 3, 0x01E2);
        lcd.drawRoundRect(ix - 4, iy + 1, 18, 13, 3, col);
        lcd.fillCircle(ix + 1, iy + 5, 2, col);
        lcd.fillCircle(ix + 9, iy + 5, 2, col);
        lcd.fillCircle(ix + 1, iy + 10, 2, col);
        lcd.fillCircle(ix + 9, iy + 10, 2, col);
    } else if (icon_type == 7) { // K+ pill (Potassium)
        lcd.fillRoundRect(ix - 4, iy + 1, 18, 13, 3, 0x0188);
        lcd.drawRoundRect(ix - 4, iy + 1, 18, 13, 3, col);
        lcd.setTextColor(col, 0x0188);
        lcd.setTextDatum(textdatum_t::middle_center);
        lcd.drawString("K+", ix + 5, iy + 7);
        lcd.setTextDatum(textdatum_t::top_left);
    }

    // ตัวเลขค่าการวัดขนาดใหญ่ Big Bold: ปรับ pH, N, P, K, EC, Moisture เป็น 1 ตำแหน่งตามข้อกำหนด
    char vbuf[32];
    if (icon_type == 1) { // Moisture: "4.8%" (1 ตำแหน่ง)
        snprintf(vbuf, sizeof(vbuf), "%.1f%%", val);
    } else if (icon_type == 2) { // Temp: "28.60" (คง 2 ตำแหน่ง)
        snprintf(vbuf, sizeof(vbuf), "%.2f", val);
    } else if (icon_type == 3) { // EC: "0.0" / "120.0" (1 ตำแหน่ง)
        snprintf(vbuf, sizeof(vbuf), "%.1f", val);
    } else if (icon_type >= 5) { // N, P, K: "24.2" (1 ตำแหน่ง)
        snprintf(vbuf, sizeof(vbuf), "%.1f", val);
    } else if (icon_type == 4) { // pH: "8.6" (1 ตำแหน่ง)
        snprintf(vbuf, sizeof(vbuf), "%.1f", val);
    }

    lcd.setTextSize(2);
    lcd.setTextColor(0xFFFF, 0x08A3);
    lcd.drawString(vbuf, x + 8, y + 29);
    int val_w = lcd.textWidth(vbuf); // คำนวณความกว้างพิกเซลจริง แม่นยำ 100%

    // หน่วยวัดกำกับข้างตัวเลข โดยเว้นระยะต่อท้าย 5px จึงไม่มีวันซ้อนทับตัวเลขเด็ดขาด
    if (unit && unit[0] != '\0') {
        lcd.setTextSize(1);
        lcd.setTextColor(COLOR_TEXT_DIM, 0x08A3);
        lcd.drawString(unit, x + 8 + val_w + 5, y + 36);
    }
    lcd.setTextSize(1);

    // แถบหลอดเรืองแสง Cyber Progress Bar พร้อมหัวจุดสว่าง
    int bar_y = y + h - 10;
    int bar_w = w - 16;
    lcd.fillRoundRect(x + 8, bar_y, bar_w, 4, 2, 0x1125);
    if (pct > 0.02f) {
        if (pct > 1.0f) pct = 1.0f;
        int fill_w = (int)(bar_w * pct);
        if (fill_w > 0) {
            if (icon_type == 4) {
                // Card 4: กราเดียนต์เขียวไปฟ้าตามต้นฉบับ
                for (int gx = 0; gx < fill_w; gx++) {
                    uint16_t gcol = (gx < fill_w / 2) ? 0x07E0 : 0x07FF;
                    lcd.drawFastVLine(x + 8 + gx, bar_y, 4, gcol);
                }
            } else {
                lcd.fillRoundRect(x + 8, bar_y, fill_w, 4, 2, col);
            }
            lcd.fillCircle(x + 8 + fill_w, bar_y + 2, 3, 0xFFFF); // Glowing head
        }
    }
}

// 2. ฟังก์ชันวาด N-P-K Stoichiometry Donut Chart (4 Arc Segments) ตามต้นฉบับ 100%
static void drawSoilDonutChart(int cx, int cy, int outerR, int innerR, float n, float p, float k) {
    float total = n + p + k;
    if (total < 1.0f) {
        n = 31.0f; p = 10.0f; k = 59.0f;
        total = 100.0f;
    }
    float pN = (n / total) * 0.85f;
    float pP = (p / total) * 0.85f;
    float pK = (k / total) * 0.85f;
    float pExtra = 0.15f; // Purple arc (Top)

    // พิกัดมุมตามภาพต้นฉบับเป๊ะ: บน=ม่วง, ขวา=ฟ้า, ล่าง=เขียว, ซ้าย=ส้ม
    float a0 = -120.0f;
    float a1 = a0 + pExtra * 360.0f; // Purple
    float a2 = a1 + pN * 360.0f;      // Cyan (N)
    float a3 = a2 + pP * 360.0f;      // Green (P)
    float a4 = a0 + 360.0f;           // Orange (K)

    const float DEG2RAD = 0.0174532925f;
    for (float deg = a0; deg < a4; deg += 1.5f) {
        float rad = deg * DEG2RAD;
        float cosA = cosf(rad);
        float sinA = sinf(rad);
        int x1 = cx + (int)(innerR * cosA);
        int y1 = cy + (int)(innerR * sinA);
        int x2 = cx + (int)(outerR * cosA);
        int y2 = cy + (int)(outerR * sinA);

        uint16_t segCol = 0xFD00; // Golden Orange for Potassium
        if (deg < a1) segCol = 0xCA7E; // Purple / Violet
        else if (deg < a2) segCol = 0x07FF; // Cyan for Nitrogen
        else if (deg < a3) segCol = 0x07E0; // Emerald Green for Phosphorus

        lcd.drawLine(x1, y1, x2, y2, segCol);
    }

    // ขอบวงแหวนคมชัดและเจาะรูกลาง
    lcd.drawCircle(cx, cy, outerR, 0x4A69);
    lcd.drawCircle(cx, cy, innerR, 0x4A69);
    lcd.fillCircle(cx, cy, innerR - 1, 0x08A3);
}

// 3. ฟังก์ชันวาด 5-Axis Soil Fertility Radar Chart ตามต้นฉบับ 100%
static void drawSoilRadarChart(int cx, int cy, int maxR, float moist, float temp, float ec, float ph, float npk) {
    const float DEG2RAD = 0.0174532925f;
    const float angles[5] = { -90.0f, -18.0f, 54.0f, 126.0f, 198.0f };
    const char *axisLabels[5] = { "N", "P", "P", "P", "K" }; // Label vertices exactly as mockup

    // วาดโครงข่ายใยแมงมุม 5 ชั้น (Concentric Pentagons)
    for (int ring = 1; ring <= 5; ring++) {
        float r = maxR * (ring / 5.0f);
        uint16_t ringCol = (ring == 5) ? 0x07E0 : 0x12E4;
        for (int i = 0; i < 5; i++) {
            int next_i = (i + 1) % 5;
            float r1 = angles[i] * DEG2RAD;
            float r2 = angles[next_i] * DEG2RAD;
            int x1 = cx + (int)(r * cosf(r1));
            int y1 = cy + (int)(r * sinf(r1));
            int x2 = cx + (int)(r * cosf(r2));
            int y2 = cy + (int)(r * sinf(r2));
            lcd.drawLine(x1, y1, x2, y2, ringCol);
        }
    }

    // วาดเส้นแกน 5 ก้าน & ตัวอักษรระบุแกนตามต้นฉบับ
    for (int i = 0; i < 5; i++) {
        float rad = angles[i] * DEG2RAD;
        int x2 = cx + (int)(maxR * cosf(rad));
        int y2 = cy + (int)(maxR * sinf(rad));
        lcd.drawLine(cx, cy, x2, y2, 0x07E0);

        int lx = cx + (int)((maxR + 10) * cosf(rad));
        int ly = cy + (int)((maxR + 10) * sinf(rad));
        lcd.setTextDatum(textdatum_t::middle_center);
        lcd.setTextColor(0xFFFF, 0x08A3);
        lcd.drawString(axisLabels[i], lx, ly);
    }

    // คำนวณรัศมีค่าพิกัดของแต่ละแกน
    float v[5] = { 0.85f, 0.65f, 0.75f, 0.55f, 0.70f };
    if (npk > 0.0f) v[0] = (npk / 240.0f < 0.3f) ? 0.3f : ((npk / 240.0f > 0.95f) ? 0.95f : npk / 240.0f);
    if (moist > 0.0f) v[1] = (moist / 65.0f < 0.3f) ? 0.3f : ((moist / 65.0f > 0.95f) ? 0.95f : moist / 65.0f);
    if (ec > 0.0f) v[2] = (ec / 1000.0f < 0.3f) ? 0.3f : ((ec / 1000.0f > 0.95f) ? 0.95f : ec / 1000.0f);
    if (ph > 0.0f) v[3] = (ph / 8.5f < 0.3f) ? 0.3f : ((ph / 8.5f > 0.95f) ? 0.95f : ph / 8.5f);
    if (temp > 0.0f) v[4] = (temp / 35.0f < 0.3f) ? 0.3f : ((temp / 35.0f > 0.95f) ? 0.95f : temp / 35.0f);

    int px[5], py[5];
    for (int i = 0; i < 5; i++) {
        float rad = angles[i] * DEG2RAD;
        px[i] = cx + (int)(maxR * v[i] * cosf(rad));
        py[i] = cy + (int)(maxR * v[i] * sinf(rad));
    }

    // ระบายพื้นผิวโพลีกอนสีเขียวโปร่งใส
    for (int i = 0; i < 5; i++) {
        int next_i = (i + 1) % 5;
        lcd.fillTriangle(cx, cy, px[i], py[i], px[next_i], py[next_i], 0x0345);
        lcd.drawLine(px[i], py[i], px[next_i], py[next_i], 0x07E0);
    }

    // จุด Vertex เรืองแสงสีฟ้า Cyan บนมุมทั้ง 5
    for (int i = 0; i < 5; i++) {
        lcd.fillCircle(px[i], py[i], 3, 0x07FF);
    }
    lcd.setTextDatum(textdatum_t::top_left);
}

// ============================================================================
// หน้าต่างย่อยที่ 4: รายละเอียด Soil 7-in-1 (Root Zone & NPK Macronutrients)
// ถอดแบบตามภาพ soil_7in1_dashboard_ui.jpg 100% พร้อมระบบเลื่อนหน้าจอที่กว้างขวาง
// ============================================================================
static void drawPageDetailSoil7(const FarmSensorTelemetry &data) {
    char buf[80];
    int sy = scrollOffsetY;

    // ซ่อนเมนูด้านบน เพื่อให้ Dashboard แสดงผลเต็มหน้าจอ 480x320 ไม่ถูกแถบเมนูบัง
    lcd.fillRect(0, 0, 460, 320, COLOR_BG);
    lcd.setClipRect(0, 0, 460, 320);

    int c_y = 6 - sy;

    // ========================================================================
    // 0. TOP HUD CIRCUIT TRACE & STATUS (ถอดแบบภาพต้นฉบับ 100%)
    // ========================================================================
    // 1. ซ้ายสุด: ไอคอนฐานข้อมูลทรงกระบอกสีฟ้า (Database Cylinder Icon)
    int db_x = 6;
    int db_y = c_y + 3;
    lcd.drawRoundRect(db_x, db_y, 11, 4, 2, 0x07FF);
    lcd.drawFastHLine(db_x + 1, db_y + 6, 9, 0x07FF);
    lcd.drawPixel(db_x, db_y + 5, 0x07FF);
    lcd.drawPixel(db_x + 10, db_y + 5, 0x07FF);
    lcd.drawFastHLine(db_x + 1, db_y + 10, 9, 0x07FF);
    lcd.drawPixel(db_x, db_y + 9, 0x07FF);
    lcd.drawPixel(db_x + 10, db_y + 9, 0x07FF);

    // ข้อความ "Dashboard" สีฟ้านีออน (แบบไม่มีกรอบสี่เหลี่ยม ตามต้นฉบับเป๊ะ)
    lcd.setTextColor(0x07FF, COLOR_BG);
    lcd.setTextDatum(textdatum_t::top_left);
    lcd.drawString("Dashboard", 21, c_y + 3);

    // แคปซูลนีออนเรืองแสงแนวนอน (Glowing Neon Pill Capsule)
    lcd.fillRoundRect(80, c_y + 6, 18, 5, 2, 0x028A); // เรืองแสงชั้นนอก
    lcd.fillRoundRect(82, c_y + 7, 14, 3, 1, 0x07FF); // นีออนสีฟ้าสว่างชั้นใน

    // 2. ลายเส้นวงจรฮูด (Circuit Trace with Chamfer Bay)
    // วงแหวนกลมฝั่งซ้าย ○
    lcd.drawCircle(107, c_y + 8, 3, 0x05BD);

    // เส้นแนวนอนซ้าย
    lcd.drawFastHLine(110, c_y + 8, 70, 0x05BD);

    // เส้นหักมุมเฉียง 45 องศาลงขวา เข้าสู่ร่องกลาง \
    lcd.drawLine(180, c_y + 8, 192, c_y + 18, 0x05BD);
    lcd.drawLine(180, c_y + 9, 192, c_y + 19, 0x0288);

    // เส้นรางแนวนอนใต้ HUD Status
    lcd.drawFastHLine(192, c_y + 18, 96, 0x05BD);

    // เส้นหักมุมเฉียง 45 องศาขึ้นขวา ออกจากร่องกลาง /
    lcd.drawLine(288, c_y + 18, 300, c_y + 8, 0x05BD);
    lcd.drawLine(288, c_y + 19, 300, c_y + 9, 0x0288);

    // เส้นแนวนอนขวา
    lcd.drawFastHLine(300, c_y + 8, 64, 0x05BD);

    // วงแหวนกลมฝั่งขวา ○
    lcd.drawCircle(367, c_y + 8, 3, 0x05BD);

    // แถบนีออนเรืองแสงสีฟ้าใต้ข้อความ HUD Status
    lcd.fillRoundRect(220, c_y + 18, 40, 2, 1, 0x07FF);

    // 3. องค์ประกอบภายในร่องกลาง (HUD Status Bay)
    // จุดไฟเขียวฝั่งซ้าย 3 จุด (เขียวสว่าง -> เขียวเข้ม -> เขียวหม่น)
    lcd.fillCircle(197, c_y + 7, 3, 0x07E0);
    lcd.fillCircle(204, c_y + 7, 2, 0x03A0);
    lcd.fillCircle(210, c_y + 7, 2, 0x0260);

    // ไอคอนเสาส่งสัญญาณซ้าย ((•))
    lcd.drawFastVLine(221, c_y + 5, 5, 0x07FF);
    lcd.drawPixel(221, c_y + 4, 0xFFFF);
    lcd.drawPixel(218, c_y + 5, 0x07FF);
    lcd.drawPixel(217, c_y + 6, 0x07FF);
    lcd.drawPixel(217, c_y + 7, 0x07FF);
    lcd.drawPixel(218, c_y + 8, 0x07FF);
    lcd.drawPixel(224, c_y + 5, 0x07FF);
    lcd.drawPixel(225, c_y + 6, 0x07FF);
    lcd.drawPixel(225, c_y + 7, 0x07FF);
    lcd.drawPixel(224, c_y + 8, 0x07FF);

    // ข้อความกลาง "HUD Status" สีขาวคมชัด
    lcd.setTextDatum(textdatum_t::middle_center);
    lcd.setTextColor(0xFFFF, COLOR_BG);
    lcd.drawString("HUD Status", 240, c_y + 7);
    lcd.setTextDatum(textdatum_t::top_left);

    // ไอคอนเสาส่งสัญญาณขวา ((•))
    lcd.drawFastVLine(259, c_y + 5, 5, 0x07FF);
    lcd.drawPixel(259, c_y + 4, 0xFFFF);
    lcd.drawPixel(256, c_y + 5, 0x07FF);
    lcd.drawPixel(255, c_y + 6, 0x07FF);
    lcd.drawPixel(255, c_y + 7, 0x07FF);
    lcd.drawPixel(256, c_y + 8, 0x07FF);
    lcd.drawPixel(262, c_y + 5, 0x07FF);
    lcd.drawPixel(263, c_y + 6, 0x07FF);
    lcd.drawPixel(263, c_y + 7, 0x07FF);
    lcd.drawPixel(262, c_y + 8, 0x07FF);

    // จุดไฟเขียวฝั่งขวา 3 จุด (เขียวสว่าง -> เขียวเข้ม -> เขียวหม่น)
    lcd.fillCircle(270, c_y + 7, 3, 0x07E0);
    lcd.fillCircle(276, c_y + 7, 2, 0x03A0);
    lcd.fillCircle(282, c_y + 7, 2, 0x0260);

    // 4. ขวาสุด: ขีดสัญญาณ 4 แท่งสีฟ้า และข้อความ "2 hours ago"
    lcd.fillRect(384, c_y + 11, 2, 3, 0x07FF);
    lcd.fillRect(388, c_y + 9, 2, 5, 0x07FF);
    lcd.fillRect(392, c_y + 7, 2, 7, 0x07FF);
    lcd.fillRect(396, c_y + 5, 2, 9, 0x07FF);

    lcd.setTextColor(0x9CD3, COLOR_BG);
    lcd.drawString("2 hours ago", 404, c_y + 4);

    // ========================================================================
    // HEADER TITLE ROW: [ ⚙ ] Soil 7-in-1 Multi-parameter & TinyML Root Zone Monitoring ... [ Soil Data ▾ ]
    // เพิ่มระยะห่างระหว่างแถบ HUD ด้านบน และแถวชื่อหัวข้อเป็น 42px (เว้นระยะโปร่งสบายตา 100% ตรงตามต้นฉบับ)
    // ========================================================================
    int t_y = c_y + 42;

    // แถบ Tab สีเขียวอมฟ้าชิดขอบซ้าย พร้อมไอคอนฟันเฟืองดอกไม้ตามต้นฉบับ 100%
    lcd.fillRoundRect(0, t_y - 2, 16, 22, 3, 0x028A);
    lcd.drawRoundRect(0, t_y - 2, 16, 22, 3, 0x07FF);
    lcd.drawCircle(8, t_y + 9, 3, 0x07FF);
    lcd.fillCircle(8, t_y + 9, 1, 0xFFFF);
    lcd.drawPixel(8, t_y + 5, 0x07FF);
    lcd.drawPixel(8, t_y + 13, 0x07FF);
    lcd.drawPixel(4, t_y + 9, 0x07FF);
    lcd.drawPixel(12, t_y + 9, 0x07FF);

    // ชื่อหัวข้อหลักภาษาอังกฤษเต็มตามภาพต้นฉบับ 100%
    lcd.setTextColor(0xFFFF, COLOR_BG);
    lcd.drawString("Soil 7-in-1 Multi-parameter & TinyML Root Zone Monitoring", 24, t_y + 5);

    // ปุ่มตัวกรองมุมขวา: [ 🎛️ Soil Data ▾ ] ตามต้นฉบับ 100%
    int fb_x = 372;
    lcd.fillRoundRect(fb_x, t_y - 2, 86, 22, 4, 0x0926);
    lcd.drawRoundRect(fb_x, t_y - 2, 86, 22, 4, 0x2969);

    // ไอคอน Slider Controls 3 เส้นแนวนอน
    lcd.drawFastHLine(fb_x + 8, t_y + 6, 8, 0x9CD3);
    lcd.fillCircle(fb_x + 11, t_y + 6, 1, 0x9CD3);
    lcd.drawFastHLine(fb_x + 8, t_y + 10, 8, 0x9CD3);
    lcd.fillCircle(fb_x + 14, t_y + 10, 1, 0x9CD3);
    lcd.drawFastHLine(fb_x + 8, t_y + 14, 8, 0x9CD3);
    lcd.fillCircle(fb_x + 10, t_y + 14, 1, 0x9CD3);

    // ข้อความ "Soil Data"
    lcd.setTextColor(0xCE79, 0x0926);
    lcd.drawString("Soil Data", fb_x + 20, t_y + 5);

    // สัญลักษณ์ลูกศรลง Chevron v
    lcd.drawLine(fb_x + 72, t_y + 8, fb_x + 75, t_y + 11, 0x9CD3);
    lcd.drawLine(fb_x + 75, t_y + 11, fb_x + 78, t_y + 8, 0x9CD3);

    // ========================================================================
    // ROW 1: 4 Cards (Moist, Temp, EC, pH) - กว้าง 106px สูง 98px ชัดเจน สง่างาม
    // เพิ่มระยะห่างระหว่างแถวหัวข้อ และแถวการ์ดแถว 1 เป็น 42px (เว้นระยะโปร่ง 100% ตรงตามต้นฉบับ)
    // ========================================================================
    int r1_y = t_y + 42;

    // Card 1: Soil Moisture
    drawCyberParamCard(6, r1_y, 106, 98, 1, "Moist", data.soil7in1.moisture, "", 0x07FF, data.soil7in1.moisture / 100.0f, 1);

    // Card 2: Soil Temp
    drawCyberParamCard(120, r1_y, 106, 98, 2, "Temp", data.soil7in1.temperature, "C", 0x07E0, data.soil7in1.temperature / 50.0f, 2);

    // Card 3: Soil EC
    drawCyberParamCard(234, r1_y, 106, 98, 3, "EC", data.soil7in1.ec, "uS/cm", 0xFD00, data.soil7in1.ec / 2000.0f, 3);

    // Card 4: Soil pH
    drawCyberParamCard(348, r1_y, 104, 98, 4, "pH", data.soil7in1.ph, "", 0xCA7E, data.soil7in1.ph / 14.0f, 4);

    // ========================================================================
    // ROW 2: 3 Cards (Nitrogen, Phosphorus, Potassium) - กว้าง 144px สูง 98px
    // เพิ่มระยะห่างในแนวตั้งระหว่างการ์ดแถว 1 และแถว 2 เป็น 18px
    // ========================================================================
    int r2_y = r1_y + 98 + 18;

    float n_val = (data.soil7in1.nitrogen > 0.0f) ? data.soil7in1.nitrogen : data.aiCalibrated.nitrogen;
    float p_val = (data.soil7in1.phosphorus > 0.0f) ? data.soil7in1.phosphorus : data.aiCalibrated.phosphorus;
    float k_val = (data.soil7in1.potassium > 0.0f) ? data.soil7in1.potassium : data.aiCalibrated.potassium;

    // Card 5: Nitrogen
    drawCyberParamCard(6, r2_y, 144, 98, 5, "Nitrogen", n_val, "mg/kg", 0x07FF, n_val / 200.0f, 5);

    // Card 6: Phosphorus
    drawCyberParamCard(158, r2_y, 144, 98, 6, "Phosphorus", p_val, "mg/kg", 0x07E0, p_val / 100.0f, 6);

    // Card 7: Potassium
    drawCyberParamCard(310, r2_y, 142, 98, 7, "Potassium", k_val, "mg/kg", 0x07FF, k_val / 250.0f, 7);

    // ========================================================================
    // ROW 3: Visual Analytics (N-P-K Stoichiometry & Soil Fertility Radar) - สูง 196px
    // เพิ่มระยะห่างในแนวตั้งระหว่างแถวเป็น 18px
    // ========================================================================
    int r3_y = r2_y + 98 + 18;

    // --- Box A (Left): N-P-K stoichiometry (w: 220, h: 196) ---
    lcd.fillRoundRect(6, r3_y, 220, 196, 6, 0x08A3);
    lcd.drawRoundRect(6, r3_y, 220, 196, 6, 0x277E);

    // Title & Show Chip (ไม่ชนกันเด็ดขาด)
    lcd.setTextColor(0xFFFF, 0x08A3);
    lcd.drawString("N-P-K Ratio", 12, r3_y + 10);
    lcd.fillRoundRect(168, r3_y + 8, 44, 16, 3, 0x18C3);
    lcd.setTextColor(0x07FF, 0x18C3);
    lcd.setTextDatum(textdatum_t::middle_center);
    lcd.drawString("Show", 168 + 22, r3_y + 16);
    lcd.setTextDatum(textdatum_t::top_left);

    // วาดโดนัทชาร์ต 4 สีขนาดใหญ่
    float disp_n = (n_val > 0.0f) ? n_val : 78.0f;
    float disp_p = (p_val > 0.0f) ? p_val : 24.0f;
    float disp_k = (k_val > 0.0f) ? k_val : 145.0f;
    float total_npk = disp_n + disp_p + disp_k;
    drawSoilDonutChart(62, r3_y + 108, 42, 25, disp_n, disp_p, disp_k);

    // รายละเอียด Legend 4 สีตามต้นฉบับ ชัดเจนอ่านง่าย
    int leg_x = 118;
    // Dot 1: Cyan (N)
    lcd.fillCircle(leg_x, r3_y + 44, 4, 0x07FF);
    snprintf(buf, sizeof(buf), "N: %.1f (%.1f%%)", disp_n, (disp_n / total_npk) * 100.0f);
    lcd.setTextColor(0xFFFF, 0x08A3);
    lcd.drawString(buf, leg_x + 8, r3_y + 38);

    // Dot 2: Green (P)
    lcd.fillCircle(leg_x, r3_y + 70, 4, 0x07E0);
    snprintf(buf, sizeof(buf), "P: %.1f (%.1f%%)", disp_p, (disp_p / total_npk) * 100.0f);
    lcd.drawString(buf, leg_x + 8, r3_y + 64);

    // Dot 3: Orange (K)
    lcd.fillCircle(leg_x, r3_y + 96, 4, 0xFD00);
    snprintf(buf, sizeof(buf), "K: %.1f (%.1f%%)", disp_k, (disp_k / total_npk) * 100.0f);
    lcd.drawString(buf, leg_x + 8, r3_y + 90);

    // Dot 4: Violet (AI/Trace)
    lcd.fillCircle(leg_x, r3_y + 122, 4, 0xCA7E);
    lcd.setTextColor(0xCA7E, 0x08A3);
    lcd.drawString("AI Trace", leg_x + 8, r3_y + 116);

    // สัดส่วน Ratio & Total
    float base_p = (disp_p > 0.1f) ? disp_p : 1.0f;
    snprintf(buf, sizeof(buf), "Ratio: %.1f:1:%.1f", disp_n / base_p, disp_k / base_p);
    lcd.setTextColor(COLOR_TEXT_DIM, 0x08A3);
    lcd.drawString(buf, leg_x + 8, r3_y + 144);

    snprintf(buf, sizeof(buf), "Total: %.1f mg", total_npk);
    lcd.drawString(buf, leg_x + 8, r3_y + 166);

    // --- Box B (Right): Soil Fertility Radar (w: 220, h: 196) ---
    lcd.fillRoundRect(232, r3_y, 220, 196, 6, 0x08A3);
    lcd.drawRoundRect(232, r3_y, 220, 196, 6, 0x07E0);

    // Title & New Chip (ไม่ชนกัน)
    lcd.setTextColor(0xFFFF, 0x08A3);
    lcd.drawString("Soil Fertility", 240, r3_y + 10);
    lcd.fillRoundRect(396, r3_y + 8, 44, 16, 3, 0x0A83);
    lcd.setTextColor(0x07E0, 0x0A83);
    lcd.setTextDatum(textdatum_t::middle_center);
    lcd.drawString("New", 396 + 22, r3_y + 16);
    lcd.setTextDatum(textdatum_t::top_left);

    // วาดเรดาร์ 5 แกนกว้างเต็มกล่องแบบต้นฉบับเป๊ะ
    drawSoilRadarChart(342, r3_y + 104, 46, data.soil7in1.moisture, data.soil7in1.temperature,
                       data.soil7in1.ec, data.soil7in1.ph, total_npk);

    // บรรทัดสรุปสถานะสมดุลดินด้านล่างเรดาร์
    lcd.setTextDatum(textdatum_t::middle_center);
    lcd.setTextColor(0x07E0, 0x08A3);
    lcd.drawString("SOIL HEALTH: 88/100 (OPTIMAL)", 342, r3_y + 172);
    lcd.setTextDatum(textdatum_t::top_left);

    // ========================================================================
    // ROW 4: Agronomic insight Notification Cards - สูง 188px
    // เพิ่มระยะห่างในแนวตั้งระหว่างการ์ดแจ้งเตือนเป็น 12px
    // ========================================================================
    int r4_y = r3_y + 196 + 18;
    lcd.fillRoundRect(6, r4_y, 446, 188, 6, 0x08A3);
    lcd.drawRoundRect(6, r4_y, 446, 188, 6, 0x4A69);

    // Title: Agronomic insight •••
    lcd.setTextColor(0xFFFF, 0x08A3);
    lcd.drawString("Agronomic insight", 14, r4_y + 10);
    lcd.setTextColor(COLOR_TEXT_DIM, 0x08A3);
    lcd.drawString("...", 426, r4_y + 10);

    // Notification Card 1: Green Bell Icon 🔔 (สูง 66px)
    int n1_y = r4_y + 30;
    lcd.fillRoundRect(12, n1_y, 434, 66, 5, 0x10E4);
    lcd.drawRoundRect(12, n1_y, 434, 66, 5, 0x07E0);

    // กระดิ่งเขียว
    lcd.fillCircle(28, n1_y + 22, 9, 0x07E0);
    lcd.fillTriangle(25, n1_y + 18, 31, n1_y + 18, 28, n1_y + 26, 0x0000);

    lcd.setTextColor(0xFFFF, 0x10E4);
    lcd.drawString("Agronomic insight notification", 44, n1_y + 9);

    lcd.setTextColor(0x9CD3, 0x10E4);
    lcd.drawString("Soil moisture cooperated by root depth participates in premium growth.", 44, n1_y + 27);

    lcd.setTextColor(0x633C, 0x10E4);
    lcd.drawString("12 hours ago", 44, n1_y + 47);

    // Notification Card 2: Purple Bell Icon 🔔 (TinyML AI Engine) (สูง 66px, เว้นระยะห่าง 12px)
    int n2_y = n1_y + 66 + 12;
    lcd.fillRoundRect(12, n2_y, 434, 66, 5, 0x18A8);
    lcd.drawRoundRect(12, n2_y, 434, 66, 5, 0xCA7E);

    // กระดิ่งม่วง
    lcd.fillCircle(28, n2_y + 22, 9, 0xCA7E);
    lcd.fillTriangle(25, n2_y + 18, 31, n2_y + 18, 28, n2_y + 26, 0x0000);

    lcd.setTextColor(0xFFFF, 0x18A8);
    lcd.drawString("TinyML Edge AI Decoupling Engine", 44, n2_y + 9);

    snprintf(buf, sizeof(buf), "Neural Denoised: AI-N:%.1f, P:%.1f, K:%.1f, pH:%.1f",
             data.aiCalibrated.nitrogen, data.aiCalibrated.phosphorus,
             data.aiCalibrated.potassium, data.aiCalibrated.ph);
    lcd.setTextColor(0x9CD3, 0x18A8);
    lcd.drawString(buf, 44, n2_y + 27);

    lcd.setTextColor(0x9CD3, 0x18A8);
    lcd.drawString("2 hours ago | Confidence: 94.8% | Latency < 0.12ms", 44, n2_y + 47);

    // ========================================================================
    // ROW 5: Industrial RS485 MODBUS RTU Telemetry - สูง 132px
    // เพิ่มระยะห่างในแนวตั้งระหว่างแถวเป็น 18px
    // ========================================================================
    int r5_y = r4_y + 188 + 18;
    lcd.fillRoundRect(6, r5_y, 446, 132, 6, 0x08A3);
    lcd.drawRoundRect(6, r5_y, 446, 132, 6, 0x4208);

    lcd.setTextColor(COLOR_CYAN, 0x08A3);
    lcd.drawString("INDUSTRIAL RS485 MODBUS RTU TELEMETRY:", 14, r5_y + 12);

    lcd.setTextColor(COLOR_TEXT_VAL, 0x08A3);
    lcd.drawString("UART2 Port: TX=GPIO40, RX=GPIO41 | Baud 9600-8-N-1", 14, r5_y + 36);
    lcd.drawString("Modbus Protocol: Slave ID 0x01 | Function 0x03 (Holding Regs)", 14, r5_y + 60);

    snprintf(buf, sizeof(buf), "%s: %s | CRC16 Checksum: %s",
             L_STR("สถานะ", "Status", "状态"),
             data.soil7in1.isConnected ? L_STR("ออนไลน์ (ปกติ)", "ONLINE (OK)", "在线 (正常)") : L_STR("ขาดการเชื่อมต่อ", "DISCONNECTED", "断开连接"),
             (data.soil7in1.readErrorCount == 0) ? "PASS" : "RETRY");
    lcd.setTextColor(data.soil7in1.isConnected ? 0x07E0 : COLOR_WARN, 0x08A3);
    lcd.drawString(buf, 14, r5_y + 84);

    snprintf(buf, sizeof(buf), "Modbus Probe: 316L Stainless Steel Electrodes | Error Count: %u", data.soil7in1.readErrorCount);
    lcd.setTextColor(COLOR_TEXT_DIM, 0x08A3);
    lcd.drawString(buf, 14, r5_y + 108);

    // ========================================================================
    // ROW 6: BOTTOM NAVIGATION BUTTONS & SCROLLBAR
    // ========================================================================
    drawDetailBottomNav(sy, PAGE_DETAIL_AIR, 892);

    lcd.clearClipRect();
    drawScrollBar(scrollOffsetY, maxScrollY, 4, 312, 0x07E0);
    pageChanged = false;
}

// ============================================================================
// หน้าที่ 2: กราฟแนวโน้มอนุกรมเวลาสด (Live Trend & Sparkline Graphs)
// ============================================================================
static void drawPageGraphs(const FarmSensorTelemetry &data) {
    ensureAppFont();
    char buf[64];

    if (pageChanged) {
        lcd.fillRect(0, 36, 480, 284, COLOR_BG);
        pageChanged = false;
    }

    // หัวข้อหน้า
    lcd.setTextSize(1);
    lcd.setTextColor(COLOR_YELLOW, COLOR_BG);
    lcd.drawString(L_STR("กราฟแนวโน้มข้อมูลสด (60 จุดล่าสุด)", "LIVE TREND GRAPHS (LAST 60 POINTS)", "实时历史趋势图 (最近60个数据点)"), 12, 40);

    // กราฟ 1: ความชื้นดิน
    const int g1_x = 35;
    const int g1_y = 54;
    const int g1_w = 430;
    const int g1_h = 100;

    lcd.fillRoundRect(g1_x - 5, g1_y - 2, g1_w + 10, g1_h + 18, 4, COLOR_CARD_BG);
    lcd.drawRoundRect(g1_x - 5, g1_y - 2, g1_w + 10, g1_h + 18, 4, 0x31A6);

    lcd.setTextColor(COLOR_TEXT_DIM, COLOR_CARD_BG);
    lcd.drawString("100%", 4, g1_y);
    lcd.drawString(" 50%", 4, g1_y + (g1_h / 2) - 4);
    lcd.drawString("  0%", 4, g1_y + g1_h - 8);

    lcd.drawLine(g1_x, g1_y, g1_x + g1_w, g1_y, 0x2104);
    lcd.drawLine(g1_x, g1_y + (g1_h / 2), g1_x + g1_w, g1_y + (g1_h / 2), 0x2104);
    lcd.drawLine(g1_x, g1_y + g1_h, g1_x + g1_w, g1_y + g1_h, 0x4208);

    int dangerY = g1_y + g1_h - (int)(0.40f * g1_h);
    for (int dx = g1_x; dx < g1_x + g1_w; dx += 8) {
        lcd.drawLine(dx, dangerY, dx + 4, dangerY, COLOR_WARN);
    }

    if (historyCount >= 2) {
        float stepX = (float)g1_w / (float)(HISTORY_LEN - 1);
        int startIdx = (historyHead - historyCount + HISTORY_LEN) % HISTORY_LEN;

        for (int i = 0; i < historyCount - 1; i++) {
            int idx1 = (startIdx + i) % HISTORY_LEN;
            int idx2 = (startIdx + i + 1) % HISTORY_LEN;

            int x1 = g1_x + (int)(i * stepX);
            int x2 = g1_x + (int)((i + 1) * stepX);

            int y1_surf = g1_y + g1_h - constrain((int)(history[idx1].soilSurface * g1_h / 100.0f), 0, g1_h);
            int y2_surf = g1_y + g1_h - constrain((int)(history[idx2].soilSurface * g1_h / 100.0f), 0, g1_h);
            lcd.drawLine(x1, y1_surf, x2, y2_surf, 0x07E0);

            int y1_deep = g1_y + g1_h - constrain((int)(history[idx1].soilDeep * g1_h / 100.0f), 0, g1_h);
            int y2_deep = g1_y + g1_h - constrain((int)(history[idx2].soilDeep * g1_h / 100.0f), 0, g1_h);
            lcd.drawLine(x1, y1_deep, x2, y2_deep, COLOR_CYAN);
        }
    }

    lcd.setTextSize(1);
    lcd.setTextColor(0x07E0, COLOR_CARD_BG);
    lcd.drawString(L_STR("- ดินตื้น (Stick)", "- Surface (Stick)", "- 表层土壤 (Stick)"), g1_x + 8, g1_y + g1_h + 3);
    lcd.setTextColor(COLOR_CYAN, COLOR_CARD_BG);
    lcd.drawString(L_STR("- ดินลึก (7-in-1)", "- Deep Root (7-in-1)", "- 深层根系 (7合1)"), g1_x + 135, g1_y + g1_h + 3);
    lcd.setTextColor(COLOR_WARN, COLOR_CARD_BG);
    lcd.drawString(L_STR("--- วิกฤต (<40%)", "--- Danger (<40%)", "--- 缺水警戒 (<40%)"), g1_x + 280, g1_y + g1_h + 3);

    // กราฟ 2: รังสีดวงอาทิตย์
    const int g2_x = 35;
    const int g2_y = 180;
    const int g2_w = 430;
    const int g2_h = 90;

    lcd.fillRoundRect(g2_x - 5, g2_y - 2, g2_w + 10, g2_h + 18, 4, COLOR_CARD_BG);
    lcd.drawRoundRect(g2_x - 5, g2_y - 2, g2_w + 10, g2_h + 18, 4, 0x31A6);

    lcd.setTextColor(COLOR_TEXT_DIM, COLOR_CARD_BG);
    lcd.drawString("1000", 2, g2_y);
    lcd.drawString(" 500", 2, g2_y + (g2_h / 2) - 4);
    lcd.drawString("   0", 2, g2_y + g2_h - 8);

    lcd.drawLine(g2_x, g2_y, g2_x + g2_w, g2_y, 0x2104);
    lcd.drawLine(g2_x, g2_y + (g2_h / 2), g2_x + g2_w, g2_y + (g2_h / 2), 0x2104);
    lcd.drawLine(g2_x, g2_y + g2_h, g2_x + g2_w, g2_y + g2_h, 0x4208);

    if (historyCount >= 2) {
        float stepX = (float)g2_w / (float)(HISTORY_LEN - 1);
        int startIdx = (historyHead - historyCount + HISTORY_LEN) % HISTORY_LEN;

        for (int i = 0; i < historyCount - 1; i++) {
            int idx1 = (startIdx + i) % HISTORY_LEN;
            int idx2 = (startIdx + i + 1) % HISTORY_LEN;

            int x1 = g2_x + (int)(i * stepX);
            int x2 = g2_x + (int)((i + 1) * stepX);

            int y1_rad = g2_y + g2_h - constrain((int)(history[idx1].solarRad * g2_h / 1000.0f), 0, g2_h);
            int y2_rad = g2_y + g2_h - constrain((int)(history[idx2].solarRad * g2_h / 1000.0f), 0, g2_h);
            lcd.drawLine(x1, y1_rad, x2, y2_rad, COLOR_YELLOW);
        }
    }

    snprintf(buf, sizeof(buf), "%s: %.2f W/m2 | %s: %.2f C",
             L_STR("รังสี", "Solar", "光合辐射"), data.light.solarRadiation,
             L_STR("อุณหภูมิอากาศ", "Air Temp", "气温"), data.air.temperature);
    lcd.setTextColor(COLOR_YELLOW, COLOR_CARD_BG);
    lcd.drawString(buf, g2_x + 8, g2_y + g2_h + 3);

    lcd.setTextColor(COLOR_TEXT_DIM, COLOR_BG);
    lcd.drawString(L_STR("แตะแท็บด้านบนเพื่อสลับหน้าจอ", "TAP TOP TABS TO SWITCH PAGES", "点击顶部标签切换页面"), 130, 305);
}

// ============================================================================
// หน้าที่ 3: แผงควบคุมรีเลย์ & ระบบอัตโนมัติ (Relay Control & Smart Automation)
// ============================================================================
static void drawPageRelays(bool pumpState, bool mistingState) {
    ensureAppFont();
    if (pageChanged) {
        lcd.fillRect(0, 36, 480, 284, COLOR_BG);
        pageChanged = false;
    }

    lcd.setTextSize(1);
    lcd.setTextColor(0xFFE0, COLOR_BG); // หัวข้อสีเหลืองทองนีออนสว่างสดใส
    lcd.drawString(L_STR("แผงควบคุมสวิตช์รีเลย์ & ระบบอัตโนมัติ", "MANUAL & AUTOMATIC RELAY CONTROL", "继电器手动与智能自控面板"), 14, 42);

    // Relay 1: ปั๊มน้ำ 1
    int r1_bg = pumpState ? 0x0320 : 0x10E4;
    uint16_t r1_border = pumpState ? 0x07E0 : 0xF948; // เปิด = เขียวนีออน / ปิด = แดงทับทิมนีออนสว่าง
    lcd.fillRoundRect(14, 60, 218, 70, 8, r1_bg);
    lcd.drawRoundRect(14, 60, 218, 70, 8, r1_border);
    lcd.drawRoundRect(15, 61, 216, 68, 7, pumpState ? 0x15D3 : 0xFD20); // ขอบหนา 2 ชั้น คมกริบ
    lcd.setTextSize(1);
    lcd.setTextColor(0xFFFF, r1_bg); // ข้อความสีขาวสว่าง ชัดเจน คอนทราสต์สูง
    lcd.drawString(pumpState ? L_STR("ปั๊มน้ำ 1: เปิด [ทำงาน]", "PUMP 1: ON [RUNNING]", "水泵 1: 开启 [运行中]") : L_STR("ปั๊มน้ำ 1: ปิด [สแตนด์บาย]", "PUMP 1: OFF [STANDBY]", "水泵 1: 关闭 [待机]"), 24, 72);
    lcd.setTextColor(pumpState ? 0x15D3 : 0x3DFF, r1_bg);
    lcd.drawString("Relay O1 (GPIO 39) | Safety Cutoff 5m", 24, 98);

    // Relay 2: ปั๊มน้ำ 2
    bool r2_state = (digitalRead(RELAY_2_PIN) == HIGH);
    int r2_bg = r2_state ? 0x0320 : 0x10E4;
    uint16_t r2_border = r2_state ? 0x07E0 : 0xF948;
    lcd.fillRoundRect(248, 60, 218, 70, 8, r2_bg);
    lcd.drawRoundRect(248, 60, 218, 70, 8, r2_border);
    lcd.drawRoundRect(249, 61, 216, 68, 7, r2_state ? 0x15D3 : 0xFD20);
    lcd.setTextColor(0xFFFF, r2_bg);
    lcd.drawString(r2_state ? L_STR("ปั๊มน้ำ 2: เปิด [ทำงาน]", "PUMP 2: ON [RUNNING]", "水泵 2: 开启 [运行中]") : L_STR("ปั๊มน้ำ 2: ปิด [สแตนด์บาย]", "PUMP 2: OFF [STANDBY]", "水泵 2: 关闭 [待机]"), 258, 72);
    lcd.setTextColor(r2_state ? 0x15D3 : 0x3DFF, r2_bg);
    lcd.drawString("Relay O2 (GPIO 38) | Solenoid Valve", 258, 98);

    // Relay 3: วาล์วน้ำ
    bool r3_state = (digitalRead(RELAY_3_PIN) == HIGH);
    int r3_bg = r3_state ? 0x0320 : 0x10E4;
    uint16_t r3_border = r3_state ? 0x07E0 : 0xF948;
    lcd.fillRoundRect(14, 140, 218, 70, 8, r3_bg);
    lcd.drawRoundRect(14, 140, 218, 70, 8, r3_border);
    lcd.drawRoundRect(15, 141, 216, 68, 7, r3_state ? 0x15D3 : 0xFD20);
    lcd.setTextColor(0xFFFF, r3_bg);
    lcd.drawString(r3_state ? L_STR("วาล์วน้ำ: เปิด [ไหล]", "VALVE: ON [OPEN]", "电磁阀: 开启 [通水]") : L_STR("วาล์วน้ำ: ปิด [ปิดสนิท]", "VALVE: OFF [CLOSED]", "电磁阀: 关闭 [切断]"), 24, 152);
    lcd.setTextColor(r3_state ? 0x15D3 : 0x3DFF, r3_bg);
    lcd.drawString("Relay O3 (GPIO 7)  | Surface Valve", 24, 178);

    // Relay 4: พ่นหมอก
    int r4_bg = mistingState ? 0x0320 : 0x10E4;
    uint16_t r4_border = mistingState ? 0x07E0 : 0xF948;
    lcd.fillRoundRect(248, 140, 218, 70, 8, r4_bg);
    lcd.drawRoundRect(248, 140, 218, 70, 8, r4_border);
    lcd.drawRoundRect(249, 141, 216, 68, 7, mistingState ? 0x15D3 : 0xFD20);
    lcd.setTextColor(0xFFFF, r4_bg);
    lcd.drawString(mistingState ? L_STR("พ่นหมอก: เปิด [ทำงาน]", "MISTING: ON [ACTIVE]", "喷雾: 开启 [降温中]") : L_STR("พ่นหมอก: ปิด [สแตนด์บาย]", "MISTING: OFF [STANDBY]", "喷雾: 关闭 [待机]"), 258, 152);
    lcd.setTextColor(mistingState ? 0x15D3 : 0x3DFF, r4_bg);
    lcd.drawString("Relay O4 (GPIO 6)  | Misting Cooler", 258, 178);

    // กล่องแสดงกฎ Smart Automation
    lcd.fillRoundRect(14, 222, 452, 60, 8, 0x0184);
    lcd.drawRoundRect(14, 222, 452, 60, 8, 0x07FF);
    lcd.drawRoundRect(15, 223, 450, 58, 7, 0x03FF);
    lcd.setTextSize(1);
    lcd.setTextColor(0xFFE0, 0x0184); // หัวข้อกฎสีเหลืองทองนีออน
    lcd.drawString(L_STR("เงื่อนไขการทำงานอัตโนมัติ (Smart Rules):", "SMART AUTOMATION RULES:", "智能自控联动规则:"), 24, 230);
    lcd.setTextColor(0xFFFF, 0x0184); // เนื้อหากฎสีขาวสว่าง ชัดเจน
    lcd.drawString(L_STR("1. ปั๊มน้ำ: เปิดเมื่อดิน < 40%, ปิดเมื่อดิน >= 65%", "1. Water Pump: Auto ON < 40%, OFF >= 65%", "1. 水泵: 土壤湿度<40%启动，>=65%关闭"), 24, 246);
    lcd.drawString(L_STR("2. พ่นหมอก: เปิดเมื่อ อุณหภูมิ > 35C และ ความชื้น < 70%", "2. Misting: Auto ON Temp > 35C & RH < 70%", "2. 喷雾: 气温>35℃且空气湿度<70%启动"), 24, 262);

    lcd.setTextColor(0x07FF, COLOR_BG);
    lcd.drawString(L_STR("แตะที่กล่องเพื่อสลับสถานะเปิด/ปิด", "TAP BOX TO TOGGLE RELAY STATE", "点击方块切换开关状态"), 135, 298);
}
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
